TadeoSinay/planos_flama-/salida/documentos/DOC-04_NFPA10_vs_IRAM.pdf

FLAMA S.A. | NFPA 10 frente a IRAM | DOC-04
Edición 0 | Señalización, colores, instalación e intervalos | 28/09/2026

# NFPA 10 frente a IRAM: marcado, colores e instalación

## 1. Identificación de clases de fuego

NFPA 10 admite dos sistemas de marcado de la etiqueta: el sistema letra-forma de color y el sistema de pictogramas (Anexo B). En Argentina, IRAM 10005 usa las mismas formas geométricas para las clases. Láminas: FL_SEN_03 (letra-forma) y FL_SEN_05 (pictogramas).
Clase | Fuego | Letra-forma (NFPA 10 / IRAM 10005) | Pictograma NFPA 10
A | combustibles sólidos comunes | triángulo verde | cesto con residuos y fuego
B | líquidos y gases inflamables | cuadrado rojo | bidón y fuego
C | equipos eléctricos energizados | círculo azul | enchufe y fuego
D | metales combustibles | estrella de 5 puntas amarilla | sin pictograma
K | aceites y grasas de cocina | hexágono negro | sartén y fuego
En el sistema de pictogramas, la clase para la que el agente no es apto se muestra con fondo negro y barra diagonal roja; los matafuegos de agua y espuma deben mostrar la clase C tachada.

## 2. NFPA 704 no se usa en el matafuego

El rombo de NFPA 704 (azul salud, rojo inflamabilidad, amarillo inestabilidad, blanco riesgos especiales, escala 0 a 4) identifica los peligros de los materiales almacenados en un edificio o tanque para los bomberos. No es una señal del matafuego ni de su clase de fuego.

## 3. Colores de seguridad y carteles

Tema | IRAM / Argentina | NFPA 10 / EE. UU.
Color del matafuego | rojo (IRAM 3523 y afines) | rojo habitual; NFPA no fija el color del cuerpo
Cartel en altura | tridimensional EXTINTOR + pictograma, caras ≥ 280 × 220, a 2,0-2,5 m (3517-2:2020 7.3, FL_SEN_02) | OSHA / ANSI Z535; ISO 7010 F001 aceptado
Chapa baliza | 350 (ó 260) × 870, franjas 100 mm a 45°, borde fotoluminiscente 15 mm, tipos de fuego, n° de puesto, datos del PRS (7.2, FL_SEN_01/07) | no existe en NFPA 10
Símbolos de clase | contorno de color con letra + pictograma, colores IRAM-DEF D 1054 (7.2.2, FL_SEN_03) | letra-forma rellena o pictogramas (Anexo B)

## 4. Instalación

Tema | IRAM / Argentina | NFPA 10
Altura de la parte superior | ≤ 1,5 m hasta 20 kg; ≤ 1,0 m si pesa más (3517-2:2020 6.2.14) | ≤ 1,53 m (5 ft) si pesa ≤ 18,14 kg; ≤ 1,07 m (3,5 ft) si pesa más (§6.1.3.8.1-2)
Separación al piso | ≥ 0,10 m (6.2.14) | ≥ 102 mm (4 in) (§6.1.3.8.3)
Distancia de recorrido | ≤ 20 m clase A, ≤ 15 m clase B, ≤ 3 m clase K; mínimo uno cada 200 m² (6.2.4, 6.2.5) | clase A: 22,9 m (75 ft); clase B: 9,15 o 15,25 m (30 o 50 ft) según potencial
Visibilidad | chapa baliza y cartel | visible, accesible, sin obstrucciones; señalizado si no se ve

## 5. Inspección, mantenimiento y prueba hidráulica

Actividad | IRAM | NFPA 10
Control / inspección | trimestral; mensual en alto riesgo (8.2) | mensual

FLAMA S.A. · DOC-04 · página 1 de 2

Mantenimiento | anual; vehículos: semestral recomendado (9.2.1)

anual

Examen interno polvo presurizado | en cada mantenimiento con cámara (9.8.2) | cada 6 años
PH polvo y gases limpios | 5 años máx.; rodantes a 4 MPa (9.7) | cada 12 años
PH CO2 | cada 5 años | cada 5 años
PH agua, AFFF, acetato de potasio | 2 años máx. (anexo E) | cada 5 años
Agente agua / AFFF / sales K | cambio anual (9.9.1.8-10) | AFFF premezclado: cada 3 años
Mangueras rodantes y CO2 | PH anual (9.7.1.4) | PH con el cilindro

Los números de sección de NFPA 10 corresponden a la edición 2022; verificar contra la edición adoptada por la autoridad competente. Valores IRAM: IRAM 3517-2:2020 (apartados citados).
Fuente: C = catálogo FLAMA · N = norma citada (texto leído) · N* = norma hermana aplicada por analogía · R = valor de referencia habitual, a confirmar por FLAMA con la edición vigente de la norma IRAM (el texto de las normas IRAM es material protegido y no se transcribe).

FLAMA S.A. · DOC-04 · página 2 de 2
