TadeoSinay/planos_flama-/salida/FL_MAT_ABC_2.5kg/FL_MAT_ABC_2.5kg.step

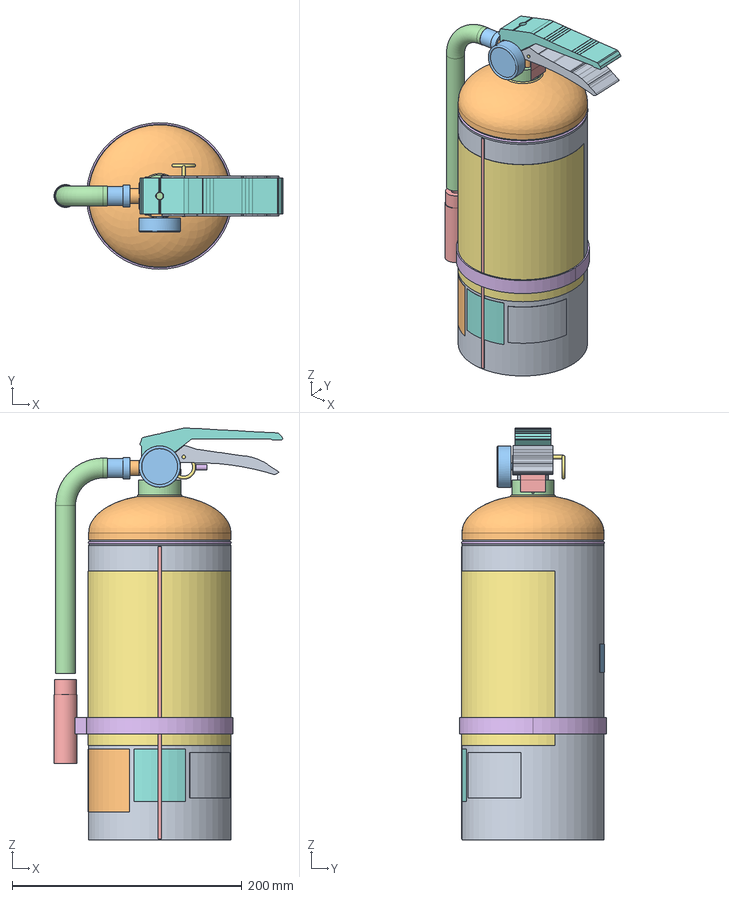
[picture p57: CAD file, 2026-10-10]
salida/FL_MAT_ABC_2.5kg/FL_MAT_ABC_2.5kg.step
199.2 x 127.6 x 358.7 mm
cuerpo
cupula
fondo
cuello
soldaduras
espiga
tuerca
cuerpo_valvula
manometro
vastago
resorte
eje
pasador
manija_superior
manija_inferior
cano_pesca
racor
manguera
tobera
suncho
etiqueta
oblea_pba
sello_iram
tarjeta_caba
etiqueta_serie
junta_cuello
faja_garantia
precinto
