TadeoSinay/planos_flama-/salida/FL_MAT_ABC_25kg/FL_MAT_ABC_25kg.step

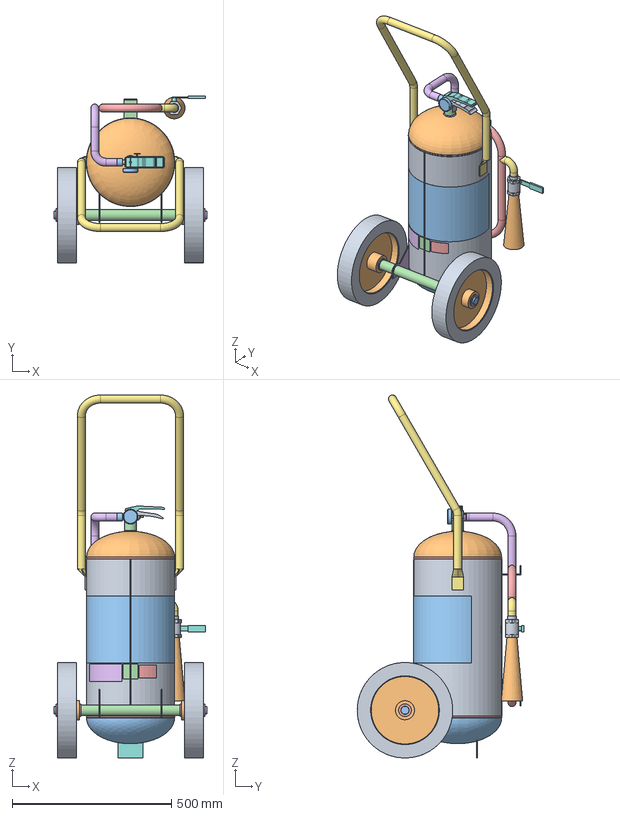
[picture p58: CAD file, 2026-10-10]
salida/FL_MAT_ABC_25kg/FL_MAT_ABC_25kg.step
480.0 x 522.9 x 1140.0 mm
cuerpo
cupula
fondo
cuello
soldaduras
tercera_pata
rueda_der
llanta_der
rueda_izq
llanta_izq
eje_ruedas
portaeje
arandelas_tope
soportes_eje
manija_carro
espiga
tuerca
cuerpo_valvula
manometro
vastago
resorte
eje
pasador
manija_superior
manija_inferior
cano_pesca
racor
ganchos_manguera
manguera_enrollada
manguera
valvula_esferica
tobera_campana
etiqueta
oblea_pba
sello_iram
tarjeta_caba
etiqueta_serie
junta_cuello
faja_garantia
precinto
