TadeoSinay/planos_flama-/salida/FL_MAT_ABC_50kg/FL_MAT_ABC_50kg_3D.dxf

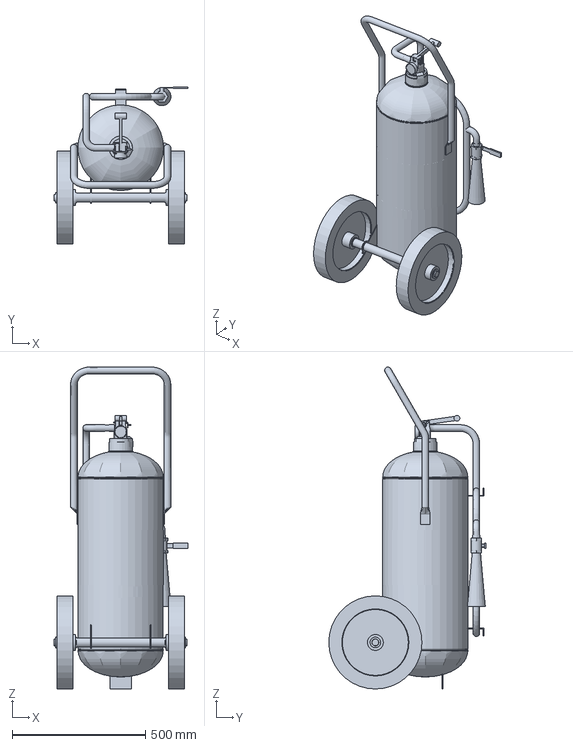
[picture p59: CAD file, 2026-10-10]
salida/FL_MAT_ABC_50kg/FL_MAT_ABC_50kg_3D.dxf
502.5 x 591.5 x 1210.0 mm
