TadeoSinay/planos_flama-/salida/FL_MAT_ABC_5kg/FL_MAT_ABC_5kg.step

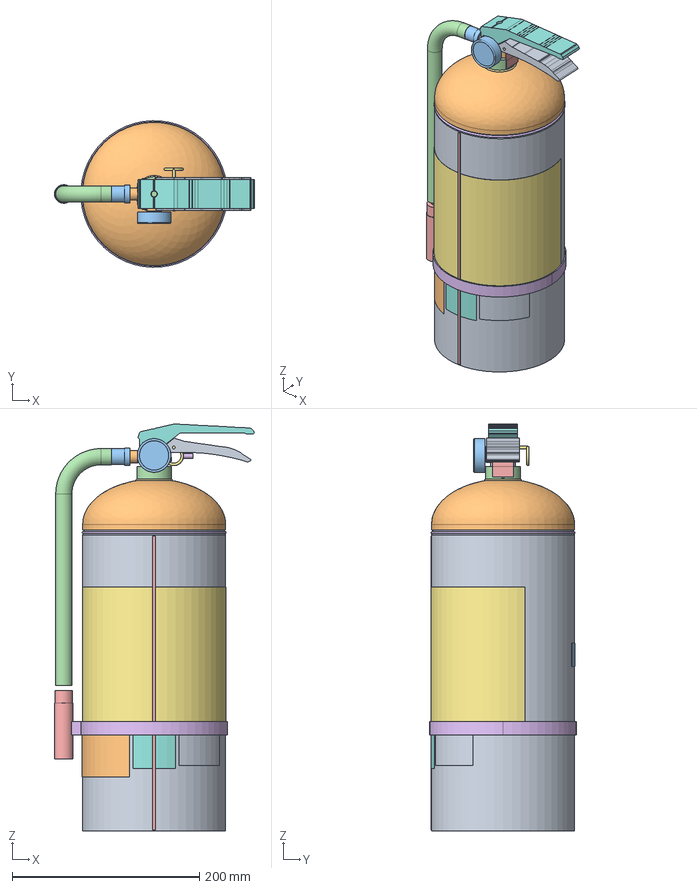
[picture p60: CAD file, 2026-10-10]
salida/FL_MAT_ABC_5kg/FL_MAT_ABC_5kg.step
213.7 x 156.6 x 434.7 mm
cuerpo
cupula
fondo
cuello
soldaduras
espiga
tuerca
cuerpo_valvula
manometro
vastago
resorte
eje
pasador
manija_superior
manija_inferior
cano_pesca
racor
manguera
tobera
suncho
etiqueta
oblea_pba
sello_iram
tarjeta_caba
etiqueta_serie
junta_cuello
faja_garantia
precinto
