TadeoSinay/planos_flama-/salida/FL_MAT_ABC_70kg/FL_MAT_ABC_70kg_3D.dxf

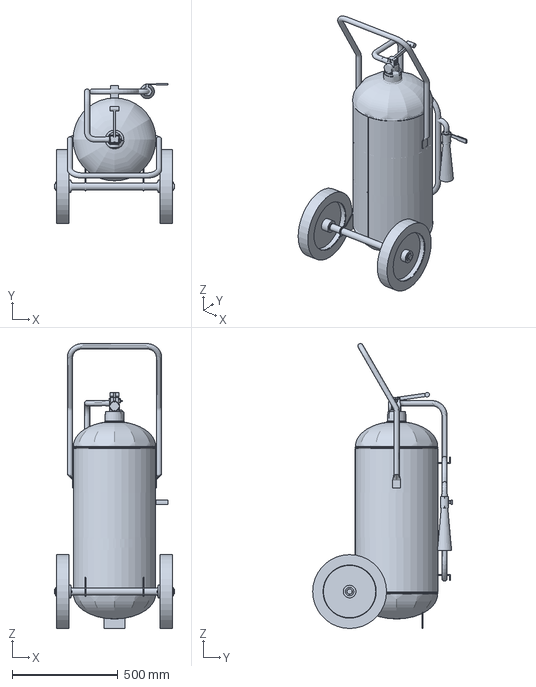
[picture p61: CAD file, 2026-10-10]
salida/FL_MAT_ABC_70kg/FL_MAT_ABC_70kg_3D.dxf
570.0 x 661.5 x 1350.0 mm
