TadeoSinay/planos_flama-/salida/FL_MAT_AFFF_10l/FL_MAT_AFFF_10l_3D.dxf

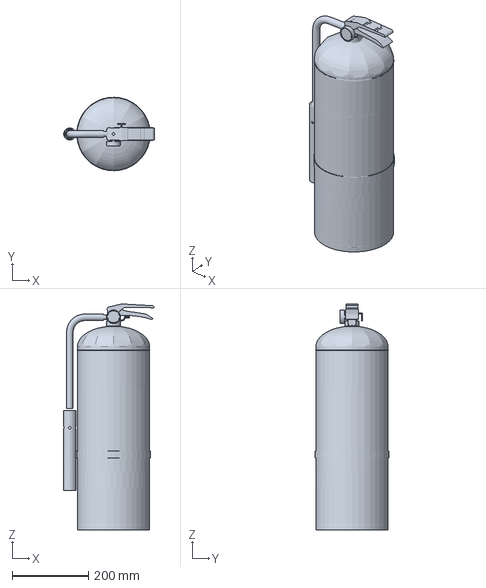
[picture p62: CAD file, 2026-10-10]
salida/FL_MAT_AFFF_10l/FL_MAT_AFFF_10l_3D.dxf
238.3 x 193.5 x 594.3 mm
