TadeoSinay/planos_flama-/salida/FL_MAT_AGUA_10l/FL_MAT_AGUA_10l_3D.dxf

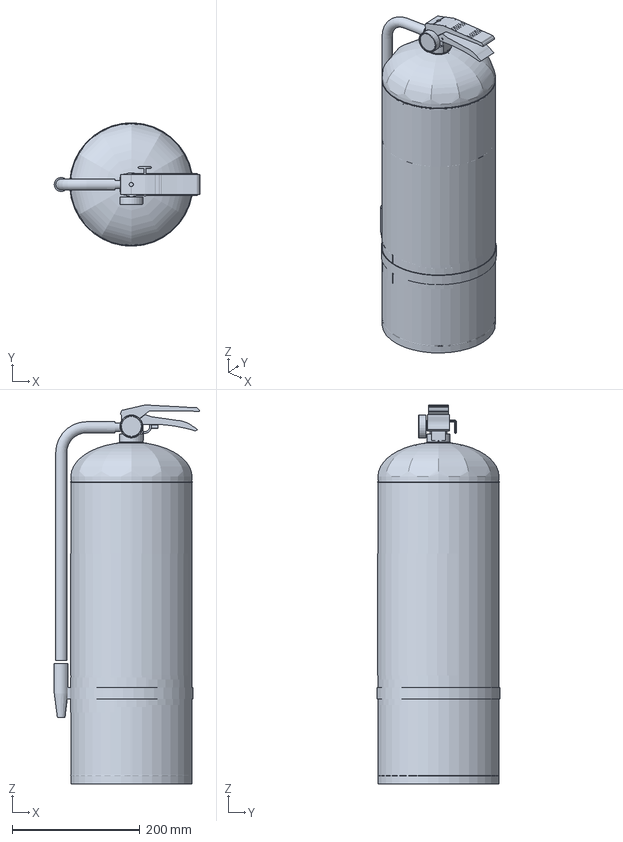
[picture p63: CAD file, 2026-10-10]
salida/FL_MAT_AGUA_10l/FL_MAT_AGUA_10l_3D.dxf
228.3 x 193.5 x 594.3 mm
