TadeoSinay/planos_flama-/salida/FL_MAT_CLASED_9l/FL_MAT_CLASED_9l_3D.dxf

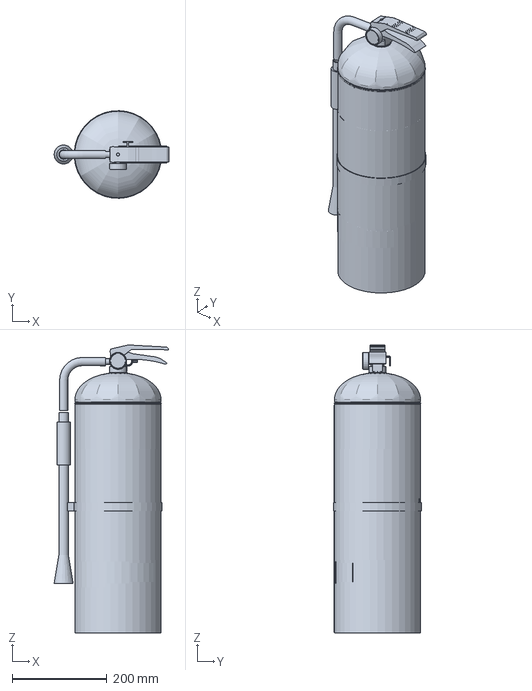
[picture p64: CAD file, 2026-10-10]
salida/FL_MAT_CLASED_9l/FL_MAT_CLASED_9l_3D.dxf
242.0 x 185.0 x 607.7 mm
