TadeoSinay/planos_flama-/salida/FL_MAT_CO2_2kg/FL_MAT_CO2_2kg_3D.dxf

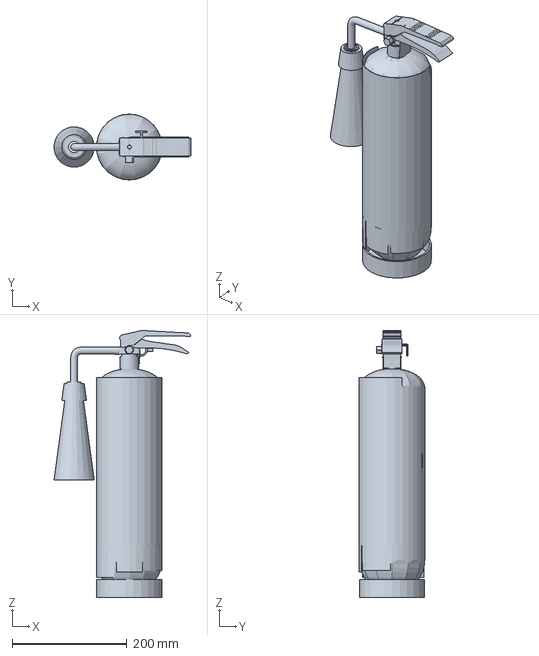
[picture p65: CAD file, 2026-10-10]
salida/FL_MAT_CO2_2kg/FL_MAT_CO2_2kg_3D.dxf
238.3 x 114.6 x 464.4 mm
