TadeoSinay/planos_flama-/salida/FL_MAT_CO2_5kg/FL_MAT_CO2_5kg.step

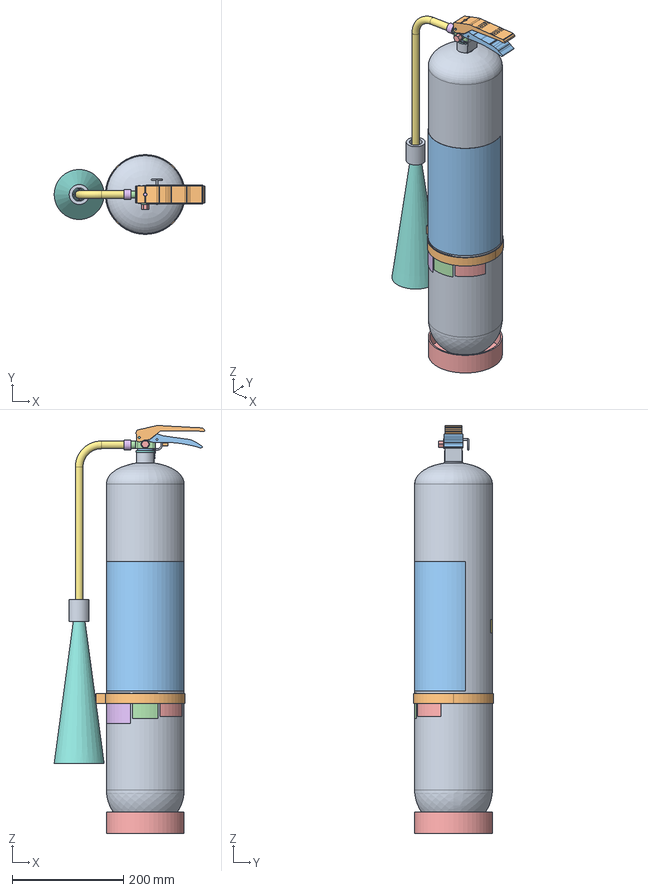
[picture p66: CAD file, 2026-10-10]
salida/FL_MAT_CO2_5kg/FL_MAT_CO2_5kg.step
271.3 x 143.6 x 734.6 mm
cuerpo
espiga
tuerca
cuerpo_valvula
disco_seguridad
vastago
resorte
eje
pasador
manija_superior
manija_inferior
cano_pesca
pie
racor
manguera
difusor
empunadura
suncho
etiqueta
oblea_pba
sello_iram
tarjeta_caba
etiqueta_serie
junta_cuello
faja_garantia
precinto
