TadeoSinay/planos_flama-/salida/FL_MAT_SALESK_6l/FL_MAT_SALESK_6l_3D.dxf

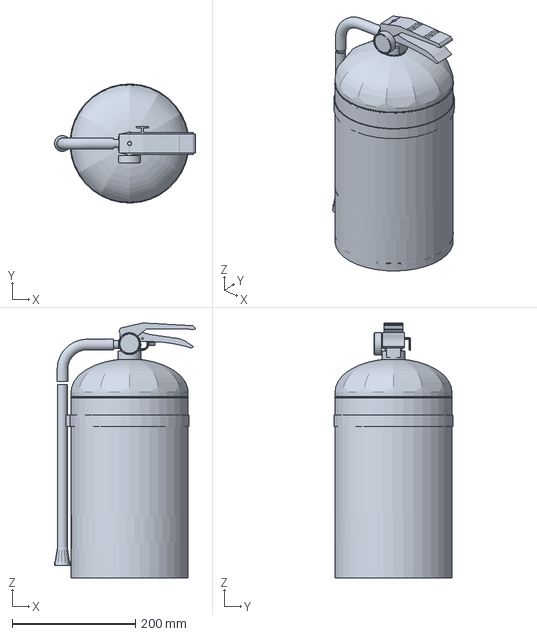
[picture p67: CAD file, 2026-10-10]
salida/FL_MAT_SALESK_6l/FL_MAT_SALESK_6l_3D.dxf
229.3 x 193.5 x 414.3 mm
