TadeoSinay/planos_flama-/salida/senaletica/FL_SEN_09.dxf

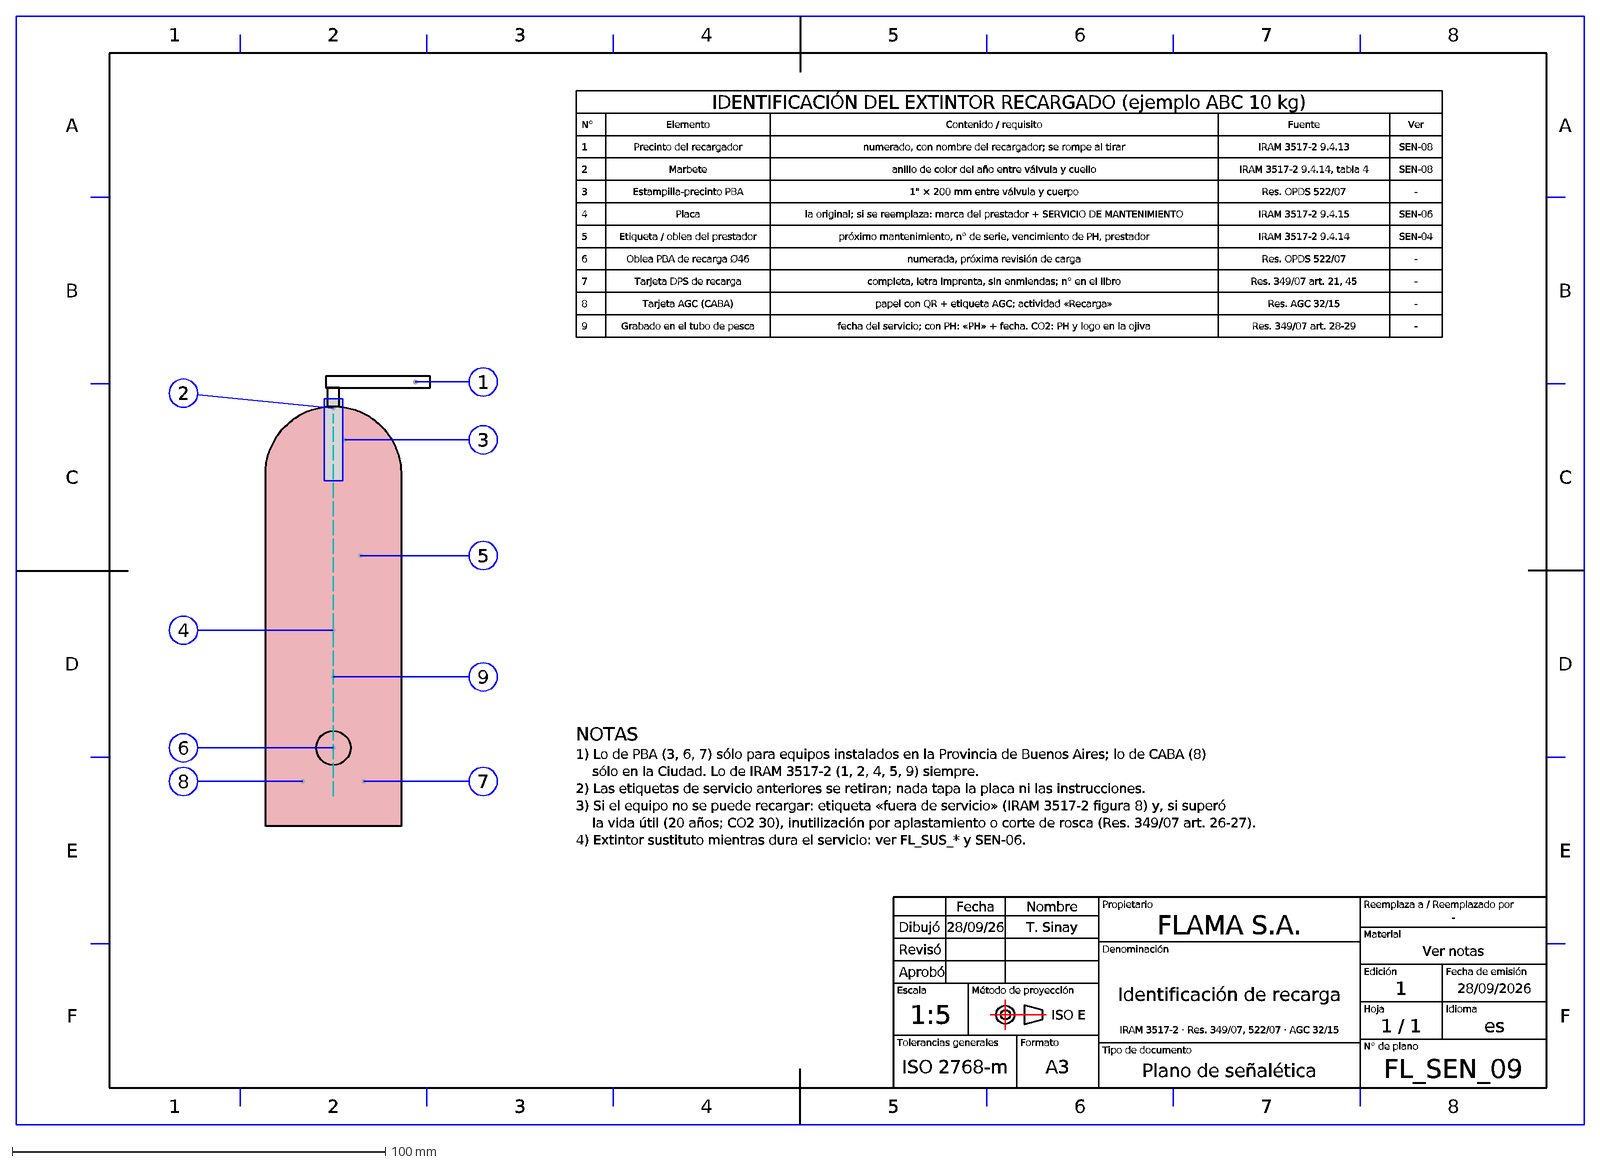
[picture p68: CAD file, 2026-10-10]
salida/senaletica/FL_SEN_09.dxf
1
2
3
4
5
6
7
8
F
E
D
C
B
A
Fecha
Nombre
Dibujó
28/09/26
T. Sinay
Revisó
Aprobó
Escala
1:5
Método de proyección
ISO E
Tolerancias generales
ISO 2768-m
Formato
A3
Propietario
FLAMA S.A.
Denominación
Identificación de recarga
IRAM 3517-2 · Res. 349/07, 522/07 · AGC 32/15
Tipo de documento
Plano de señalética
Reemplaza a / Reemplazado por
-
Material
Ver notas
Edición
Fecha de emisión
28/09/2026
Hoja
1 / 1
Idioma
es
N° de plano
FL_SEN_09
9
IDENTIFICACIÓN DEL EXTINTOR RECARGADO (ejemplo ABC 10 kg)
N°
Elemento
Contenido / requisito
Fuente
Ver
Precinto del recargador
numerado, con nombre del recargador; se rompe al tirar
IRAM 3517-2 9.4.13
SEN-08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
