TadeoSinay/planos_flama-/salida/accesorios/FL_ACC_03.step

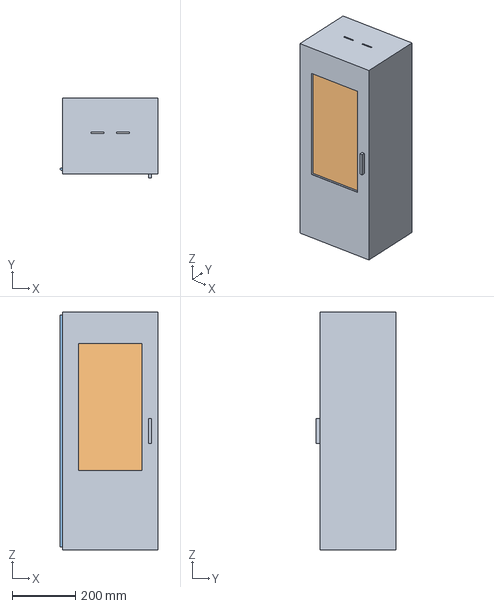
[picture p70: CAD file, 2026-10-10]
salida/accesorios/FL_ACC_03.step
308.0 x 252.0 x 750.0 mm
