TadeoSinay/planos_flama-/salida/esquemas/FL_ESQ_03.dxf

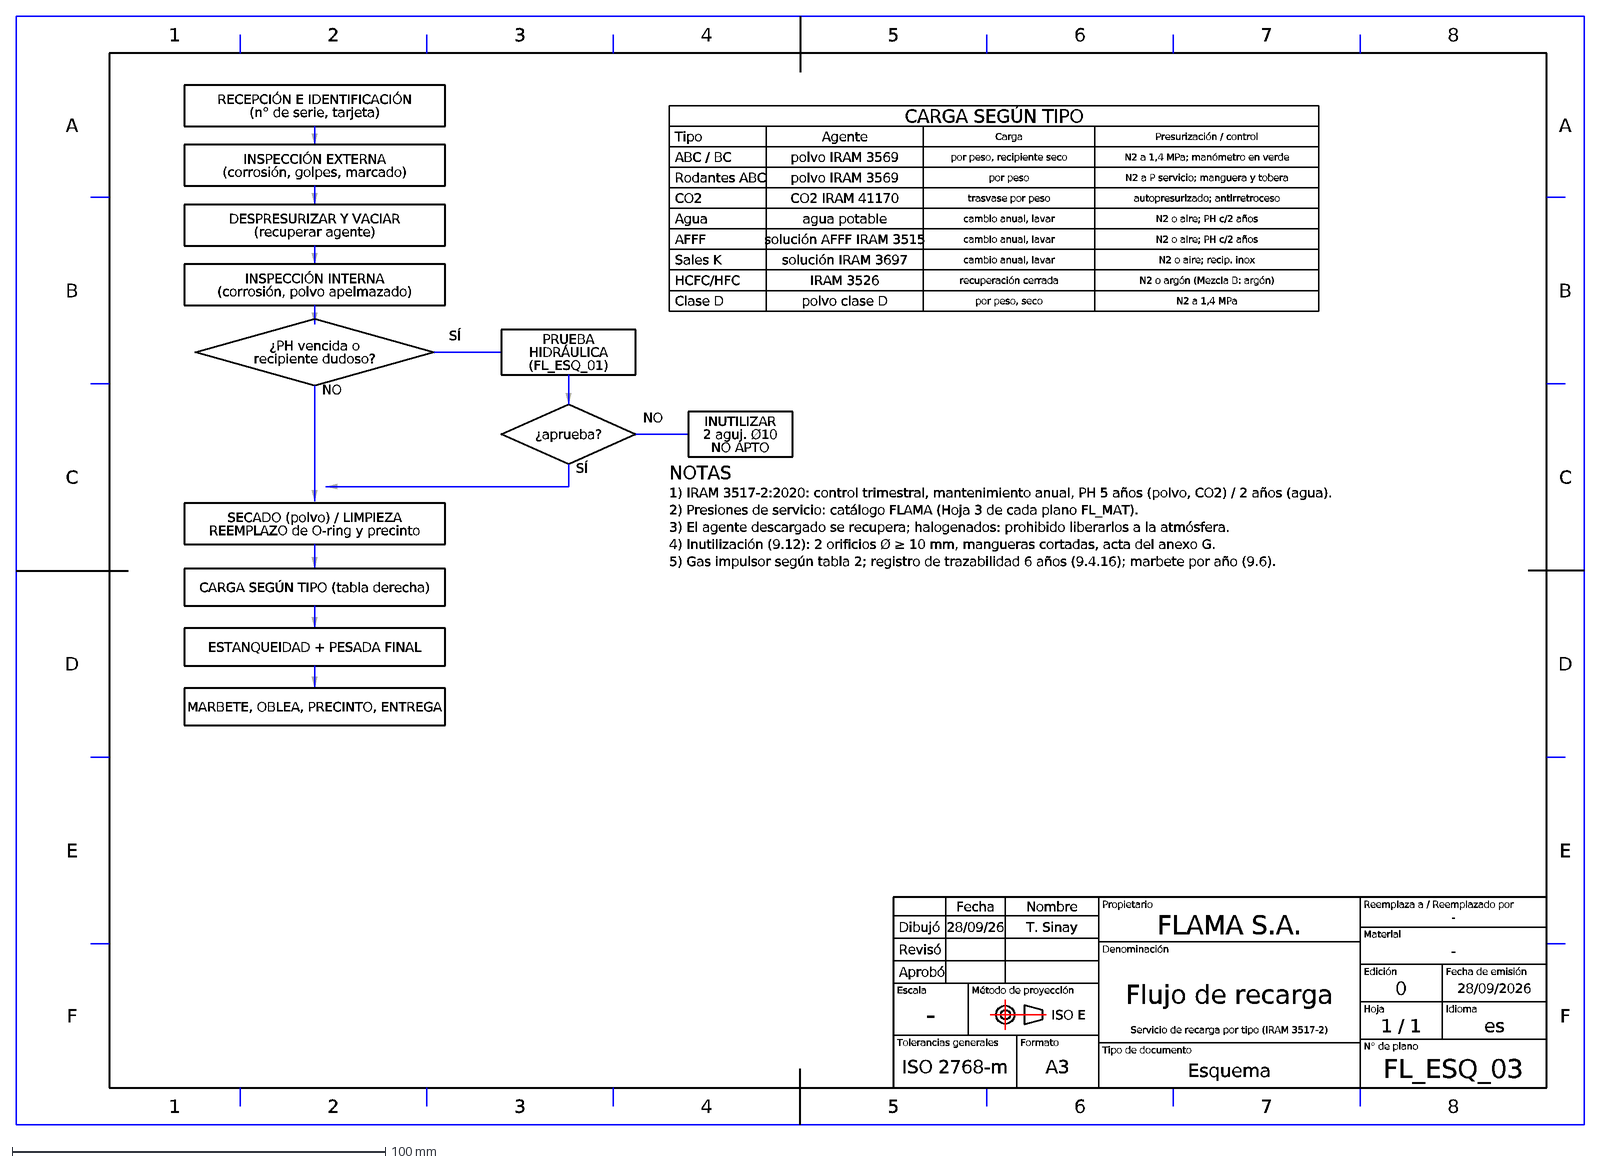
[picture p72: CAD file, 2026-10-10]
salida/esquemas/FL_ESQ_03.dxf
1
2
3
4
5
6
7
8
F
E
D
C
B
A
Fecha
Nombre
Dibujó
28/09/26
T. Sinay
Revisó
Aprobó
Escala
-
Método de proyección
ISO E
Tolerancias generales
ISO 2768-m
Formato
A3
Propietario
FLAMA S.A.
Denominación
Flujo de recarga
Servicio de recarga por tipo (IRAM 3517-2)
Tipo de documento
Esquema
Reemplaza a / Reemplazado por
Material
Edición
0
Fecha de emisión
28/09/2026
Hoja
1 / 1
Idioma
es
N° de plano
FL_ESQ_03
RECEPCIÓN E IDENTIFICACIÓN
(n° de serie, tarjeta)
INSPECCIÓN EXTERNA
(corrosión, golpes, marcado)
DESPRESURIZAR Y VACIAR
(recuperar agente)
INSPECCIÓN INTERNA
(corrosión, polvo apelmazado)
¿PH vencida o
recipiente dudoso?
SÍ
PRUEBA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
