TadeoSinay/planos_flama-/salida/FL_MAT_ABC_2.5kg/FL_MAT_ABC_2.5kg_3D.dxf

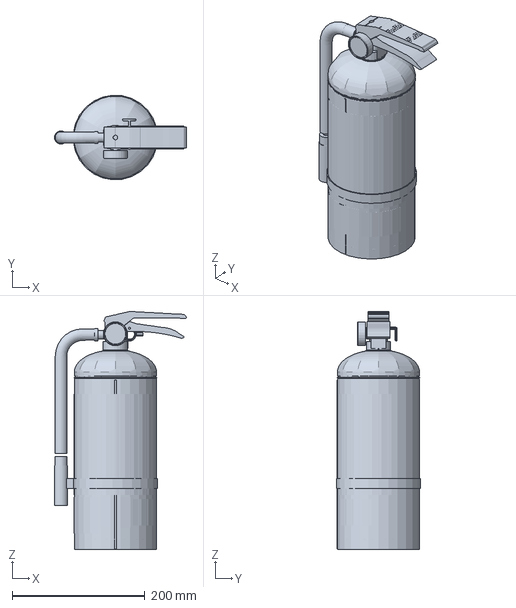
[picture p73: CAD file, 2026-10-10]
salida/FL_MAT_ABC_2.5kg/FL_MAT_ABC_2.5kg_3D.dxf
199.2 x 127.3 x 358.7 mm
