TadeoSinay/planos_flama-/salida/FL_MAT_ABC_70kg/FL_MAT_ABC_70kg.step

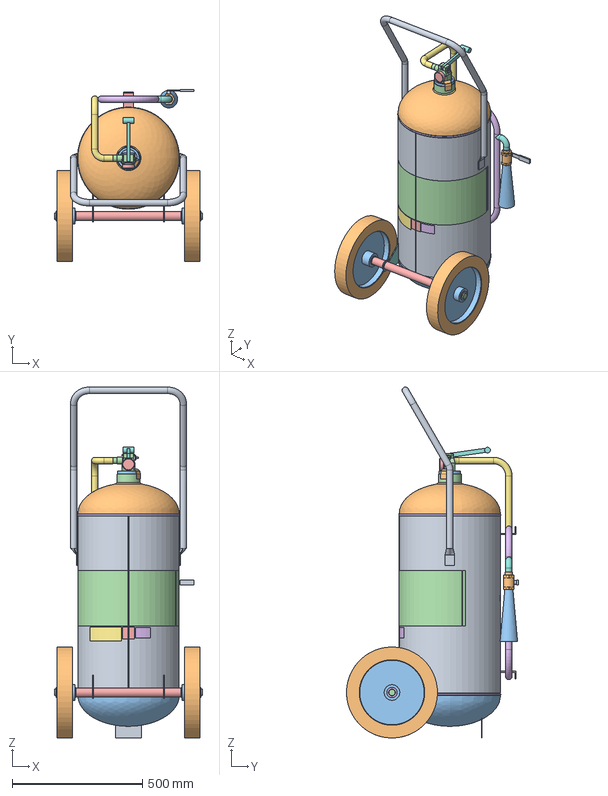
[picture p74: CAD file, 2026-10-10]
salida/FL_MAT_ABC_70kg/FL_MAT_ABC_70kg.step
570.0 x 661.4 x 1350.0 mm
cuerpo
cupula
fondo
cuello
placas_refuerzo
soldaduras
tercera_pata
rueda_der
llanta_der
rueda_izq
llanta_izq
eje_ruedas
portaeje
arandelas_tope
soportes_eje
manija_carro
espiga
tuerca
cuerpo_valvula
manometro
vastago
resorte
manija_superior
eje
pasador
cano_pesca
racor
ganchos_manguera
manguera_enrollada
manguera
valvula_esferica
tobera_campana
etiqueta
oblea_pba
sello_iram
tarjeta_caba
etiqueta_serie
junta_cuello
faja_garantia
precinto
