TadeoSinay/planos_flama-/salida/FL_MAT_CO2_5kg/FL_MAT_CO2_5kg_3D.dxf

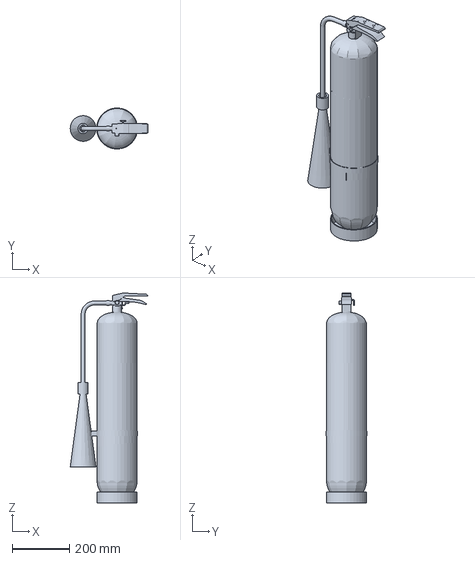
[picture p75: CAD file, 2026-10-10]
salida/FL_MAT_CO2_5kg/FL_MAT_CO2_5kg_3D.dxf
271.3 x 143.5 x 734.6 mm
