TadeoSinay/planos_flama-/salida/senaletica/FL_SEN_04.dxf

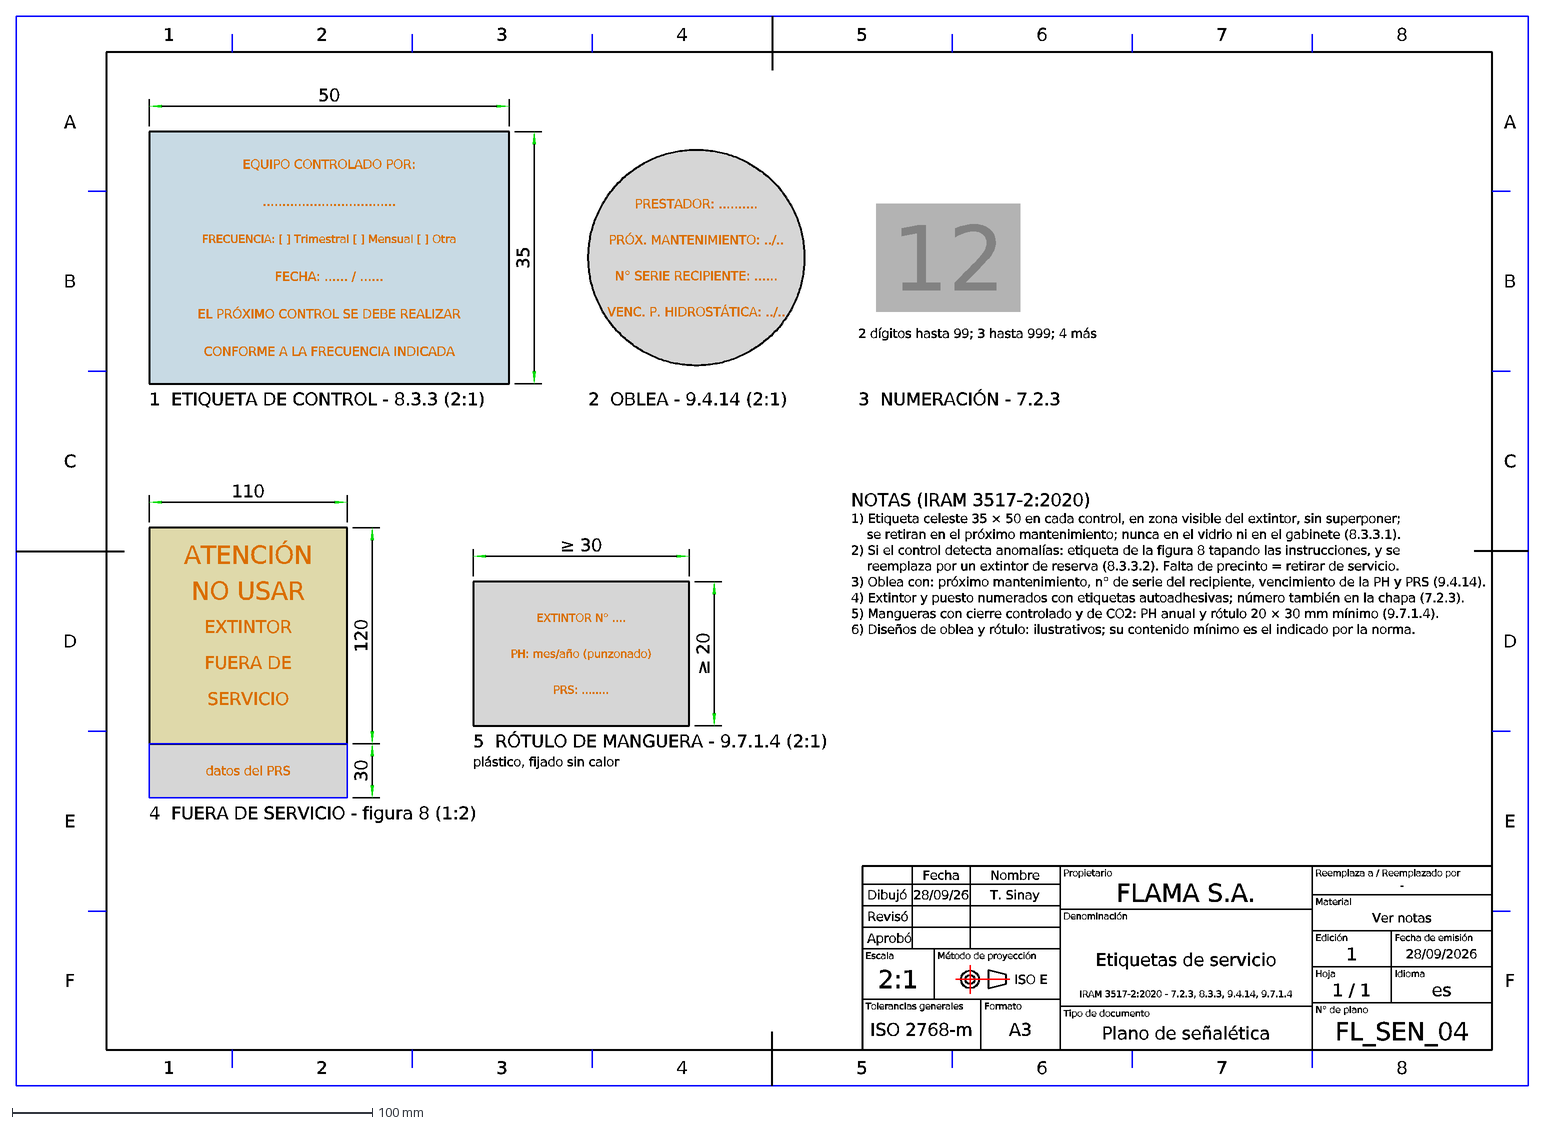
[picture p77: CAD file, 2026-10-10]
salida/senaletica/FL_SEN_04.dxf
1
2
3
4
5
6
7
8
F
E
D
C
B
A
Fecha
Nombre
Dibujó
28/09/26
T. Sinay
Revisó
Aprobó
Escala
2:1
Método de proyección
ISO E
Tolerancias generales
ISO 2768-m
Formato
A3
Propietario
FLAMA S.A.
Denominación
Etiquetas de servicio
IRAM 3517-2:2020 - 7.2.3, 8.3.3, 9.4.14, 9.7.1.4
Tipo de documento
Plano de señalética
Reemplaza a / Reemplazado por
-
Material
Ver notas
Edición
Fecha de emisión
28/09/2026
Hoja
1 / 1
Idioma
es
N° de plano
FL_SEN_04
EQUIPO CONTROLADO POR:
..................................
FRECUENCIA: [ ] Trimestral [ ] Mensual [ ] Otra
FECHA: ...... / ......
EL PRÓXIMO CONTROL SE DEBE REALIZAR
CONFORME A LA FRECUENCIA INDICADA
50
35
1 ETIQUETA DE CONTROL - 8.3.3 (2:1)
PRESTADOR: ..........
PRÓX. MANTENIMIENTO: ../..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
