TadeoSinay/planos_flama-/salida/accesorios/FL_ACC_01.step

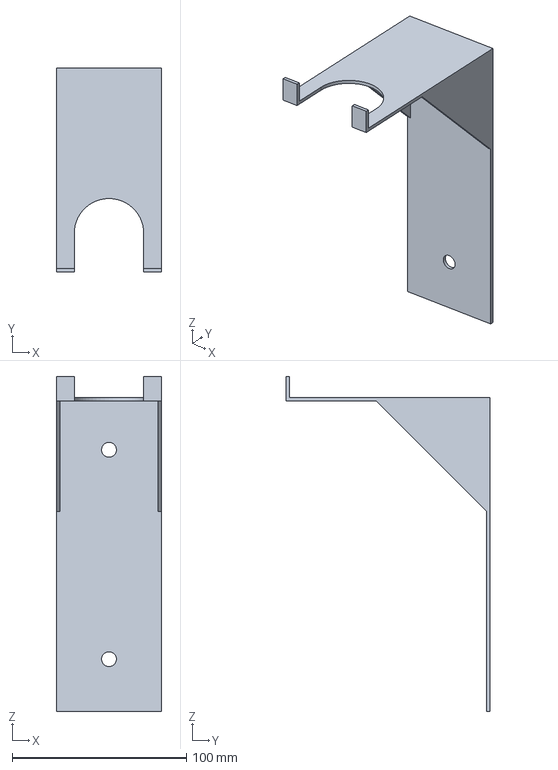
[picture p79: CAD file, 2026-10-10]
salida/accesorios/FL_ACC_01.step
60.0 x 117.0 x 192.0 mm
