TadeoSinay/planos_flama-/salida/cilindros/despiece/FL_DES_REC_ABC_10kg.dxf

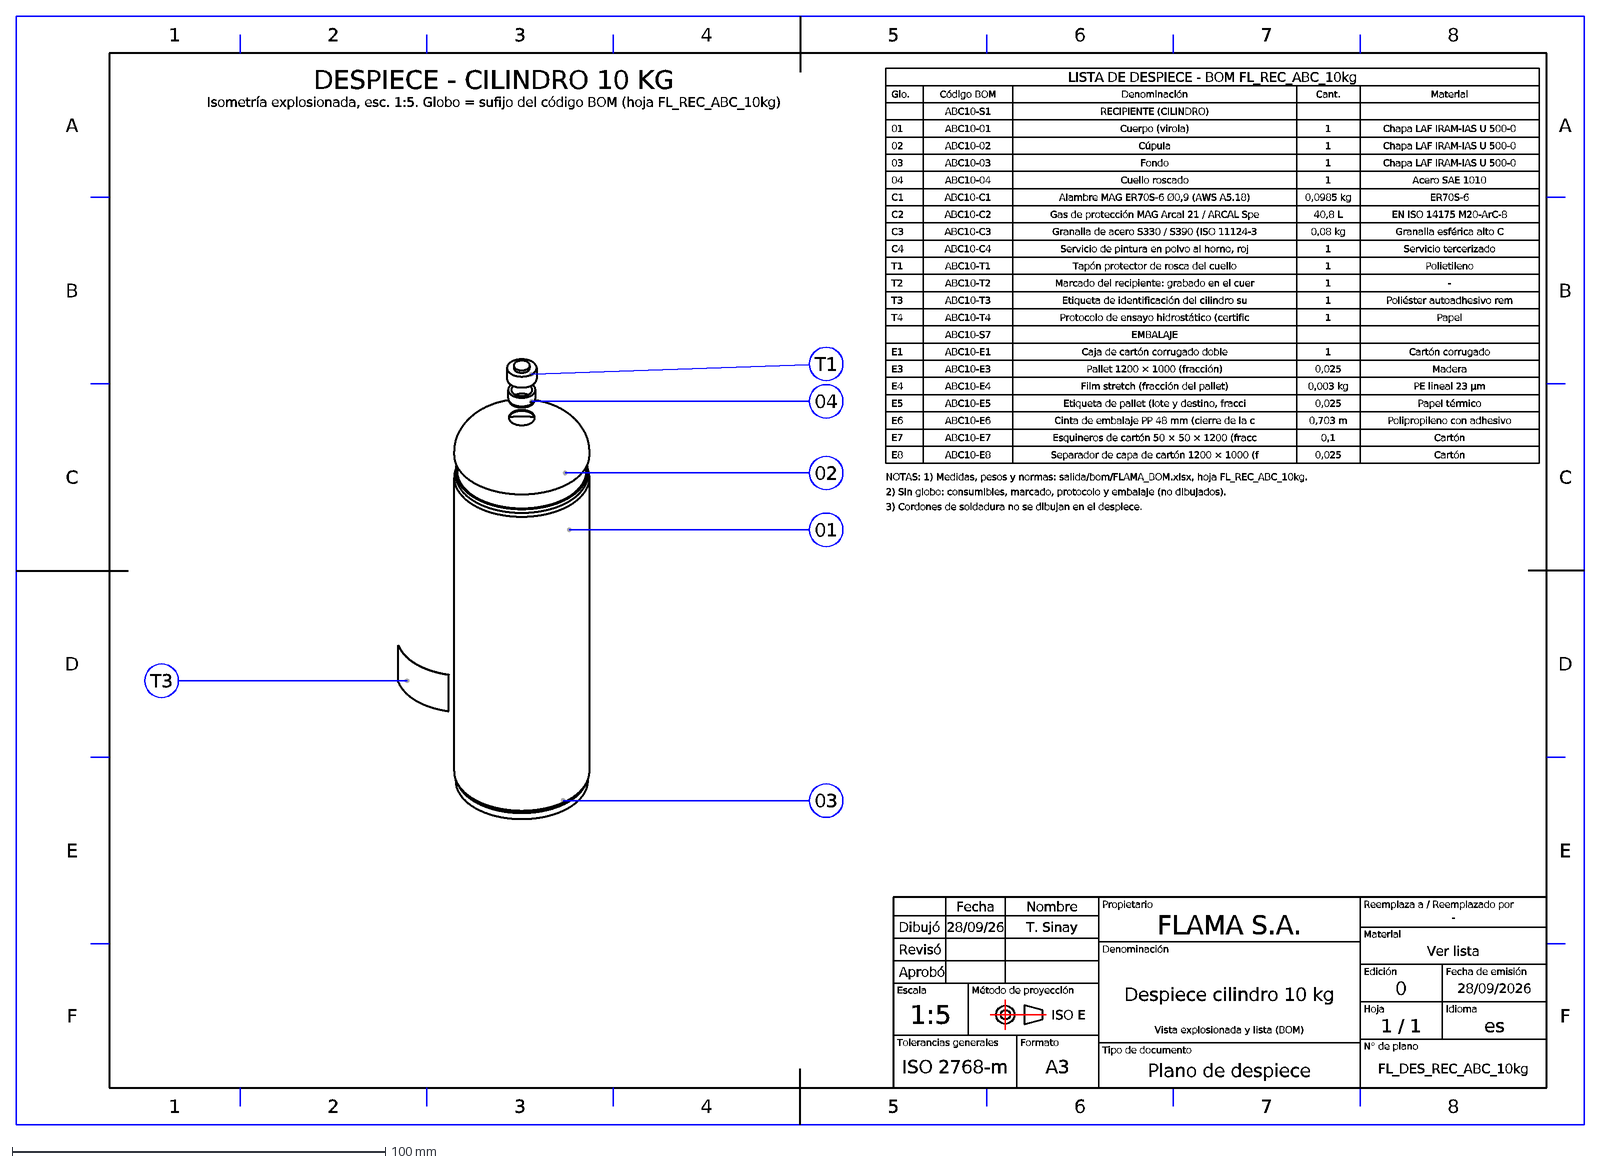
[picture p80: CAD file, 2026-10-10]
salida/cilindros/despiece/FL_DES_REC_ABC_10kg.dxf
1
2
3
4
5
6
7
8
F
E
D
C
B
A
T3
03
01
02
04
T1
DESPIECE - CILINDRO 10 KG
Isometría explosionada, esc. 1:5. Globo = sufijo del código BOM (hoja FL_REC_ABC_10kg)
LISTA DE DESPIECE - BOM FL_REC_ABC_10kg
Glo.
Código BOM
Denominación
Cant.
Material
ABC10-S1
RECIPIENTE (CILINDRO)
ABC10-01
Cuerpo (virola)
Chapa LAF IRAM-IAS U 500-0
ABC10-02
Cúpula
ABC10-03
Fondo
ABC10-04
Cuello roscado
Acero SAE 1010
C1
ABC10-C1
Alambre MAG ER70S-6 Ø0,9 (AWS A5.18)
0,0985 kg
ER70S-6
C2
ABC10-C2
Gas de protección MAG Arcal 21 / ARCAL Spe
40,8 L
EN ISO 14175 M20-ArC-8
C3
ABC10-C3
Granalla de acero S330 / S390 (ISO 11124-3
0,08 kg
Granalla esférica alto C
C4
ABC10-C4
Servicio de pintura en polvo al horno, roj
Servicio tercerizado
ABC10-T1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
