TadeoSinay/planos_flama-/salida/esquemas/FL_ESQ_02.dxf

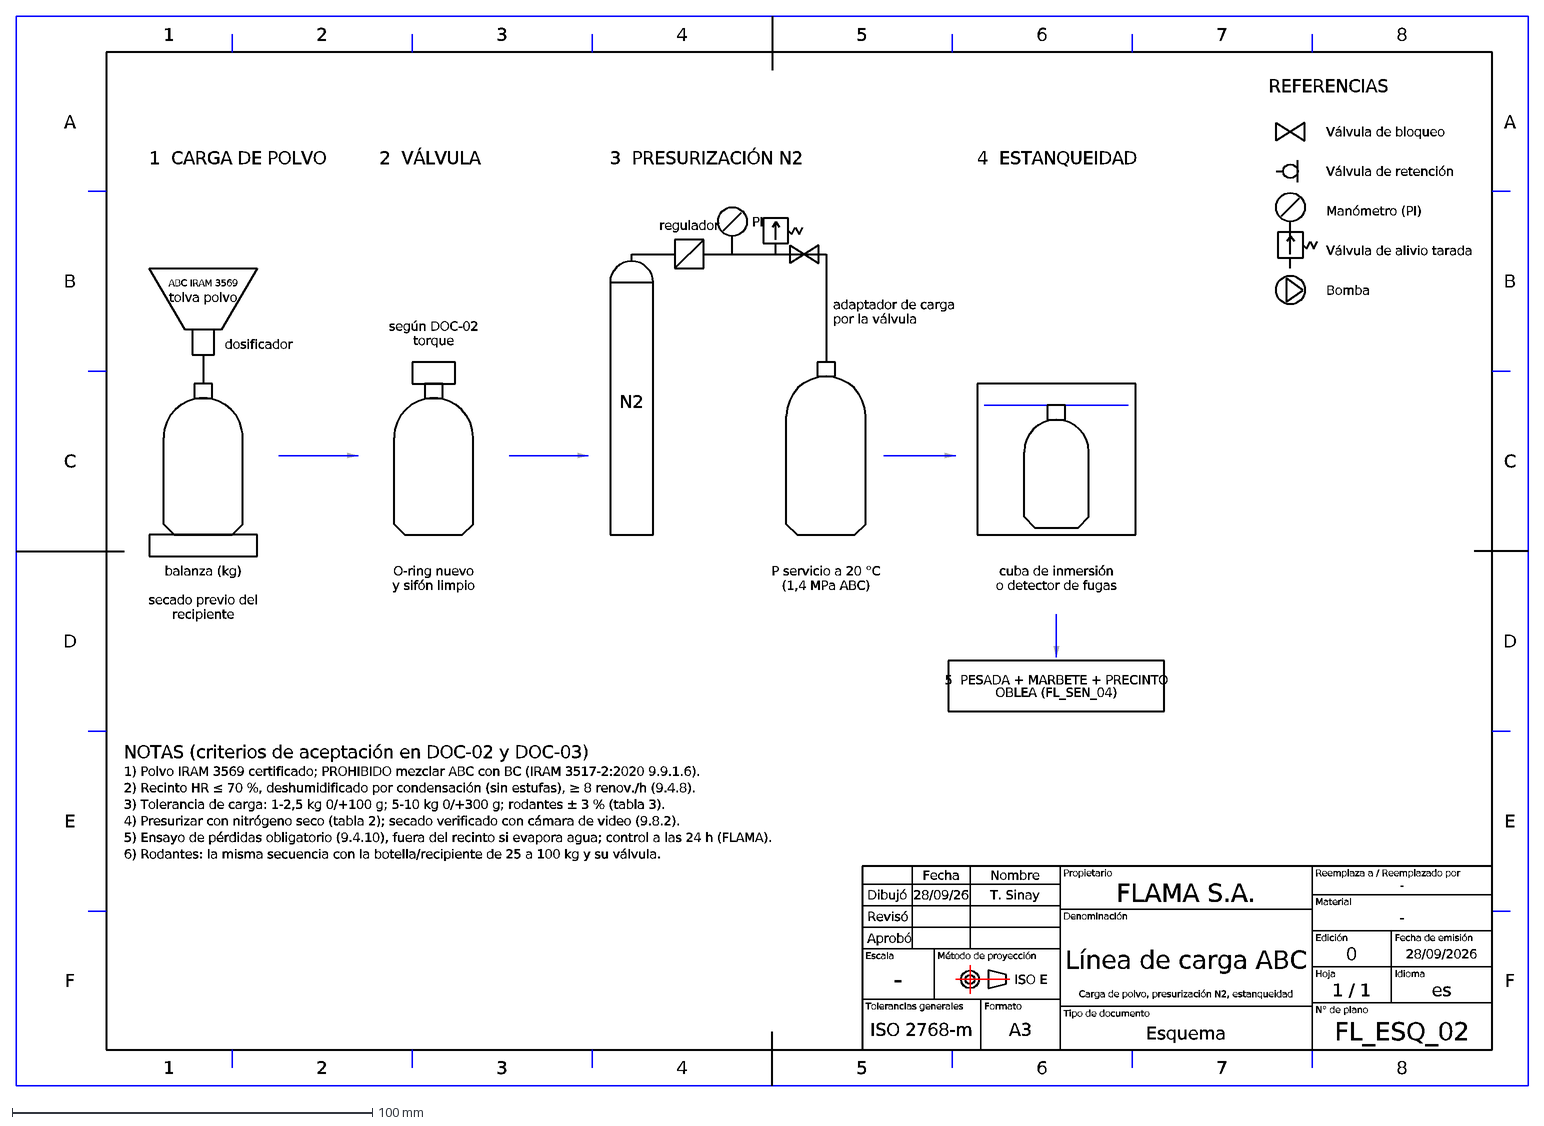
[picture p81: CAD file, 2026-10-10]
salida/esquemas/FL_ESQ_02.dxf
1
2
3
4
5
6
7
8
F
E
D
C
B
A
Fecha
Nombre
Dibujó
28/09/26
T. Sinay
Revisó
Aprobó
Escala
-
Método de proyección
ISO E
Tolerancias generales
ISO 2768-m
Formato
A3
Propietario
FLAMA S.A.
Denominación
Línea de carga ABC
Carga de polvo, presurización N2, estanqueidad
Tipo de documento
Esquema
Reemplaza a / Reemplazado por
Material
Edición
0
Fecha de emisión
28/09/2026
Hoja
1 / 1
Idioma
es
N° de plano
FL_ESQ_02
1 CARGA DE POLVO
tolva polvo
ABC IRAM 3569
dosificador
balanza (kg)
secado previo del
recipiente
2 VÁLVULA
torque
según DOC-02
O-ring nuevo
y sifón limpio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
