TadeoSinay/planos_flama-/salida/senaletica/FL_SEN_06.dxf

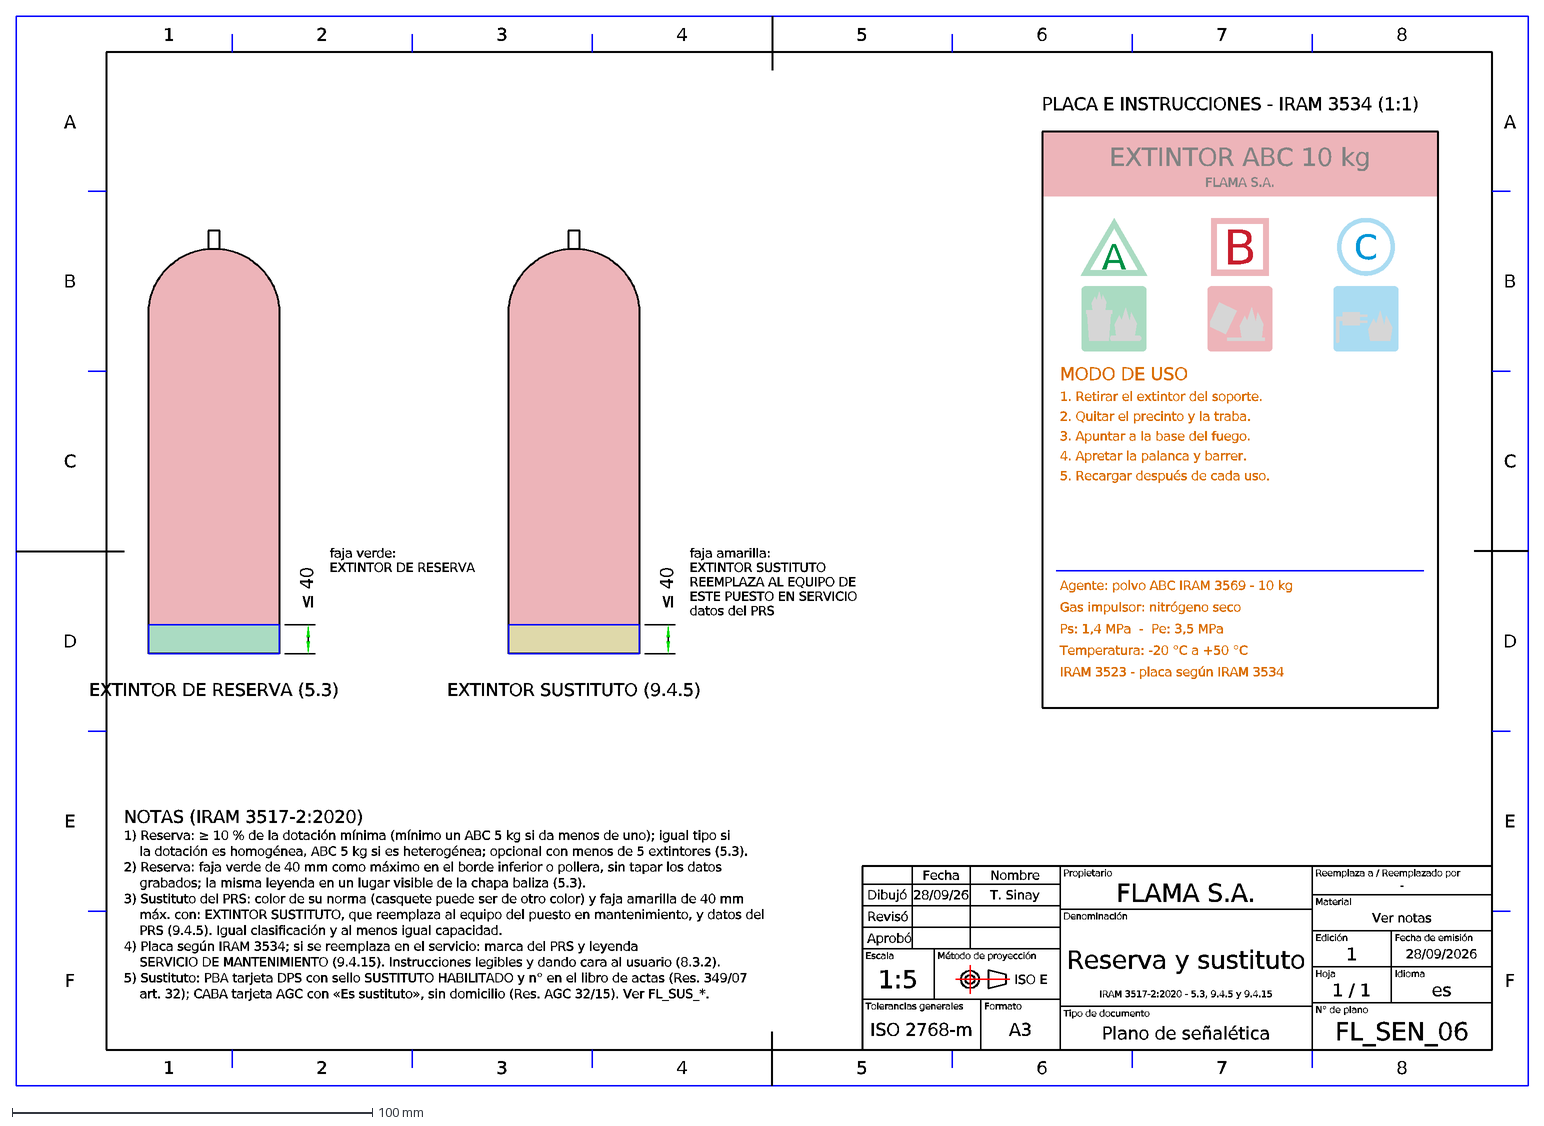
[picture p82: CAD file, 2026-10-10]
salida/senaletica/FL_SEN_06.dxf
1
2
3
4
5
6
7
8
F
E
D
C
B
A
Fecha
Nombre
Dibujó
28/09/26
T. Sinay
Revisó
Aprobó
Escala
1:5
Método de proyección
ISO E
Tolerancias generales
ISO 2768-m
Formato
A3
Propietario
FLAMA S.A.
Denominación
Reserva y sustituto
IRAM 3517-2:2020 - 5.3, 9.4.5 y 9.4.15
Tipo de documento
Plano de señalética
Reemplaza a / Reemplazado por
-
Material
Ver notas
Edición
Fecha de emisión
28/09/2026
Hoja
1 / 1
Idioma
es
N° de plano
FL_SEN_06
≤ 40
faja verde:
EXTINTOR DE RESERVA
faja amarilla:
EXTINTOR SUSTITUTO
REEMPLAZA AL EQUIPO DE
ESTE PUESTO EN SERVICIO
datos del PRS
EXTINTOR DE RESERVA (5.3)
EXTINTOR SUSTITUTO (9.4.5)
EXTINTOR ABC 10 kg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
