TadeoSinay/planos_flama-/salida/cilindros/despiece/FL_DES_REC_ABC_70kg.dxf

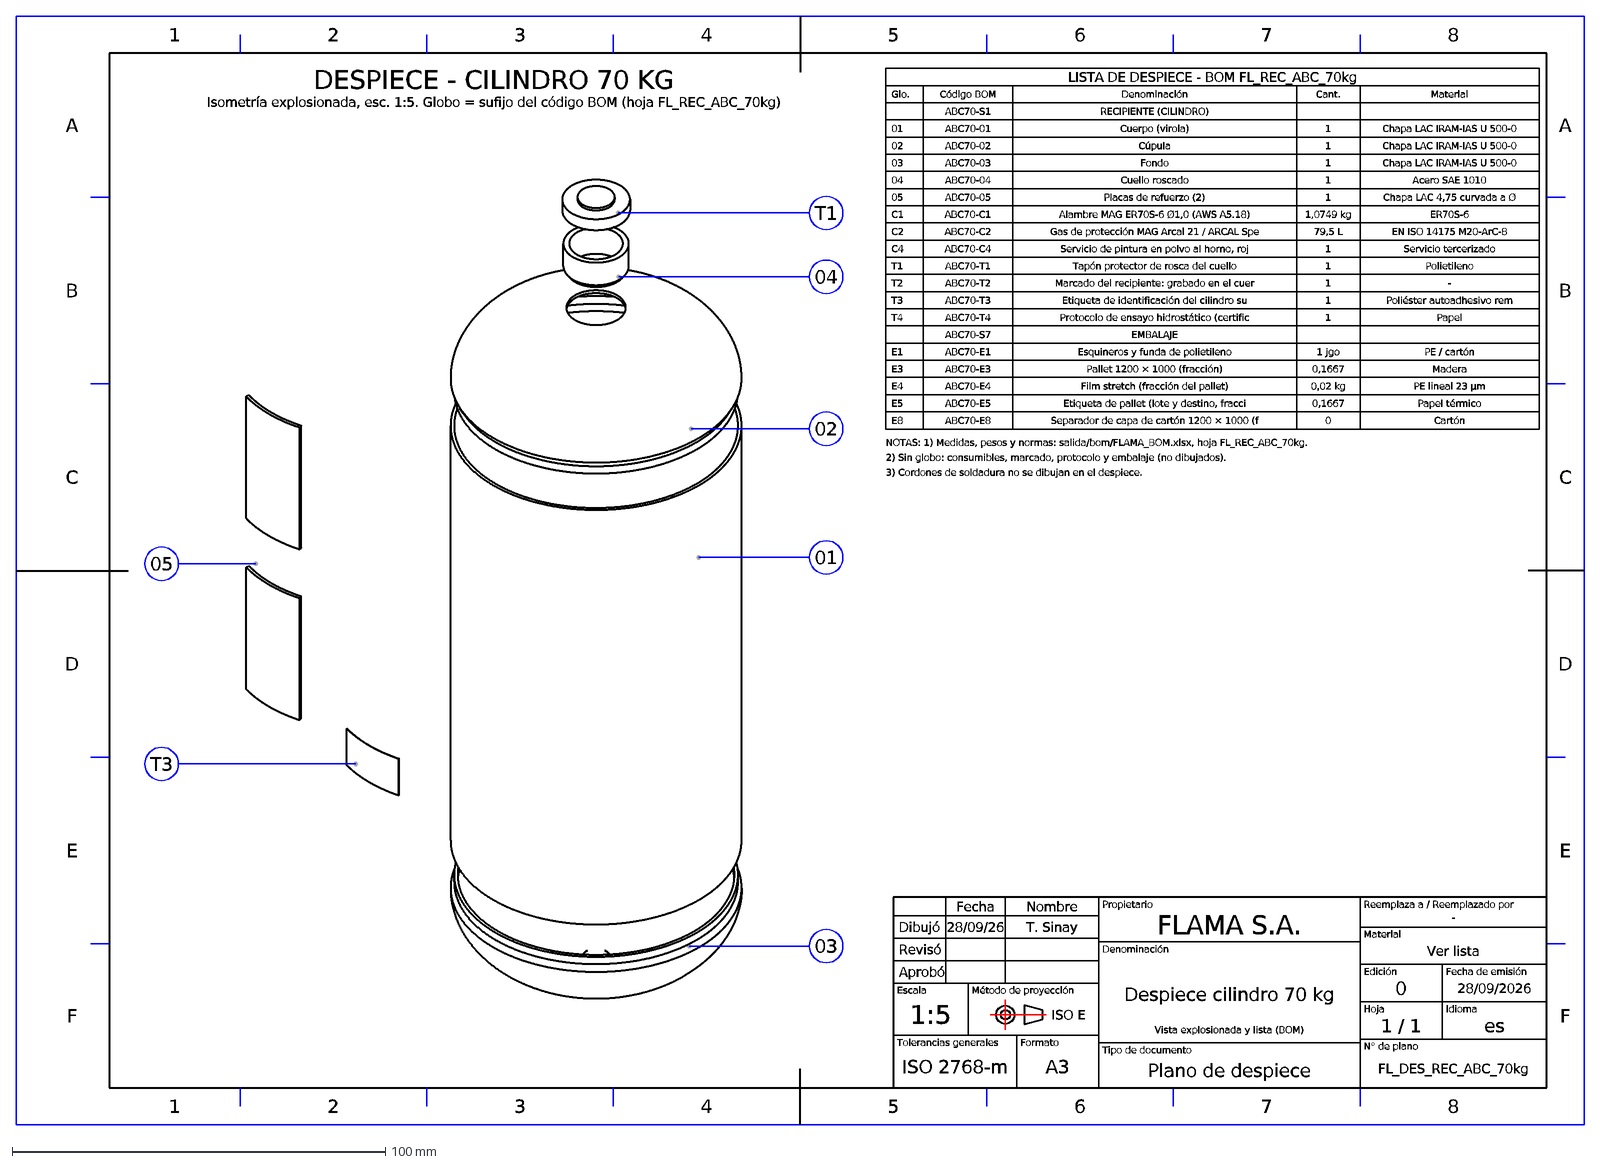
[picture p84: CAD file, 2026-10-10]
salida/cilindros/despiece/FL_DES_REC_ABC_70kg.dxf
1
2
3
4
5
6
7
8
F
E
D
C
B
A
T3
05
03
01
02
04
T1
DESPIECE - CILINDRO 70 KG
Isometría explosionada, esc. 1:5. Globo = sufijo del código BOM (hoja FL_REC_ABC_70kg)
LISTA DE DESPIECE - BOM FL_REC_ABC_70kg
Glo.
Código BOM
Denominación
Cant.
Material
ABC70-S1
RECIPIENTE (CILINDRO)
ABC70-01
Cuerpo (virola)
Chapa LAC IRAM-IAS U 500-0
ABC70-02
Cúpula
ABC70-03
Fondo
ABC70-04
Cuello roscado
Acero SAE 1010
ABC70-05
Placas de refuerzo (2)
Chapa LAC 4,75 curvada a Ø
C1
ABC70-C1
Alambre MAG ER70S-6 Ø1,0 (AWS A5.18)
1,0749 kg
ER70S-6
C2
ABC70-C2
Gas de protección MAG Arcal 21 / ARCAL Spe
79,5 L
EN ISO 14175 M20-ArC-8
C4
ABC70-C4
Servicio de pintura en polvo al horno, roj
Servicio tercerizado
ABC70-T1
Tapón protector de rosca del cuello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
