TadeoSinay/planos_flama-/salida/senaletica/FL_SEN_02.dxf

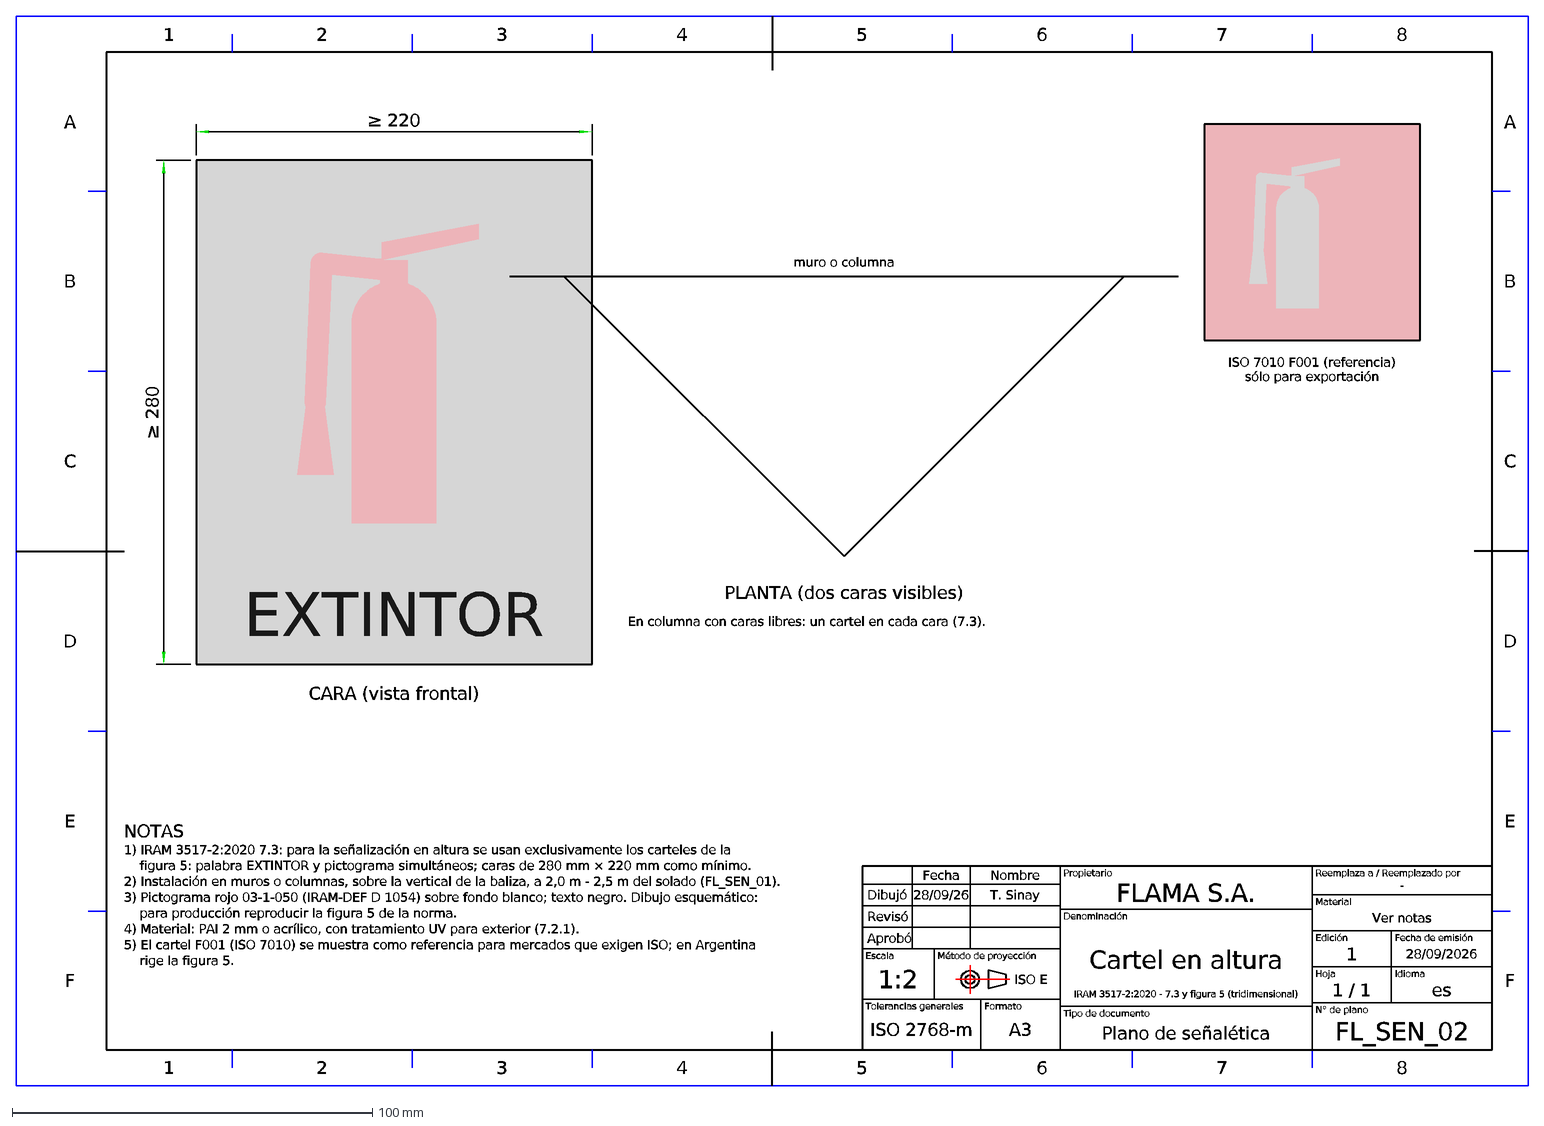
[picture p85: CAD file, 2026-10-10]
salida/senaletica/FL_SEN_02.dxf
1
2
3
4
5
6
7
8
F
E
D
C
B
A
Fecha
Nombre
Dibujó
28/09/26
T. Sinay
Revisó
Aprobó
Escala
1:2
Método de proyección
ISO E
Tolerancias generales
ISO 2768-m
Formato
A3
Propietario
FLAMA S.A.
Denominación
Cartel en altura
IRAM 3517-2:2020 - 7.3 y figura 5 (tridimensional)
Tipo de documento
Plano de señalética
Reemplaza a / Reemplazado por
-
Material
Ver notas
Edición
Fecha de emisión
28/09/2026
Hoja
1 / 1
Idioma
es
N° de plano
FL_SEN_02
EXTINTOR
≥ 220
≥ 280
CARA (vista frontal)
muro o columna
PLANTA (dos caras visibles)
En columna con caras libres: un cartel en cada cara (7.3).
ISO 7010 F001 (referencia)
sólo para exportación
NOTAS
1) IRAM 3517-2:2020 7.3: para la señalización en altura se usan exclusivamente los carteles de la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
