TadeoSinay/planos_flama-/salida/cilindros/despiece/FL_DES_REC_ABC_50kg.dxf

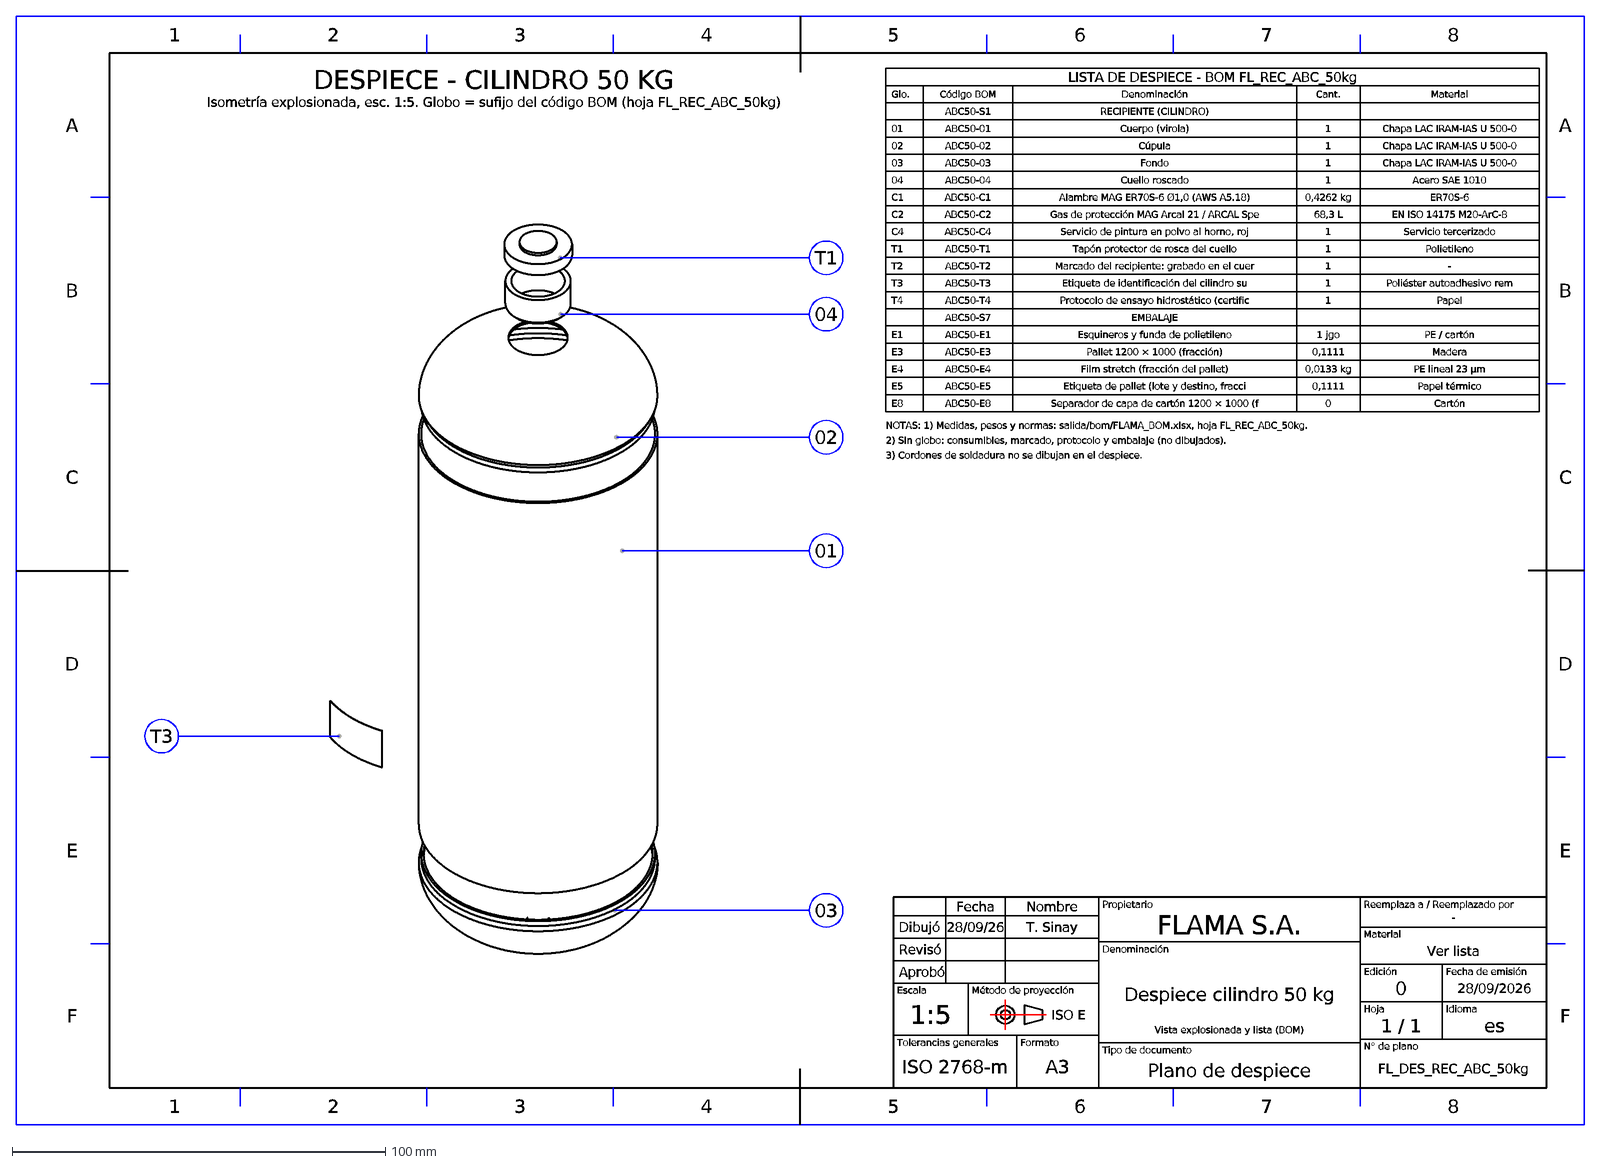
[picture p87: CAD file, 2026-10-10]
salida/cilindros/despiece/FL_DES_REC_ABC_50kg.dxf
1
2
3
4
5
6
7
8
F
E
D
C
B
A
T3
03
01
02
04
T1
DESPIECE - CILINDRO 50 KG
Isometría explosionada, esc. 1:5. Globo = sufijo del código BOM (hoja FL_REC_ABC_50kg)
LISTA DE DESPIECE - BOM FL_REC_ABC_50kg
Glo.
Código BOM
Denominación
Cant.
Material
ABC50-S1
RECIPIENTE (CILINDRO)
ABC50-01
Cuerpo (virola)
Chapa LAC IRAM-IAS U 500-0
ABC50-02
Cúpula
ABC50-03
Fondo
ABC50-04
Cuello roscado
Acero SAE 1010
C1
ABC50-C1
Alambre MAG ER70S-6 Ø1,0 (AWS A5.18)
0,4262 kg
ER70S-6
C2
ABC50-C2
Gas de protección MAG Arcal 21 / ARCAL Spe
68,3 L
EN ISO 14175 M20-ArC-8
C4
ABC50-C4
Servicio de pintura en polvo al horno, roj
Servicio tercerizado
ABC50-T1
Tapón protector de rosca del cuello
Polietileno
T2
ABC50-T2
Marcado del recipiente: grabado en el cuer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
