TadeoSinay/planos_flama-/salida/senaletica/FL_SEN_07.dxf

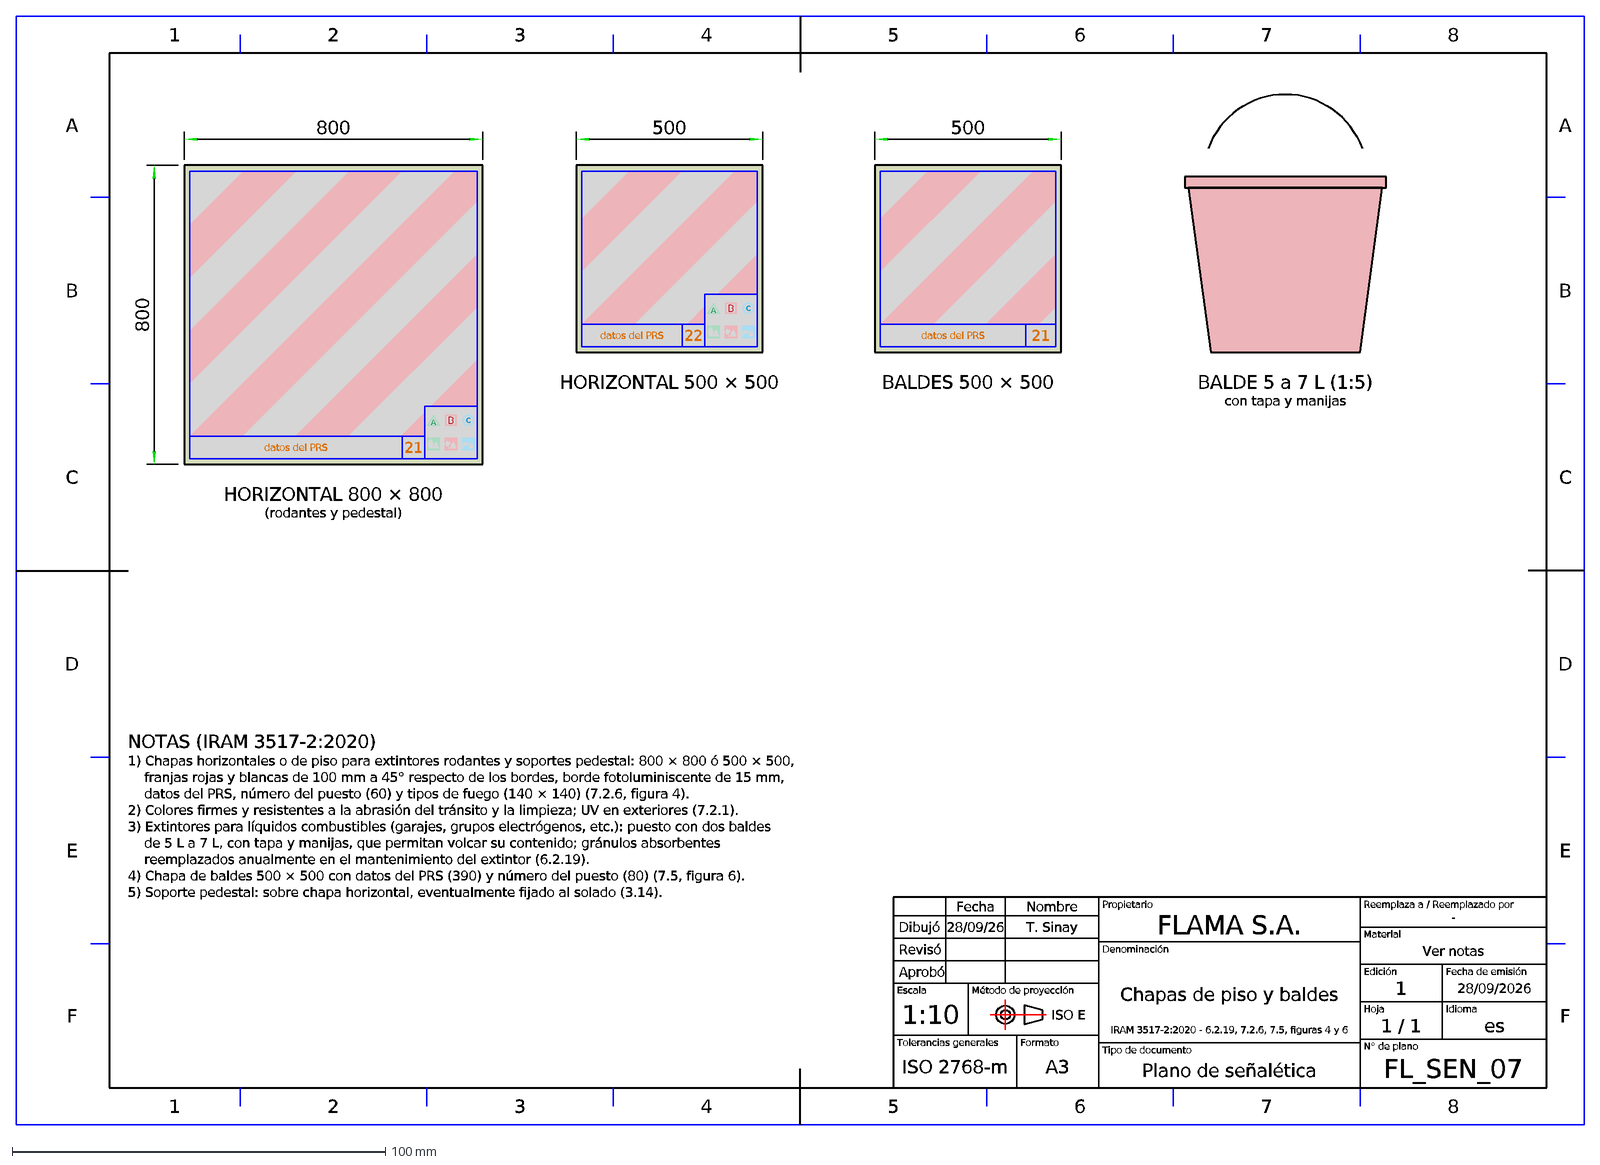
[picture p88: CAD file, 2026-10-10]
salida/senaletica/FL_SEN_07.dxf
1
2
3
4
5
6
7
8
F
E
D
C
B
A
Fecha
Nombre
Dibujó
28/09/26
T. Sinay
Revisó
Aprobó
Escala
1:10
Método de proyección
ISO E
Tolerancias generales
ISO 2768-m
Formato
A3
Propietario
FLAMA S.A.
Denominación
Chapas de piso y baldes
IRAM 3517-2:2020 - 6.2.19, 7.2.6, 7.5, figuras 4 y 6
Tipo de documento
Plano de señalética
Reemplaza a / Reemplazado por
-
Material
Ver notas
Edición
Fecha de emisión
28/09/2026
Hoja
1 / 1
Idioma
es
N° de plano
FL_SEN_07
datos del PRS
21
800
HORIZONTAL 800 × 800
(rodantes y pedestal)
22
500
HORIZONTAL 500 × 500
BALDES 500 × 500
BALDE 5 a 7 L (1:5)
con tapa y manijas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
