TadeoSinay/planos_flama-/salida/cilindros/despiece/FL_DES_REC_ABC_25kg.dxf

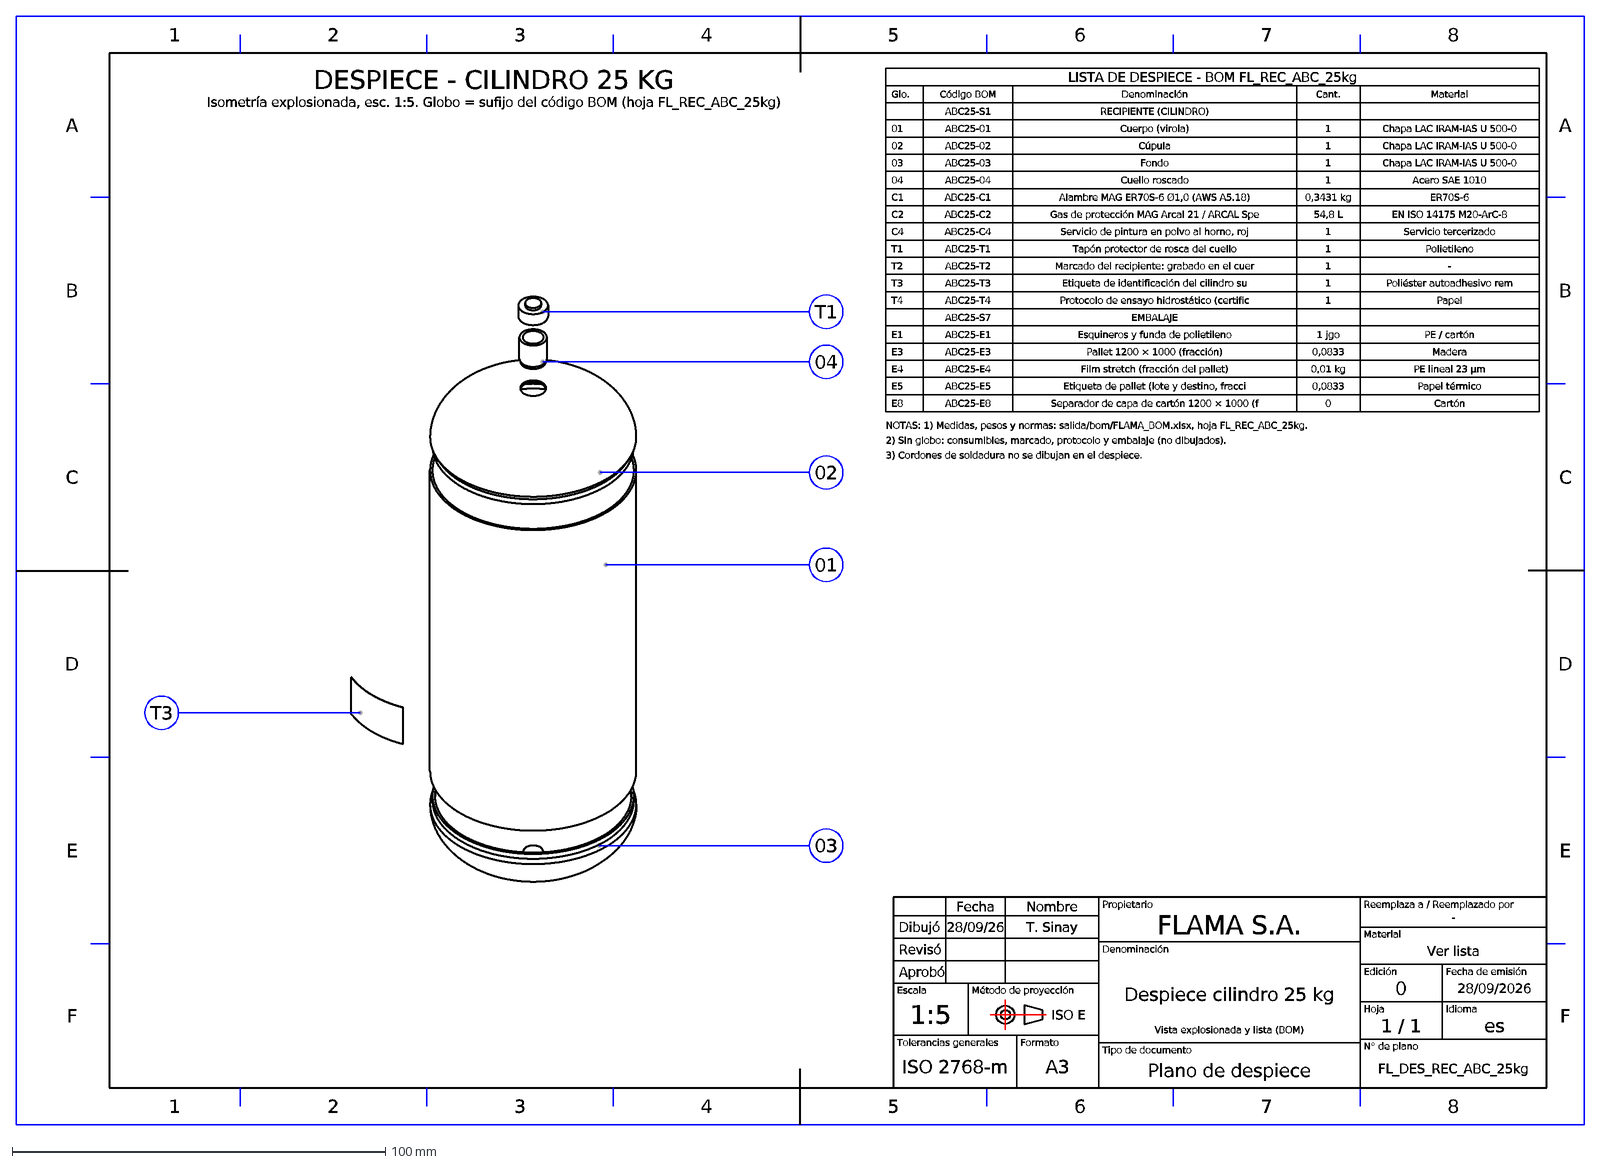
[picture p90: CAD file, 2026-10-10]
salida/cilindros/despiece/FL_DES_REC_ABC_25kg.dxf
1
2
3
4
5
6
7
8
F
E
D
C
B
A
T3
03
01
02
04
T1
DESPIECE - CILINDRO 25 KG
Isometría explosionada, esc. 1:5. Globo = sufijo del código BOM (hoja FL_REC_ABC_25kg)
LISTA DE DESPIECE - BOM FL_REC_ABC_25kg
Glo.
Código BOM
Denominación
Cant.
Material
ABC25-S1
RECIPIENTE (CILINDRO)
ABC25-01
Cuerpo (virola)
Chapa LAC IRAM-IAS U 500-0
ABC25-02
Cúpula
ABC25-03
Fondo
ABC25-04
Cuello roscado
Acero SAE 1010
C1
ABC25-C1
Alambre MAG ER70S-6 Ø1,0 (AWS A5.18)
0,3431 kg
ER70S-6
C2
ABC25-C2
Gas de protección MAG Arcal 21 / ARCAL Spe
54,8 L
EN ISO 14175 M20-ArC-8
C4
ABC25-C4
Servicio de pintura en polvo al horno, roj
Servicio tercerizado
ABC25-T1
Tapón protector de rosca del cuello
Polietileno
T2
ABC25-T2
Marcado del recipiente: grabado en el cuer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
