TadeoSinay/planos_flama-/salida/senaletica/FL_SEN_08.dxf

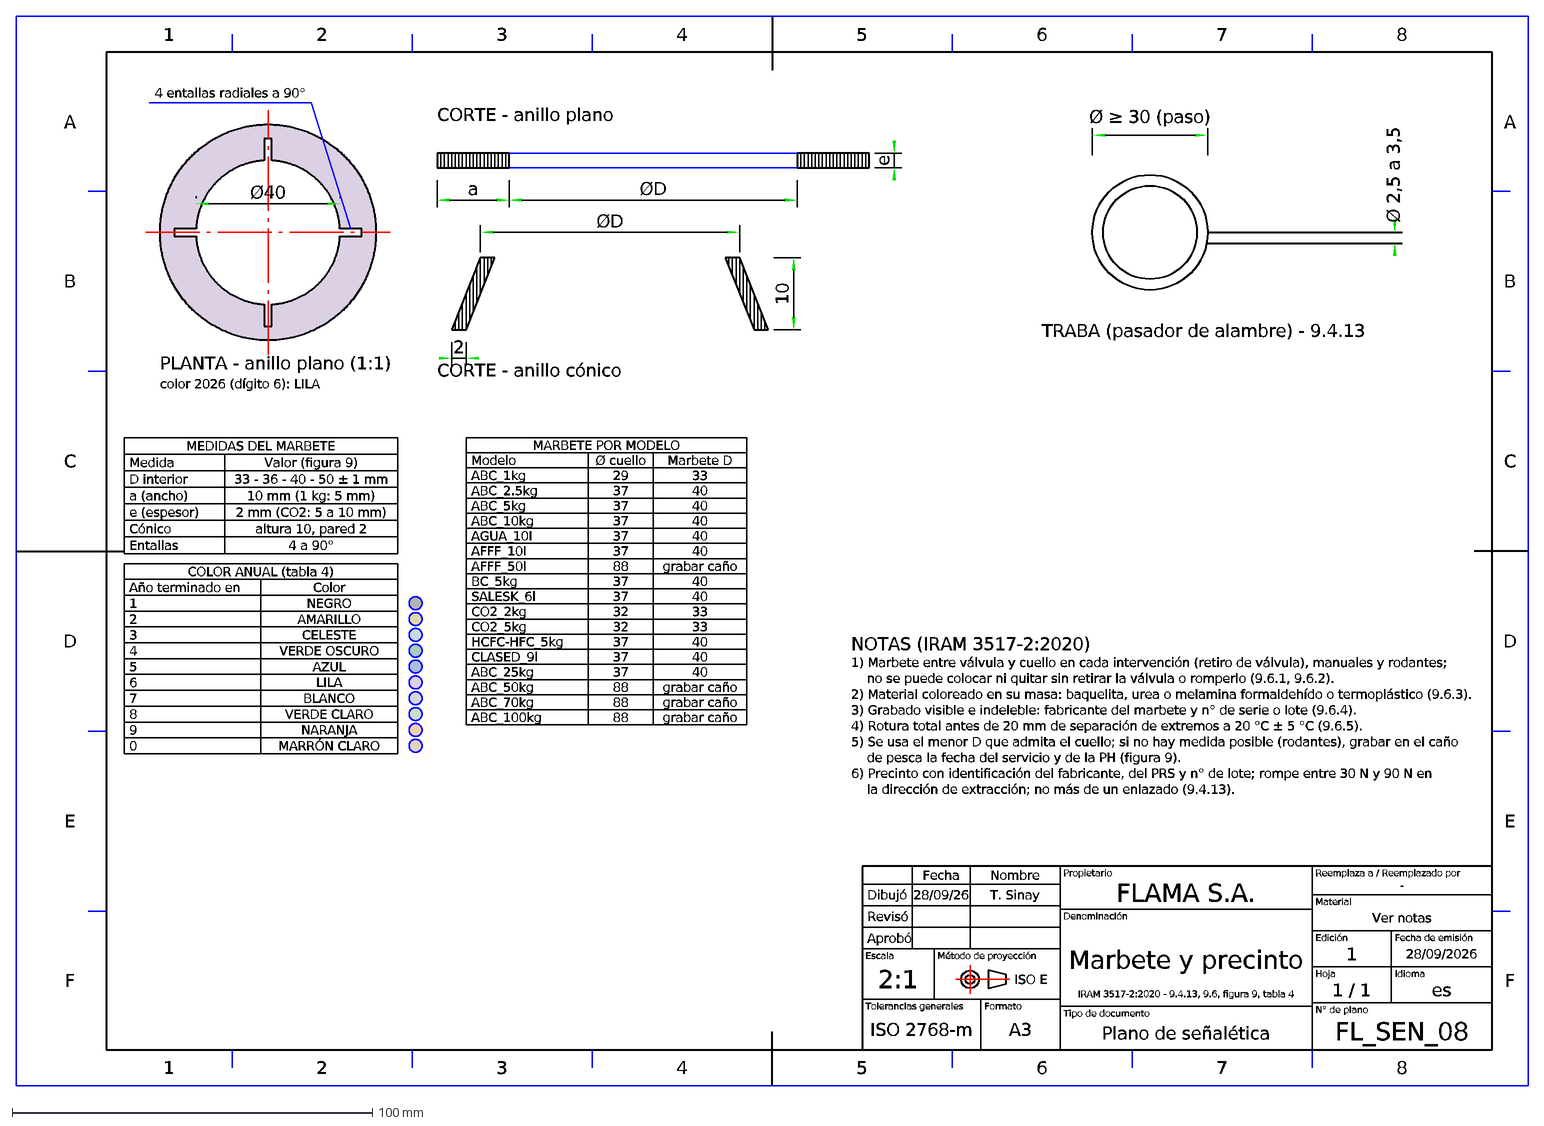
[picture p91: CAD file, 2026-10-10]
salida/senaletica/FL_SEN_08.dxf
1
2
3
4
5
6
7
8
F
E
D
C
B
A
Fecha
Nombre
Dibujó
28/09/26
T. Sinay
Revisó
Aprobó
Escala
2:1
Método de proyección
ISO E
Tolerancias generales
ISO 2768-m
Formato
A3
Propietario
FLAMA S.A.
Denominación
Marbete y precinto
IRAM 3517-2:2020 - 9.4.13, 9.6, figura 9, tabla 4
Tipo de documento
Plano de señalética
Reemplaza a / Reemplazado por
-
Material
Ver notas
Edición
Fecha de emisión
28/09/2026
Hoja
1 / 1
Idioma
es
N° de plano
FL_SEN_08
Ø40
PLANTA - anillo plano (1:1)
color 2026 (dígito 6): LILA
4 entallas radiales a 90°
a
ØD
e
CORTE - anillo plano
10
CORTE - anillo cónico
MEDIDAS DEL MARBETE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
