TadeoSinay/planos_flama-/salida/cilindros/despiece/FL_DES_REC_ABC_2.5kg.dxf

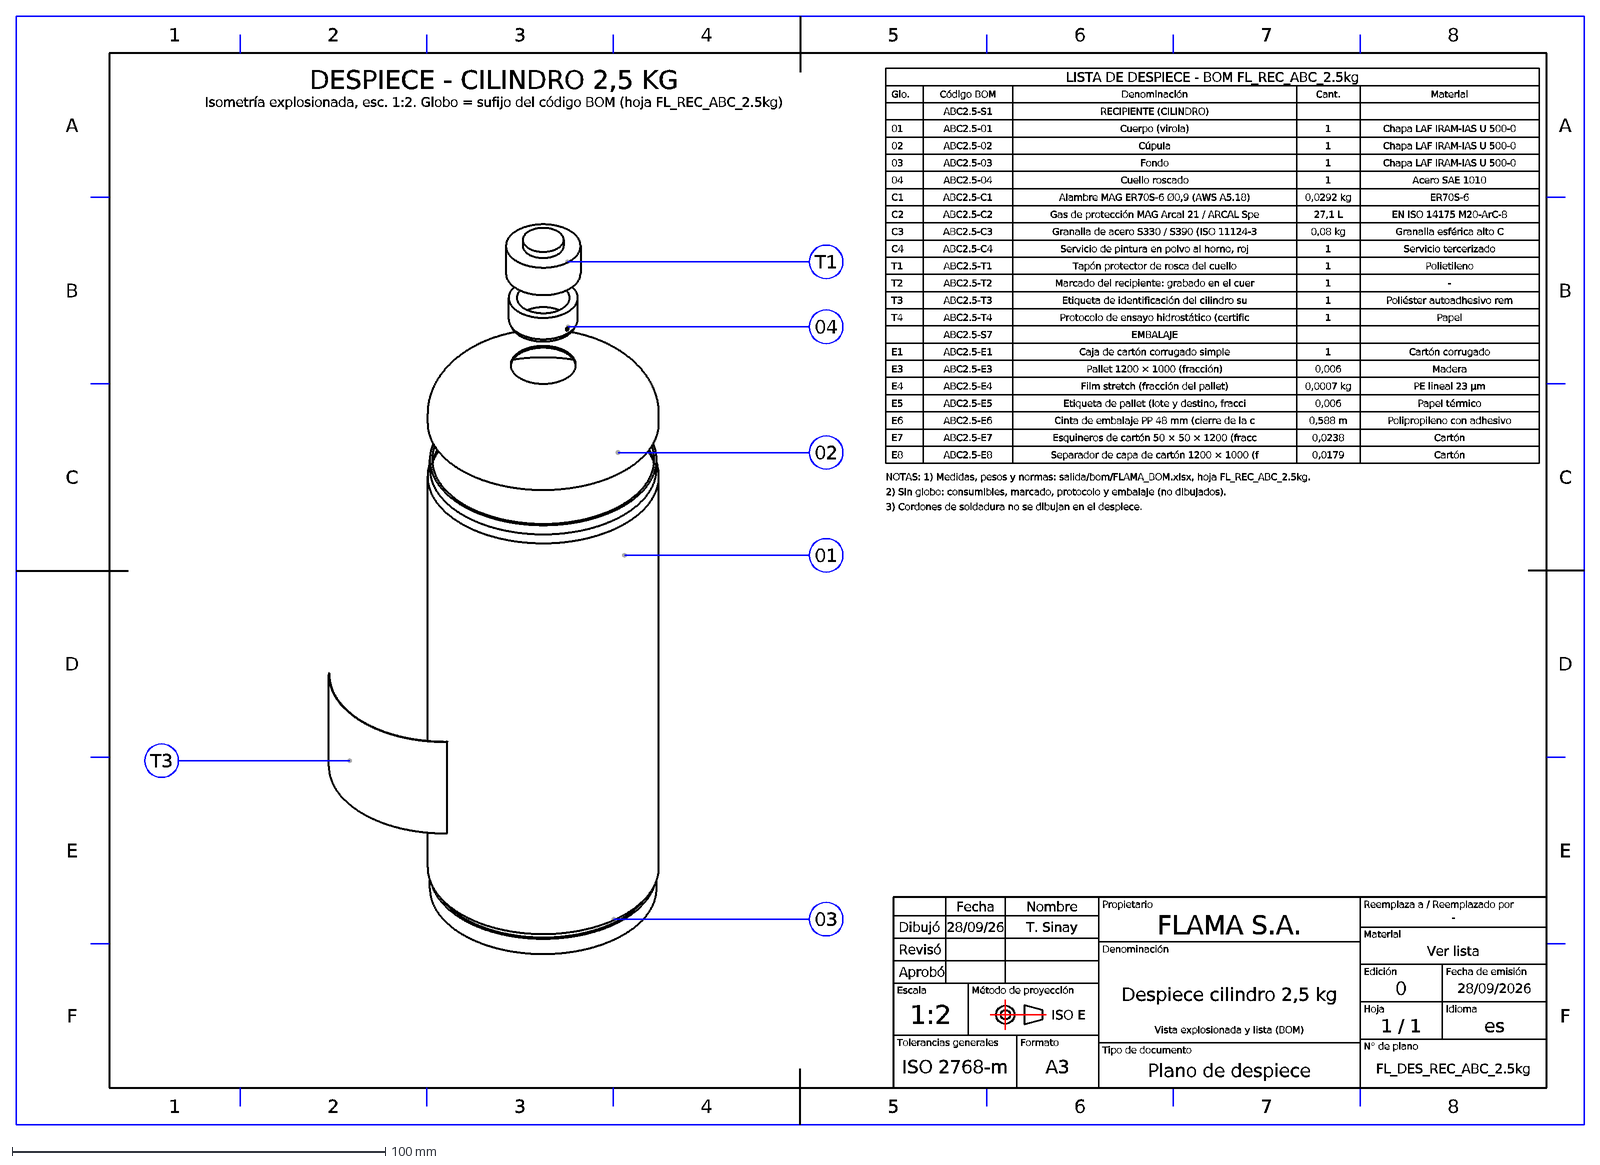
[picture p93: CAD file, 2026-10-10]
salida/cilindros/despiece/FL_DES_REC_ABC_2.5kg.dxf
1
2
3
4
5
6
7
8
F
E
D
C
B
A
T3
03
01
02
04
T1
DESPIECE - CILINDRO 2,5 KG
Isometría explosionada, esc. 1:2. Globo = sufijo del código BOM (hoja FL_REC_ABC_2.5kg)
LISTA DE DESPIECE - BOM FL_REC_ABC_2.5kg
Glo.
Código BOM
Denominación
Cant.
Material
ABC2.5-S1
RECIPIENTE (CILINDRO)
ABC2.5-01
Cuerpo (virola)
Chapa LAF IRAM-IAS U 500-0
ABC2.5-02
Cúpula
ABC2.5-03
Fondo
ABC2.5-04
Cuello roscado
Acero SAE 1010
C1
ABC2.5-C1
Alambre MAG ER70S-6 Ø0,9 (AWS A5.18)
0,0292 kg
ER70S-6
C2
ABC2.5-C2
Gas de protección MAG Arcal 21 / ARCAL Spe
27,1 L
EN ISO 14175 M20-ArC-8
C3
ABC2.5-C3
Granalla de acero S330 / S390 (ISO 11124-3
0,08 kg
Granalla esférica alto C
C4
ABC2.5-C4
Servicio de pintura en polvo al horno, roj
Servicio tercerizado
ABC2.5-T1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
