TadeoSinay/planos_flama-/salida/senaletica/FL_SEN_05.dxf

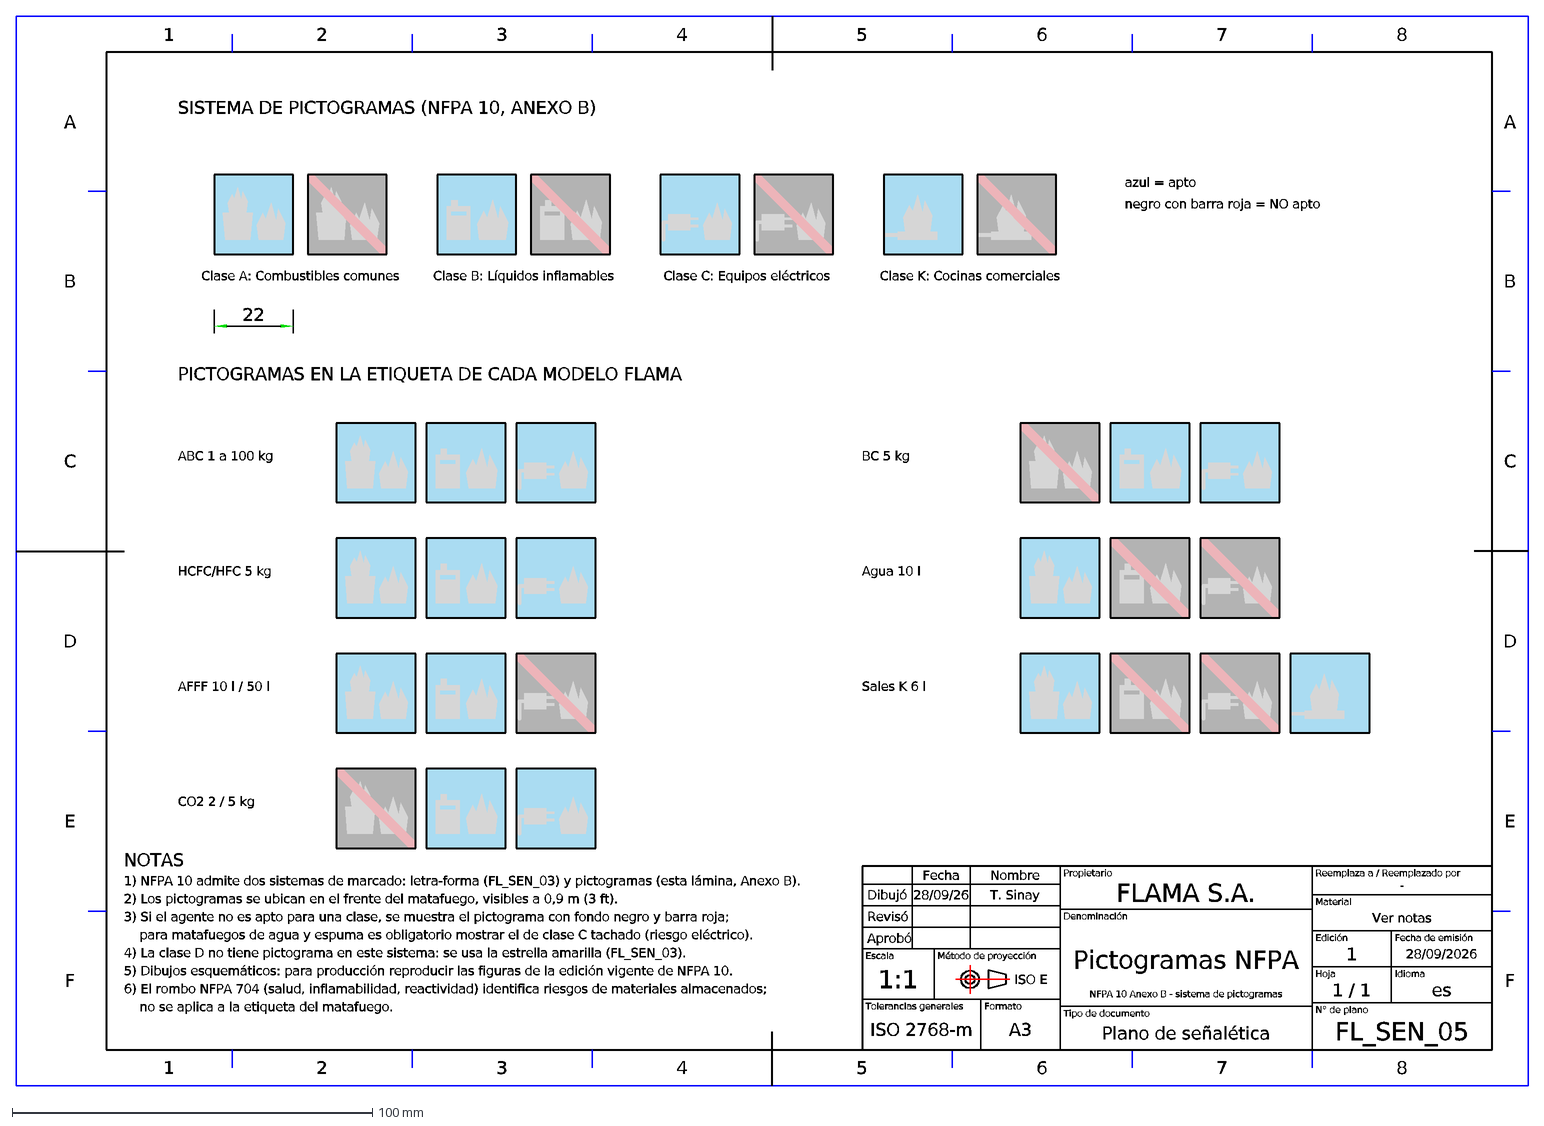
[picture p94: CAD file, 2026-10-10]
salida/senaletica/FL_SEN_05.dxf
1
2
3
4
5
6
7
8
F
E
D
C
B
A
Fecha
Nombre
Dibujó
28/09/26
T. Sinay
Revisó
Aprobó
Escala
1:1
Método de proyección
ISO E
Tolerancias generales
ISO 2768-m
Formato
A3
Propietario
FLAMA S.A.
Denominación
Pictogramas NFPA
NFPA 10 Anexo B - sistema de pictogramas
Tipo de documento
Plano de señalética
Reemplaza a / Reemplazado por
-
Material
Ver notas
Edición
Fecha de emisión
28/09/2026
Hoja
1 / 1
Idioma
es
N° de plano
FL_SEN_05
SISTEMA DE PICTOGRAMAS (NFPA 10, ANEXO B)
Clase A: Combustibles comunes
Clase B: Líquidos inflamables
Clase C: Equipos eléctricos
Clase K: Cocinas comerciales
azul = apto
negro con barra roja = NO apto
22
PICTOGRAMAS EN LA ETIQUETA DE CADA MODELO FLAMA
ABC 1 a 100 kg
BC 5 kg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
