TadeoSinay/planos_flama-/salida/sustituto/FL_SUS_00.dxf

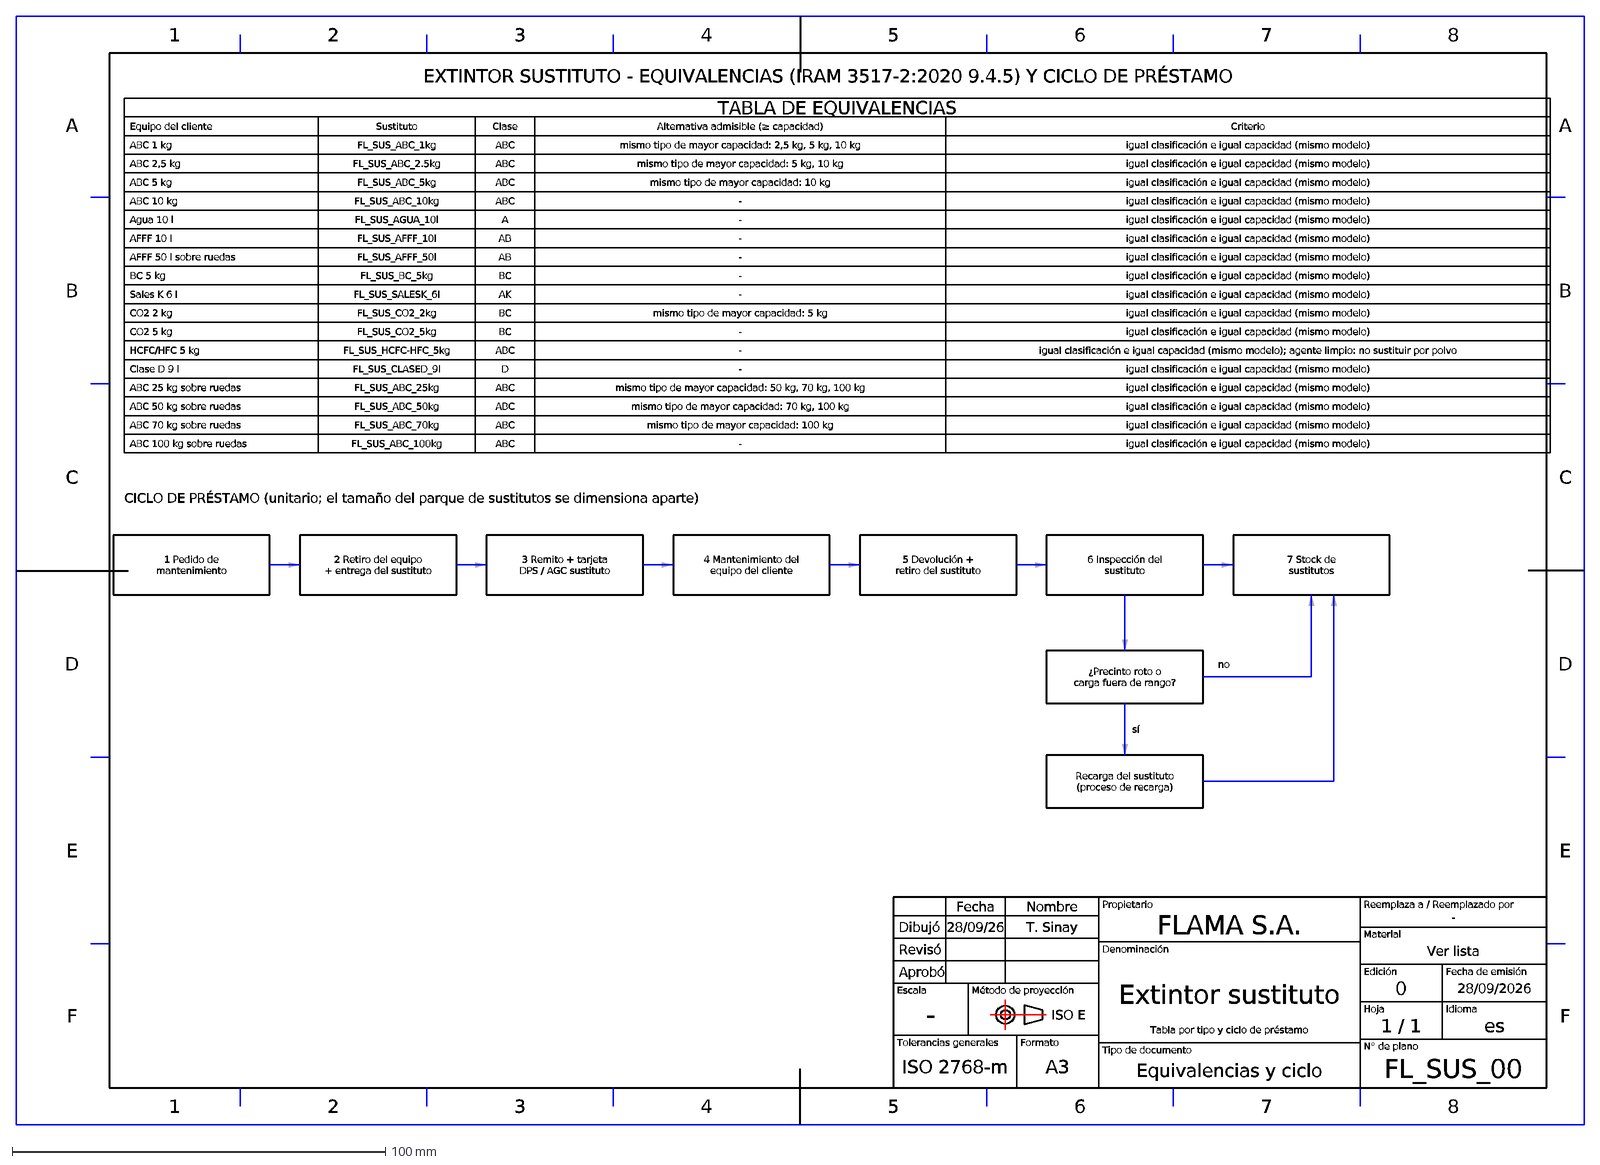
[picture p95: CAD file, 2026-10-10]
salida/sustituto/FL_SUS_00.dxf
1
2
3
4
5
6
7
8
F
E
D
C
B
A
Fecha
Nombre
Dibujó
28/09/26
T. Sinay
Revisó
Aprobó
Escala
-
Método de proyección
ISO E
Tolerancias generales
ISO 2768-m
Formato
A3
Propietario
FLAMA S.A.
Denominación
Extintor sustituto
Tabla por tipo y ciclo de préstamo
Tipo de documento
Equivalencias y ciclo
Reemplaza a / Reemplazado por
Material
Ver lista
Edición
0
Fecha de emisión
28/09/2026
Hoja
1 / 1
Idioma
es
N° de plano
FL_SUS_00
EXTINTOR SUSTITUTO - EQUIVALENCIAS (IRAM 3517-2:2020 9.4.5) Y CICLO DE PRÉSTAMO
TABLA DE EQUIVALENCIAS
Equipo del cliente
Sustituto
Clase
Alternativa admisible (≥ capacidad)
Criterio
ABC 1 kg
FL_SUS_ABC_1kg
ABC
mismo tipo de mayor capacidad: 2,5 kg, 5 kg, 10 kg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
