TadeoSinay/planos_flama-/salida/cilindros/despiece/FL_DES_REC_ABC_5kg.dxf

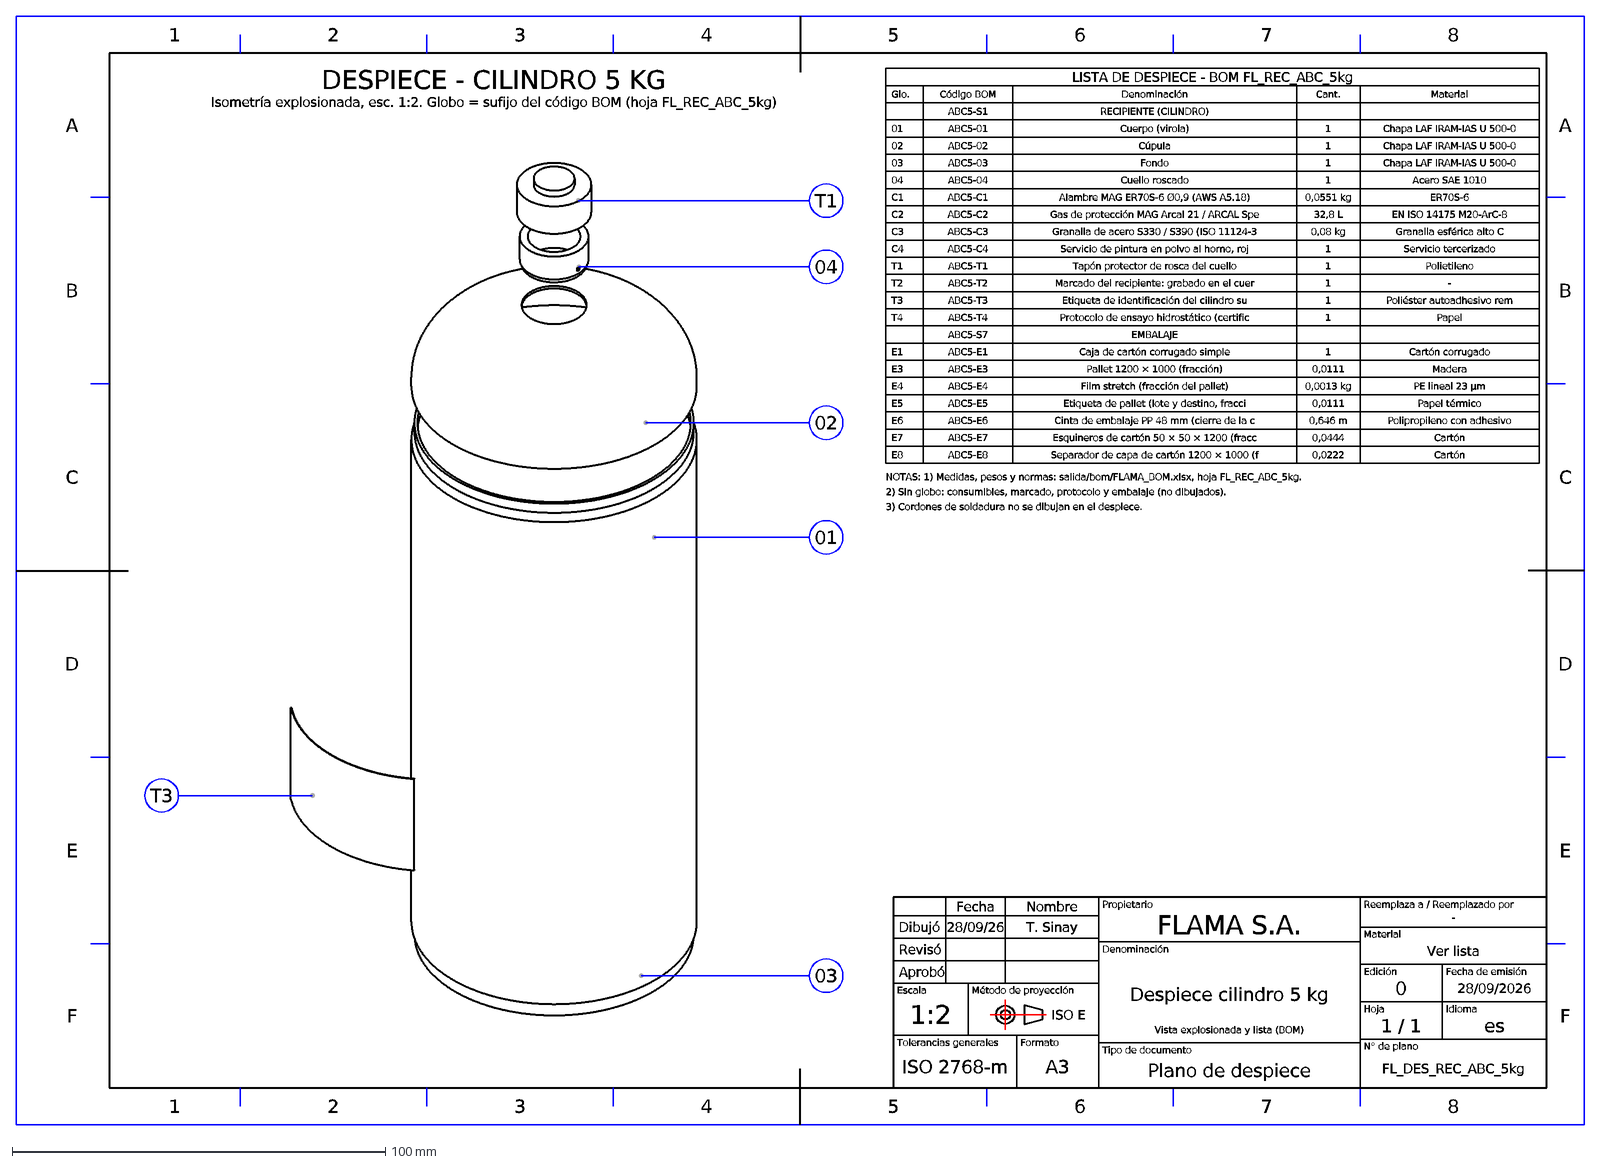
[picture p96: CAD file, 2026-10-10]
salida/cilindros/despiece/FL_DES_REC_ABC_5kg.dxf
1
2
3
4
5
6
7
8
F
E
D
C
B
A
T3
03
01
02
04
T1
DESPIECE - CILINDRO 5 KG
Isometría explosionada, esc. 1:2. Globo = sufijo del código BOM (hoja FL_REC_ABC_5kg)
LISTA DE DESPIECE - BOM FL_REC_ABC_5kg
Glo.
Código BOM
Denominación
Cant.
Material
ABC5-S1
RECIPIENTE (CILINDRO)
ABC5-01
Cuerpo (virola)
Chapa LAF IRAM-IAS U 500-0
ABC5-02
Cúpula
ABC5-03
Fondo
ABC5-04
Cuello roscado
Acero SAE 1010
C1
ABC5-C1
Alambre MAG ER70S-6 Ø0,9 (AWS A5.18)
0,0551 kg
ER70S-6
C2
ABC5-C2
Gas de protección MAG Arcal 21 / ARCAL Spe
32,8 L
EN ISO 14175 M20-ArC-8
C3
ABC5-C3
Granalla de acero S330 / S390 (ISO 11124-3
0,08 kg
Granalla esférica alto C
C4
ABC5-C4
Servicio de pintura en polvo al horno, roj
Servicio tercerizado
ABC5-T1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
