TadeoSinay/planos_flama-/salida/senaletica/FL_SEN_03.dxf

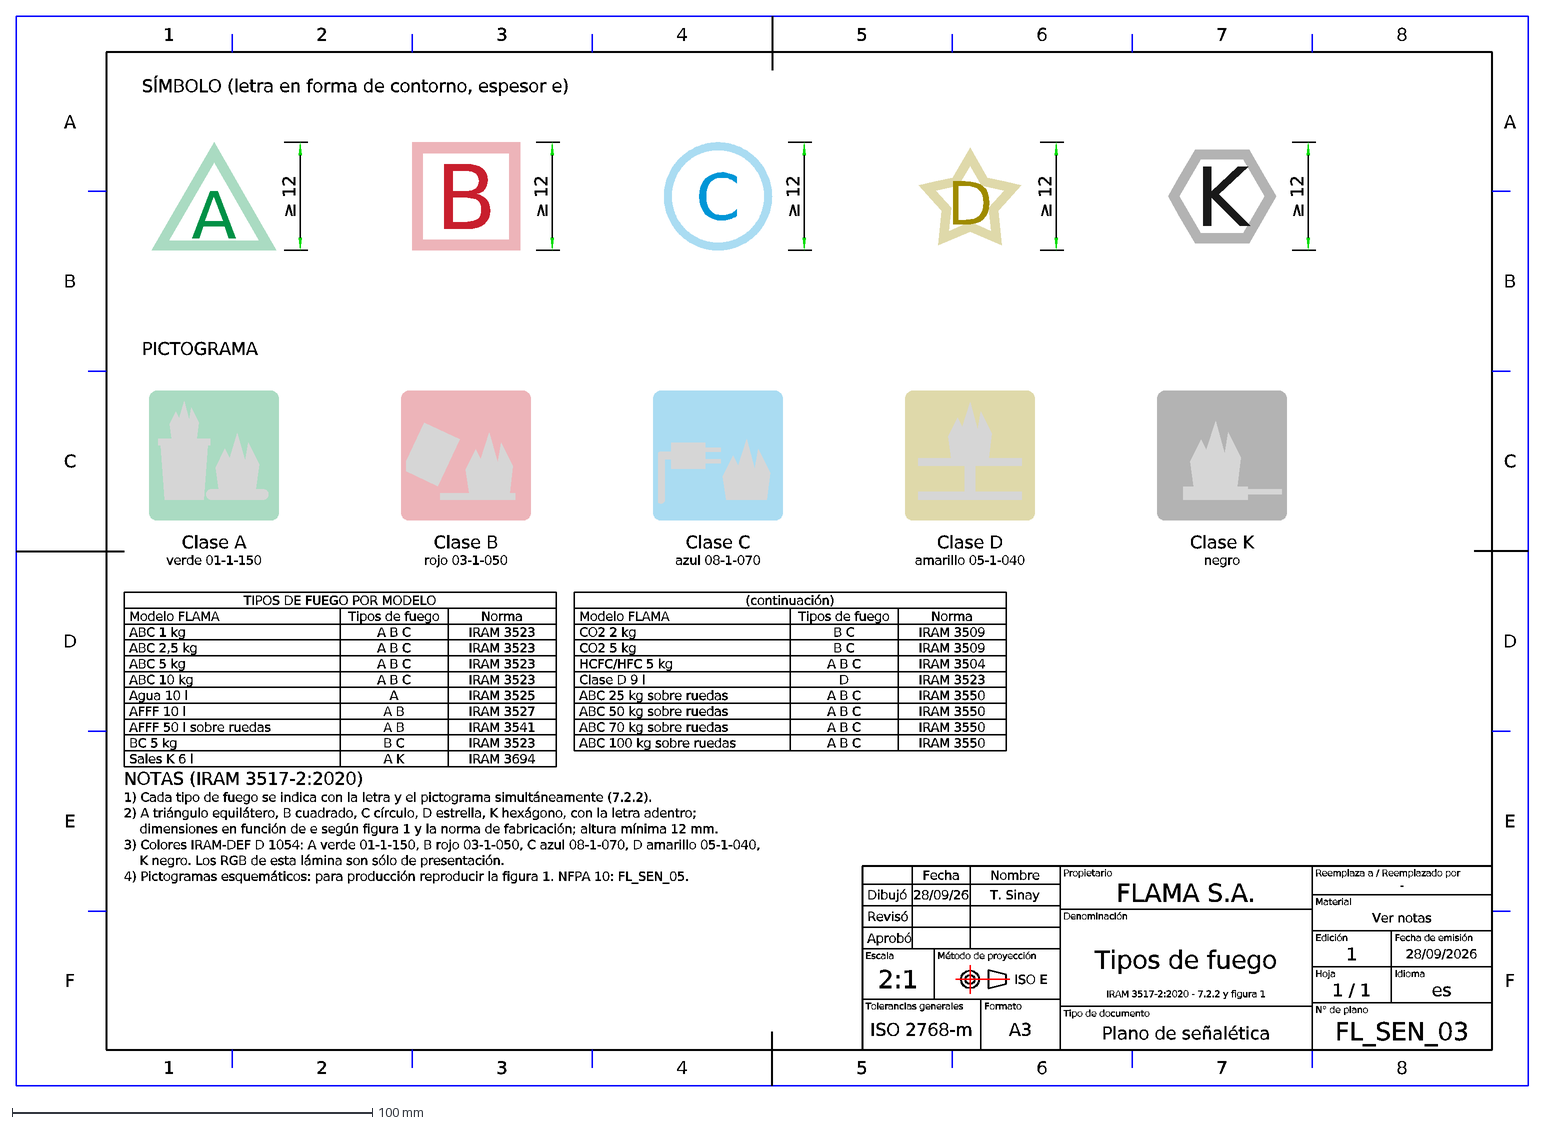
[picture p97: CAD file, 2026-10-10]
salida/senaletica/FL_SEN_03.dxf
1
2
3
4
5
6
7
8
F
E
D
C
B
A
Fecha
Nombre
Dibujó
28/09/26
T. Sinay
Revisó
Aprobó
Escala
2:1
Método de proyección
ISO E
Tolerancias generales
ISO 2768-m
Formato
A3
Propietario
FLAMA S.A.
Denominación
Tipos de fuego
IRAM 3517-2:2020 - 7.2.2 y figura 1
Tipo de documento
Plano de señalética
Reemplaza a / Reemplazado por
-
Material
Ver notas
Edición
Fecha de emisión
28/09/2026
Hoja
1 / 1
Idioma
es
N° de plano
FL_SEN_03
SÍMBOLO (letra en forma de contorno, espesor e)
PICTOGRAMA
≥ 12
Clase A
verde 01-1-150
Clase B
rojo 03-1-050
Clase C
azul 08-1-070
Clase D
amarillo 05-1-040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
