TadeoSinay/planos_flama-/salida/senaletica/FL_SEN_01.dxf

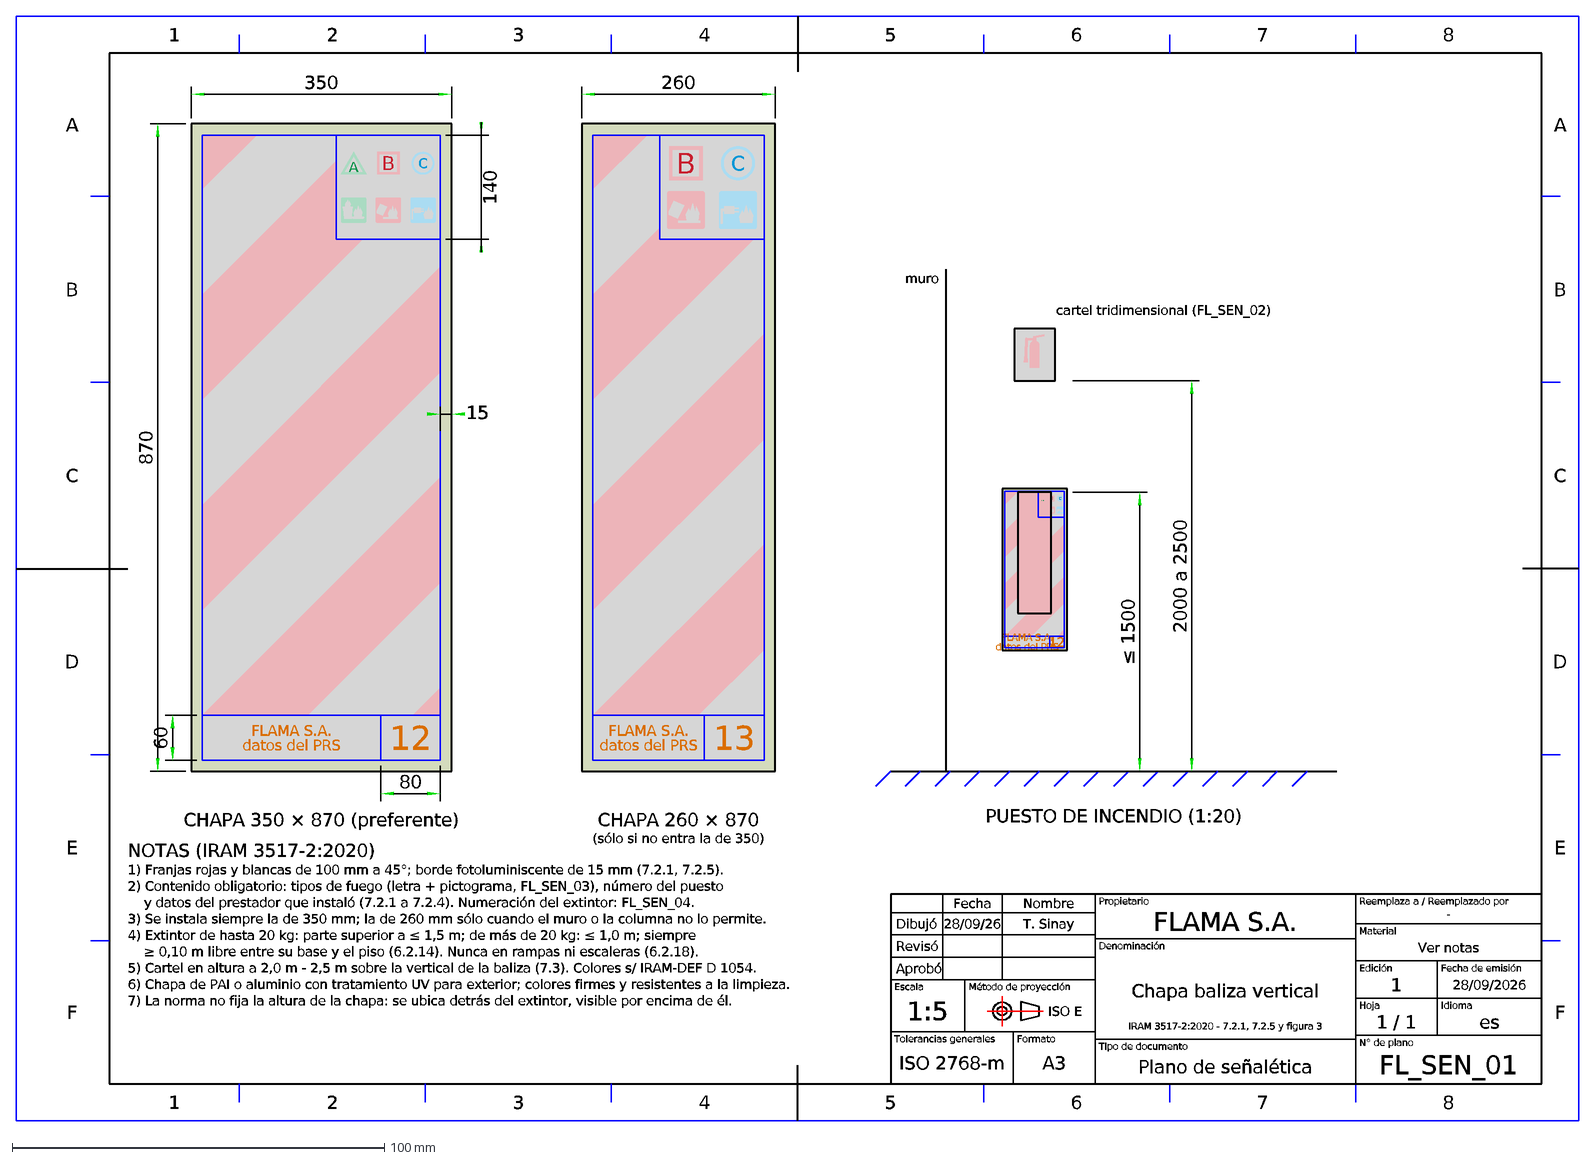
[picture p99: CAD file, 2026-10-10]
salida/senaletica/FL_SEN_01.dxf
1
2
3
4
5
6
7
8
F
E
D
C
B
A
Fecha
Nombre
Dibujó
28/09/26
T. Sinay
Revisó
Aprobó
Escala
1:5
Método de proyección
ISO E
Tolerancias generales
ISO 2768-m
Formato
A3
Propietario
FLAMA S.A.
Denominación
Chapa baliza vertical
IRAM 3517-2:2020 - 7.2.1, 7.2.5 y figura 3
Tipo de documento
Plano de señalética
Reemplaza a / Reemplazado por
-
Material
Ver notas
Edición
Fecha de emisión
28/09/2026
Hoja
1 / 1
Idioma
es
N° de plano
FL_SEN_01
datos del PRS
12
350
870
140
60
80
15
CHAPA 350 × 870 (preferente)
13
260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
