TadeoSinay/planos_flama-/salida/sustituto/FL_SUS_AFFF_50l.dxf

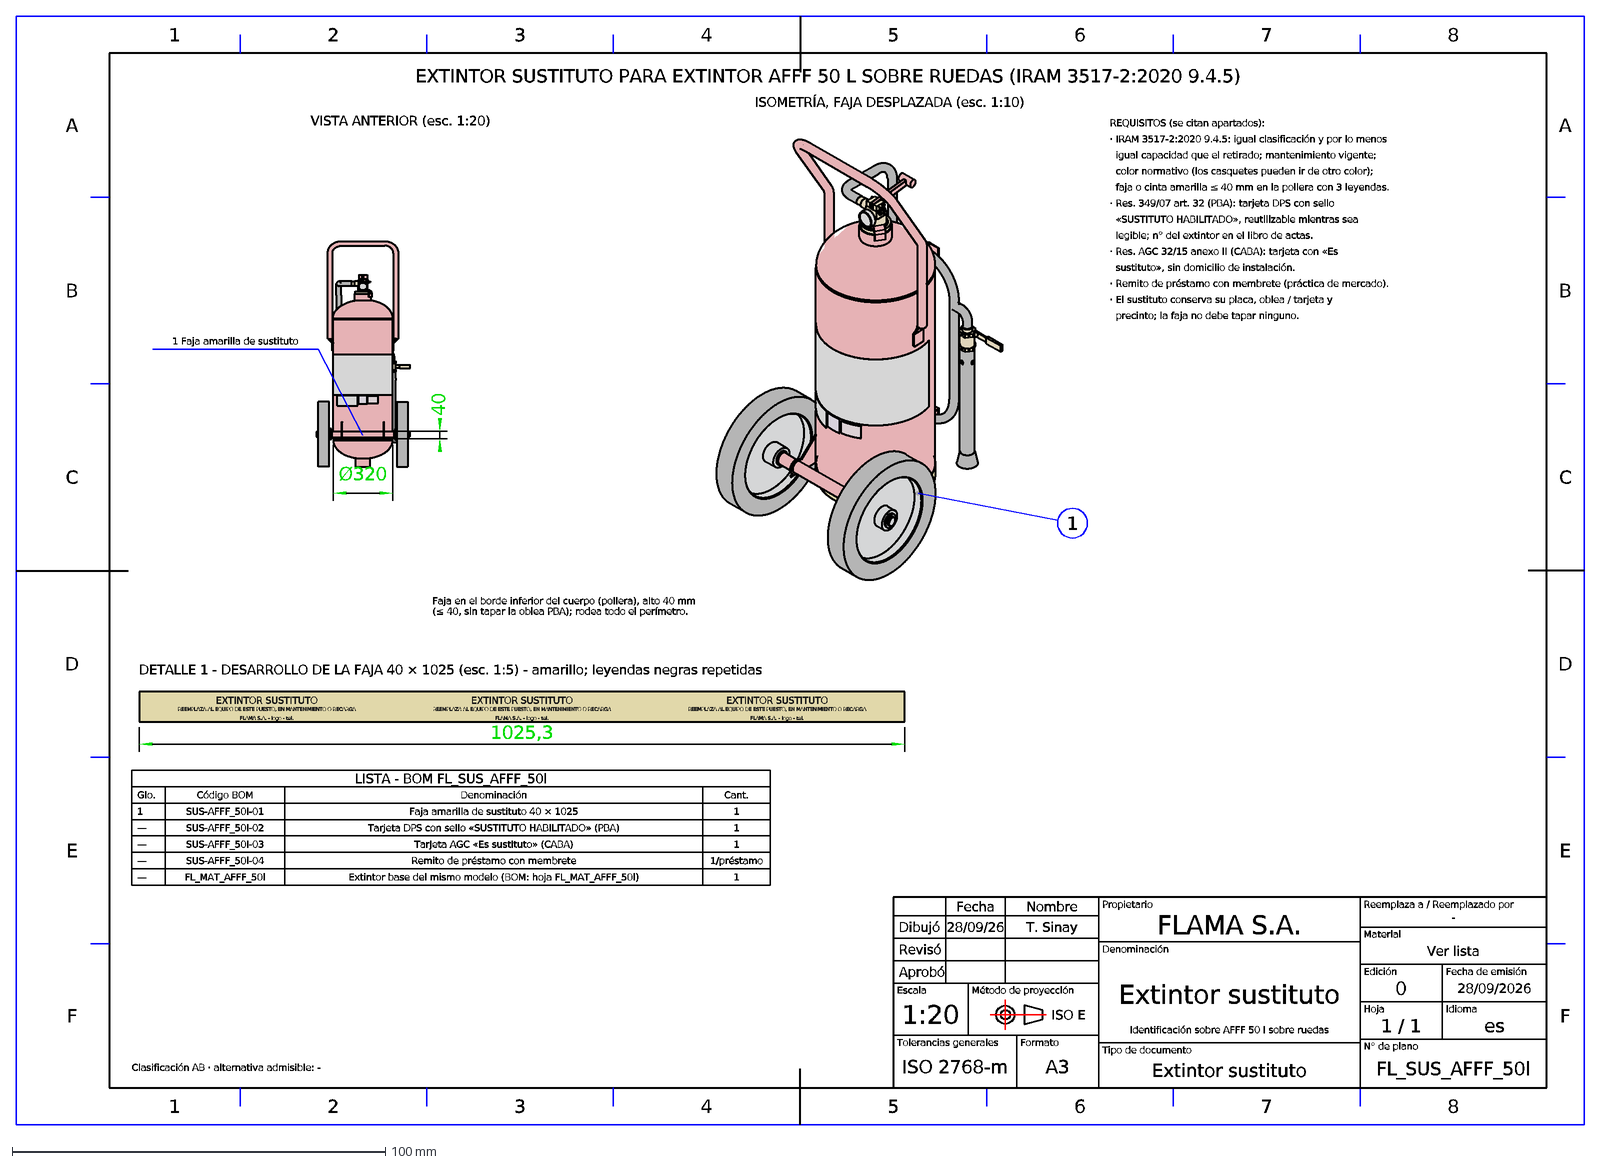
[picture p109: CAD file, 2026-10-10]
salida/sustituto/FL_SUS_AFFF_50l.dxf
1
2
3
4
5
6
7
8
F
E
D
C
B
A
EXTINTOR SUSTITUTO PARA EXTINTOR AFFF 50 L SOBRE RUEDAS (IRAM 3517-2:2020 9.4.5)
40
Ø320
1 Faja amarilla de sustituto
VISTA ANTERIOR (esc. 1:20)
ISOMETRÍA, FAJA DESPLAZADA (esc. 1:10)
REQUISITOS (se citan apartados):
· IRAM 3517-2:2020 9.4.5: igual clasificación y por lo menos
igual capacidad que el retirado; mantenimiento vigente;
color normativo (los casquetes pueden ir de otro color);
faja o cinta amarilla ≤ 40 mm en la pollera con 3 leyendas.
· Res. 349/07 art. 32 (PBA): tarjeta DPS con sello
«SUSTITUTO HABILITADO», reutilizable mientras sea
legible; n° del extintor en el libro de actas.
· Res. AGC 32/15 anexo II (CABA): tarjeta con «Es
sustituto», sin domicilio de instalación.
· Remito de préstamo con membrete (práctica de mercado).
· El sustituto conserva su placa, oblea / tarjeta y
precinto; la faja no debe tapar ninguno.
DETALLE 1 - DESARROLLO DE LA FAJA 40 × 1025 (esc. 1:5) - amarillo; leyendas negras repetidas
EXTINTOR SUSTITUTO
REEMPLAZA AL EQUIPO DE ESTE PUESTO, EN MANTENIMIENTO O RECARGA
FLAMA S.A. - logo - tel.
1025,3
LISTA - BOM FL_SUS_AFFF_50l
Glo.
Código BOM
Denominación
Cant.
SUS-AFFF_50l-01
Faja amarilla de sustituto 40 × 1025
—
SUS-AFFF_50l-02
Tarjeta DPS con sello «SUSTITUTO HABILITADO» (PBA)
SUS-AFFF_50l-03
Tarjeta AGC «Es sustituto» (CABA)
SUS-AFFF_50l-04
Remito de préstamo con membrete
1/préstamo
FL_MAT_AFFF_50l
Extintor base del mismo modelo (BOM: hoja FL_MAT_AFFF_50l)
Clasificación AB · alternativa admisible: -
Fecha
Nombre
Dibujó
28/09/26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
