TadeoSinay/planos_flama-/salida/despiece/FL_DES_ABC_5kg.pdf

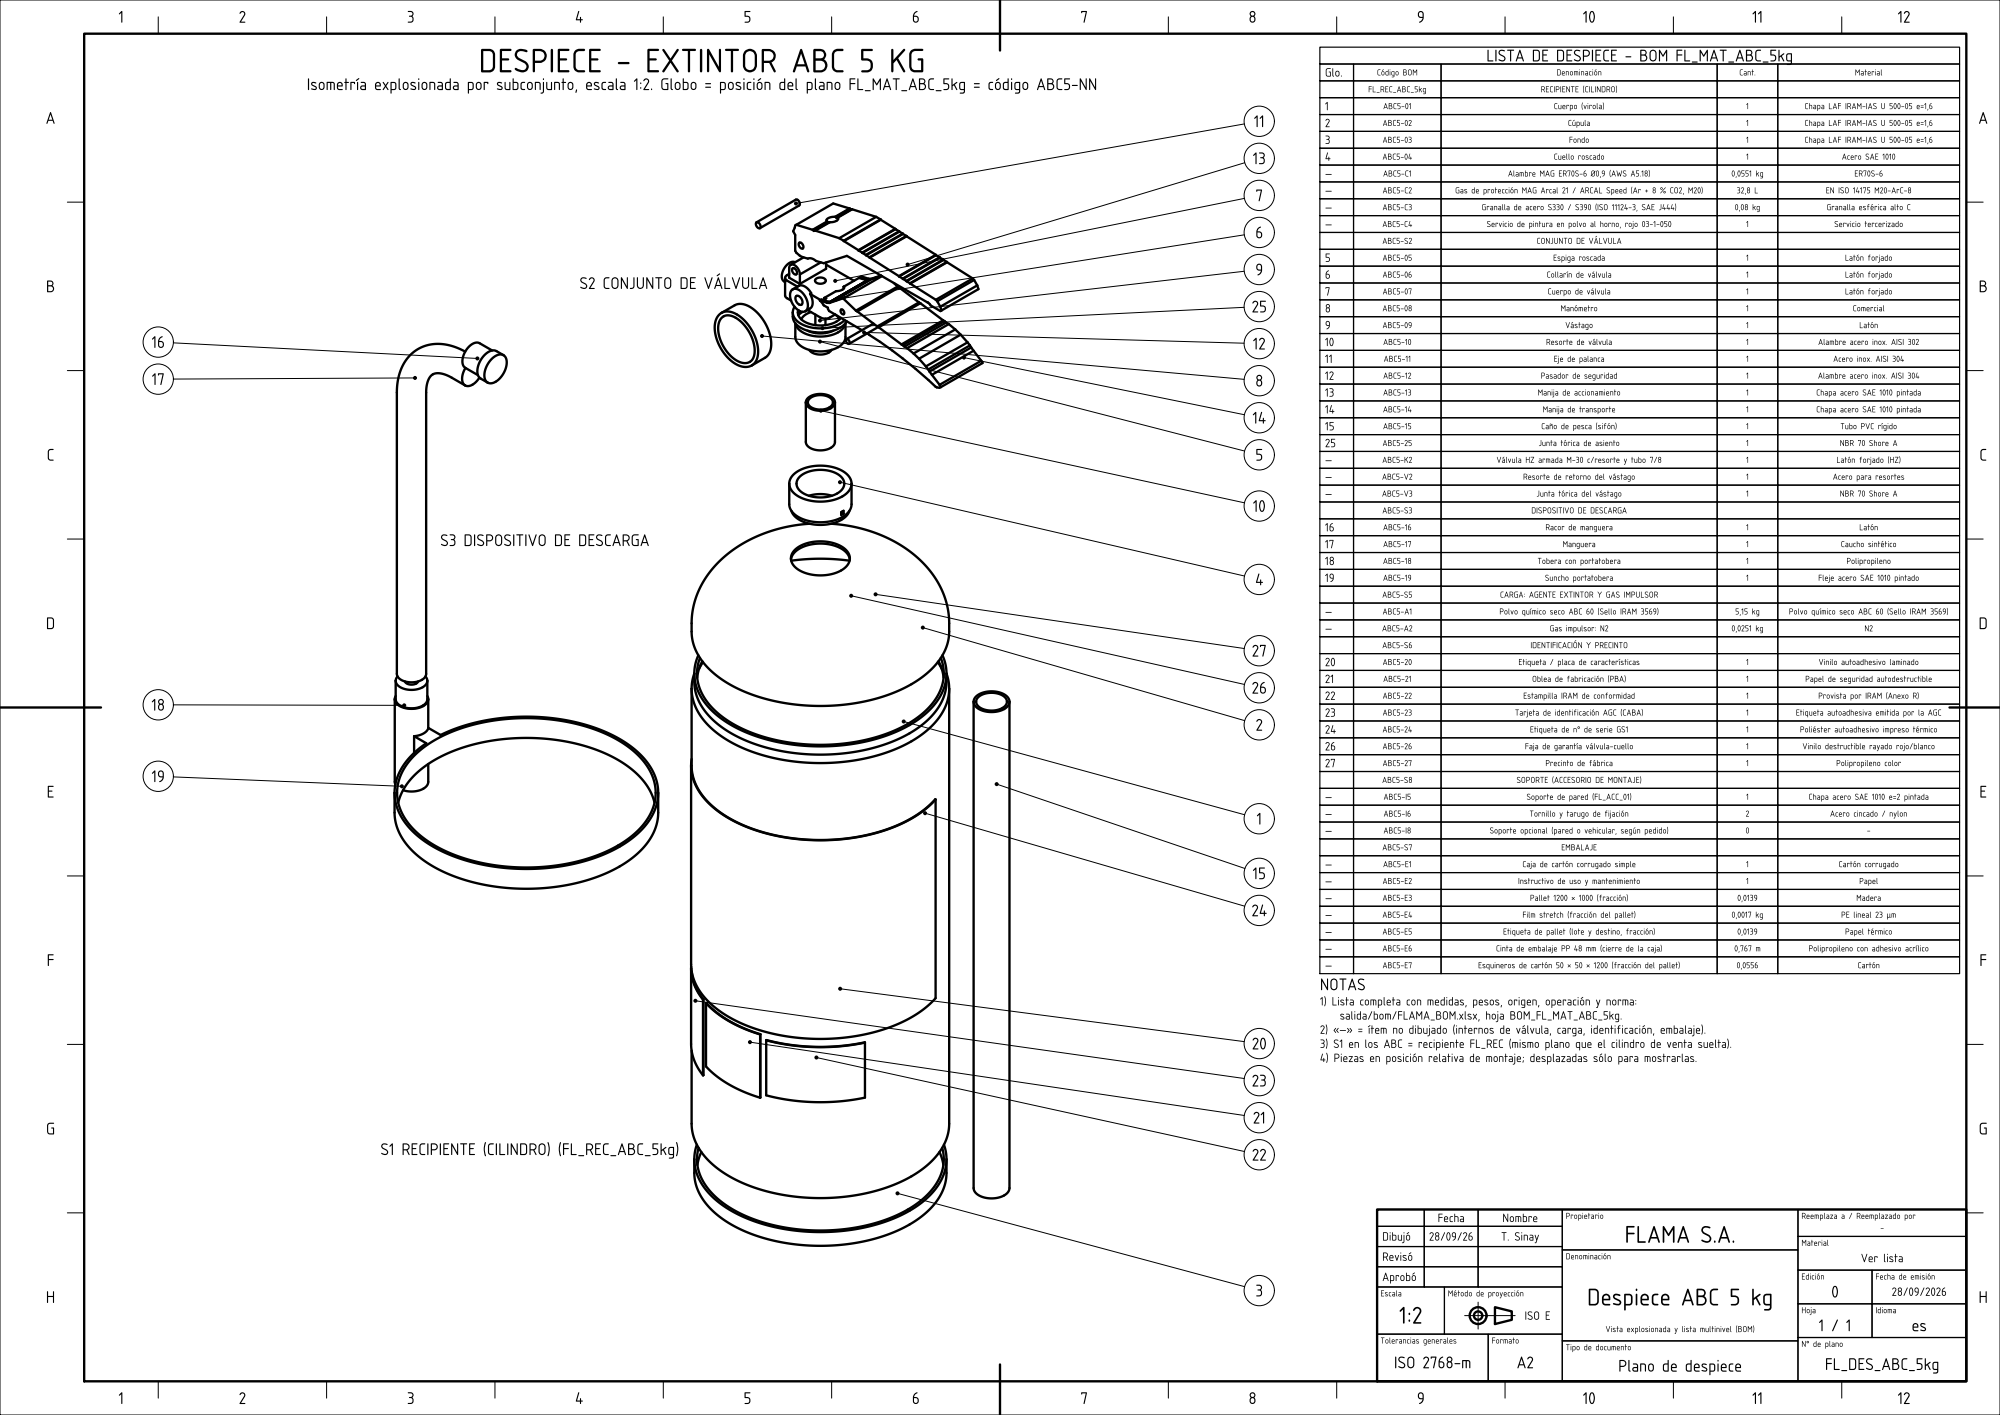
[picture p131: page 1]
