TadeoSinay/planos_flama-/salida/despiece/FL_DES_ABC_70kg.pdf

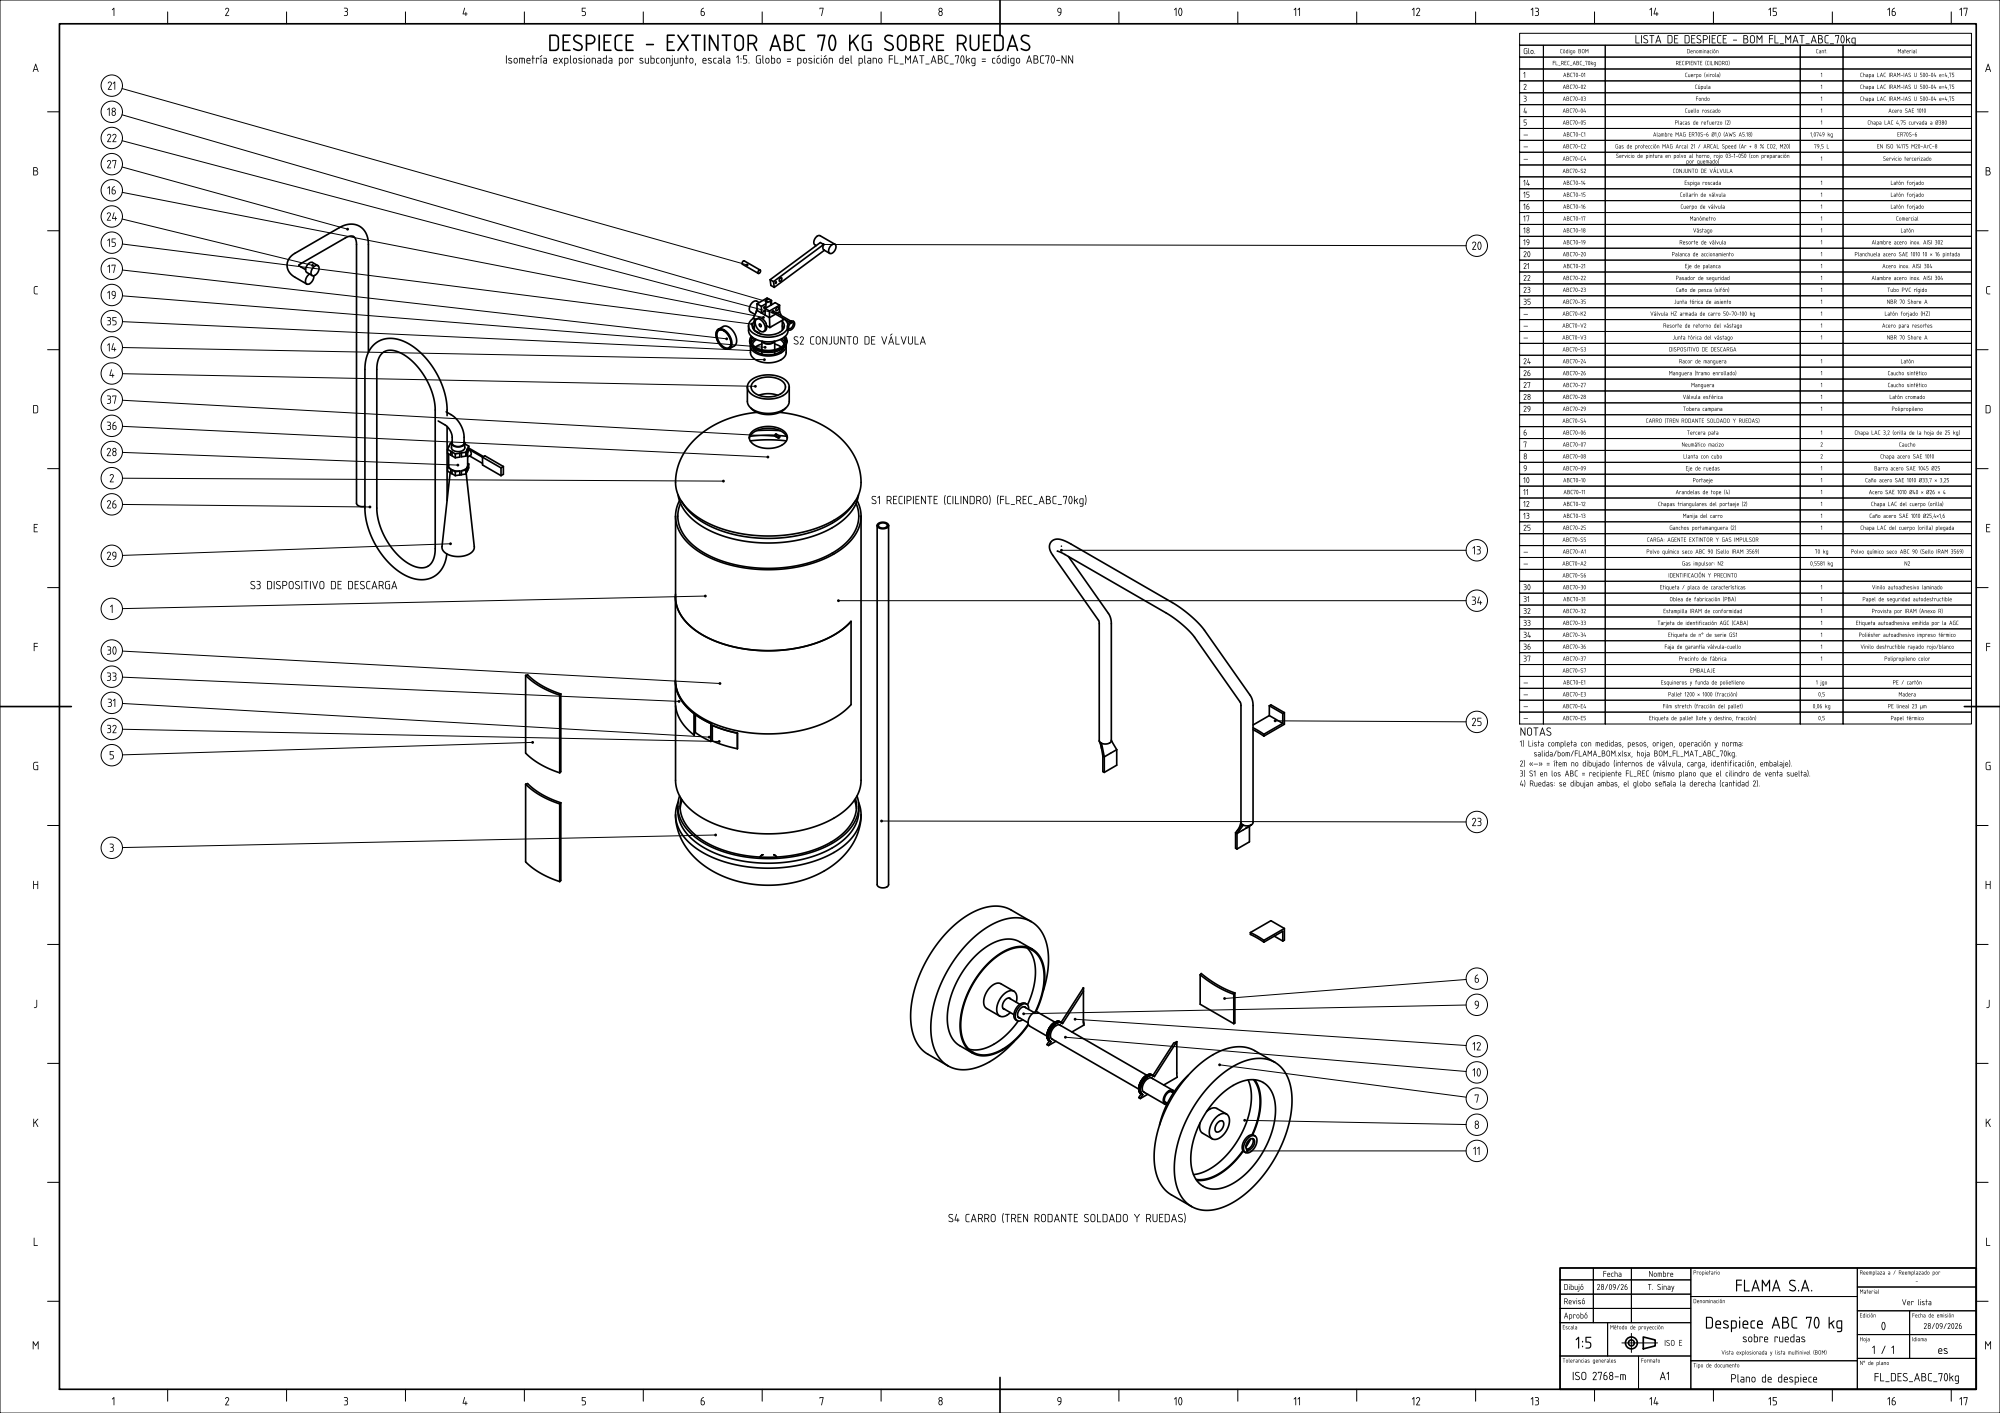
[picture p132: page 1]
