TadeoSinay/planos_flama-/salida/despiece/FL_DES_AFFF_10l.pdf

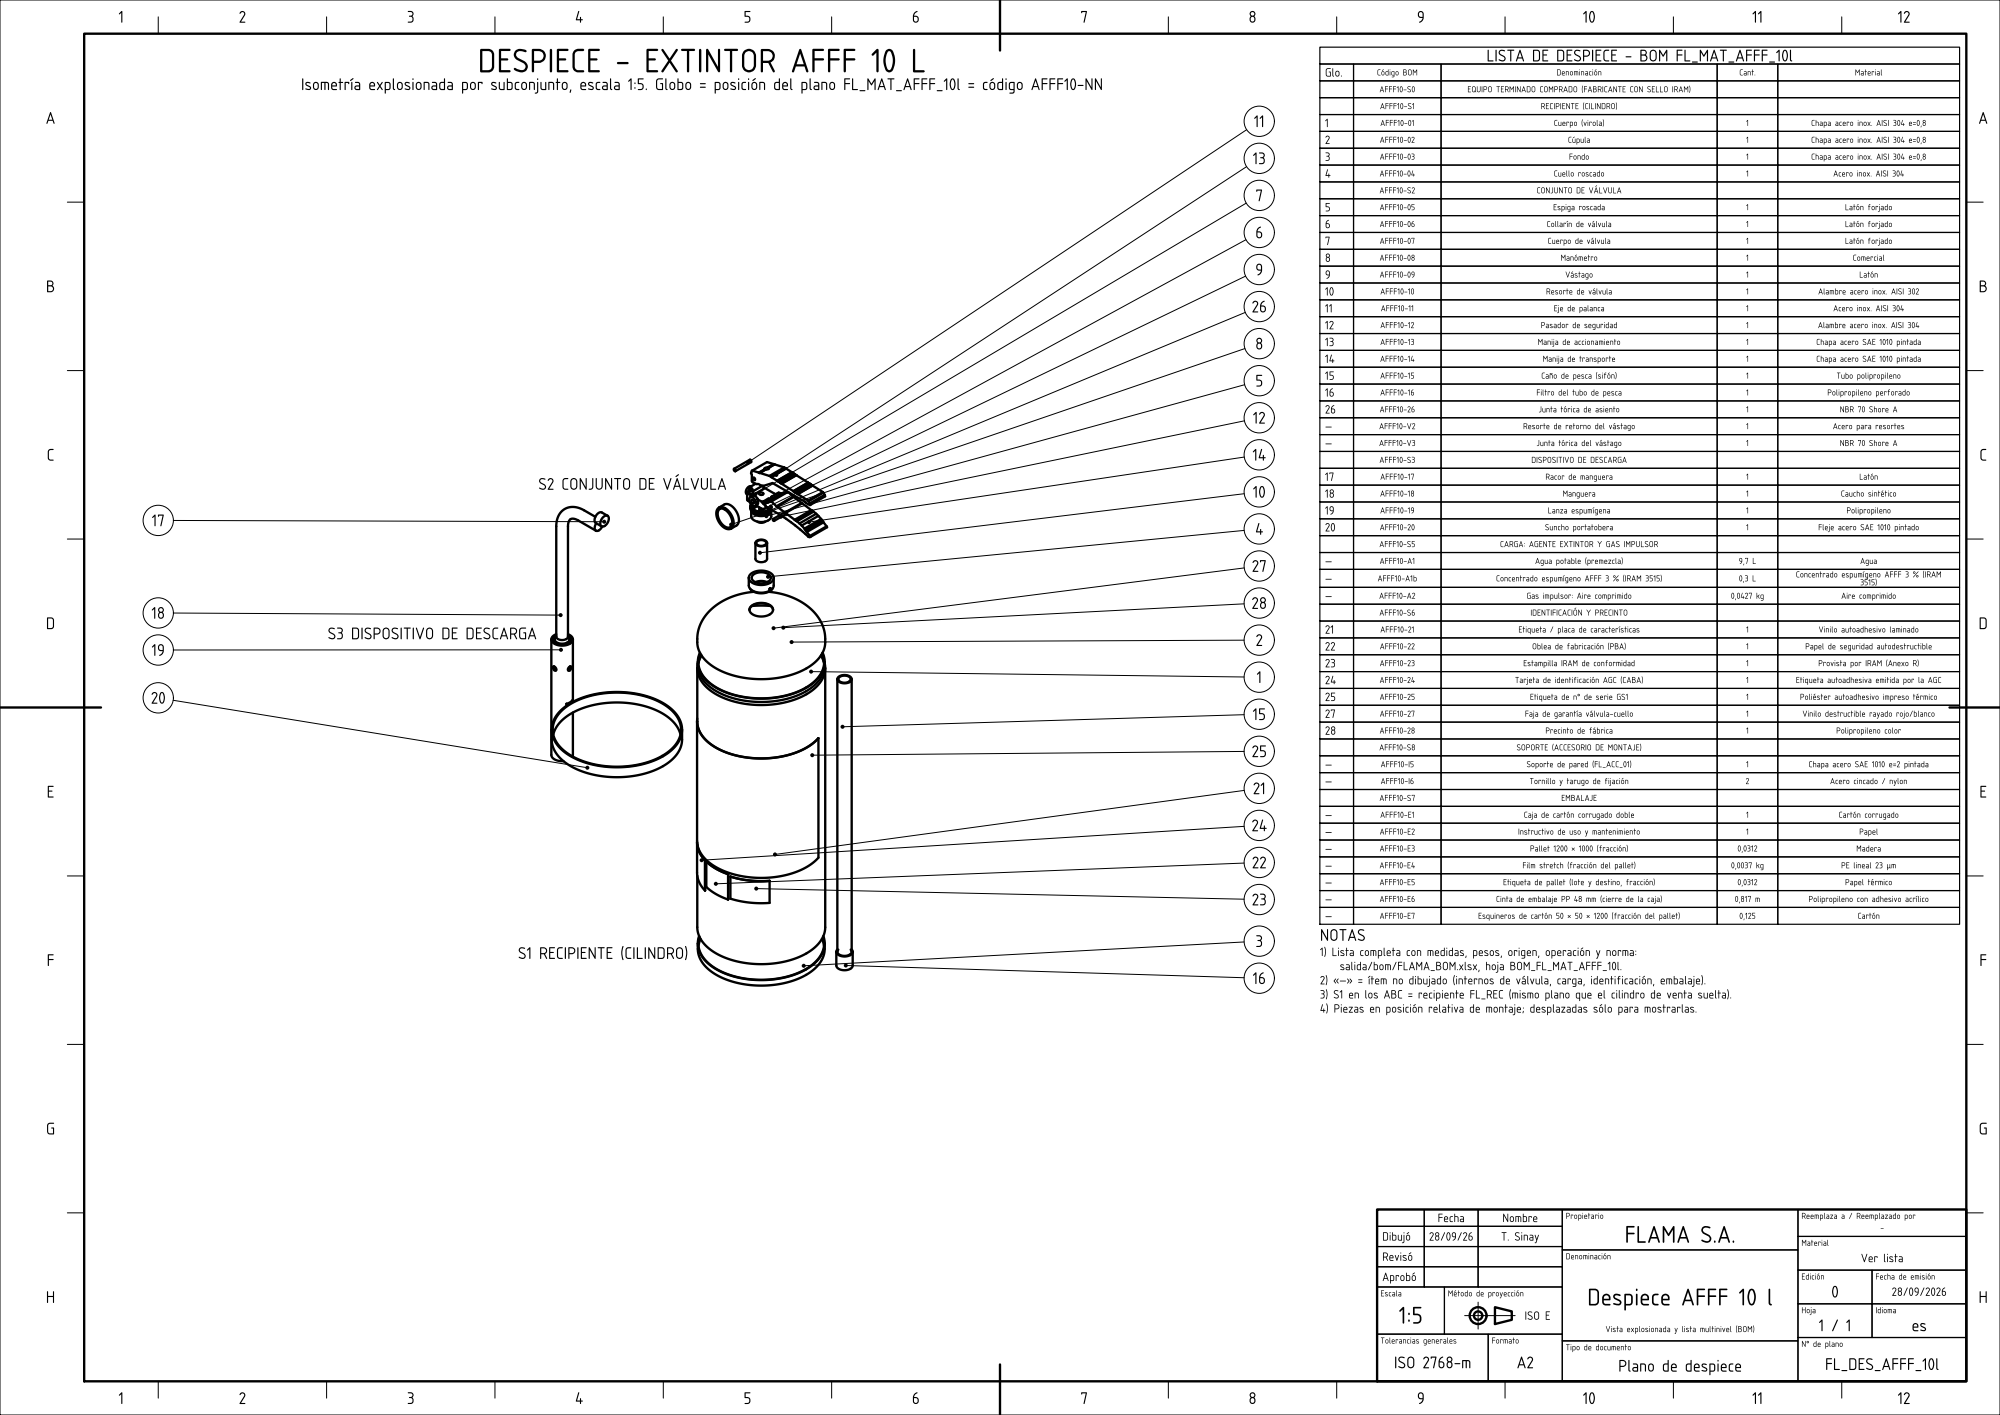
[picture p133: page 1]
