TadeoSinay/planos_flama-/salida/despiece/FL_DES_AFFF_50l.pdf

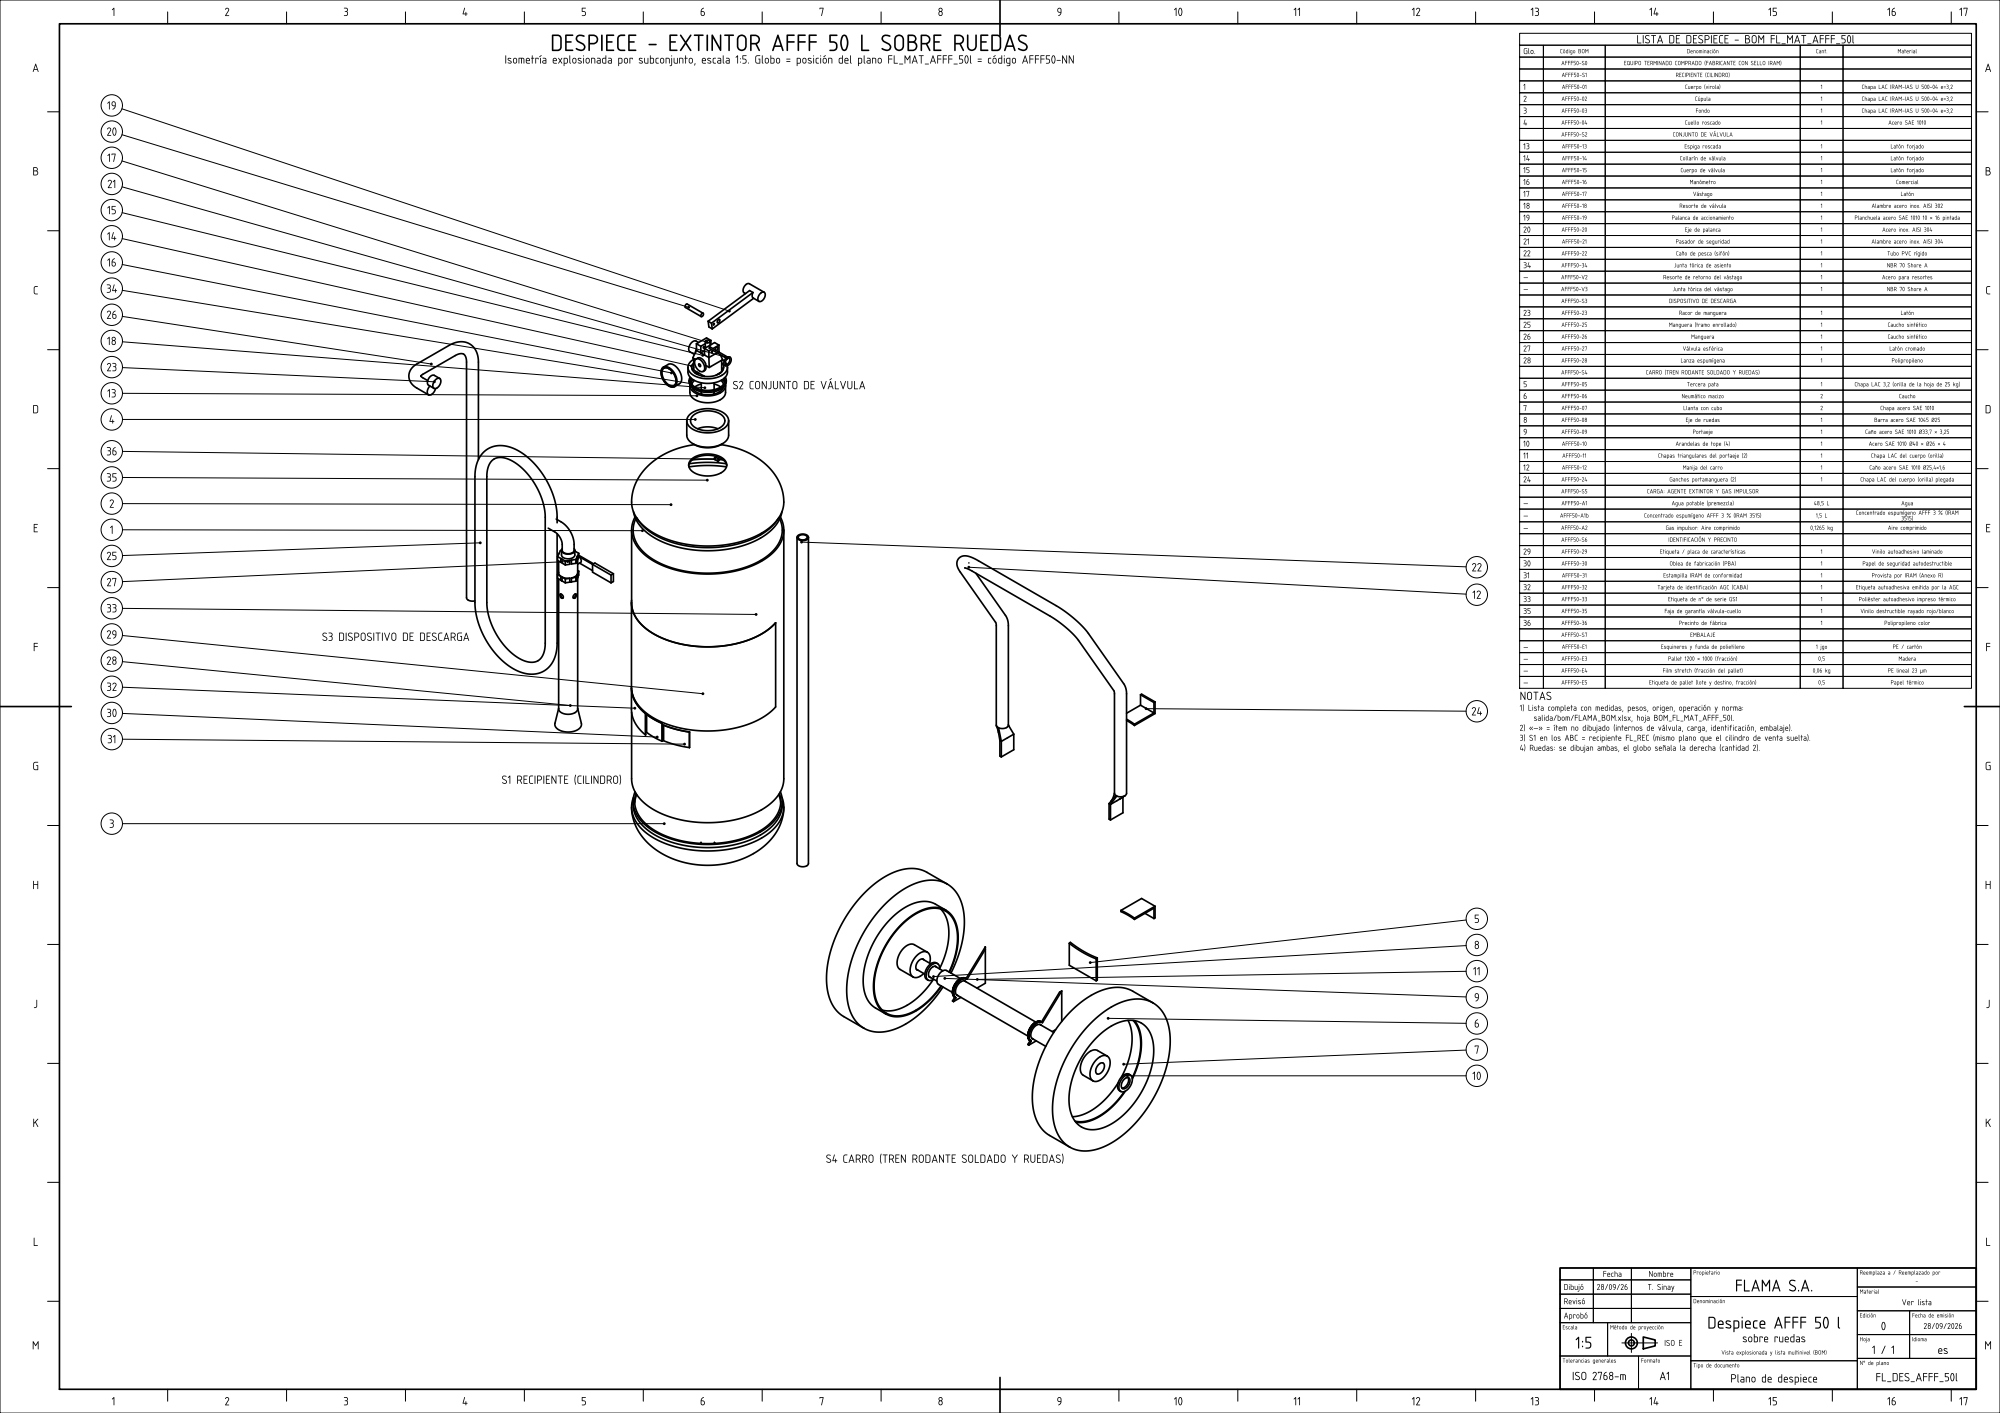
[picture p134: page 1]
