TadeoSinay/planos_flama-/salida/despiece/FL_DES_AGUA_10l.pdf

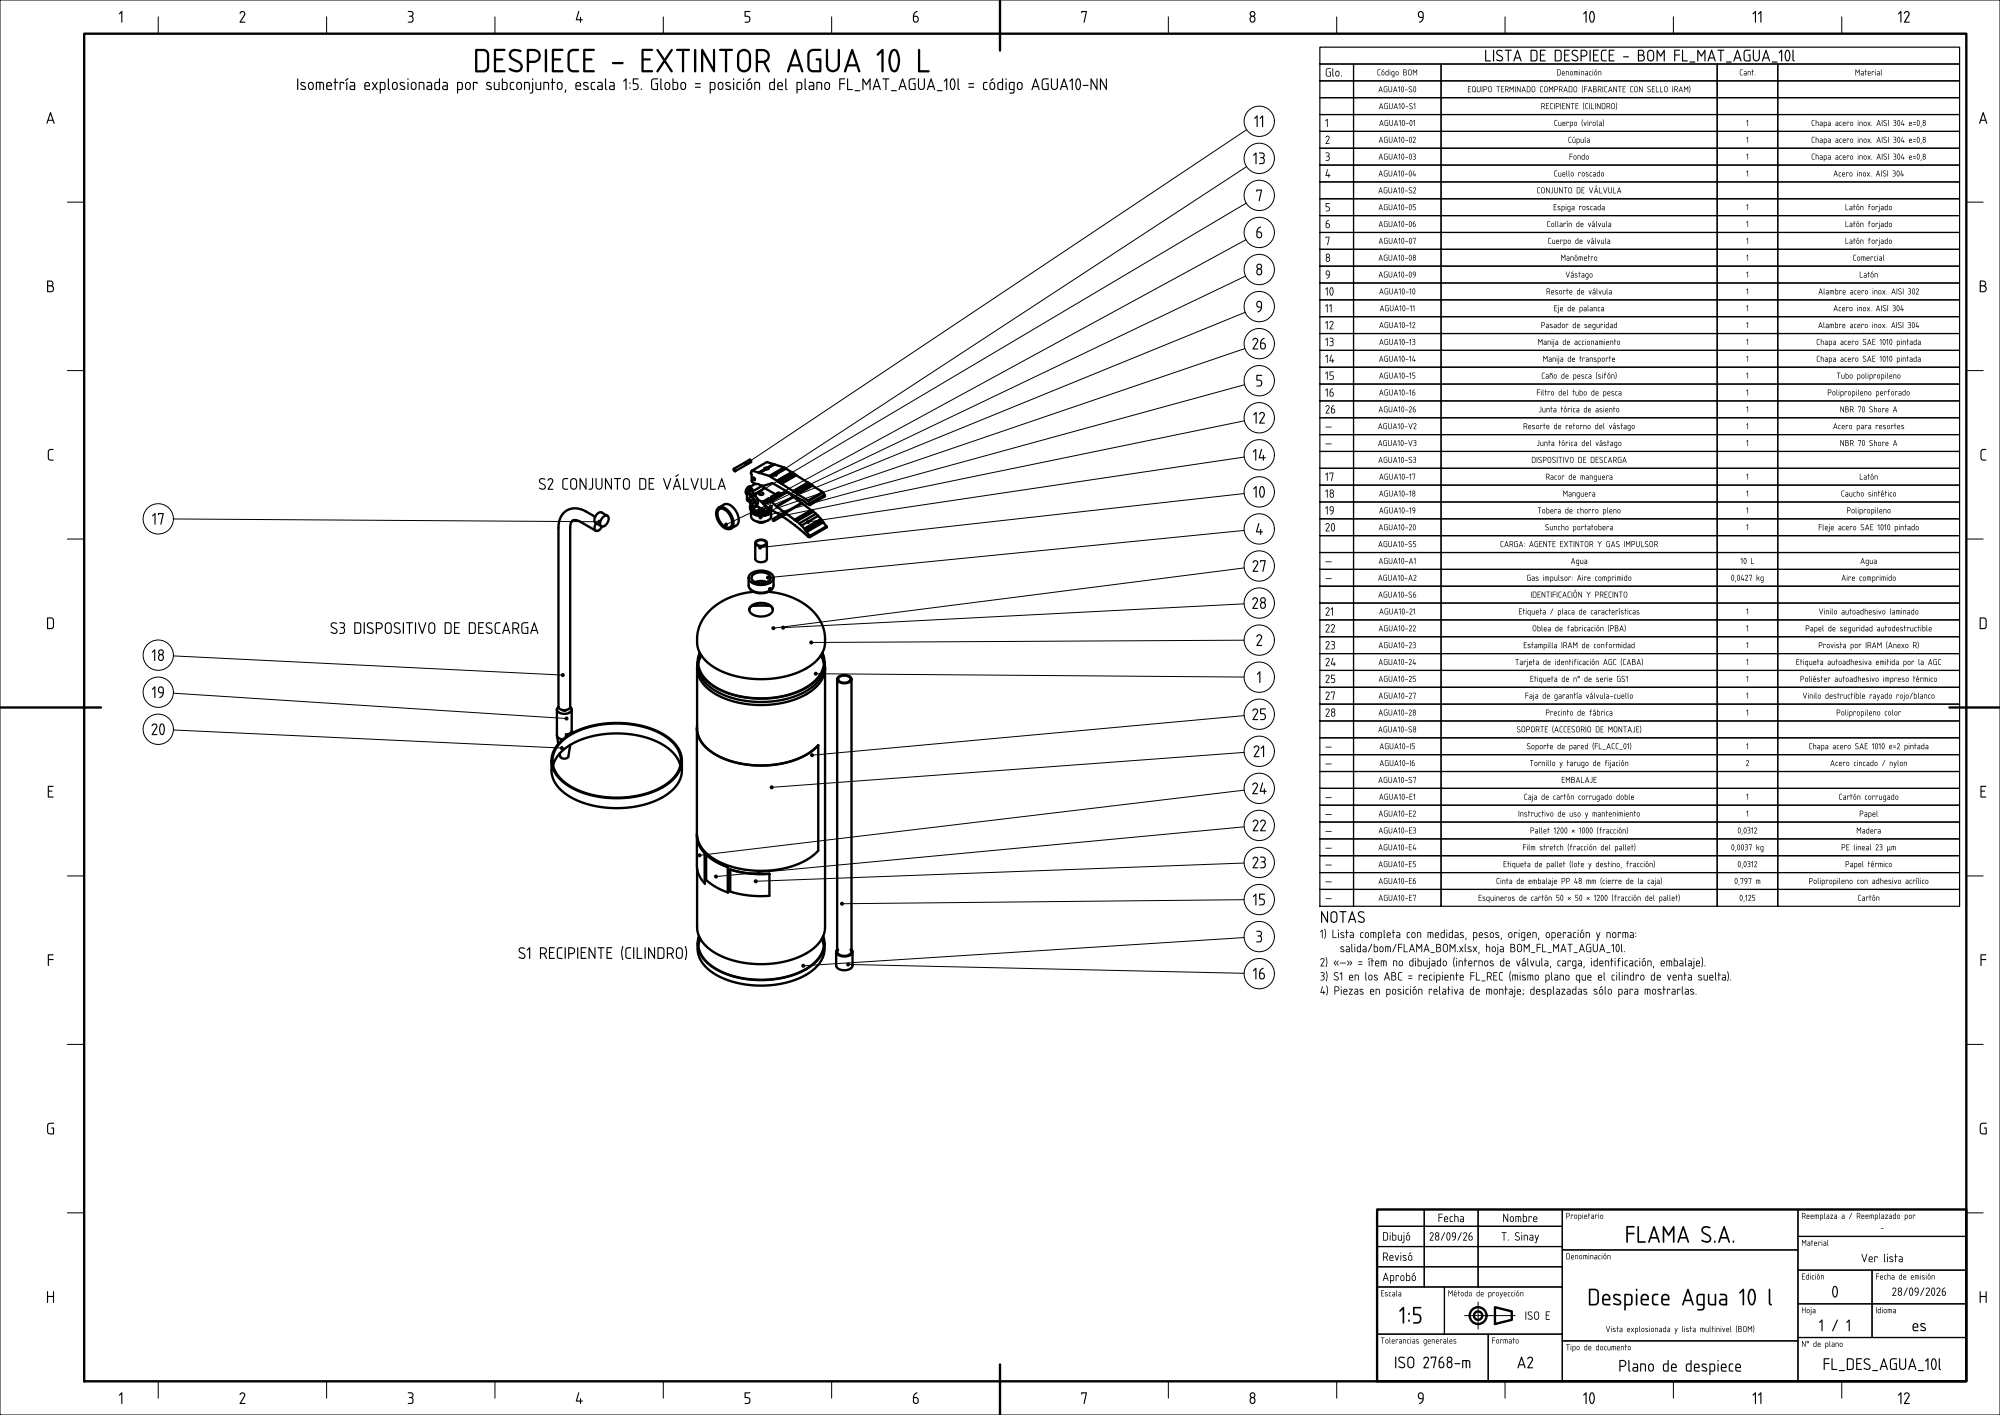
[picture p135: page 1]
