TadeoSinay/planos_flama-/salida/despiece/FL_DES_BC_5kg.pdf

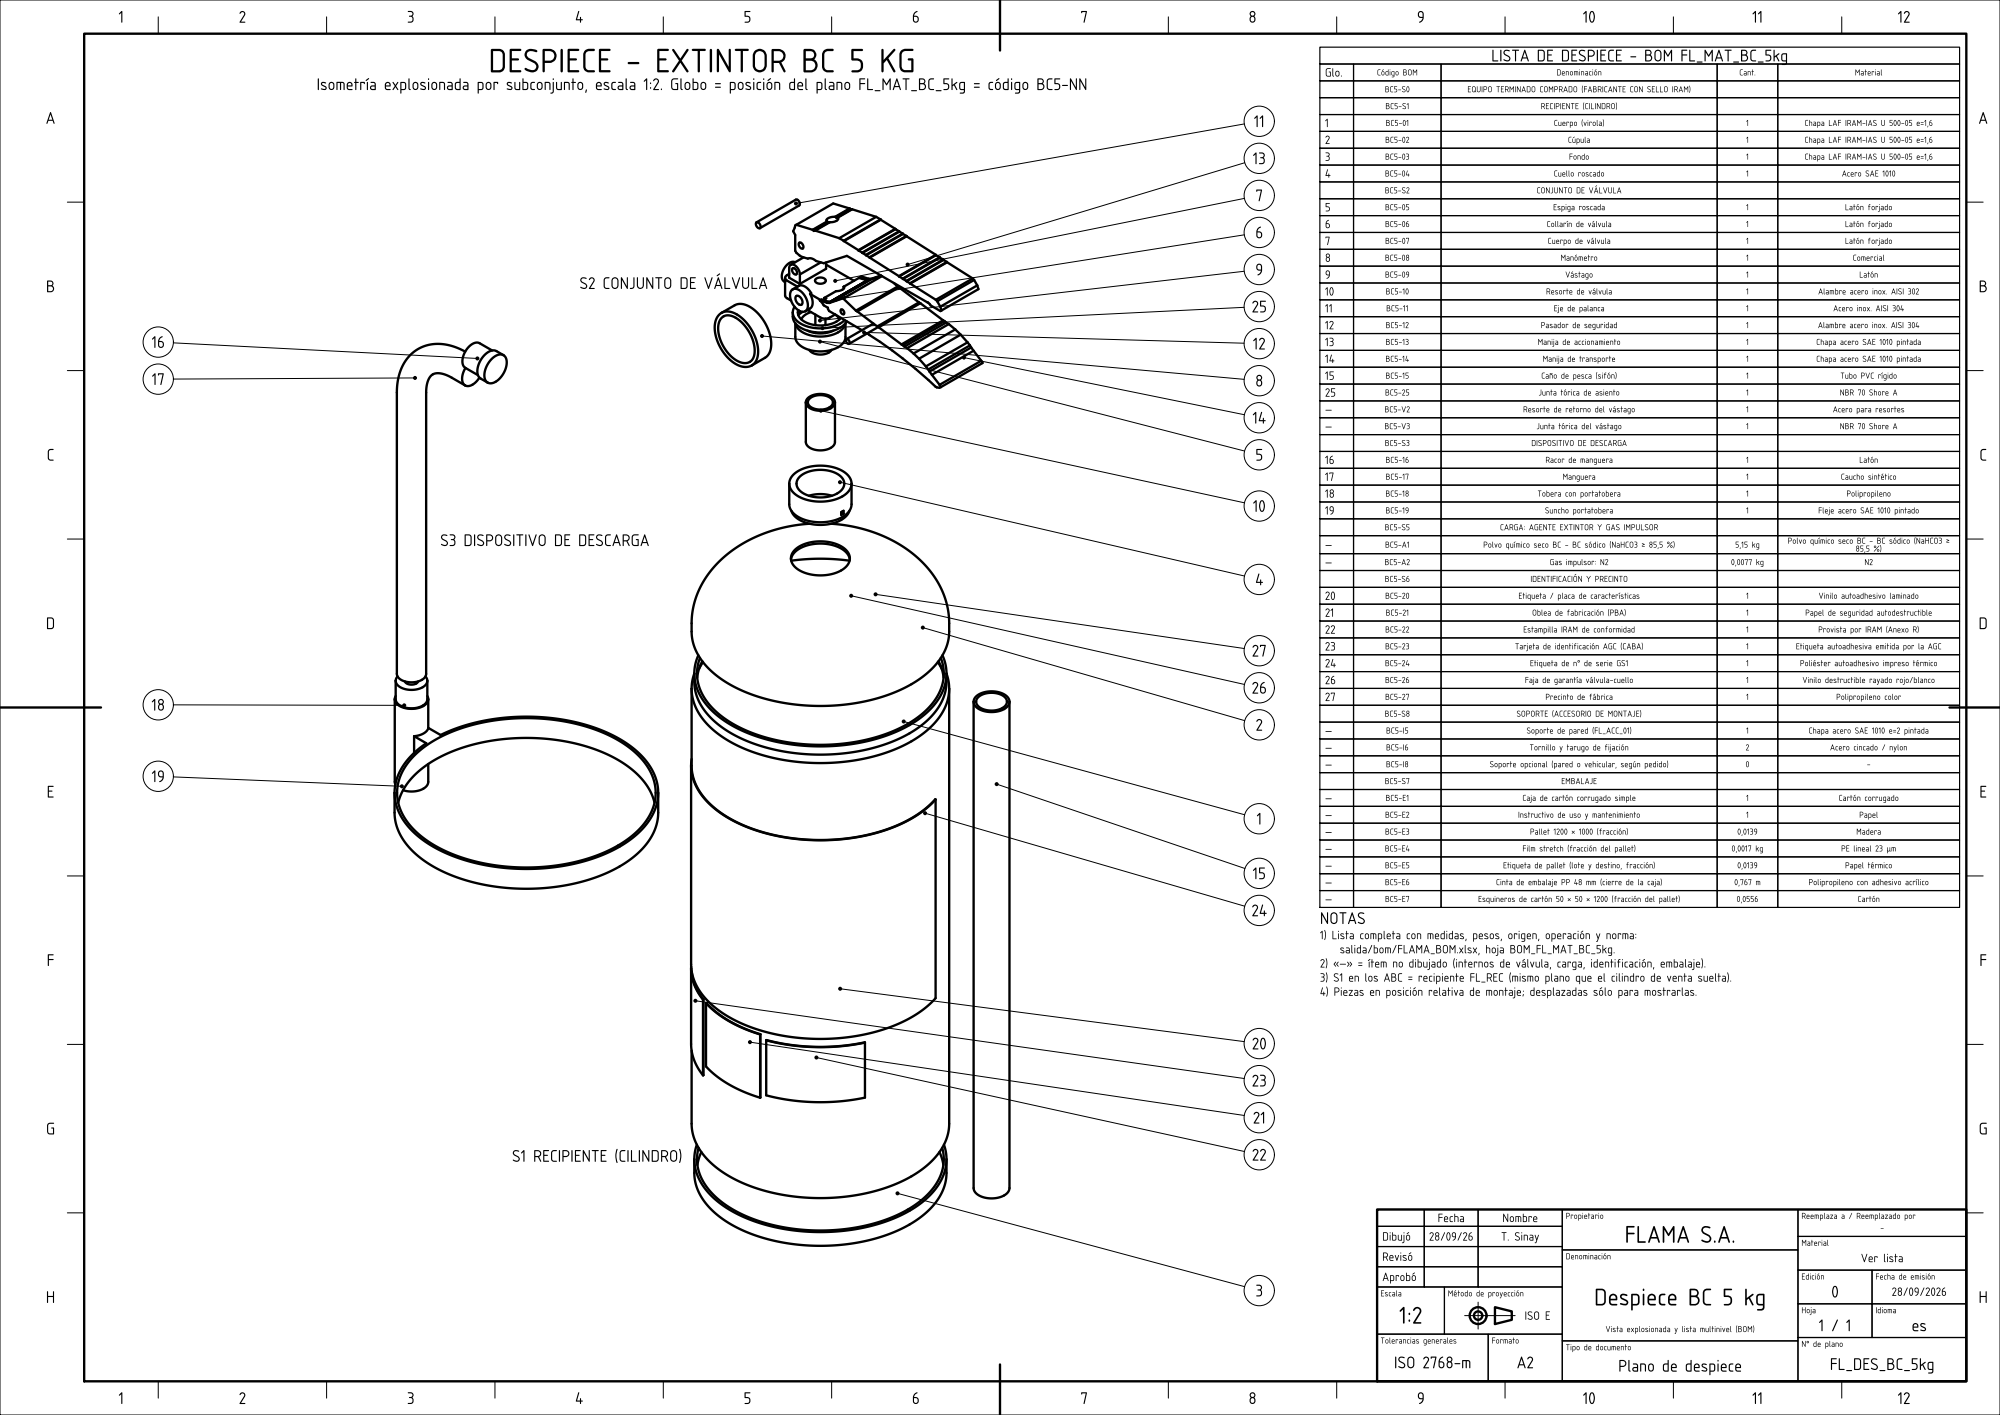
[picture p136: page 1]
