TadeoSinay/planos_flama-/salida/despiece/FL_DES_CLASED_9l.pdf

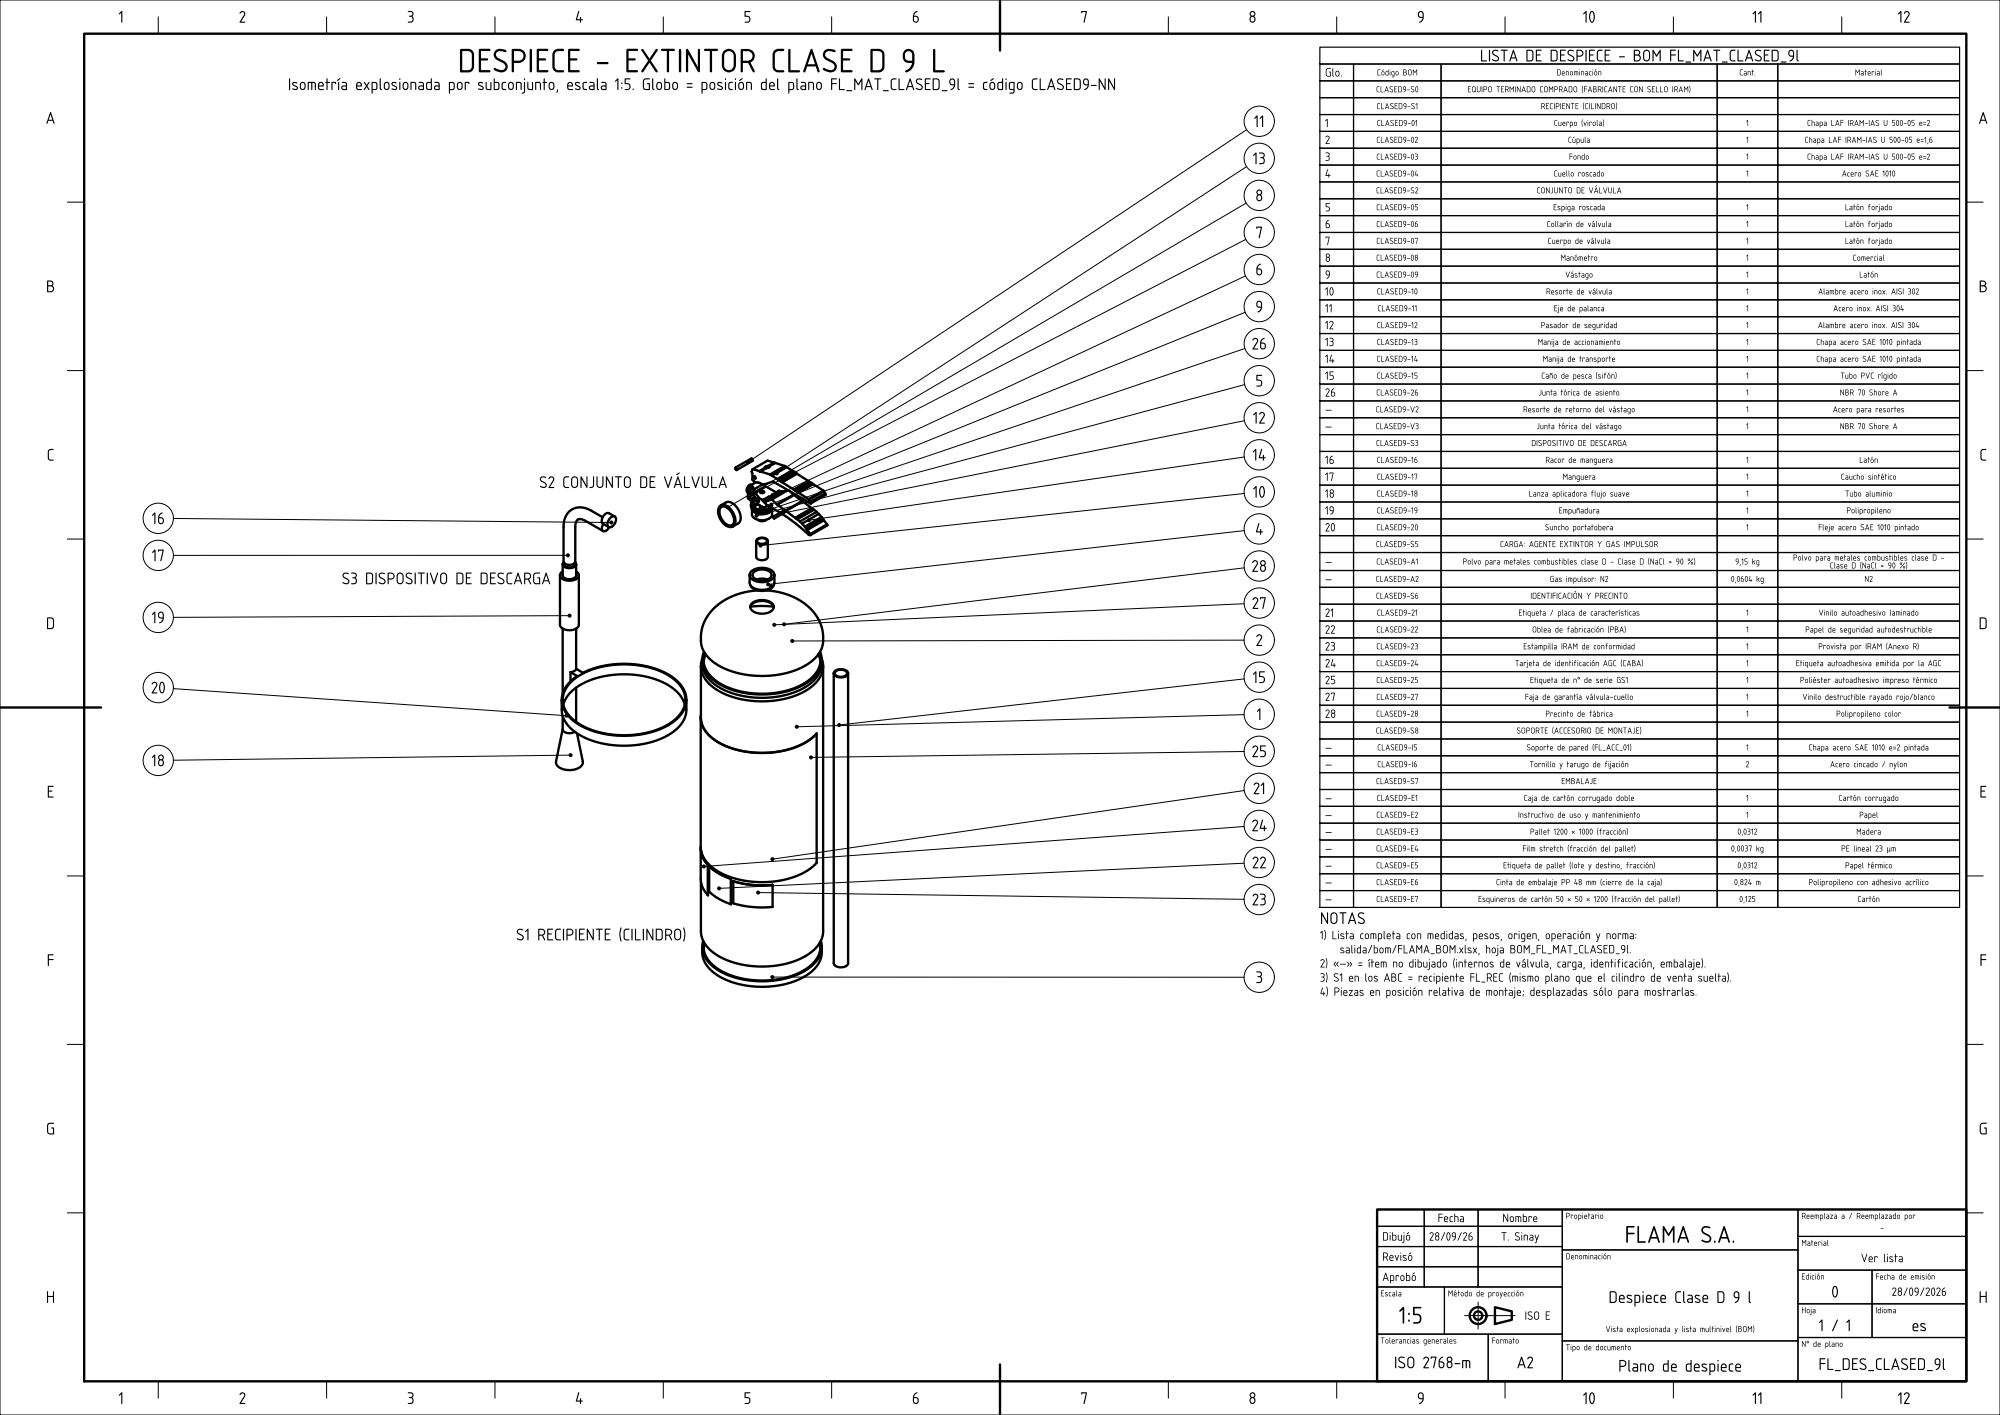
[picture p137: page 1]
