TadeoSinay/planos_flama-/salida/despiece/FL_DES_CO2_2kg.pdf

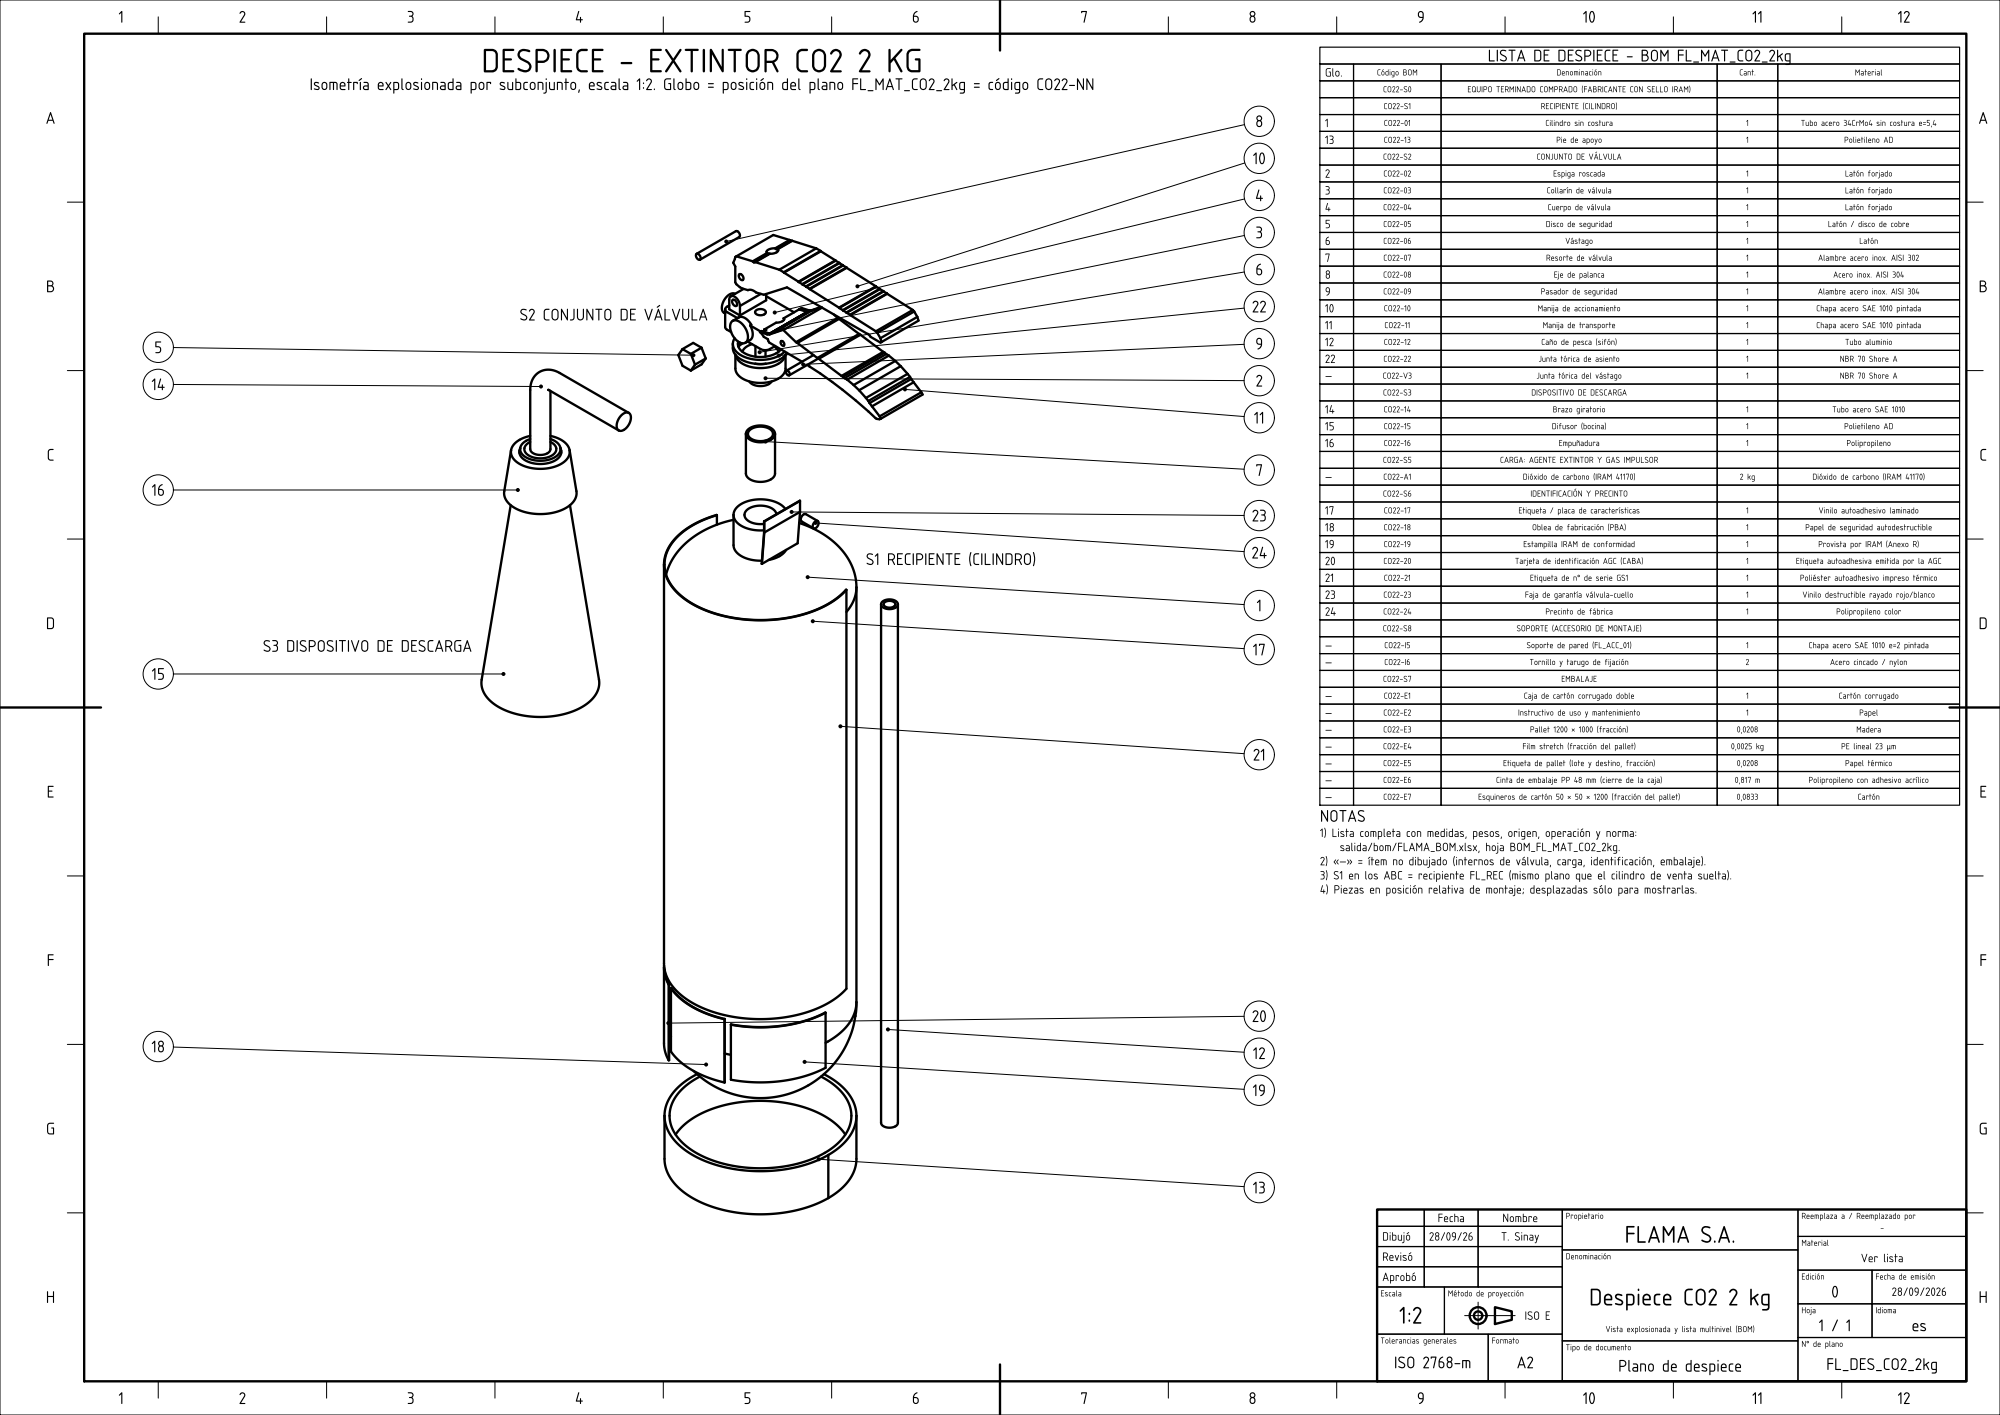
[picture p138: page 1]
