TadeoSinay/planos_flama-/salida/despiece/FL_DES_CO2_5kg.pdf

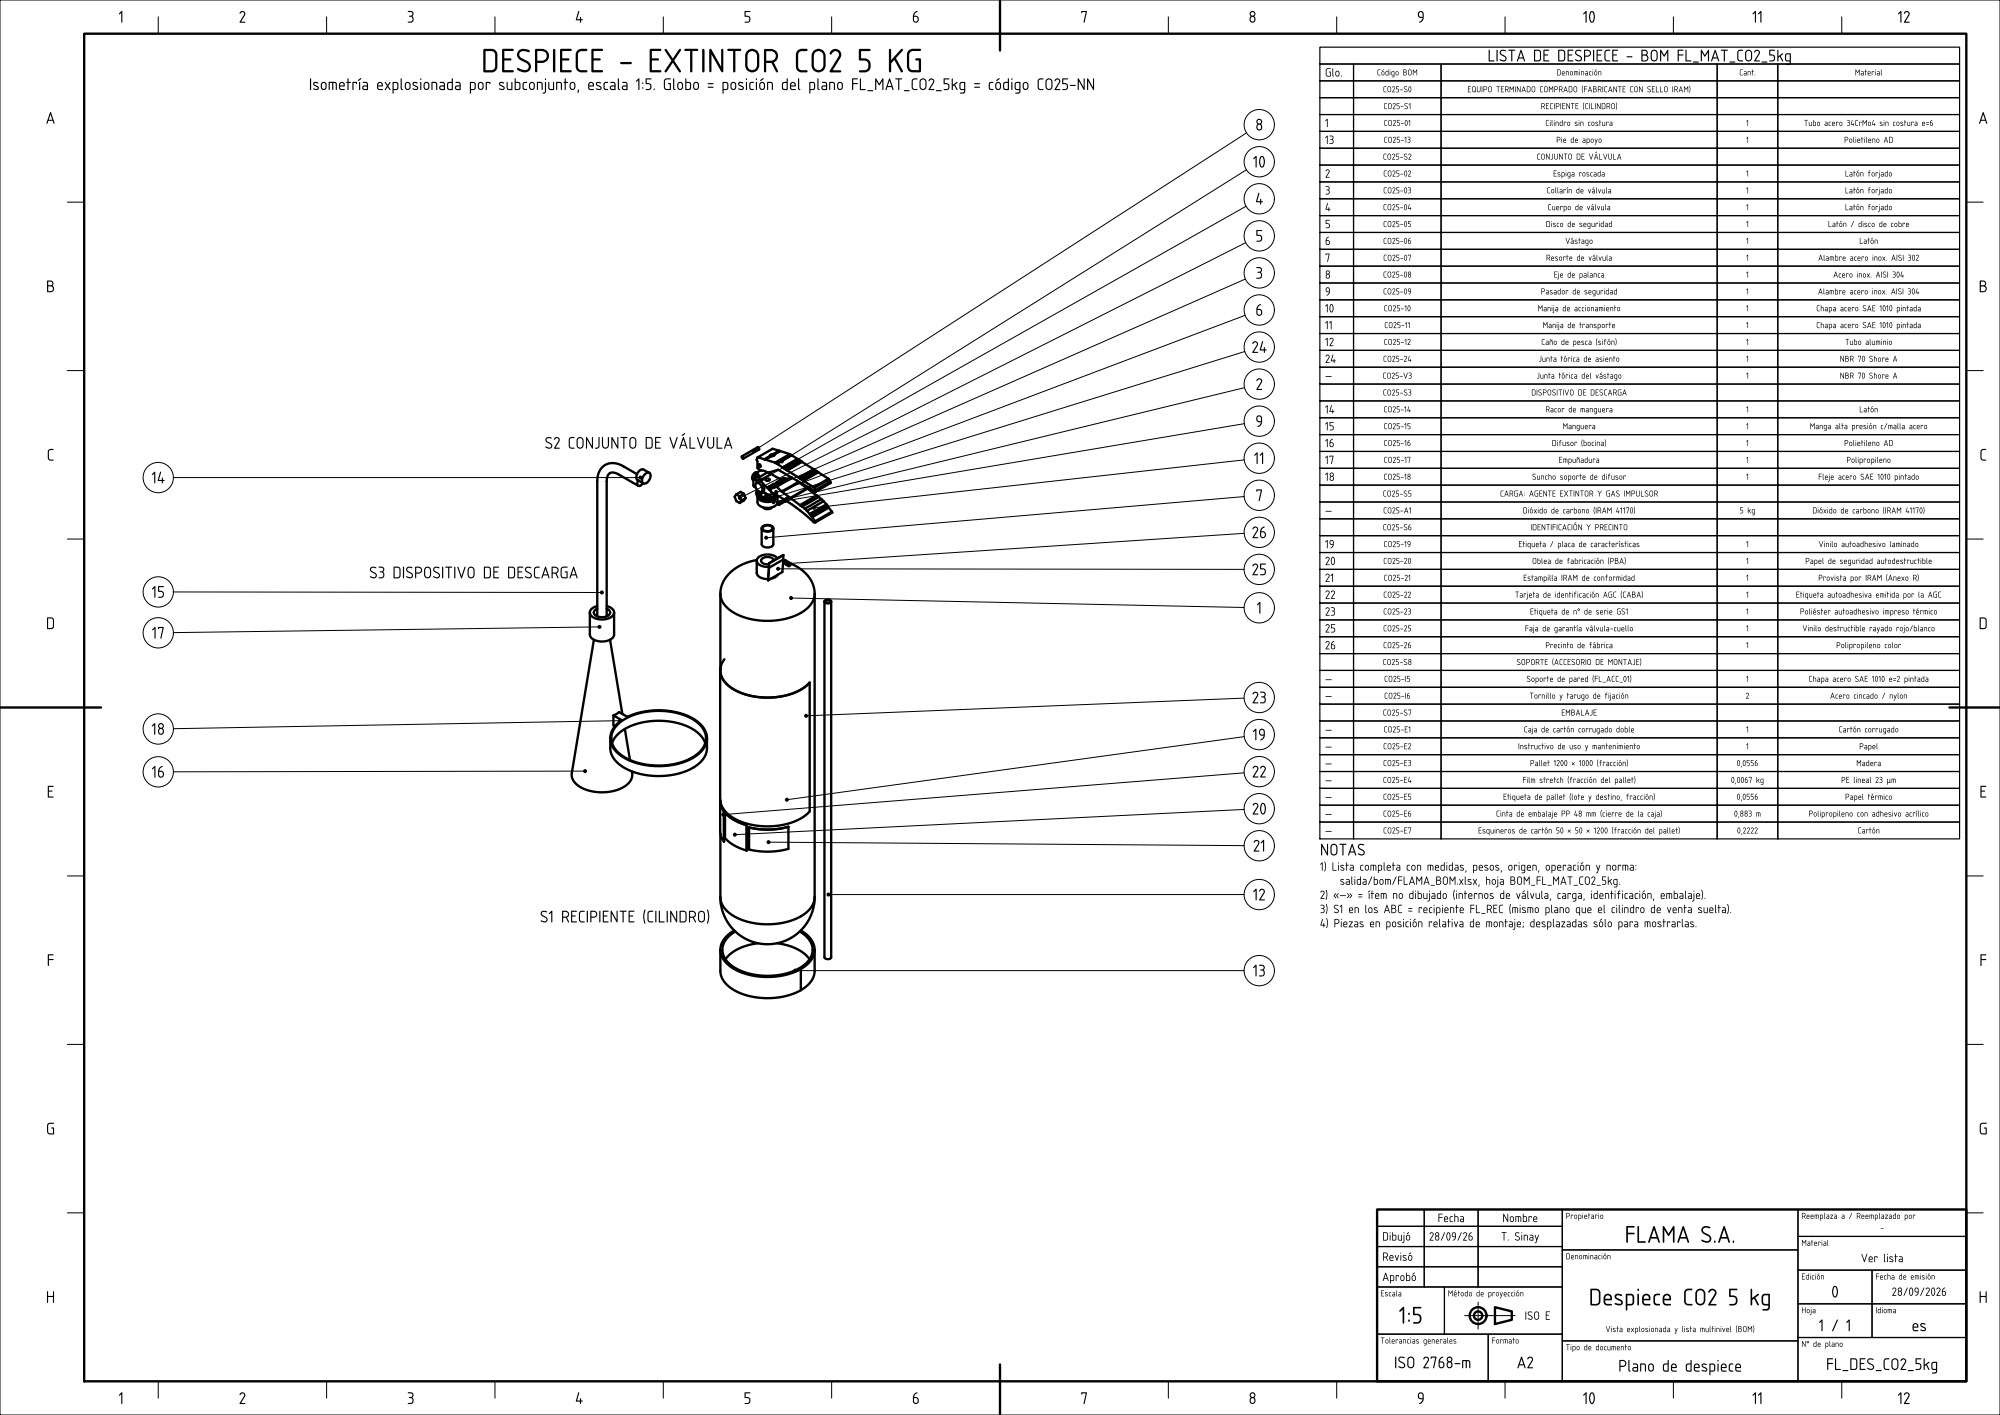
[picture p139: page 1]
