TadeoSinay/planos_flama-/salida/despiece/FL_DES_HCFC-HFC_5kg.pdf

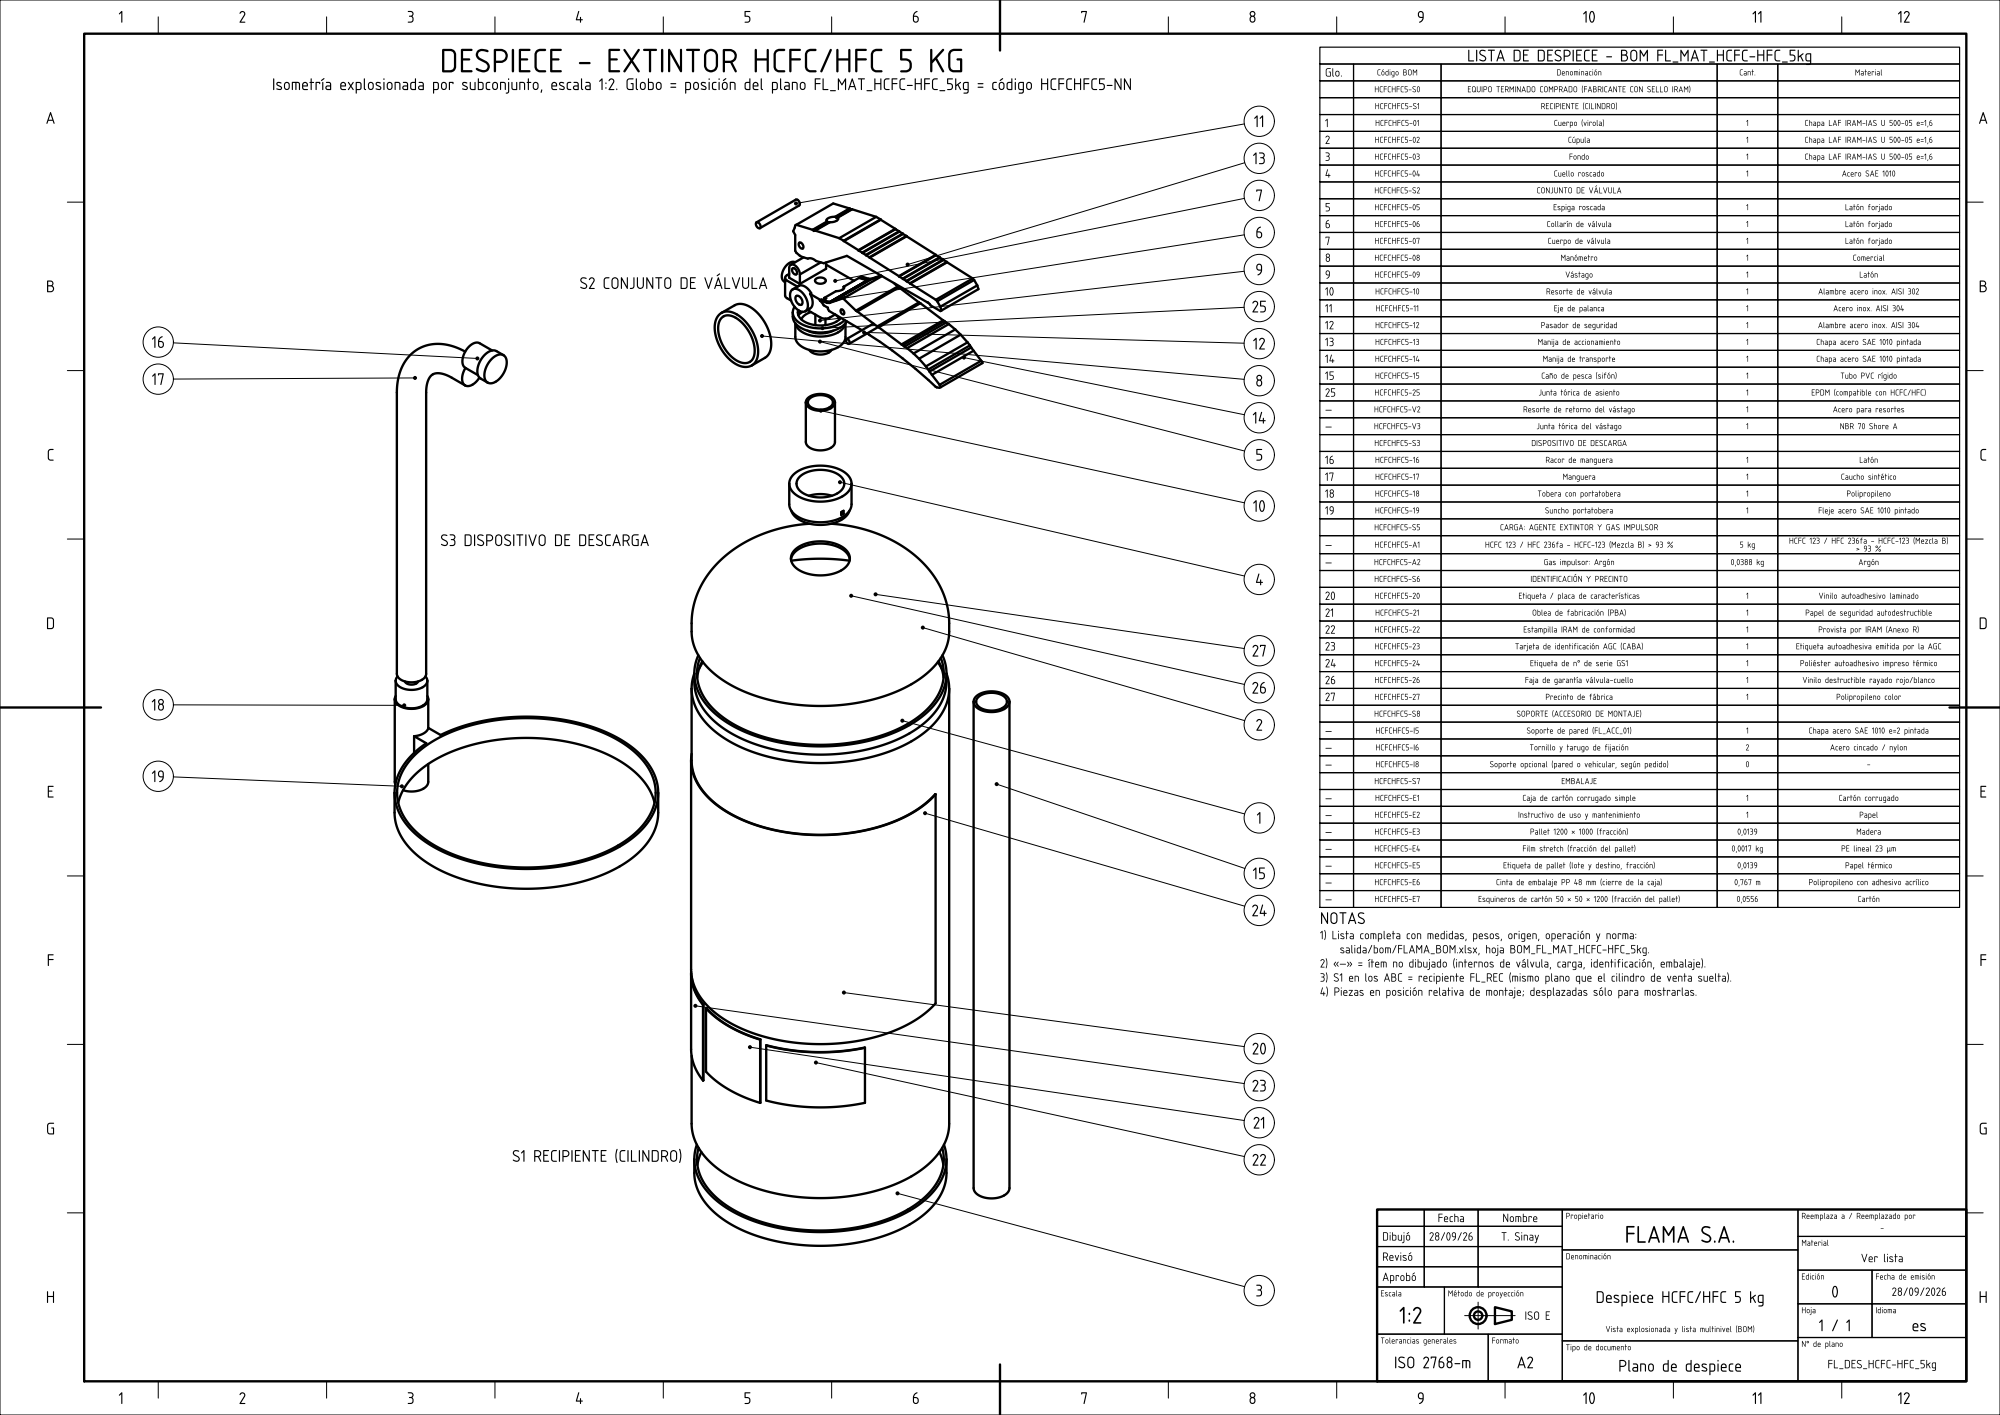
[picture p140: page 1]
