TadeoSinay/planos_flama-/salida/despiece/FL_DES_SALESK_6l.pdf

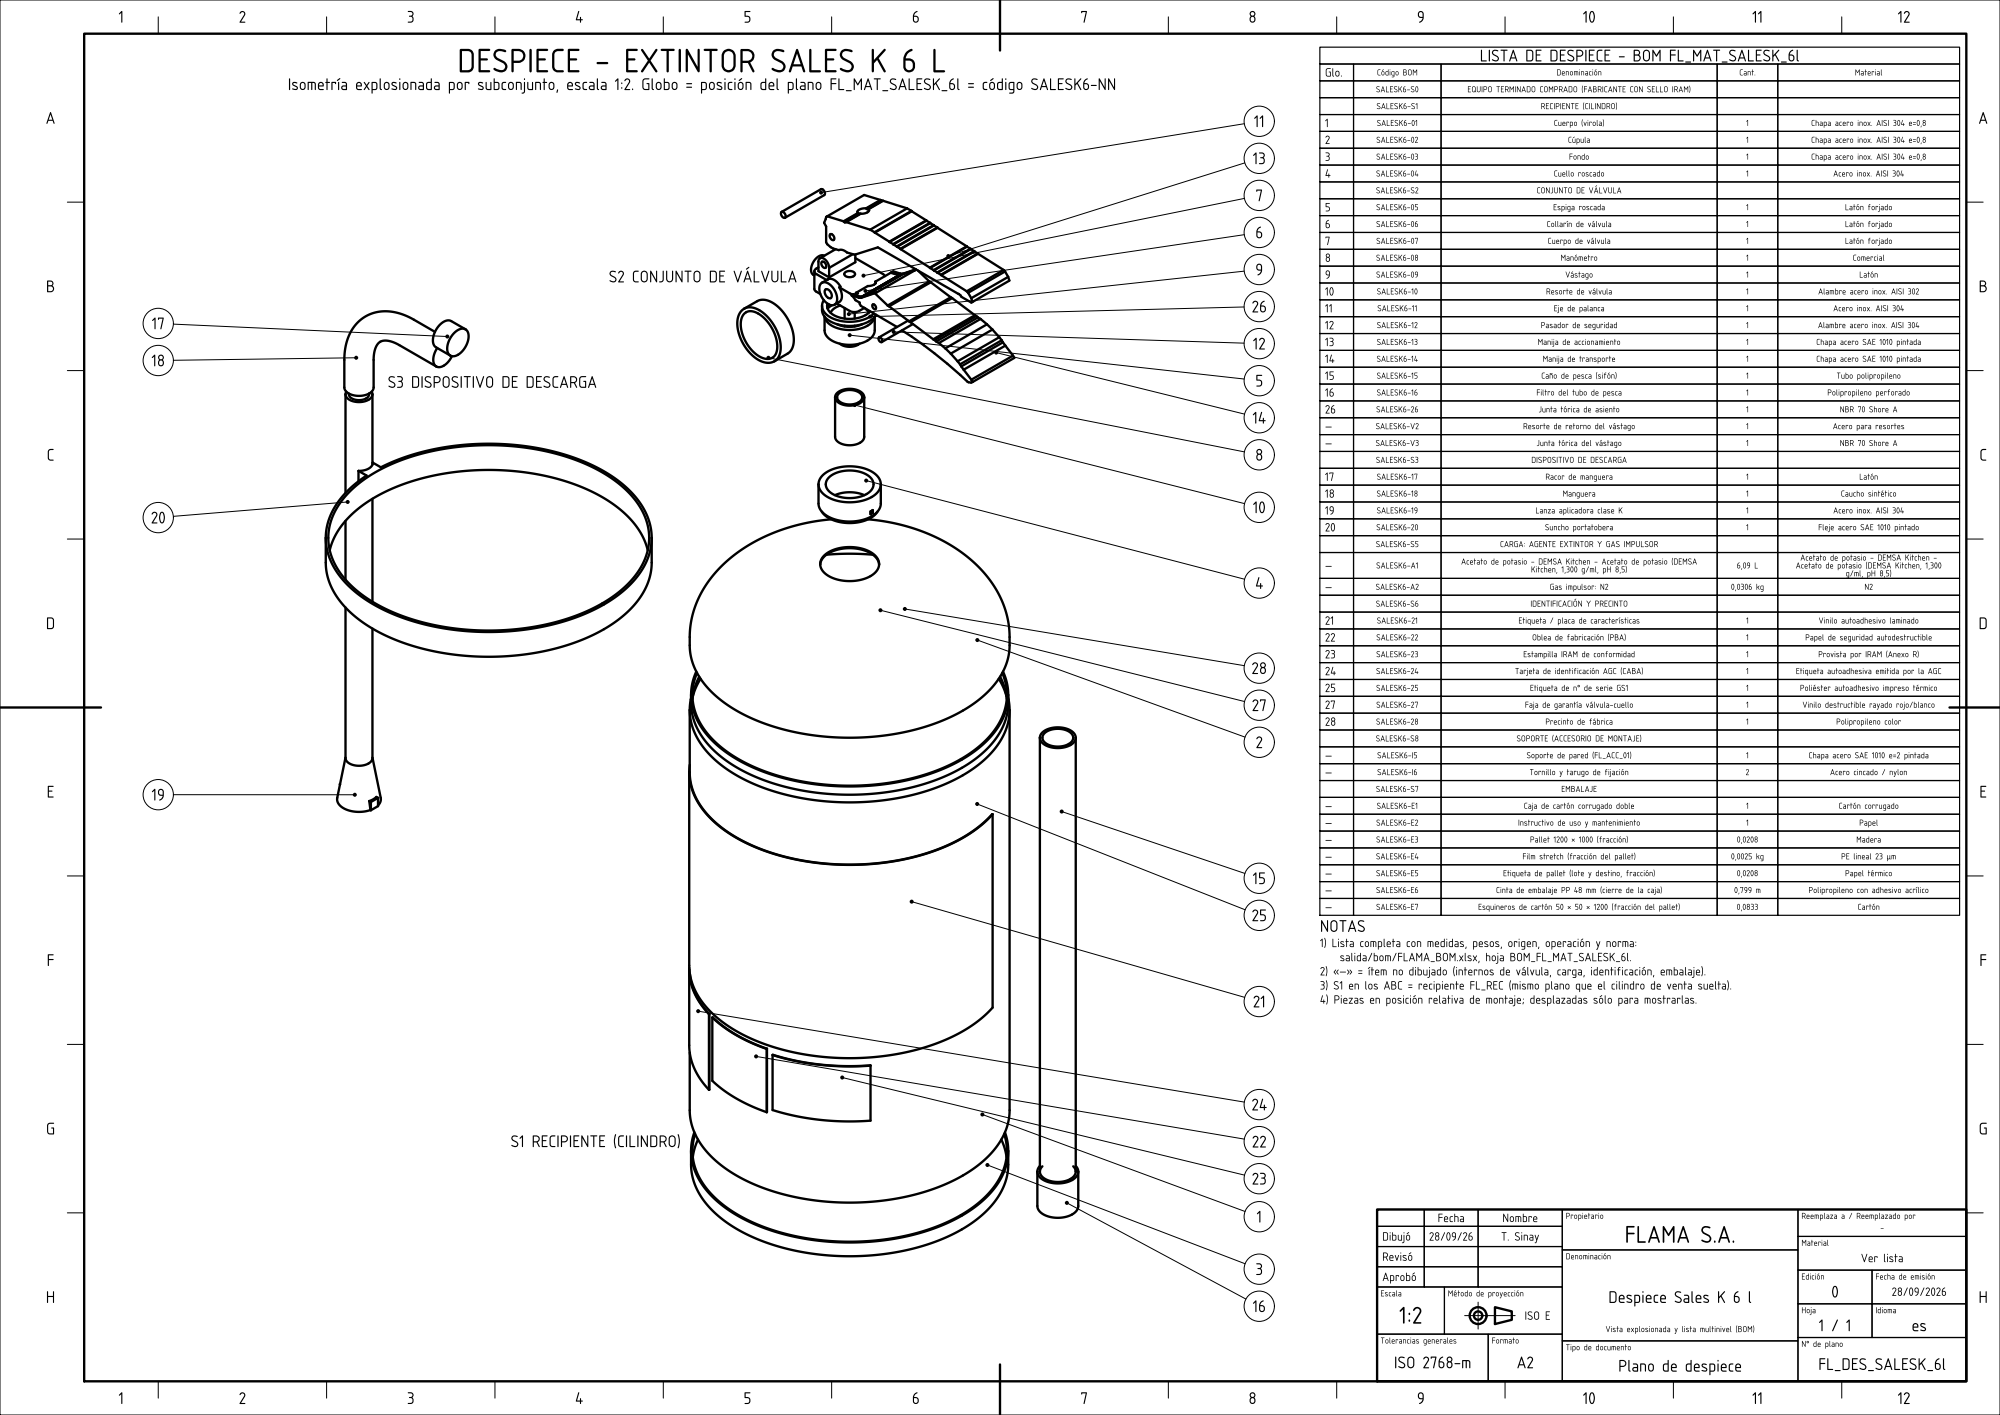
[picture p141: page 1]
