TadeoSinay/planos_flama-/salida/FL_MAT_ABC_100kg/FL_MAT_ABC_100kg.pdf

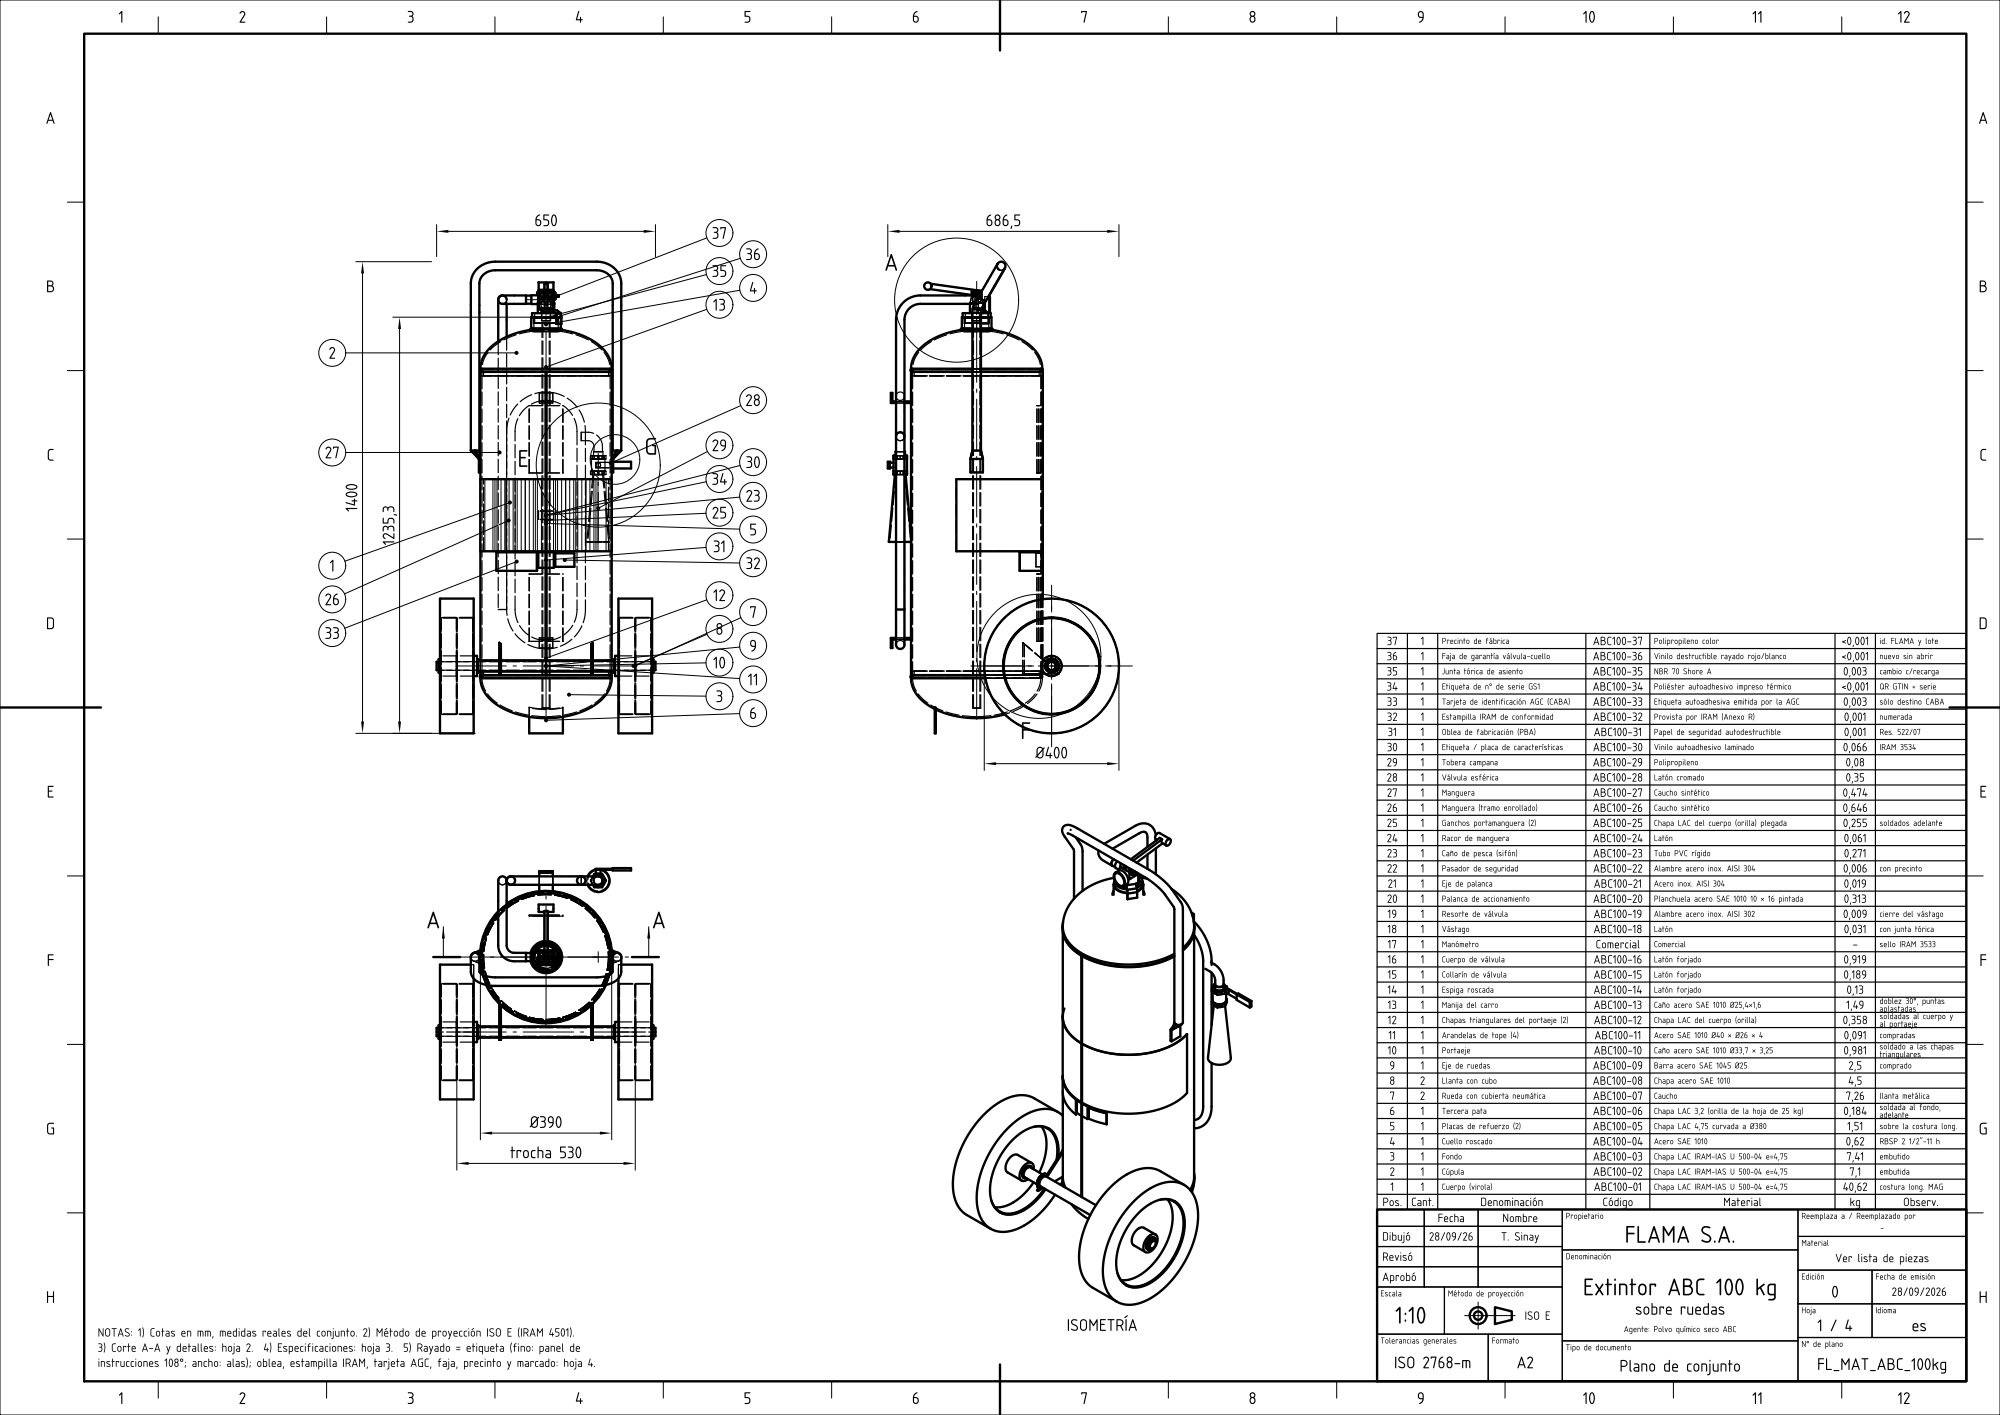
[picture p142: page 1]

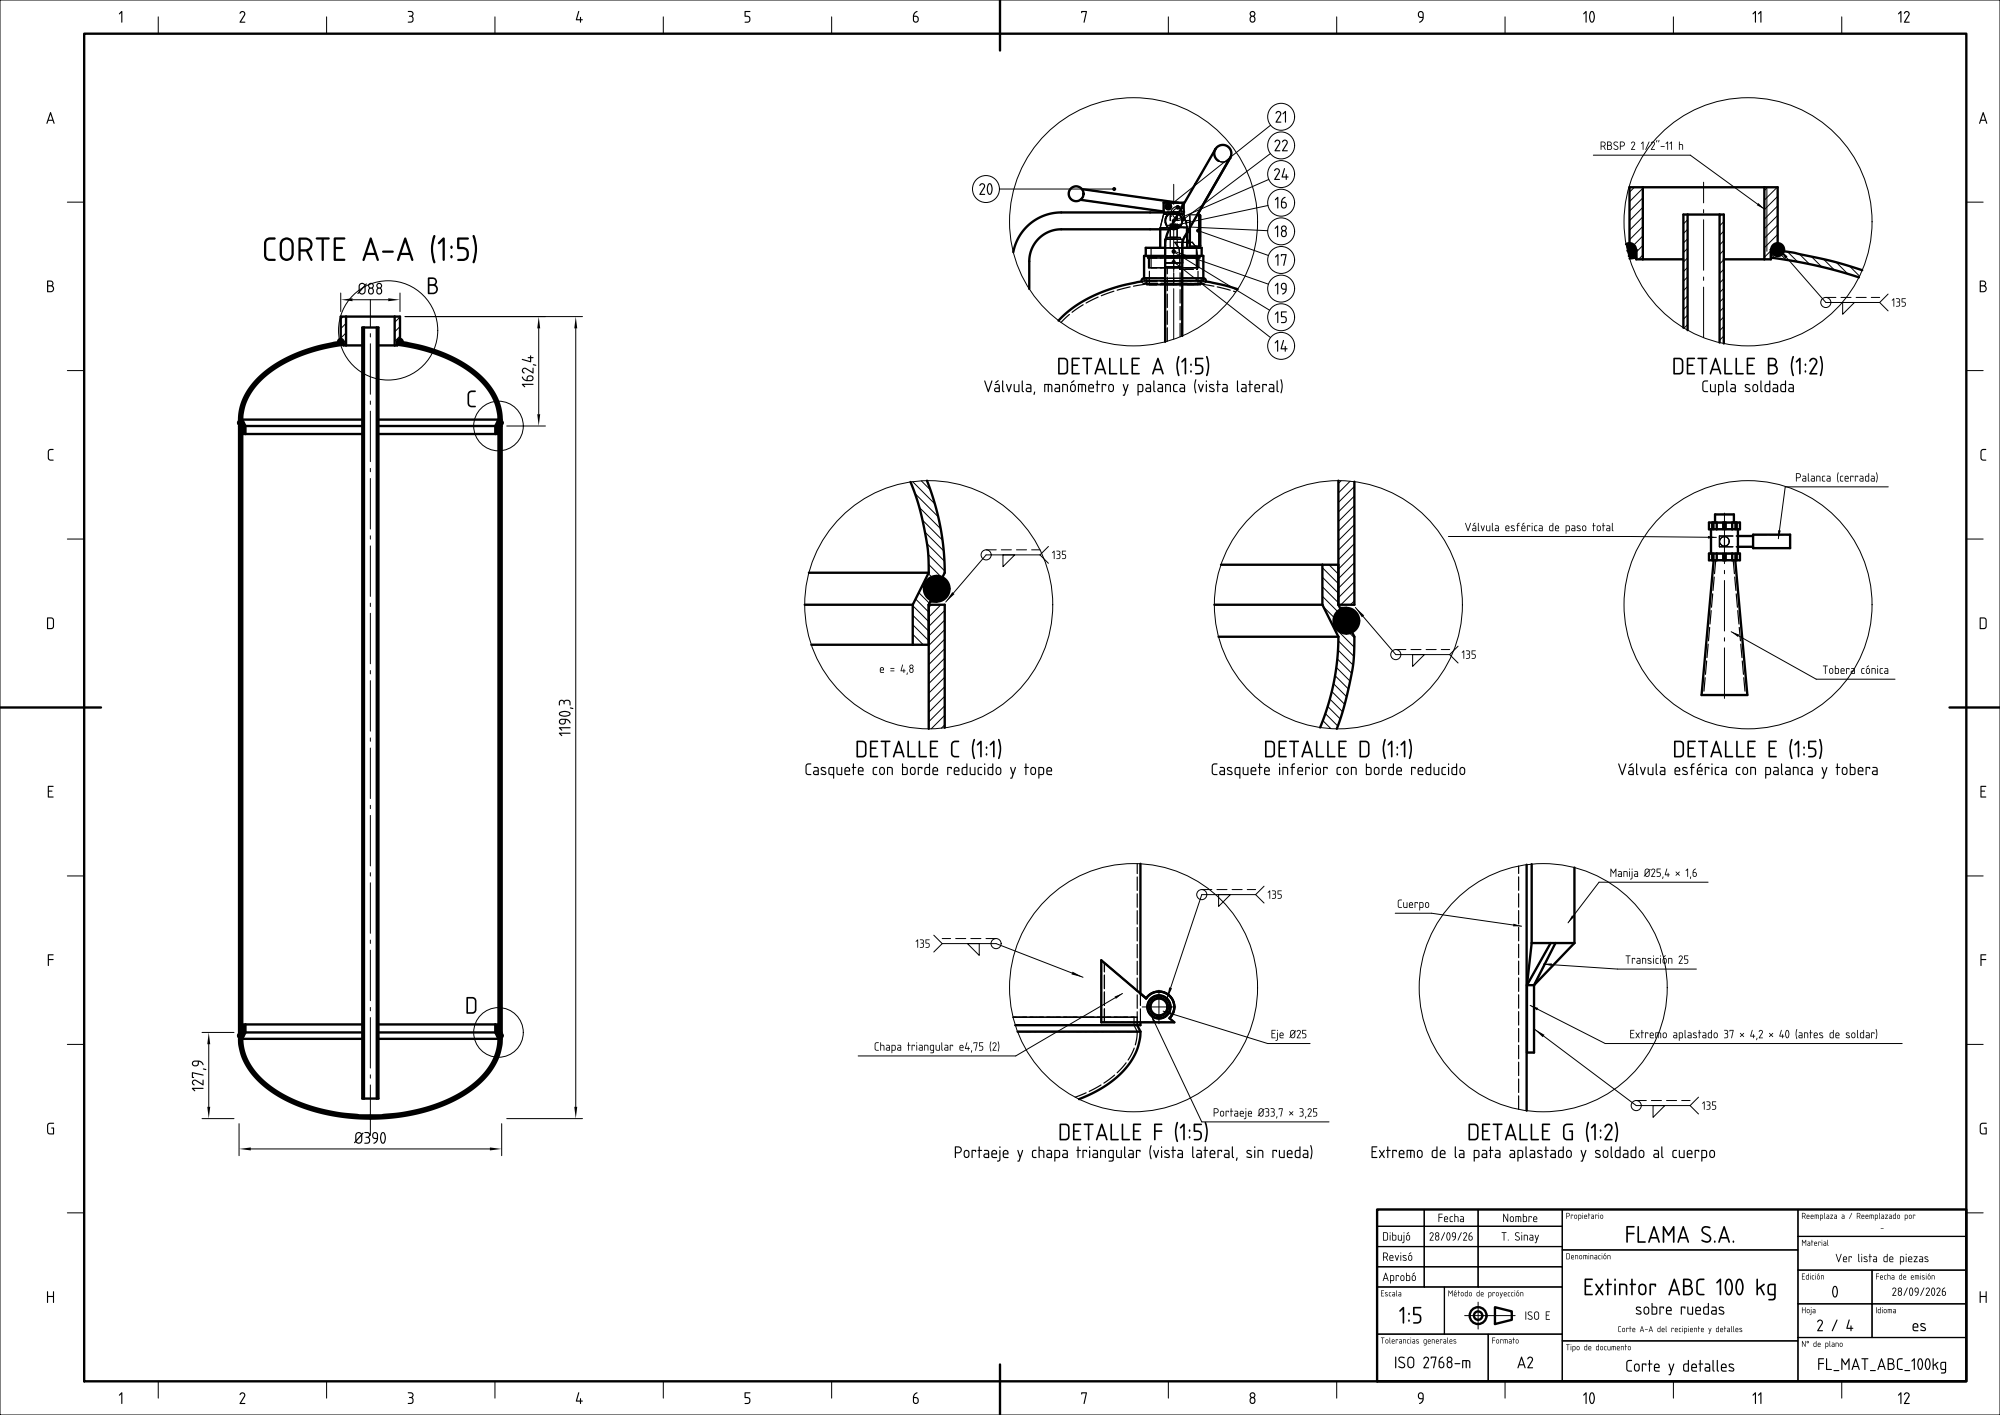
[picture p143: page 2]

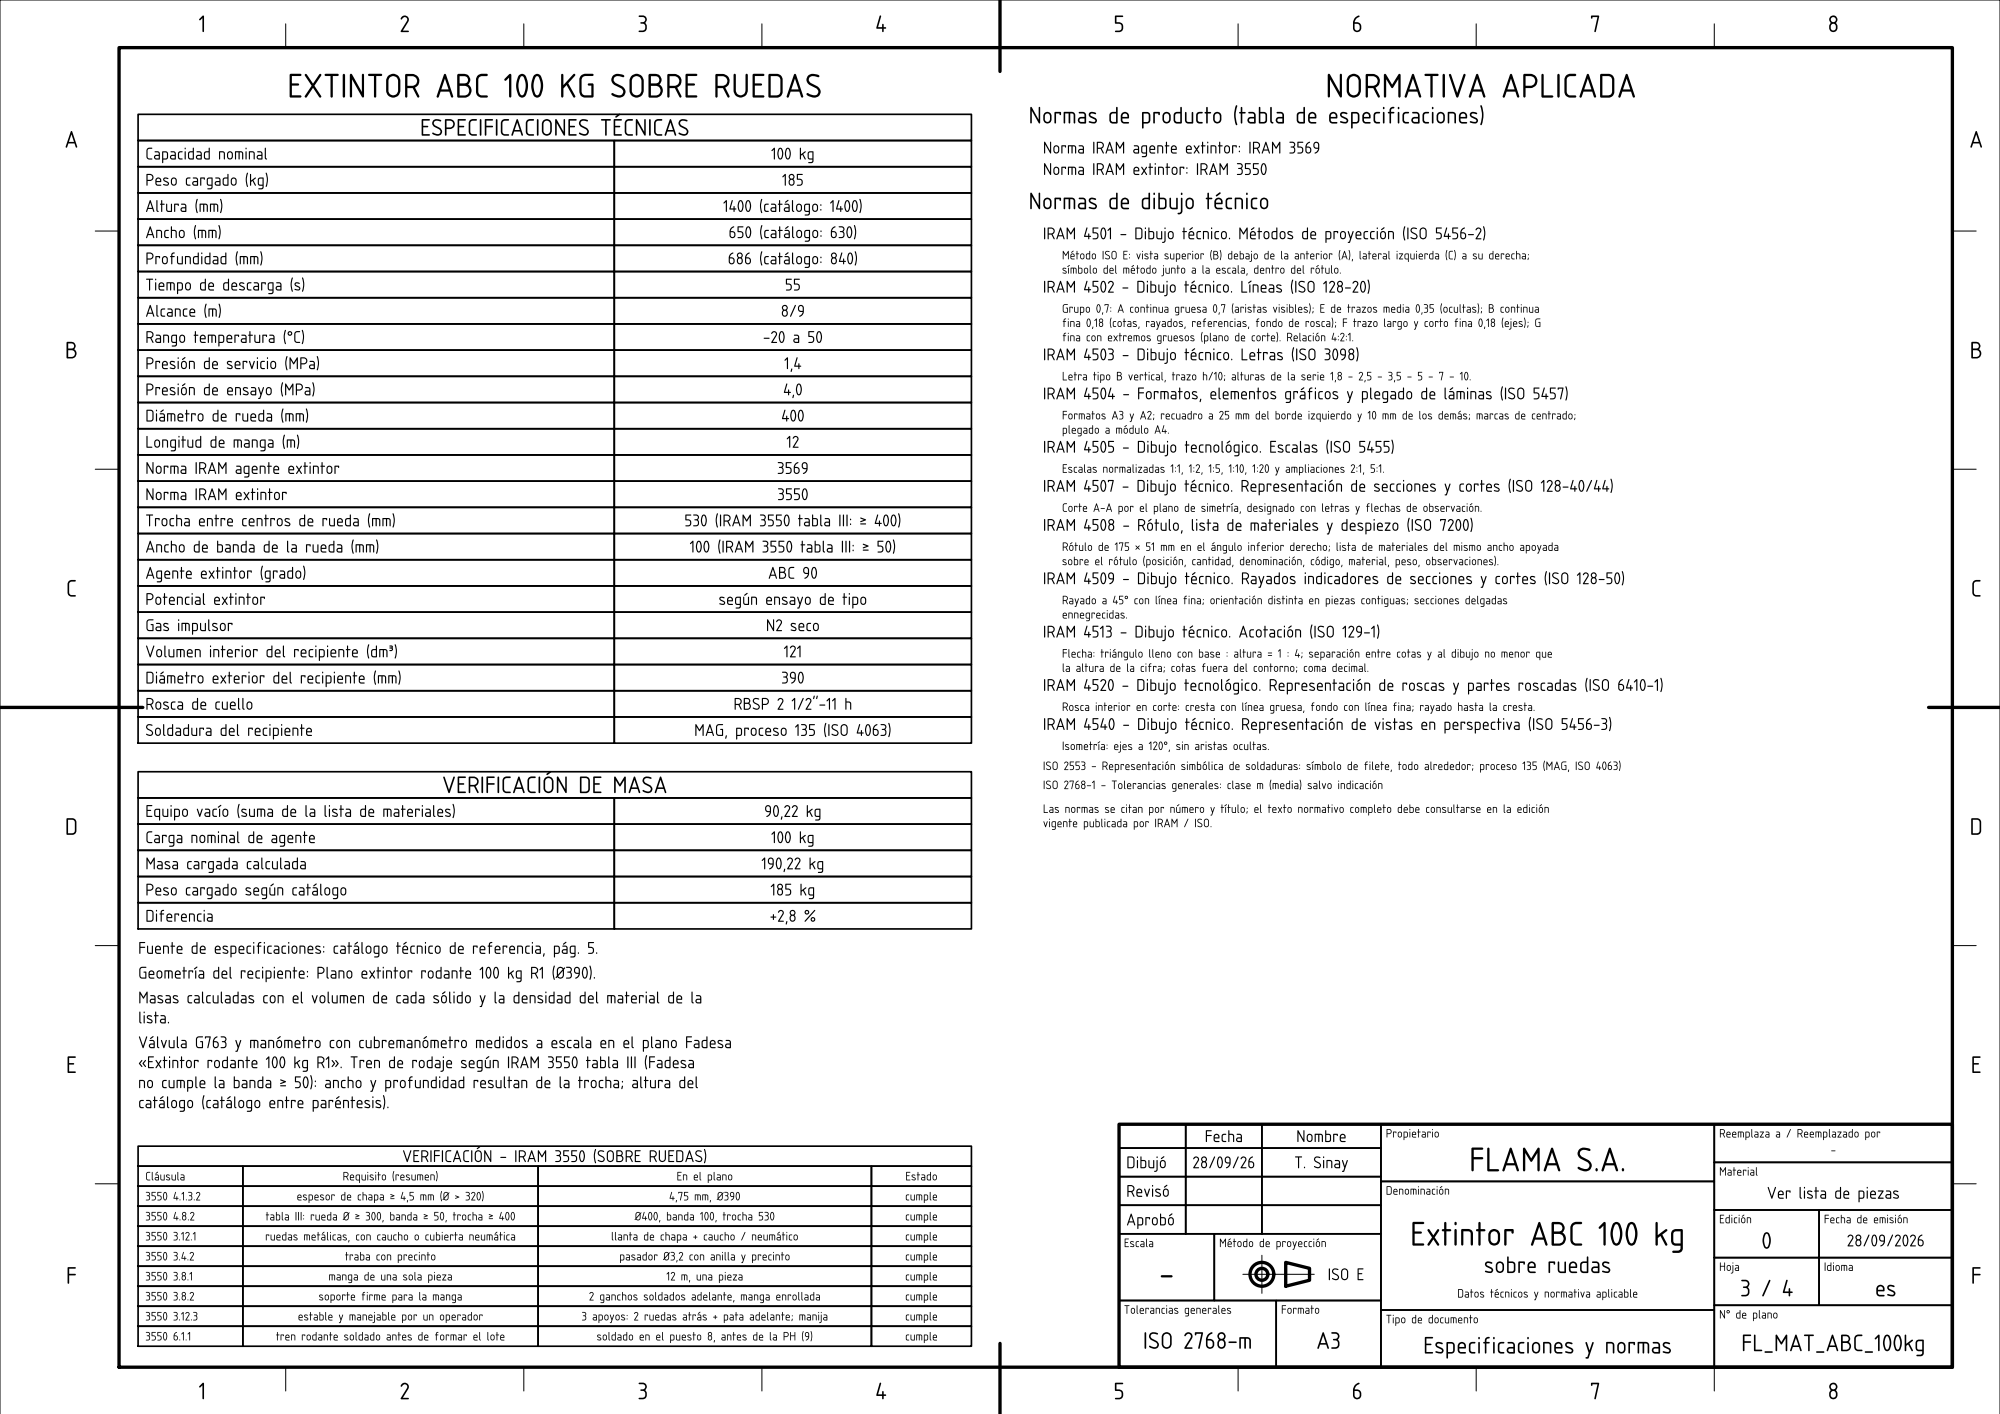
[picture p144: page 3]

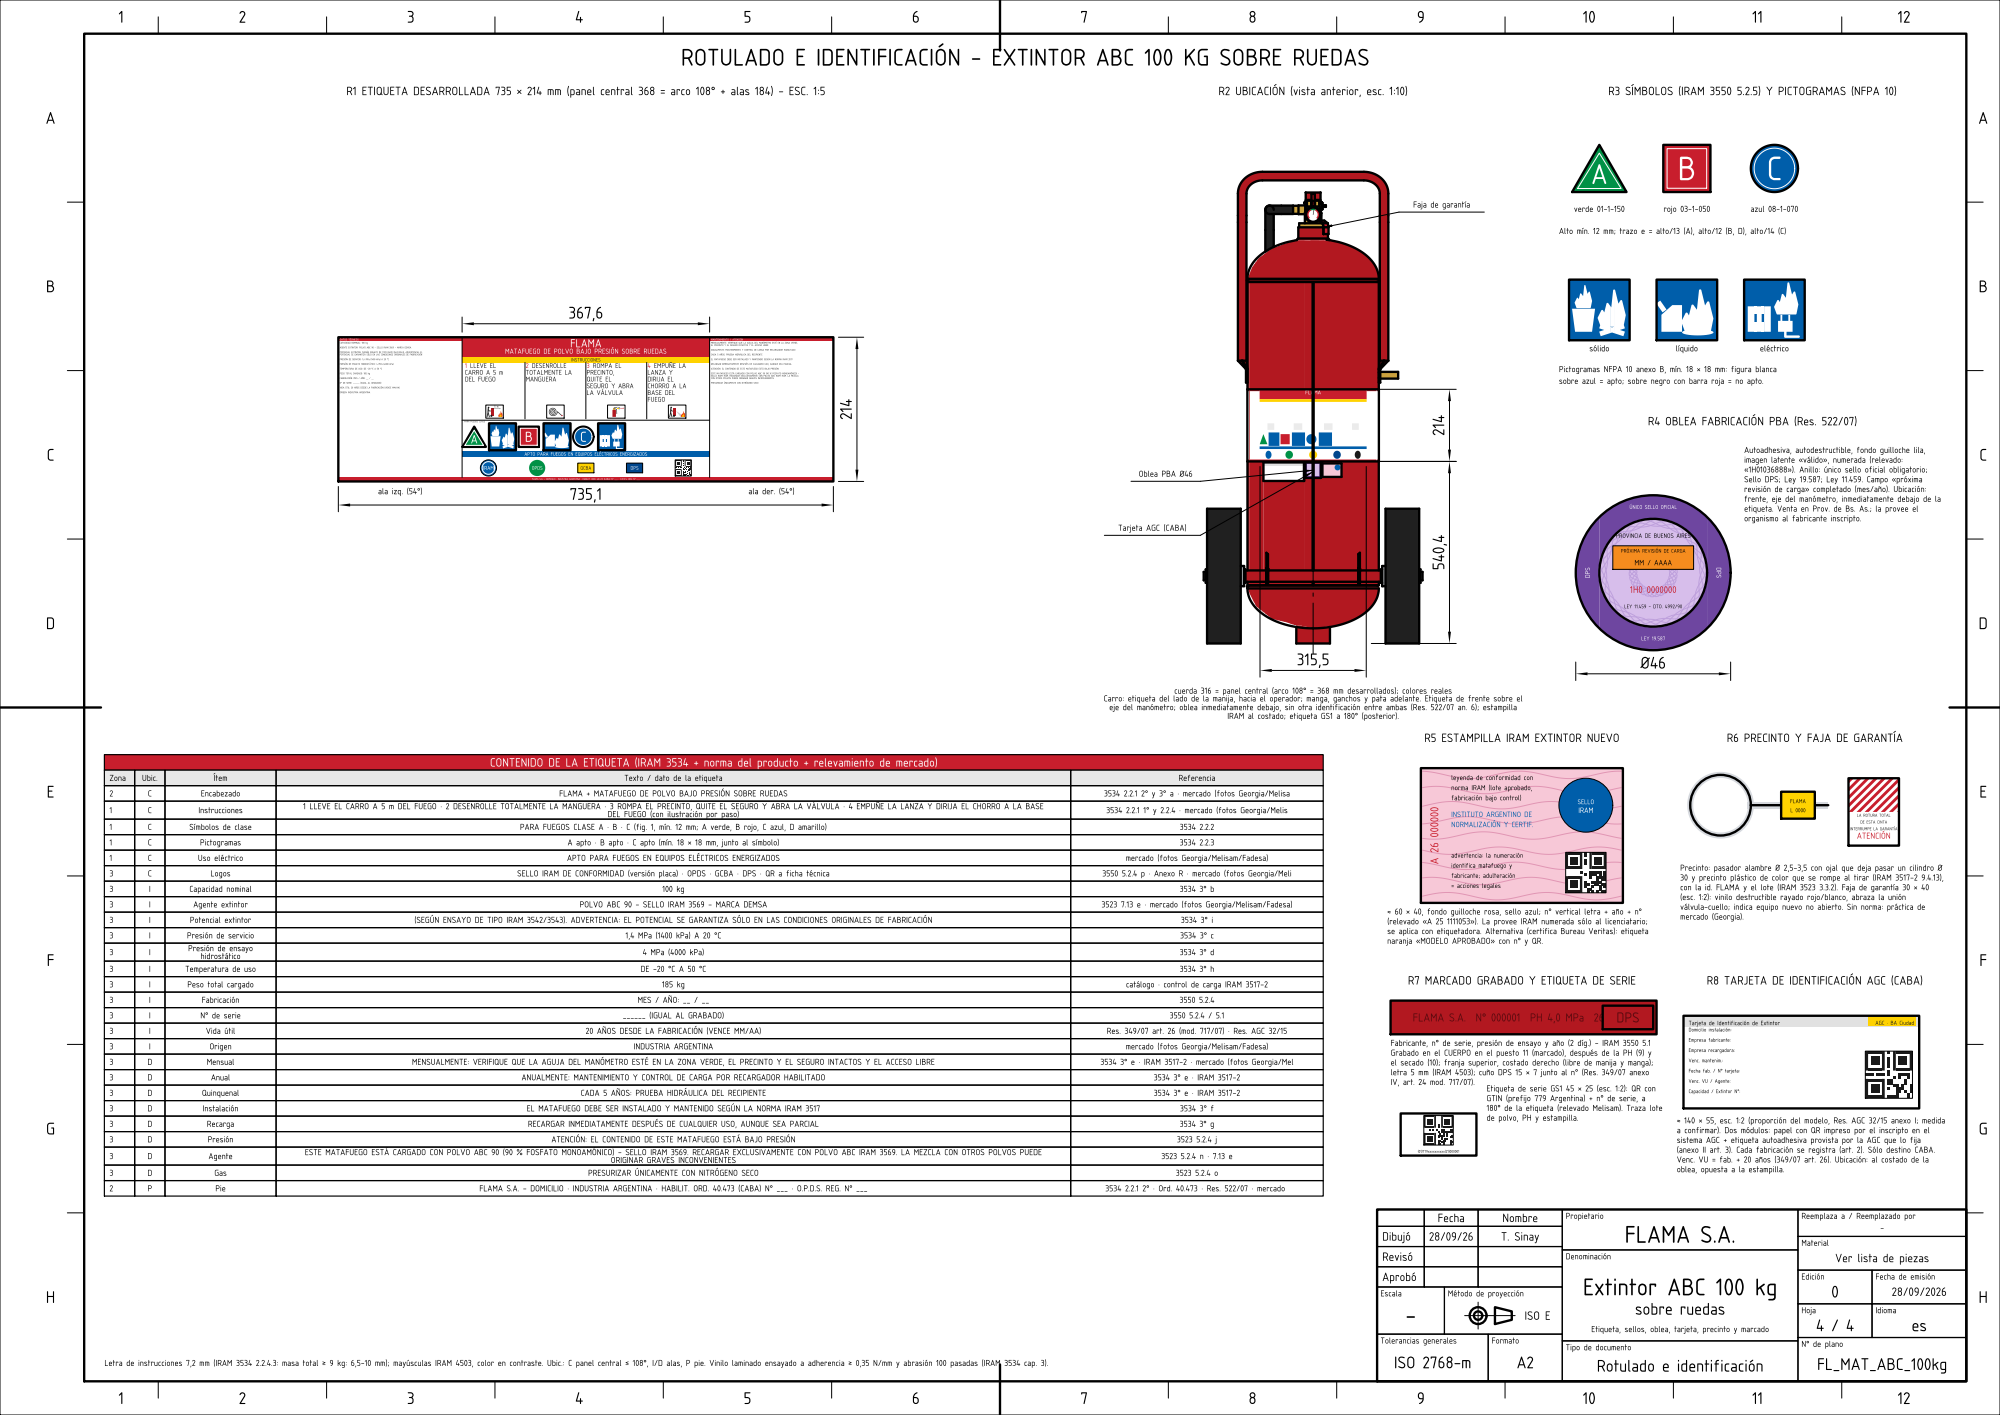
[picture p145: page 4]
