TadeoSinay/planos_flama-/salida/FL_MAT_ABC_10kg/FL_MAT_ABC_10kg.pdf

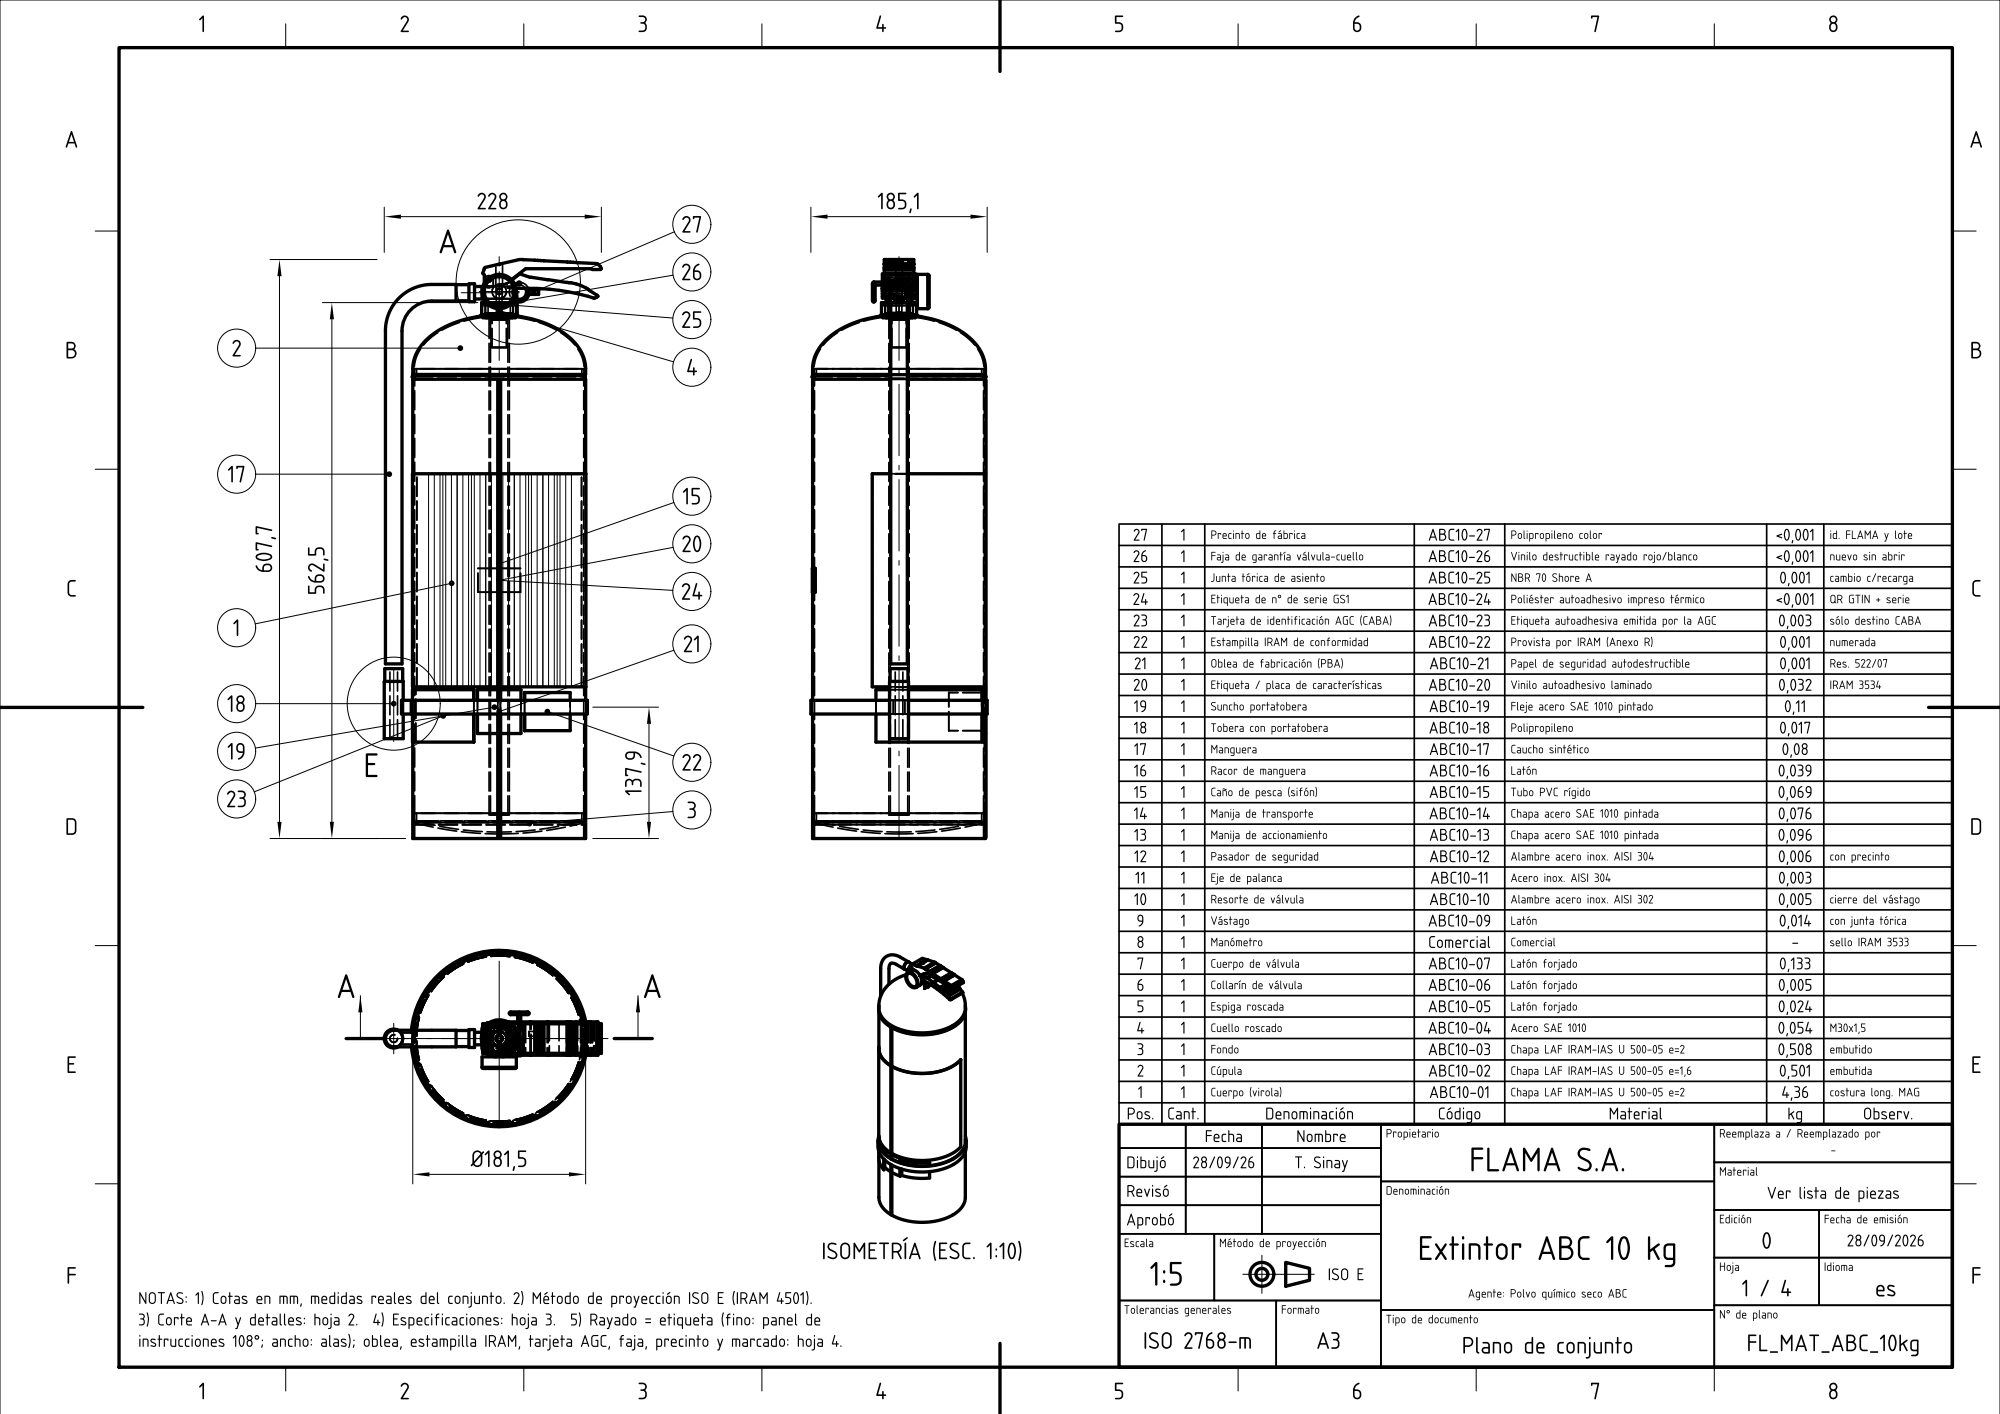
[picture p146: page 1]

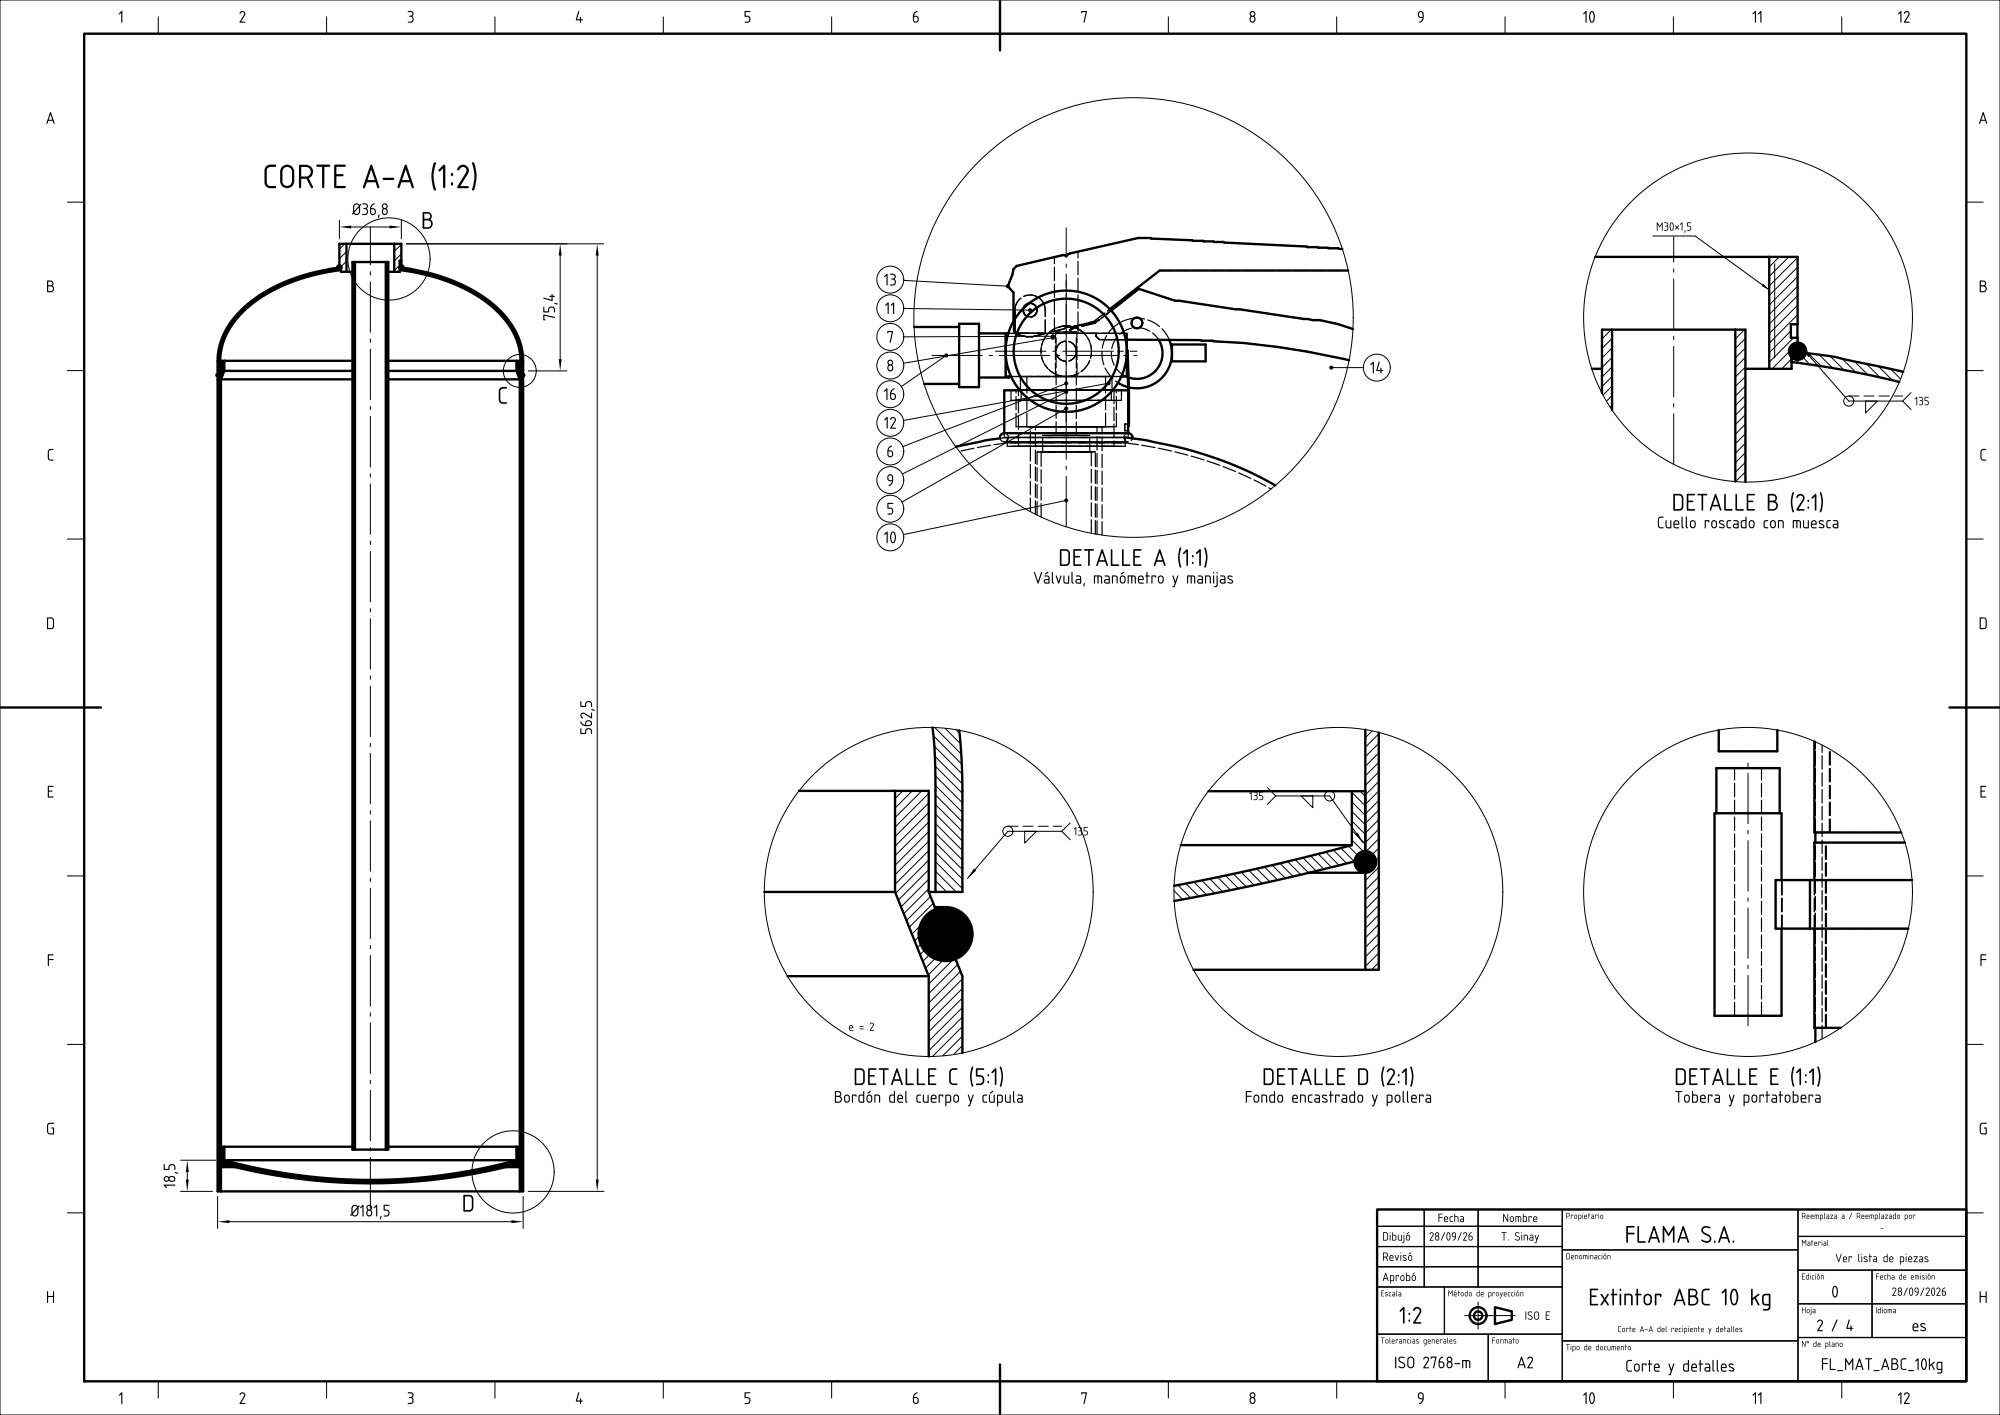
[picture p147: page 2]

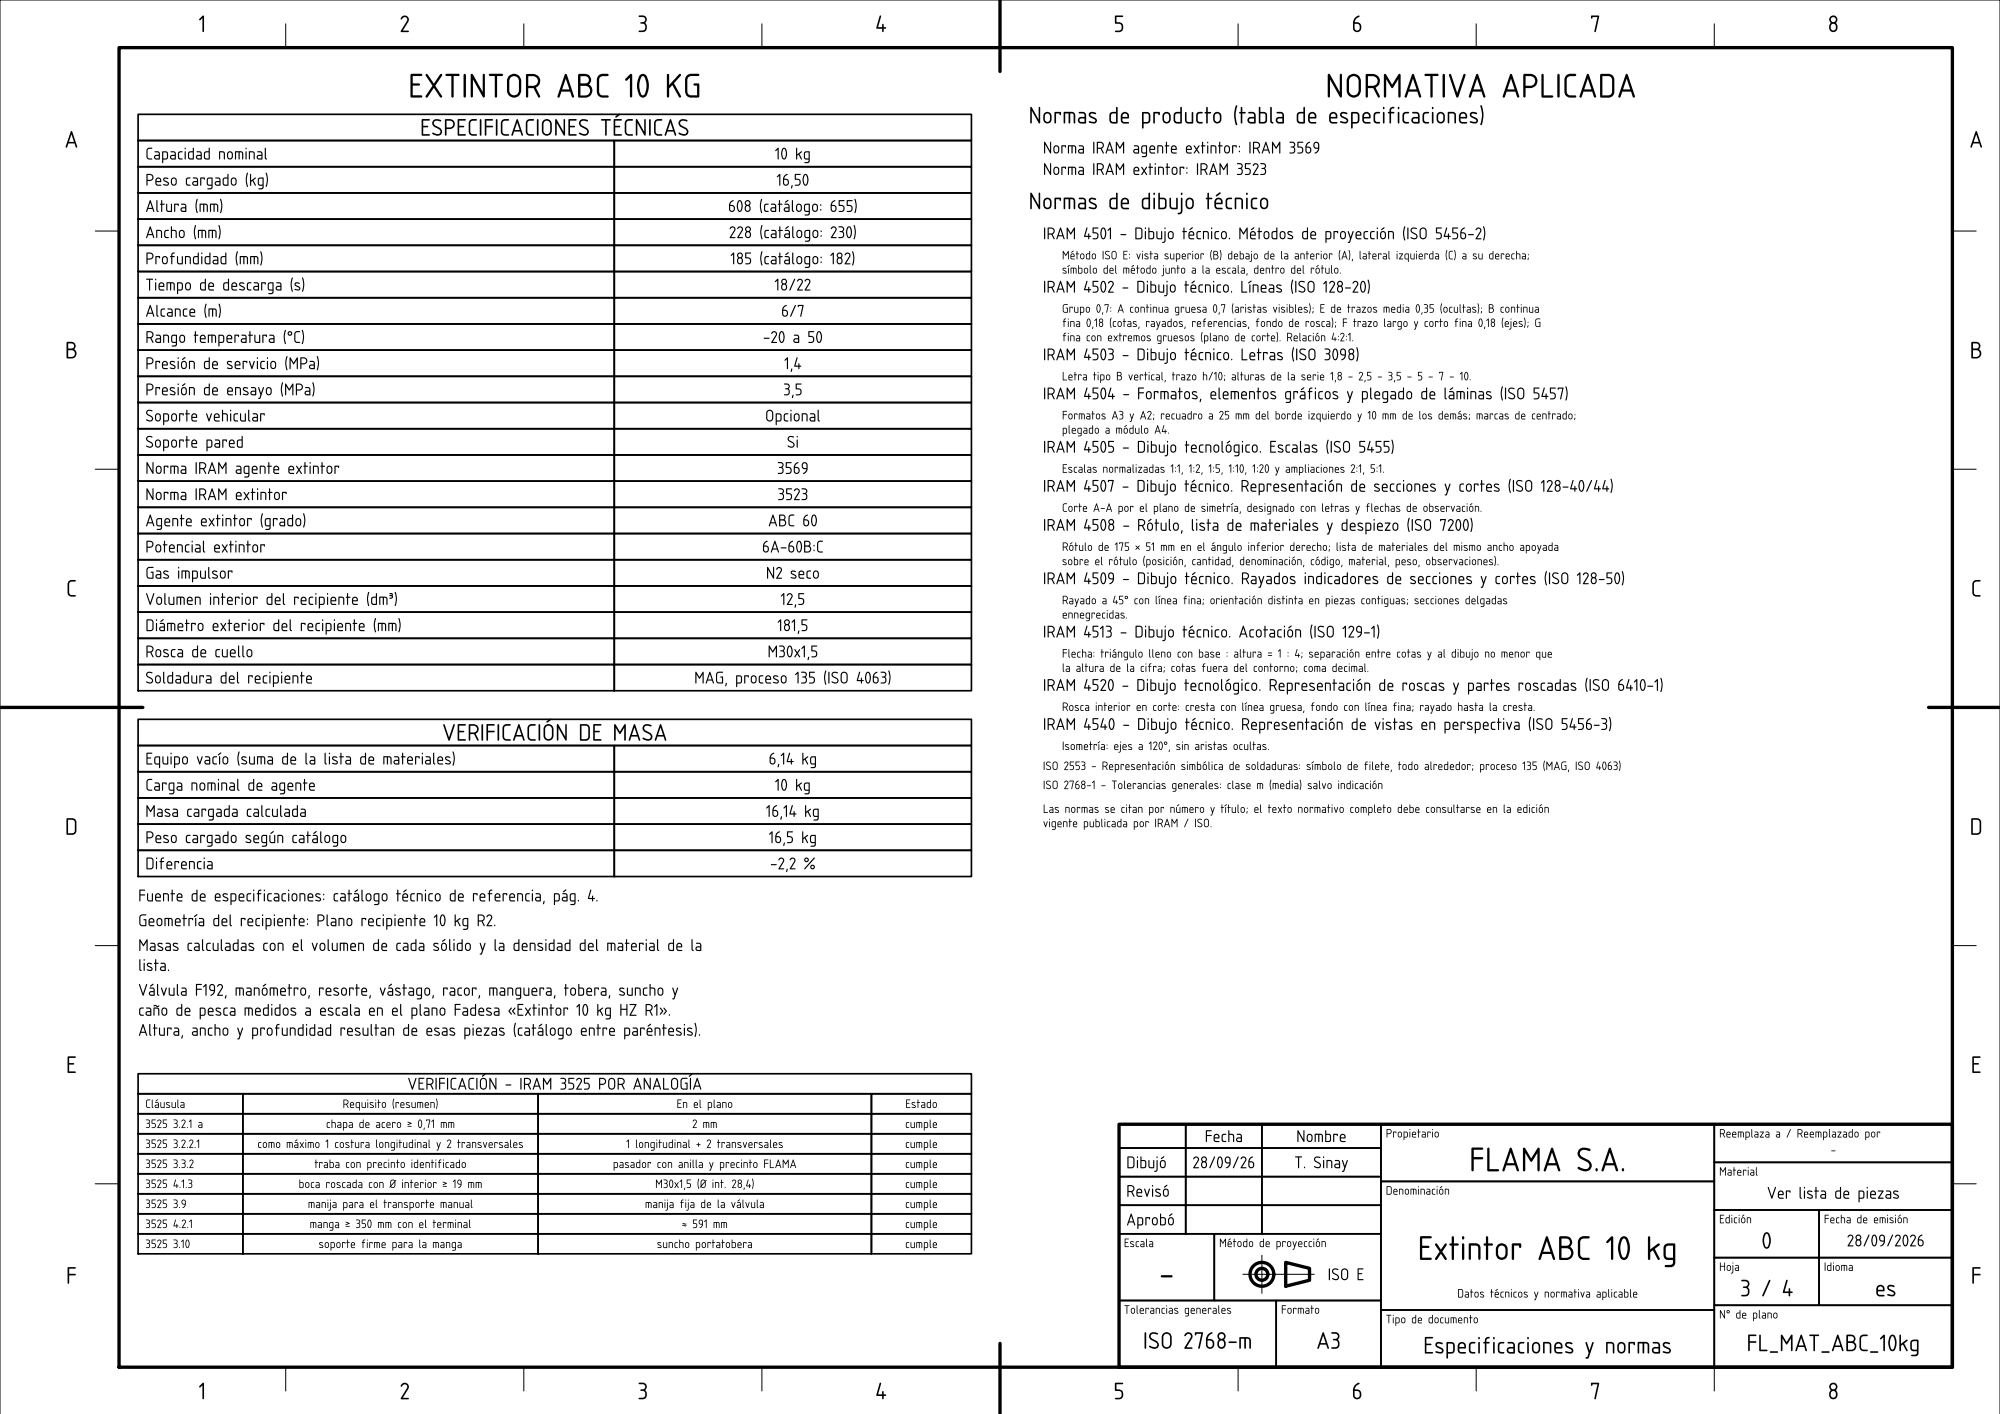
[picture p148: page 3]

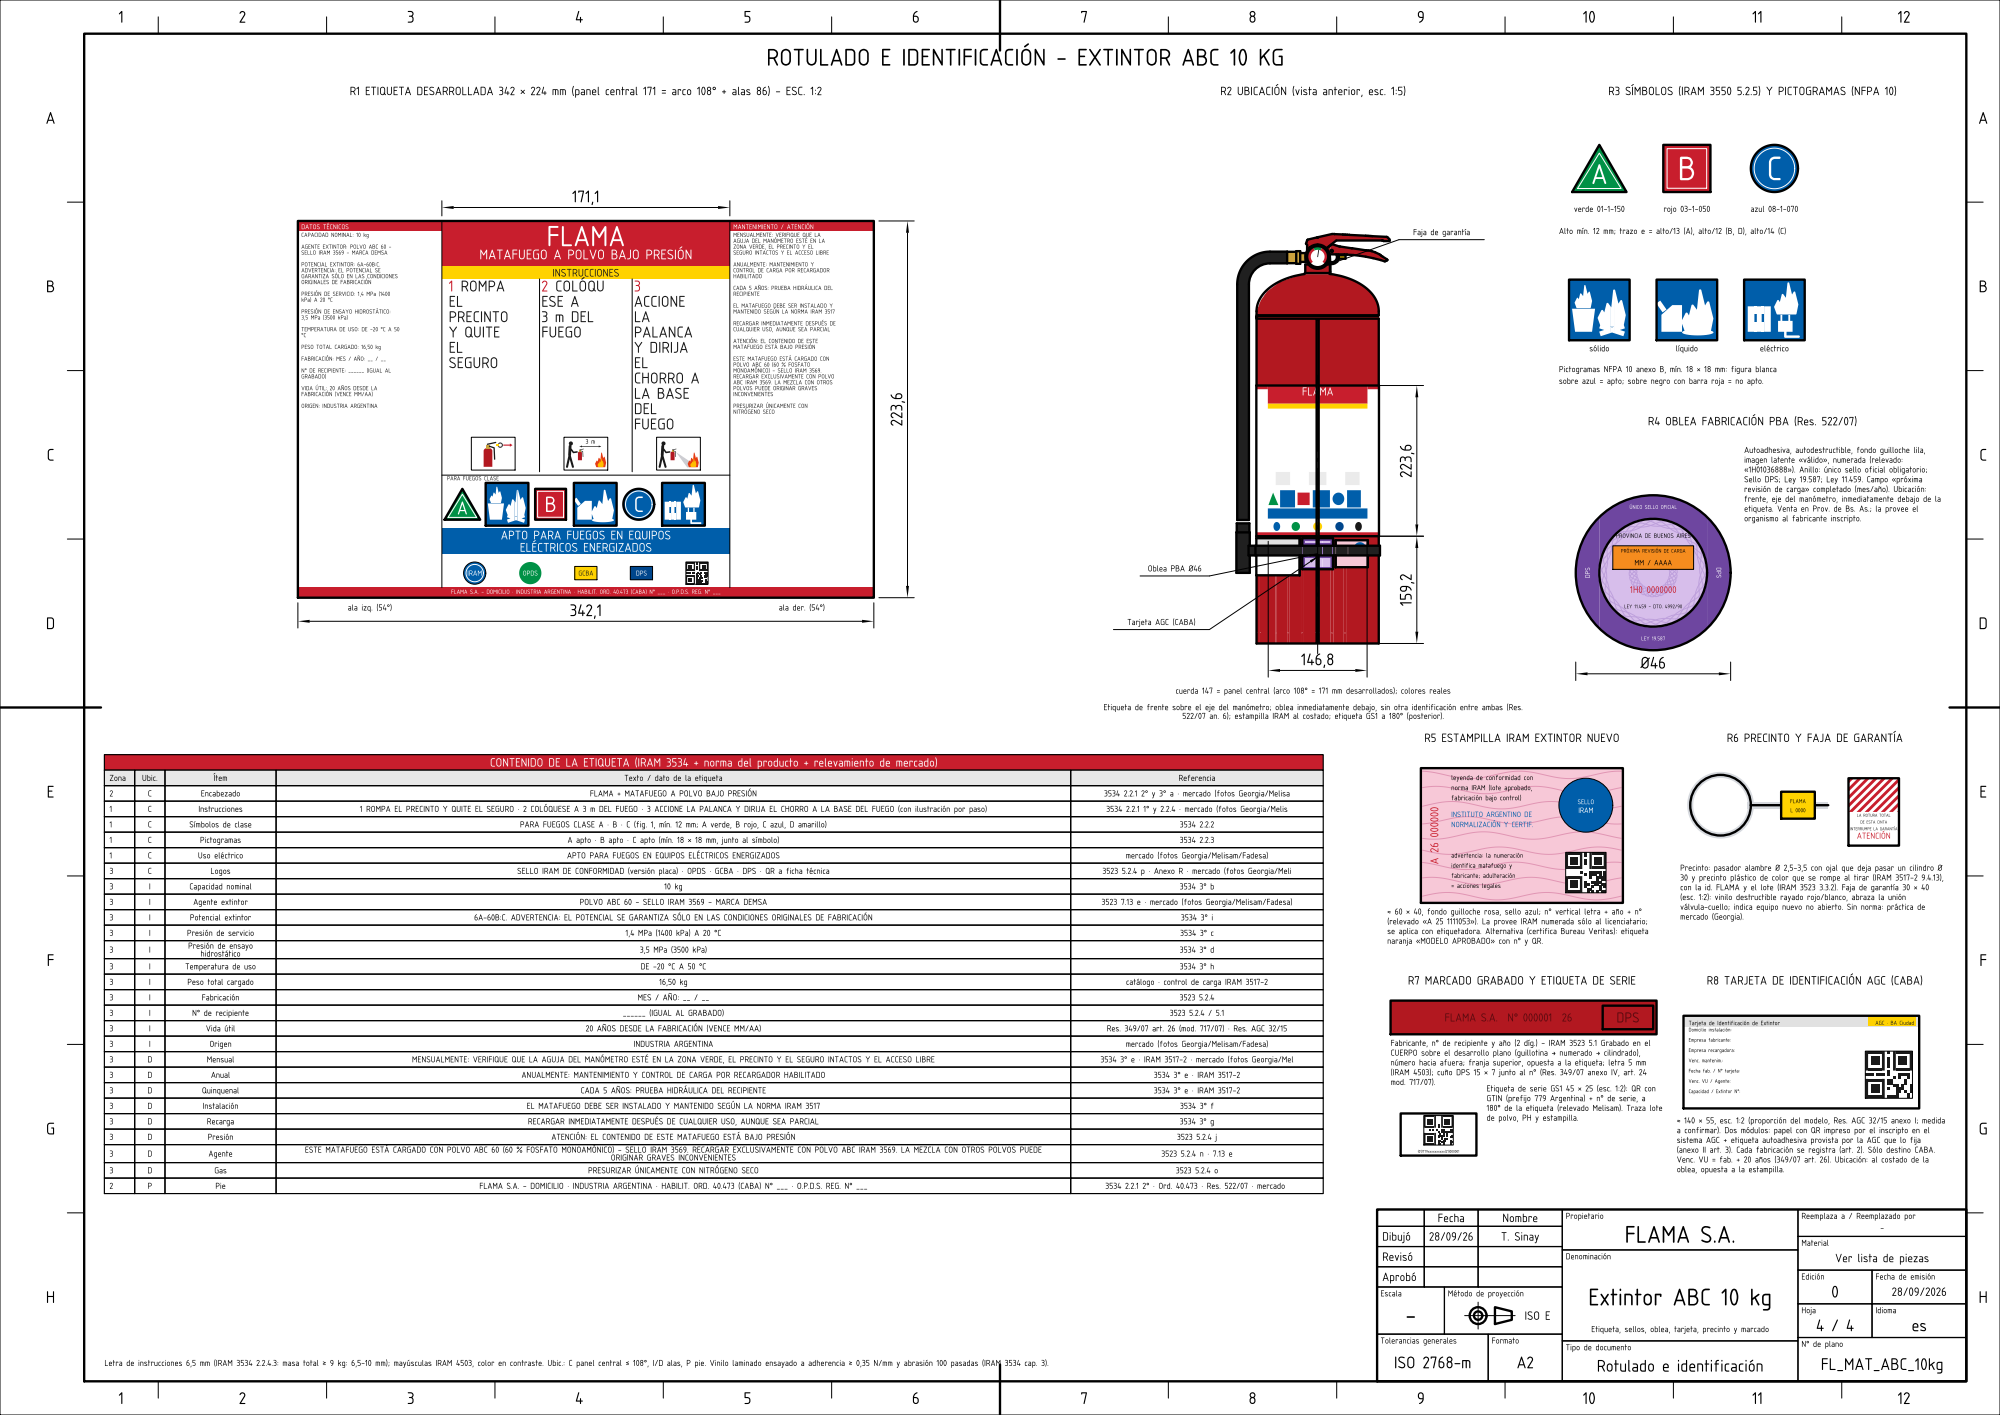
[picture p149: page 4]
