TadeoSinay/planos_flama-/salida/FL_MAT_ABC_1kg/FL_MAT_ABC_1kg.pdf

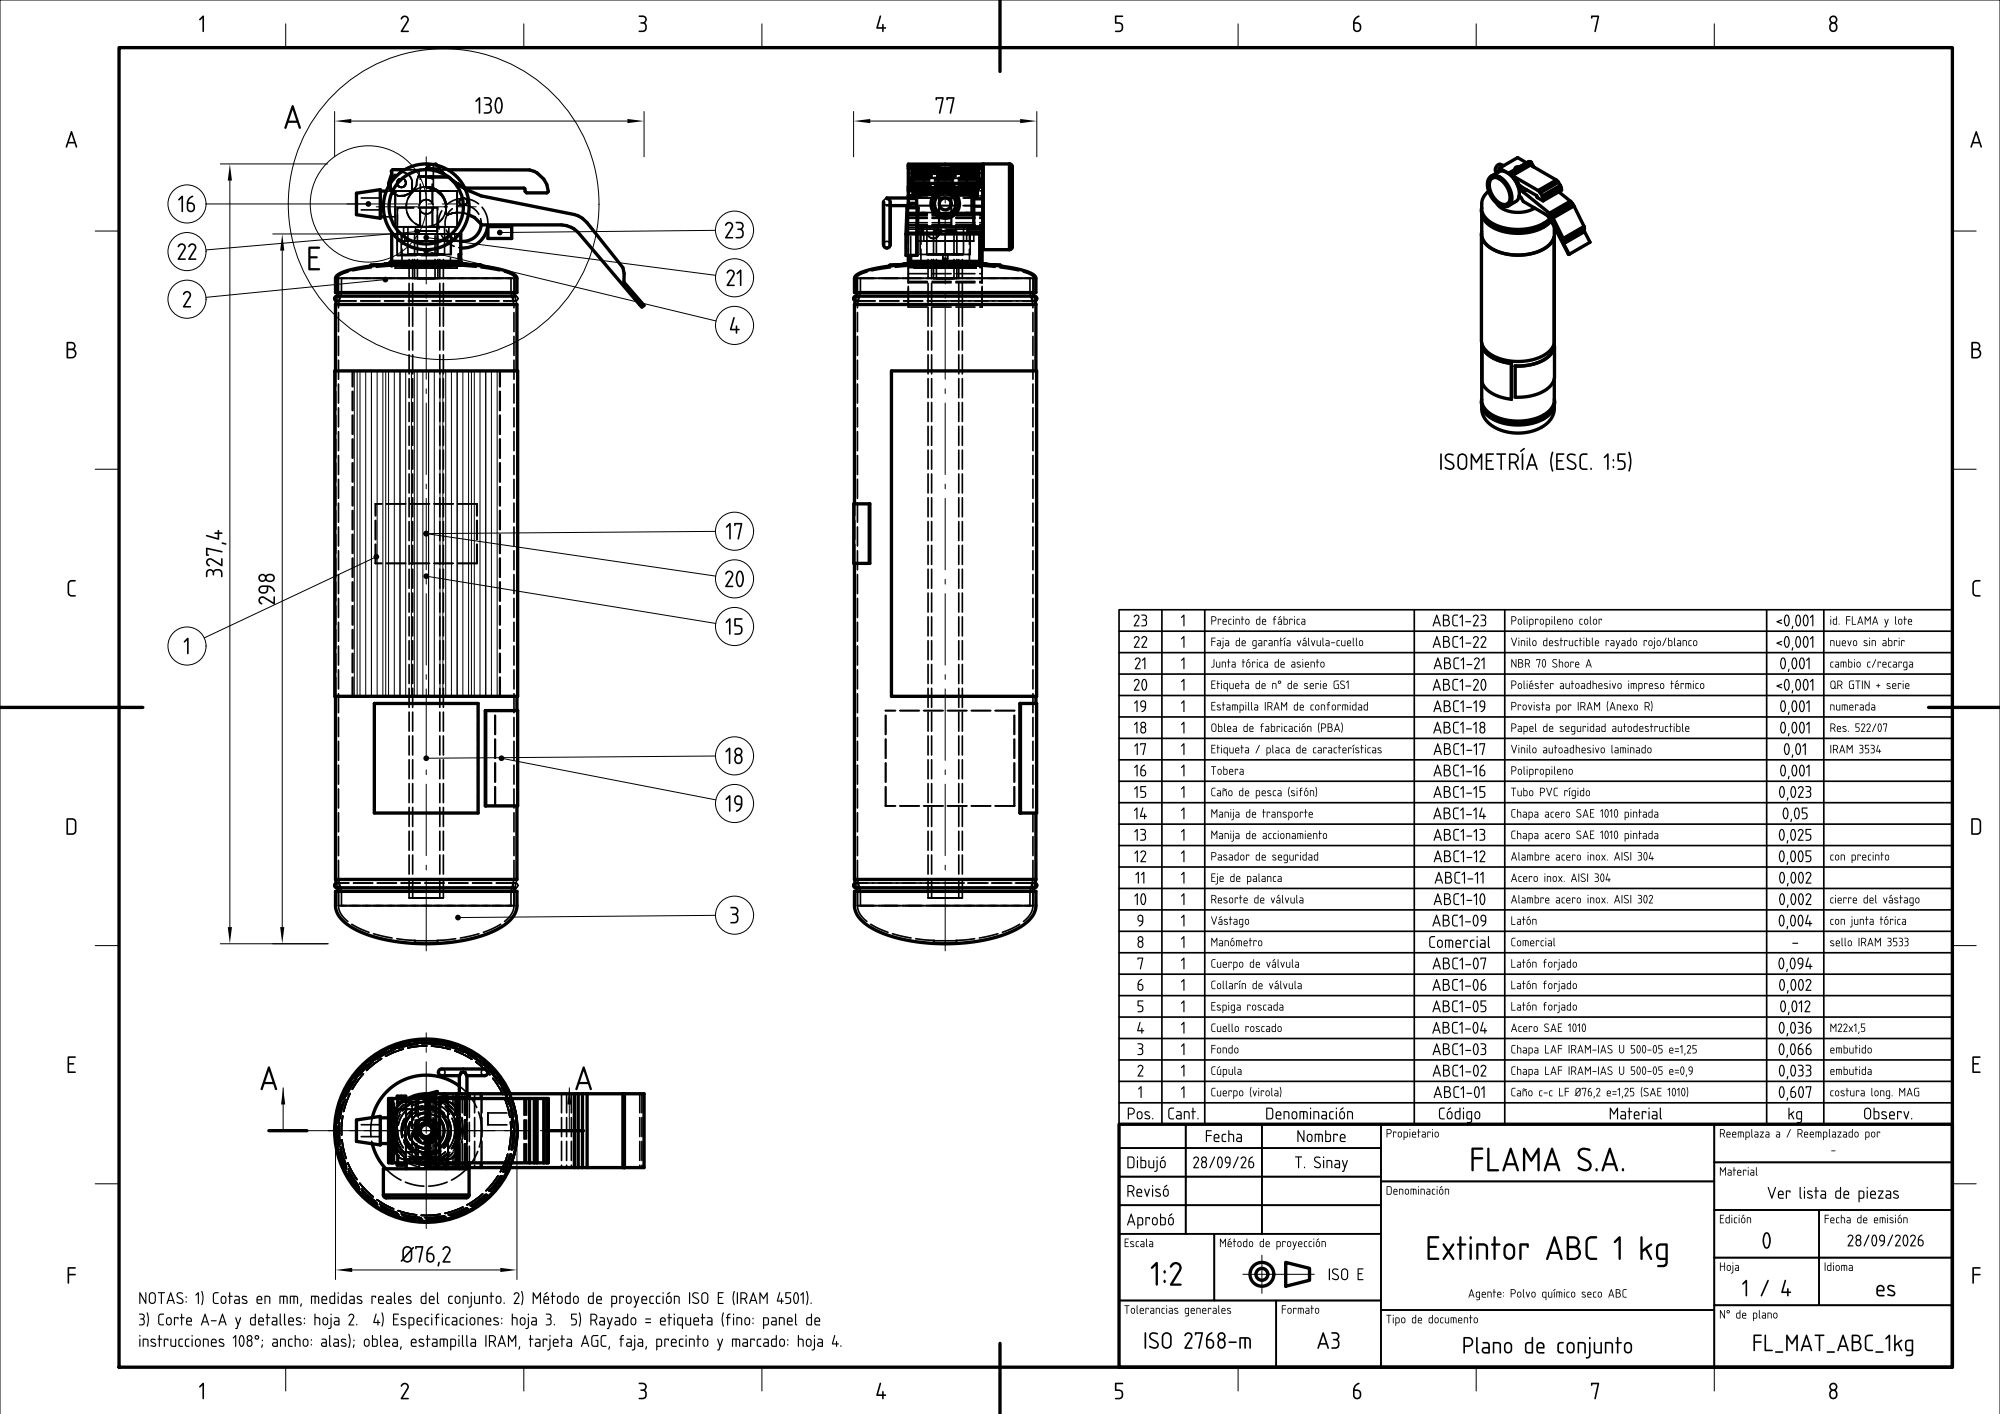
[picture p150: page 1]

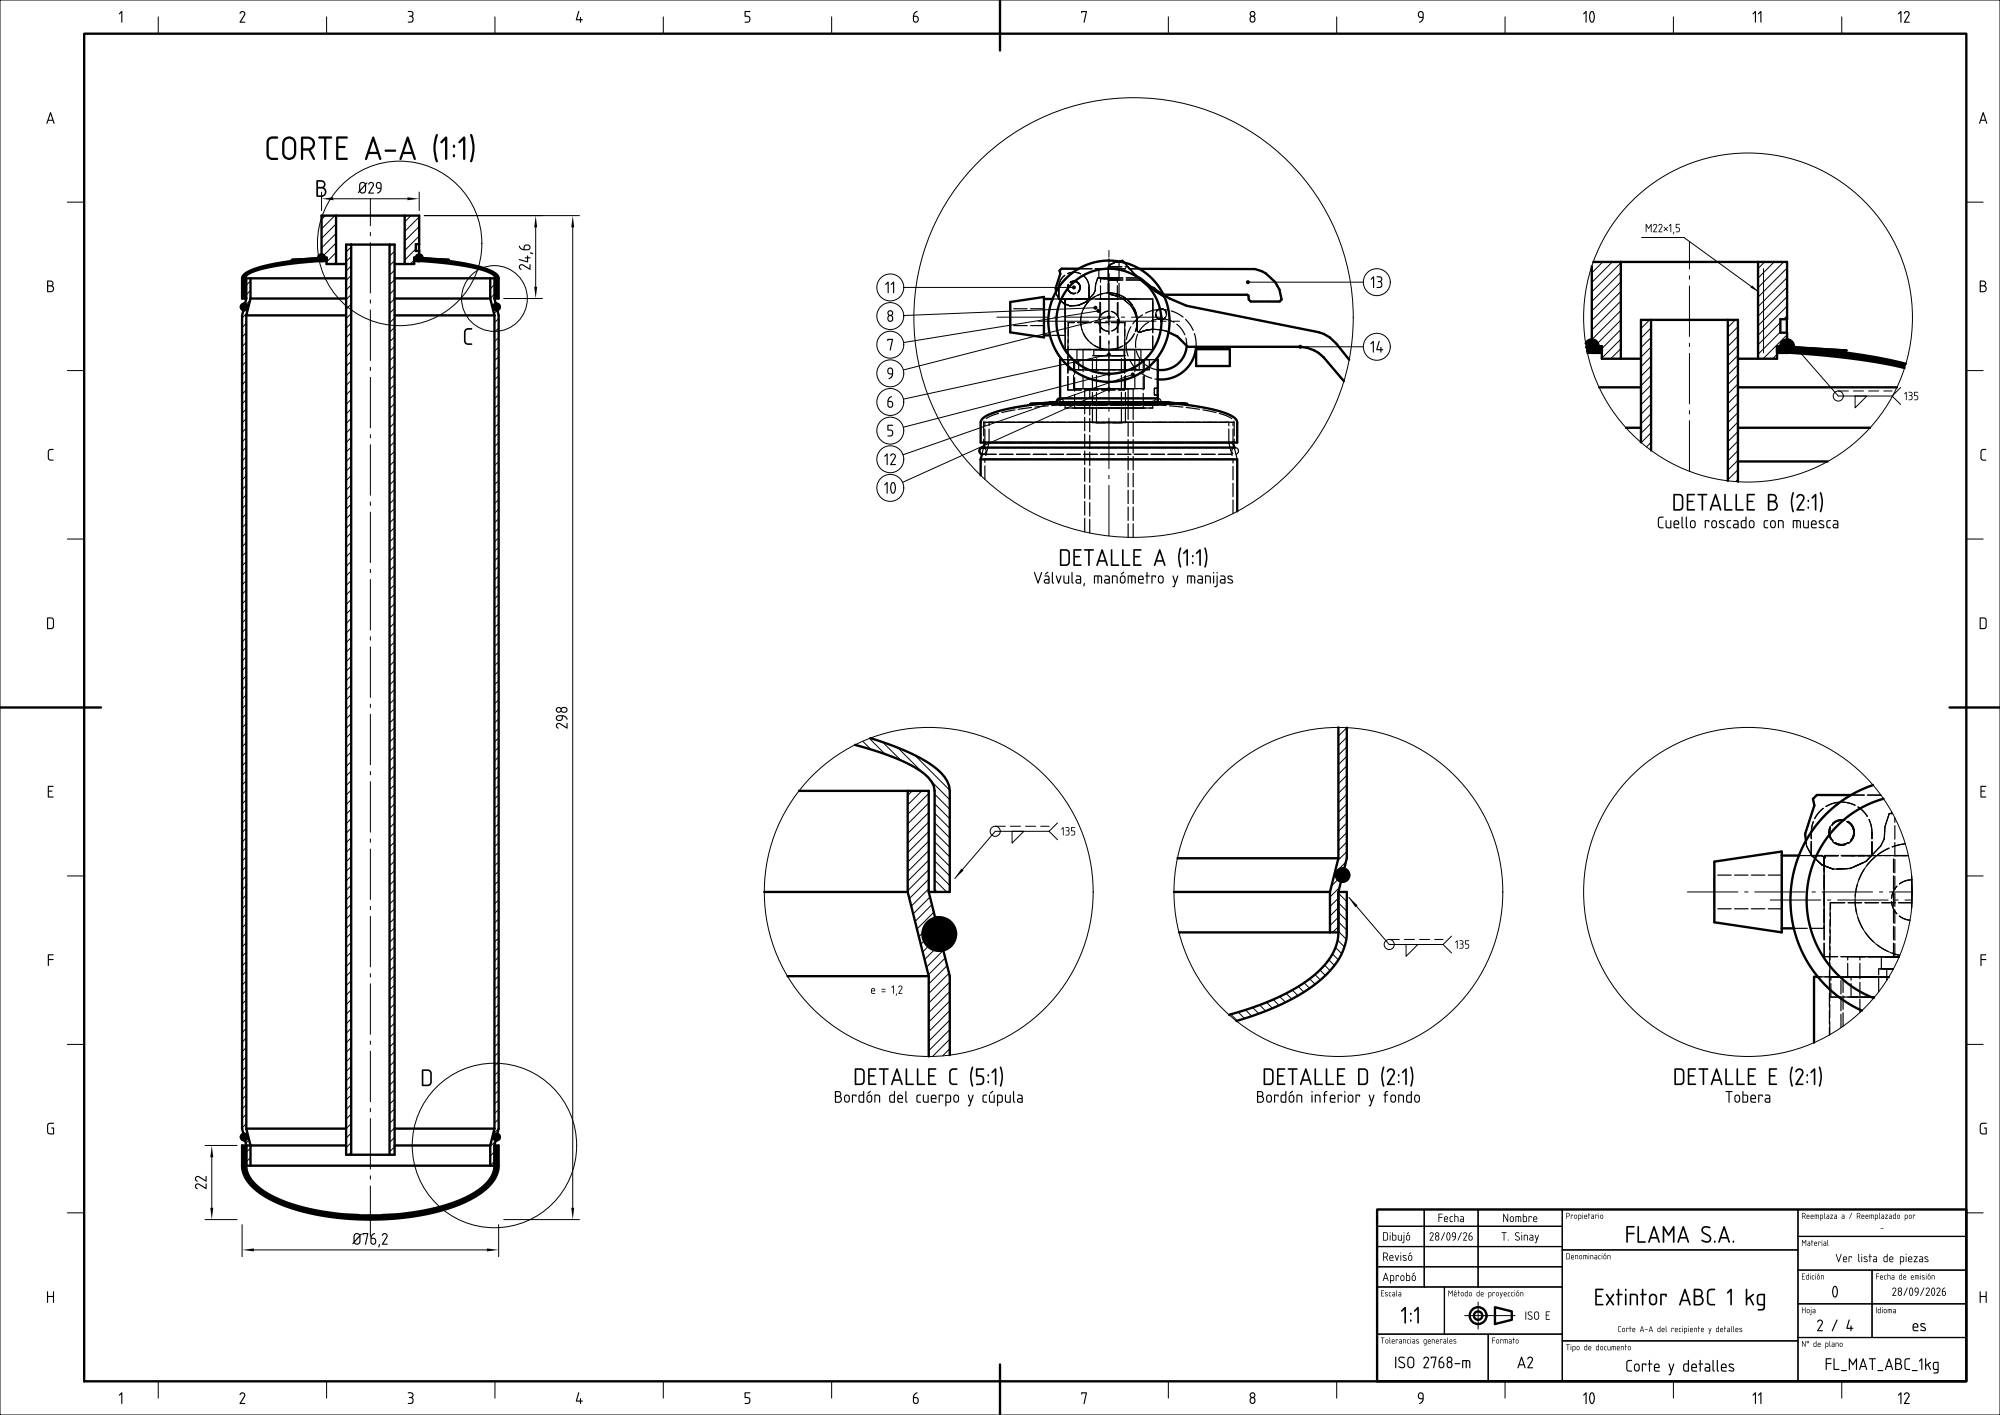
[picture p151: page 2]

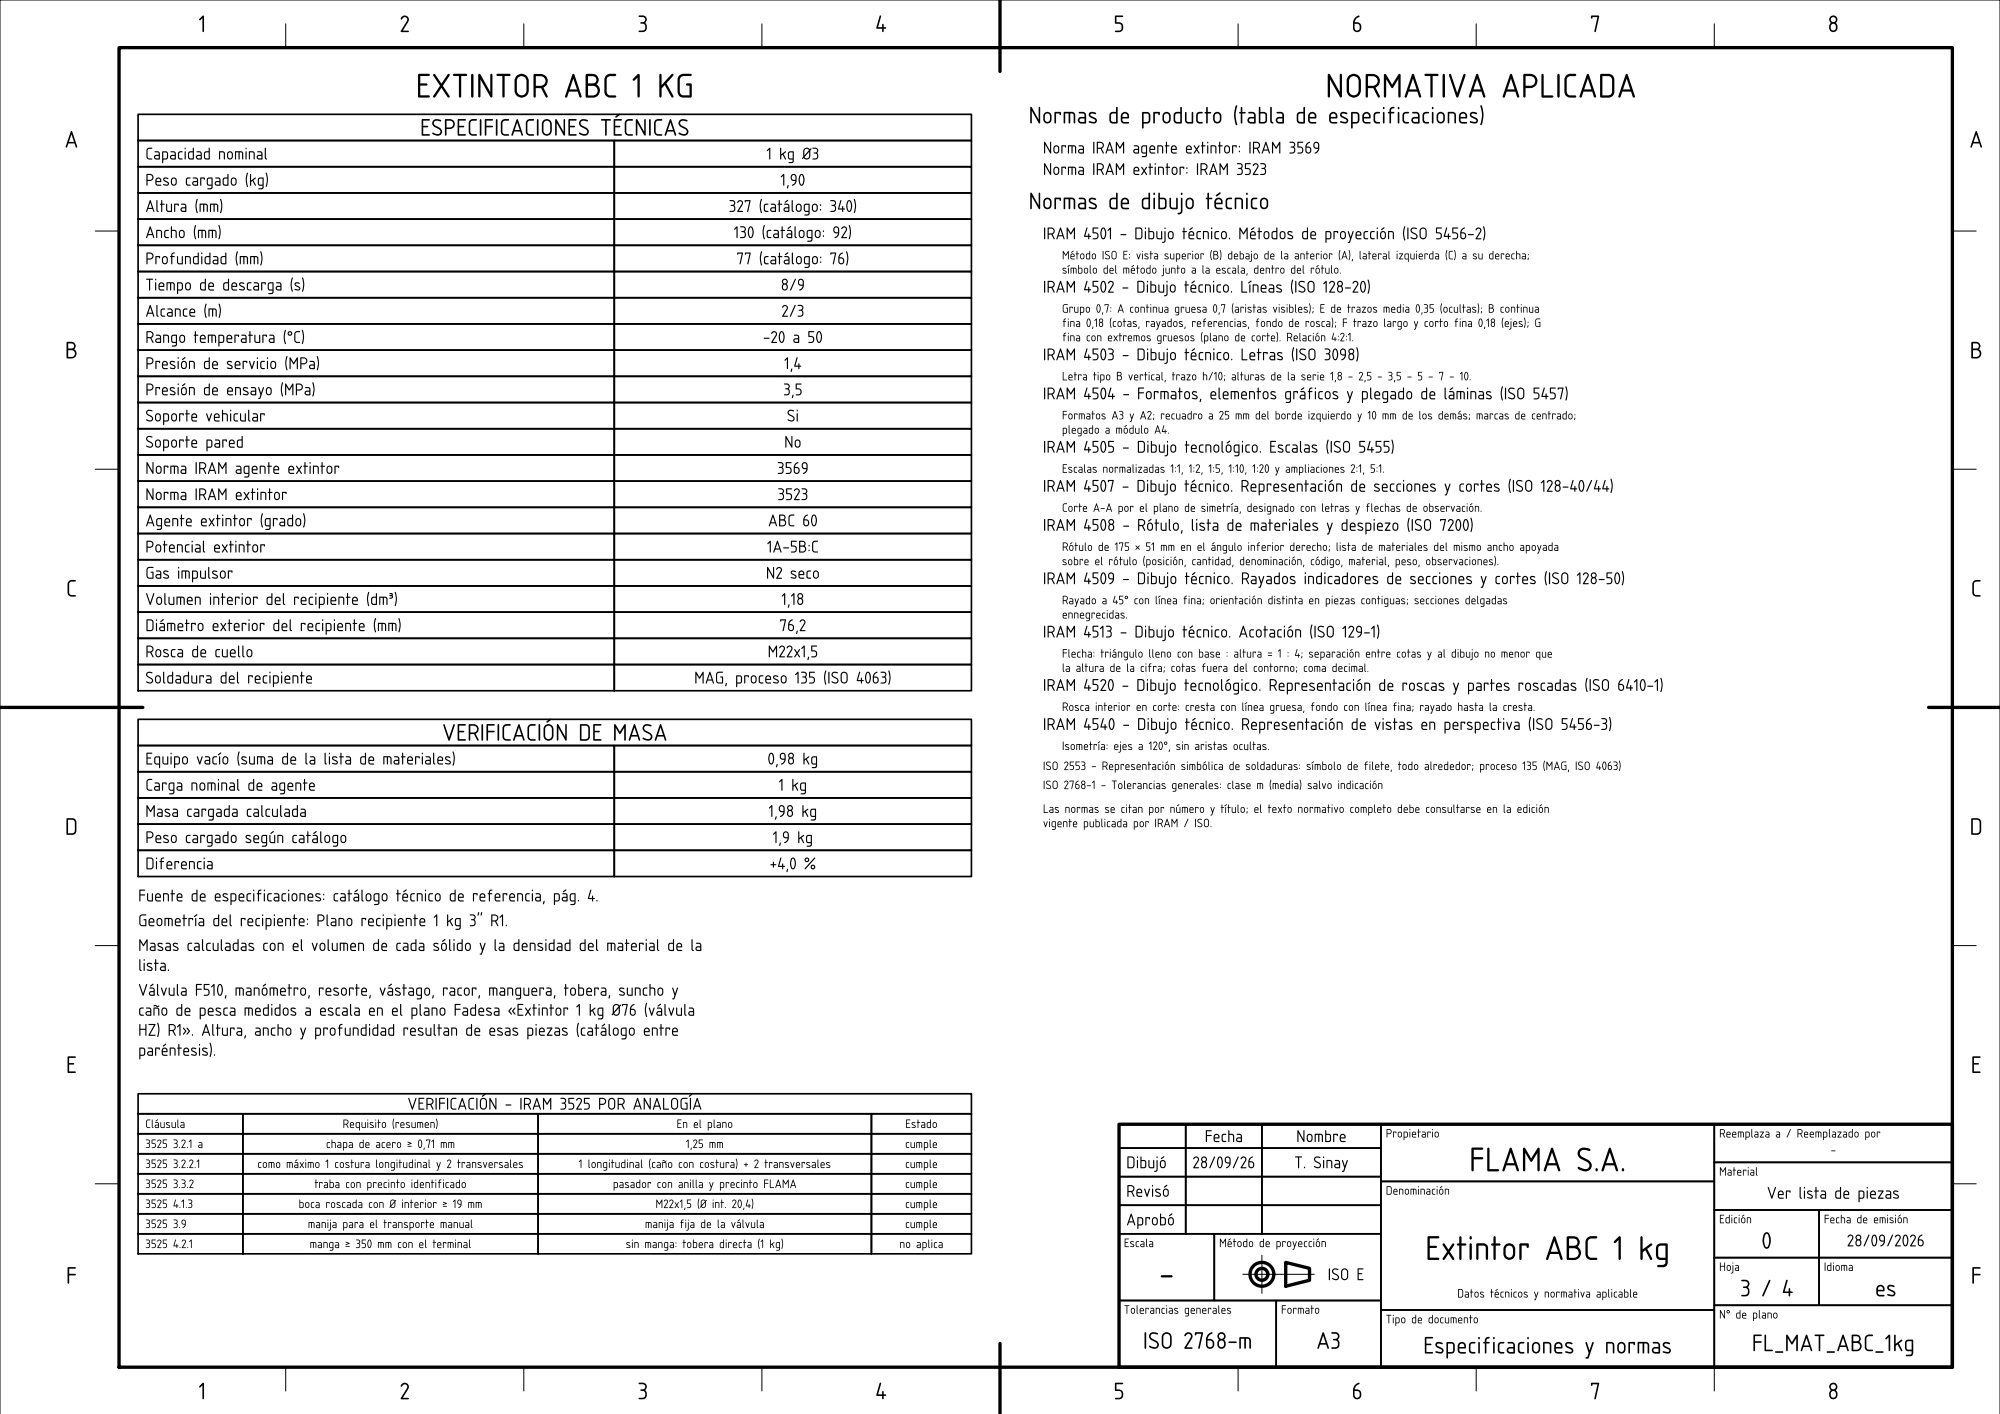
[picture p152: page 3]

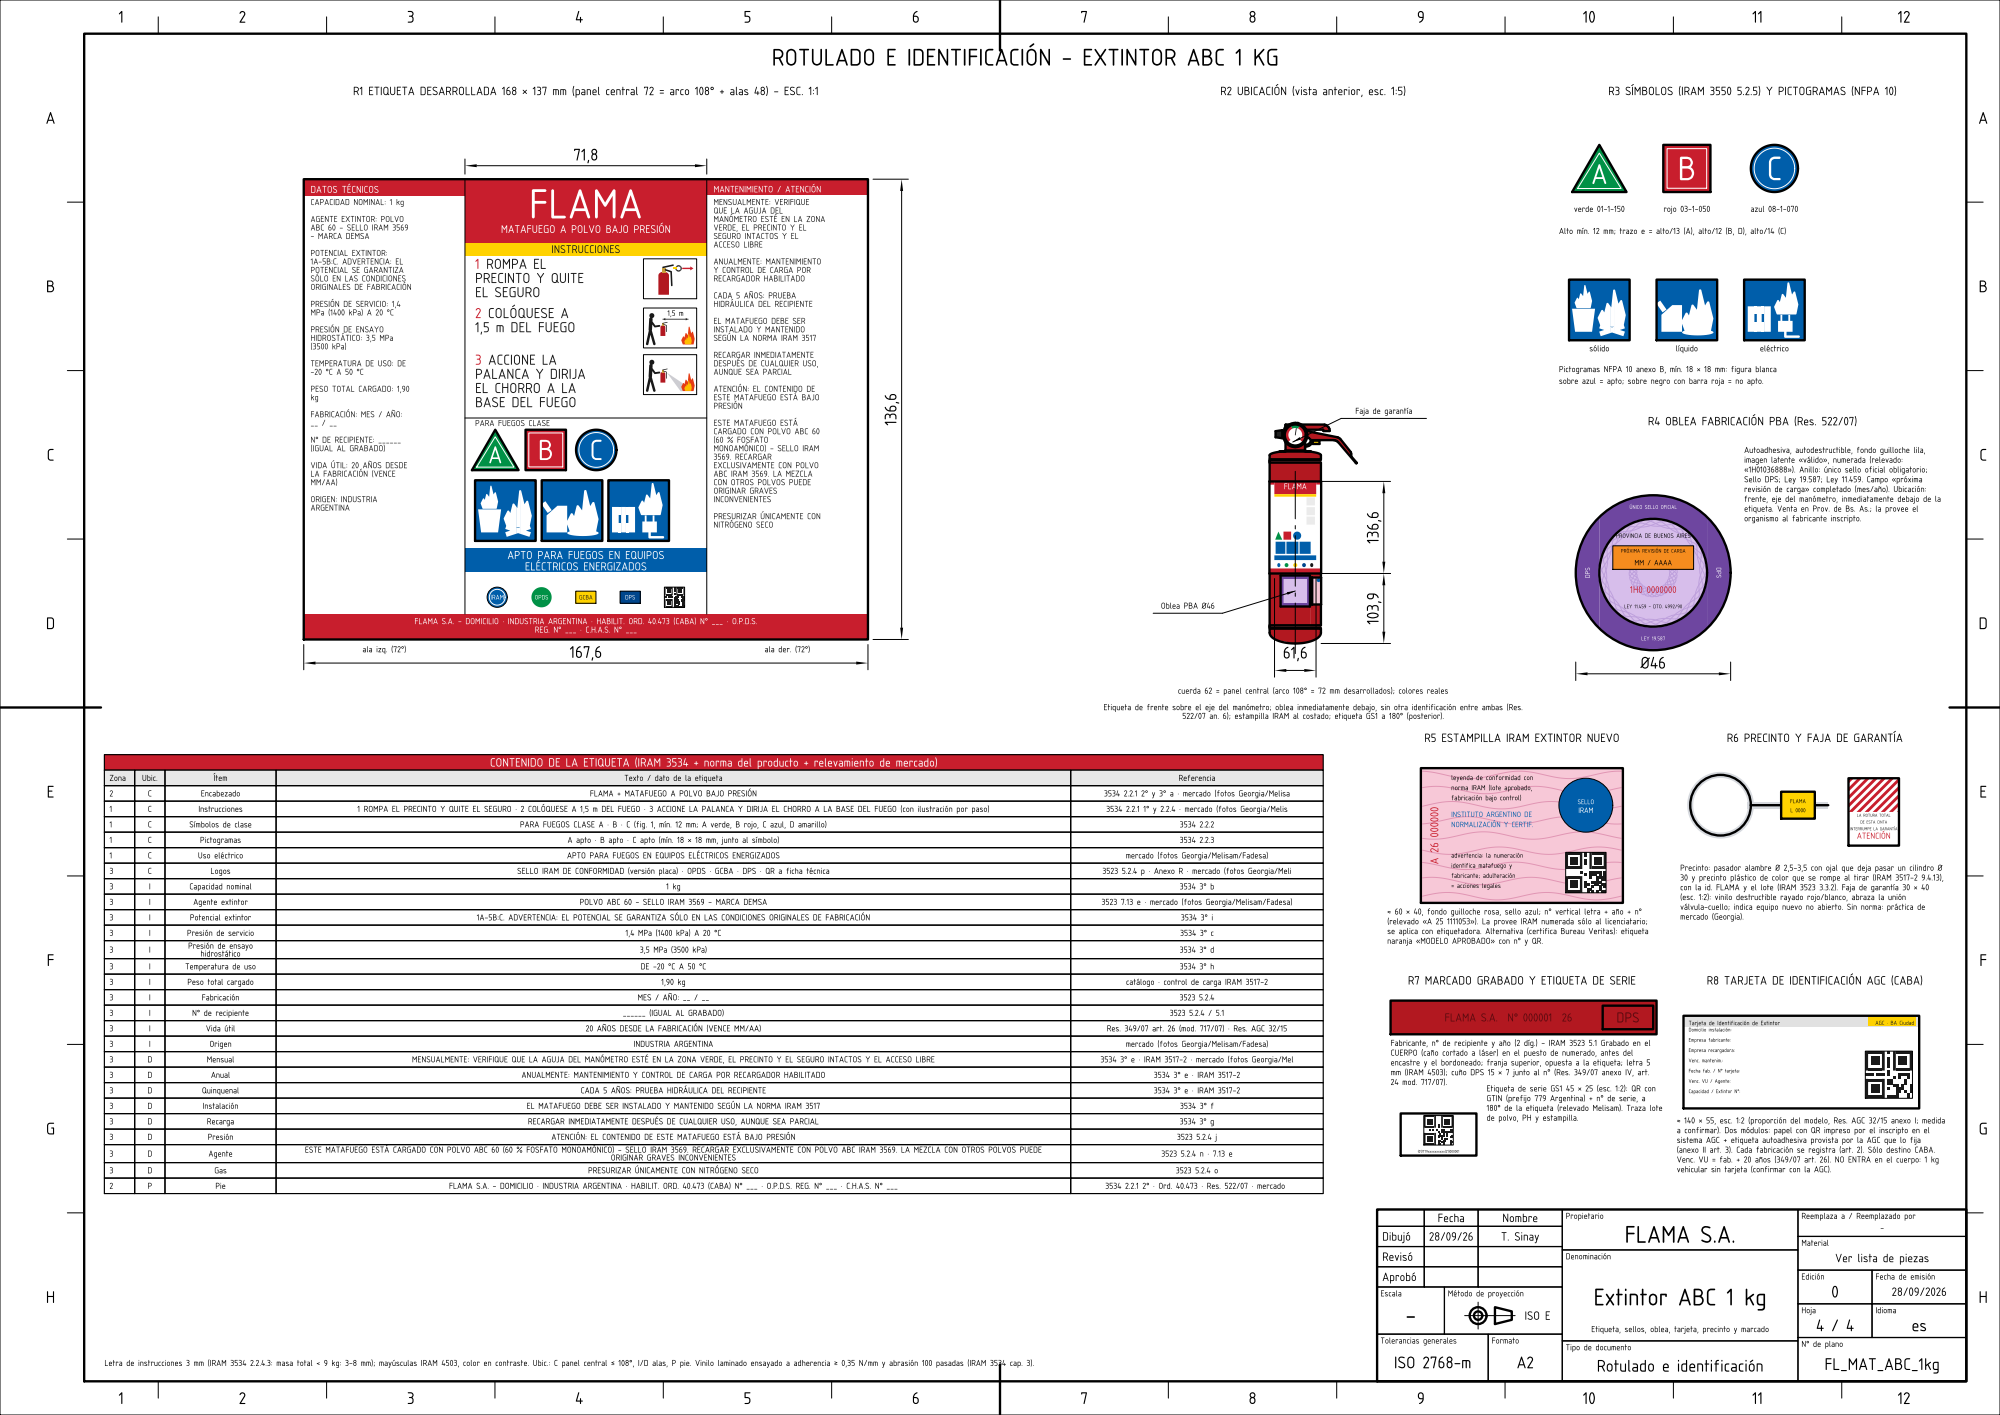
[picture p153: page 4]
