TadeoSinay/planos_flama-/salida/FL_MAT_ABC_2.5kg/FL_MAT_ABC_2.5kg.pdf

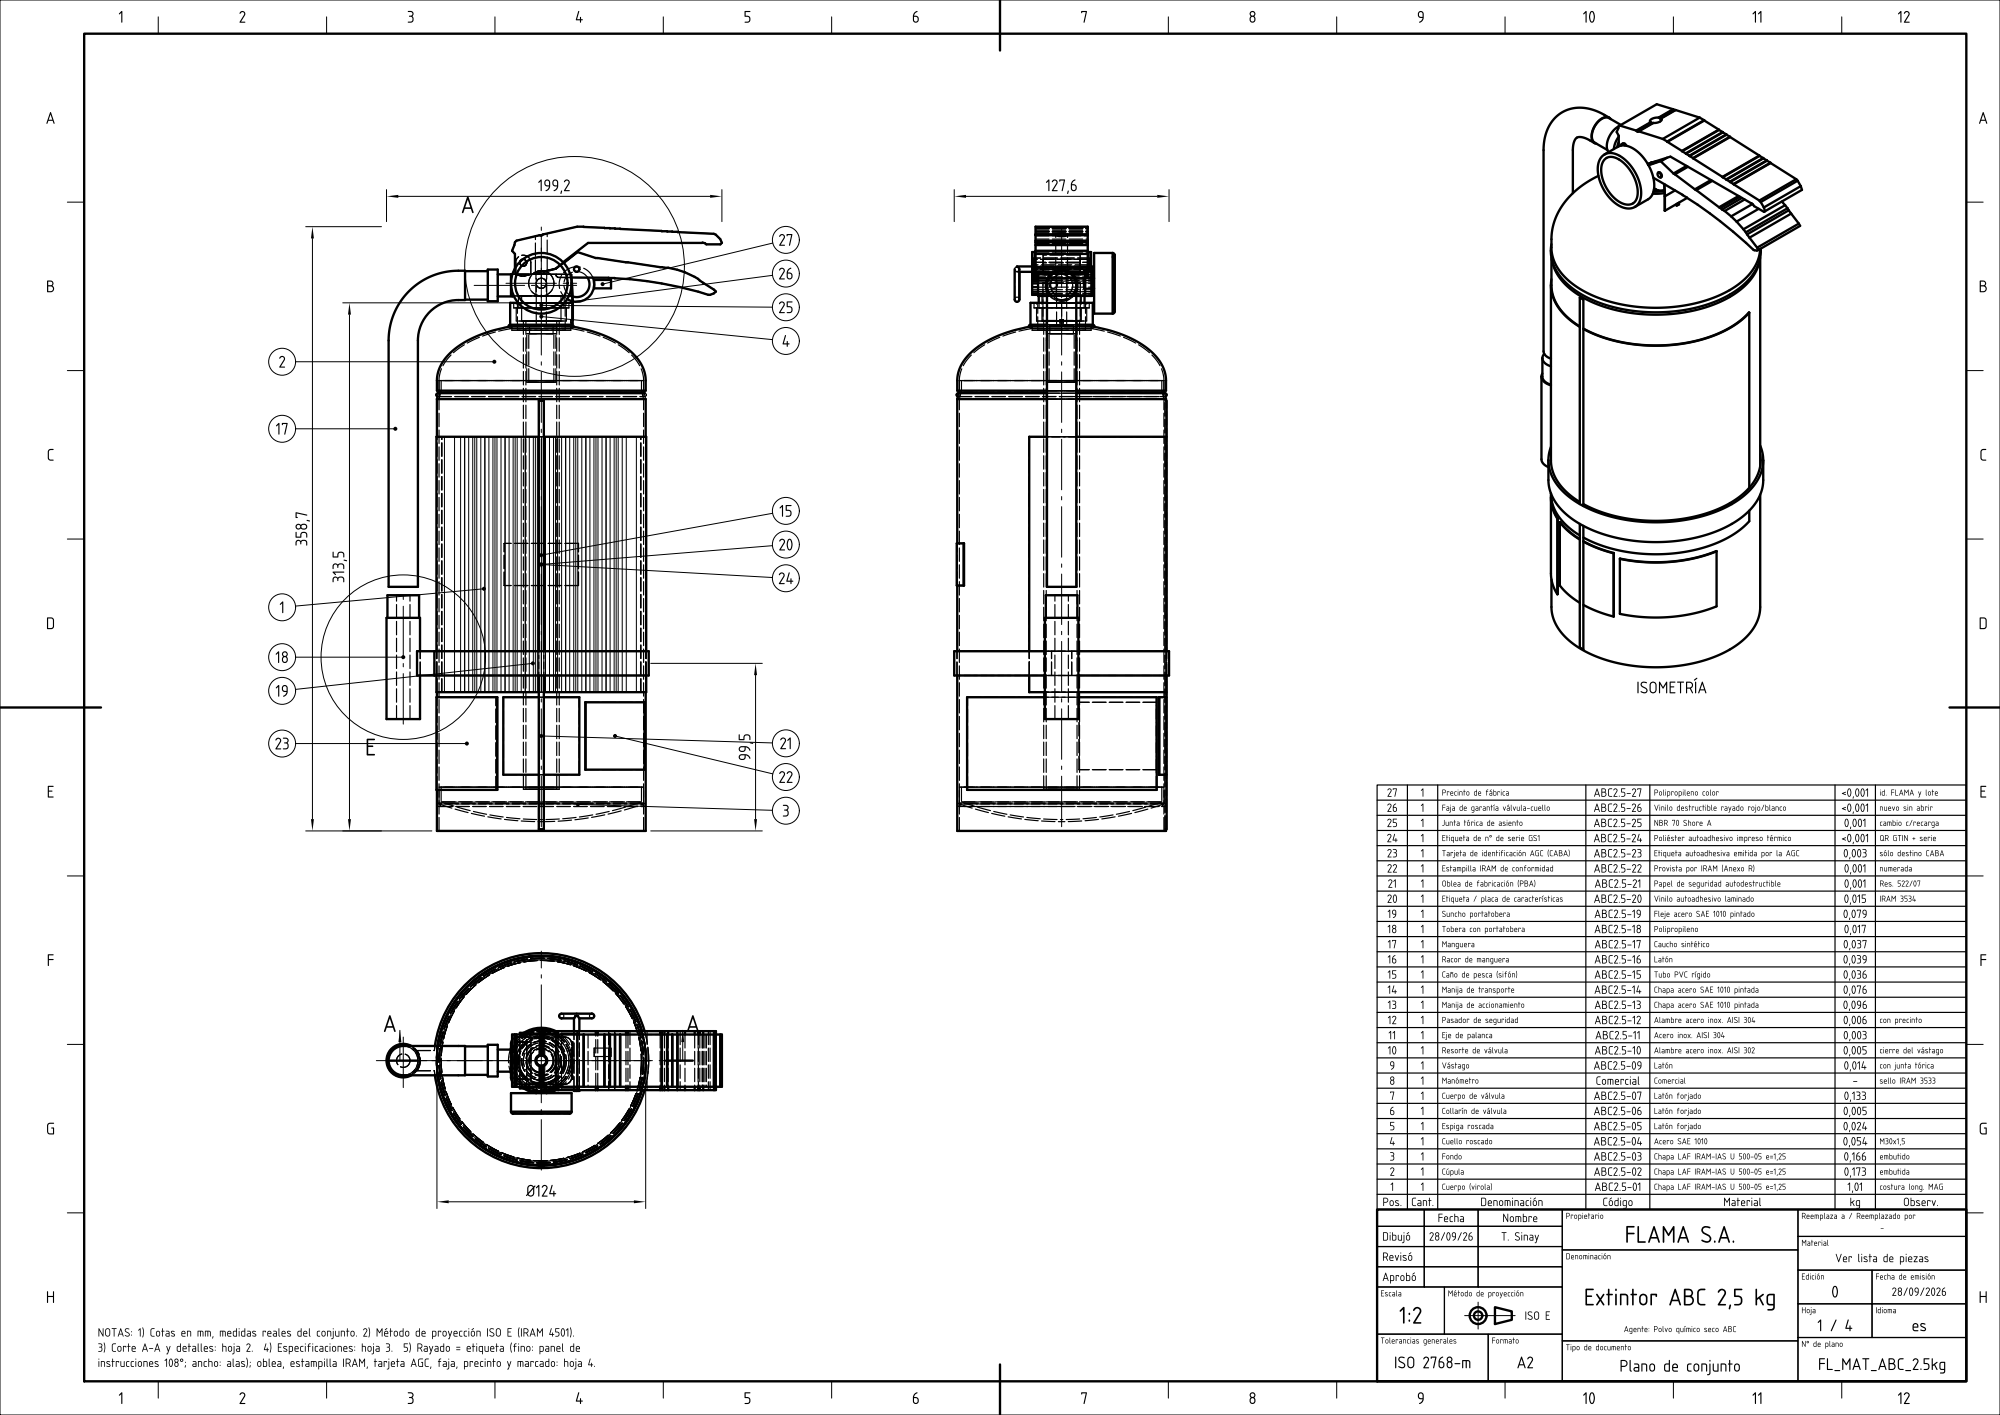
[picture p154: page 1]

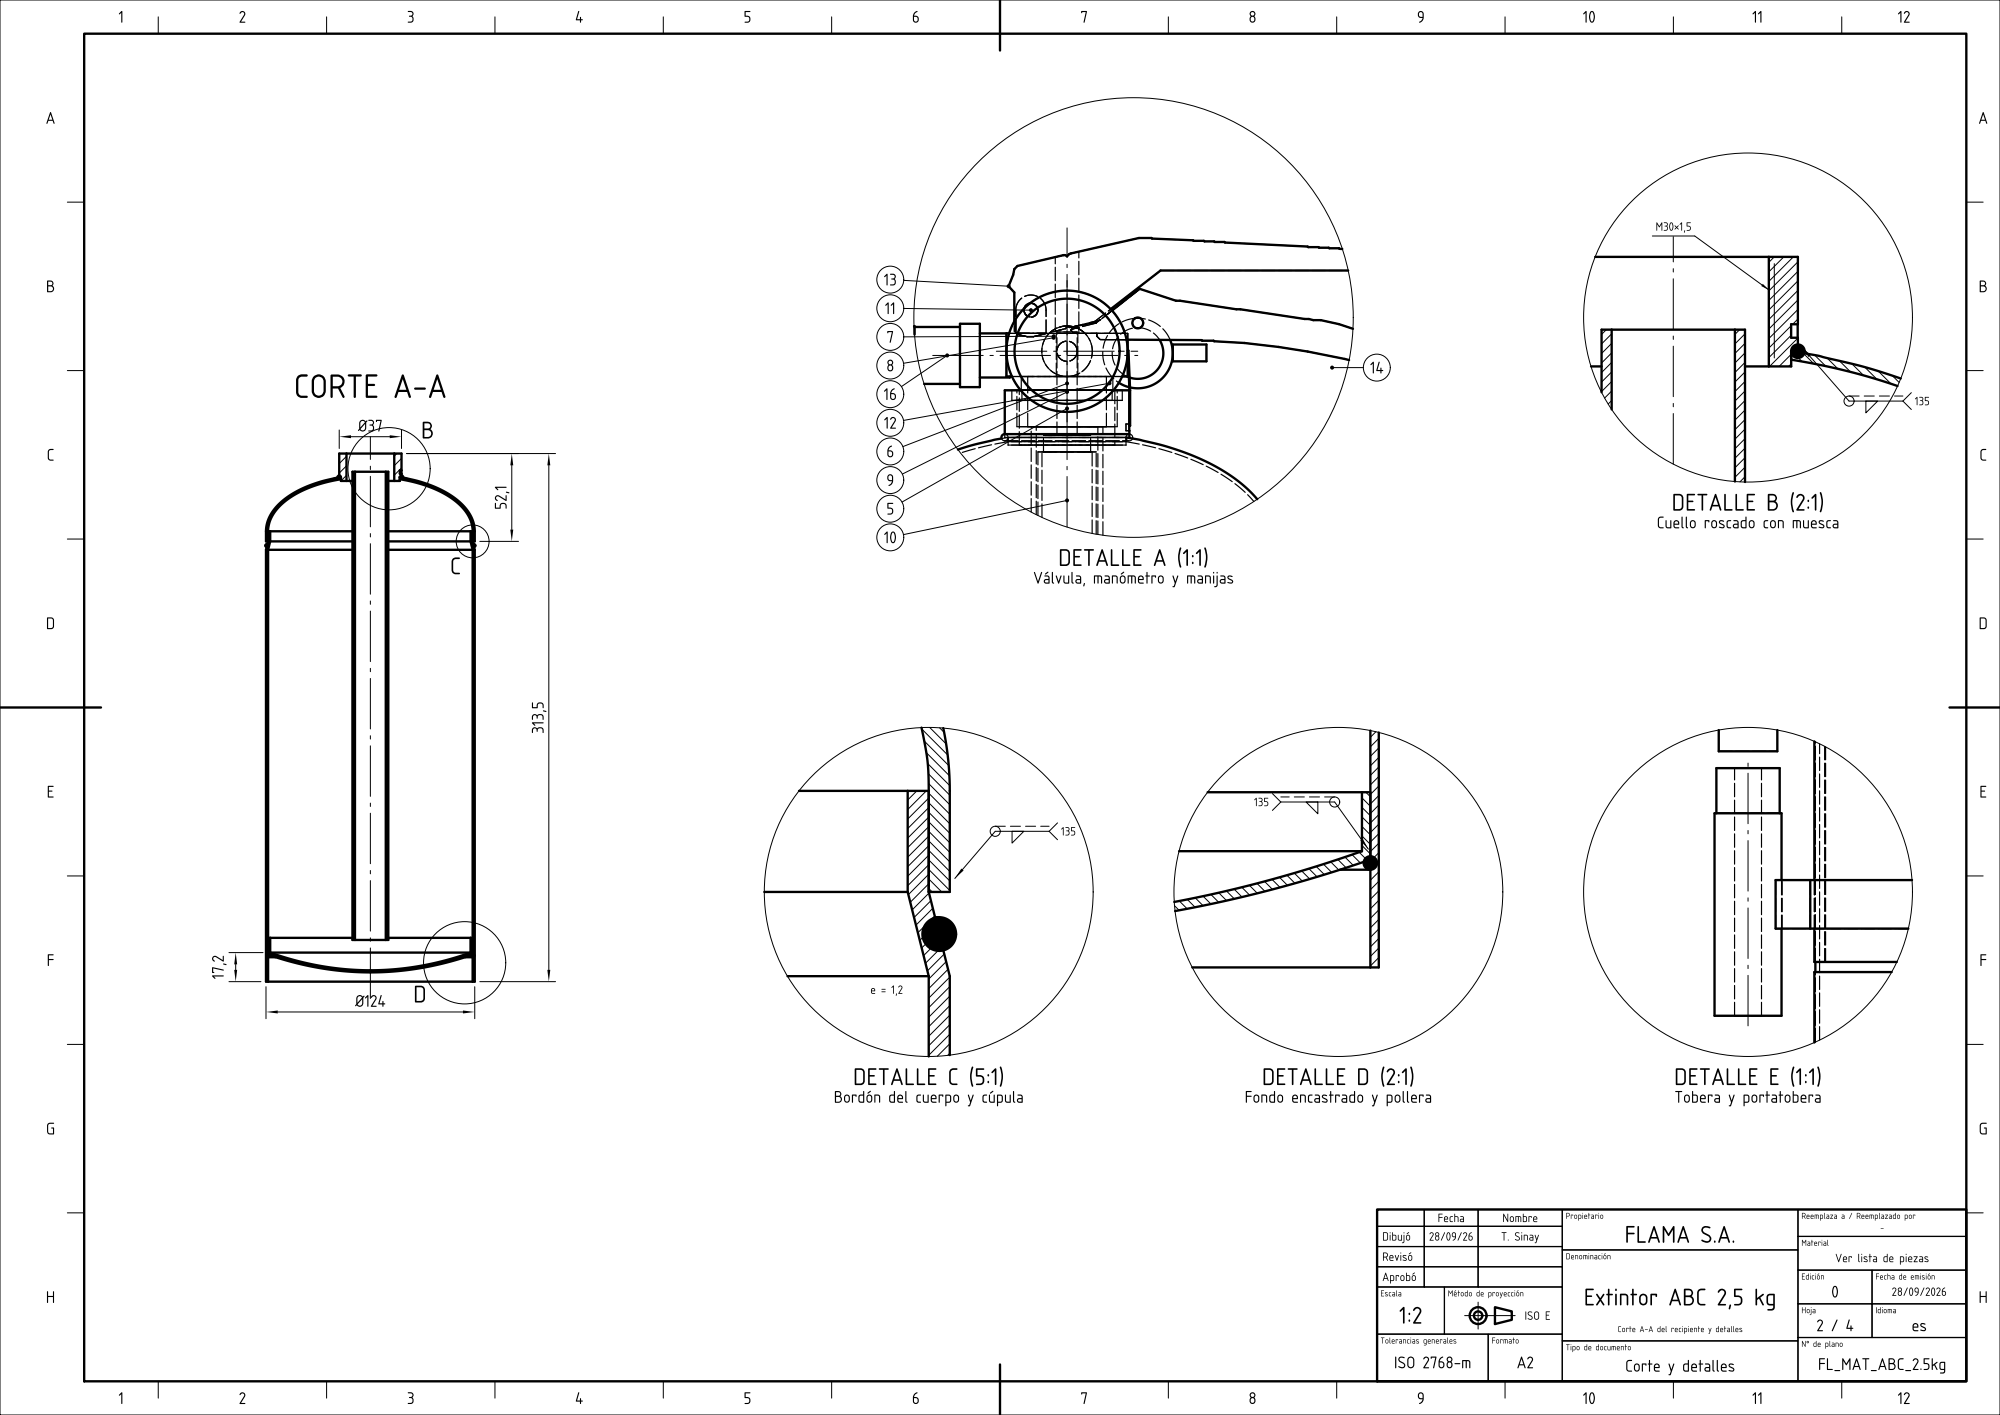
[picture p155: page 2]

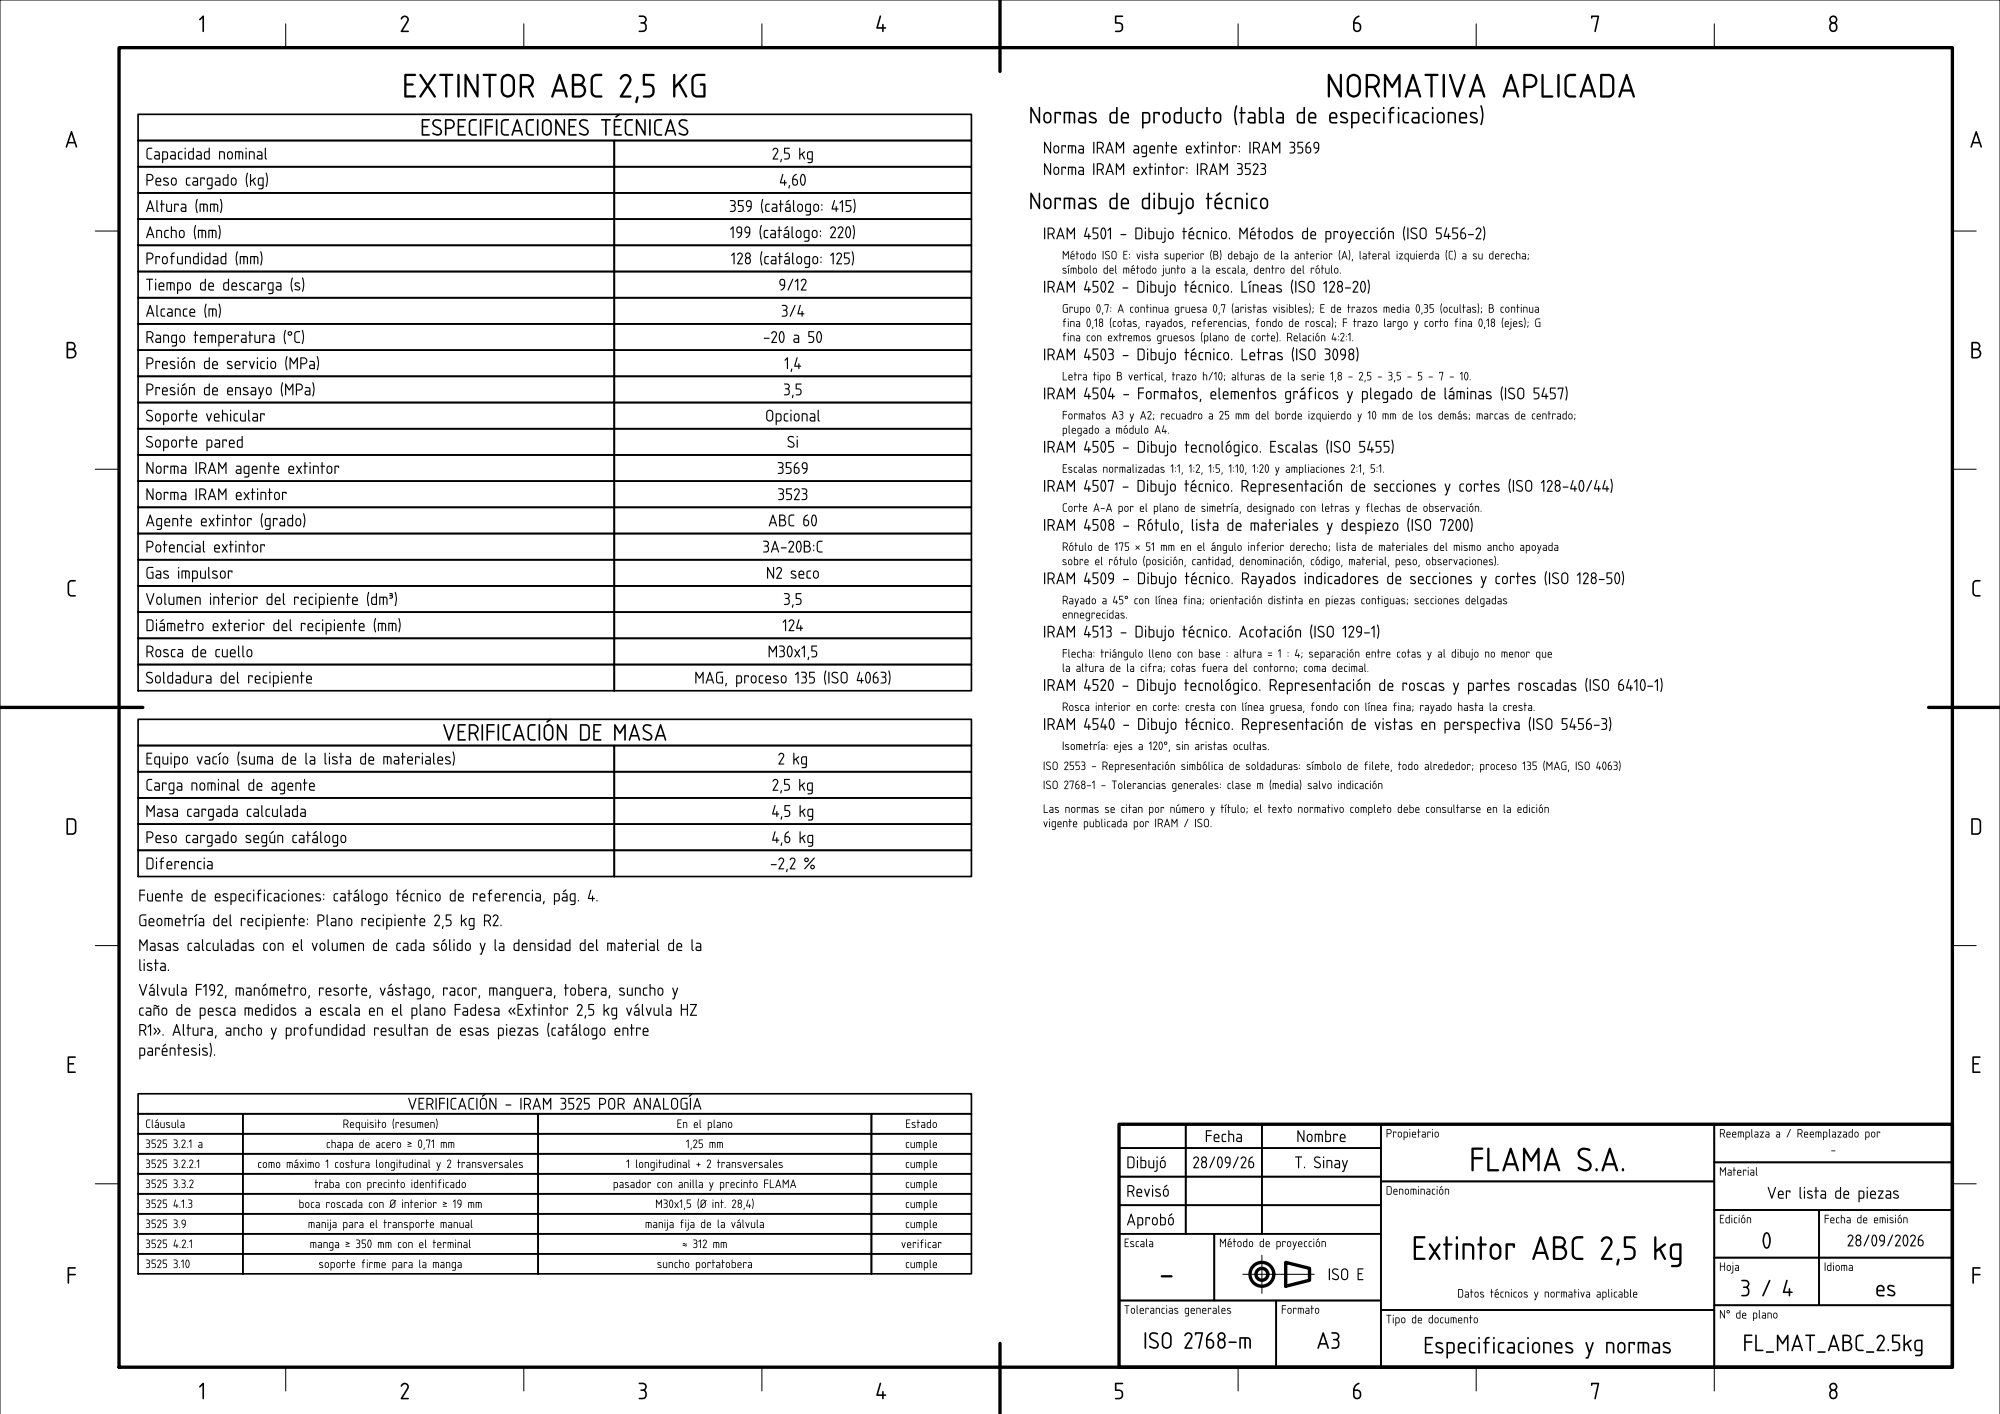
[picture p156: page 3]

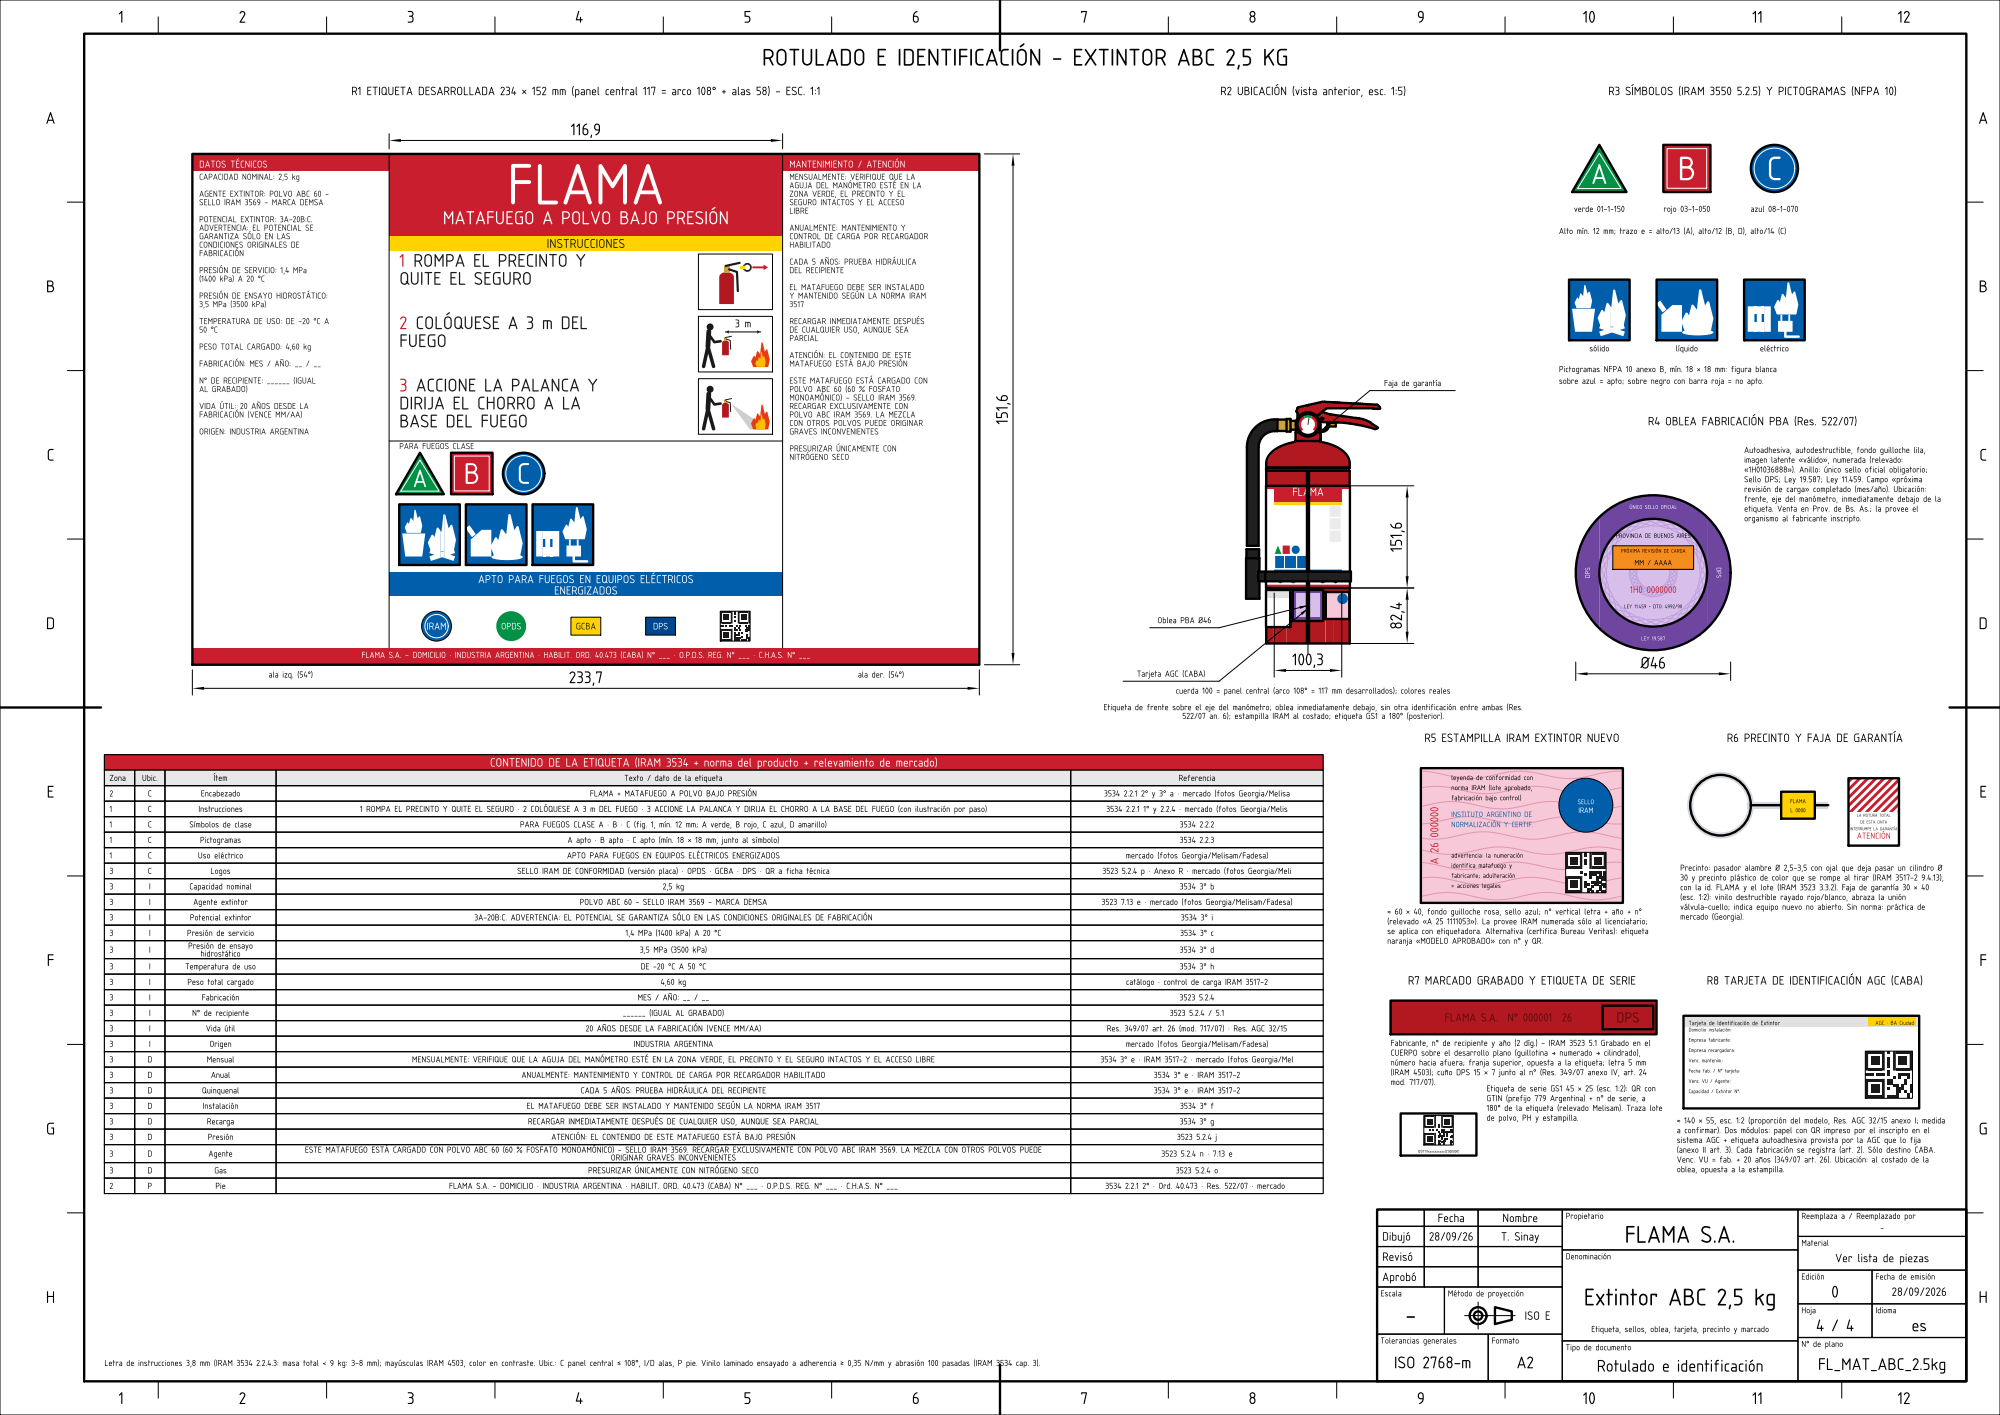
[picture p157: page 4]
