TadeoSinay/planos_flama-/salida/FL_MAT_ABC_25kg/FL_MAT_ABC_25kg.pdf

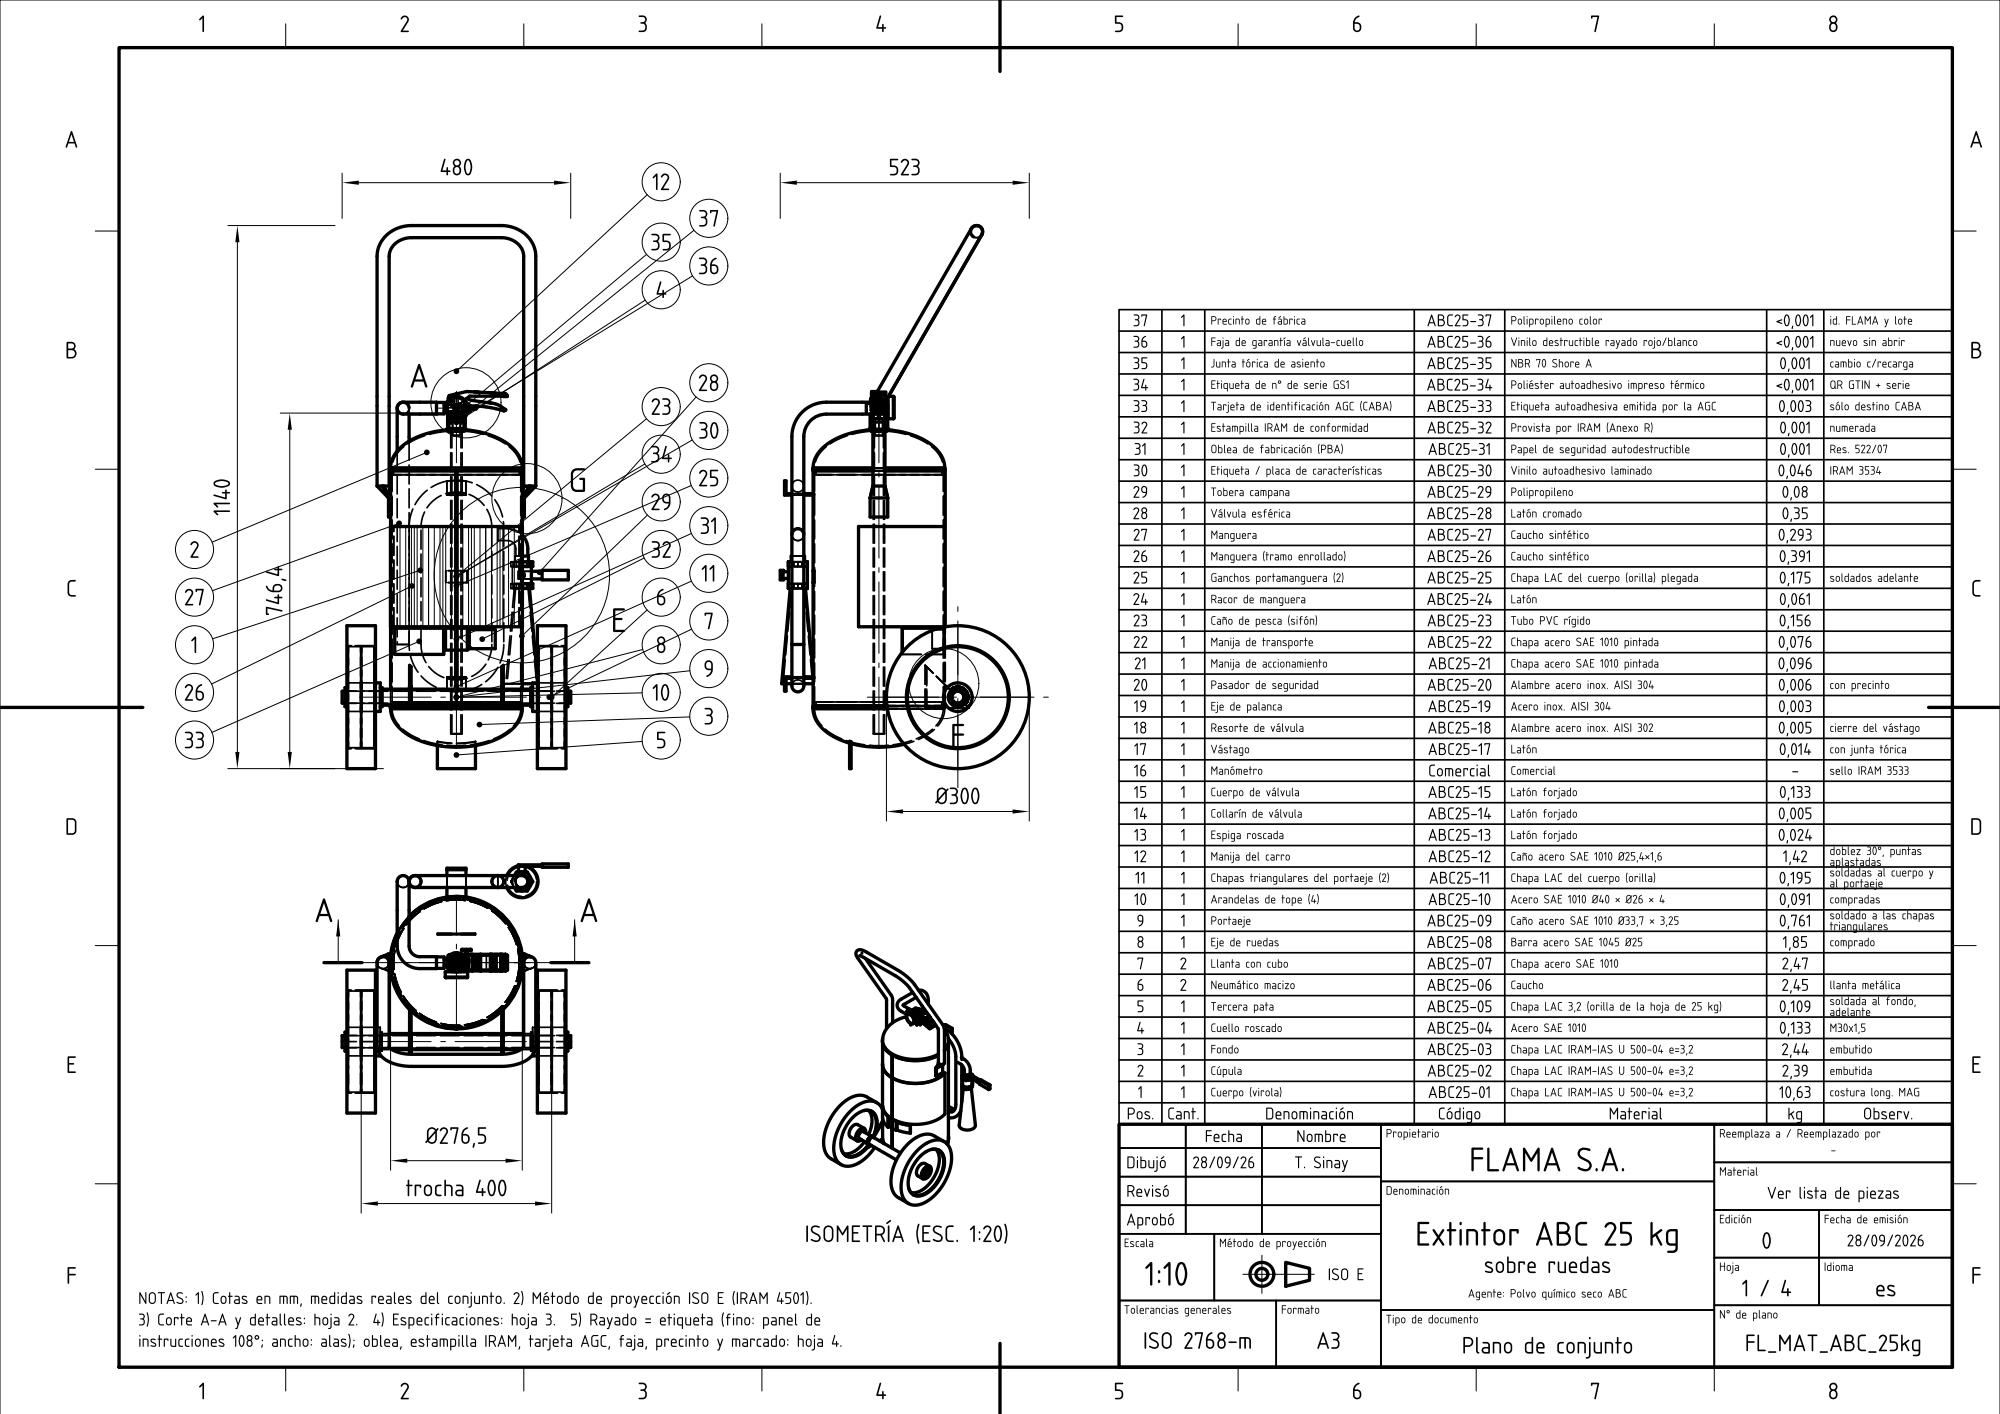
[picture p158: page 1]

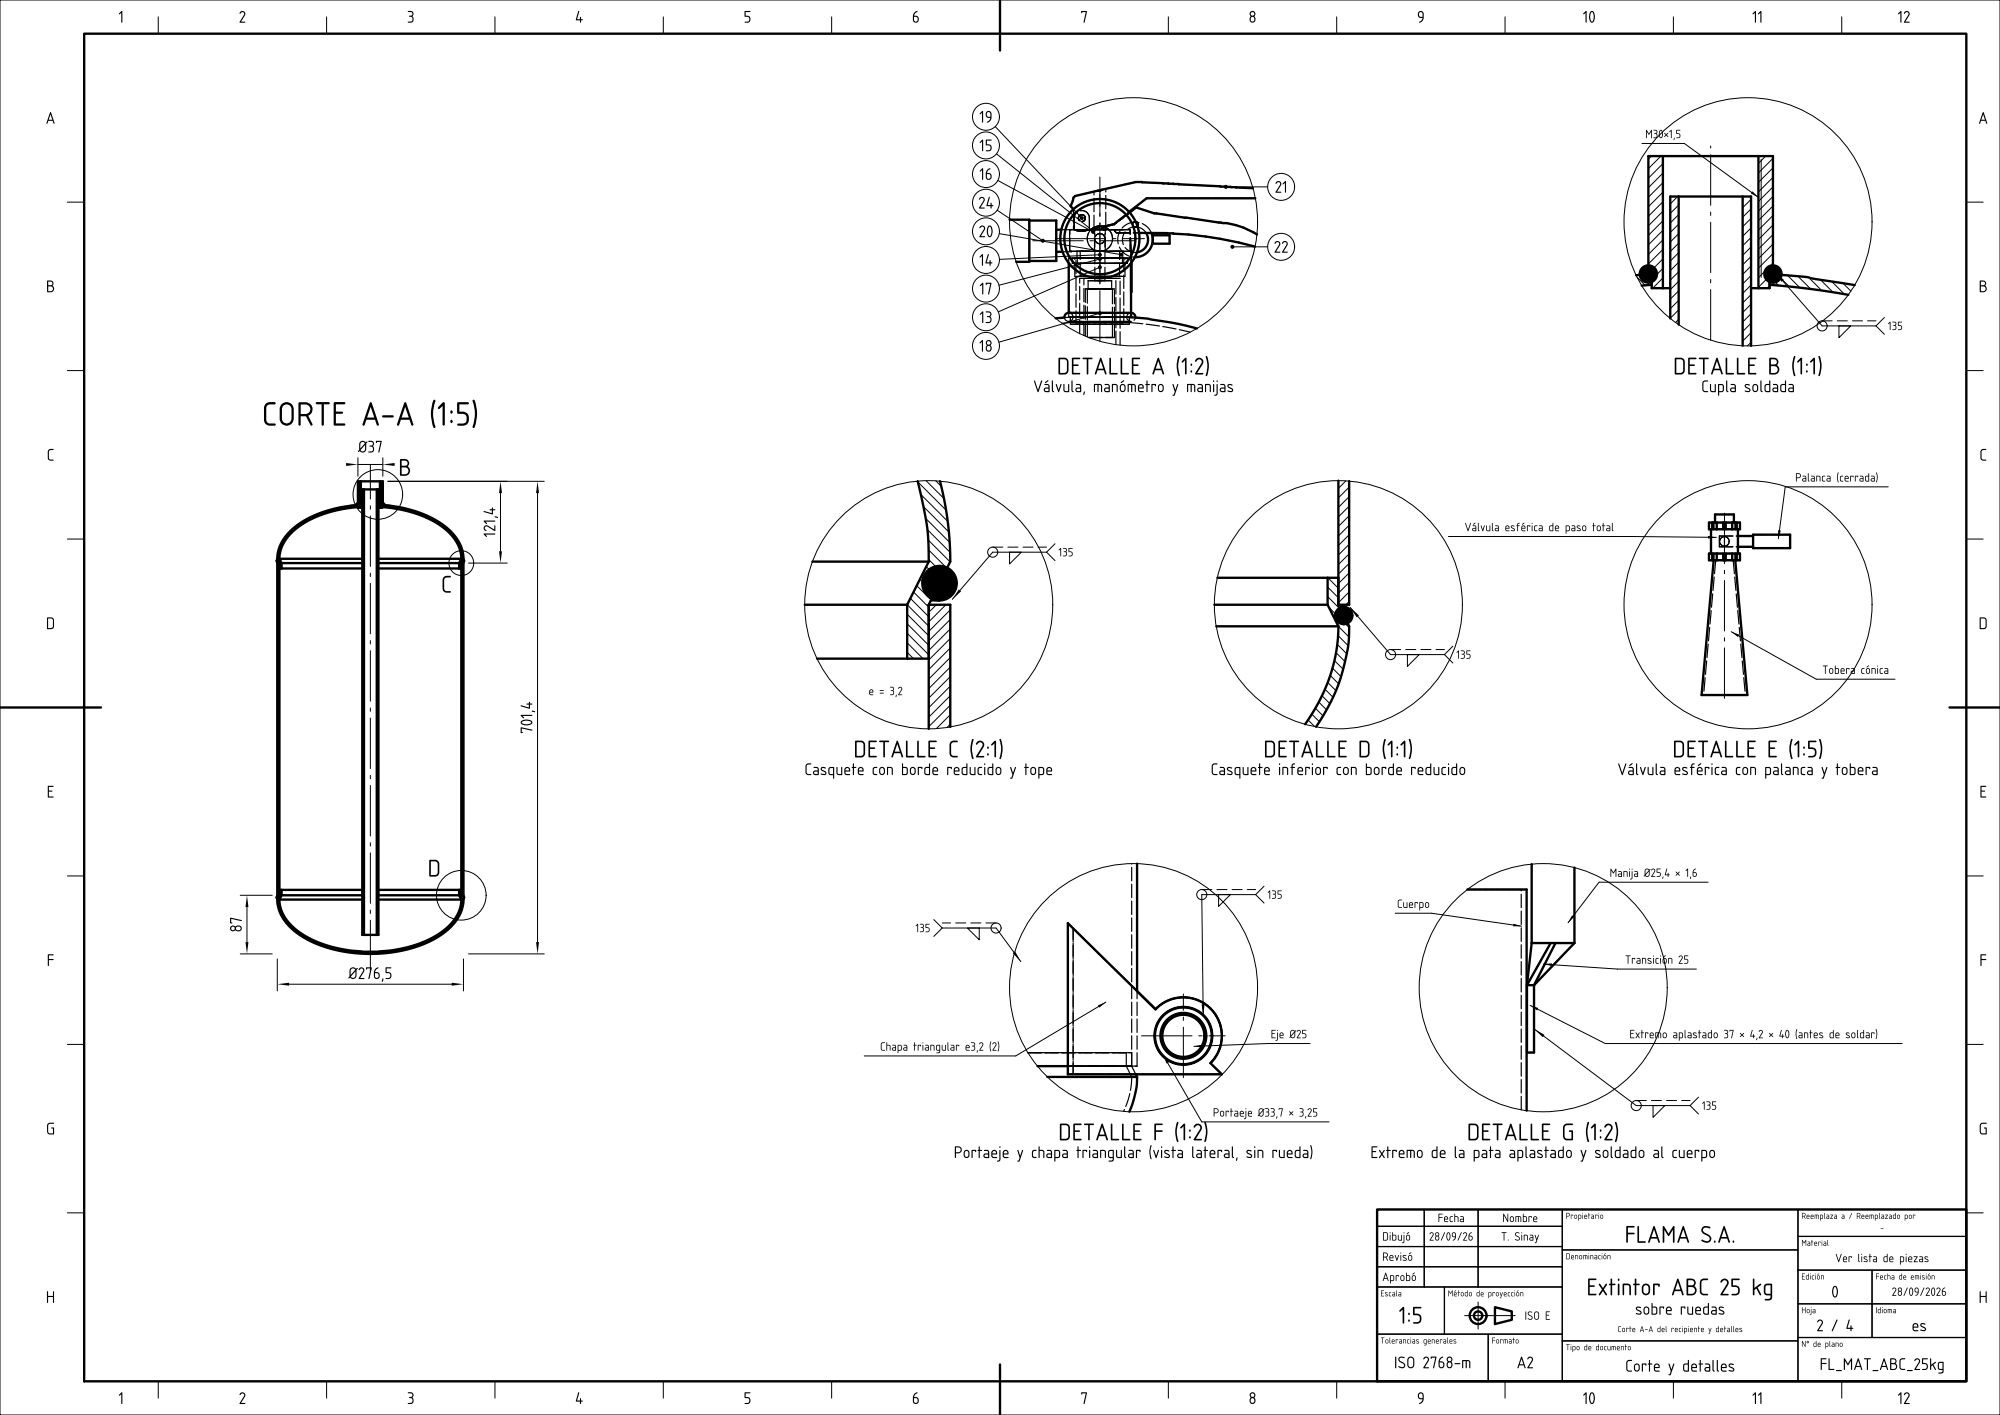
[picture p159: page 2]

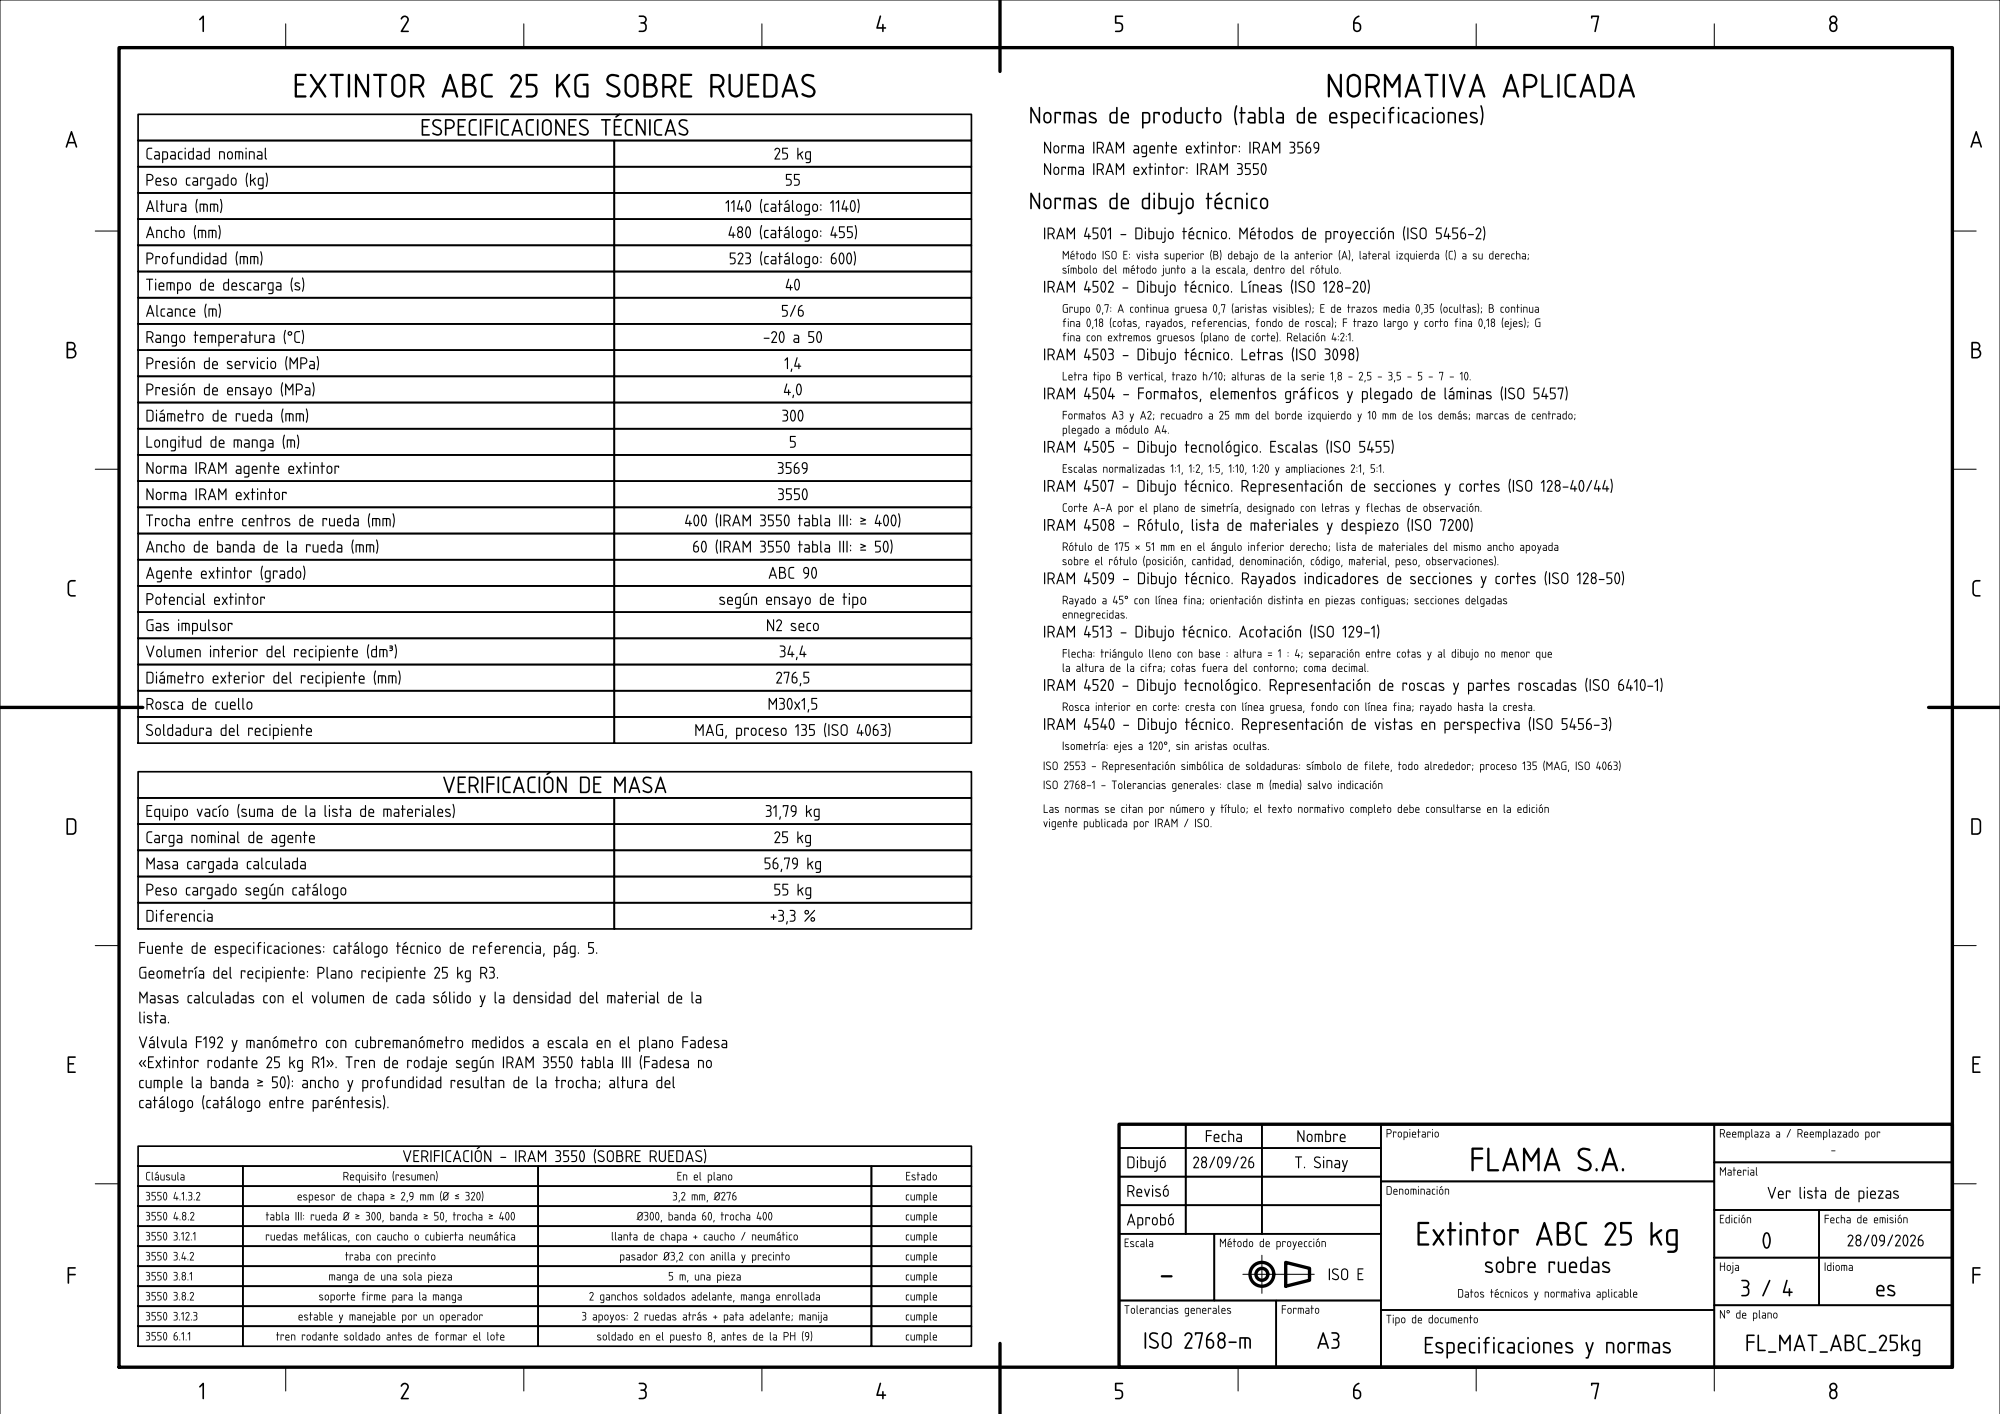
[picture p160: page 3]

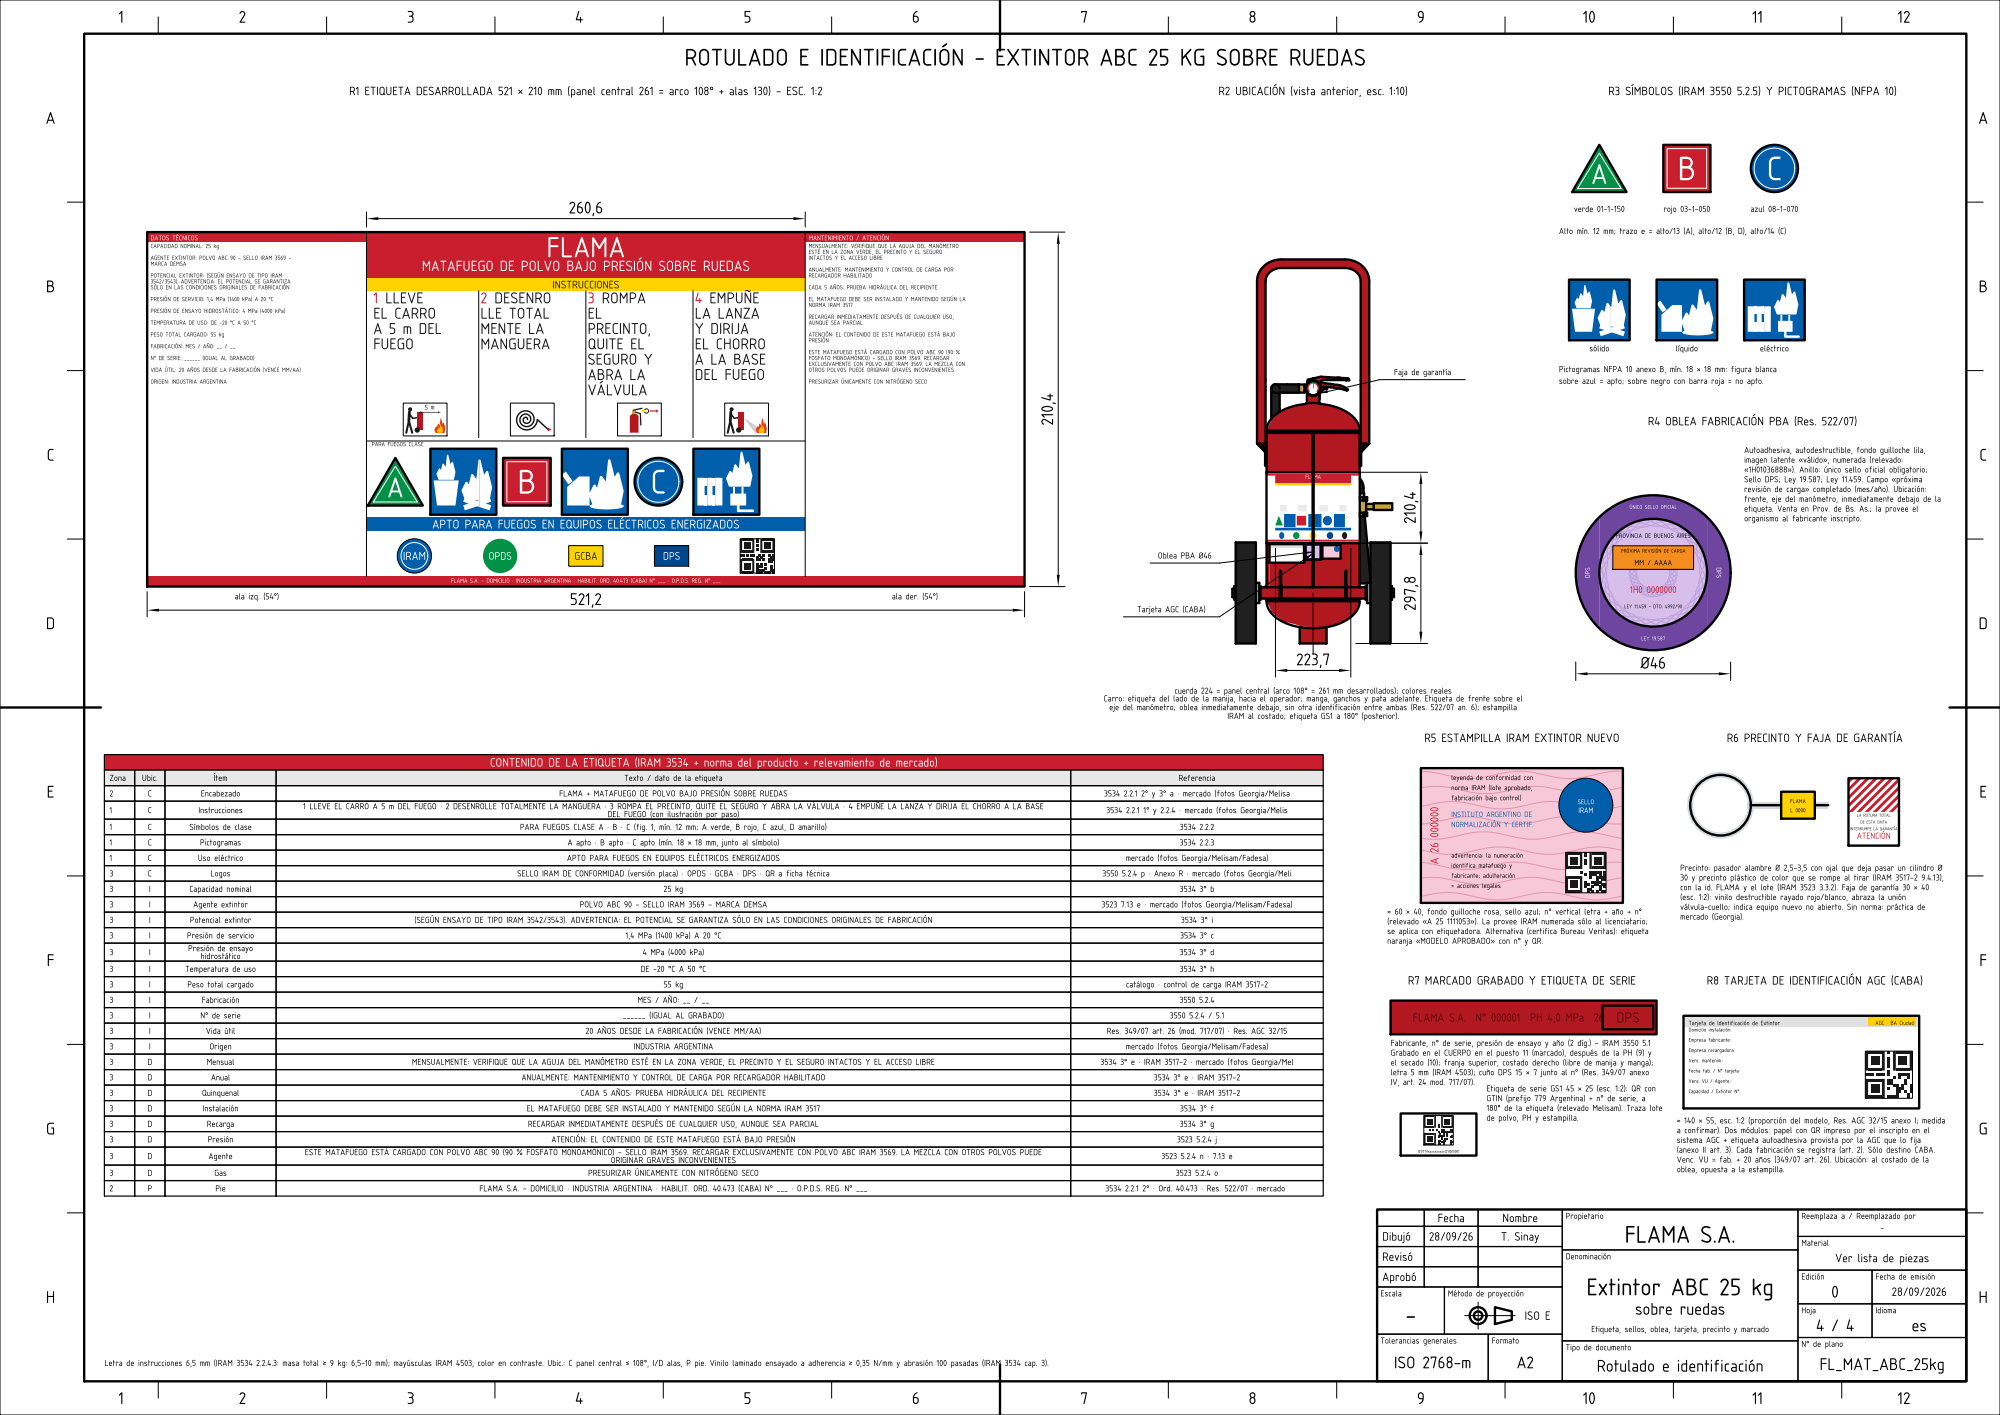
[picture p161: page 4]
