TadeoSinay/planos_flama-/salida/FL_MAT_ABC_50kg/FL_MAT_ABC_50kg.pdf

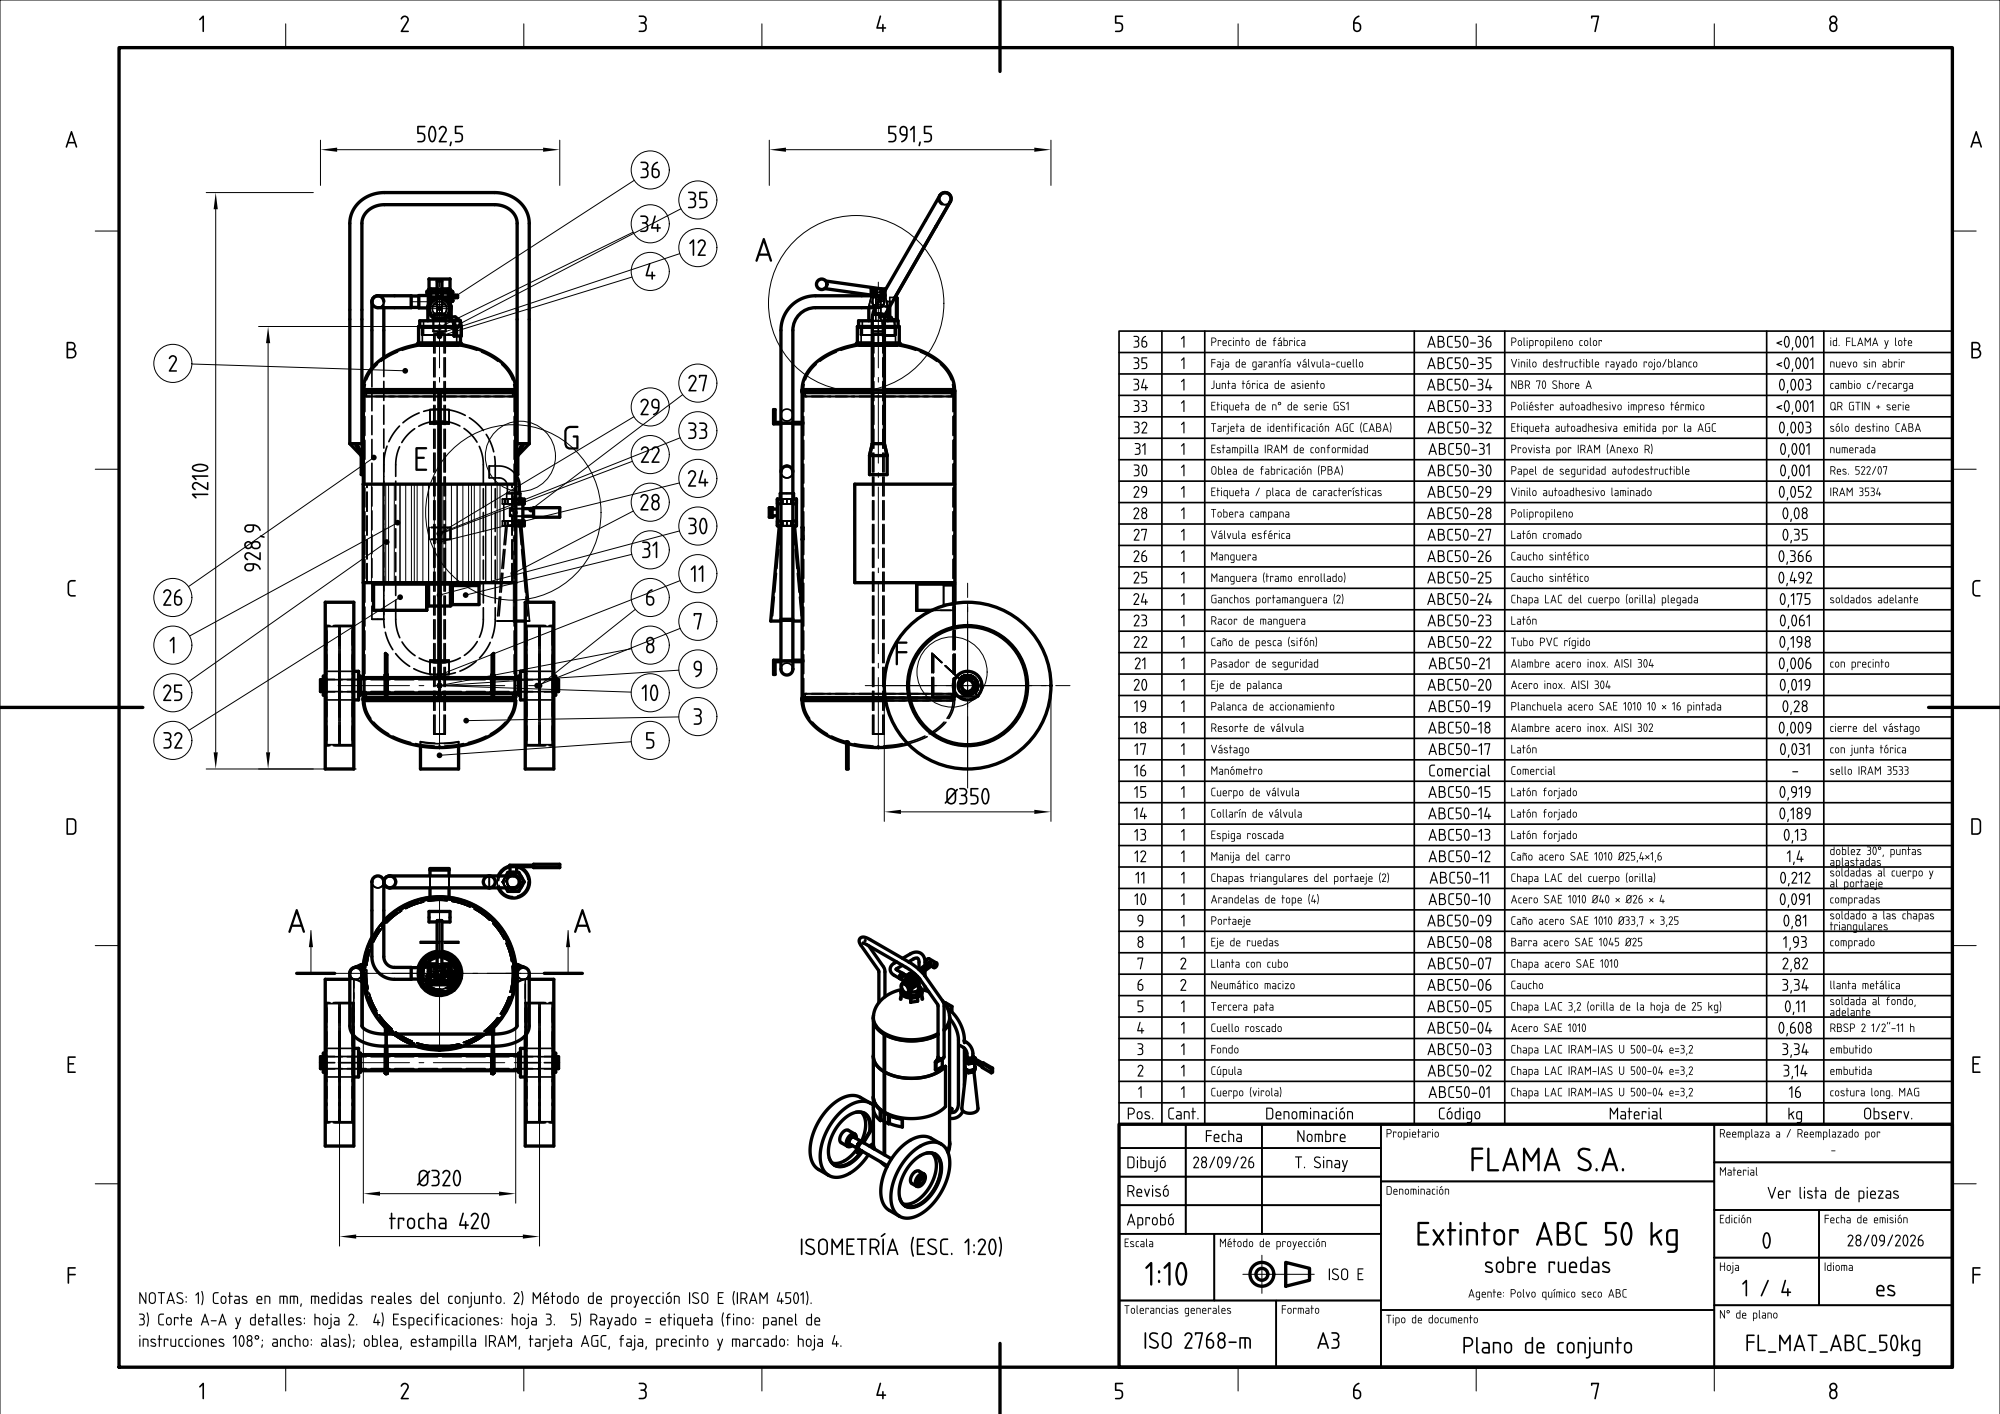
[picture p162: page 1]

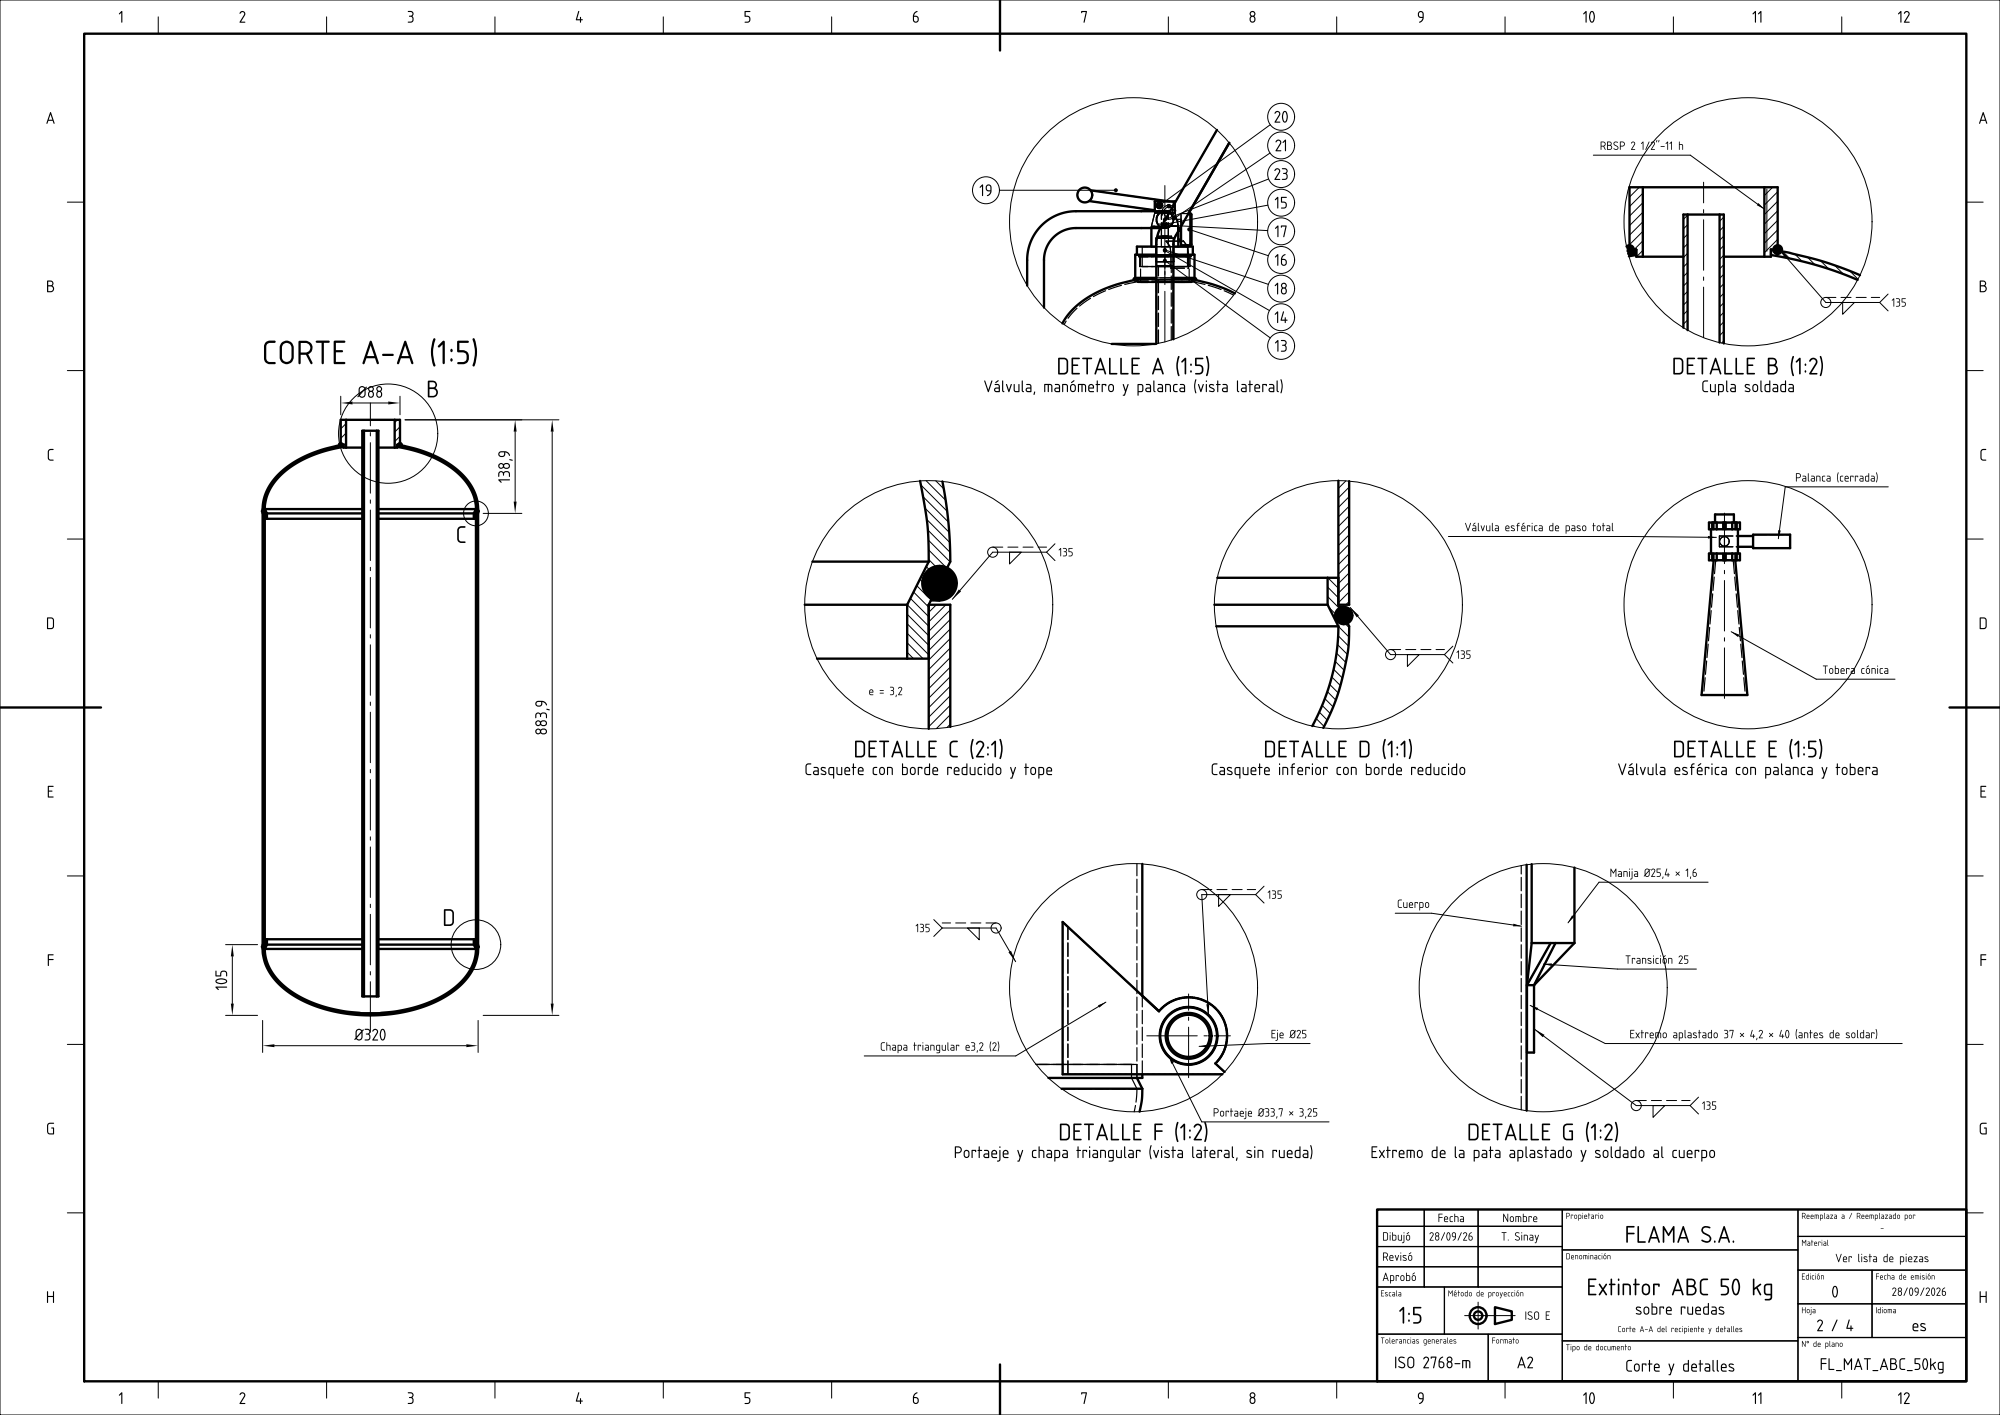
[picture p163: page 2]

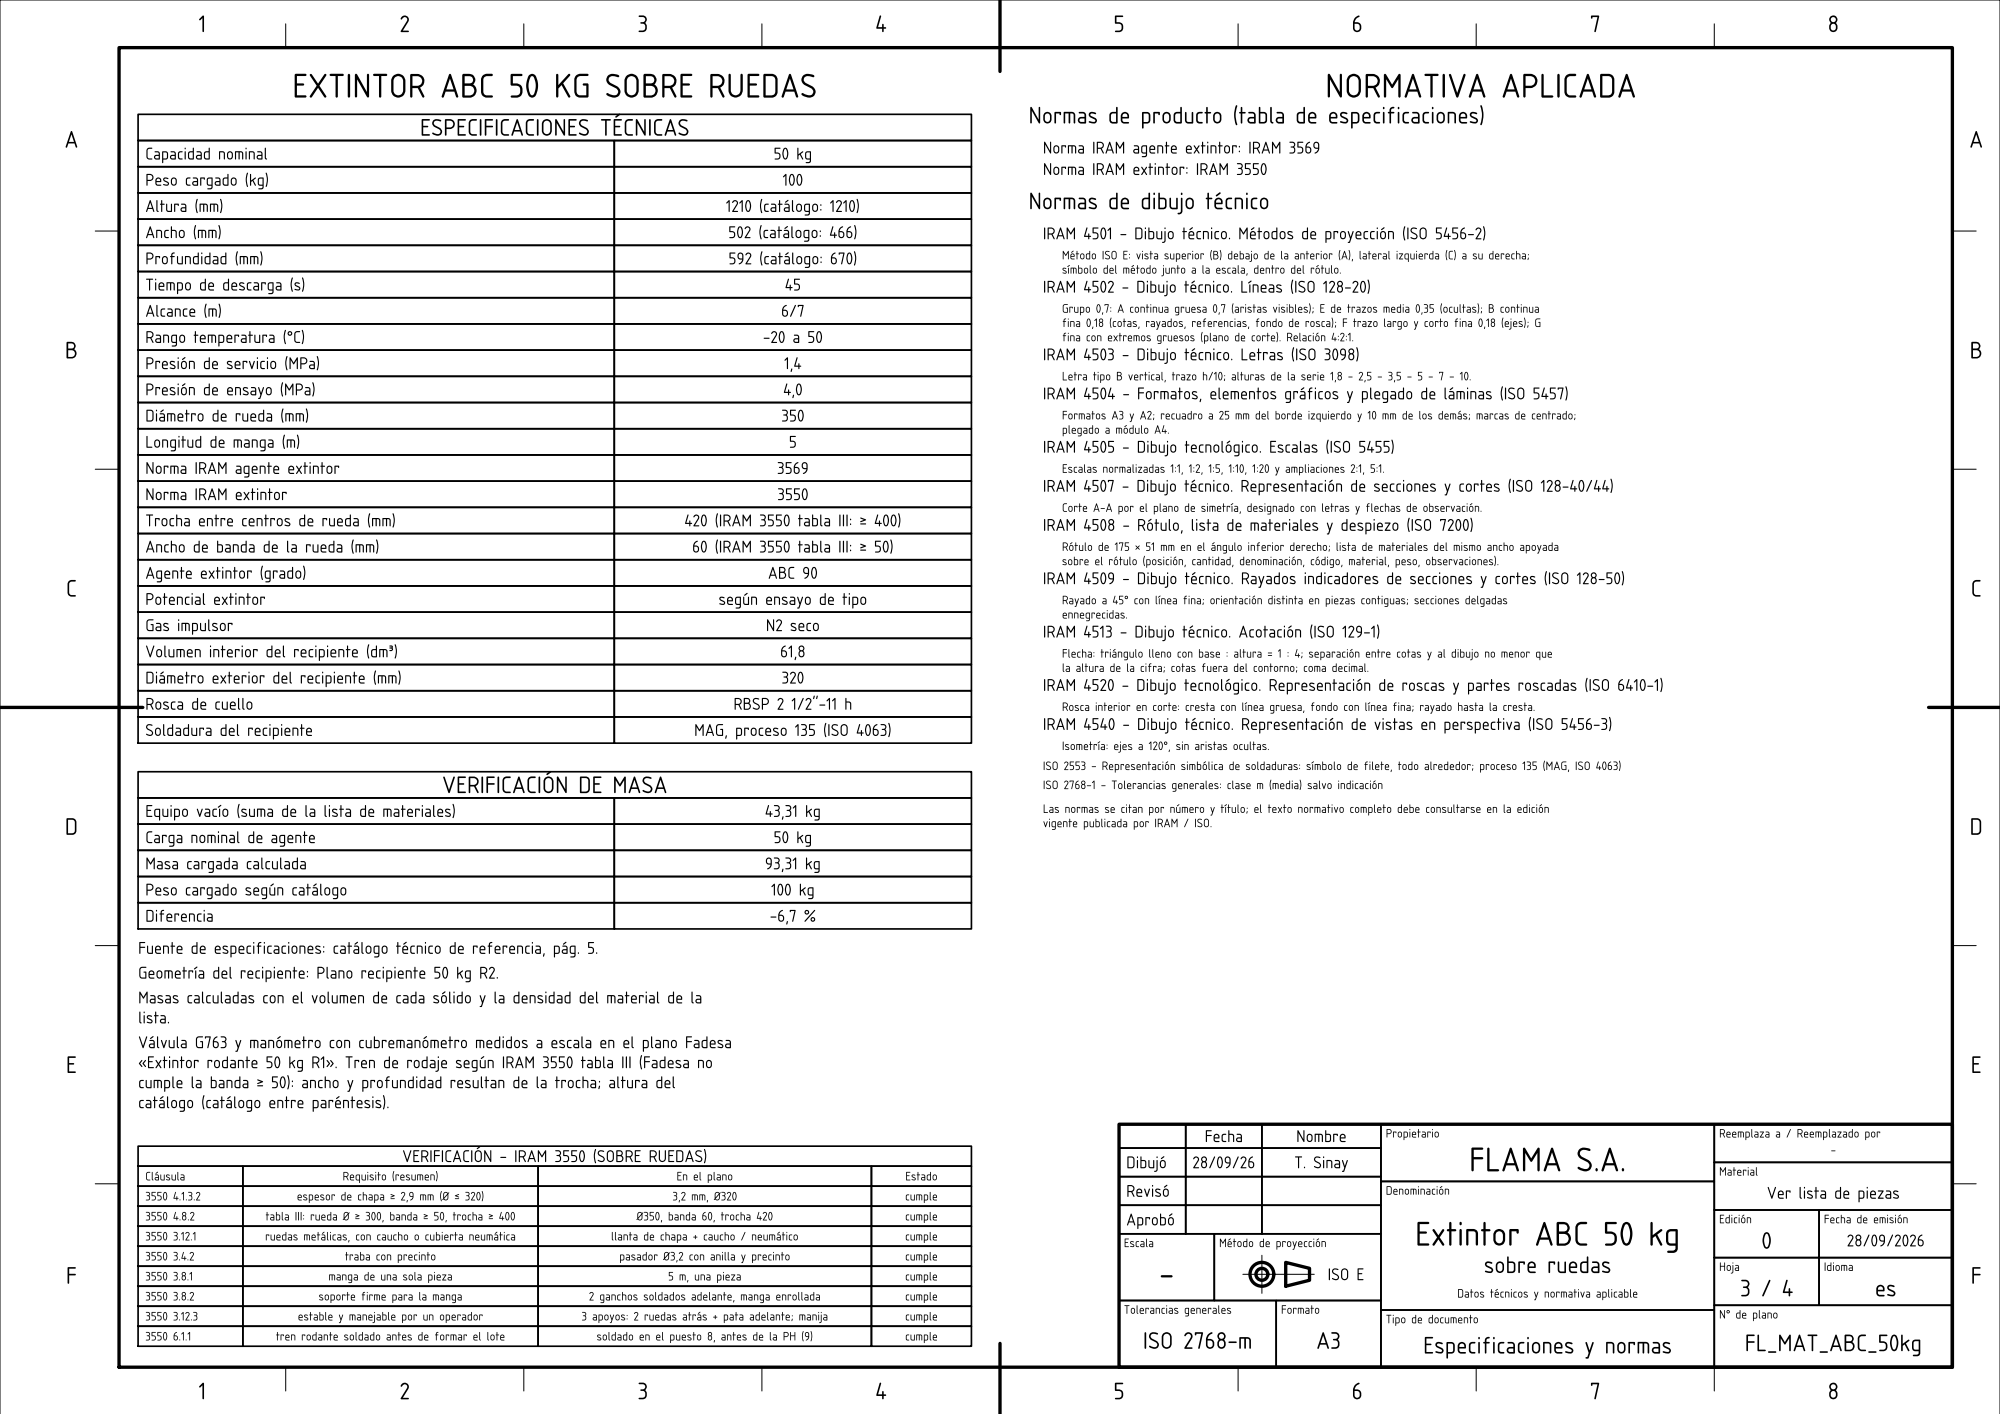
[picture p164: page 3]

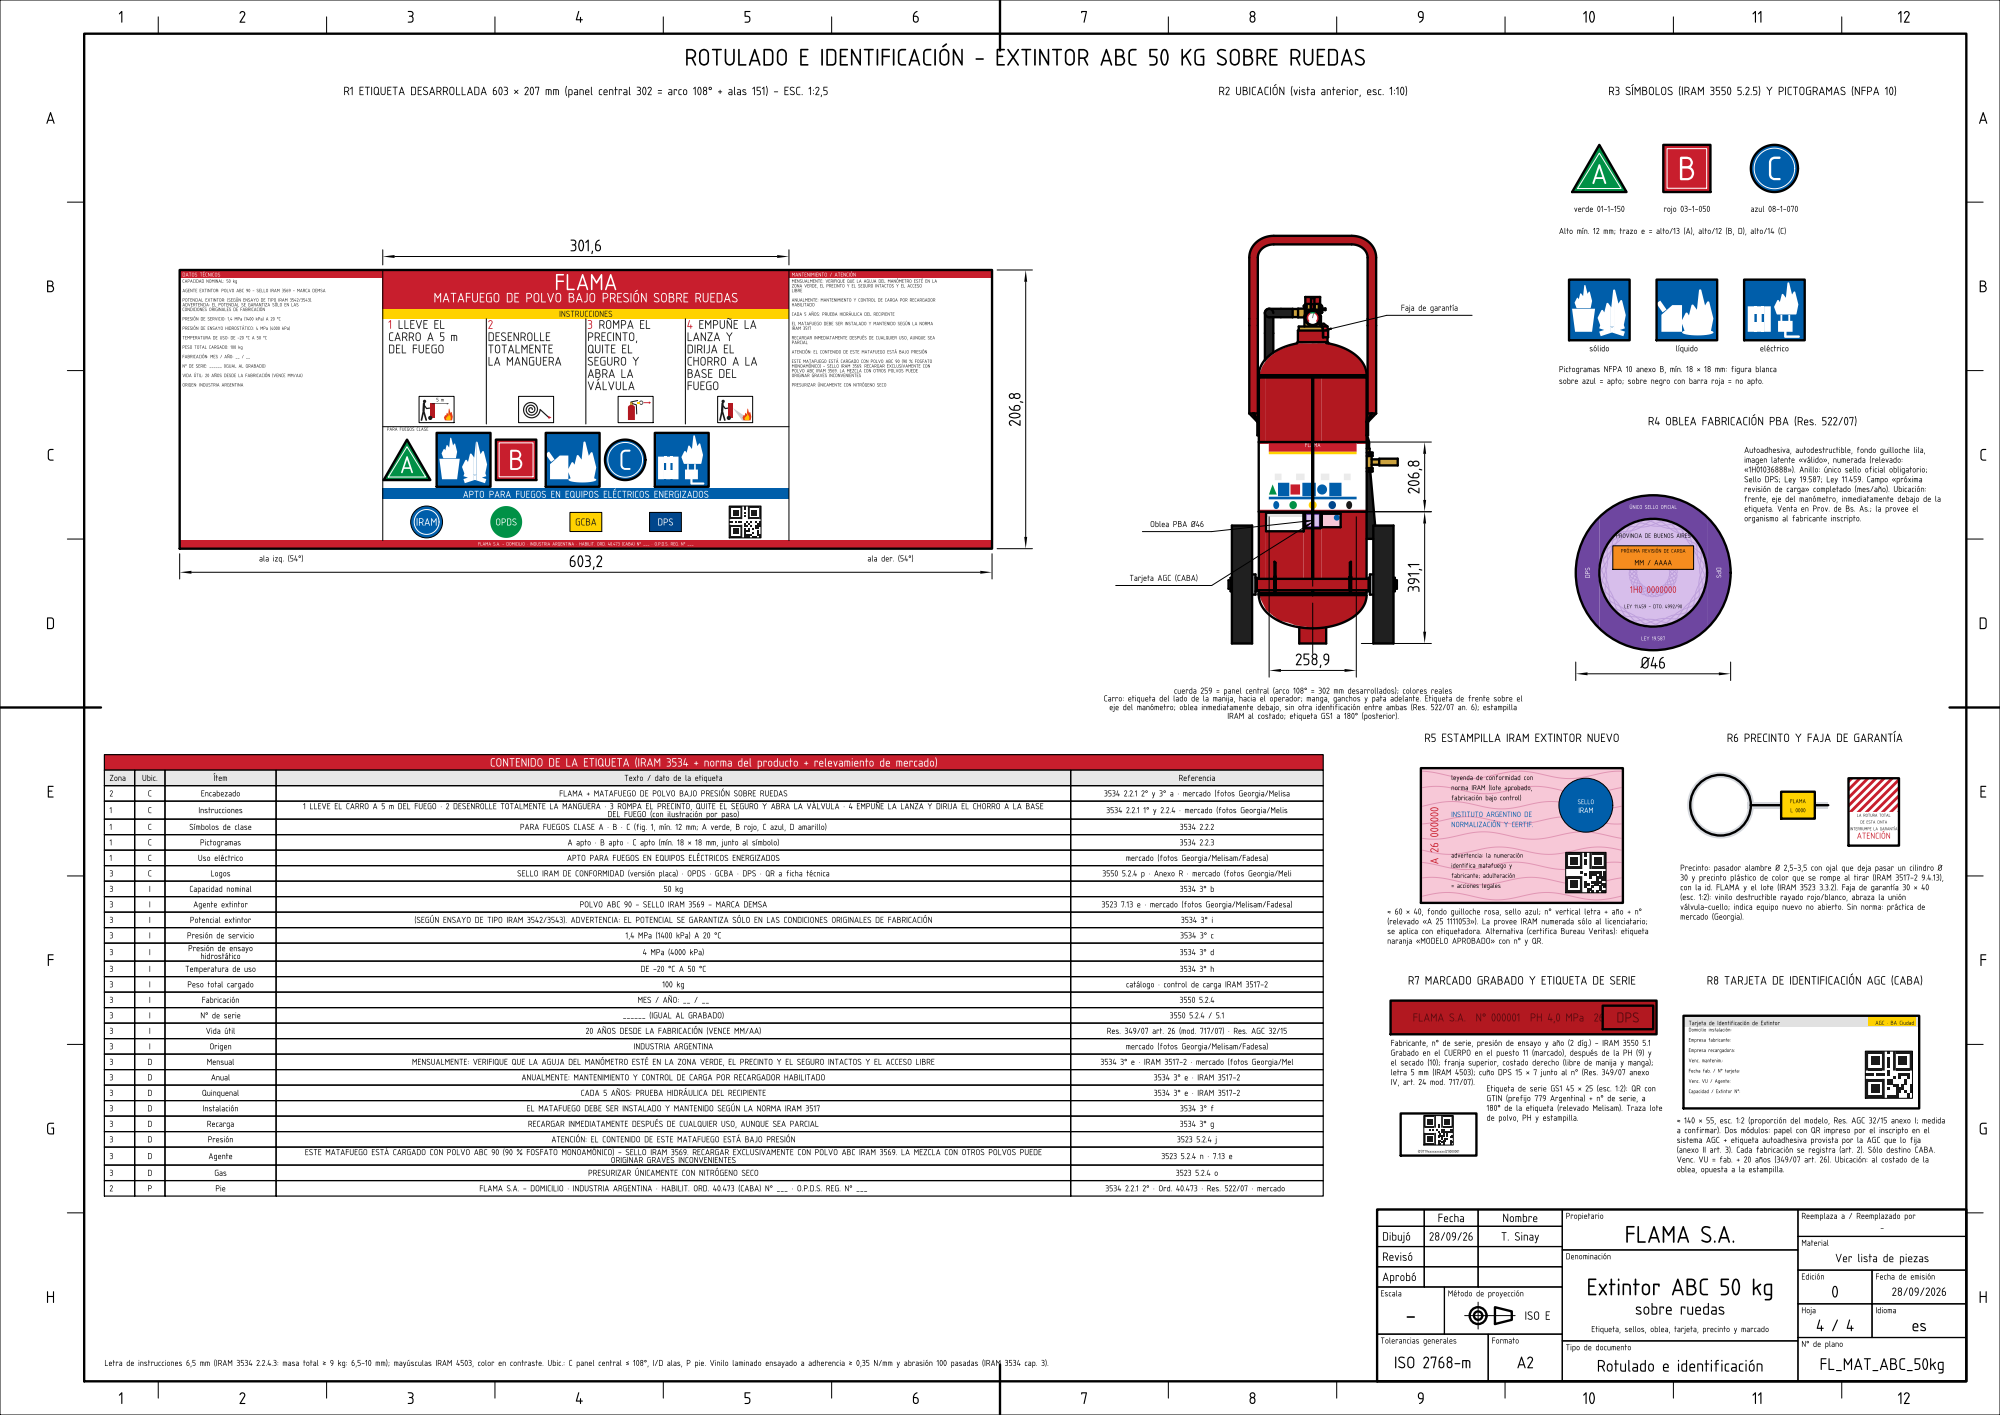
[picture p165: page 4]
