TadeoSinay/planos_flama-/salida/FL_MAT_ABC_5kg/FL_MAT_ABC_5kg.pdf

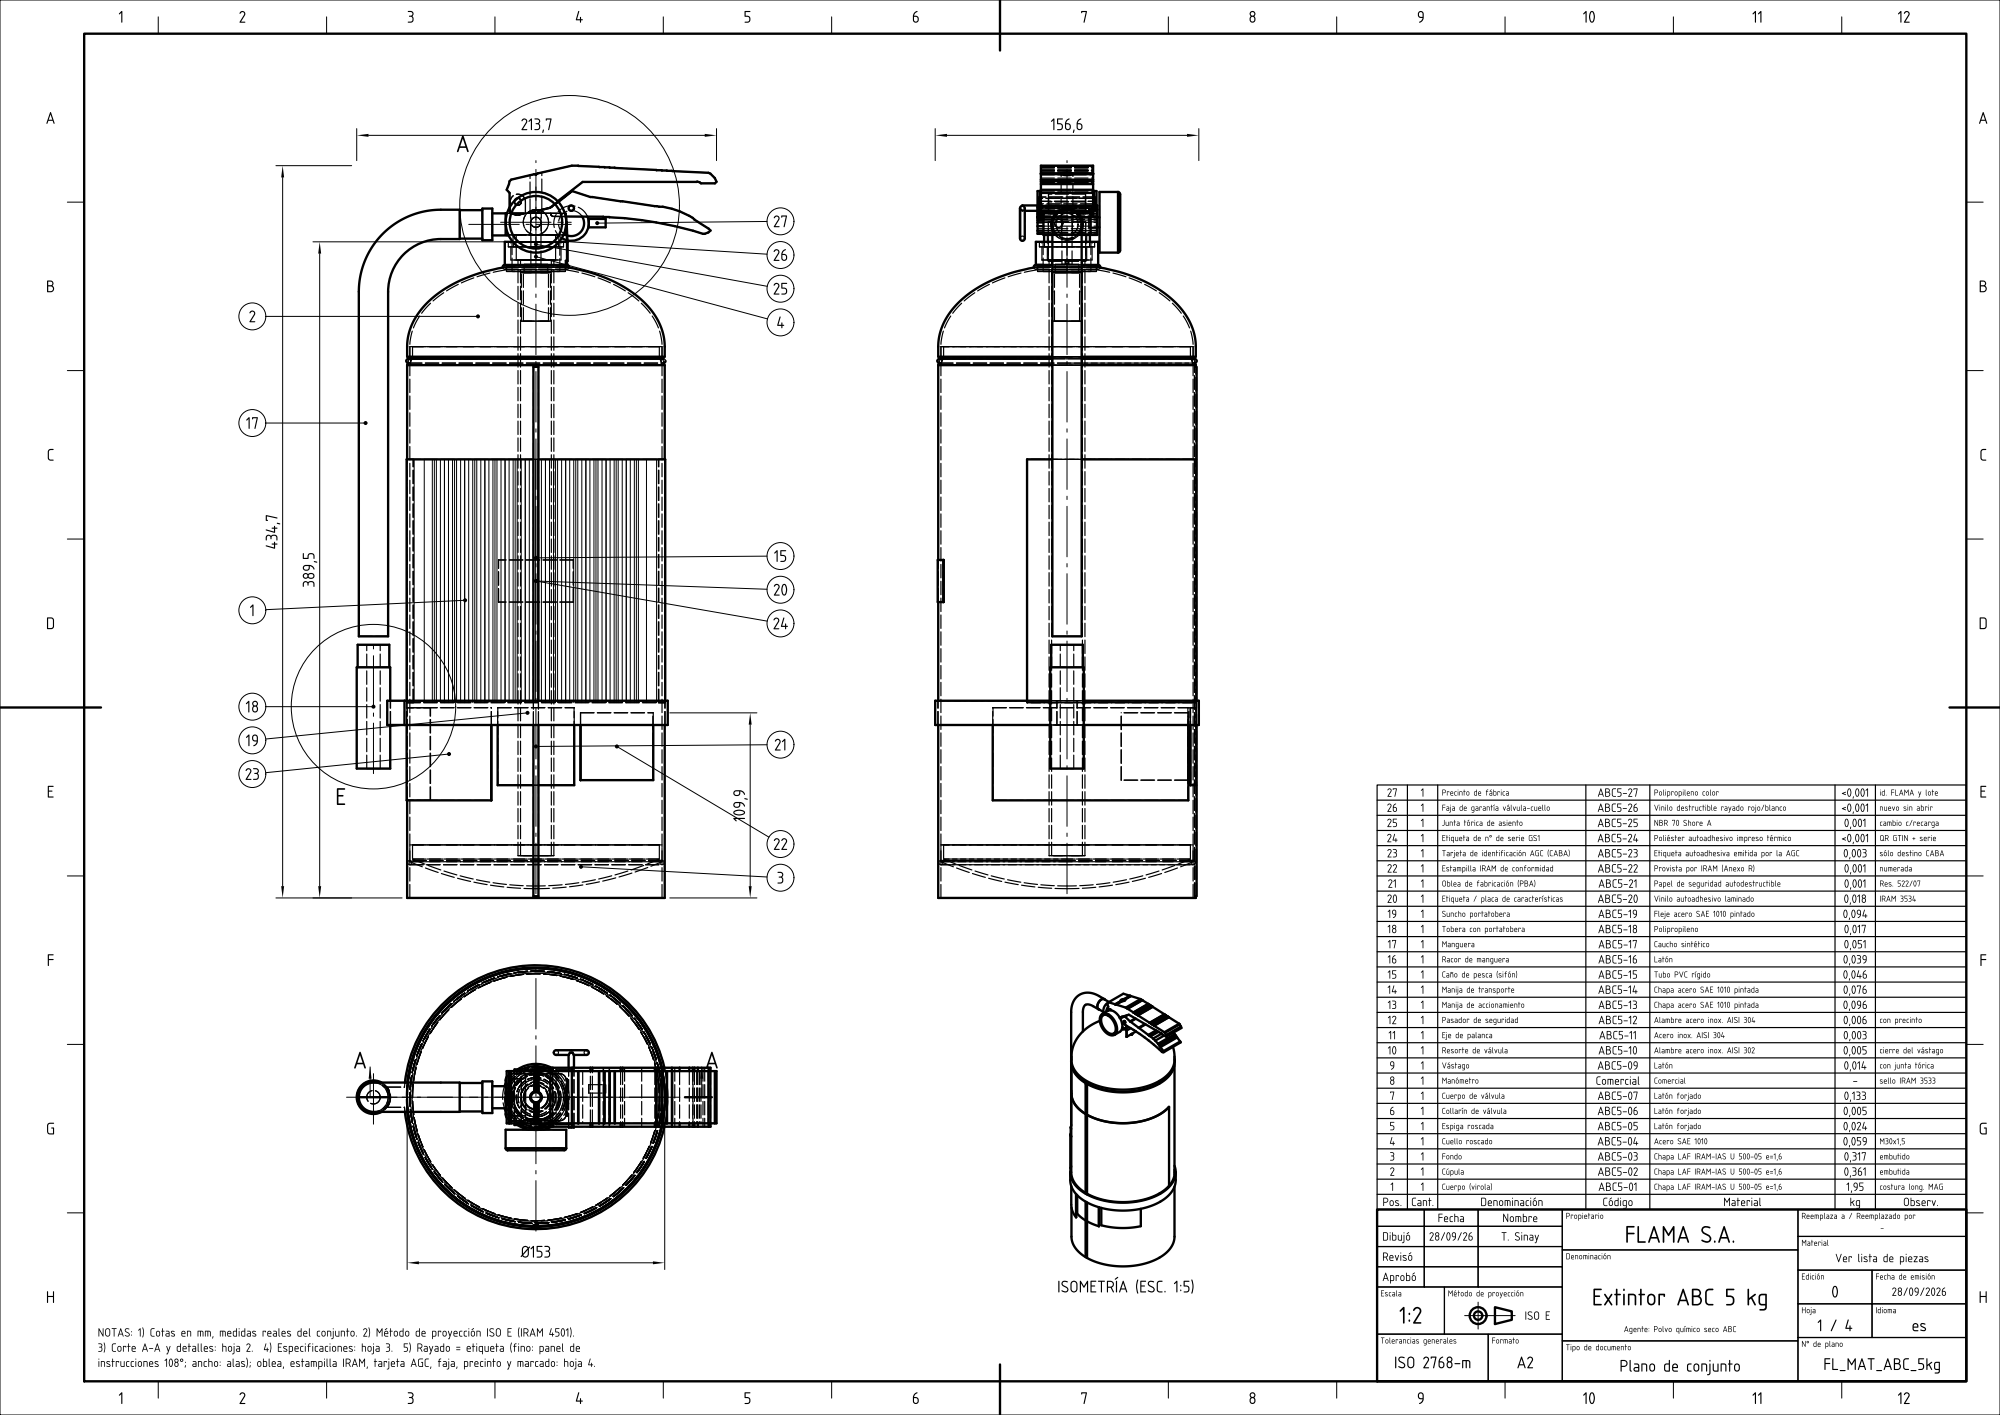
[picture p166: page 1]

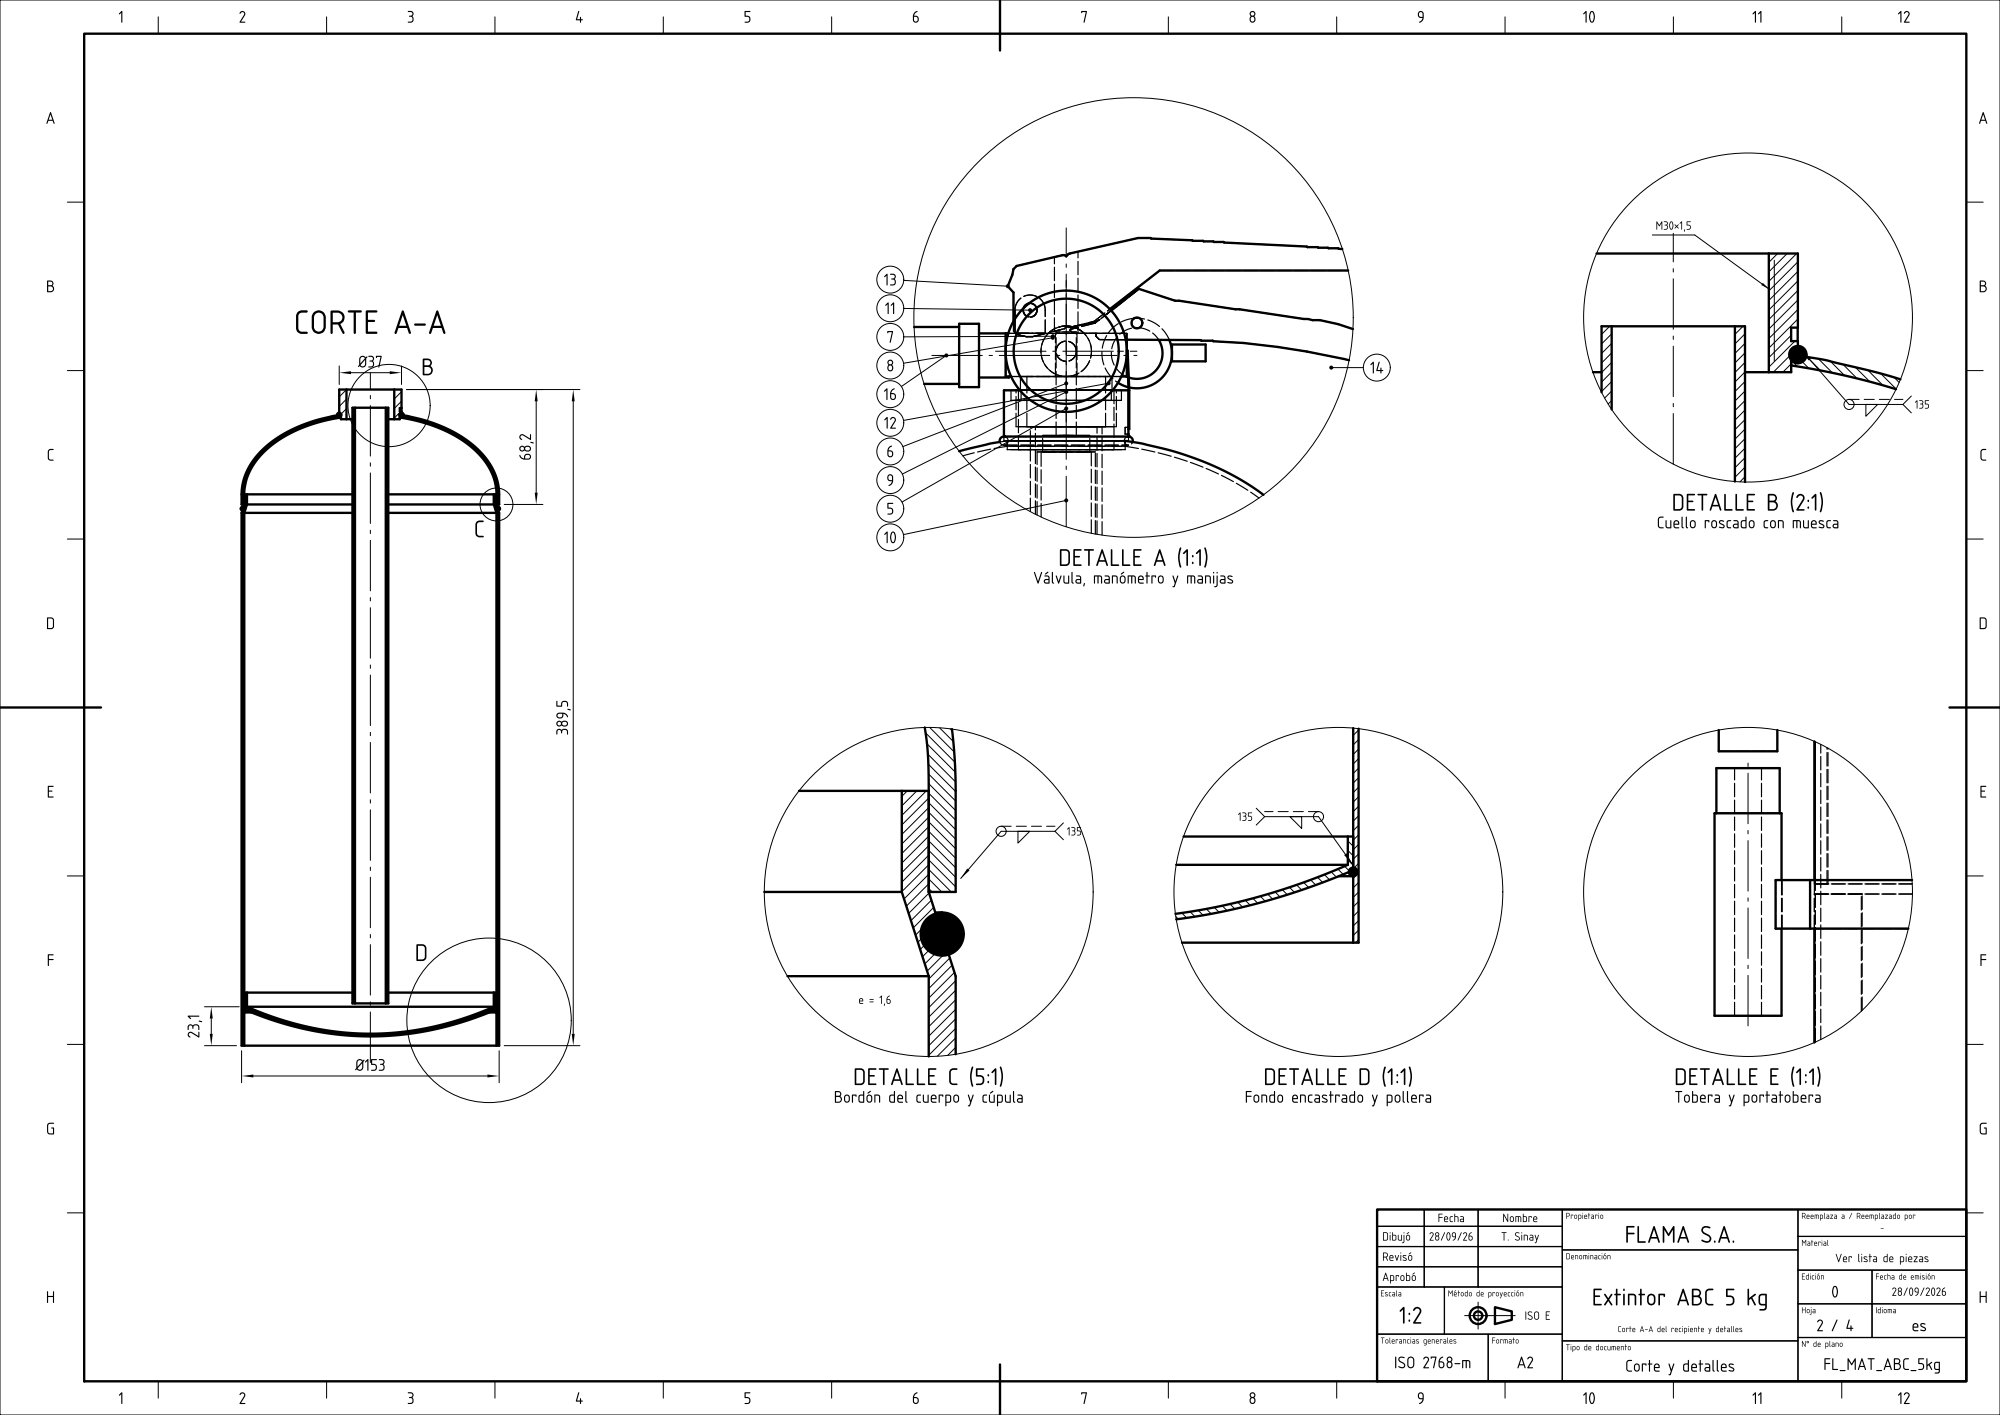
[picture p167: page 2]

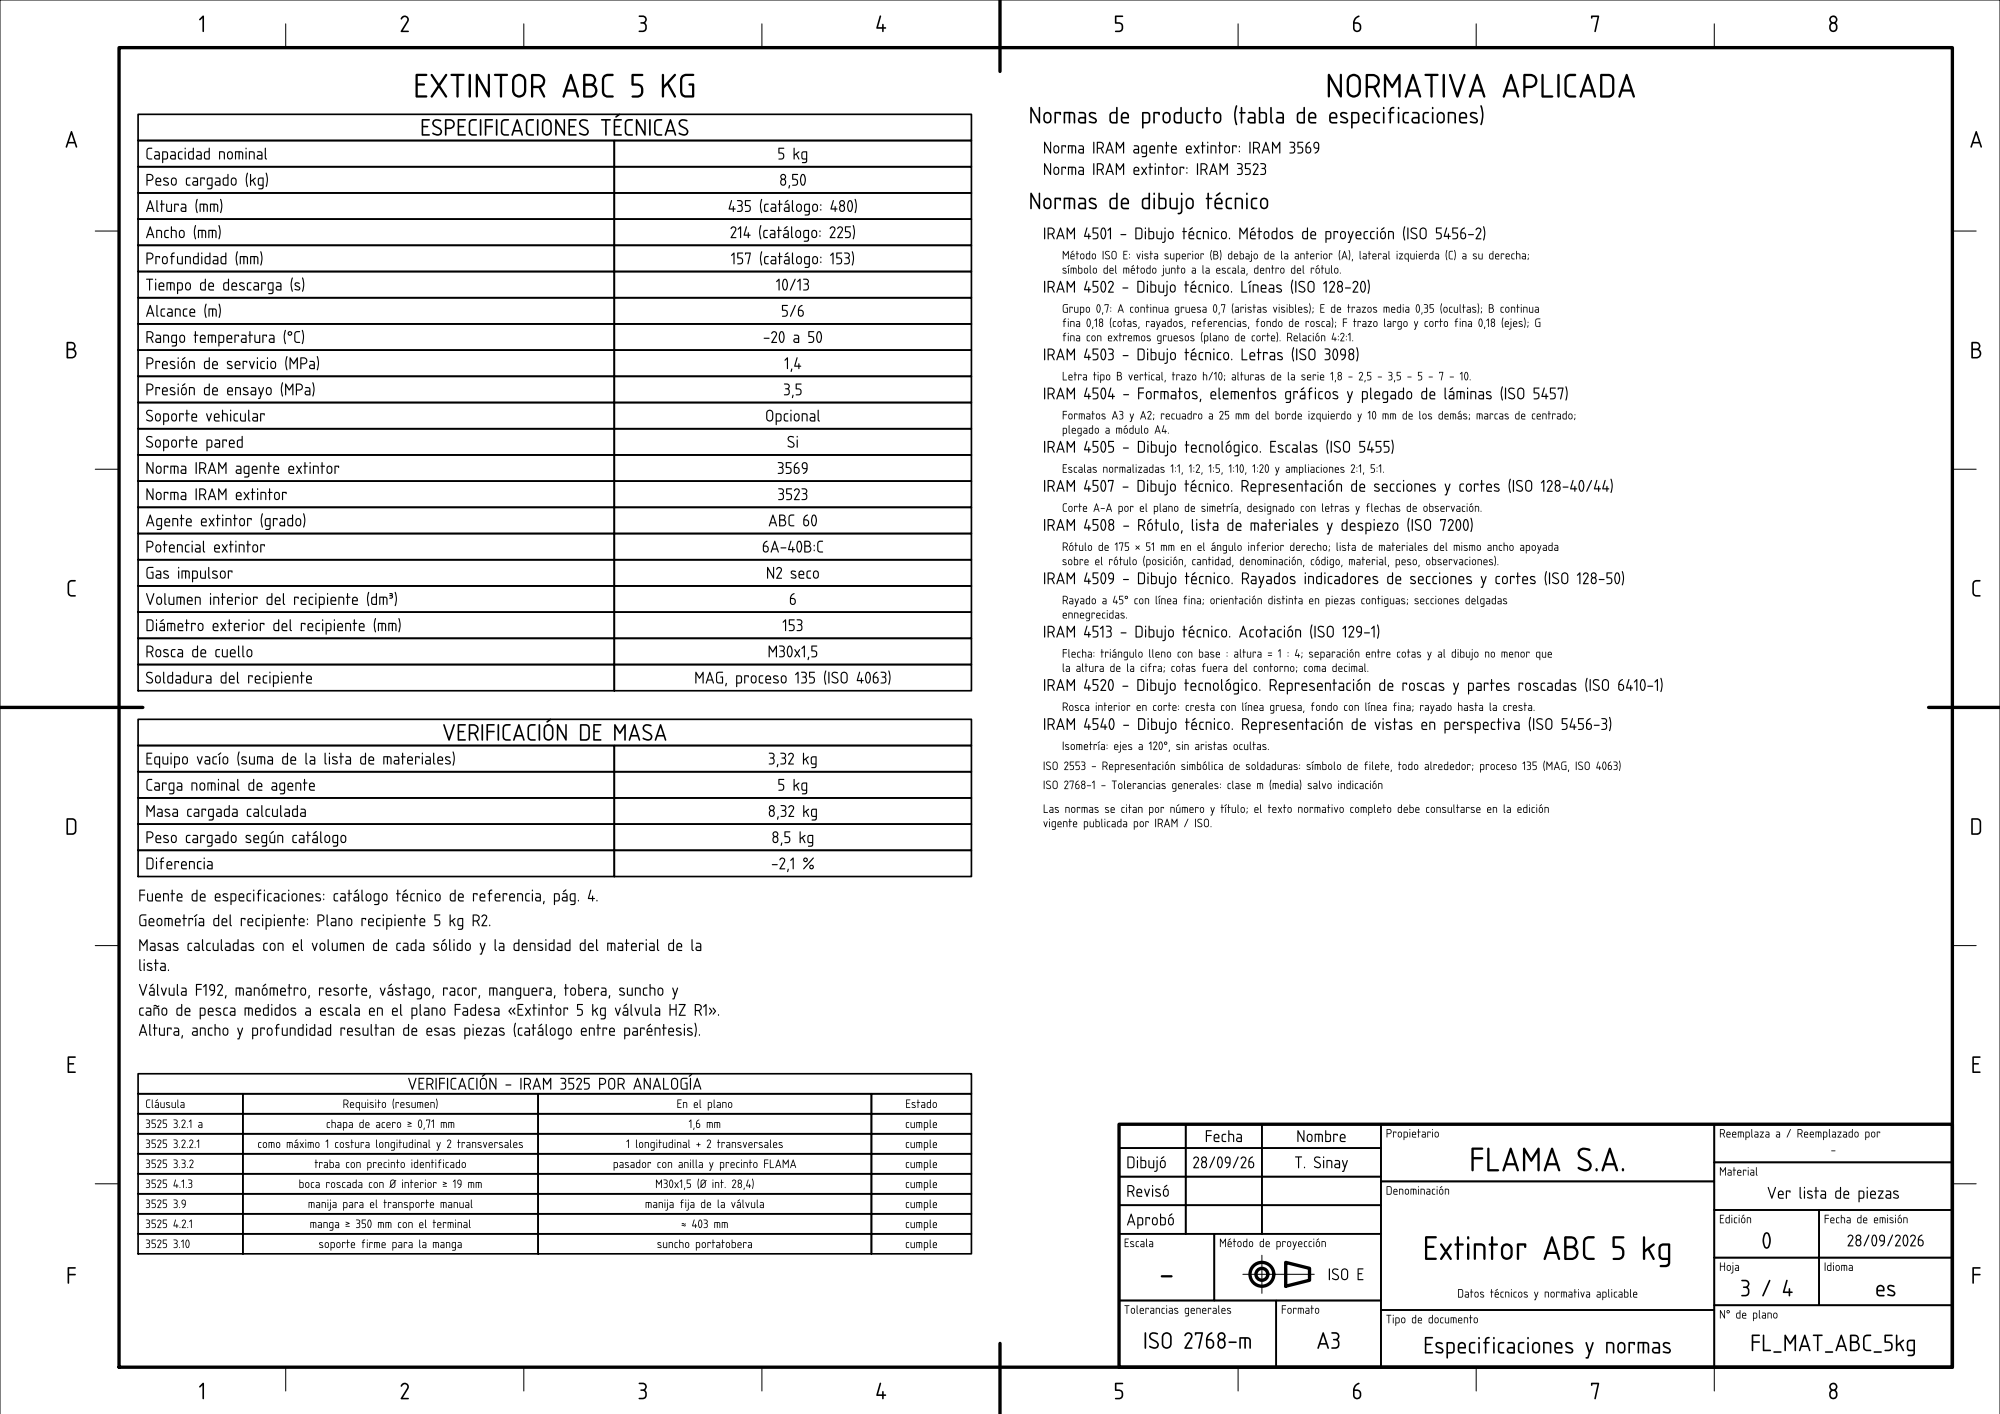
[picture p168: page 3]

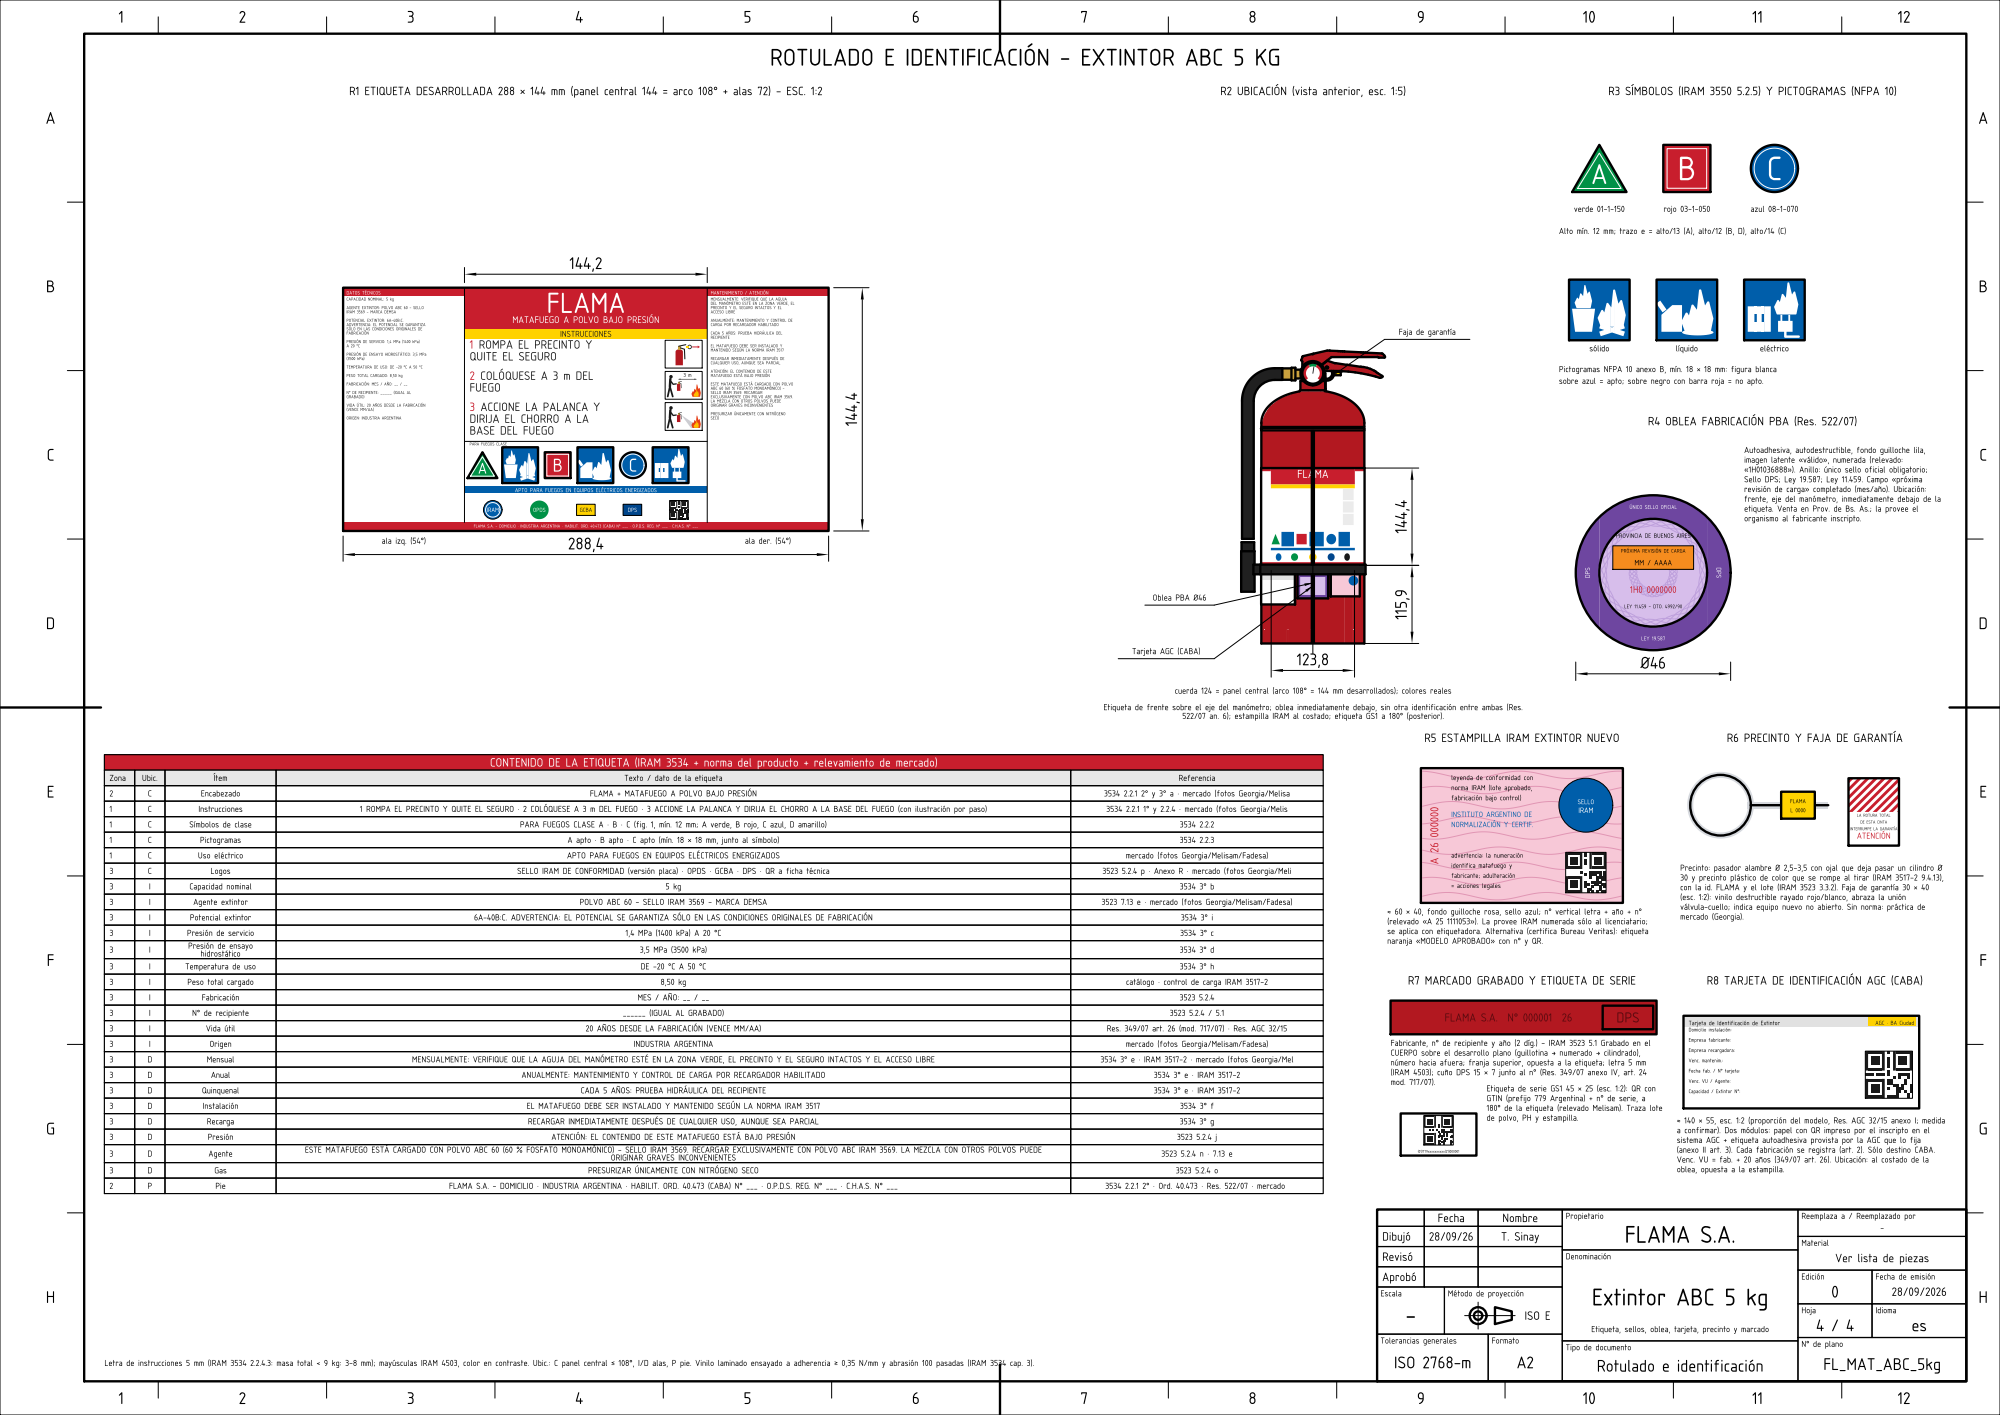
[picture p169: page 4]
