TadeoSinay/planos_flama-/salida/FL_MAT_ABC_70kg/FL_MAT_ABC_70kg.pdf

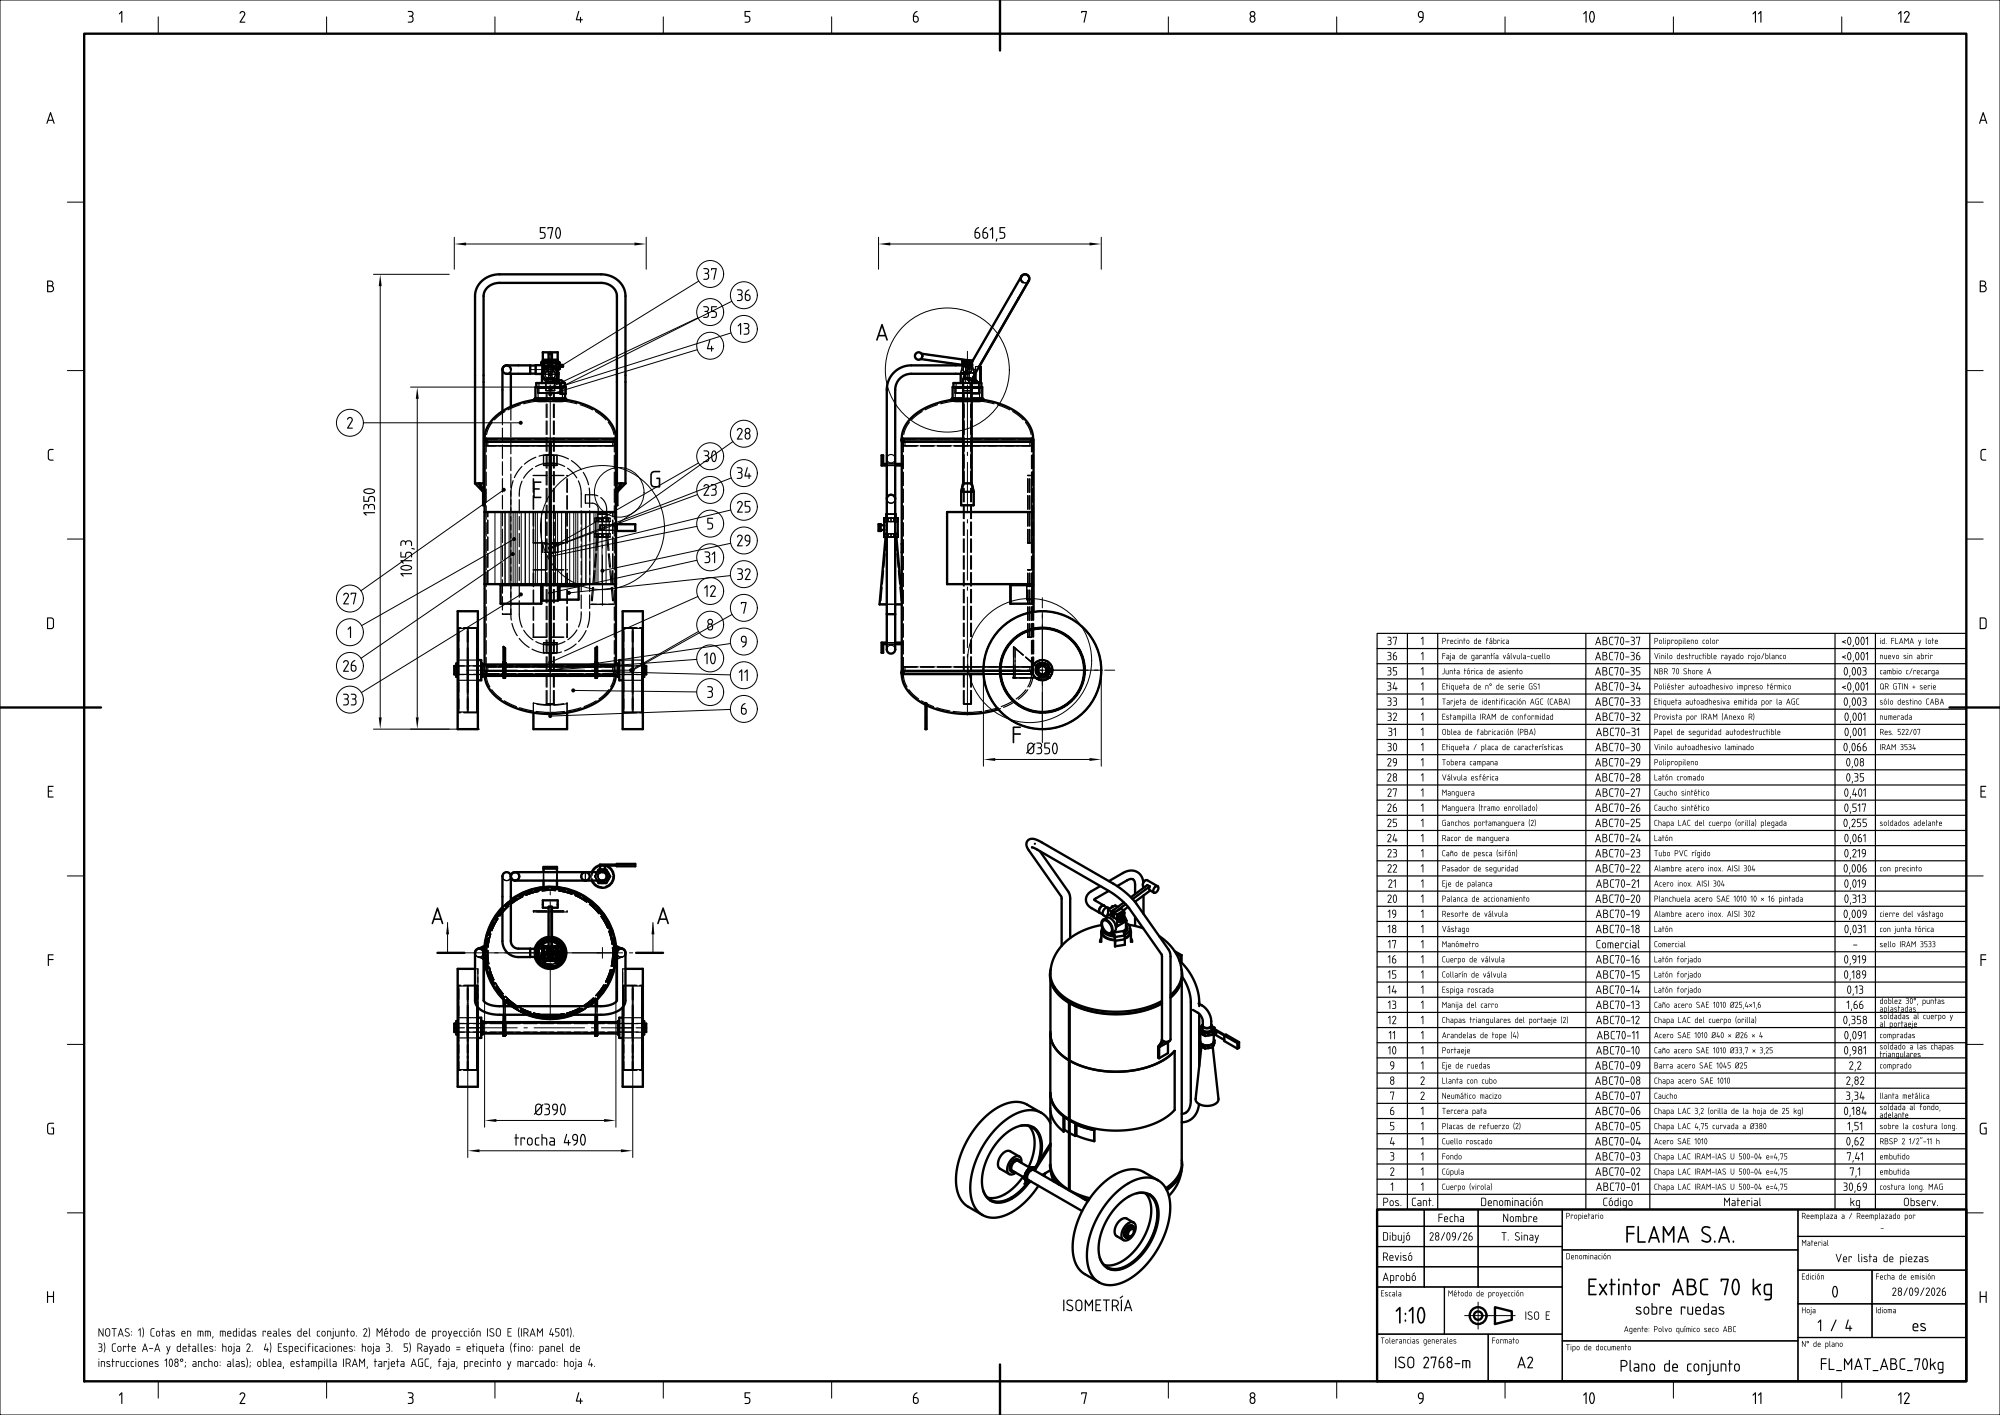
[picture p170: page 1]

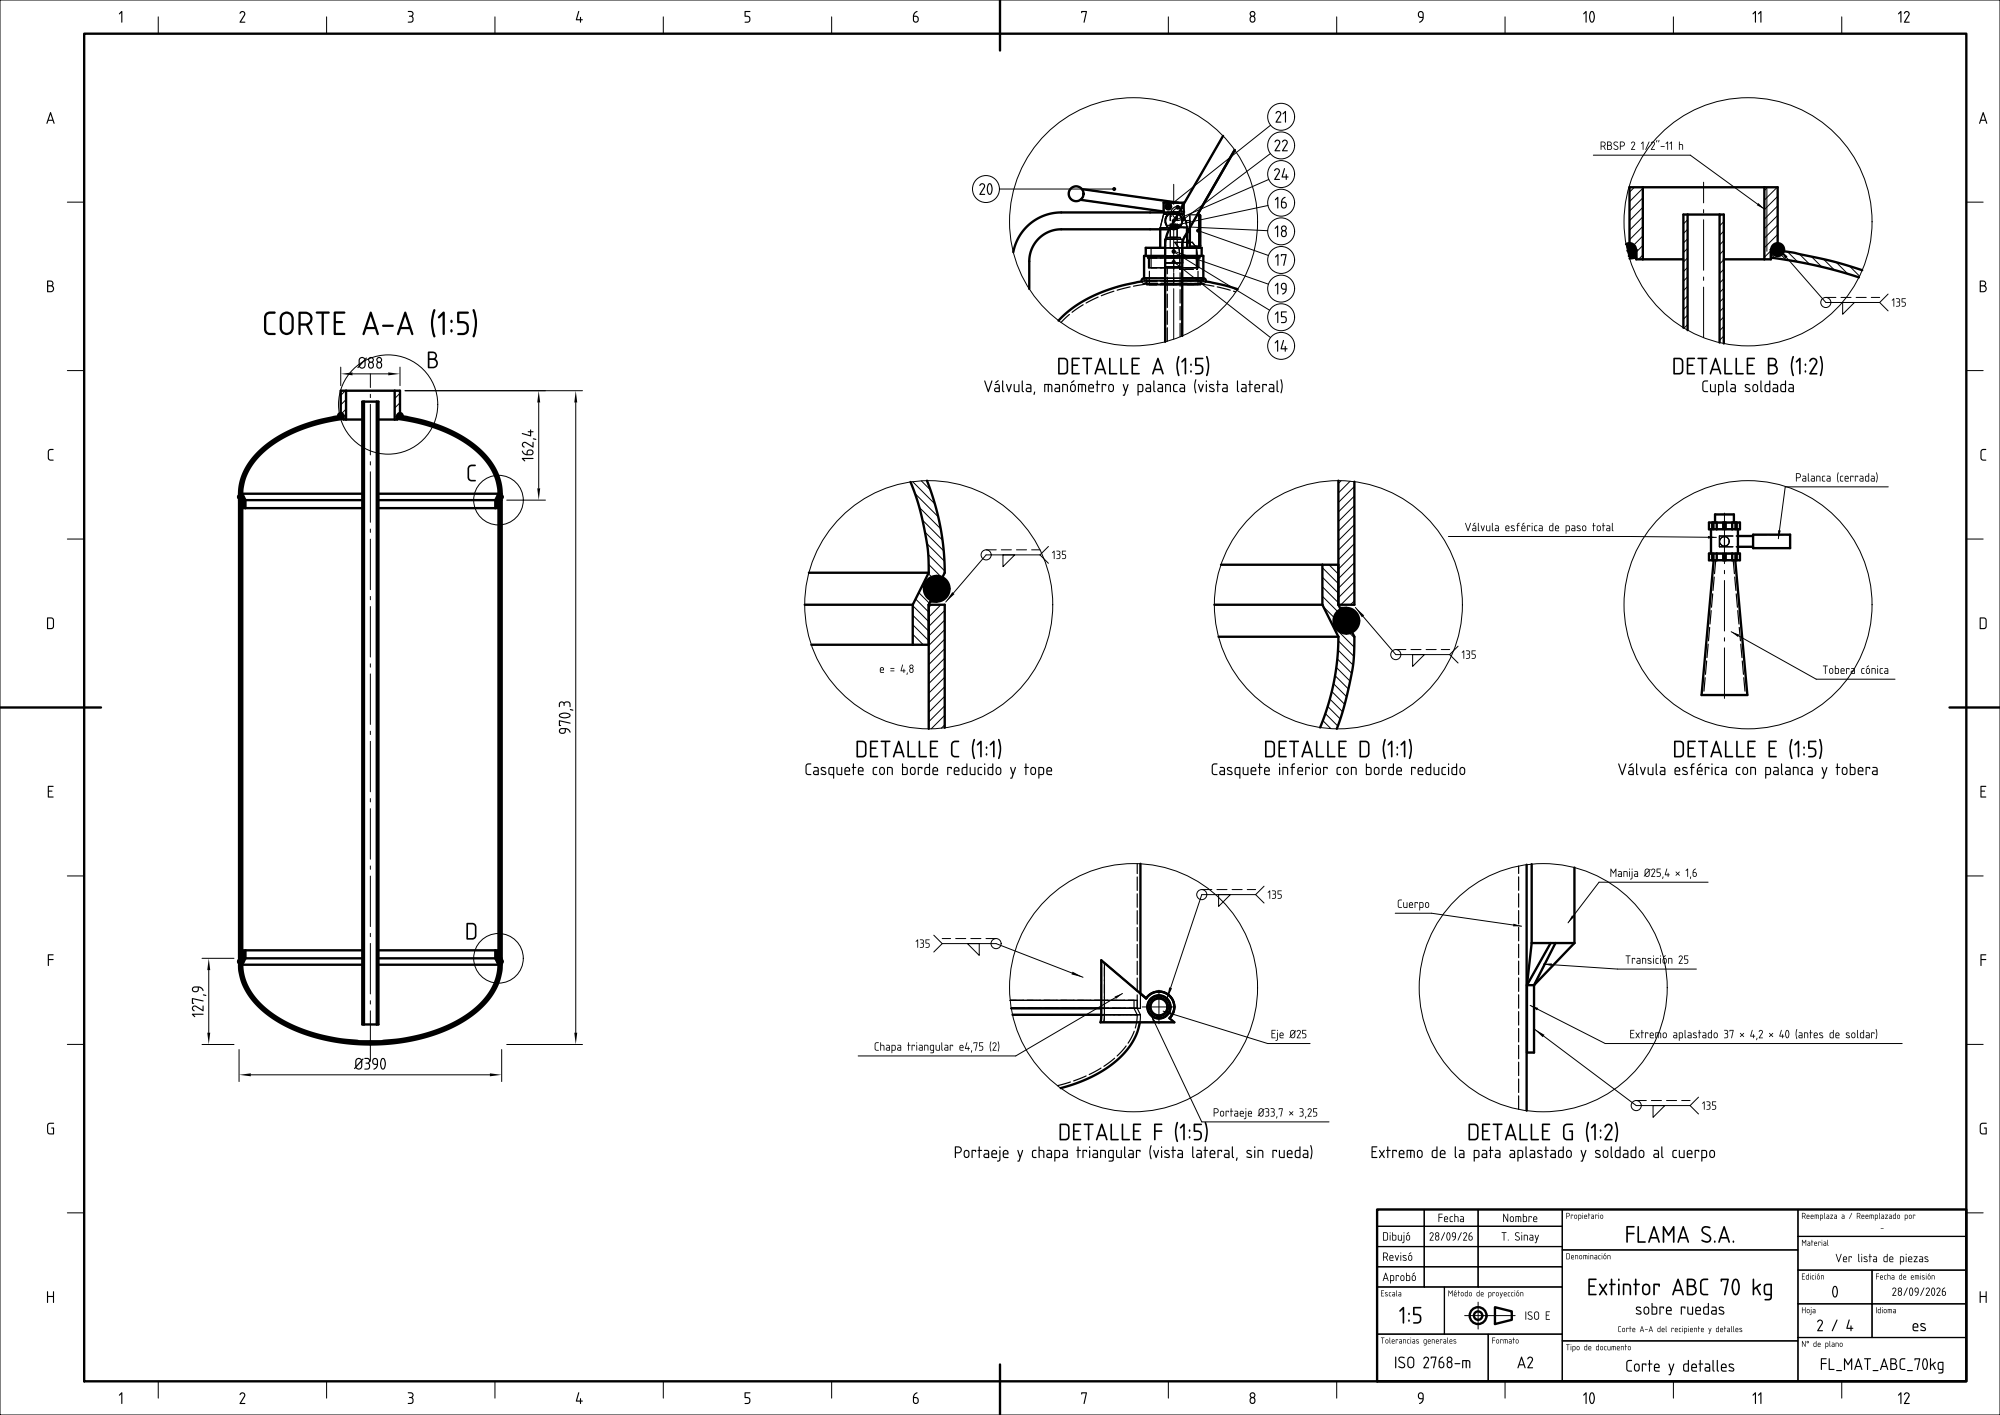
[picture p171: page 2]

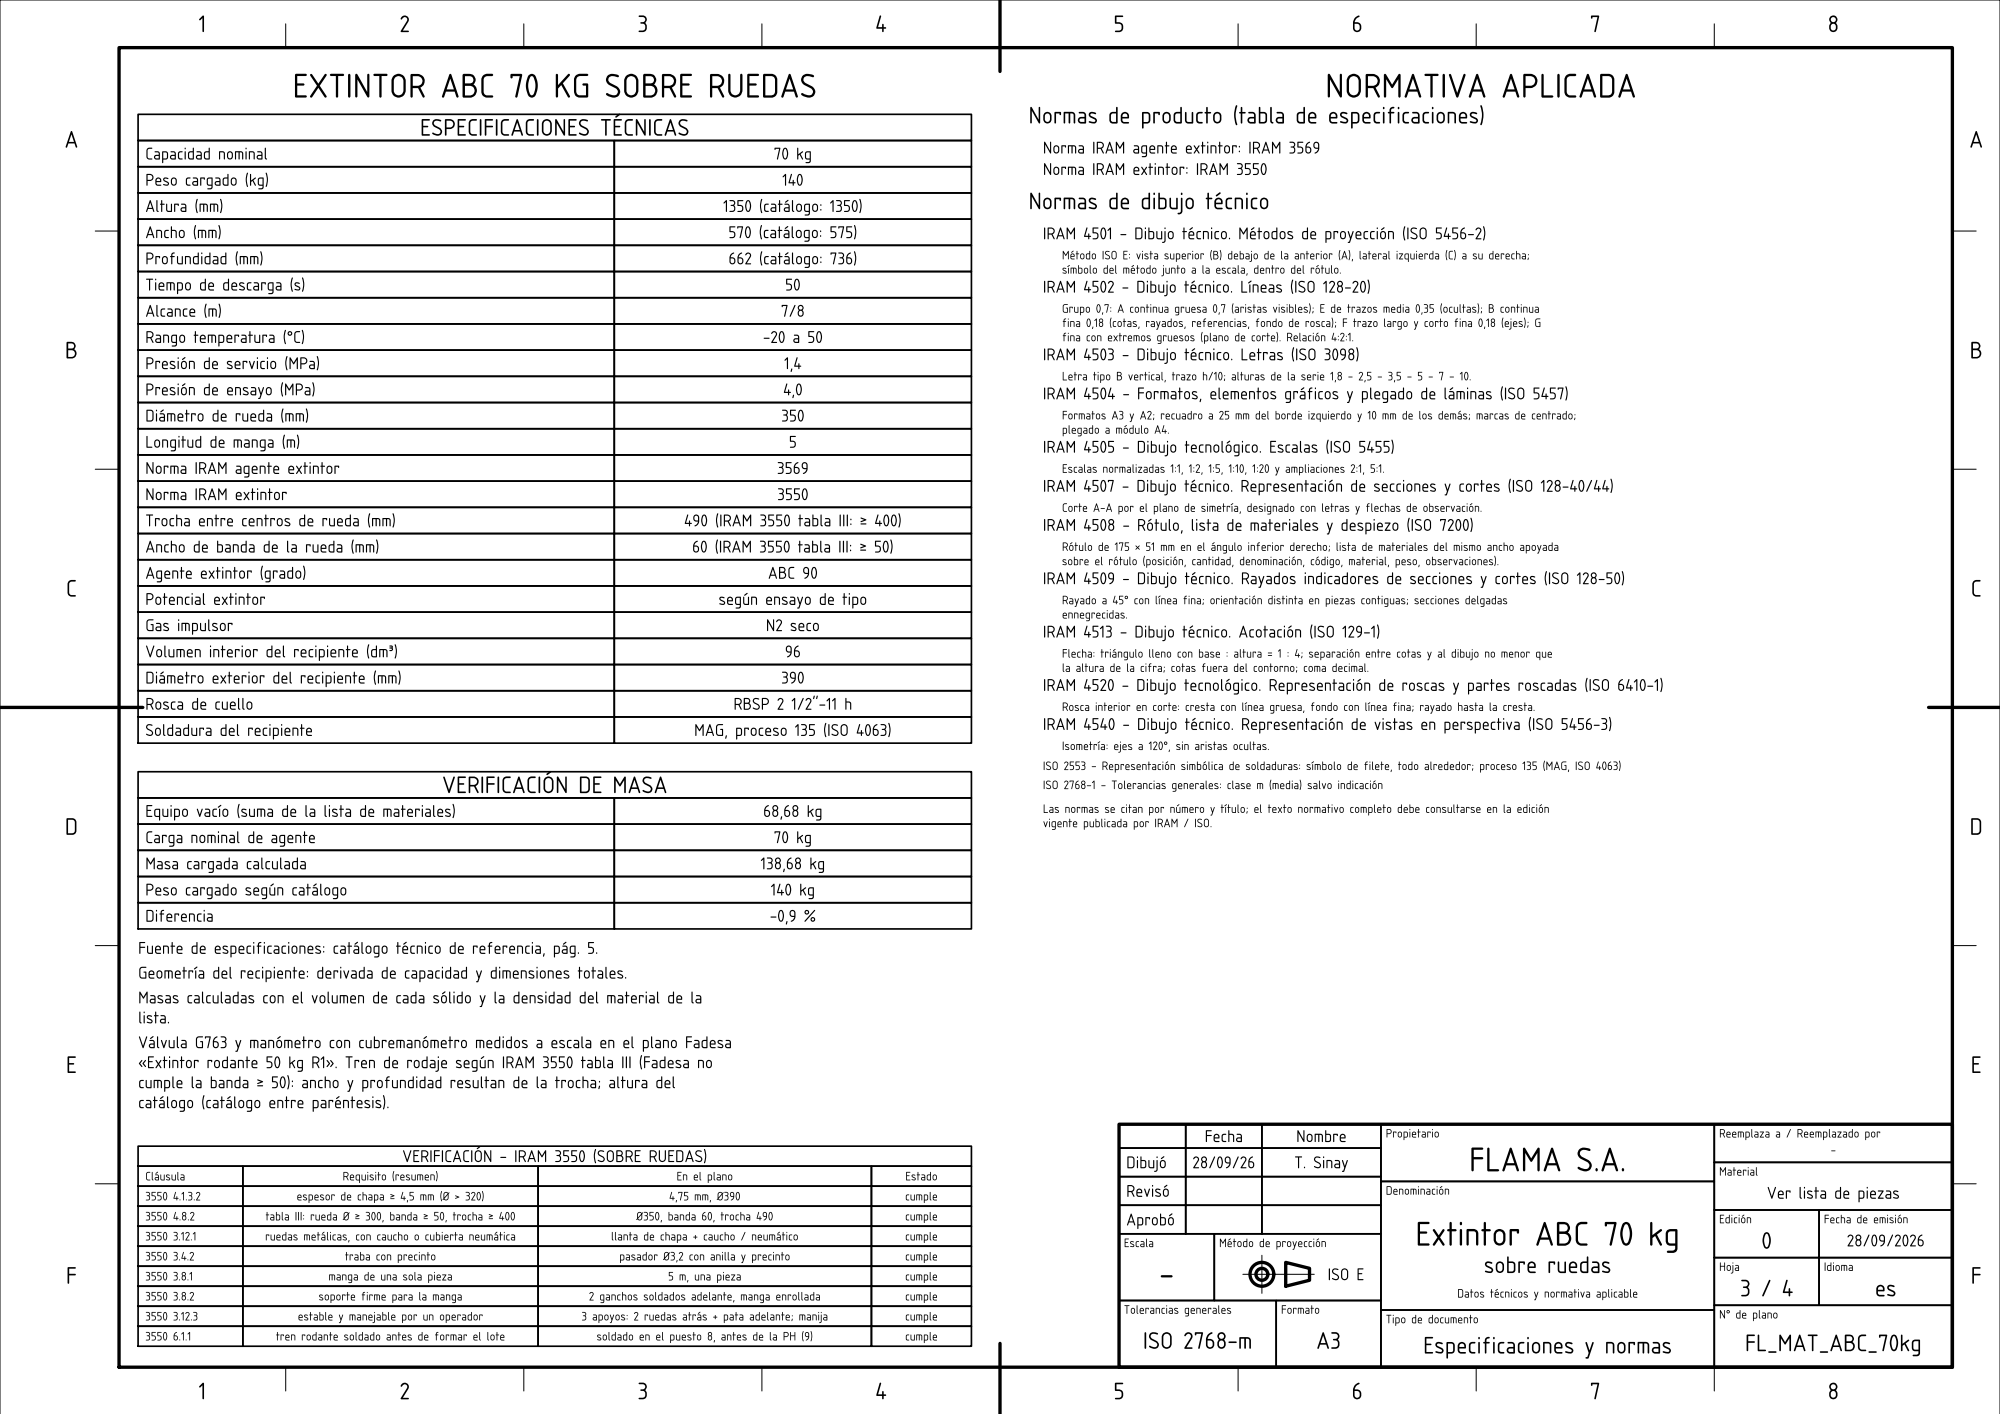
[picture p172: page 3]

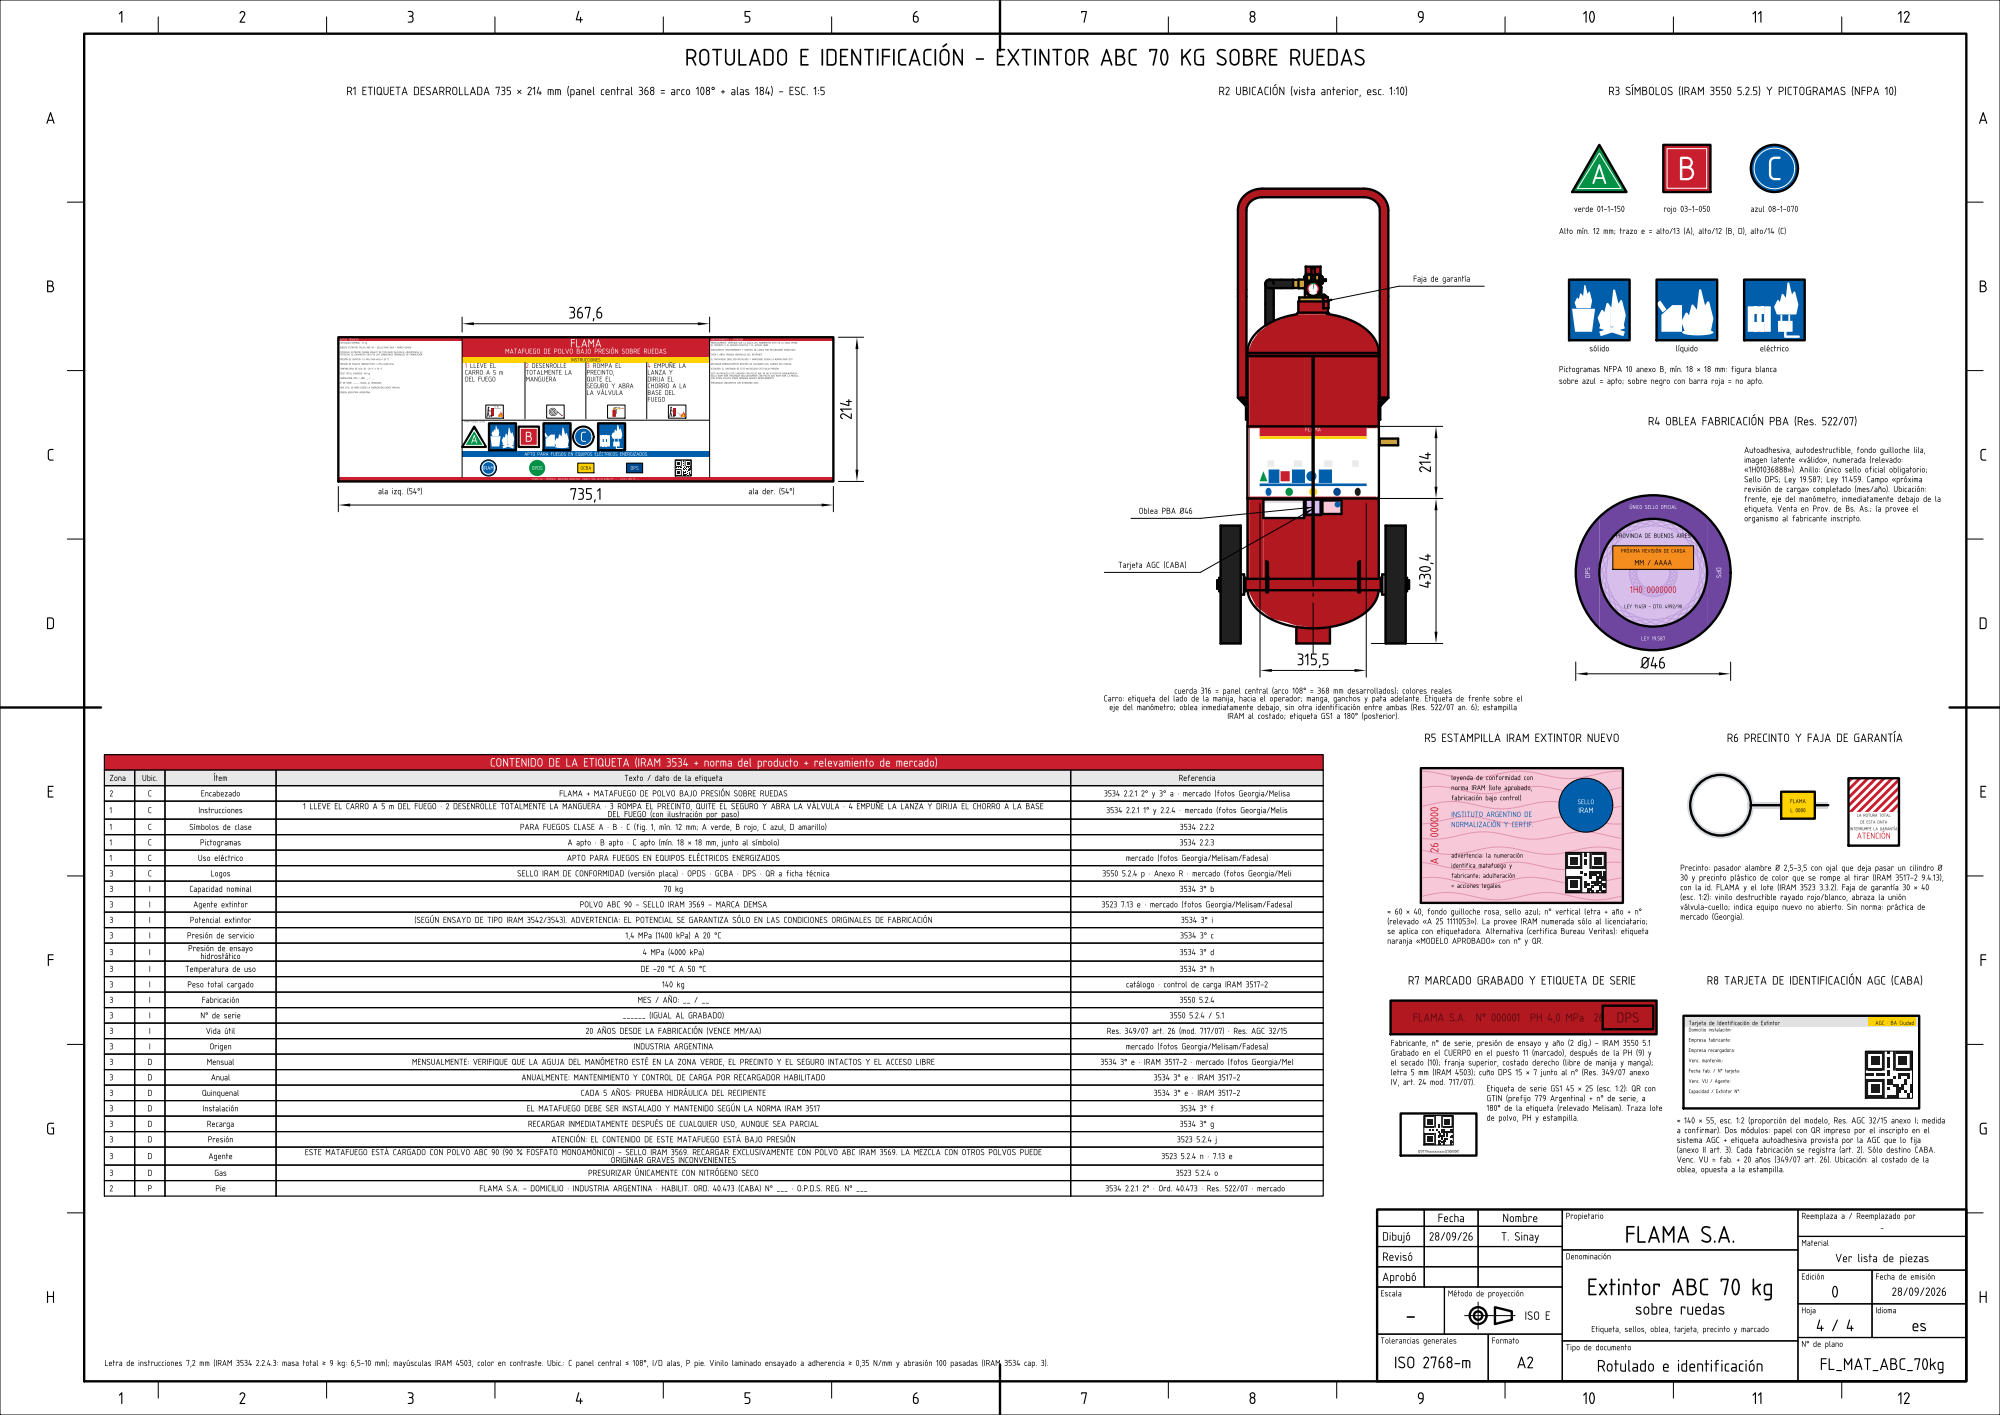
[picture p173: page 4]
