TadeoSinay/planos_flama-/salida/FL_MAT_AFFF_10l/FL_MAT_AFFF_10l.pdf

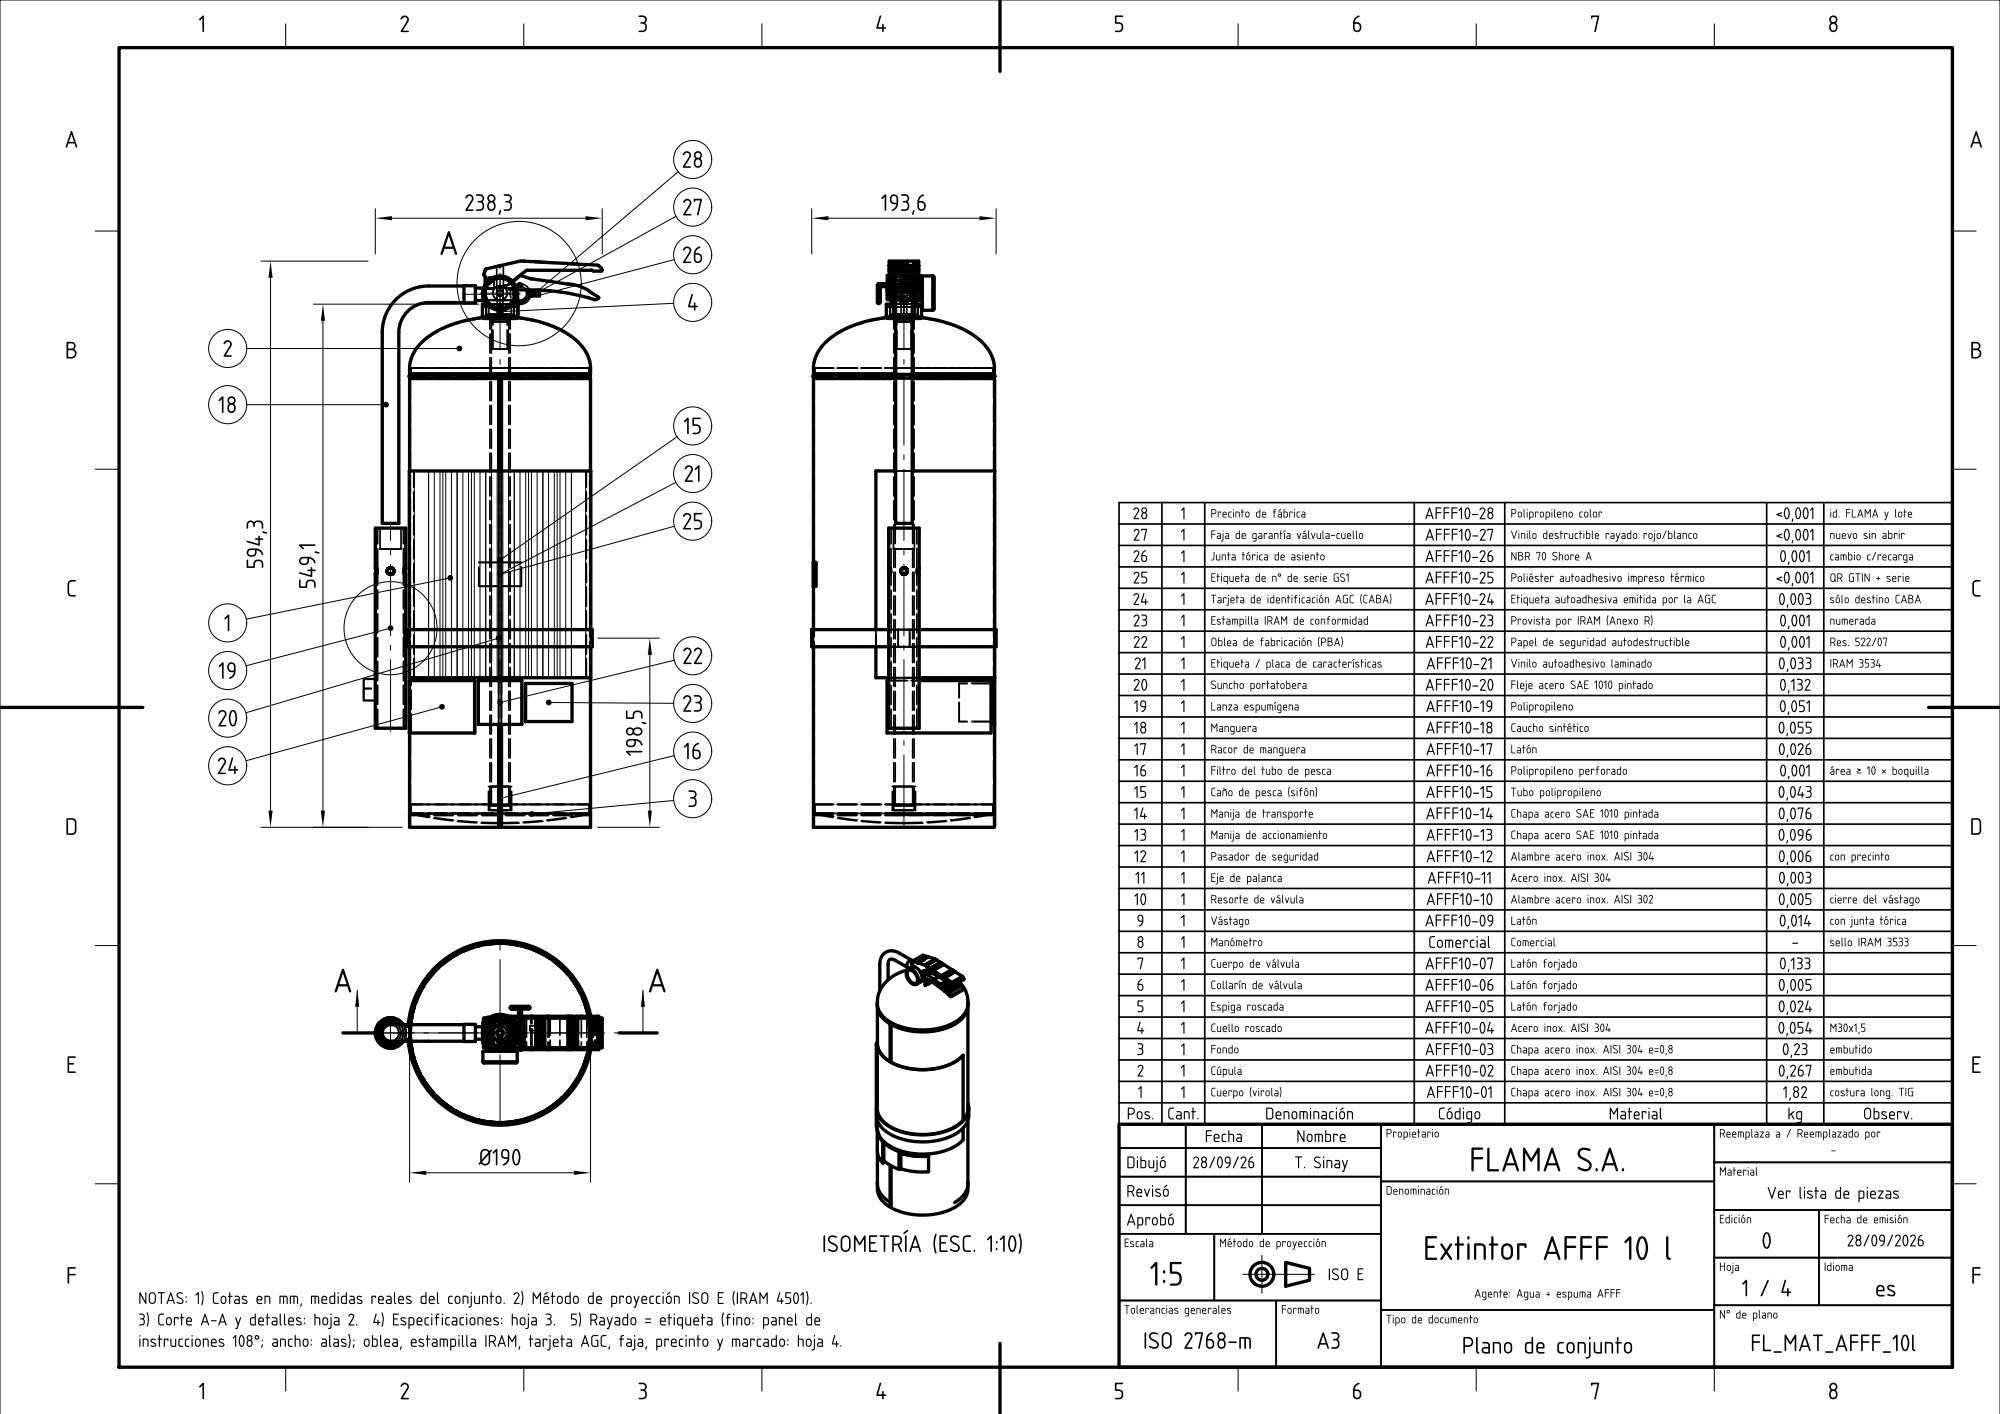
[picture p174: page 1]

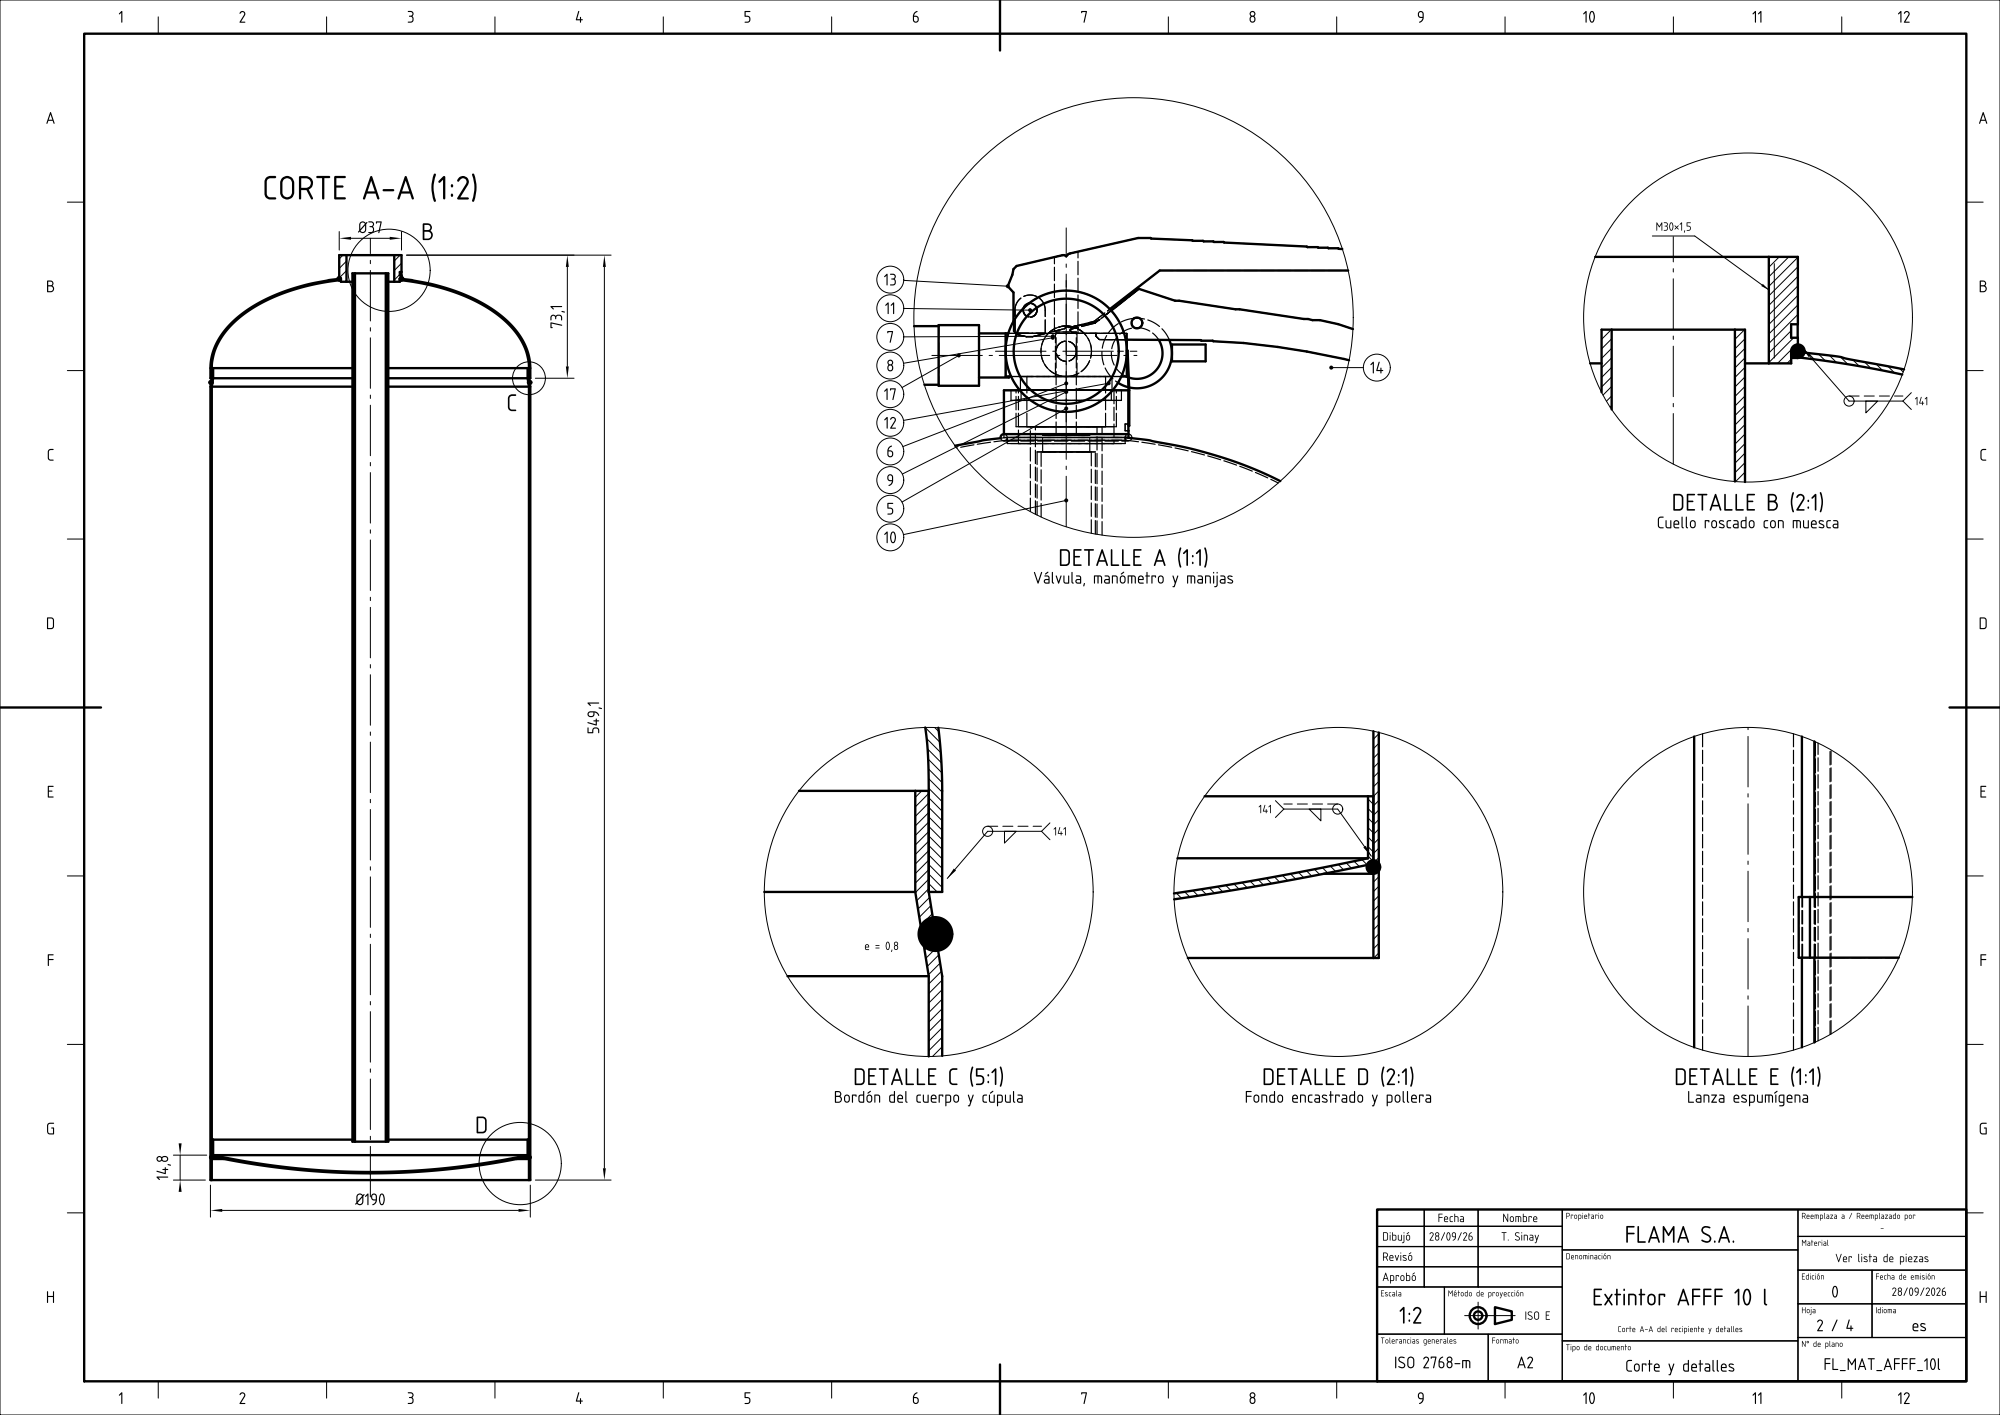
[picture p175: page 2]

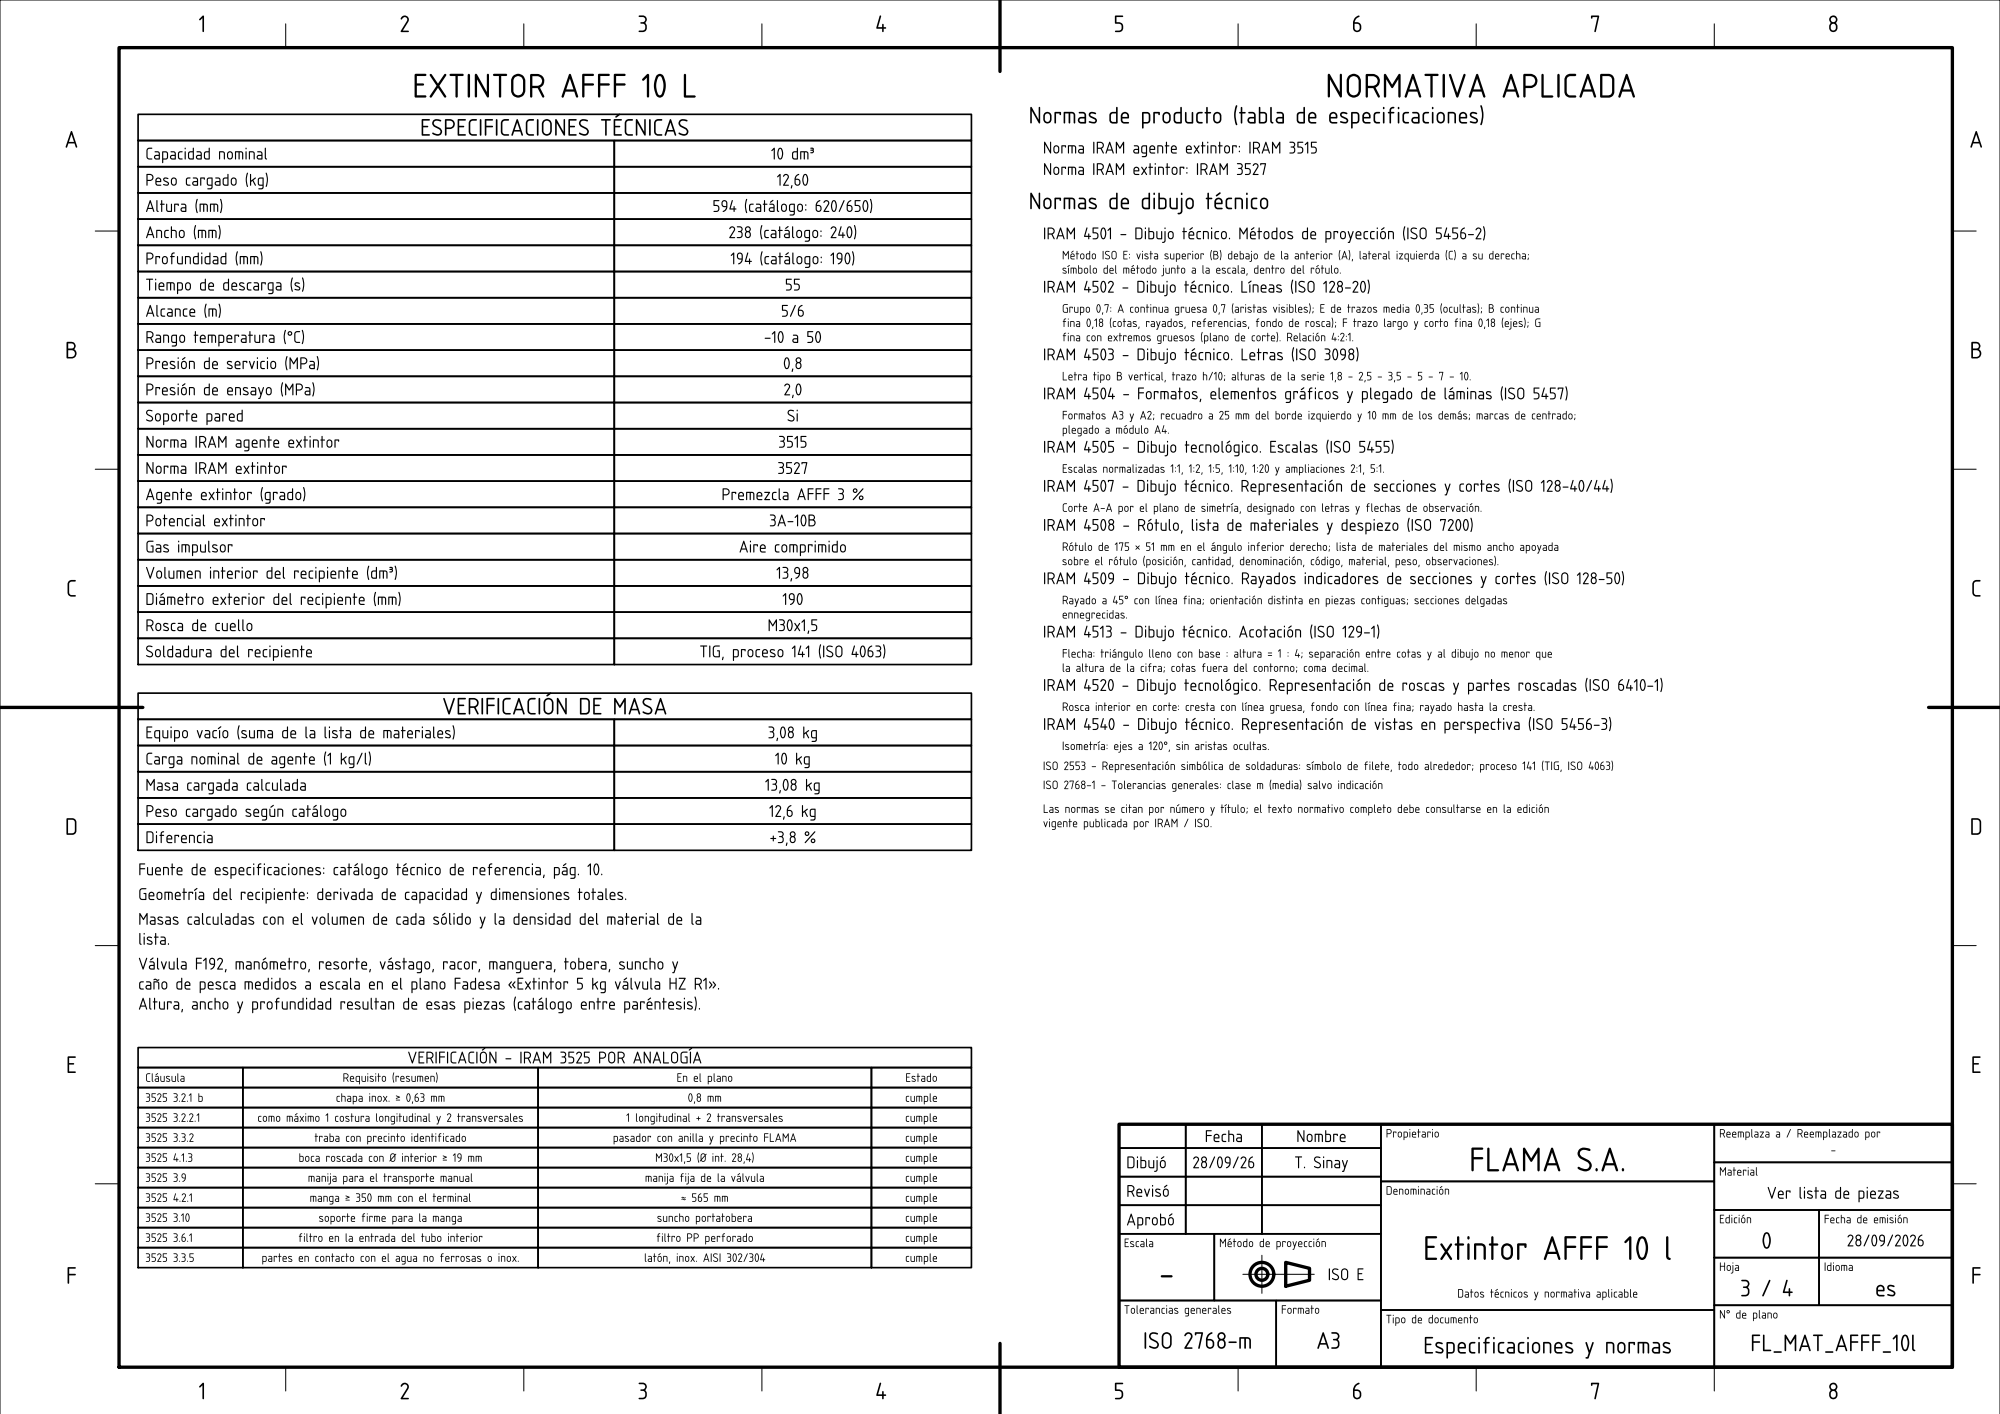
[picture p176: page 3]

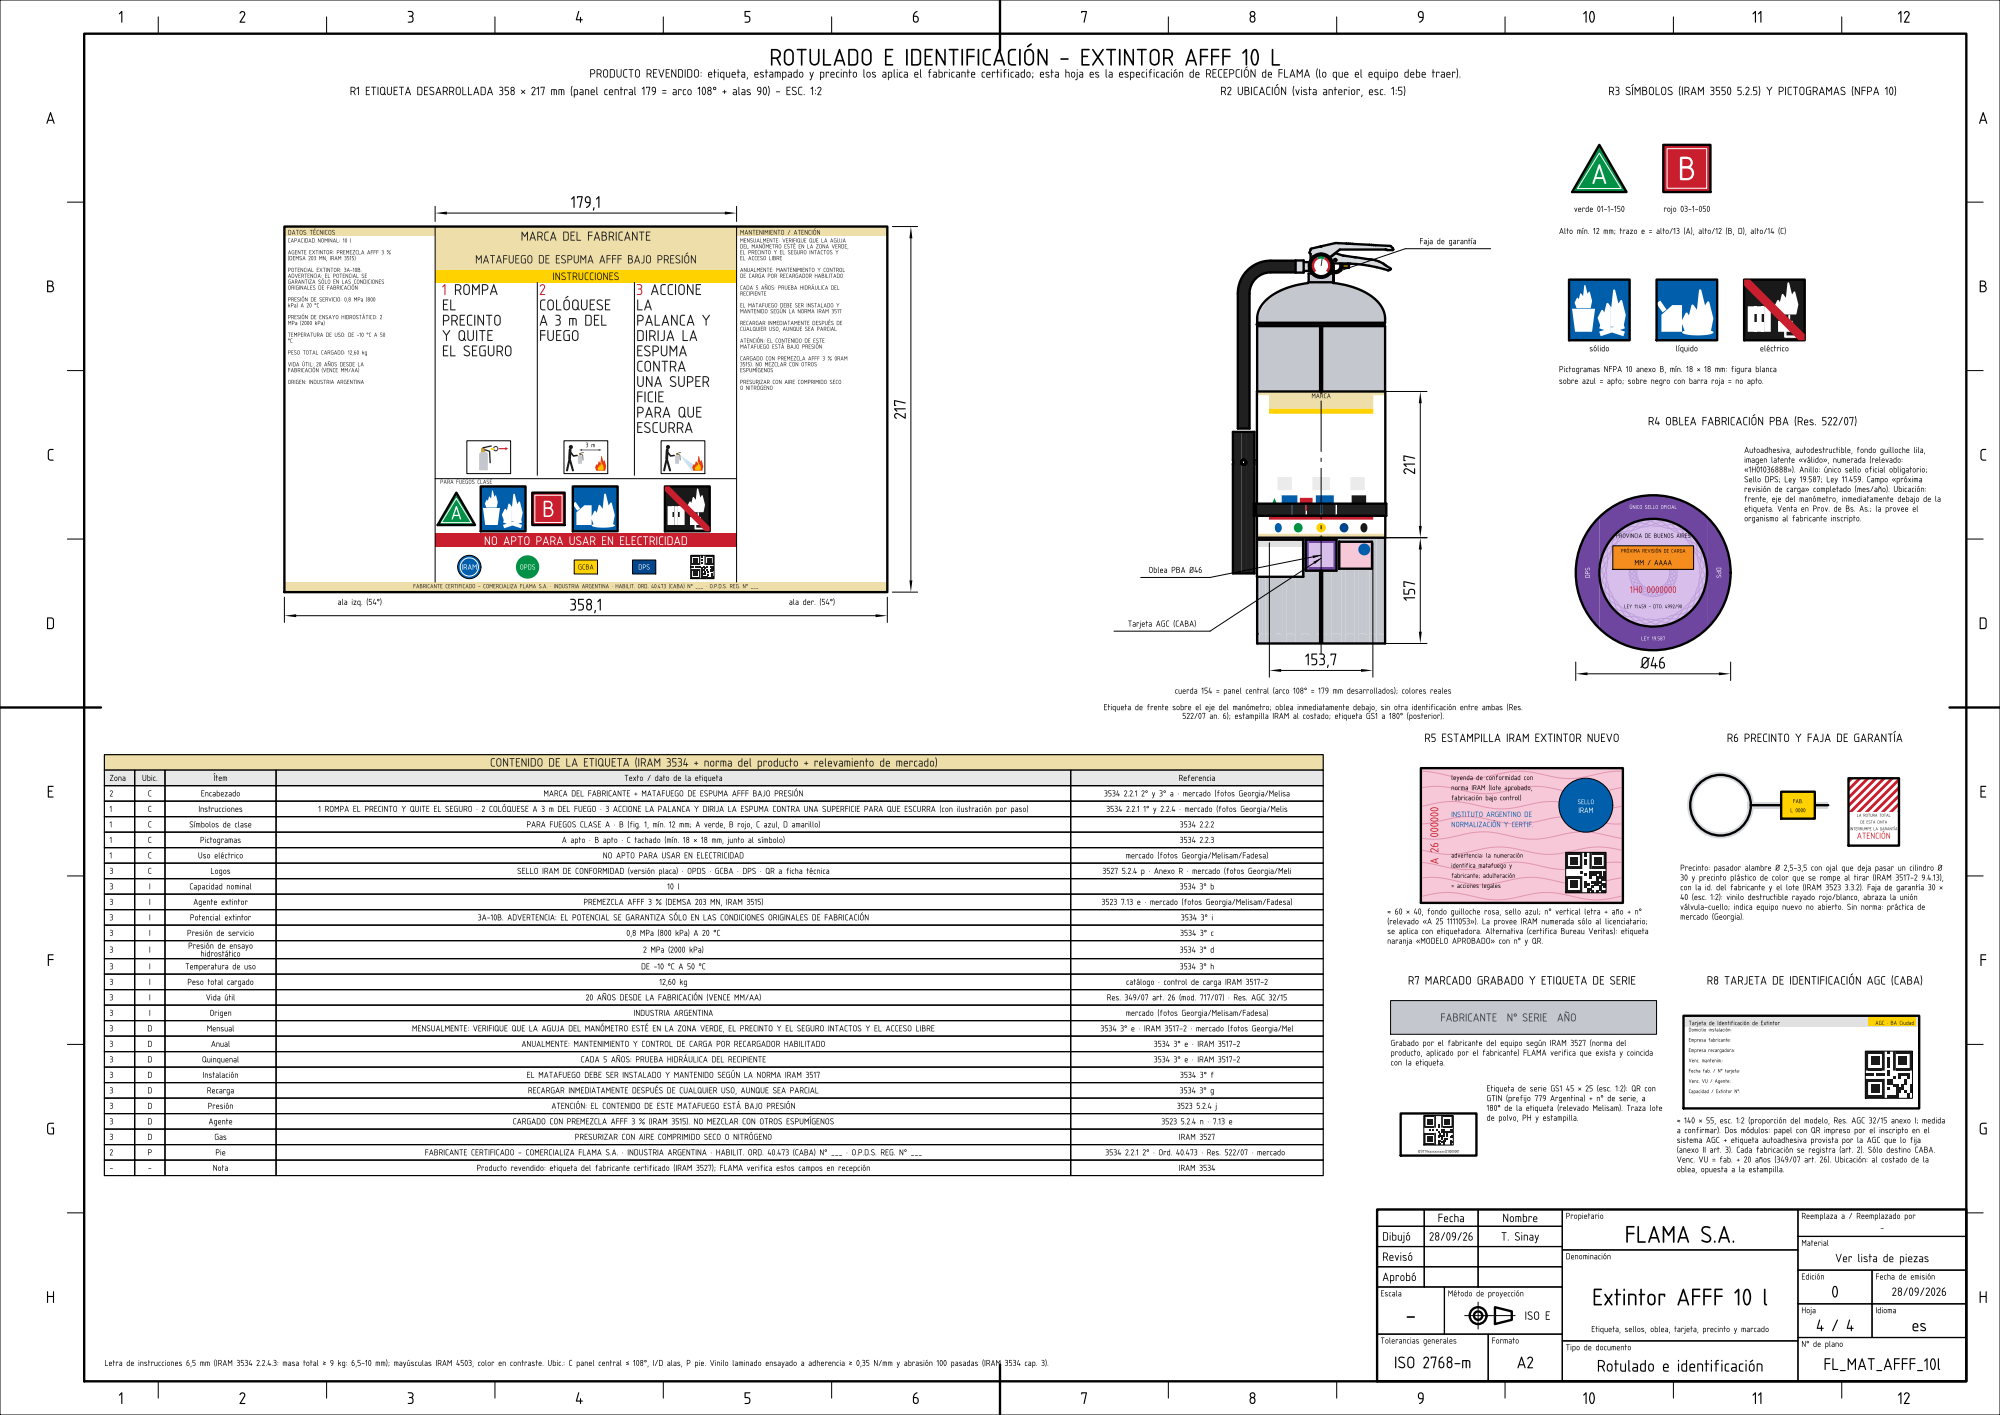
[picture p177: page 4]
