TadeoSinay/planos_flama-/salida/FL_MAT_AFFF_50l/FL_MAT_AFFF_50l.pdf

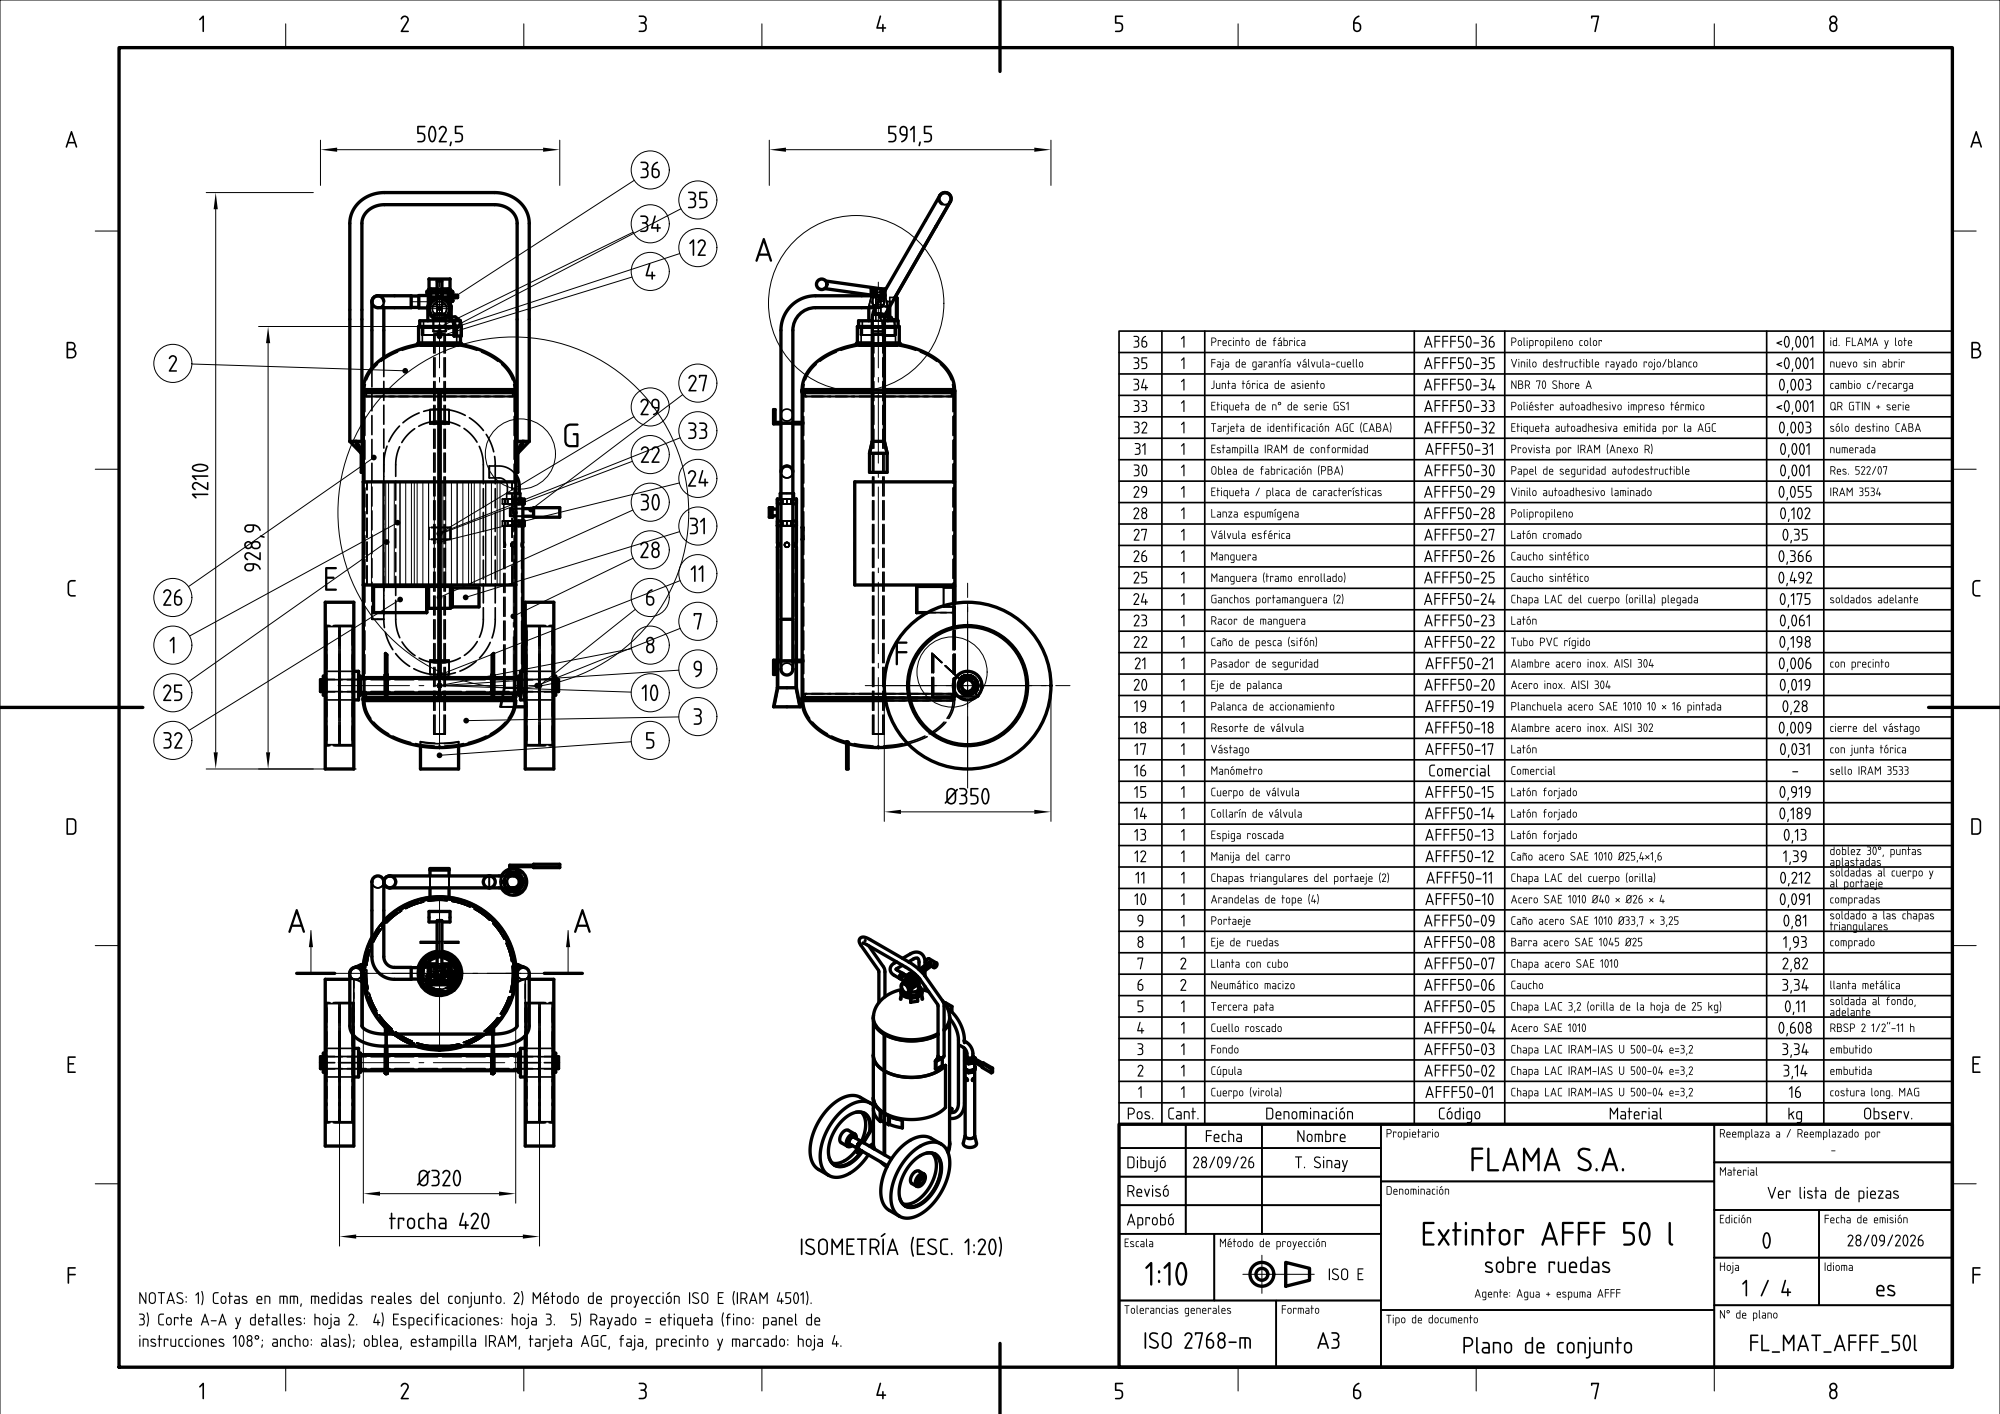
[picture p178: page 1]

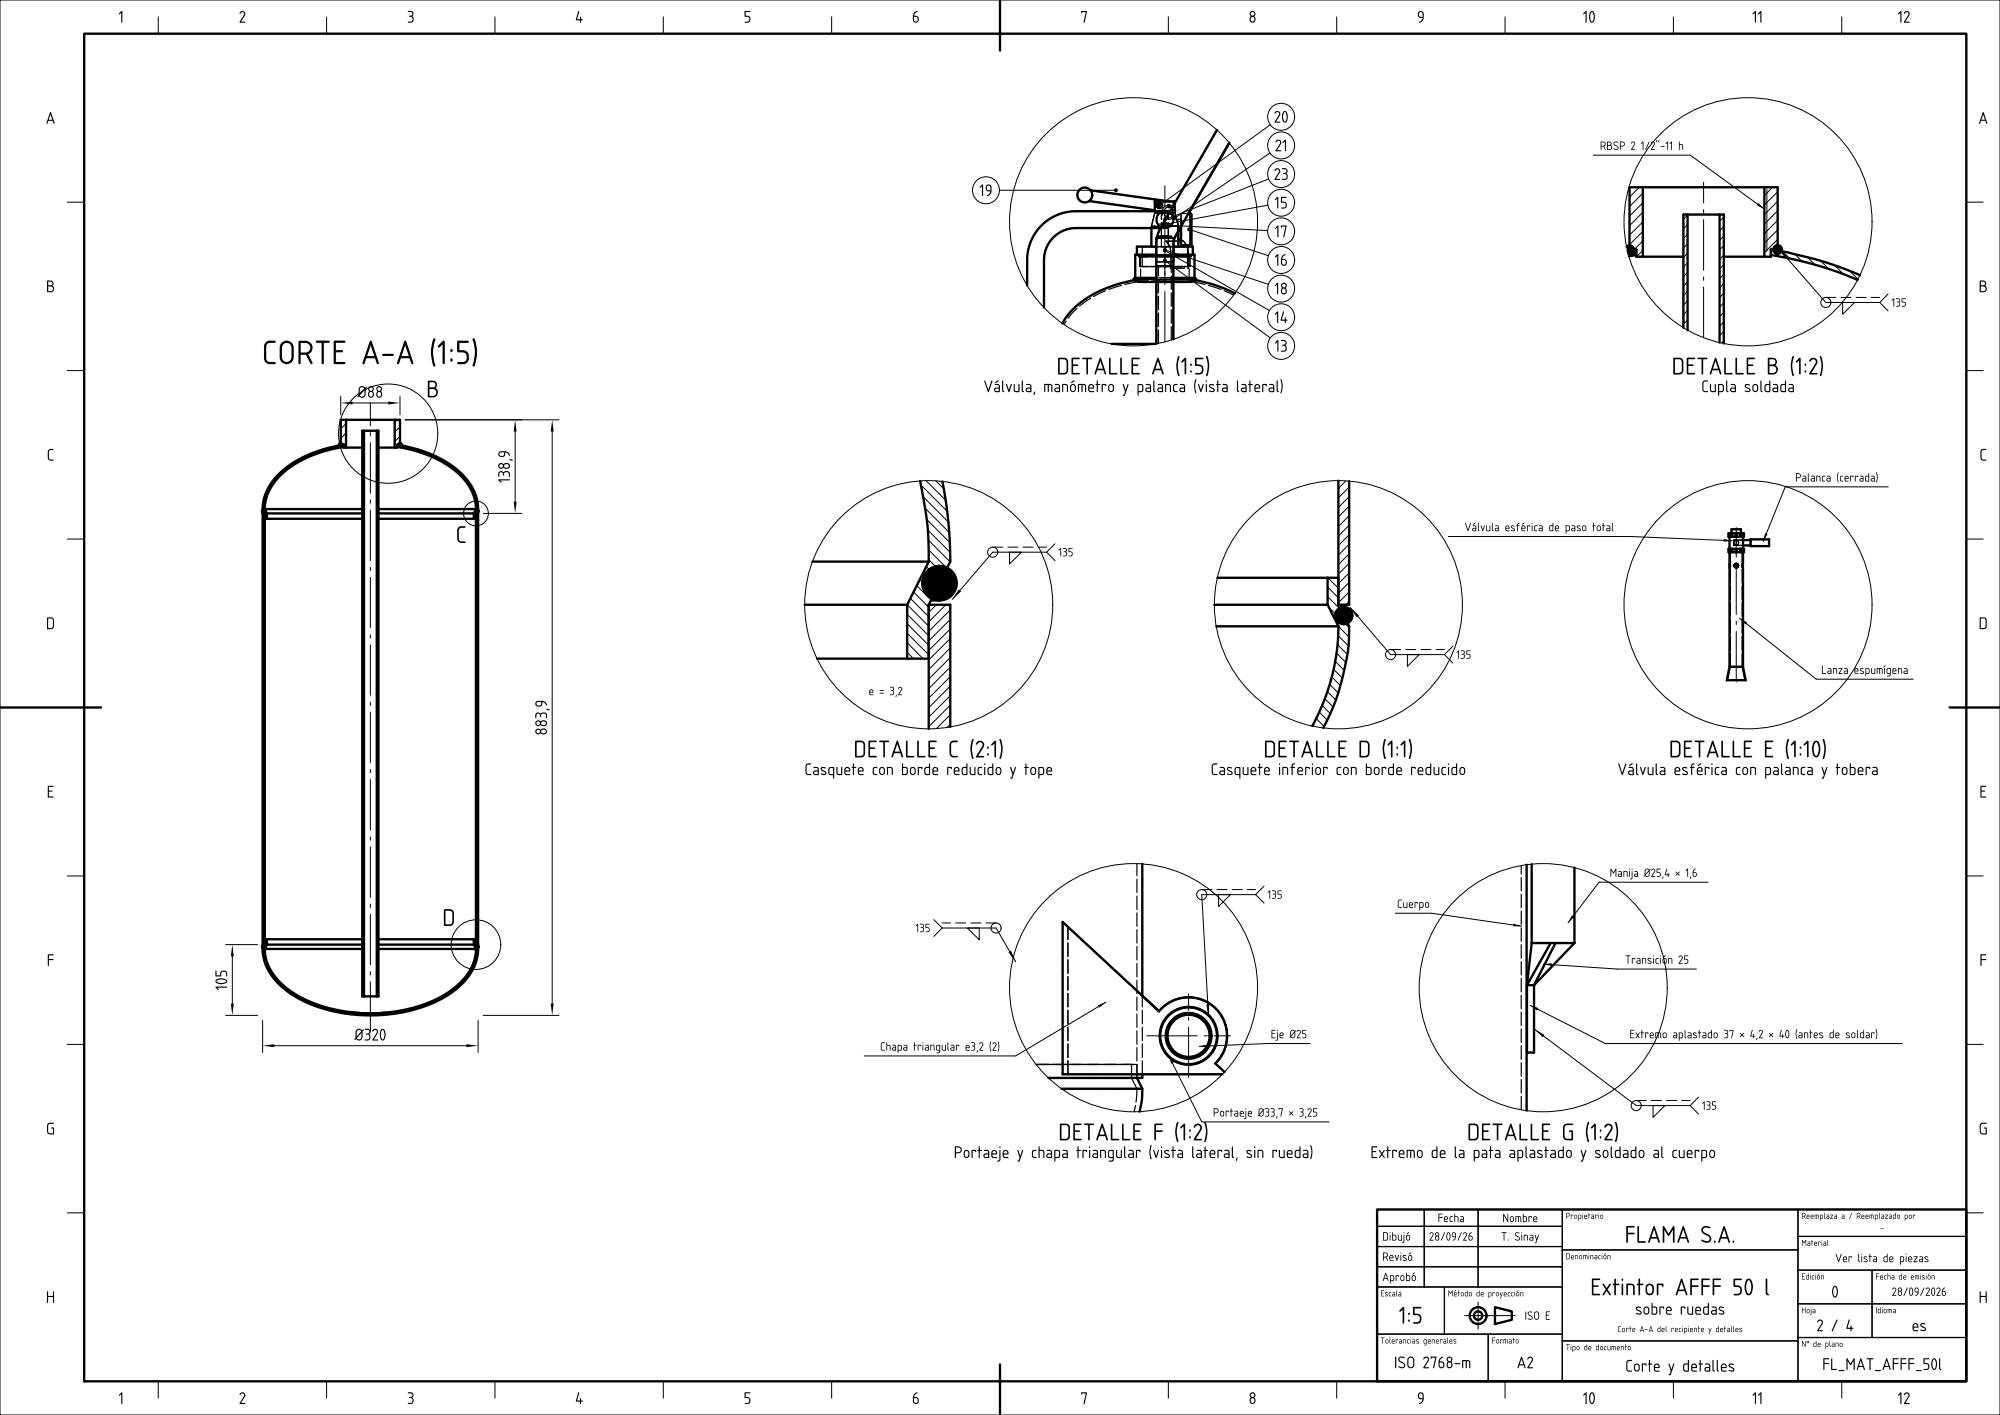
[picture p179: page 2]

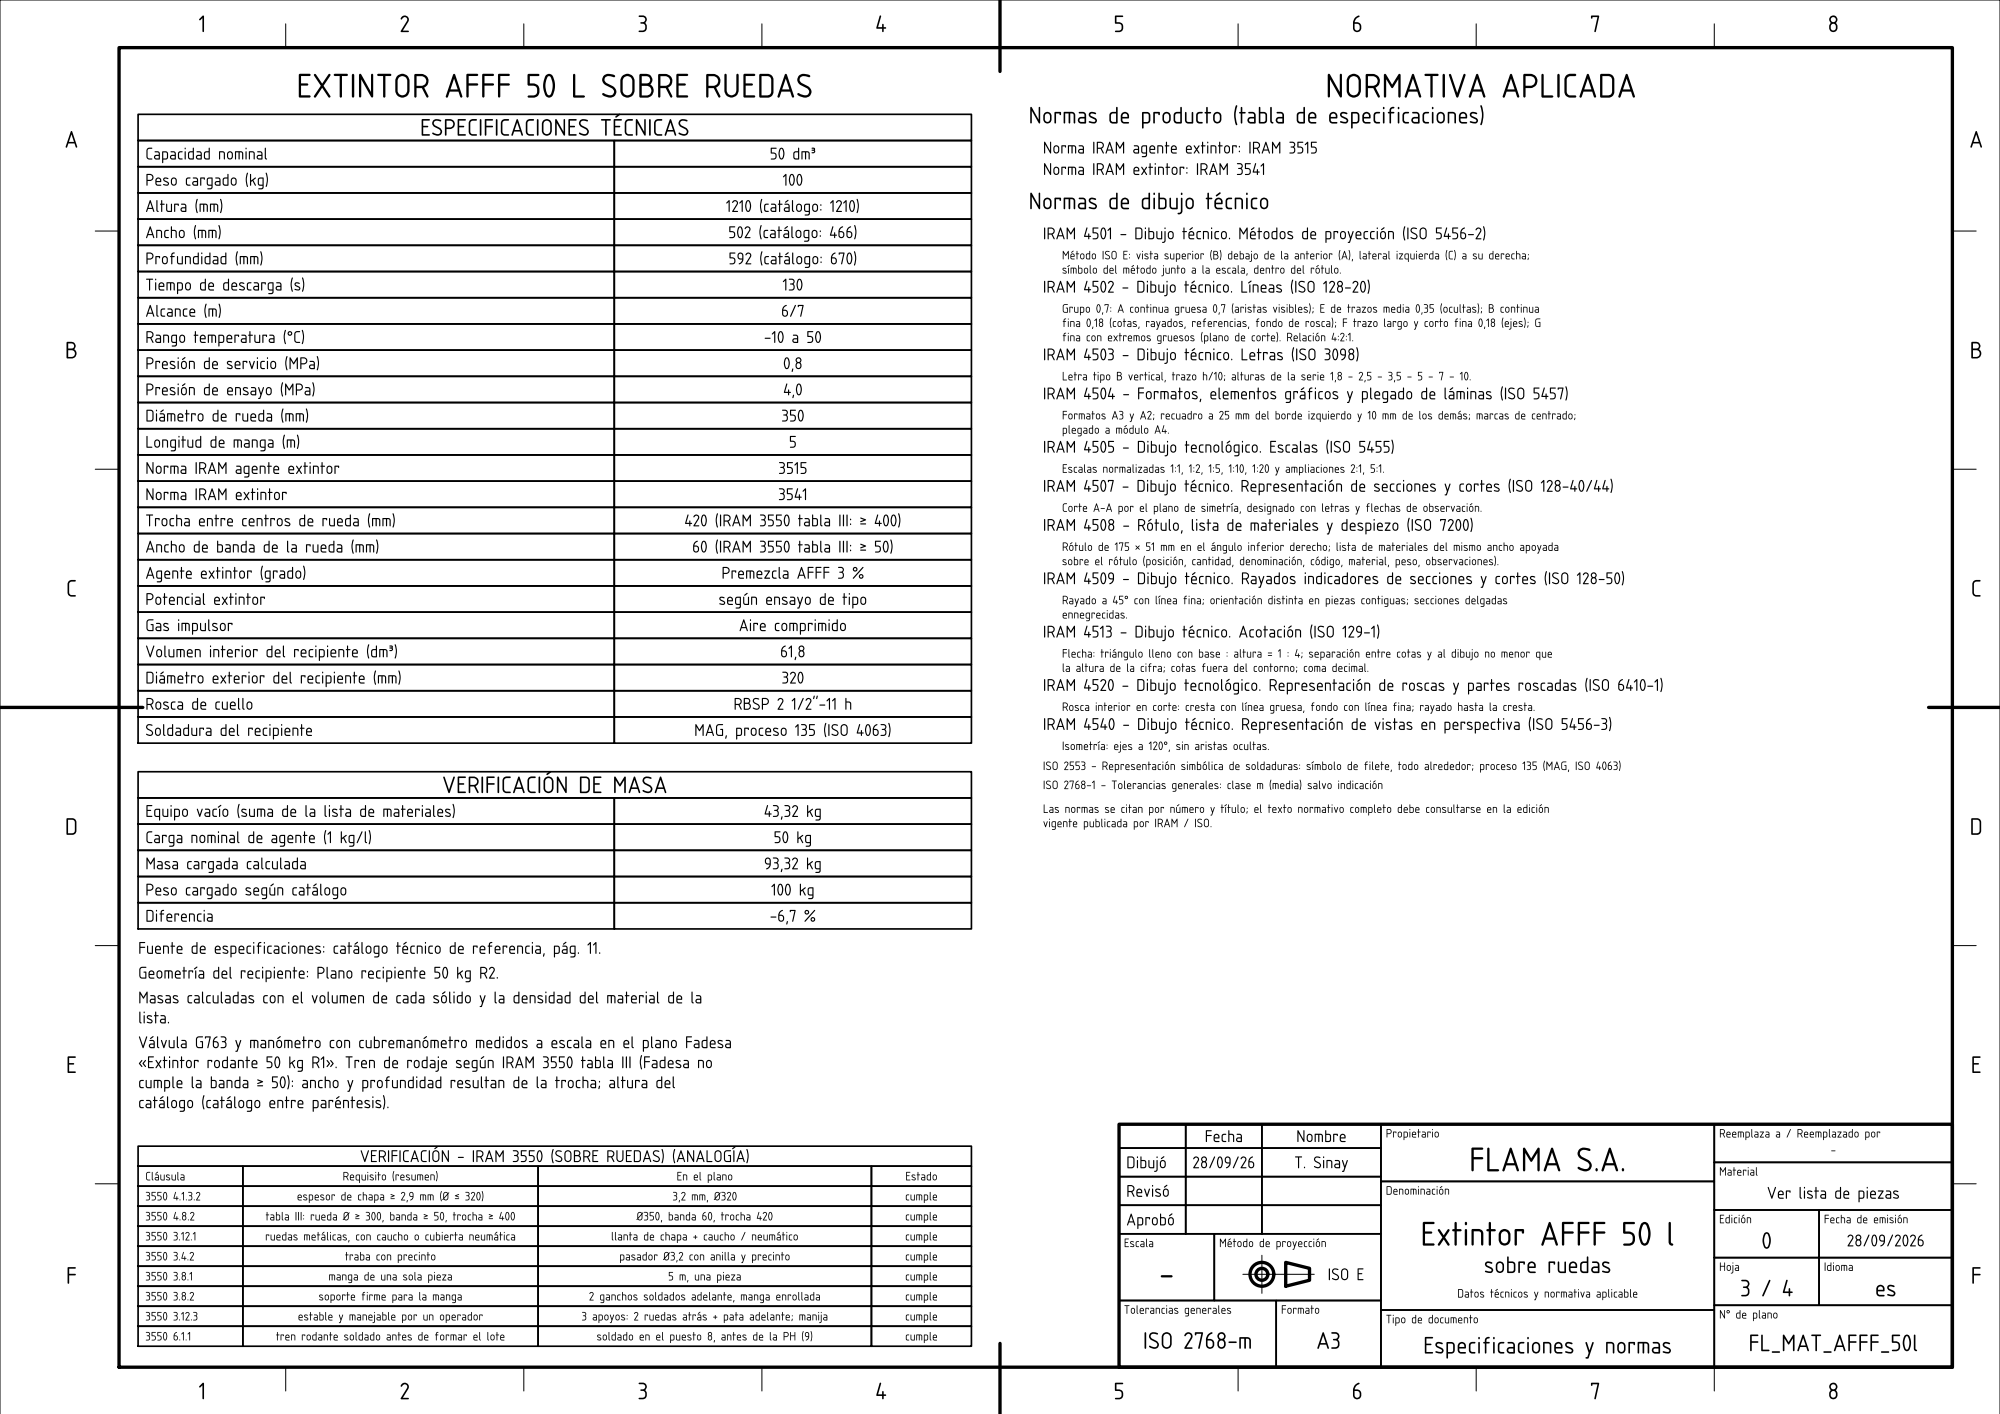
[picture p180: page 3]

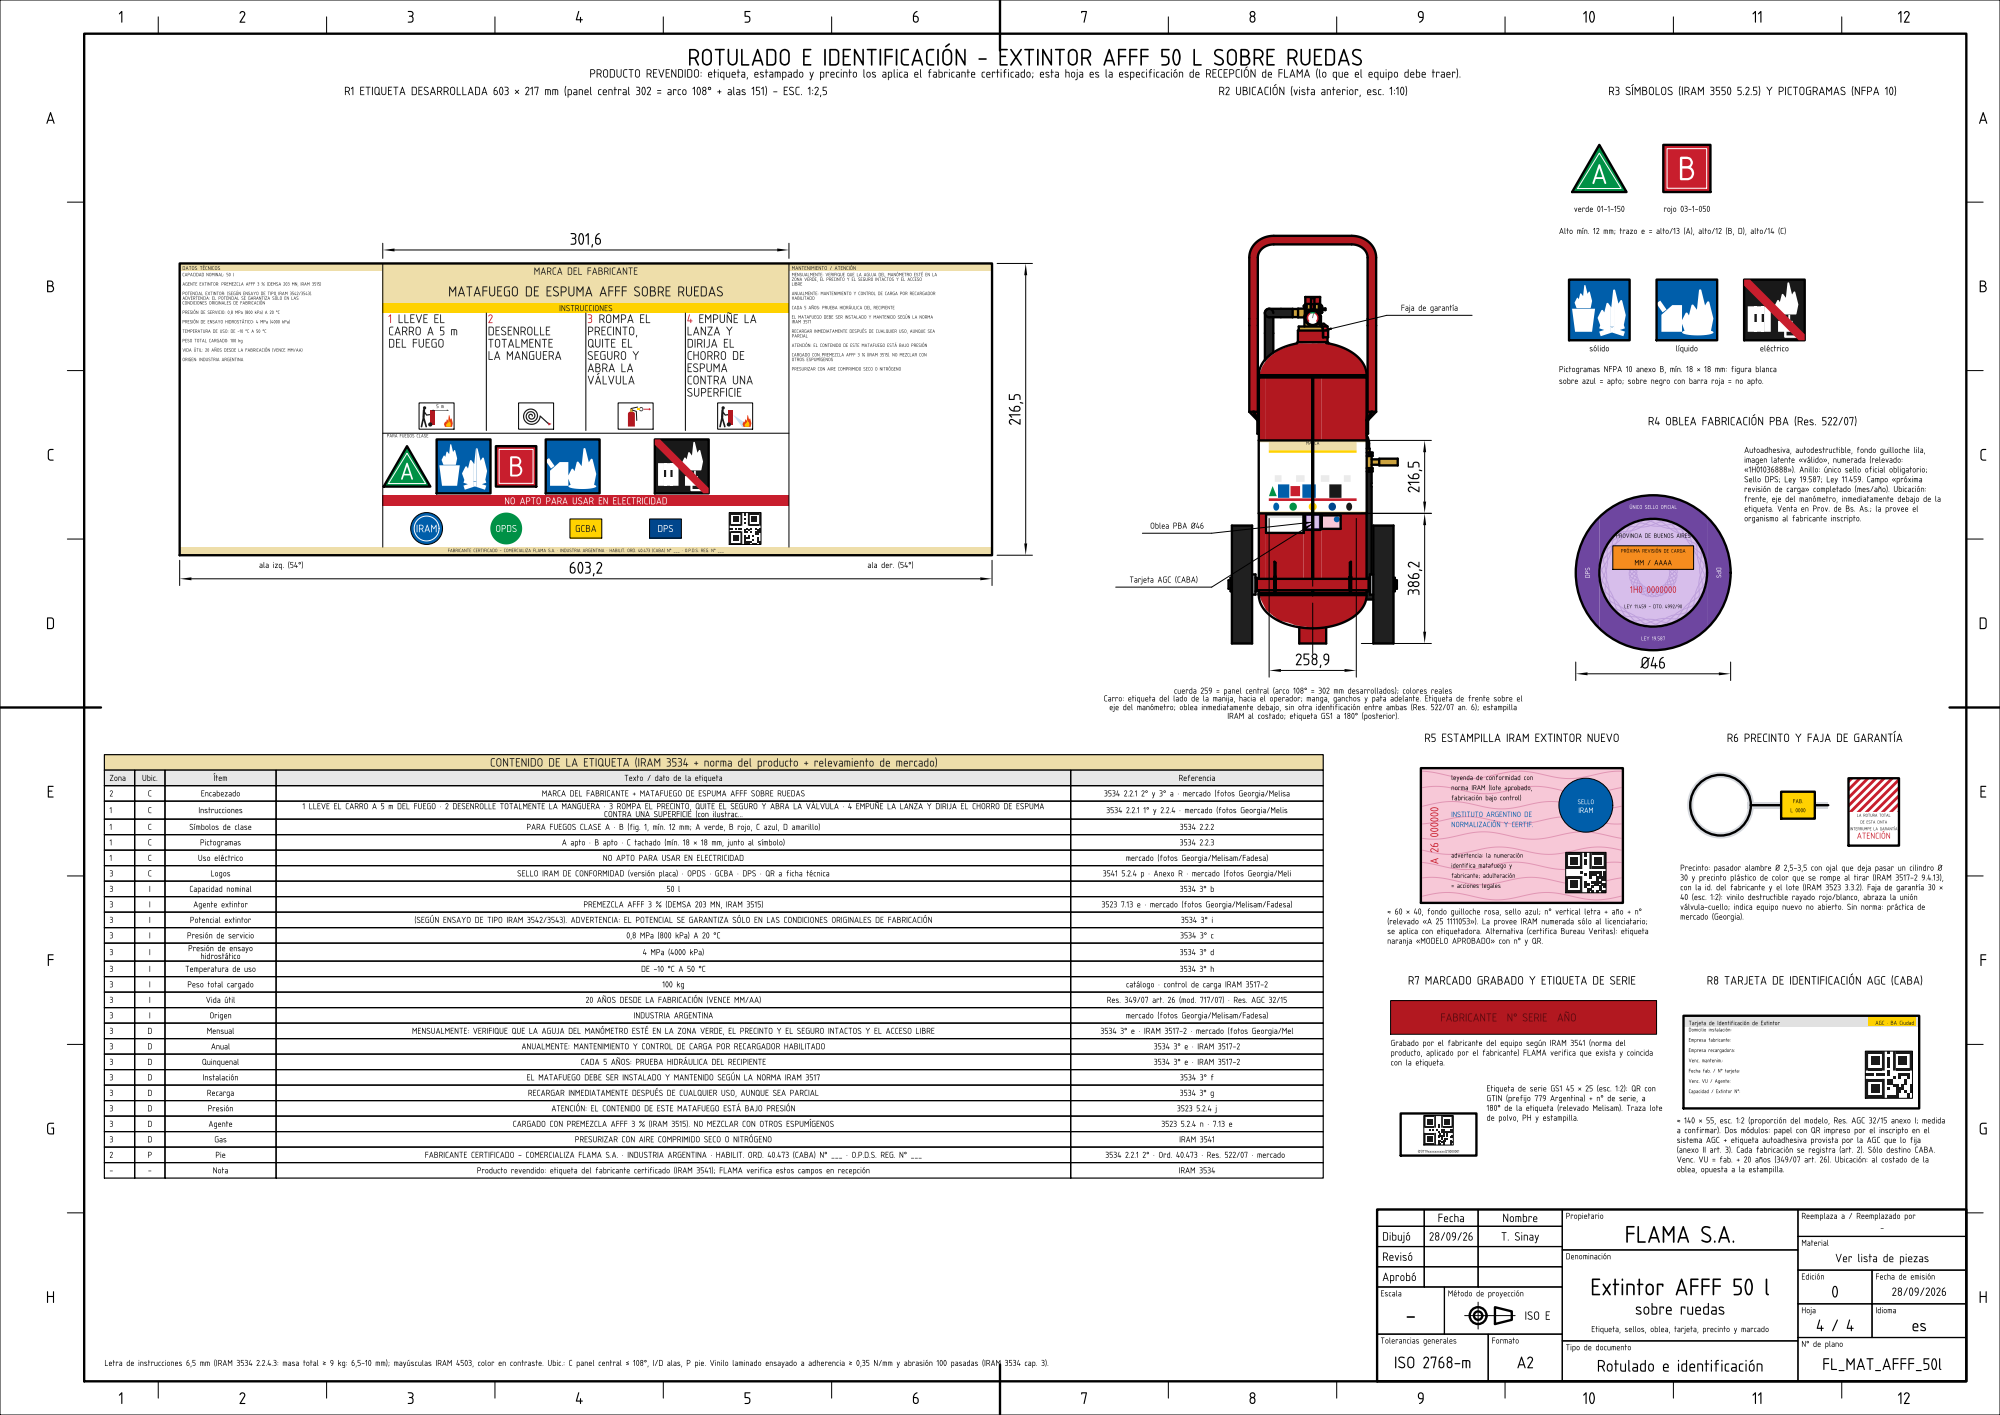
[picture p181: page 4]
