TadeoSinay/planos_flama-/salida/FL_MAT_AGUA_10l/FL_MAT_AGUA_10l.pdf

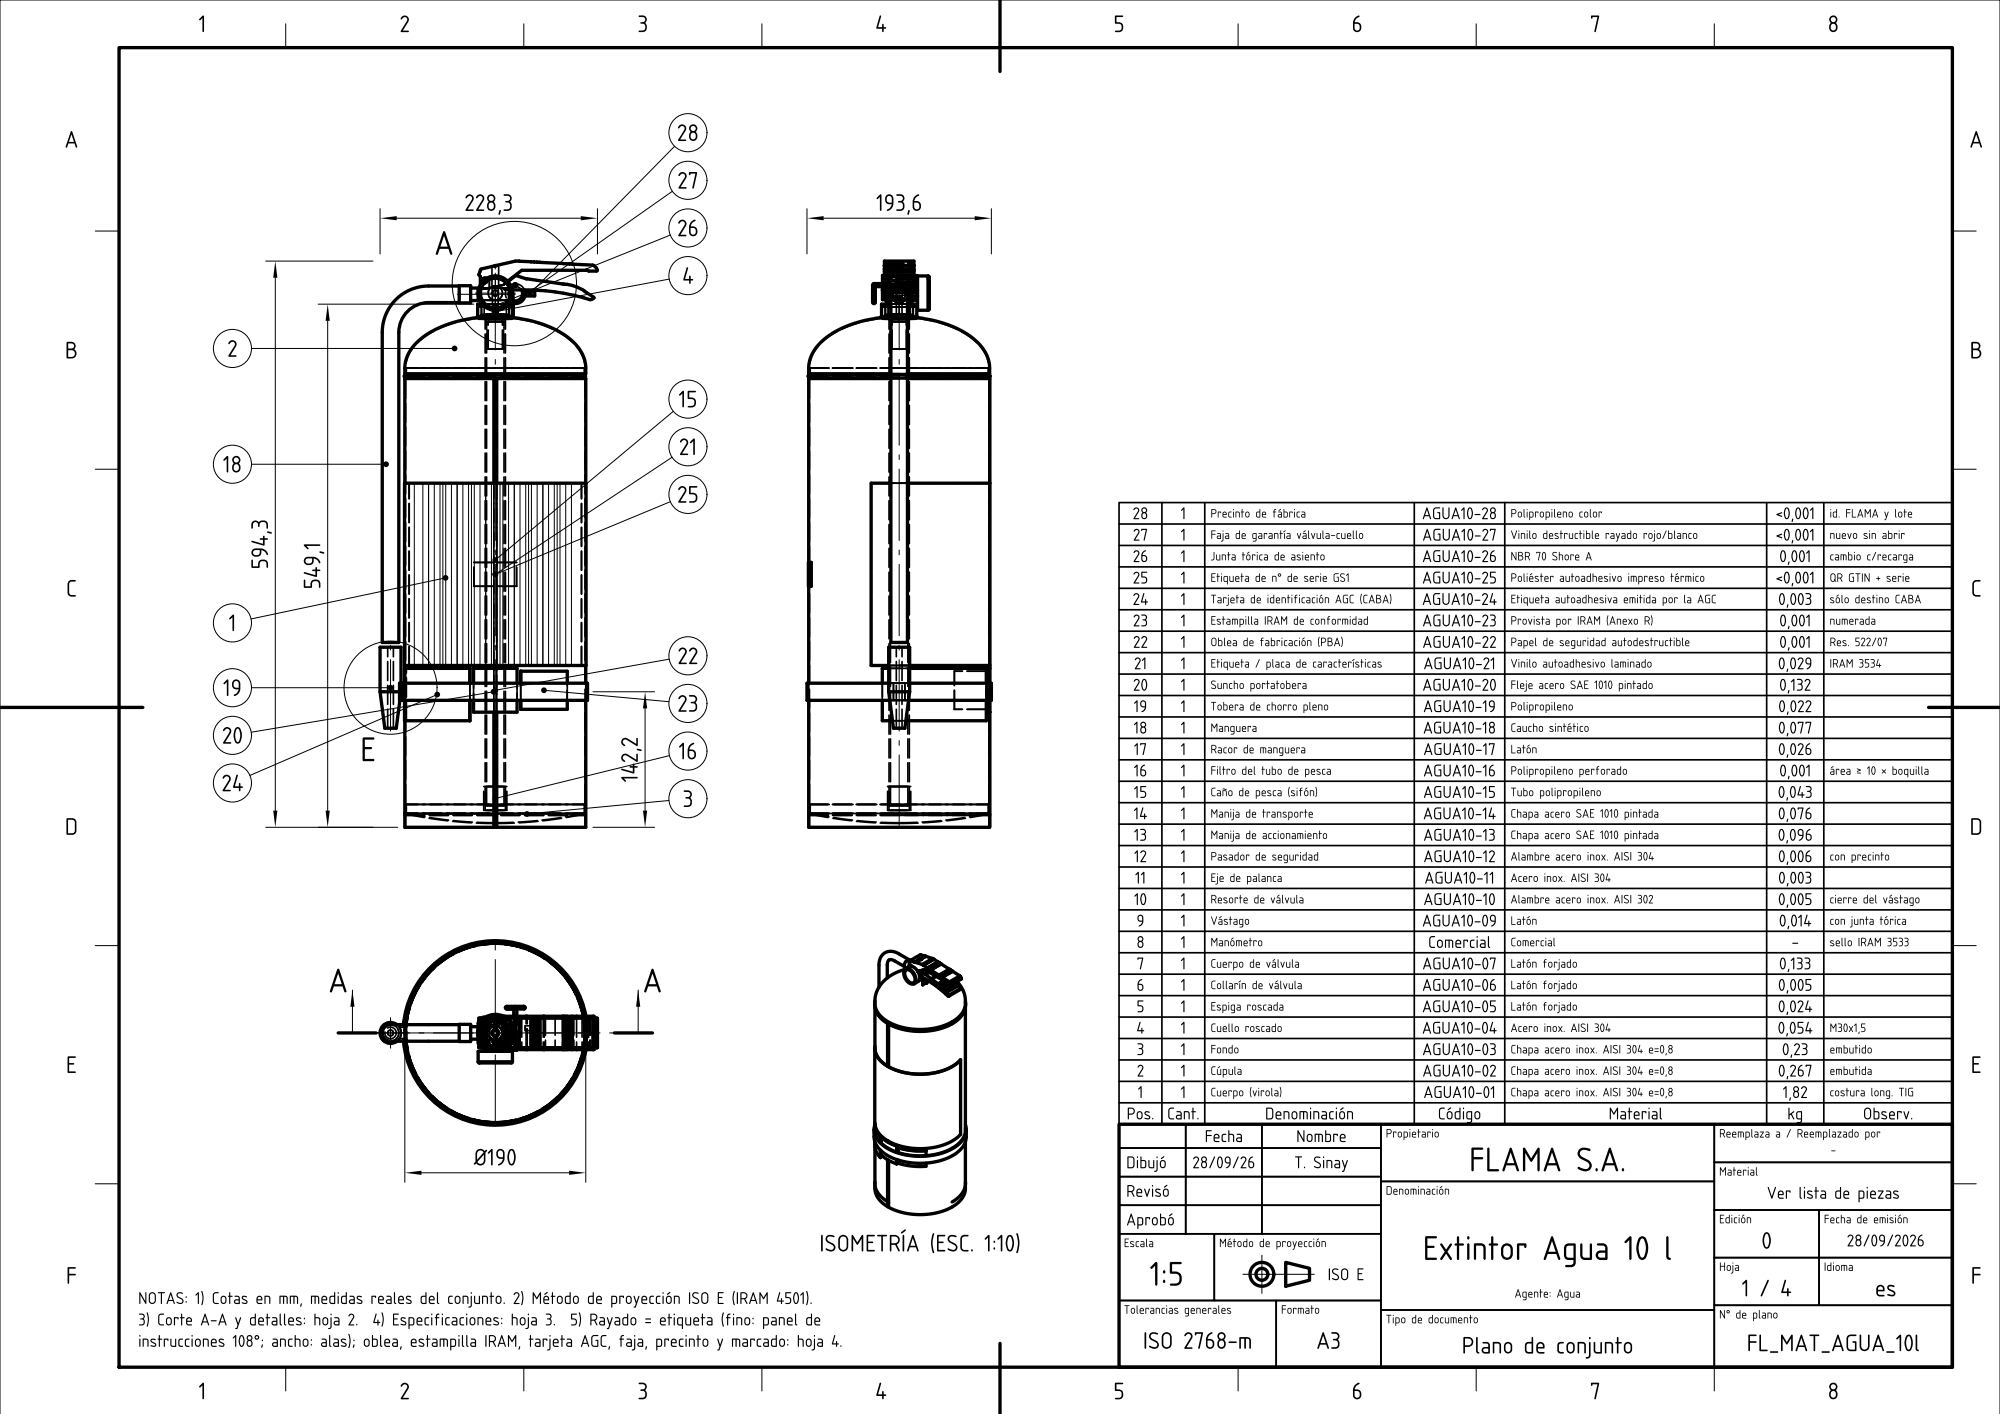
[picture p182: page 1]

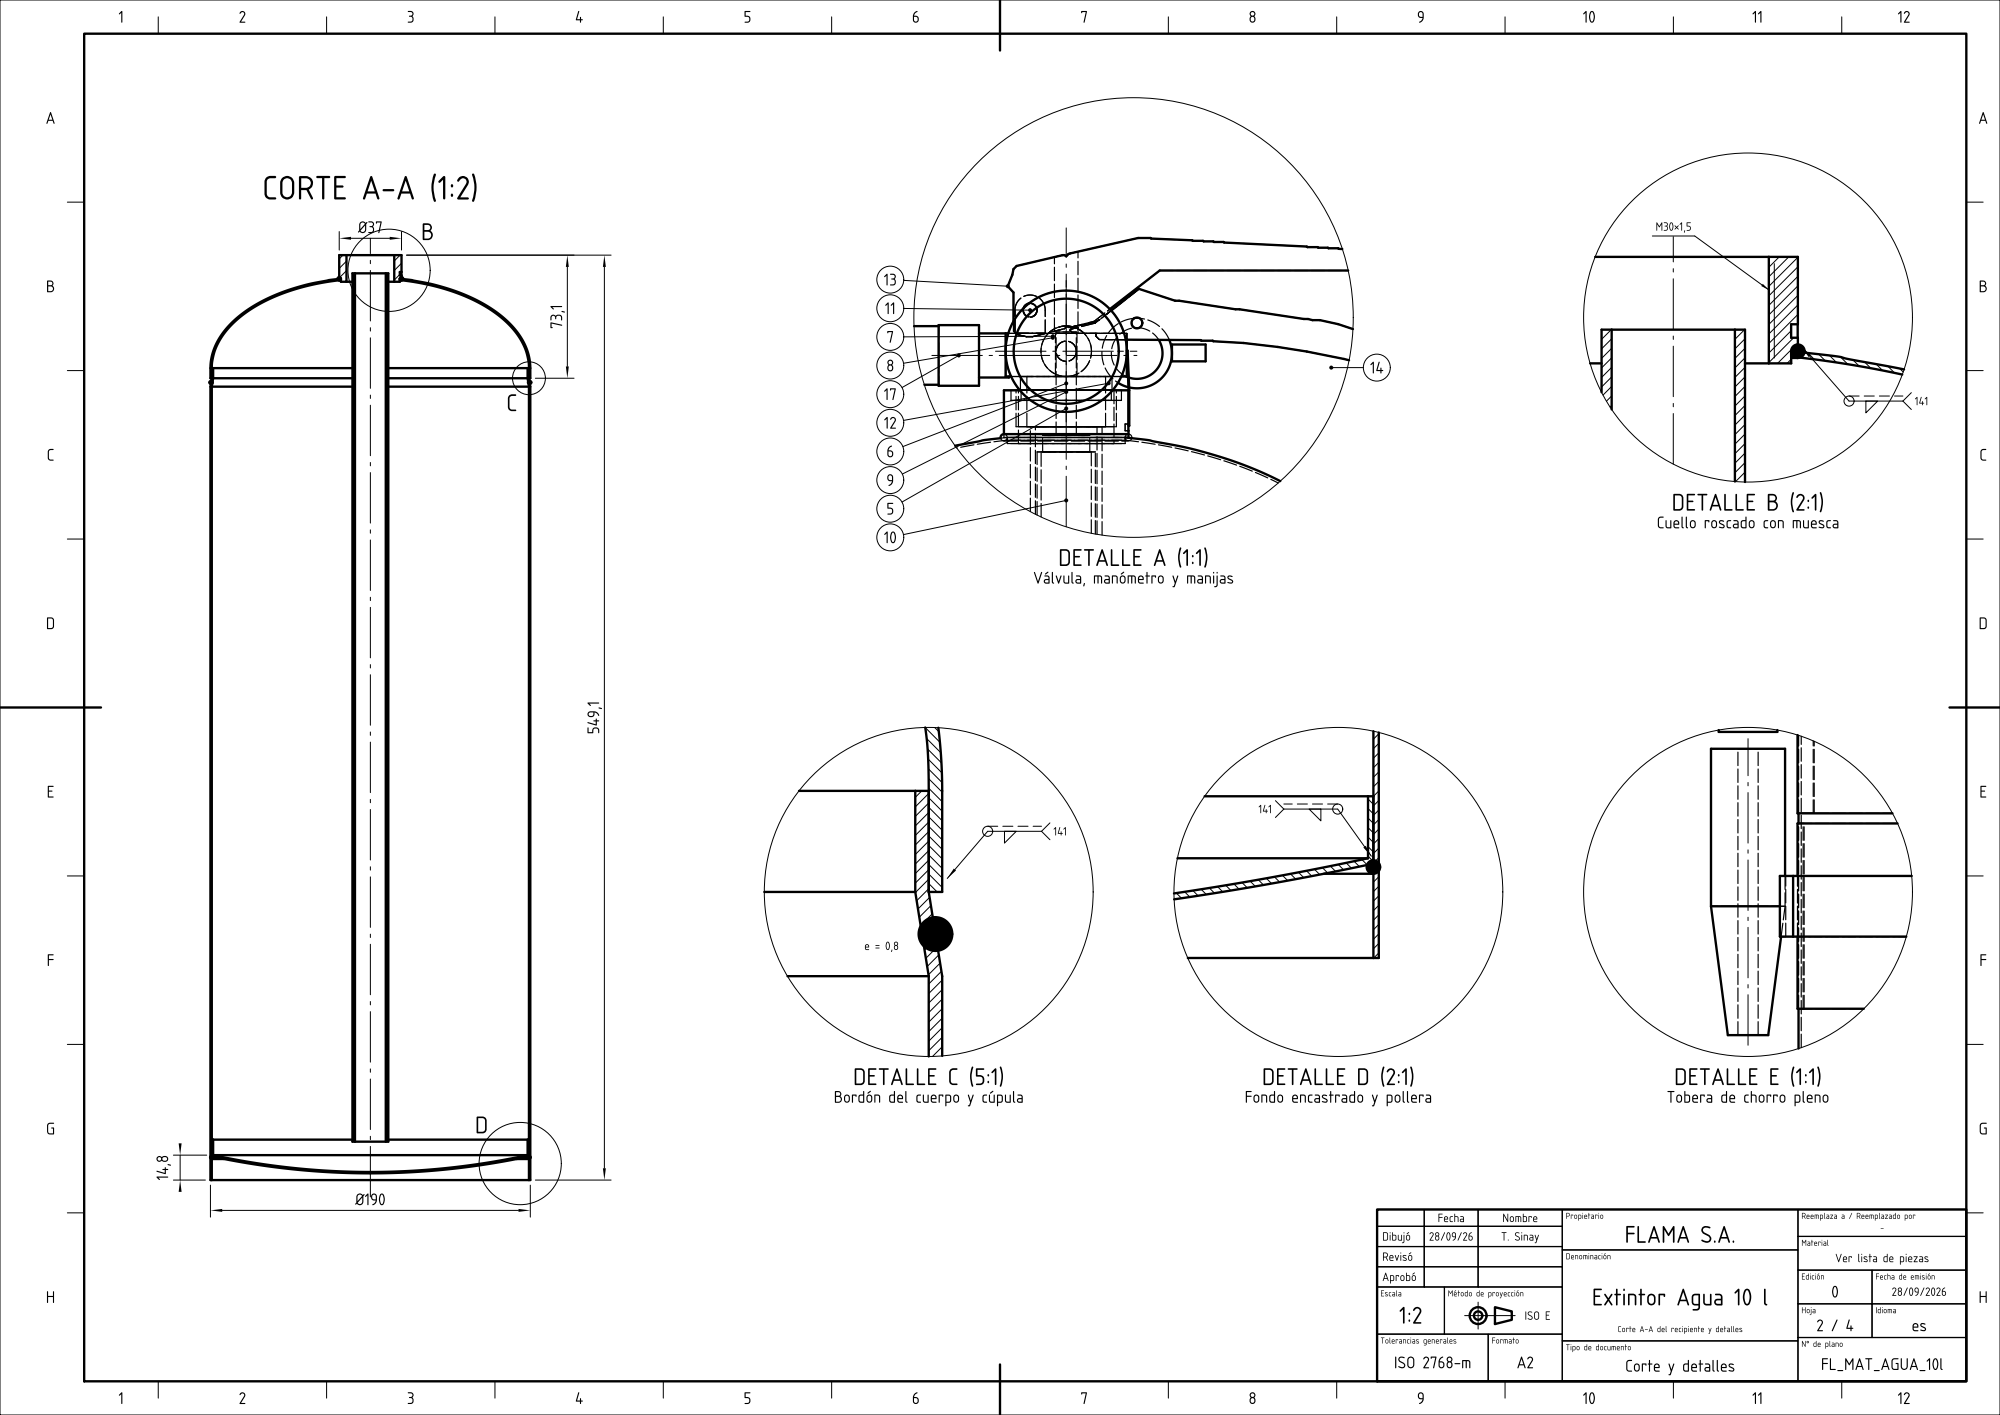
[picture p183: page 2]

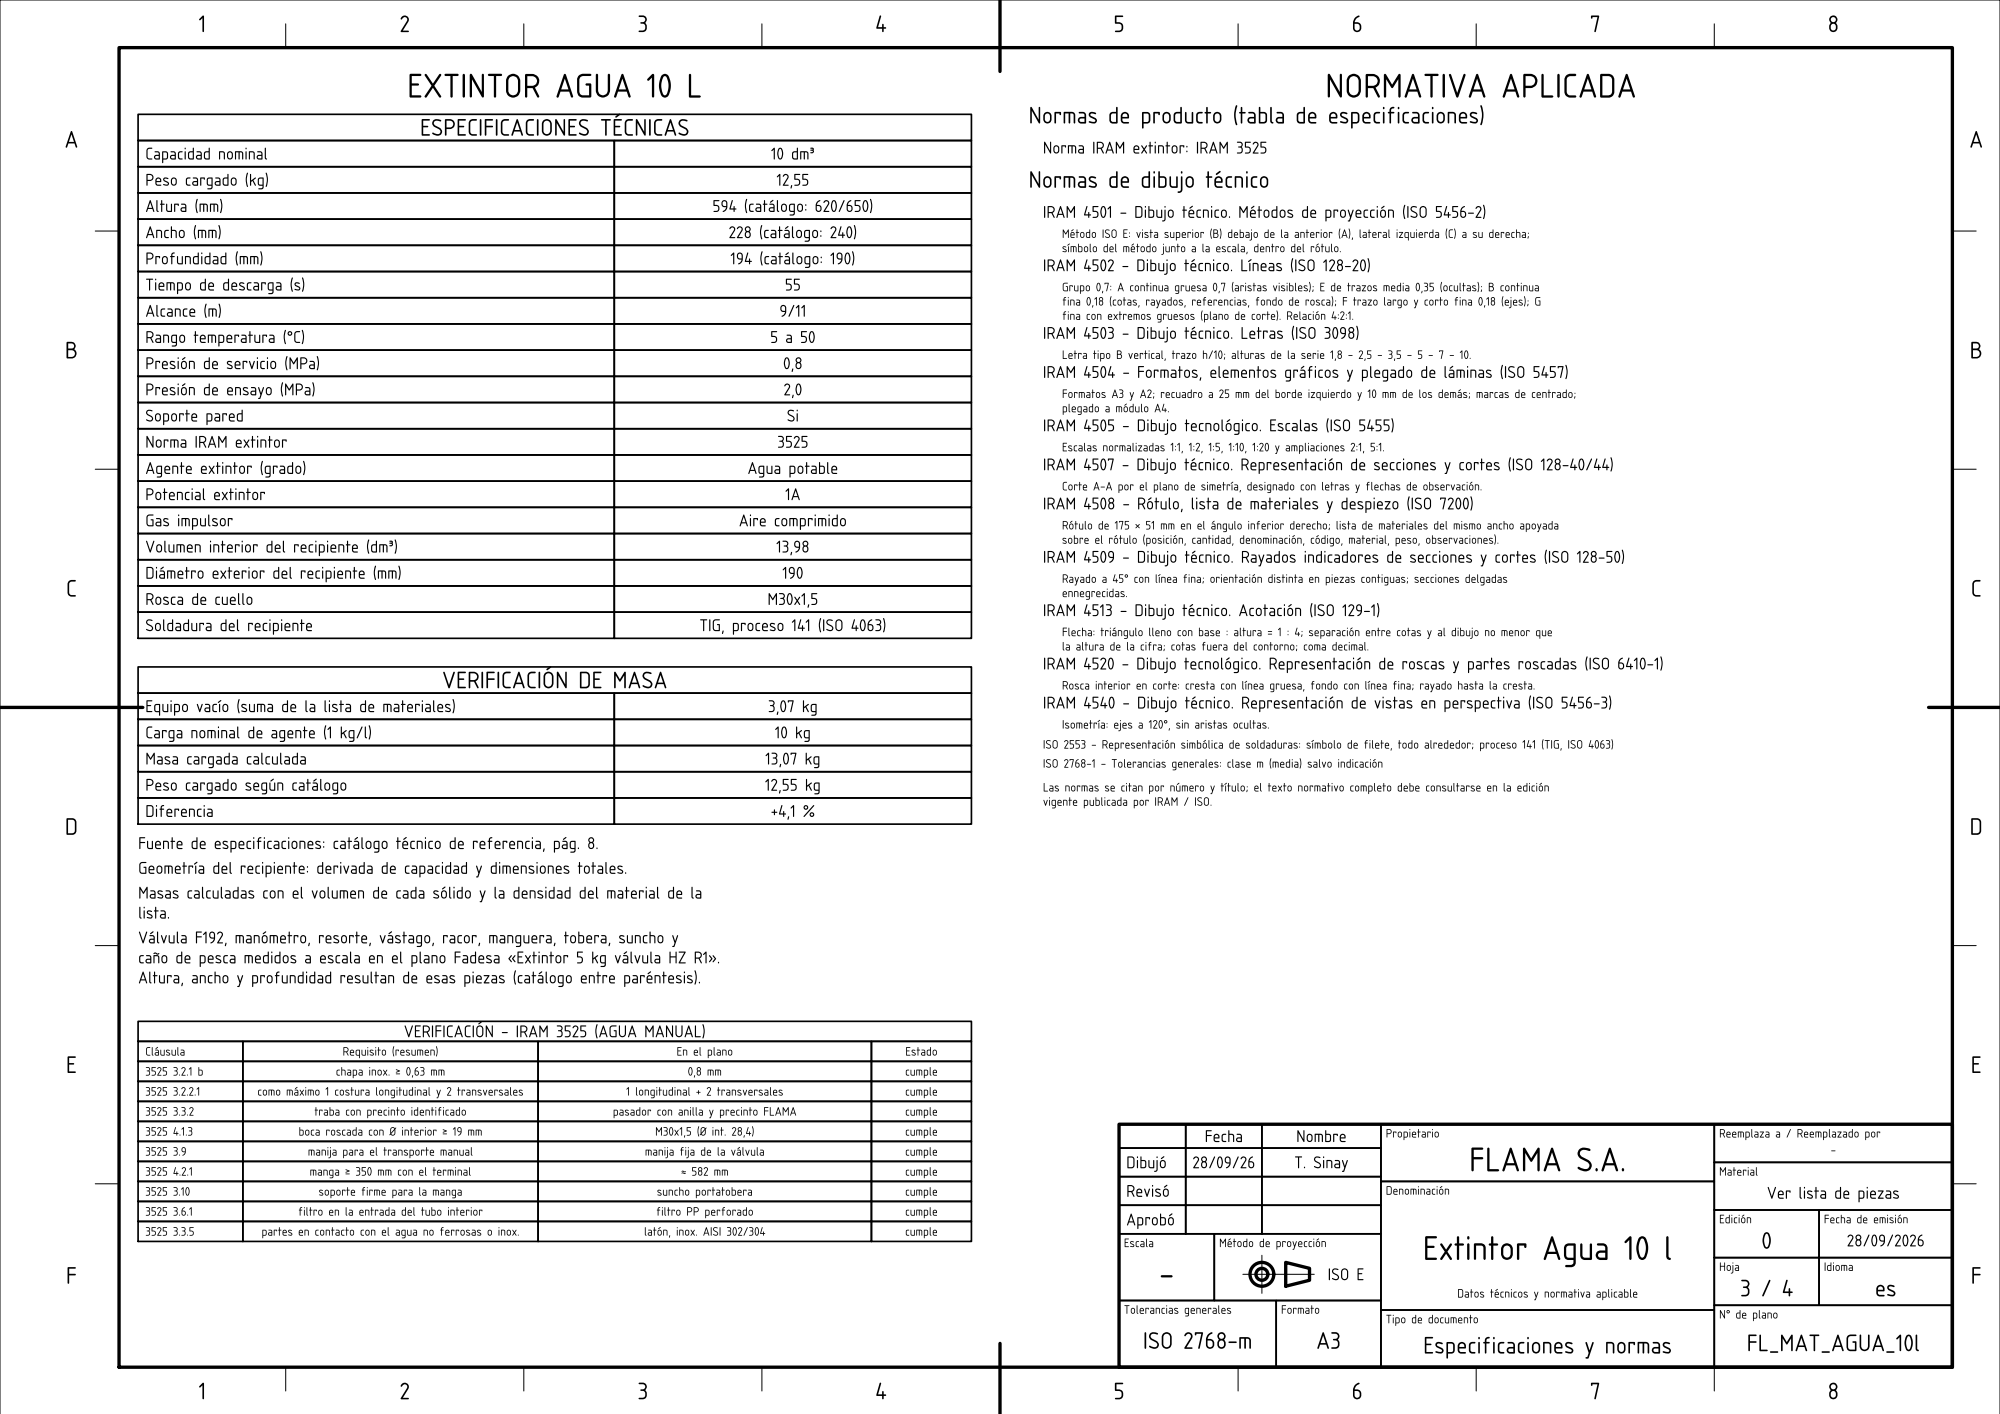
[picture p184: page 3]

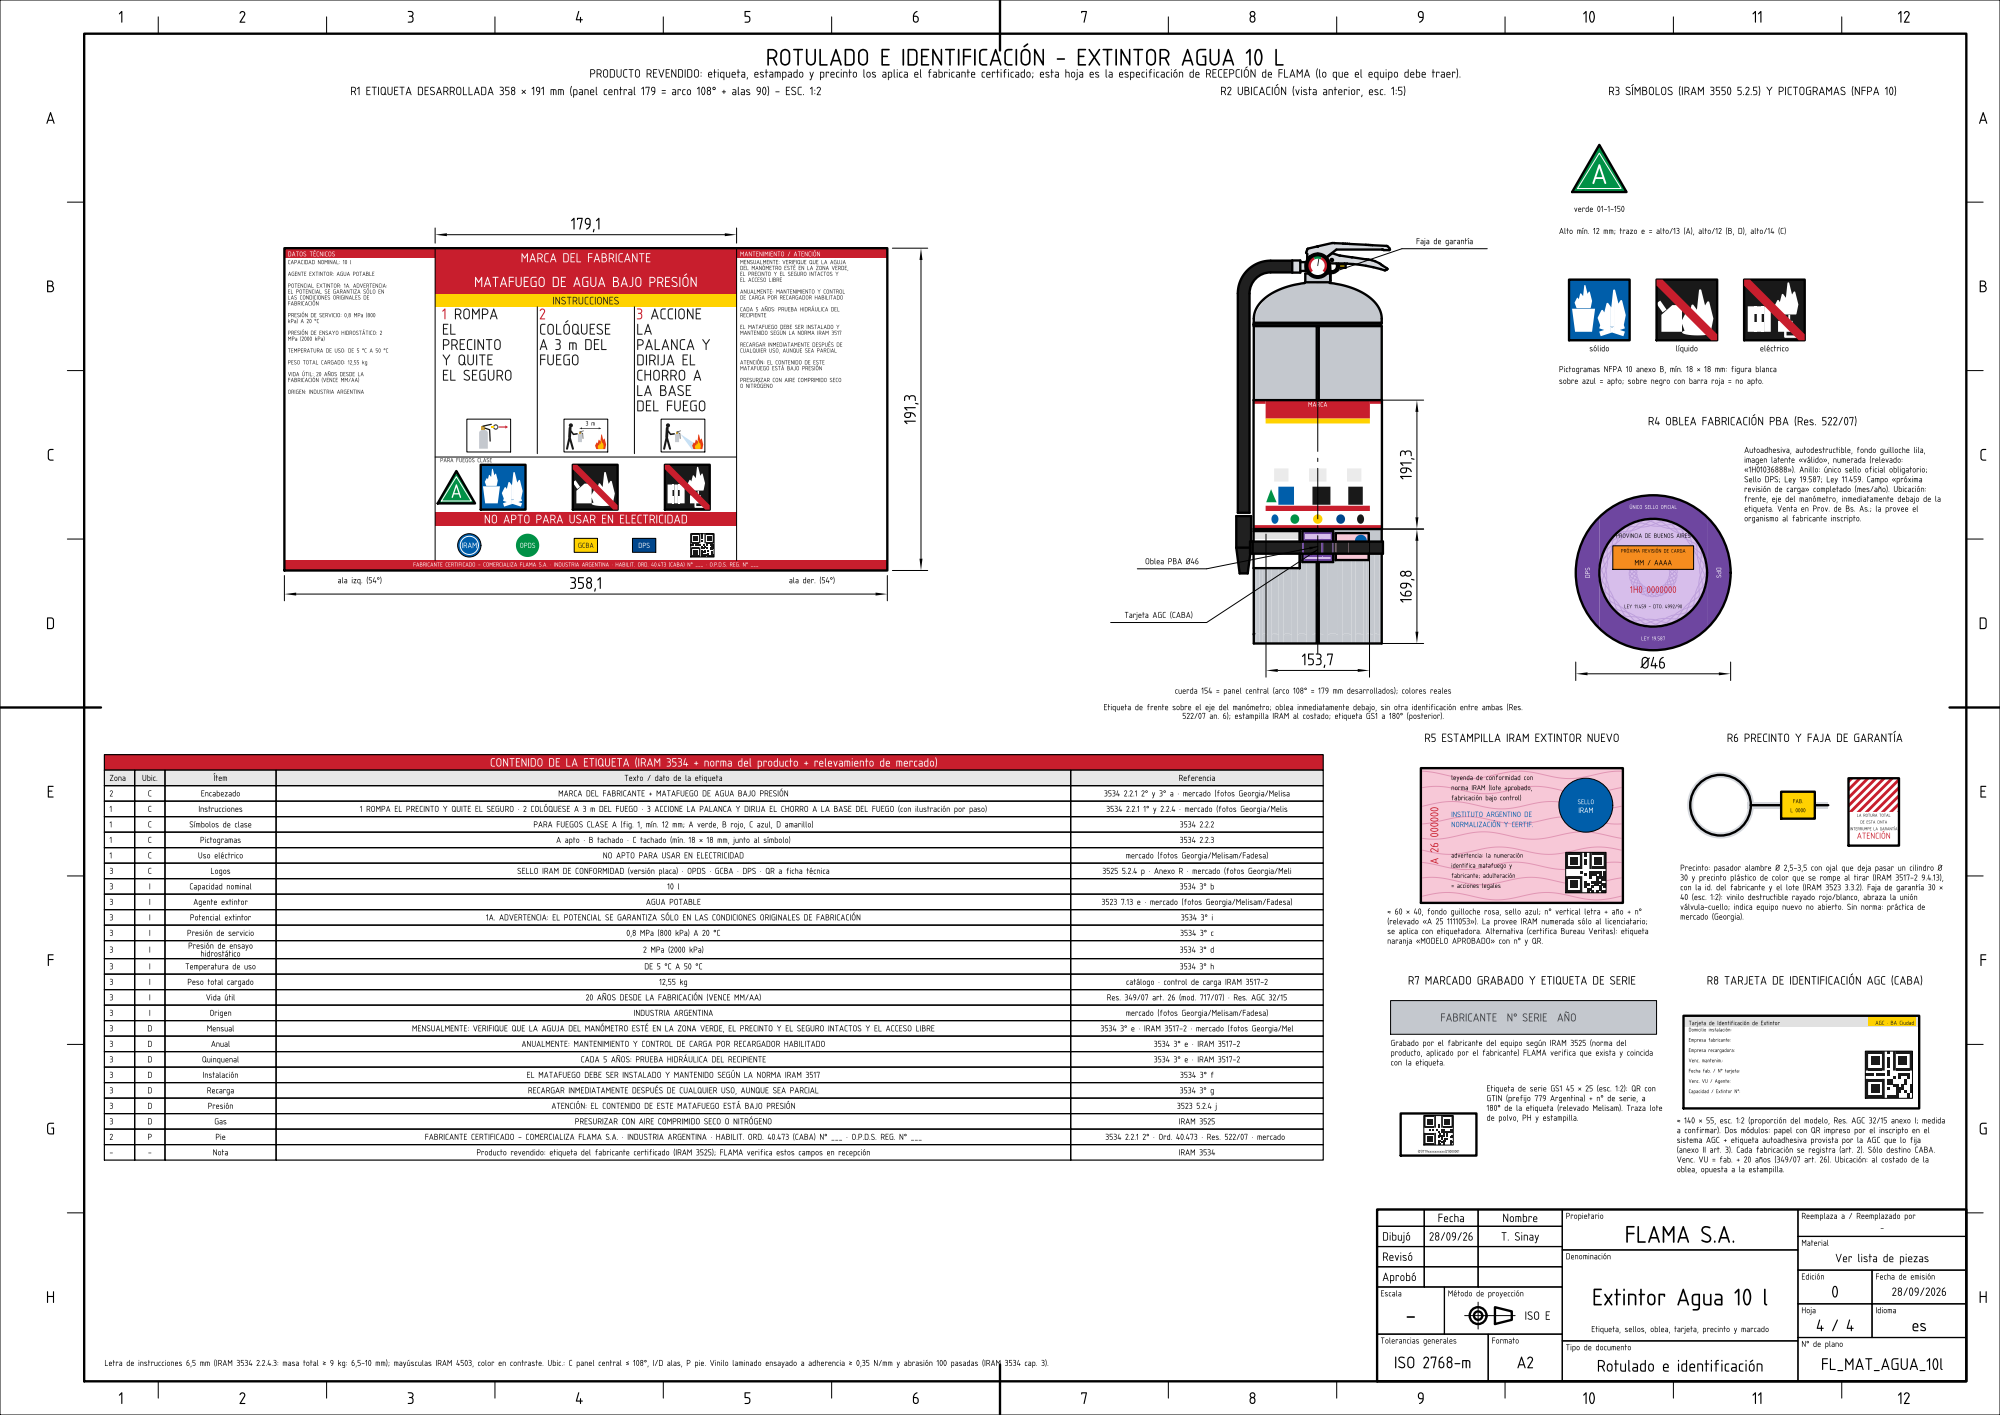
[picture p185: page 4]
