TadeoSinay/planos_flama-/salida/FL_MAT_BC_5kg/FL_MAT_BC_5kg.pdf

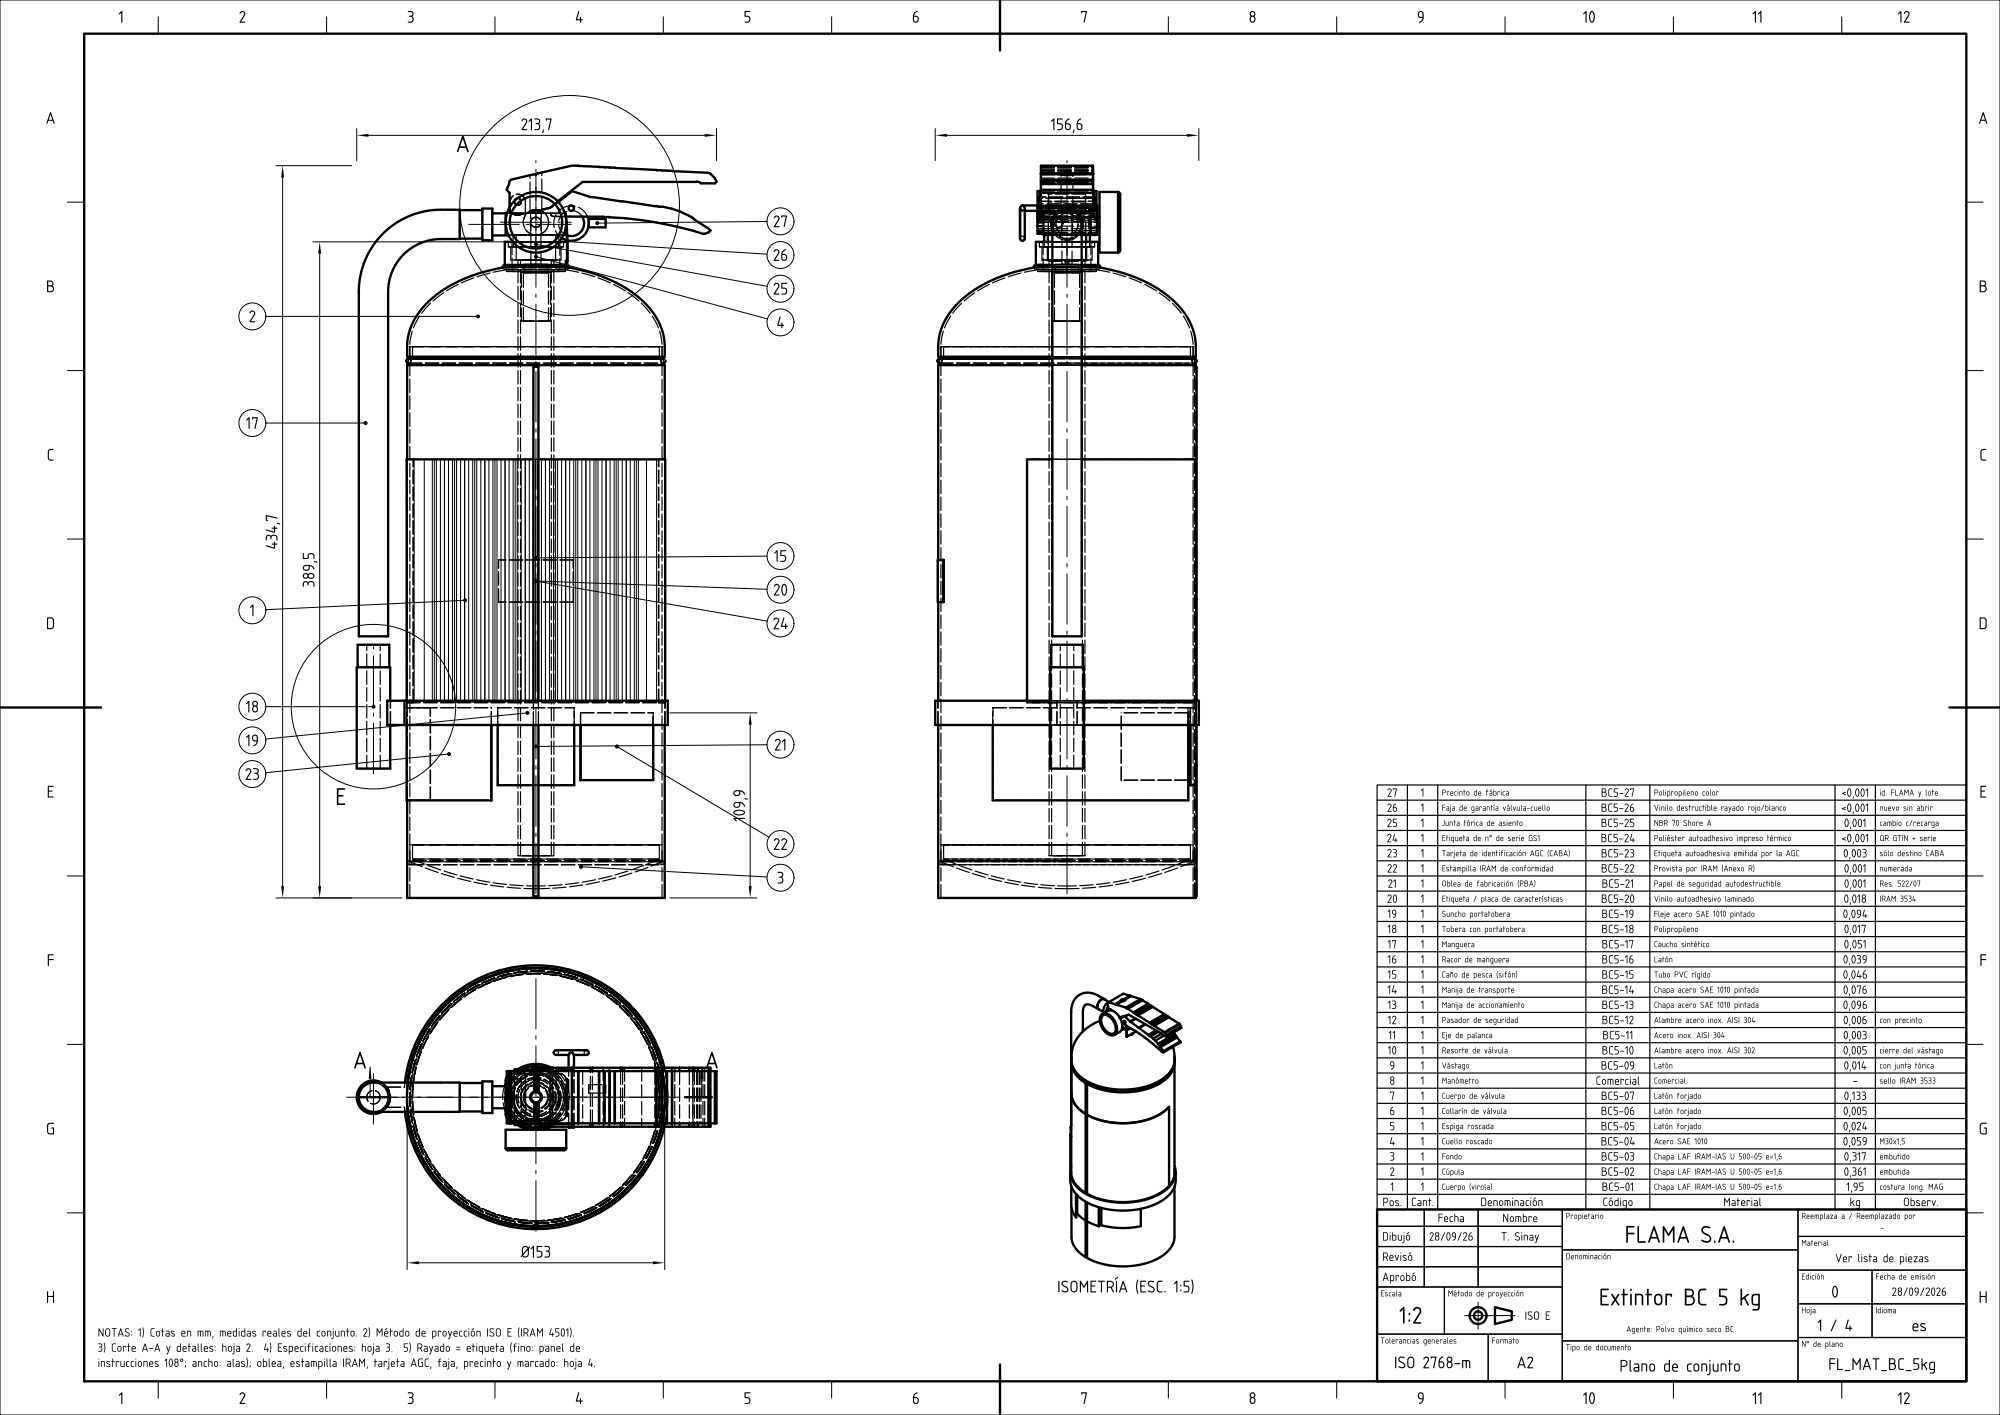
[picture p186: page 1]

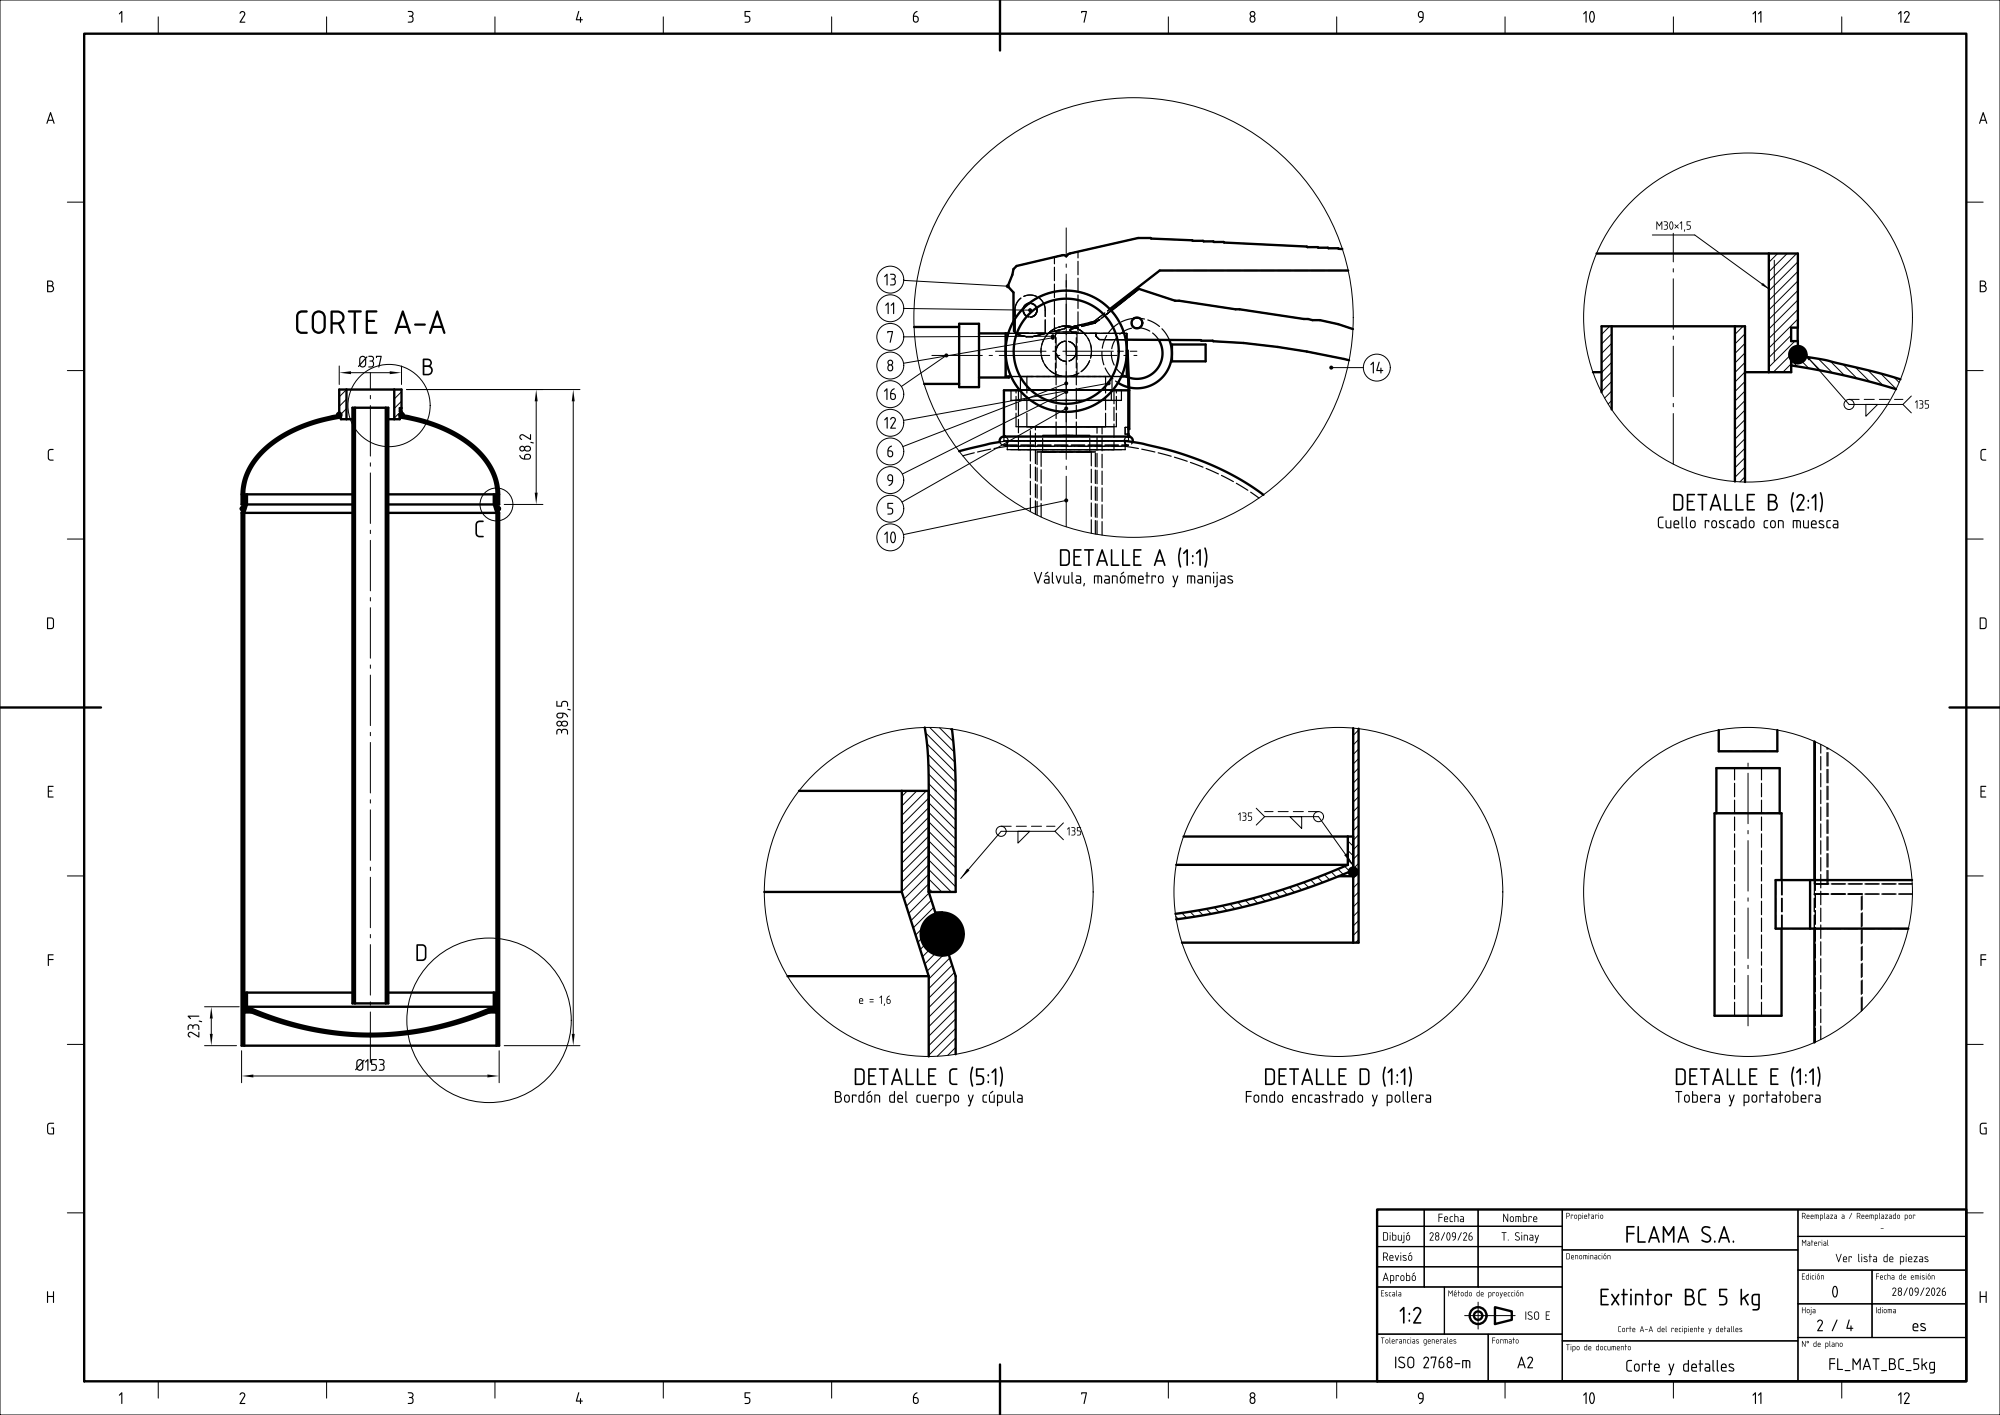
[picture p187: page 2]

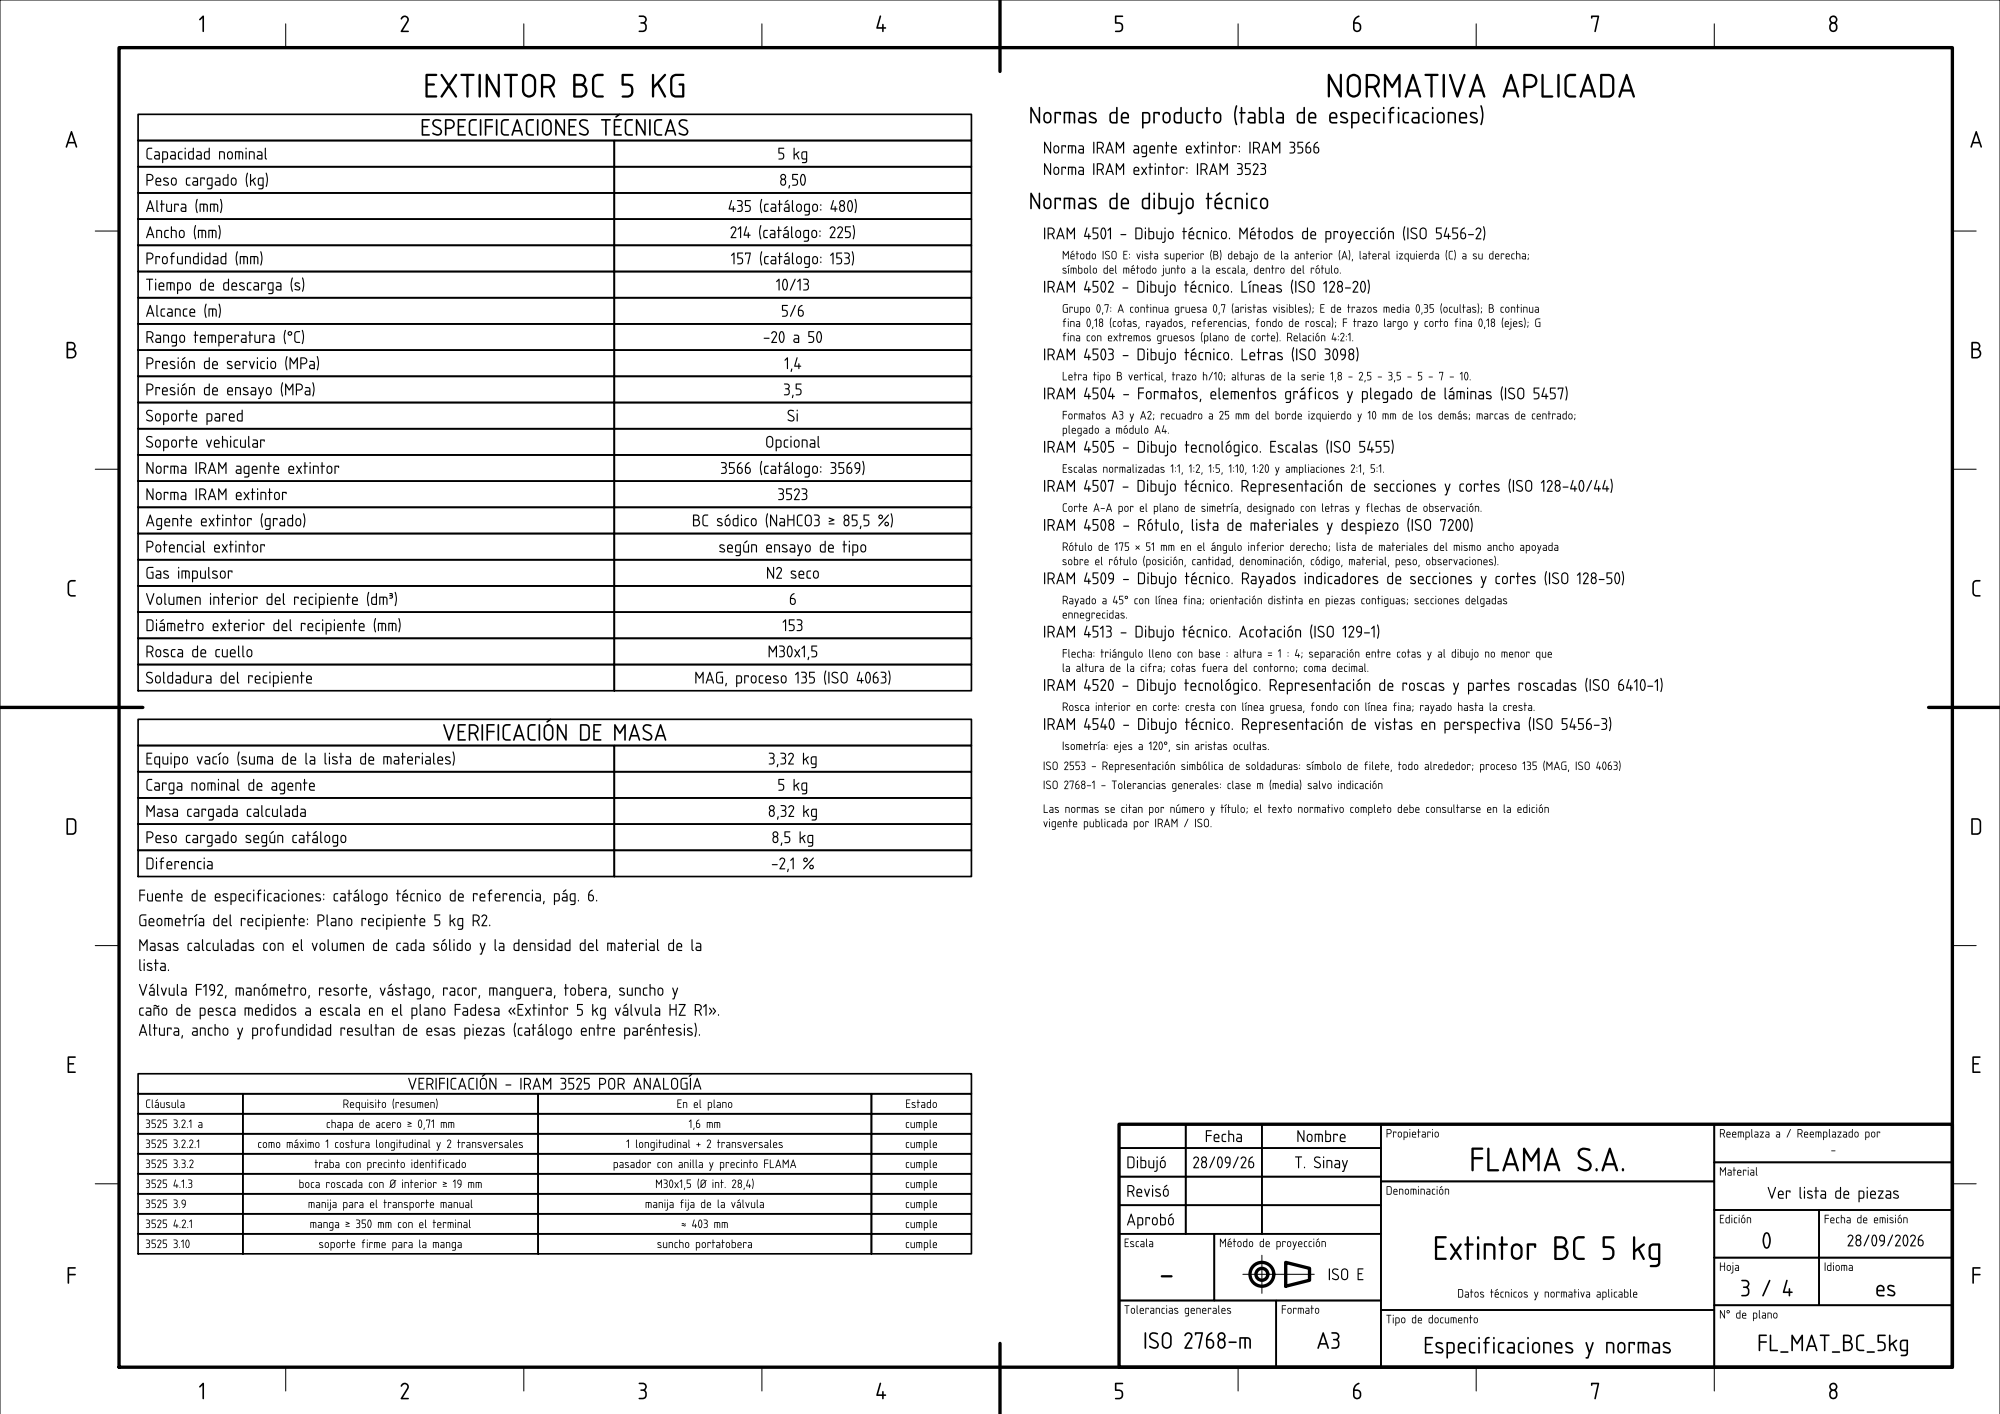
[picture p188: page 3]

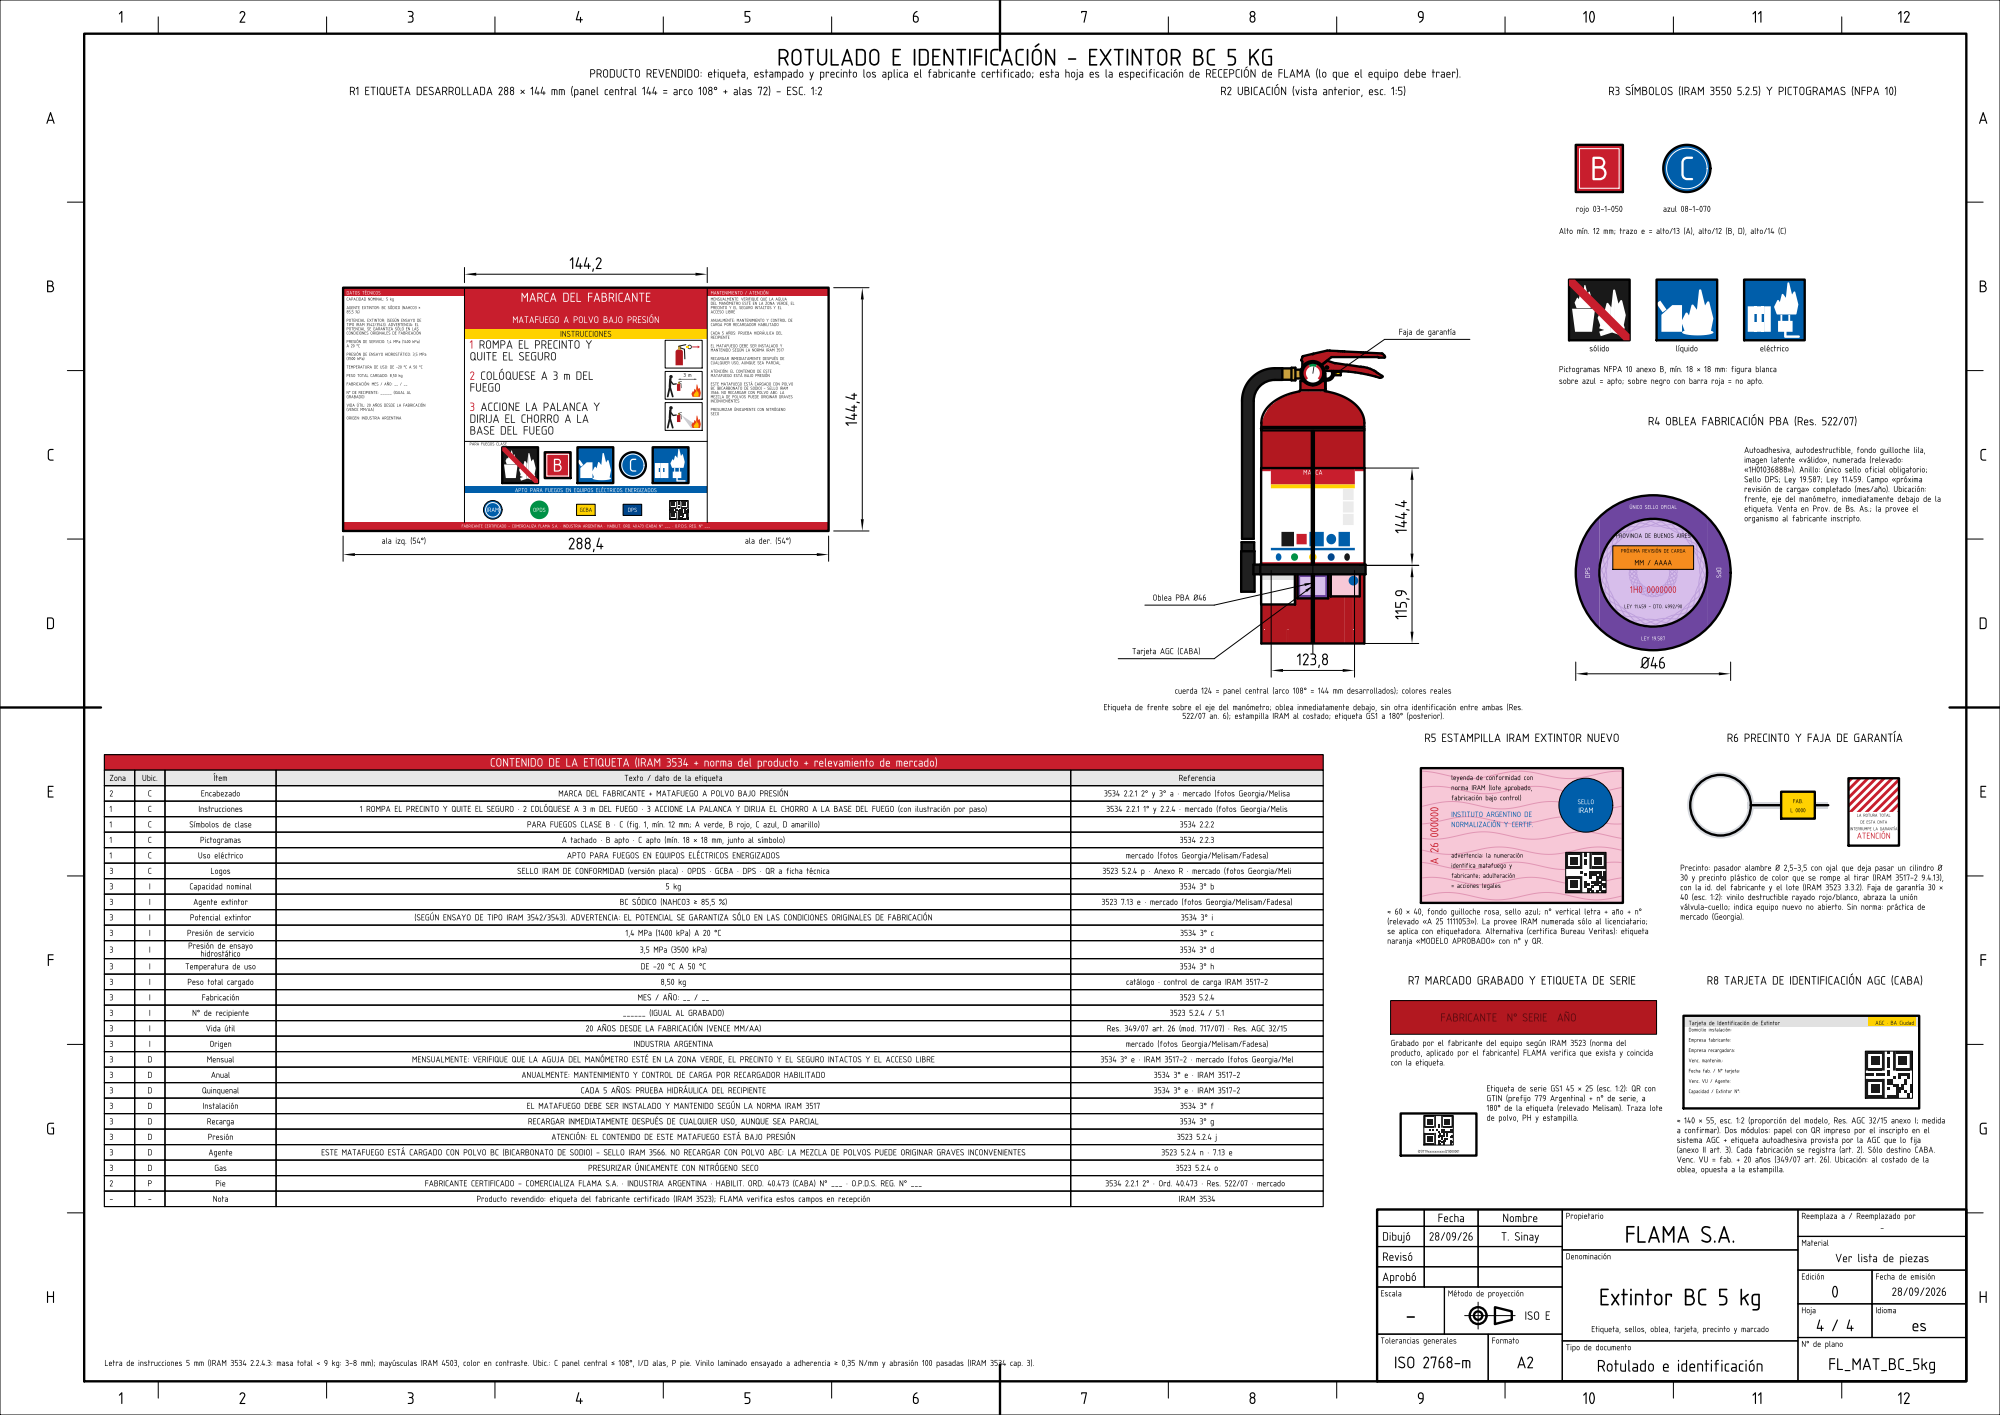
[picture p189: page 4]
