TadeoSinay/planos_flama-/salida/FL_MAT_CLASED_9l/FL_MAT_CLASED_9l.pdf

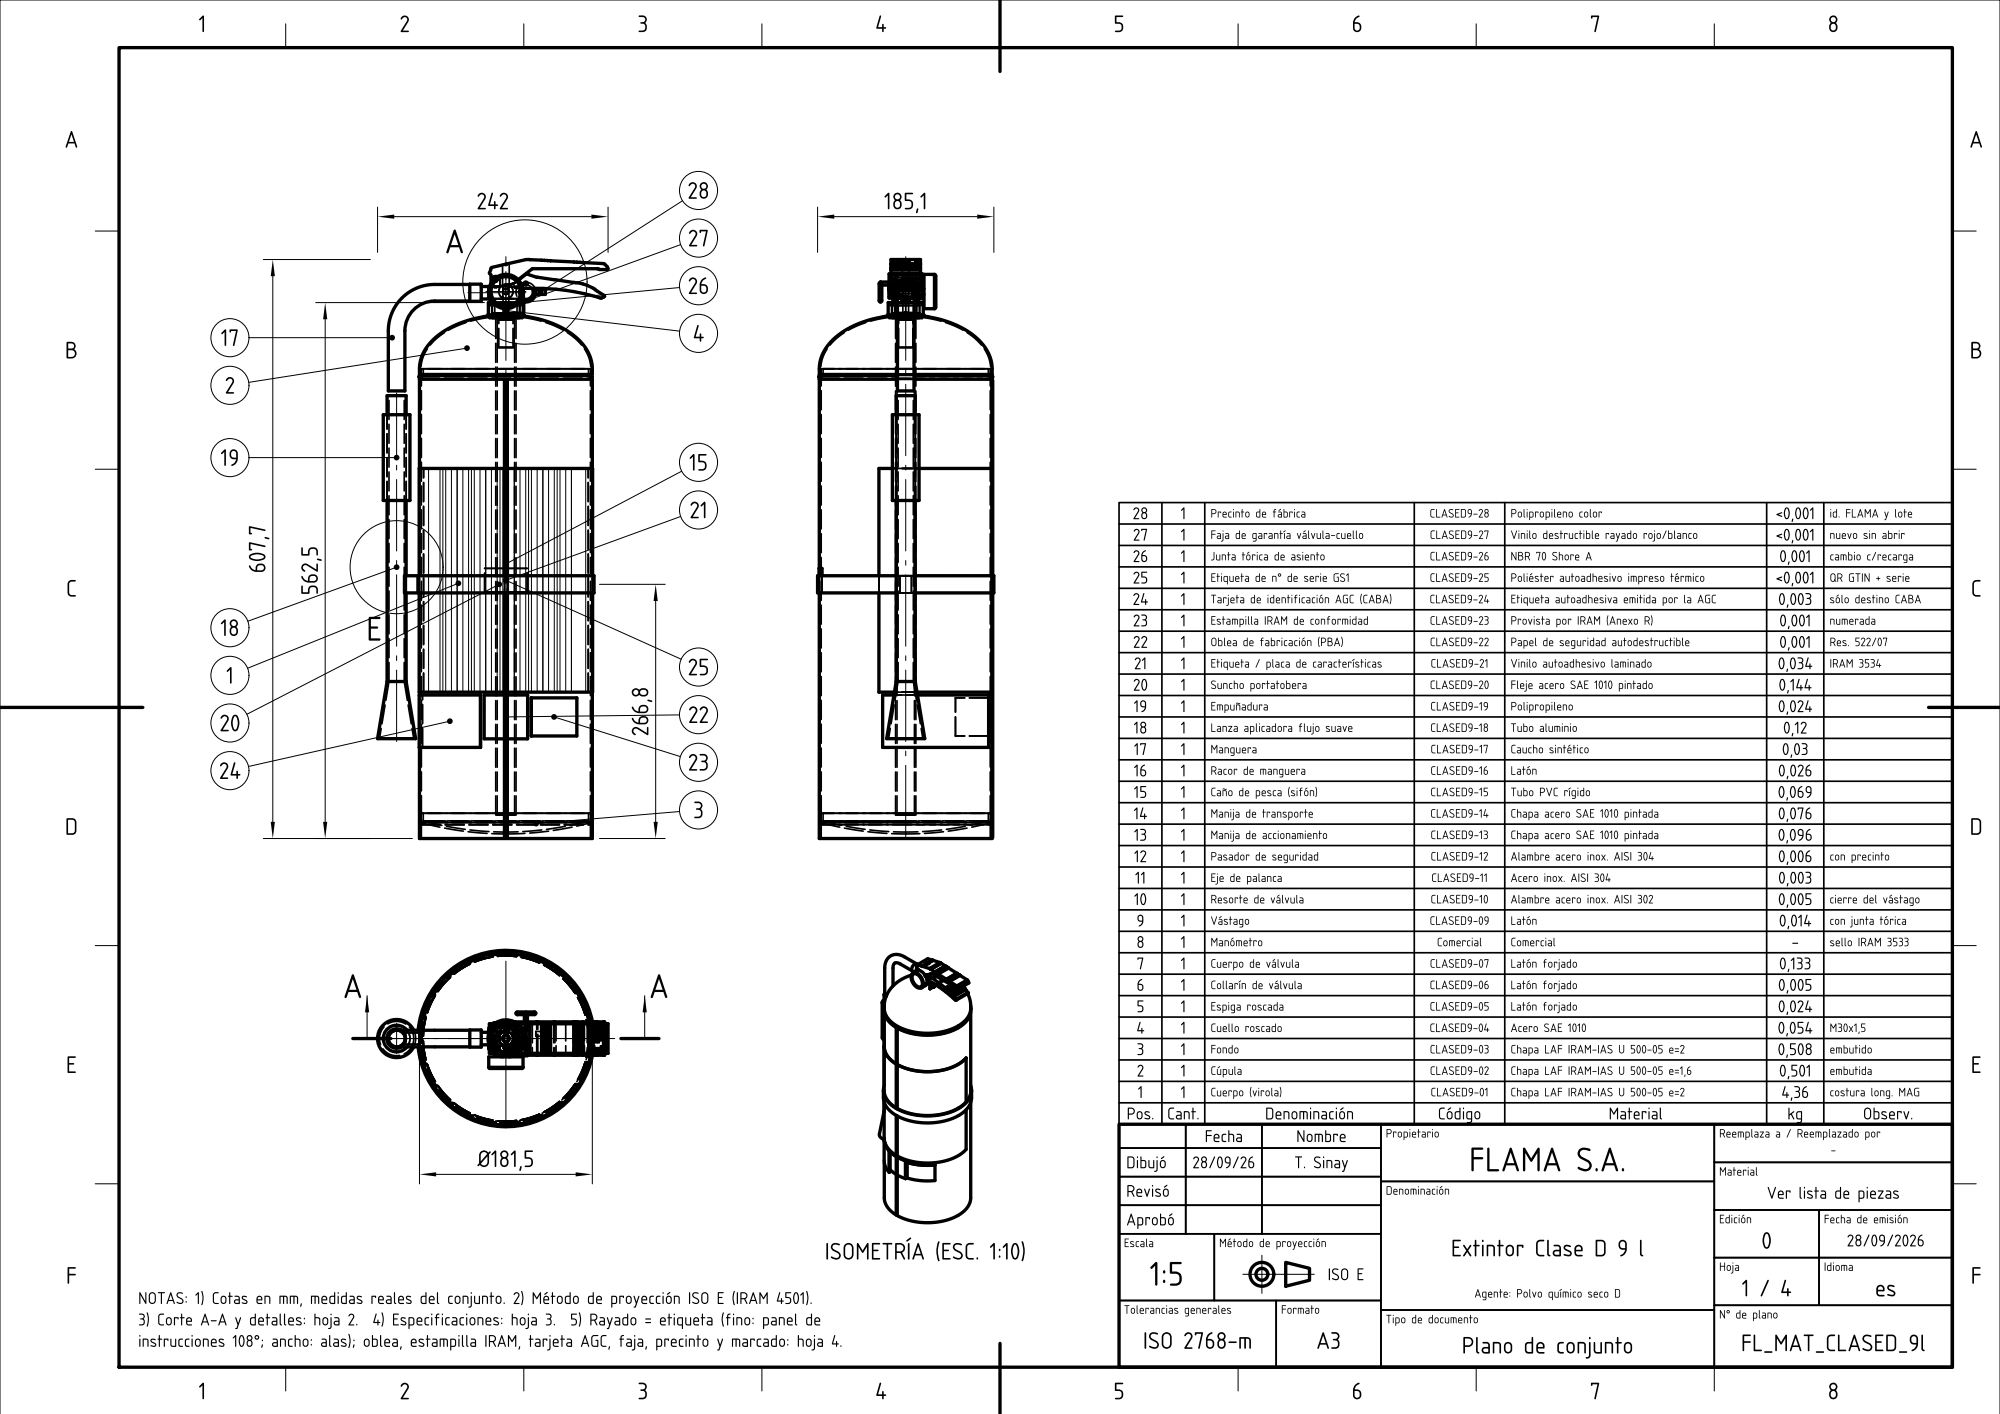
[picture p190: page 1]

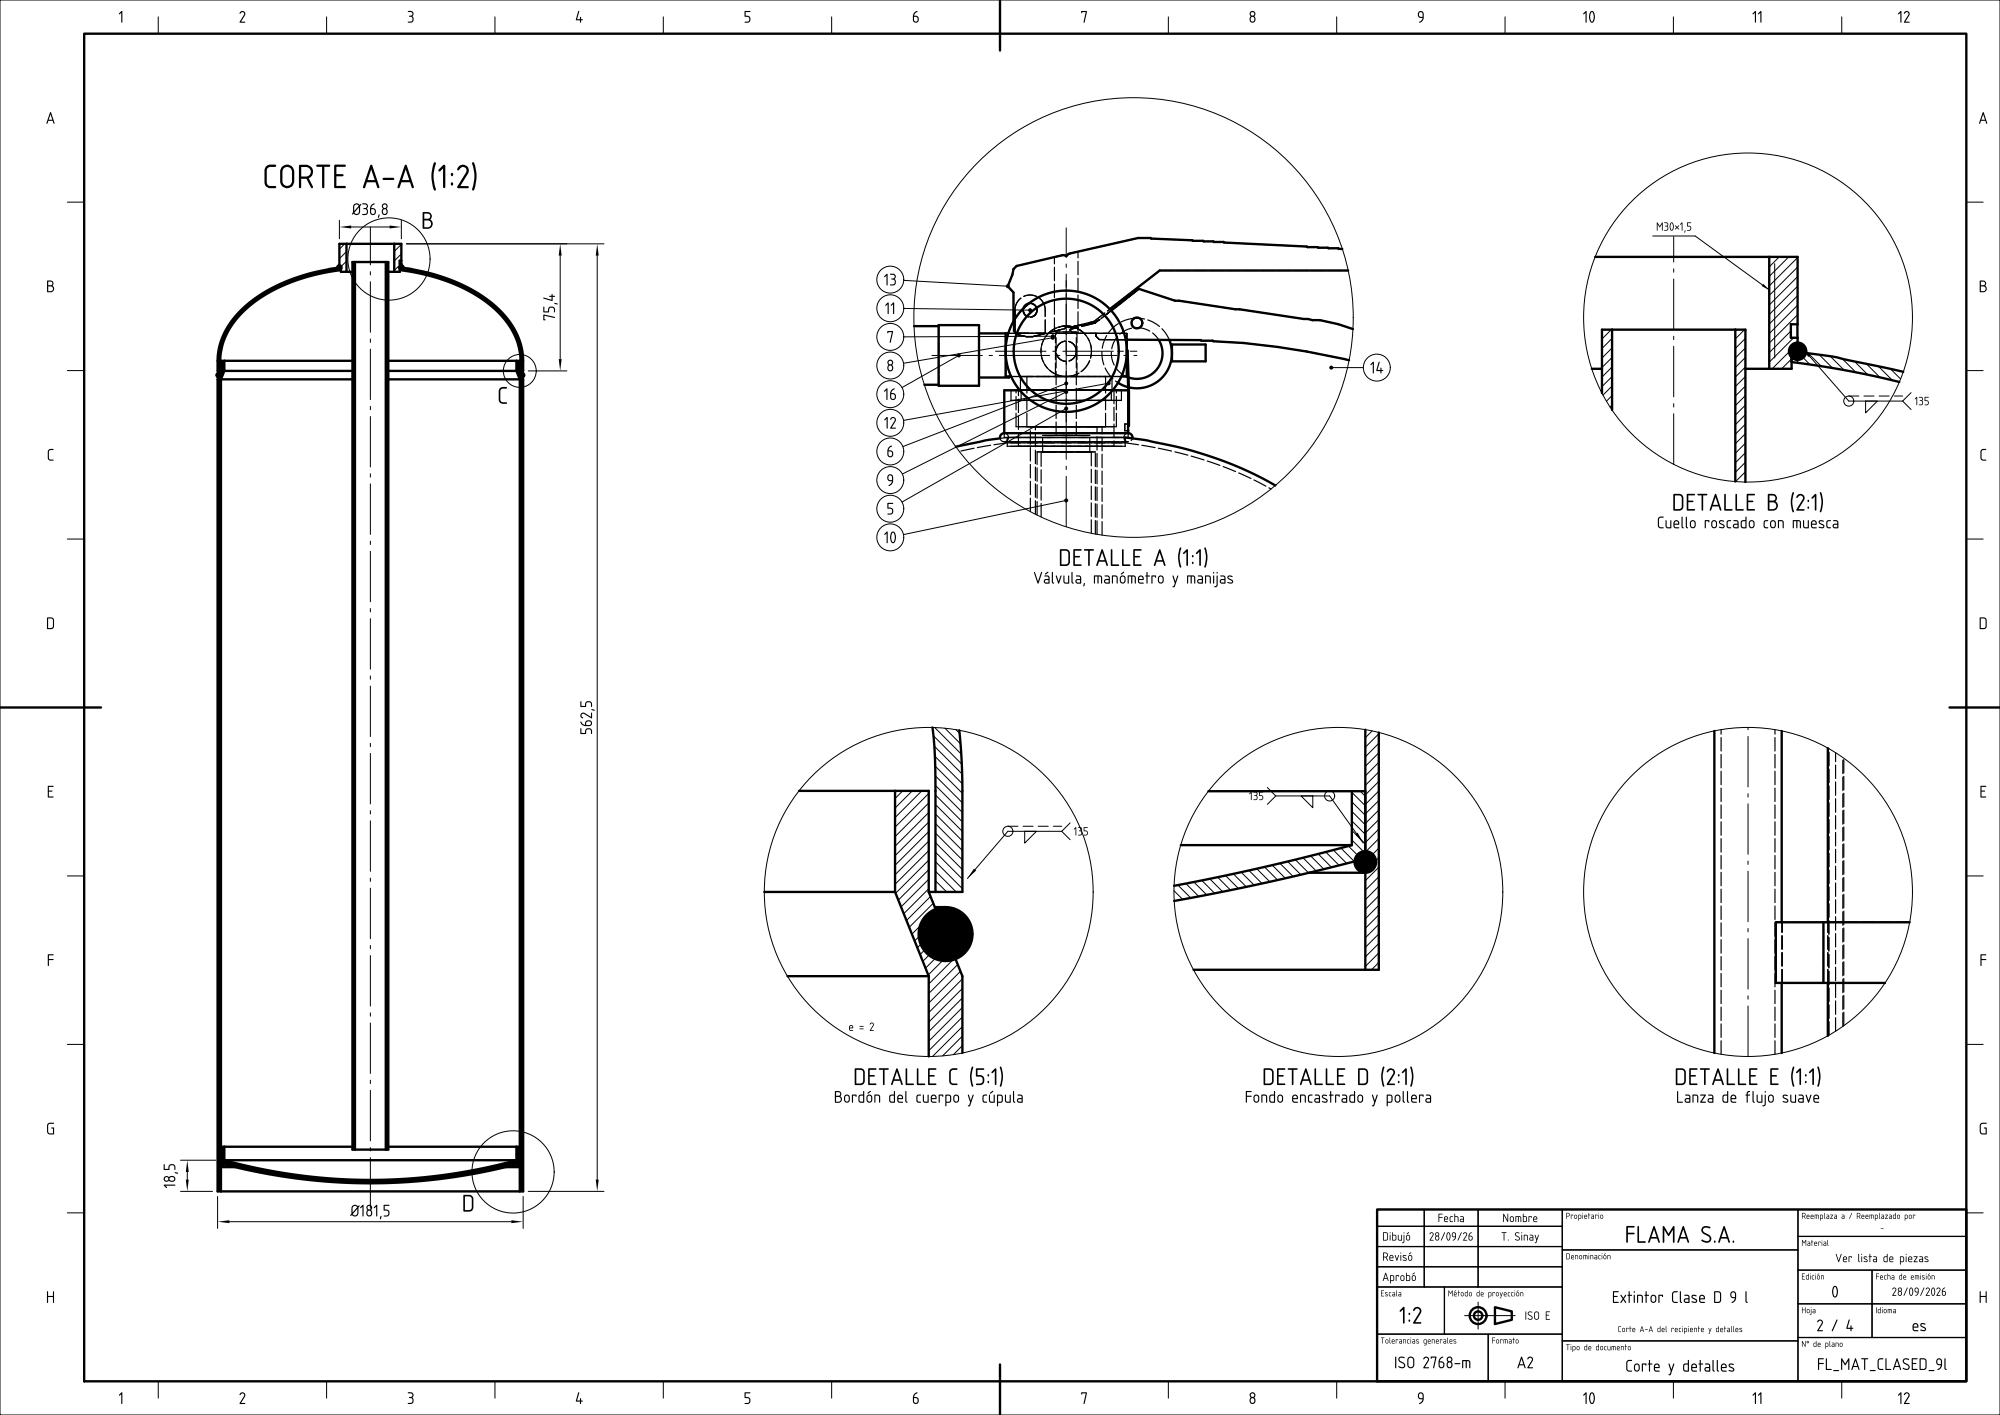
[picture p191: page 2]

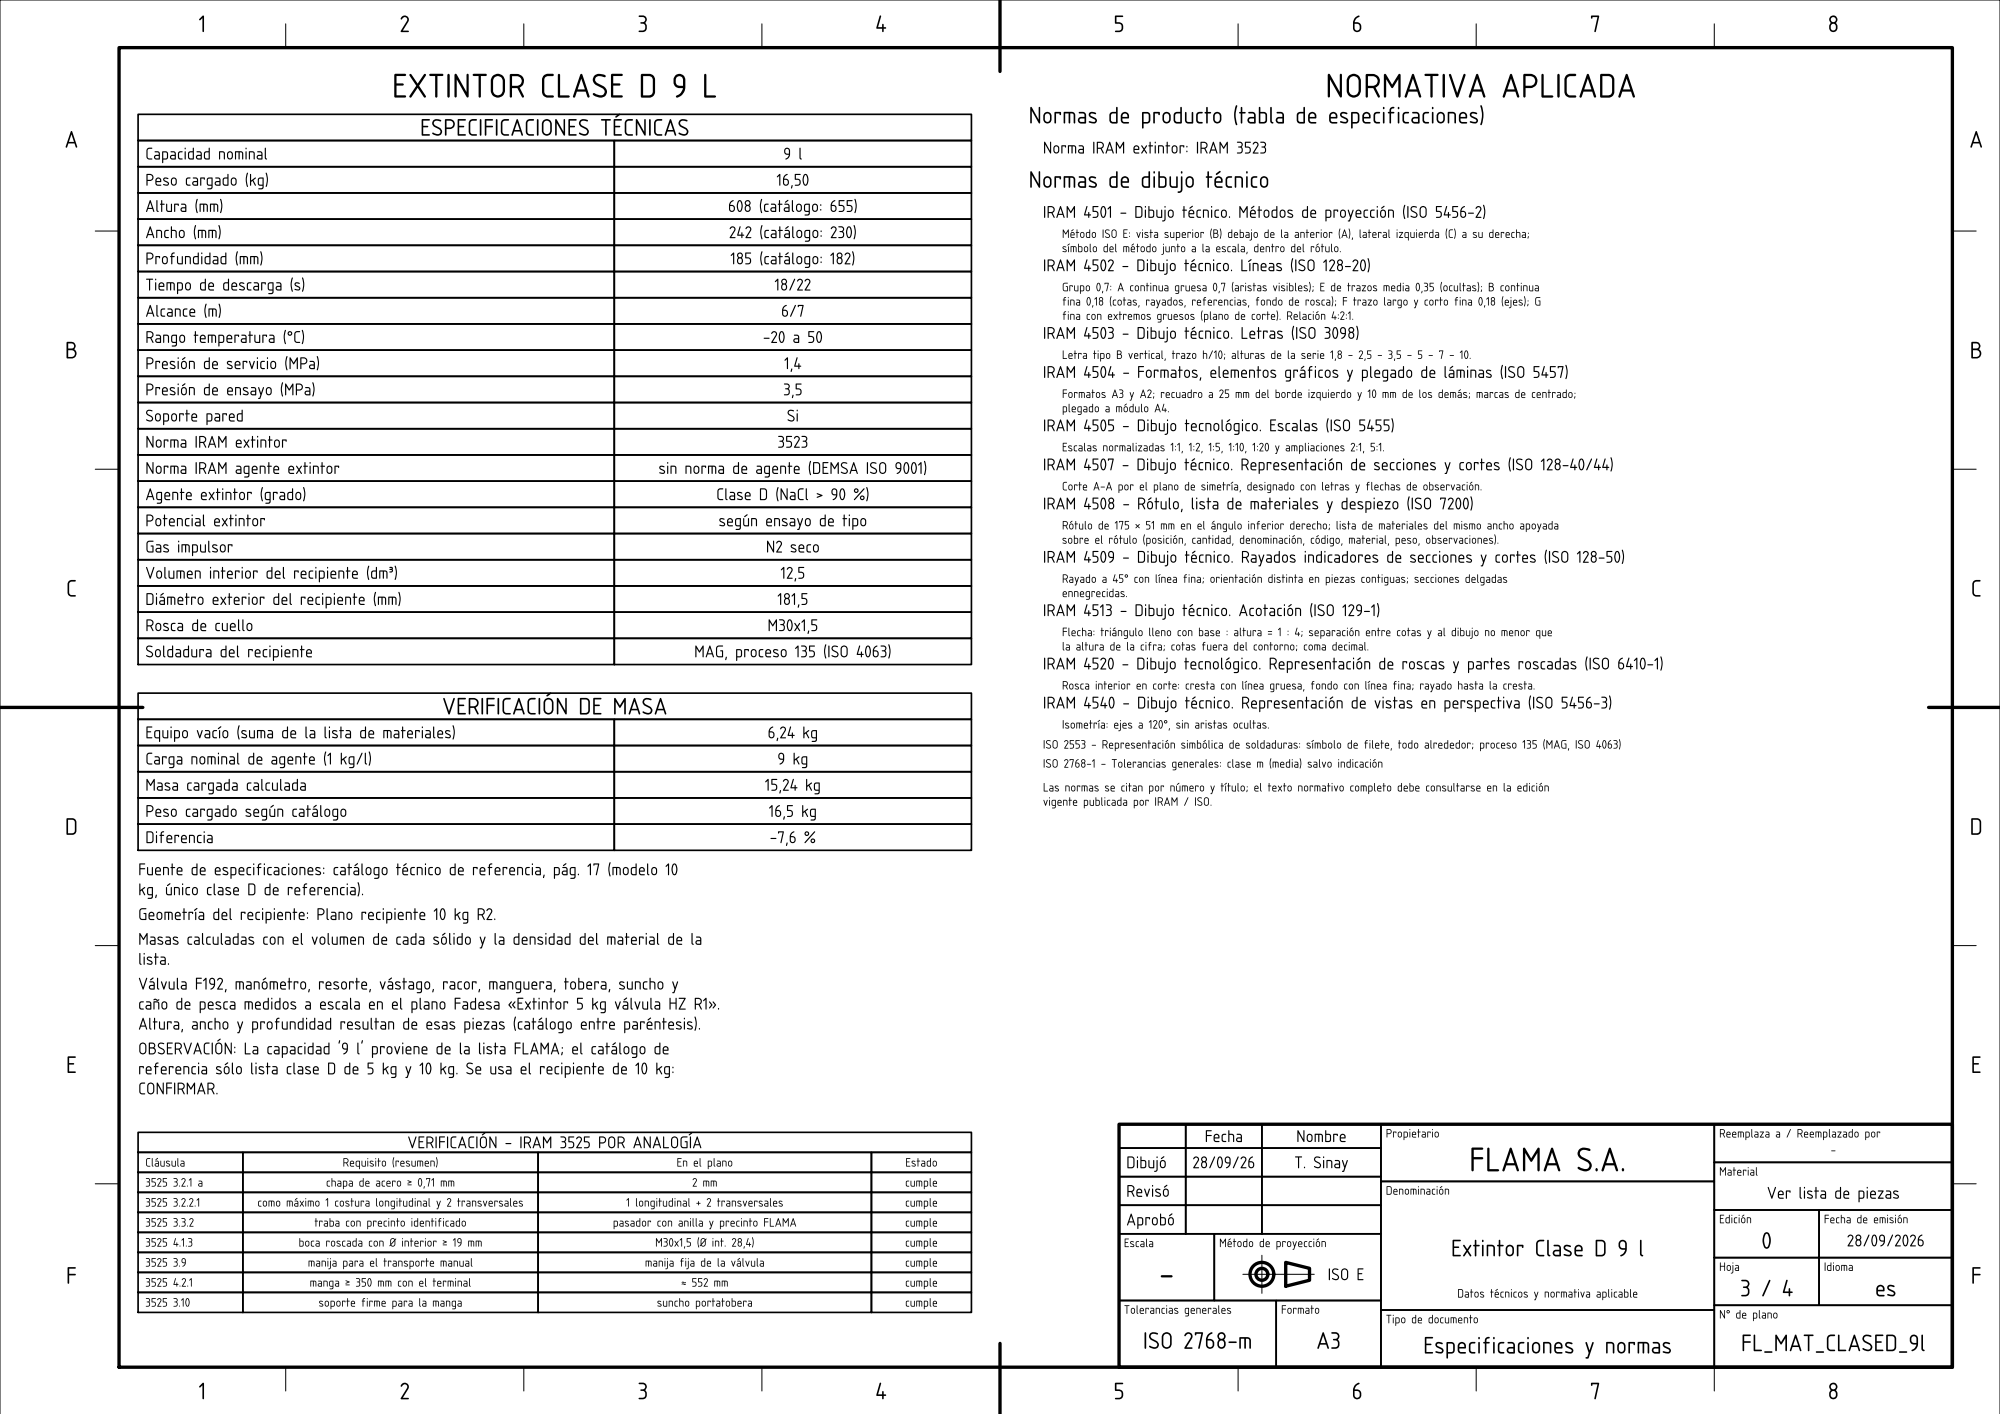
[picture p192: page 3]

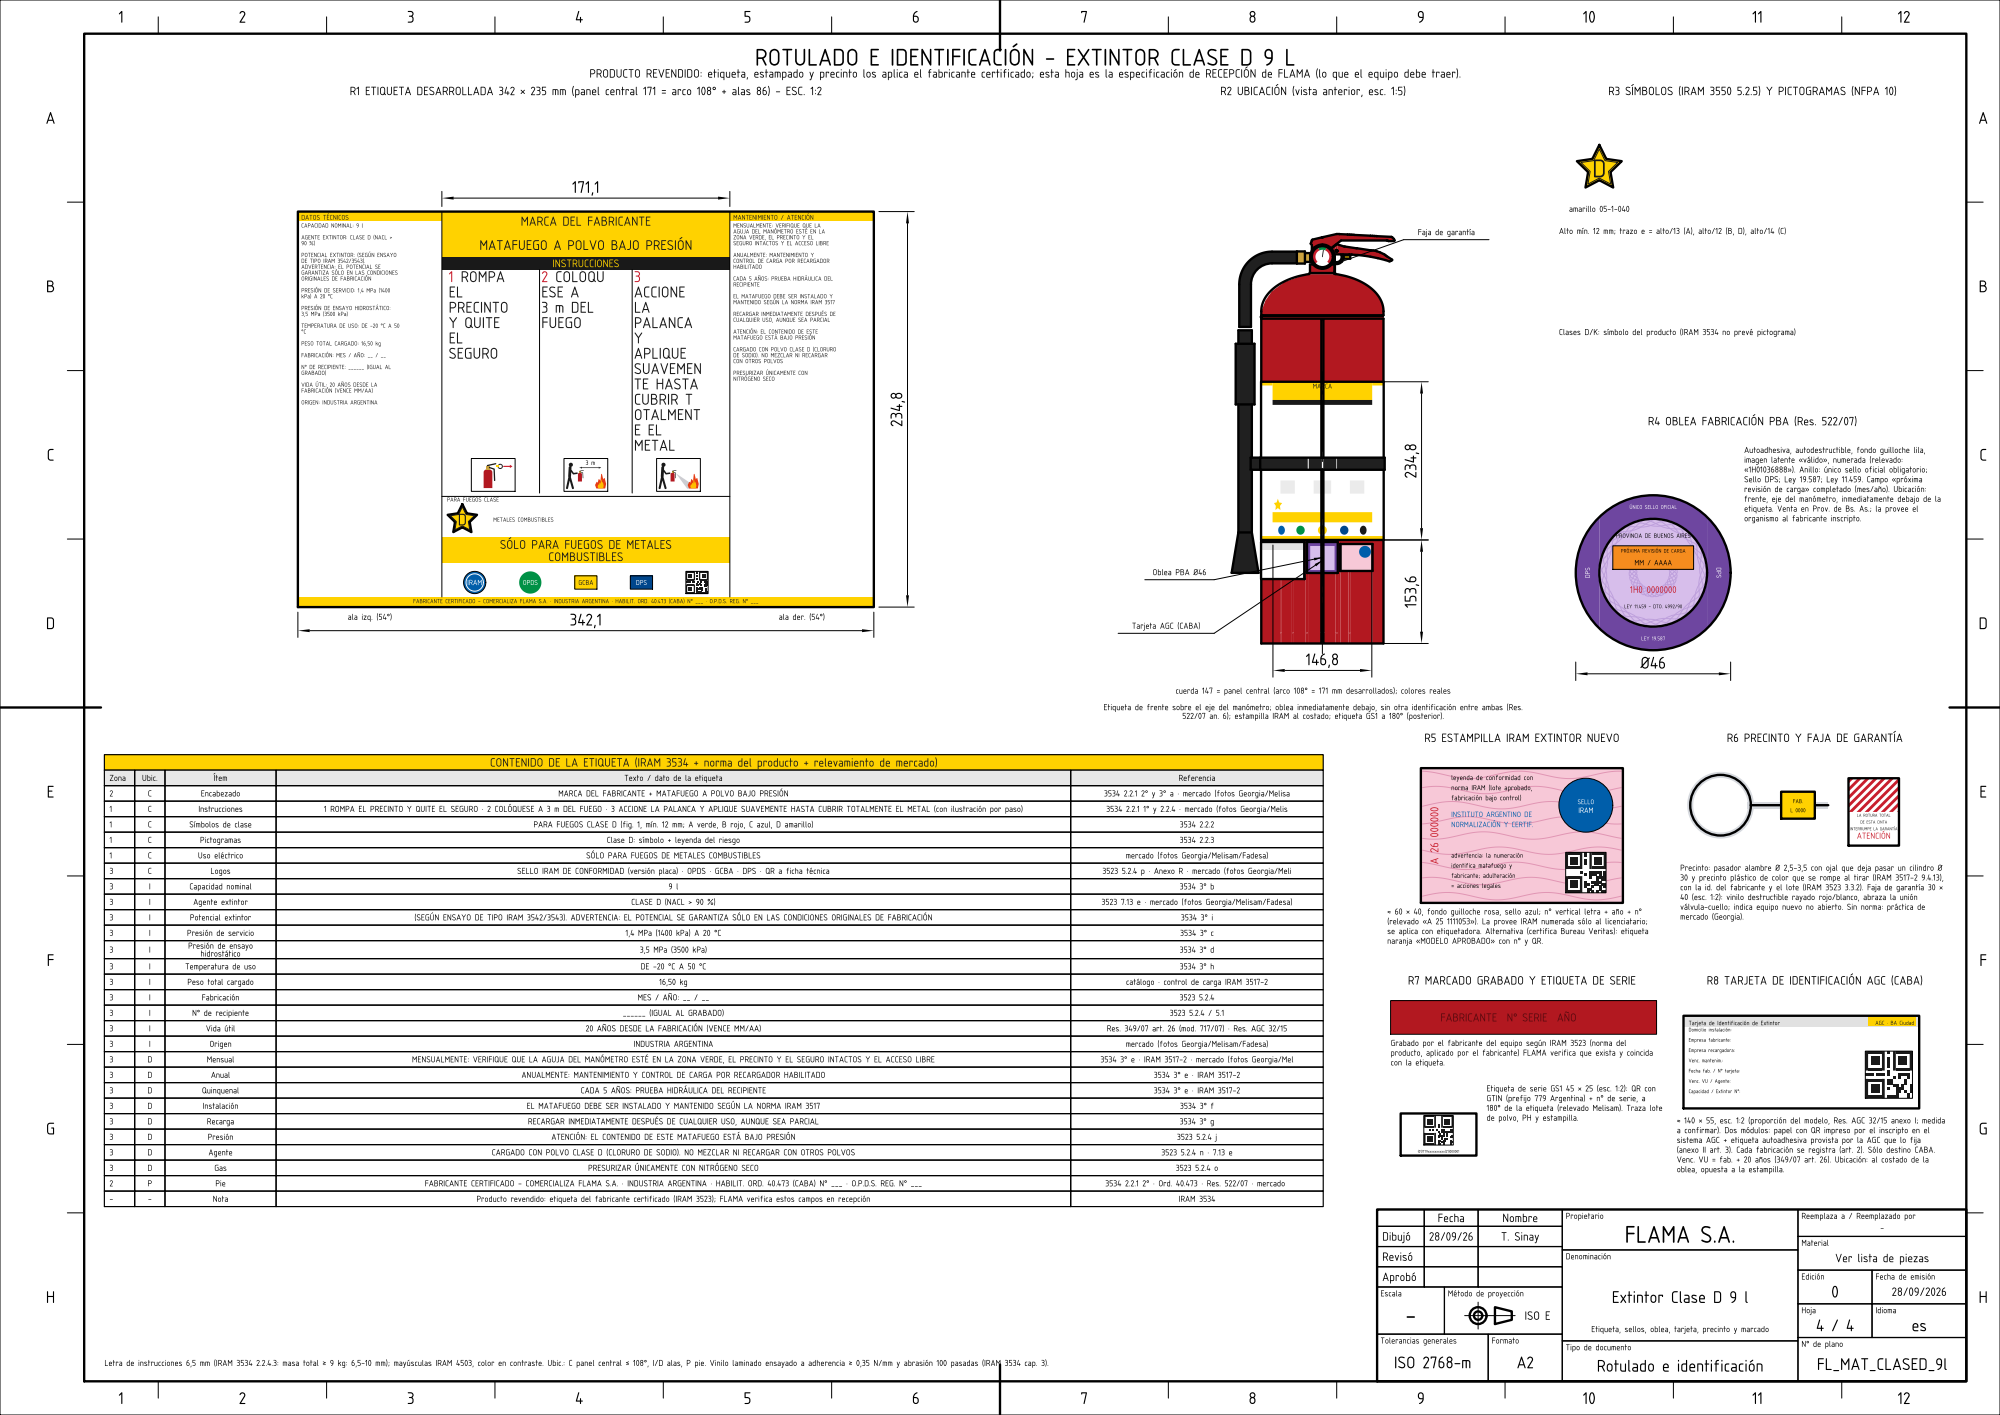
[picture p193: page 4]
