TadeoSinay/planos_flama-/salida/FL_MAT_CO2_2kg/FL_MAT_CO2_2kg.pdf

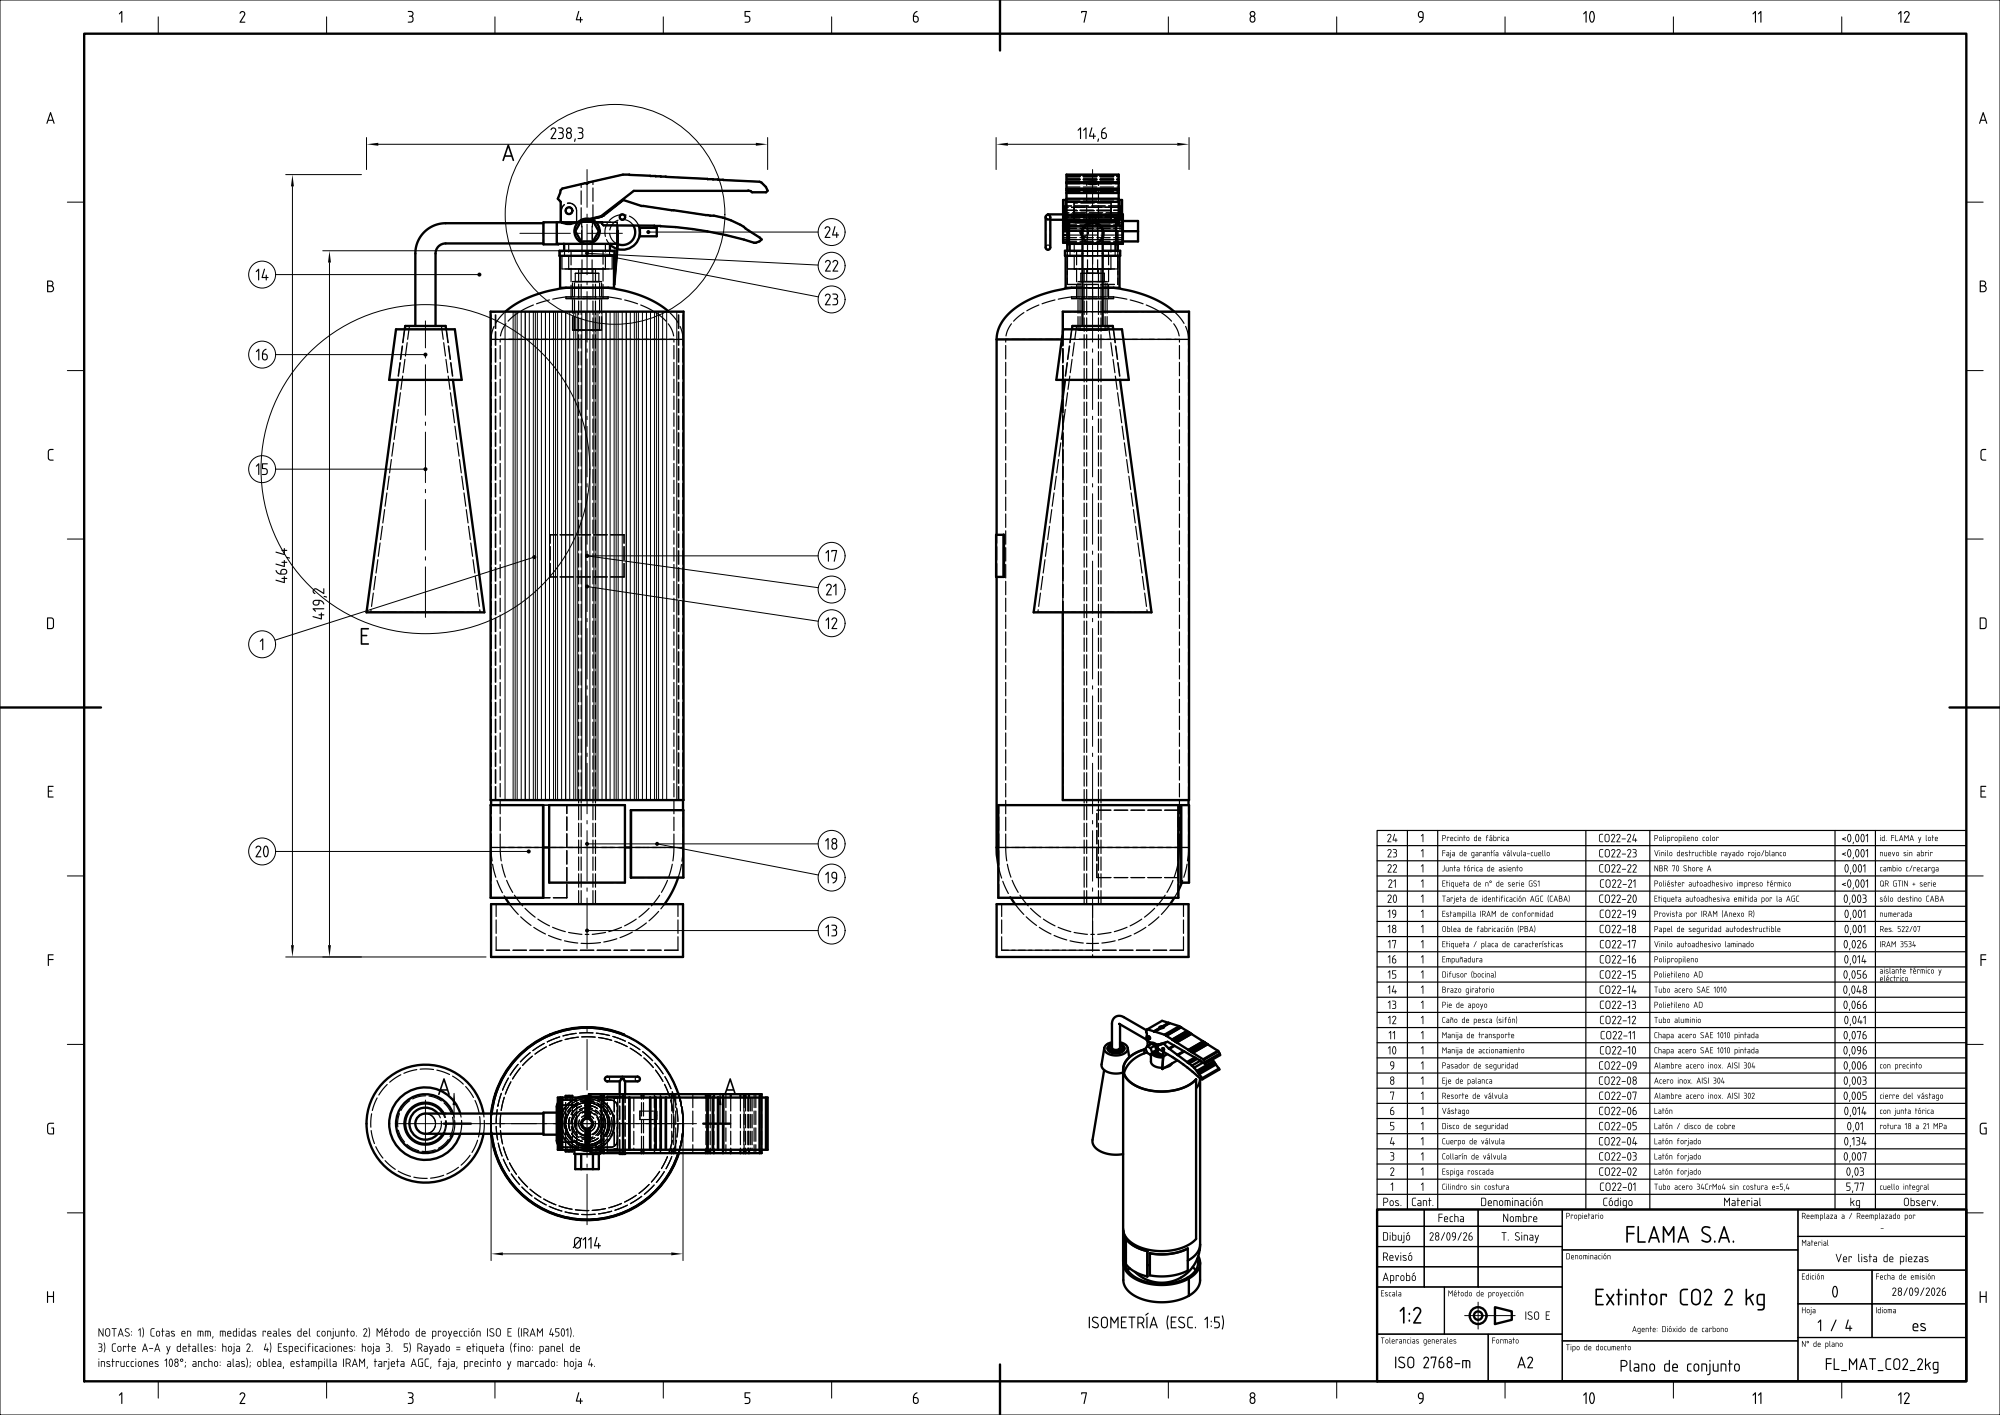
[picture p194: page 1]

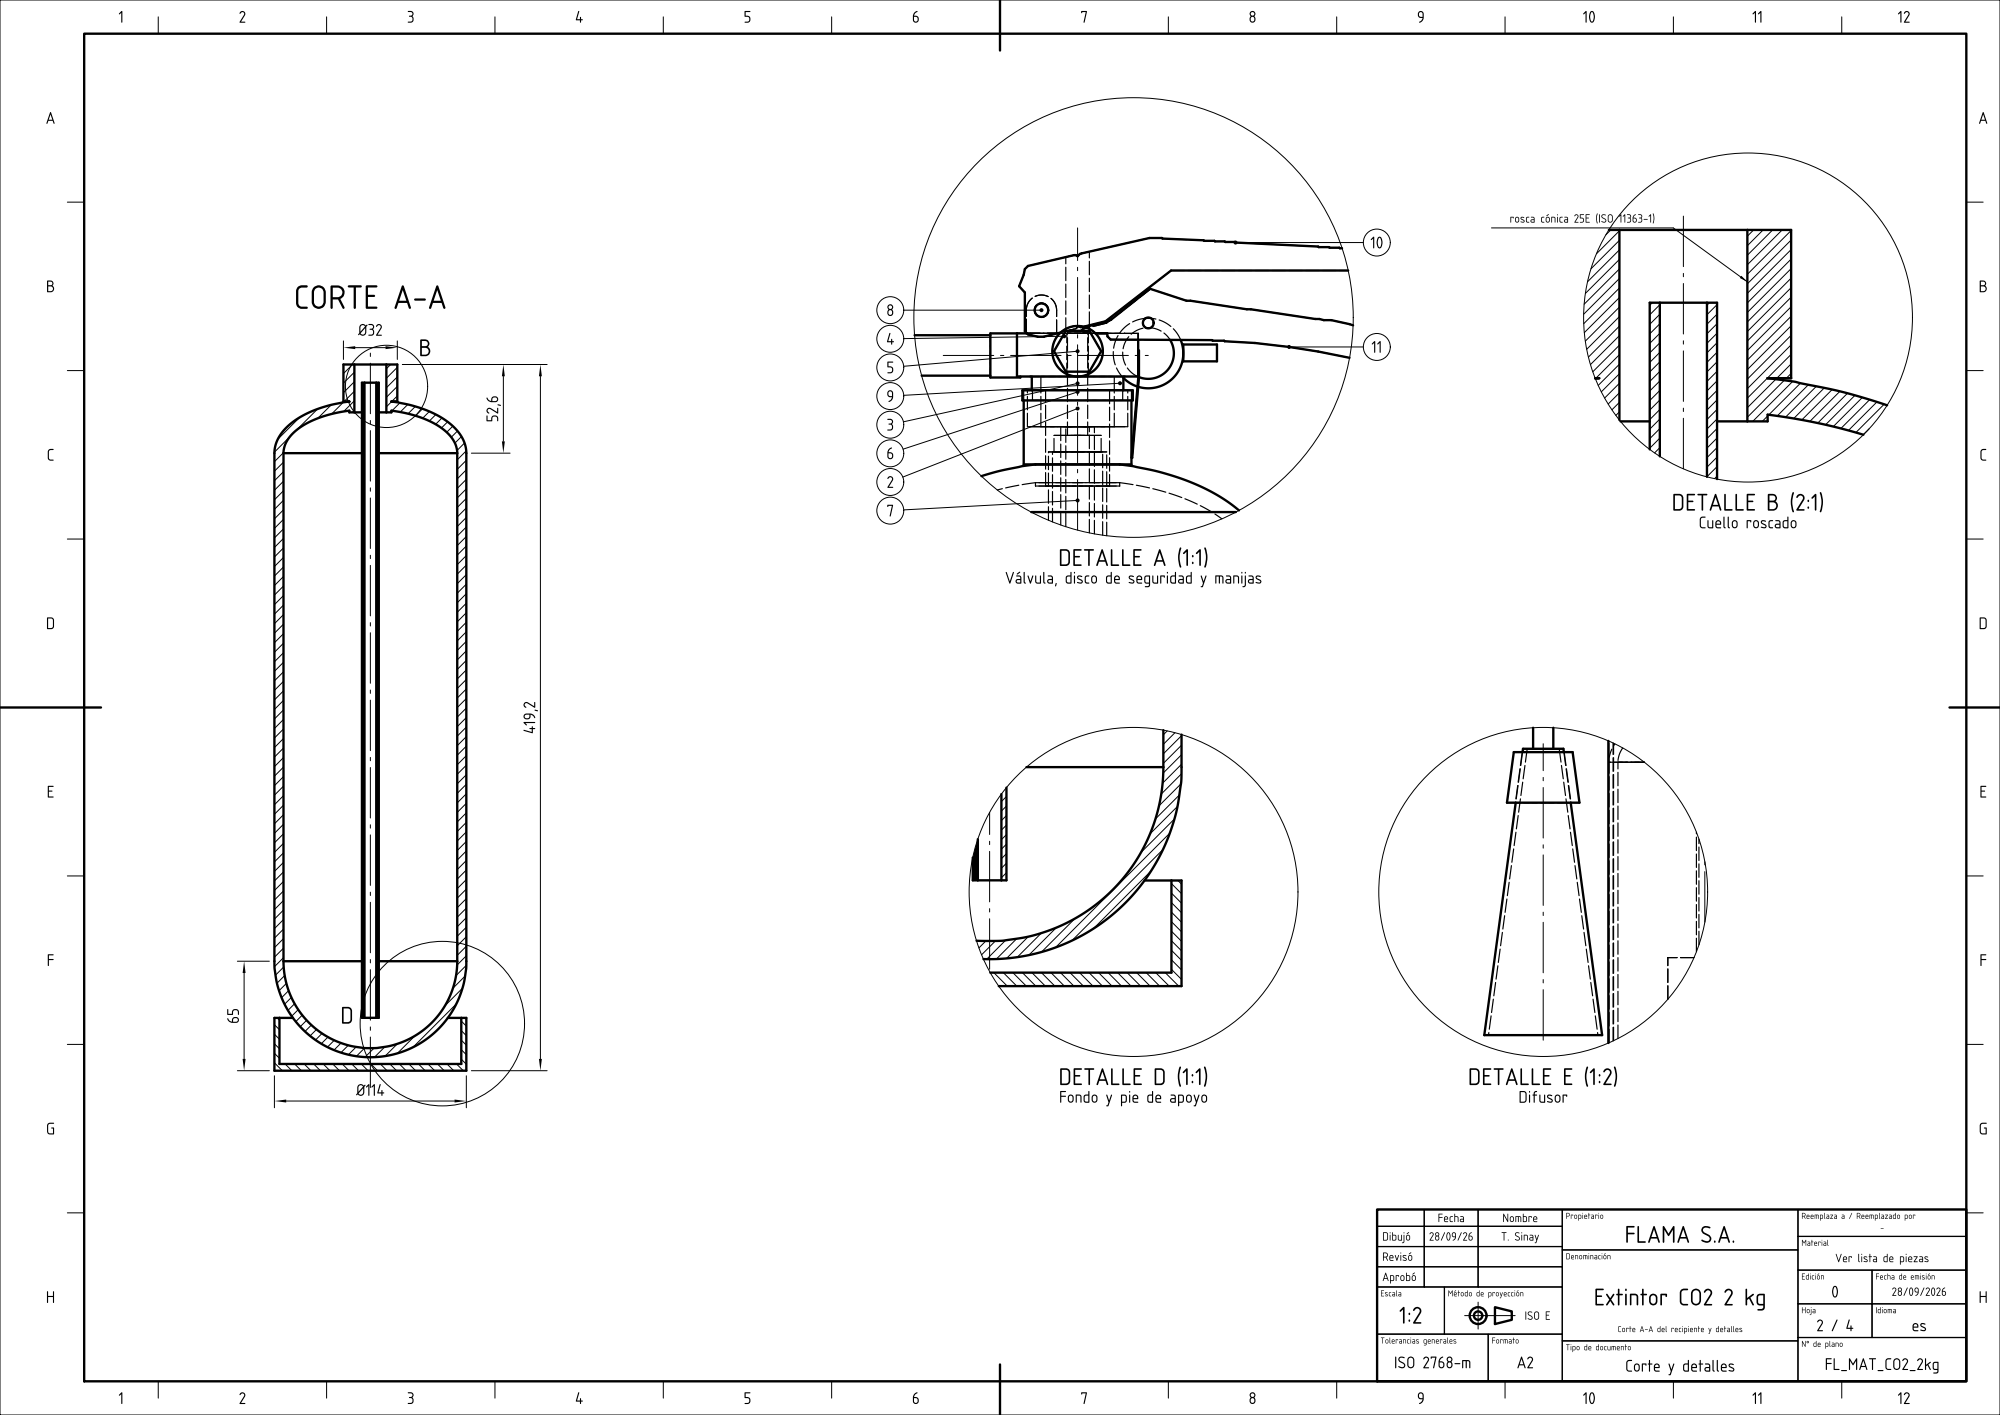
[picture p195: page 2]

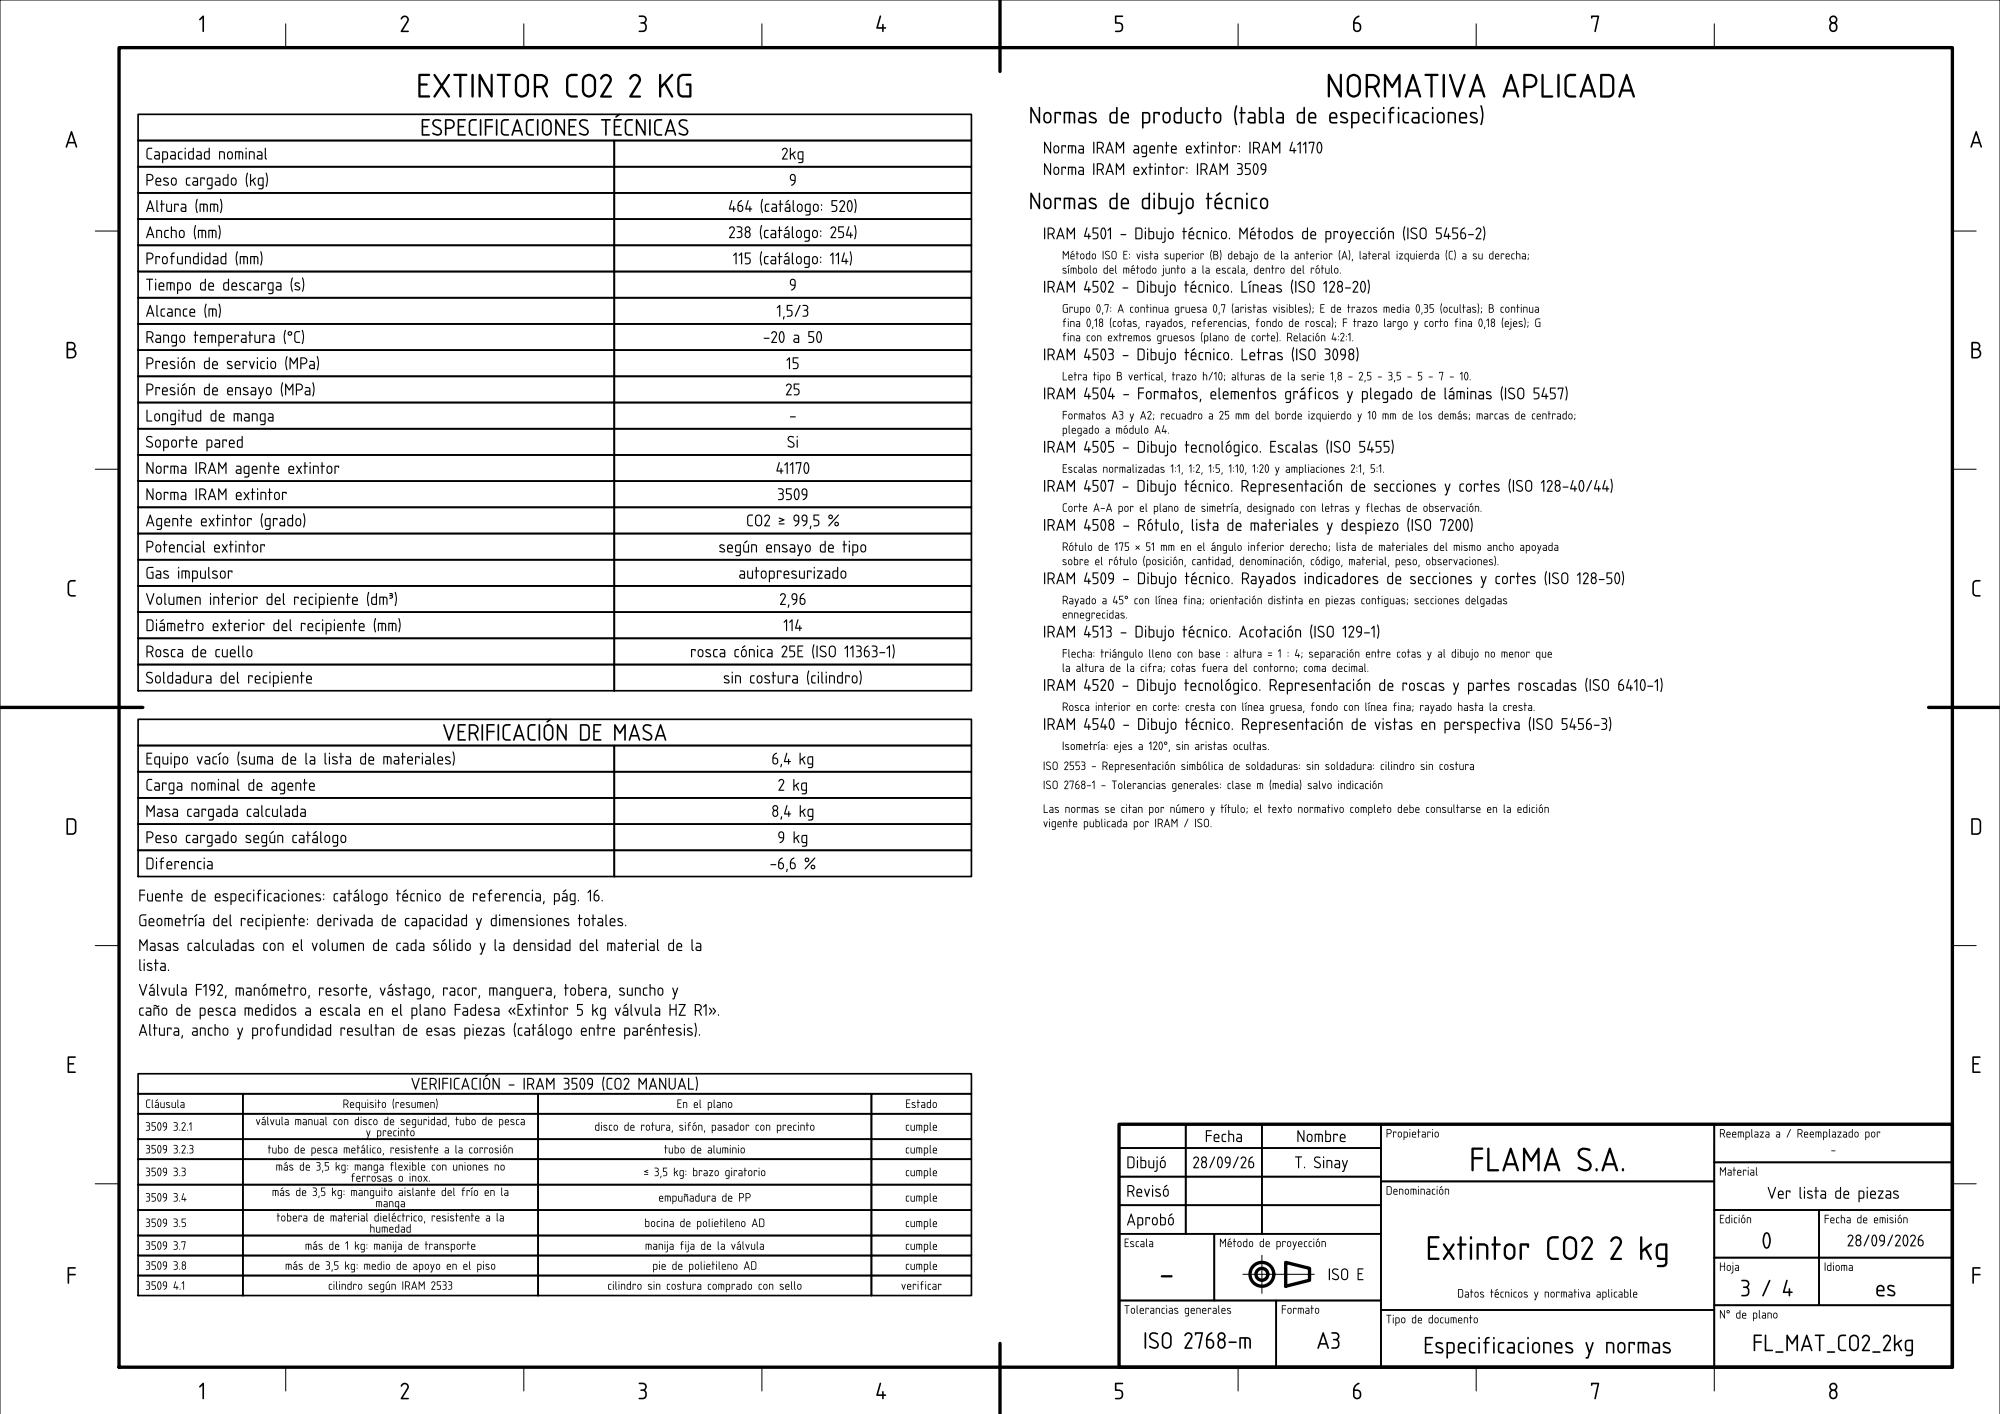
[picture p196: page 3]

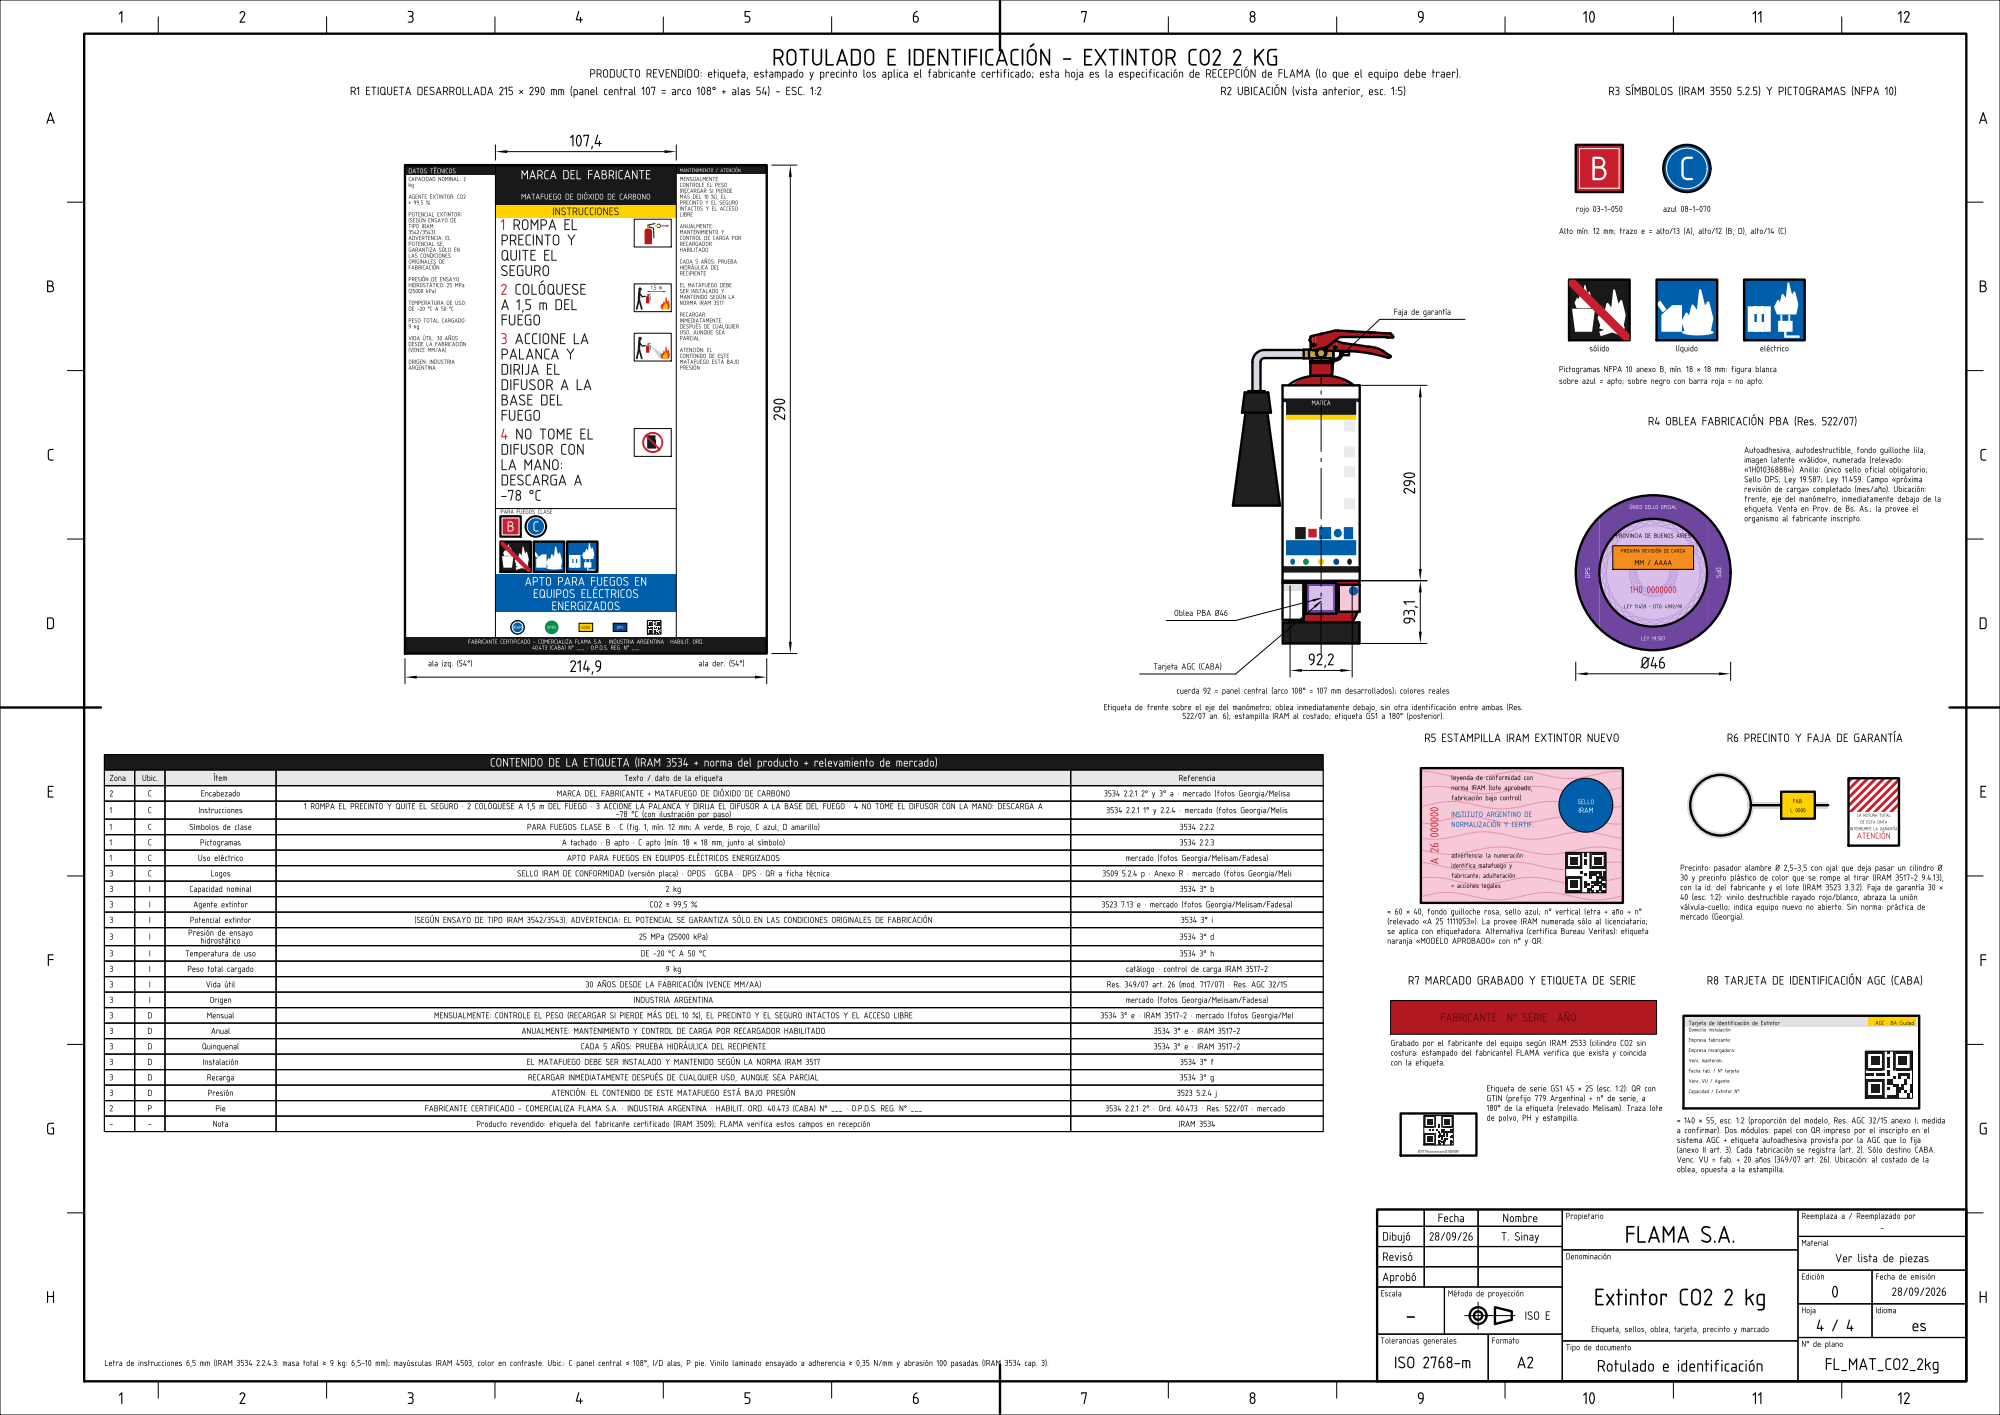
[picture p197: page 4]
