TadeoSinay/planos_flama-/salida/FL_MAT_CO2_5kg/FL_MAT_CO2_5kg.pdf

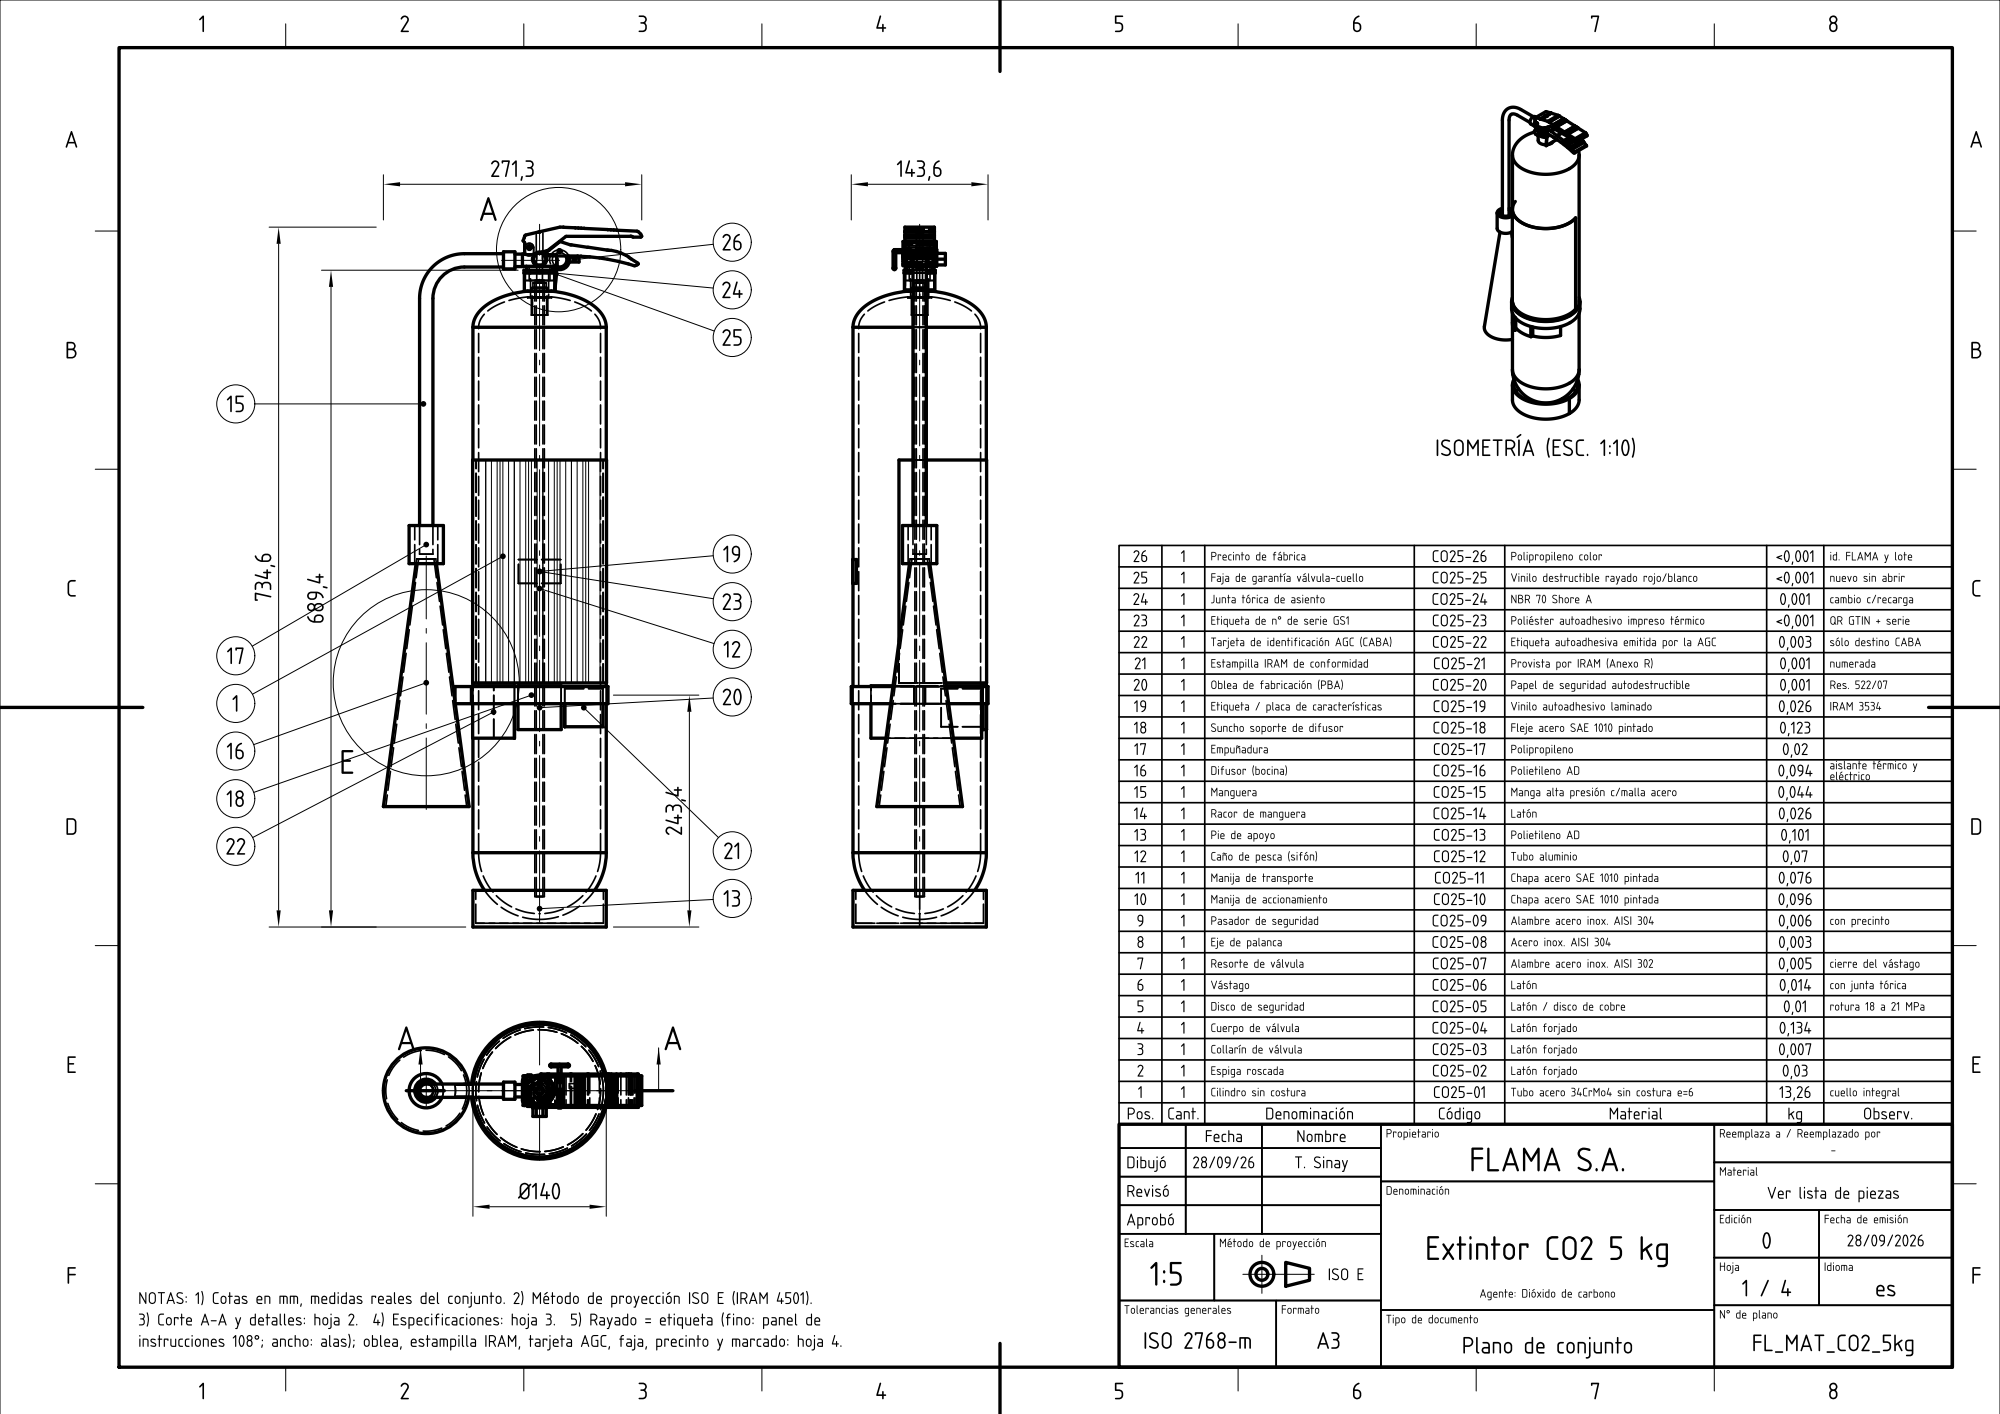
[picture p198: page 1]

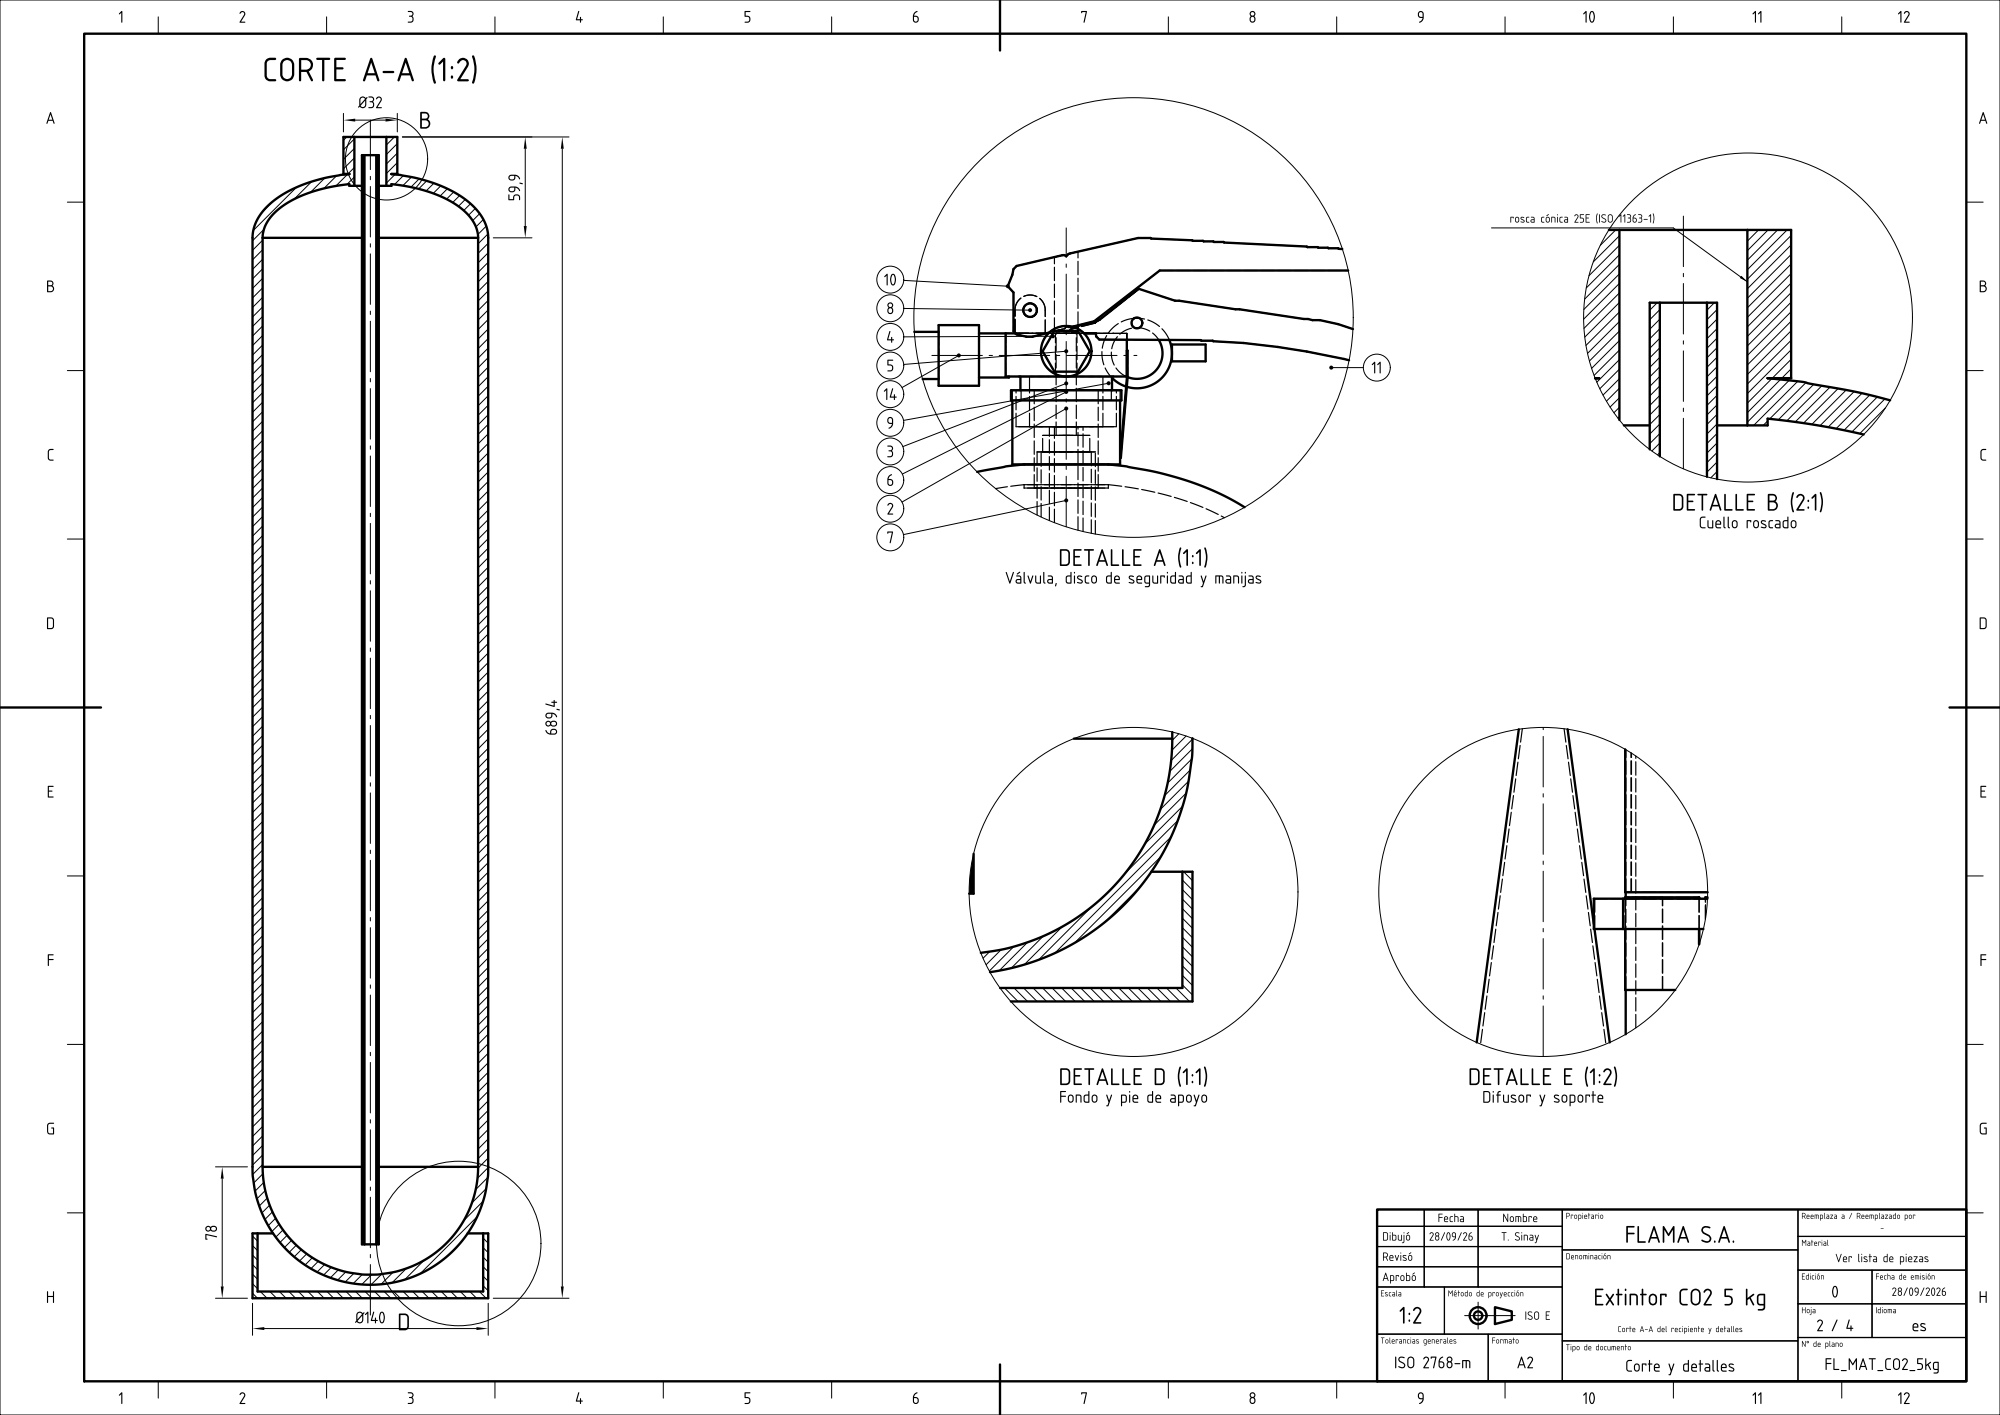
[picture p199: page 2]

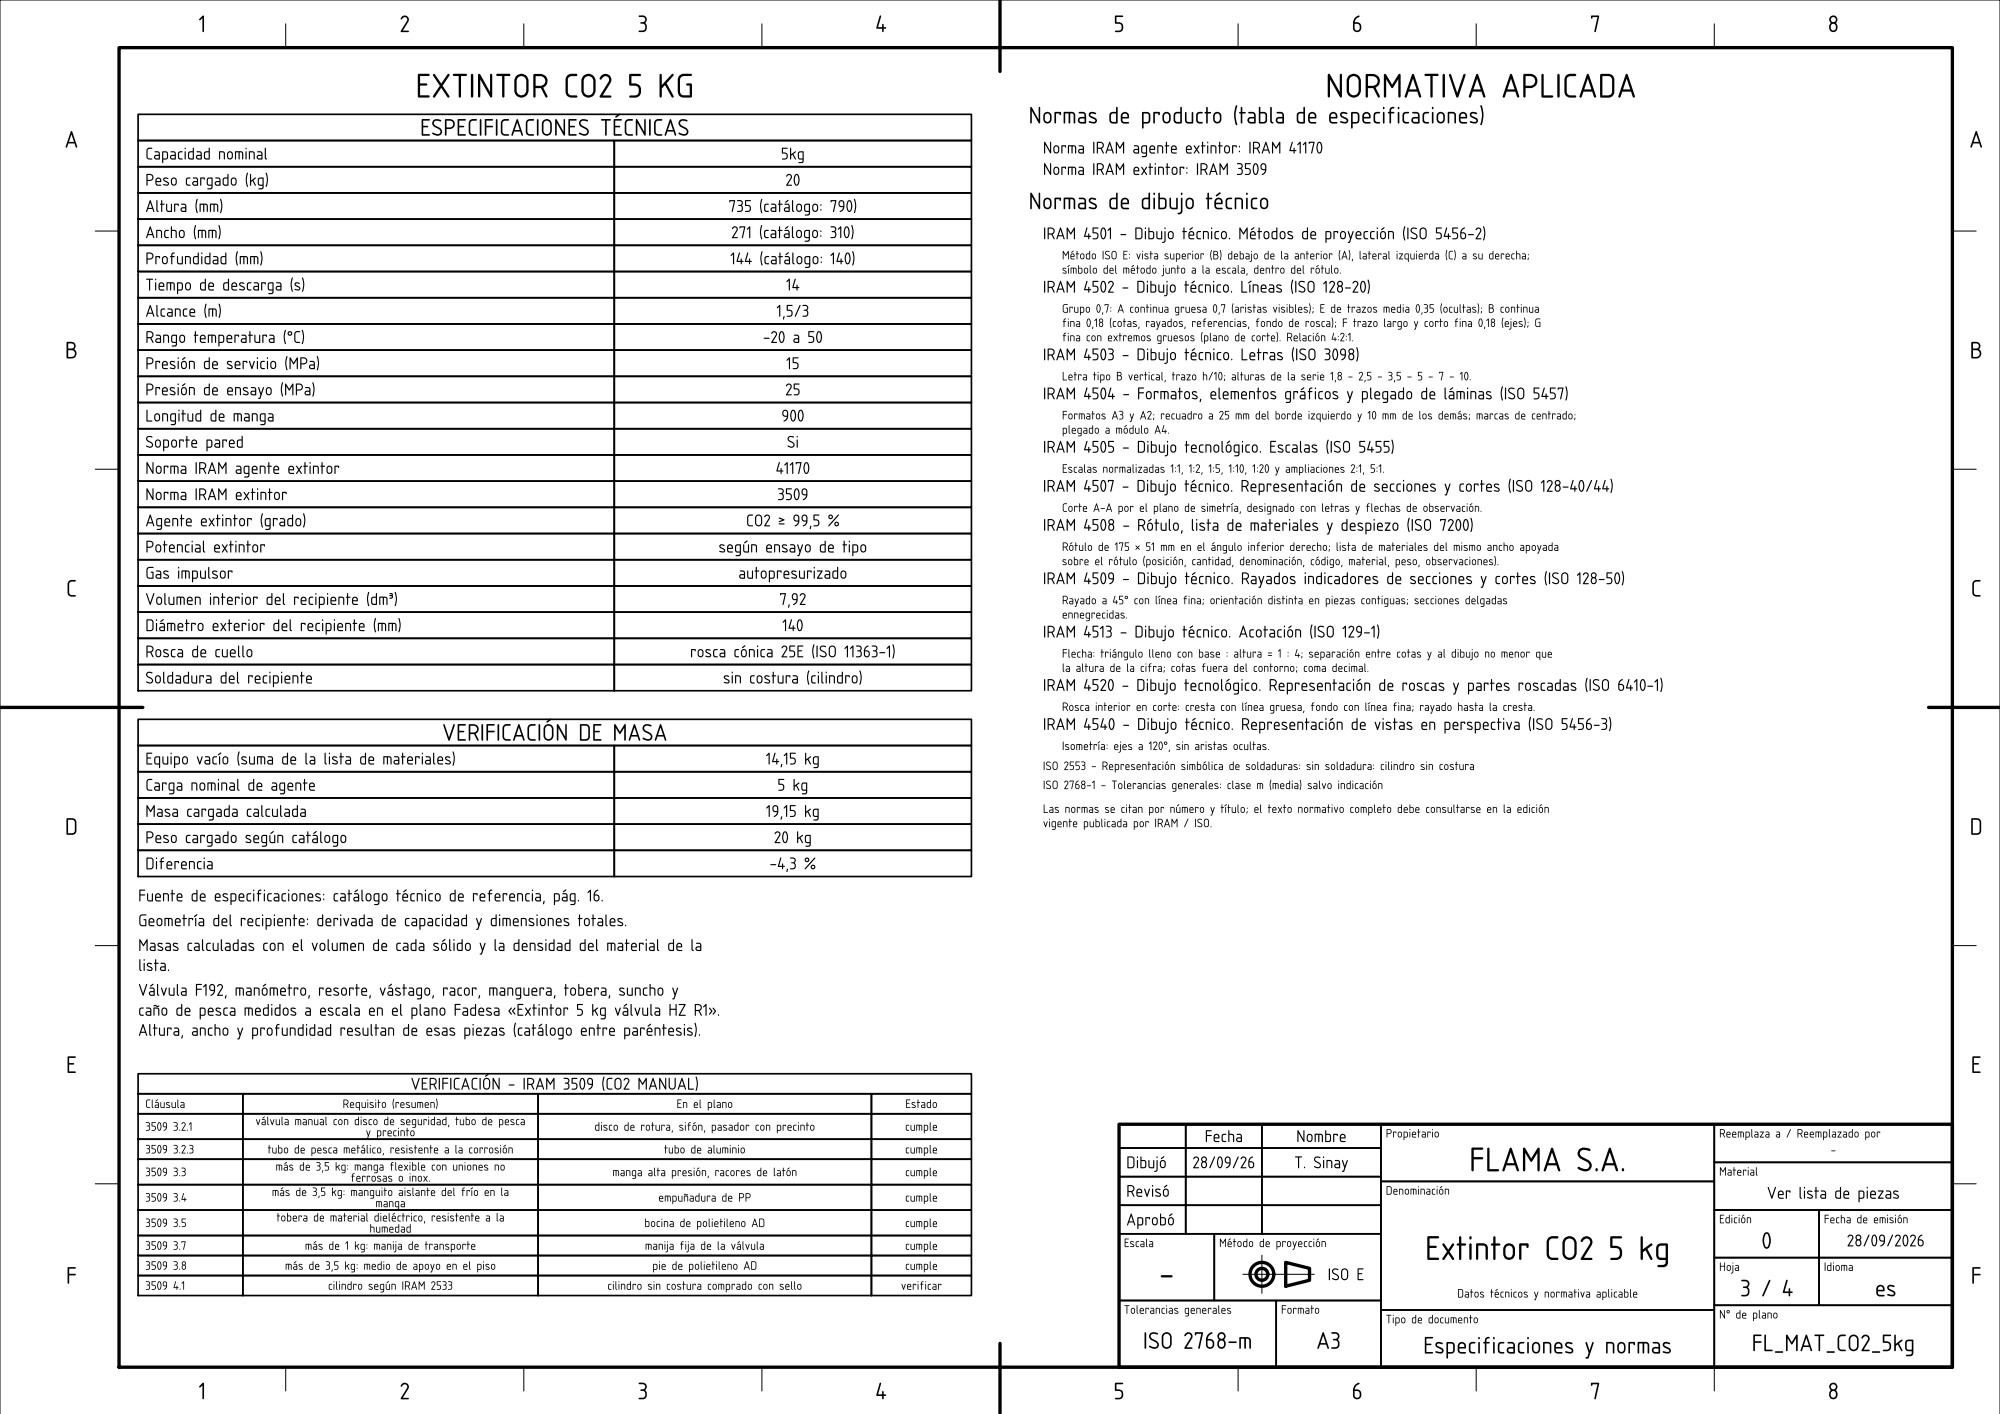
[picture p200: page 3]

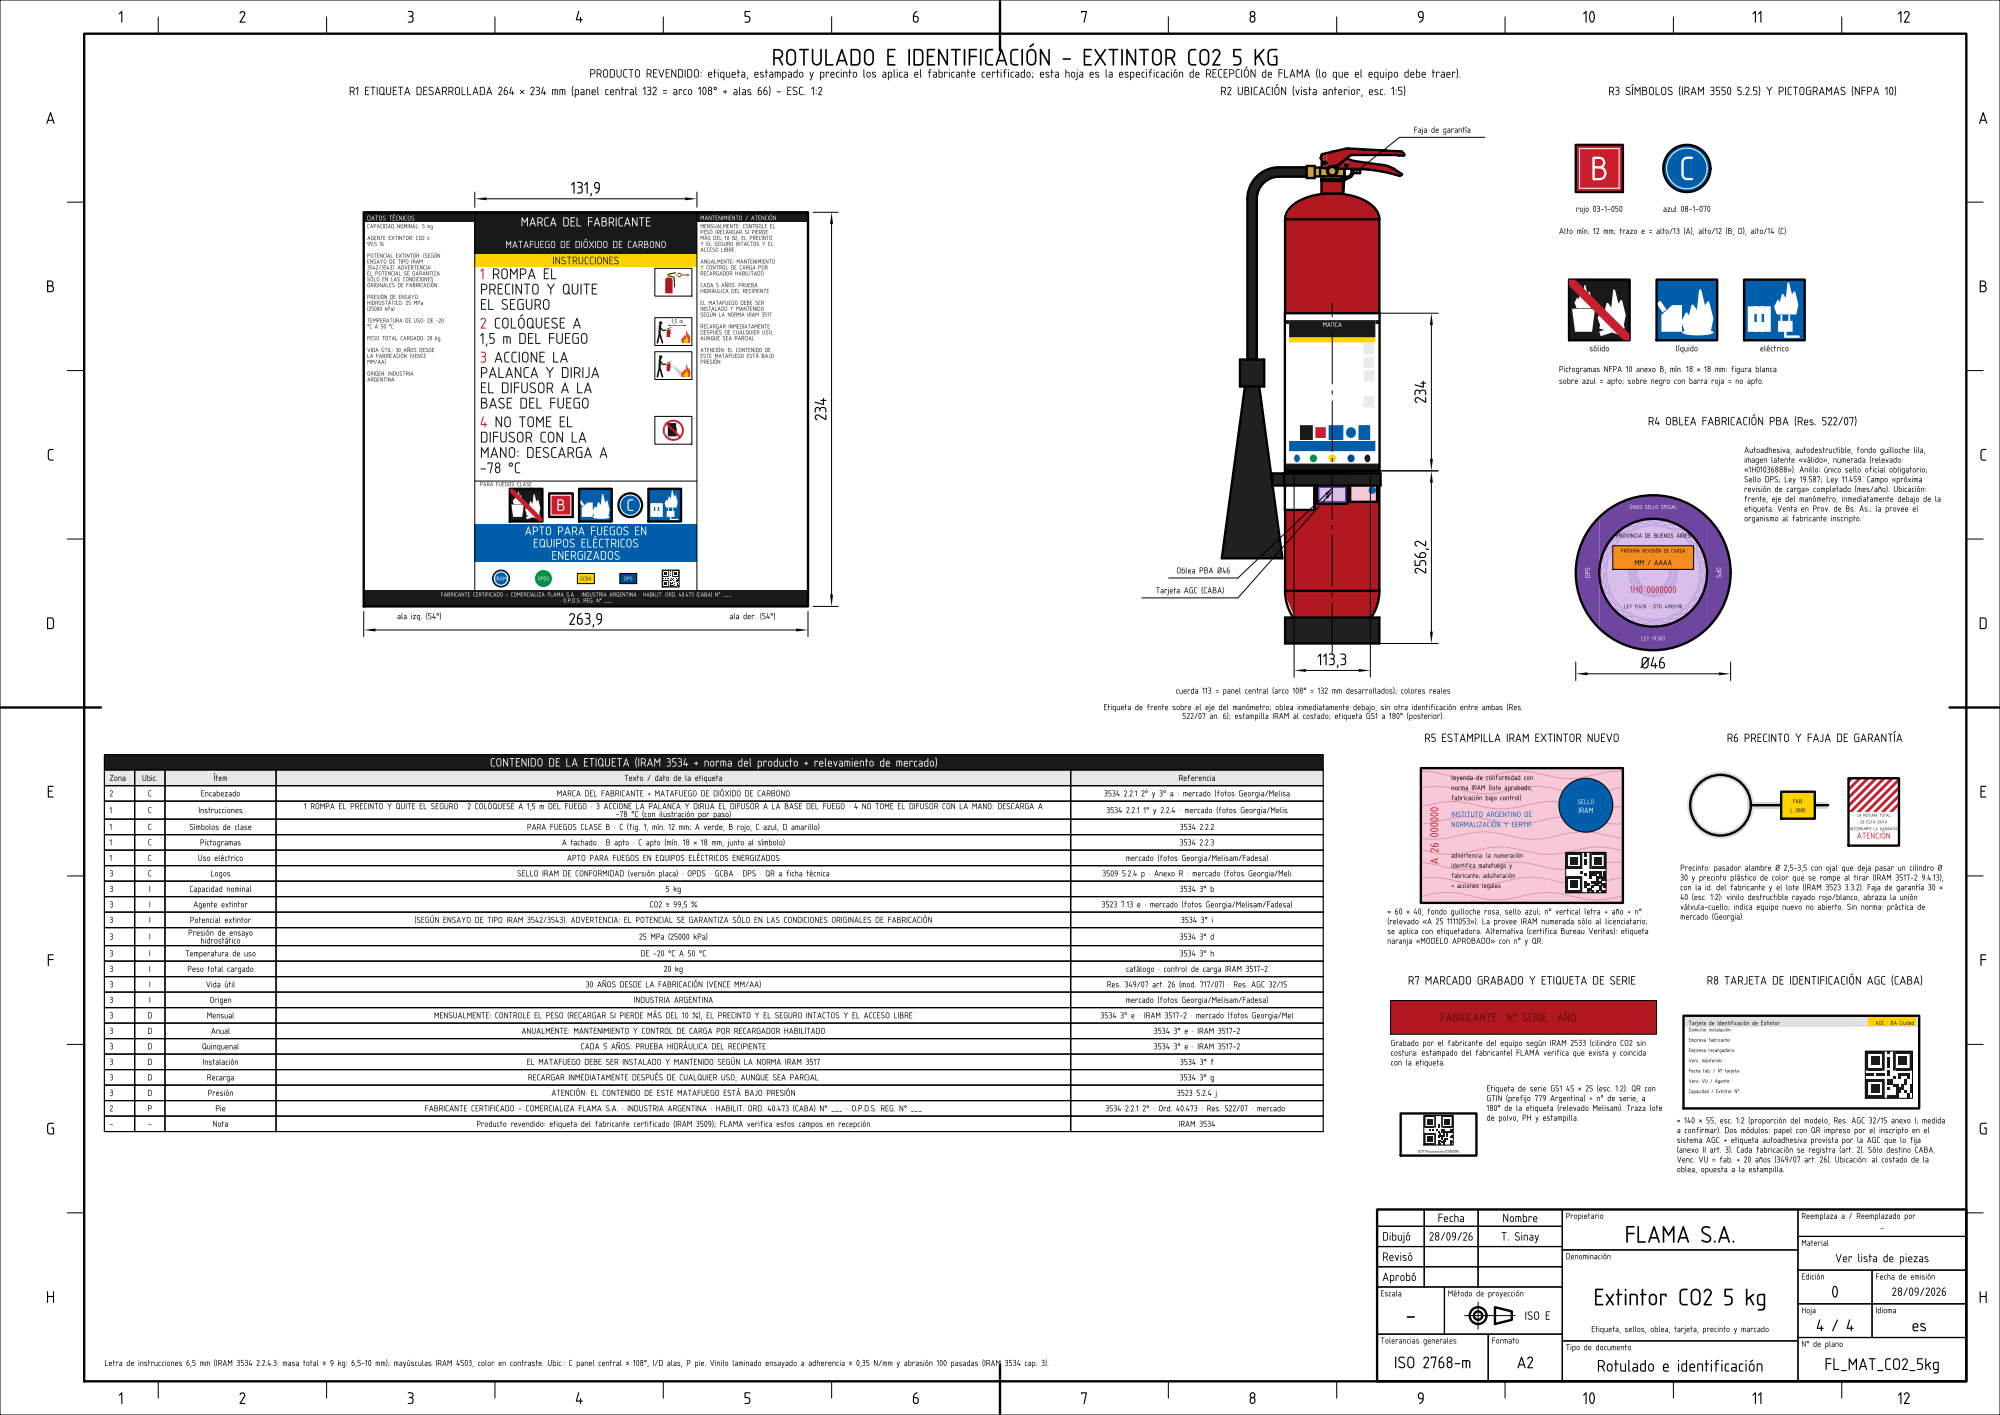
[picture p201: page 4]
