TadeoSinay/planos_flama-/salida/FL_MAT_HCFC-HFC_5kg/FL_MAT_HCFC-HFC_5kg.pdf

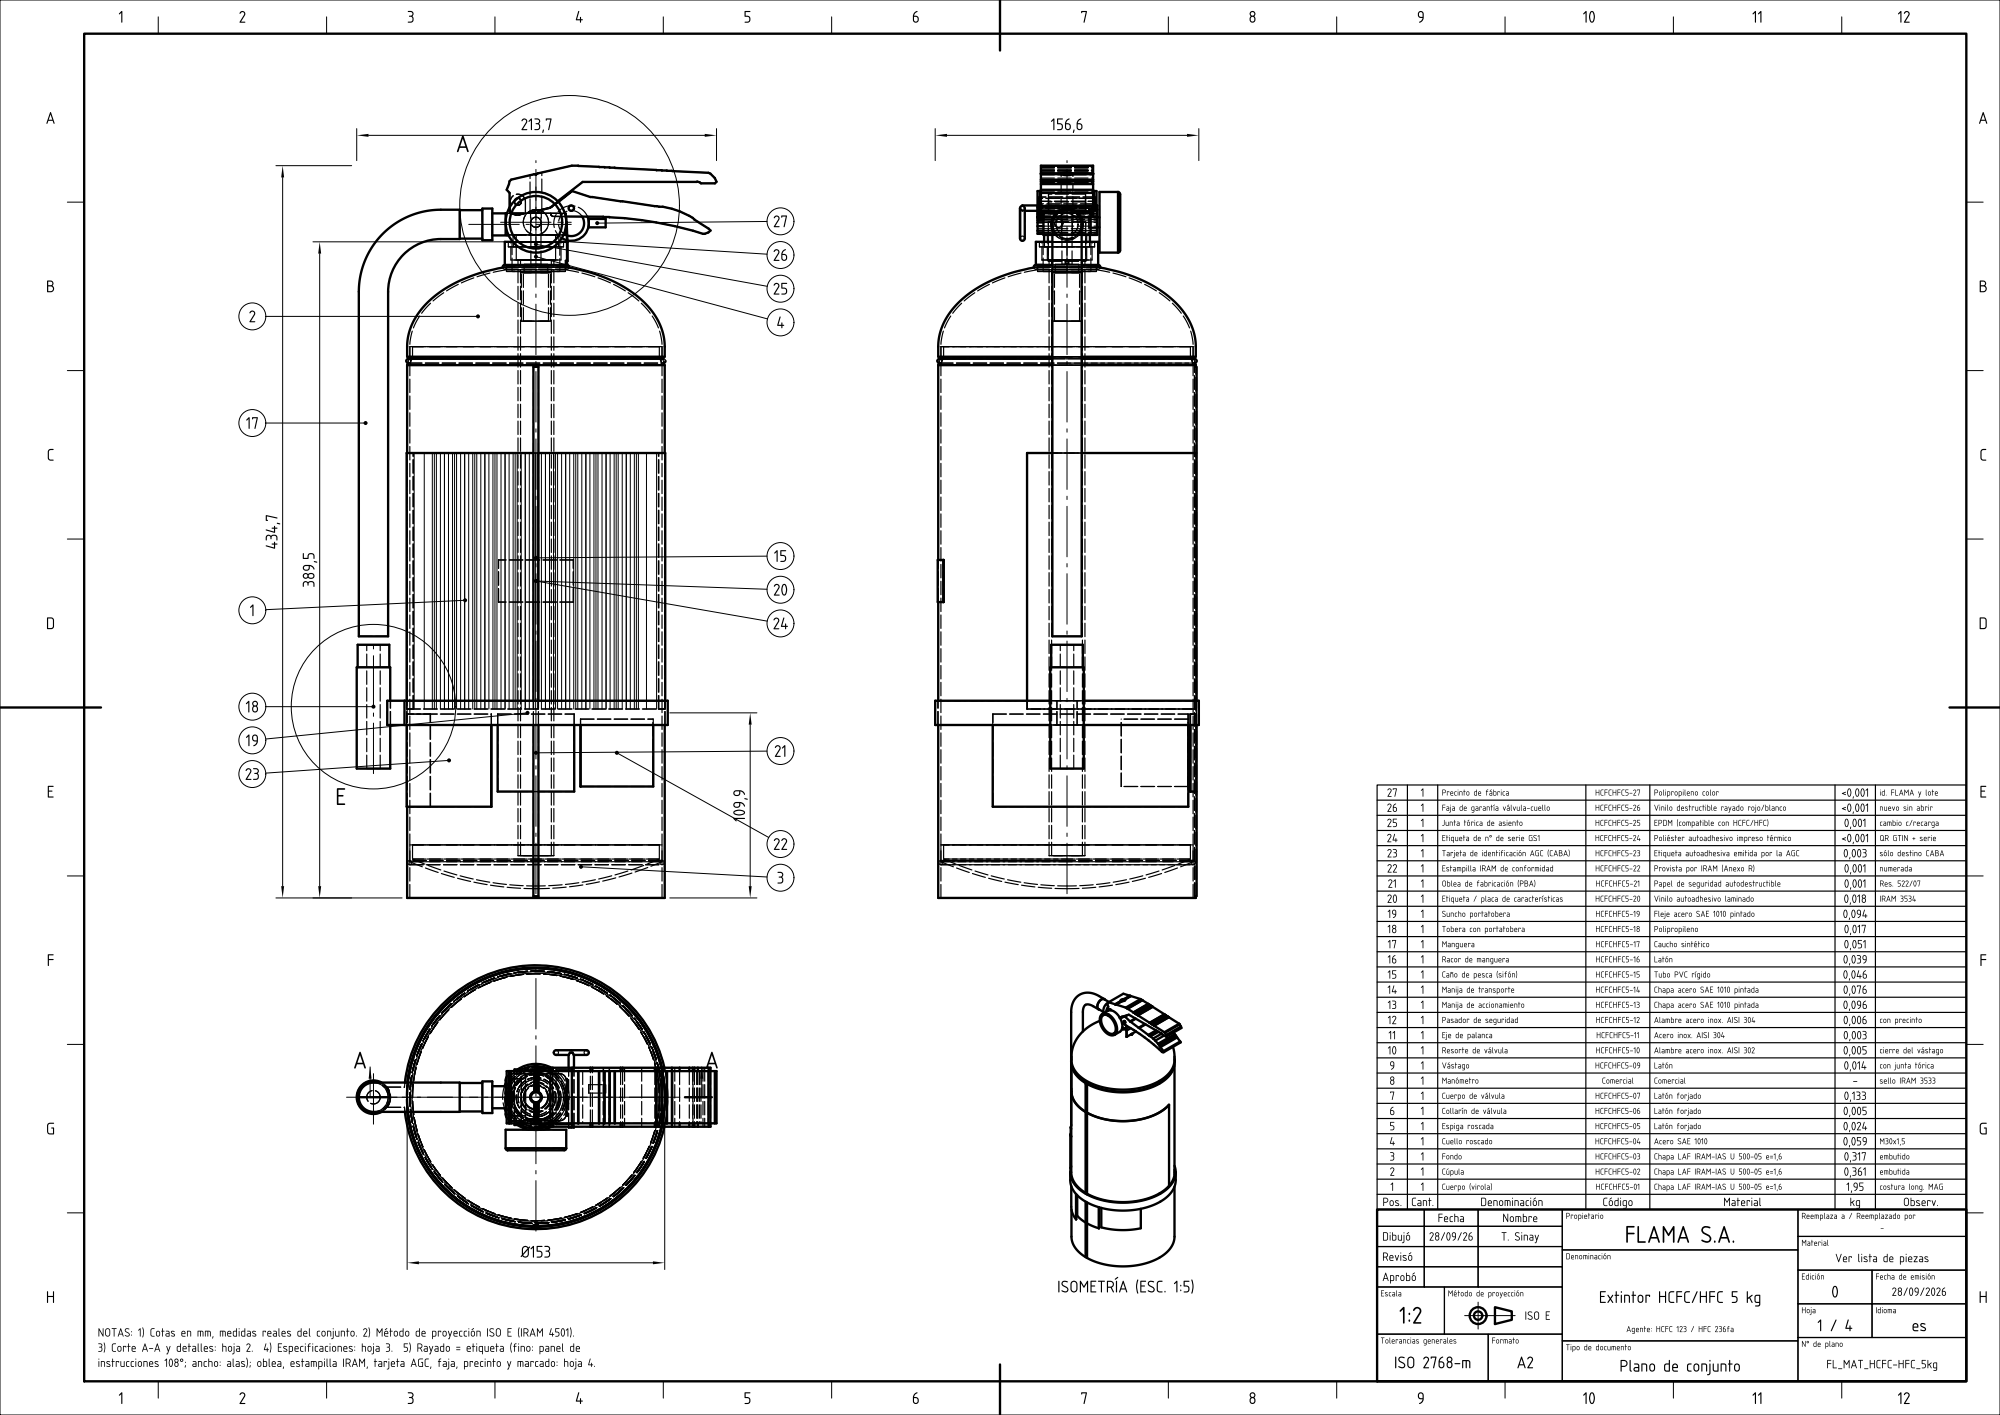
[picture p202: page 1]

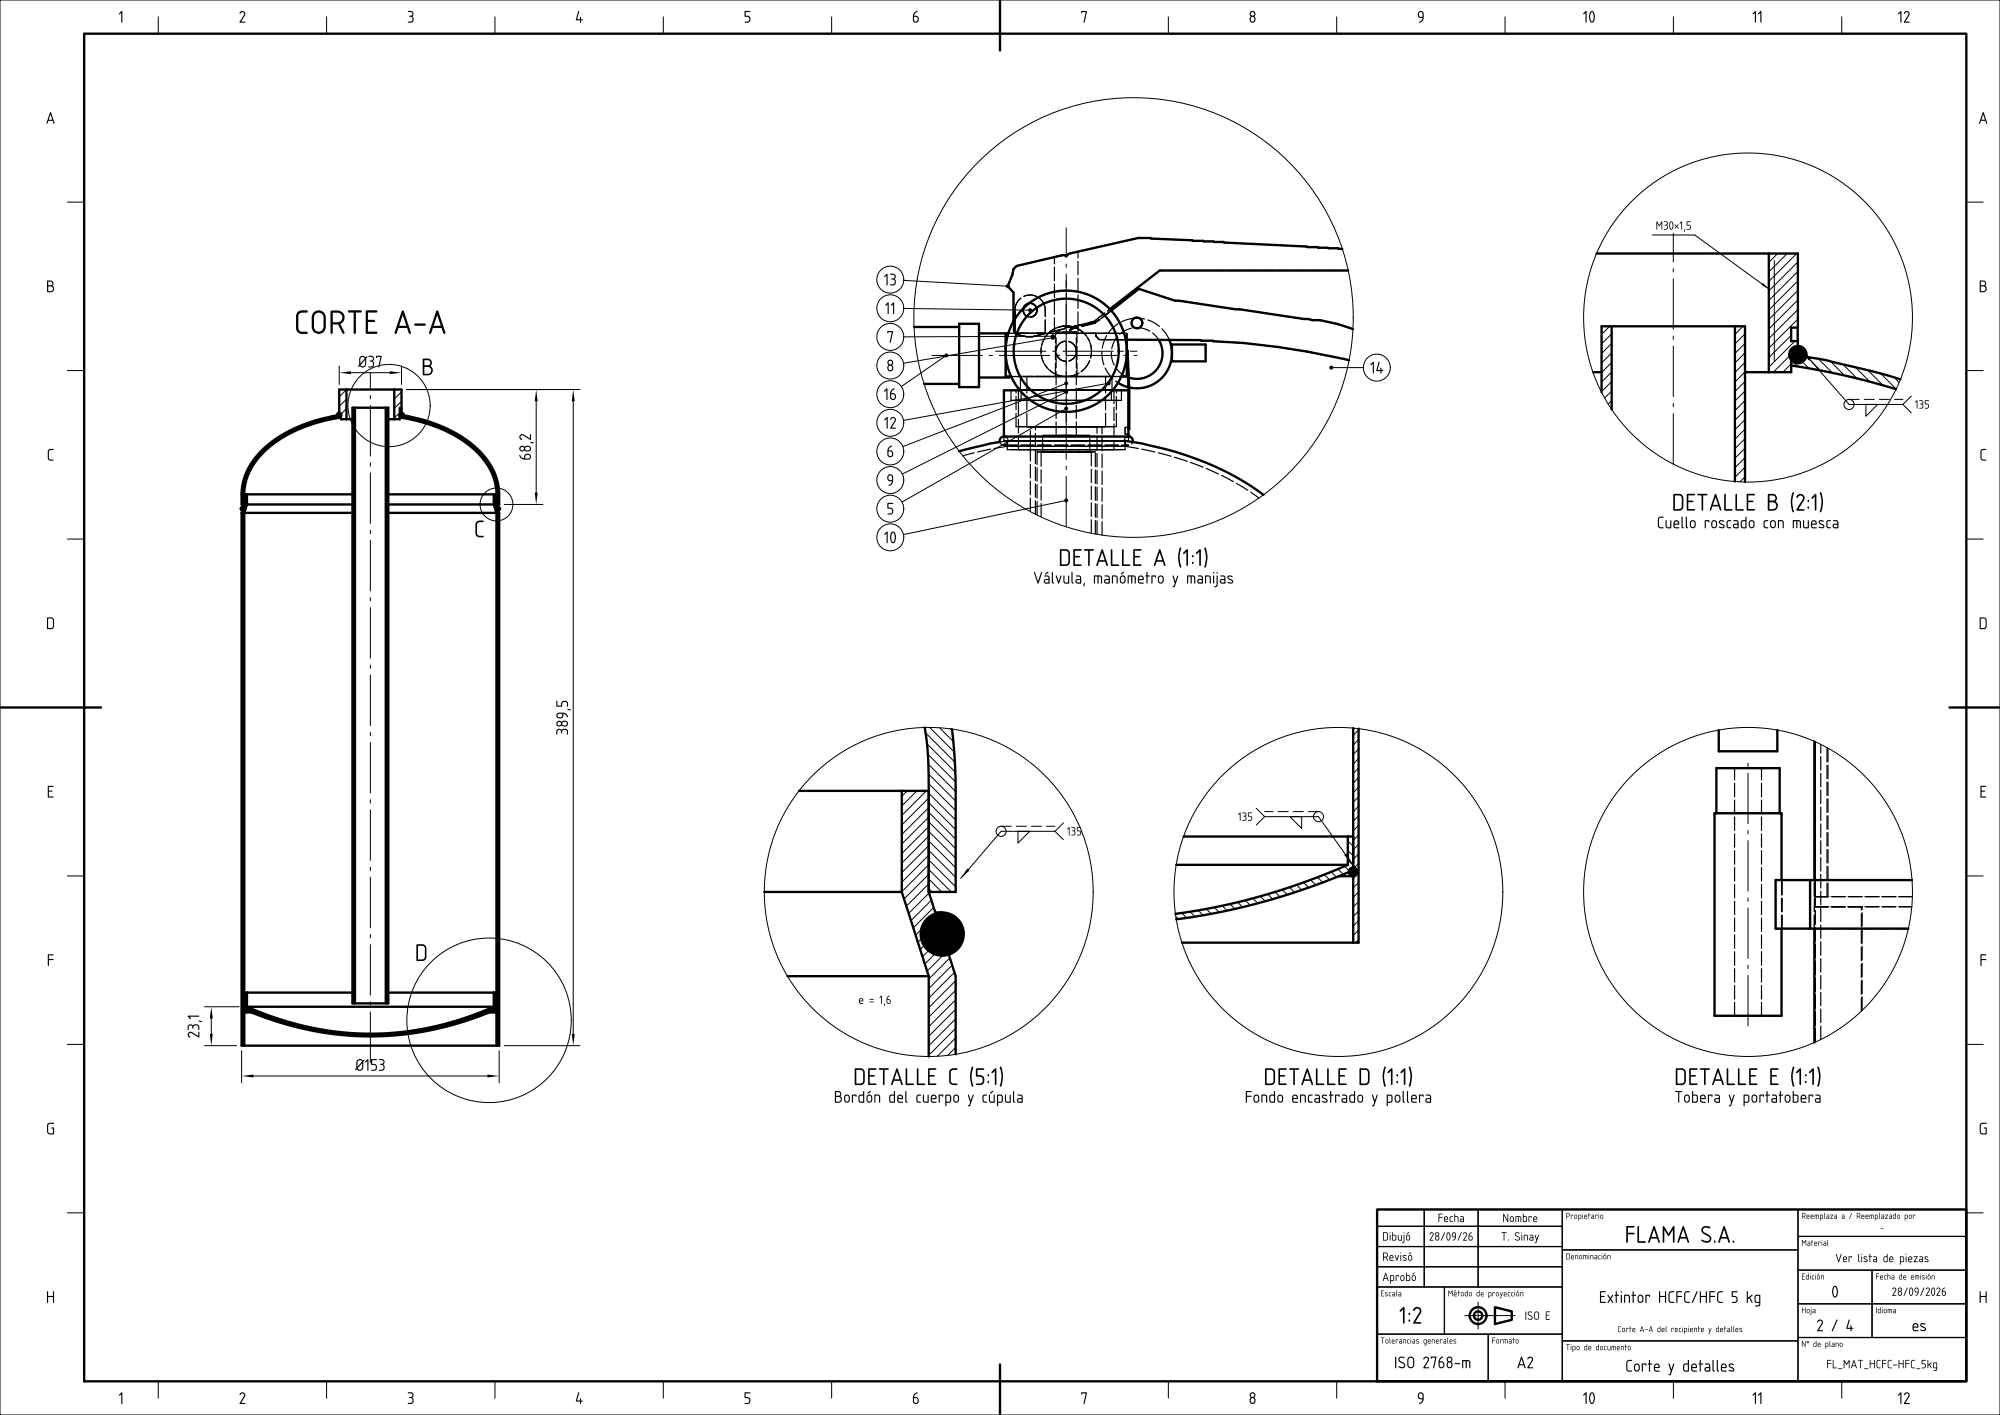
[picture p203: page 2]

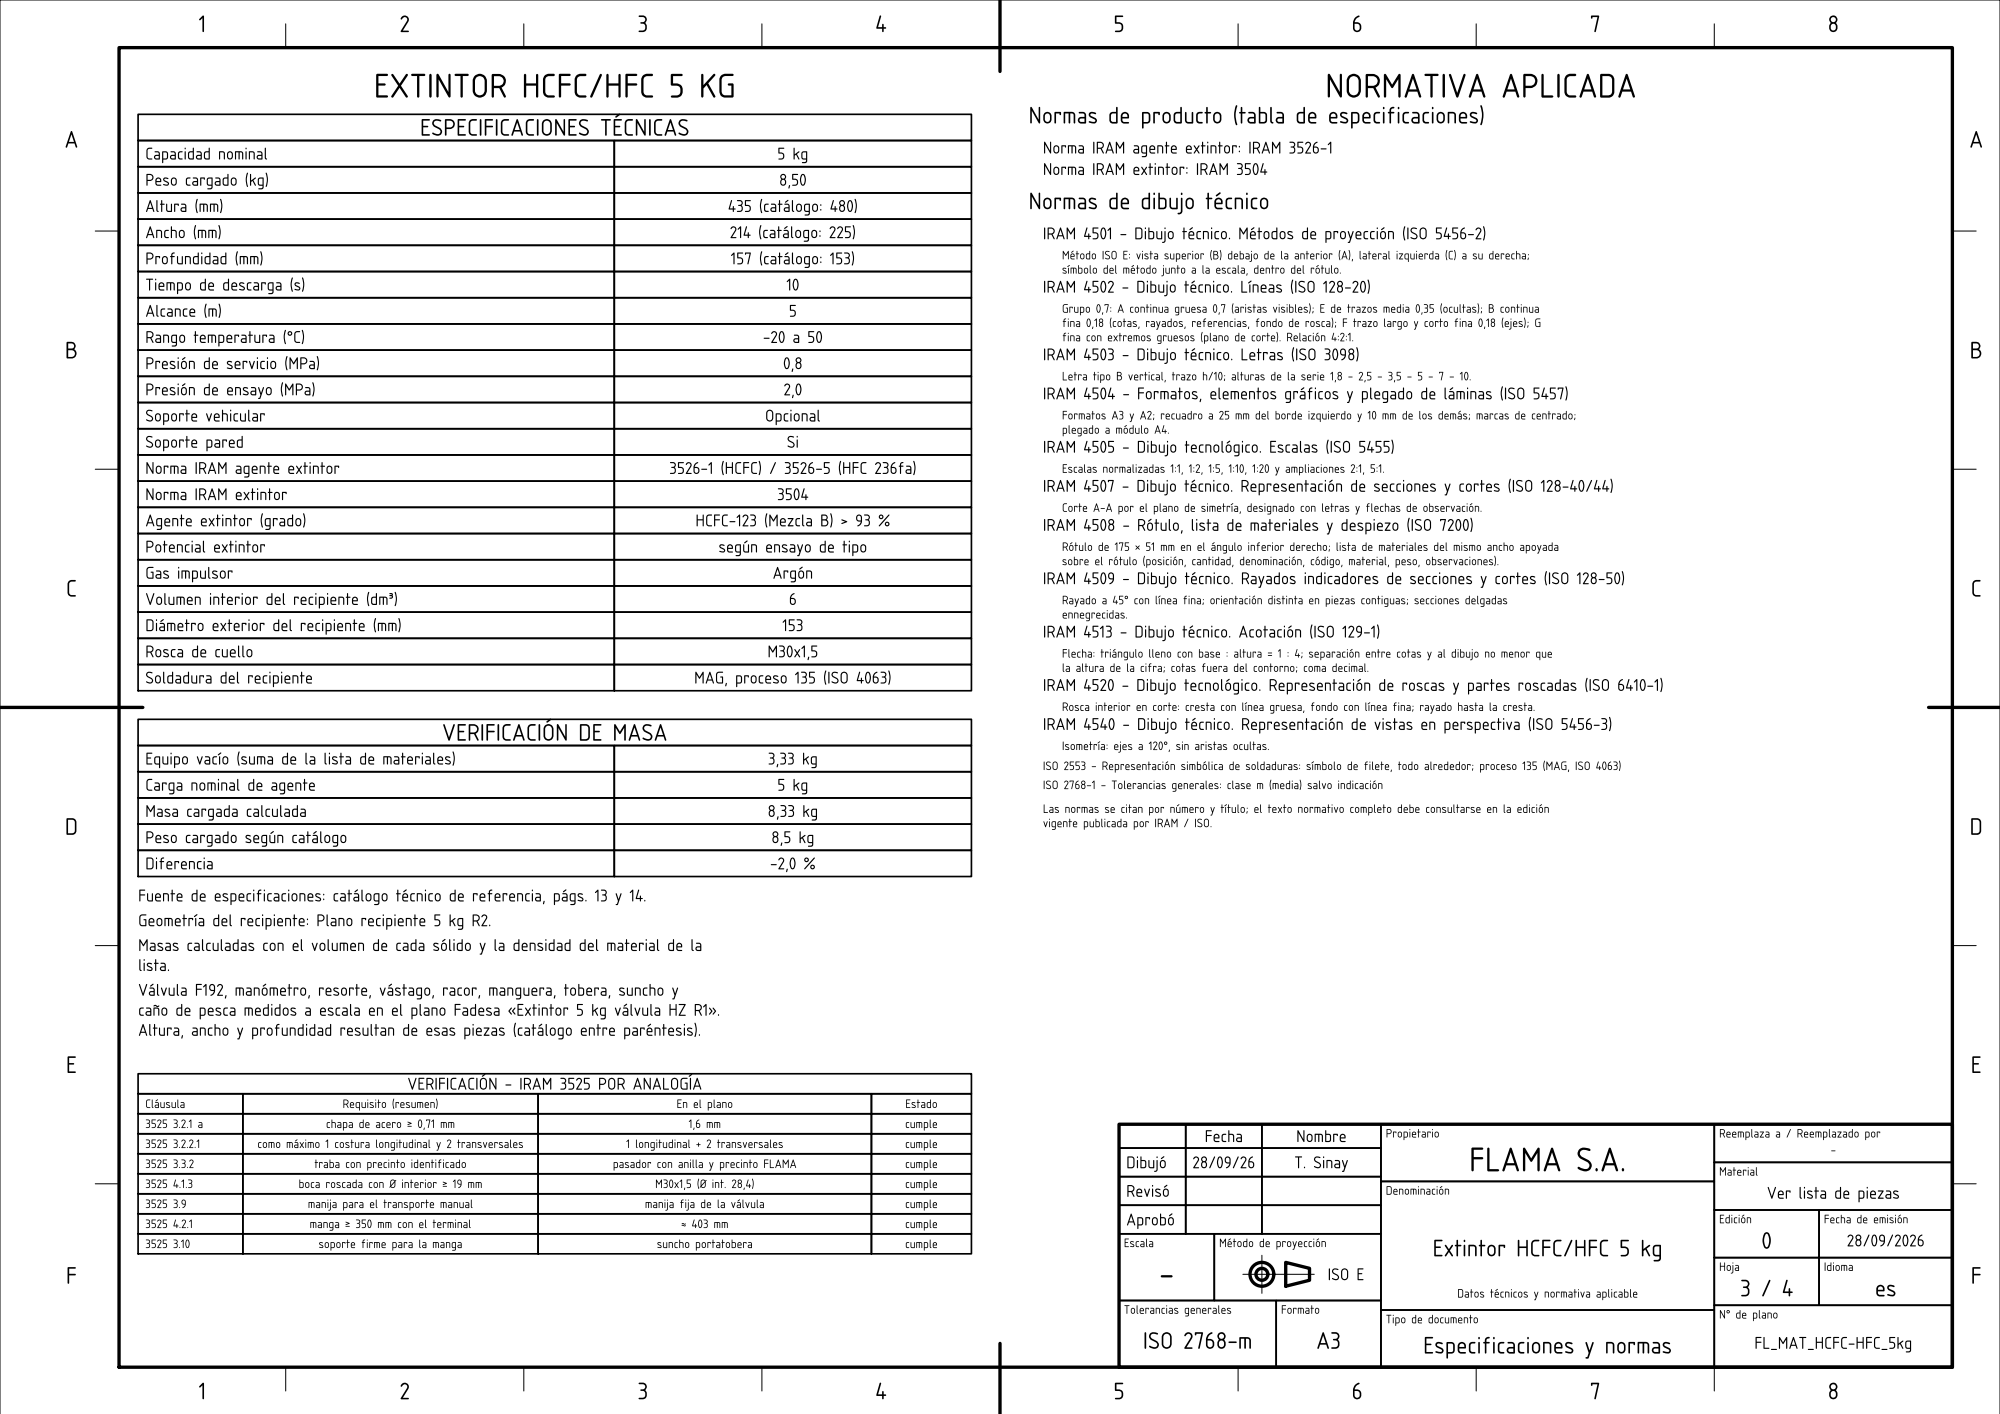
[picture p204: page 3]

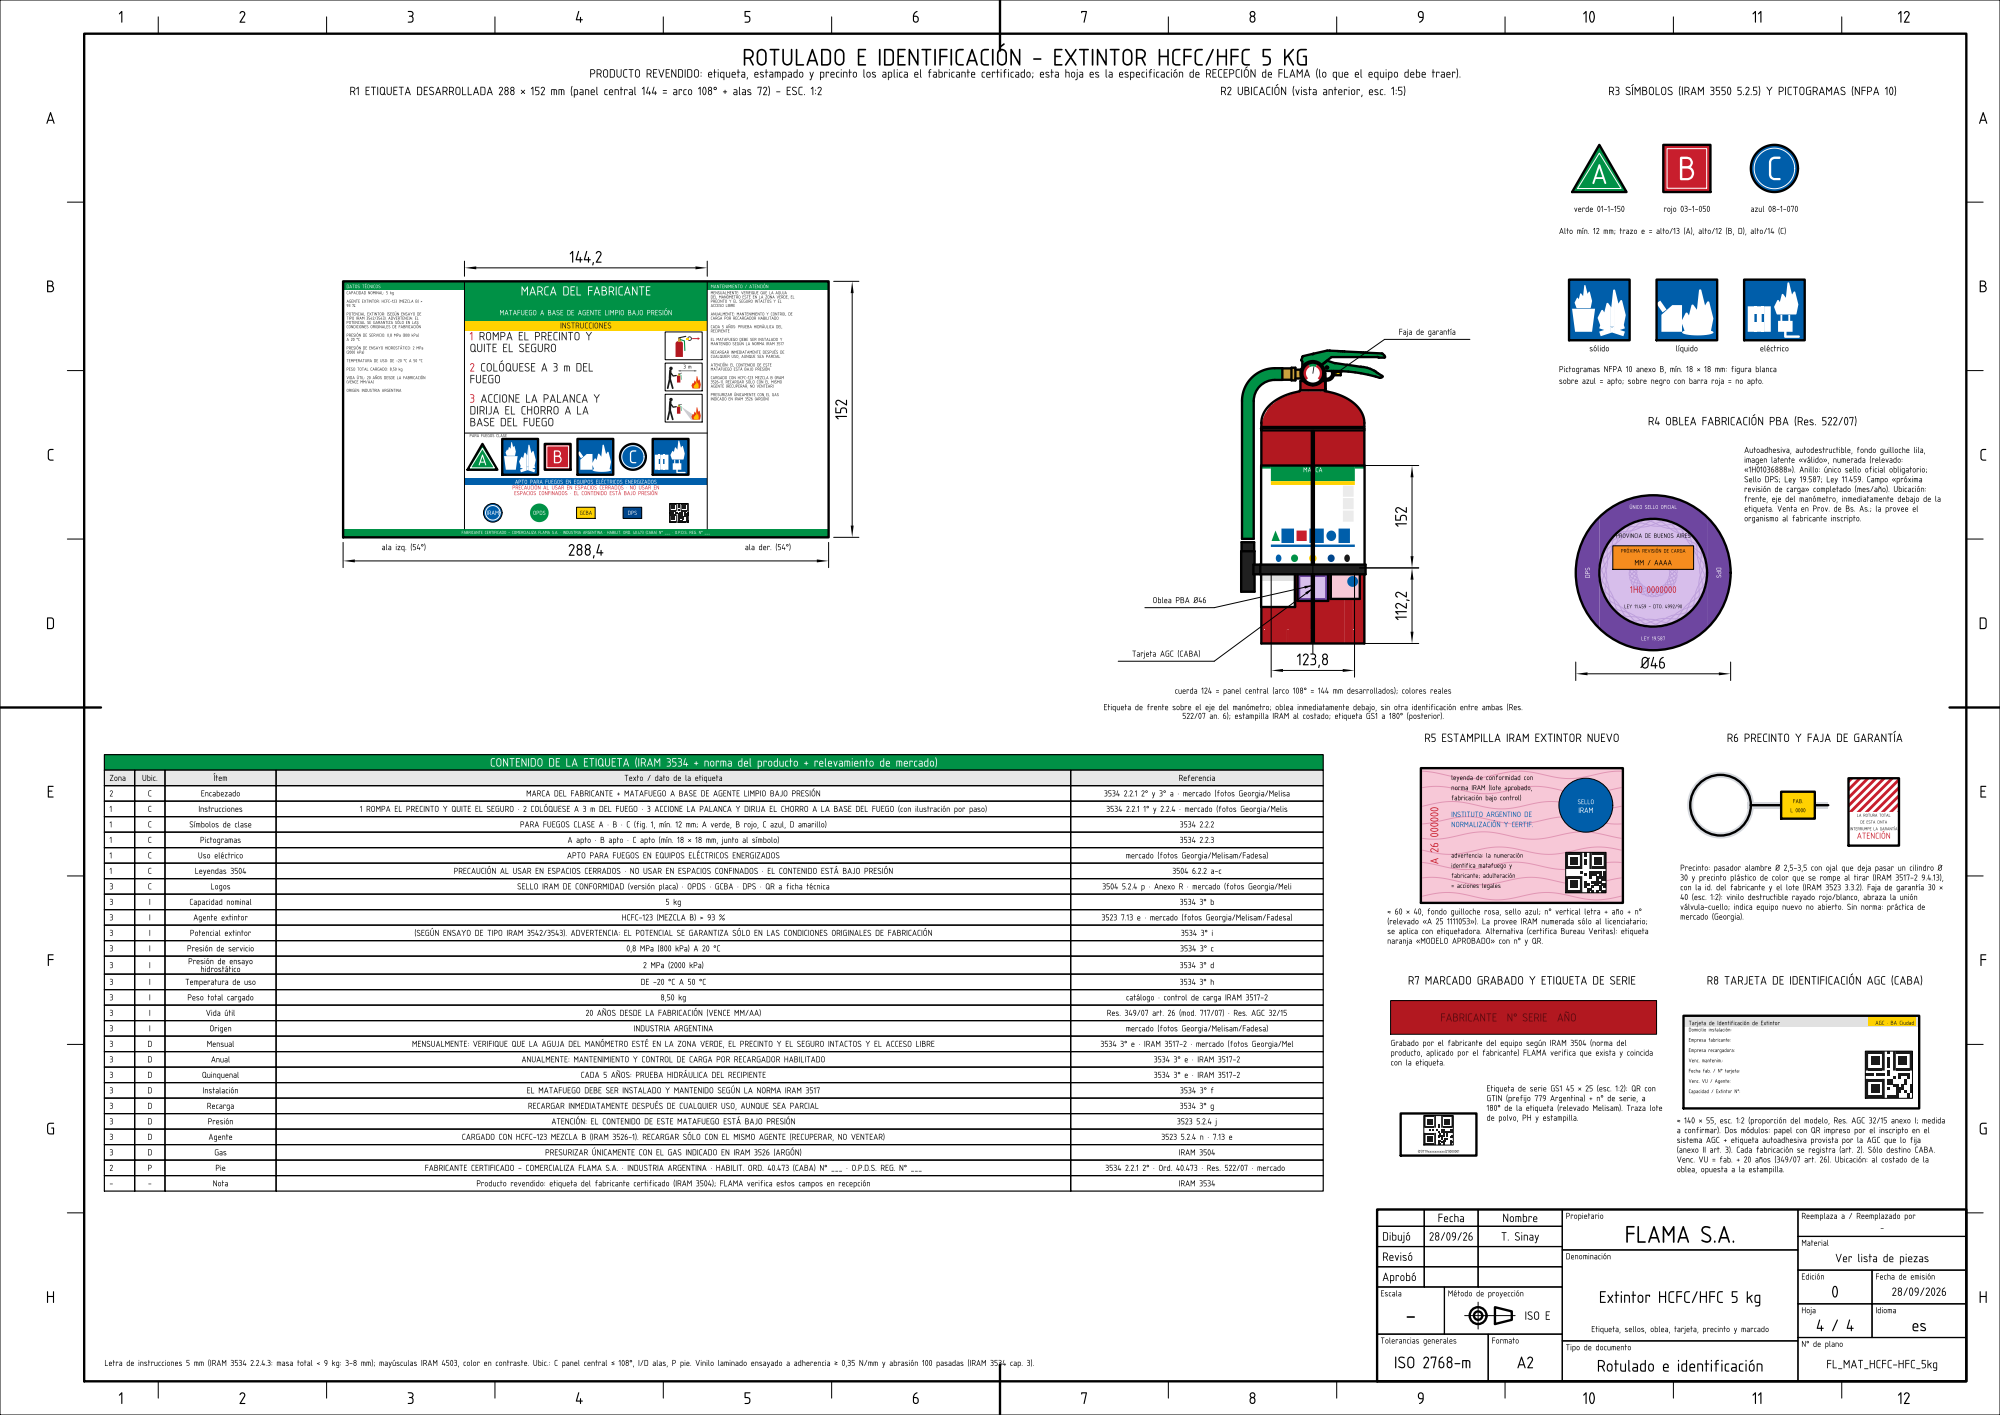
[picture p205: page 4]
