TadeoSinay/planos_flama-/salida/FL_MAT_SALESK_6l/FL_MAT_SALESK_6l.pdf

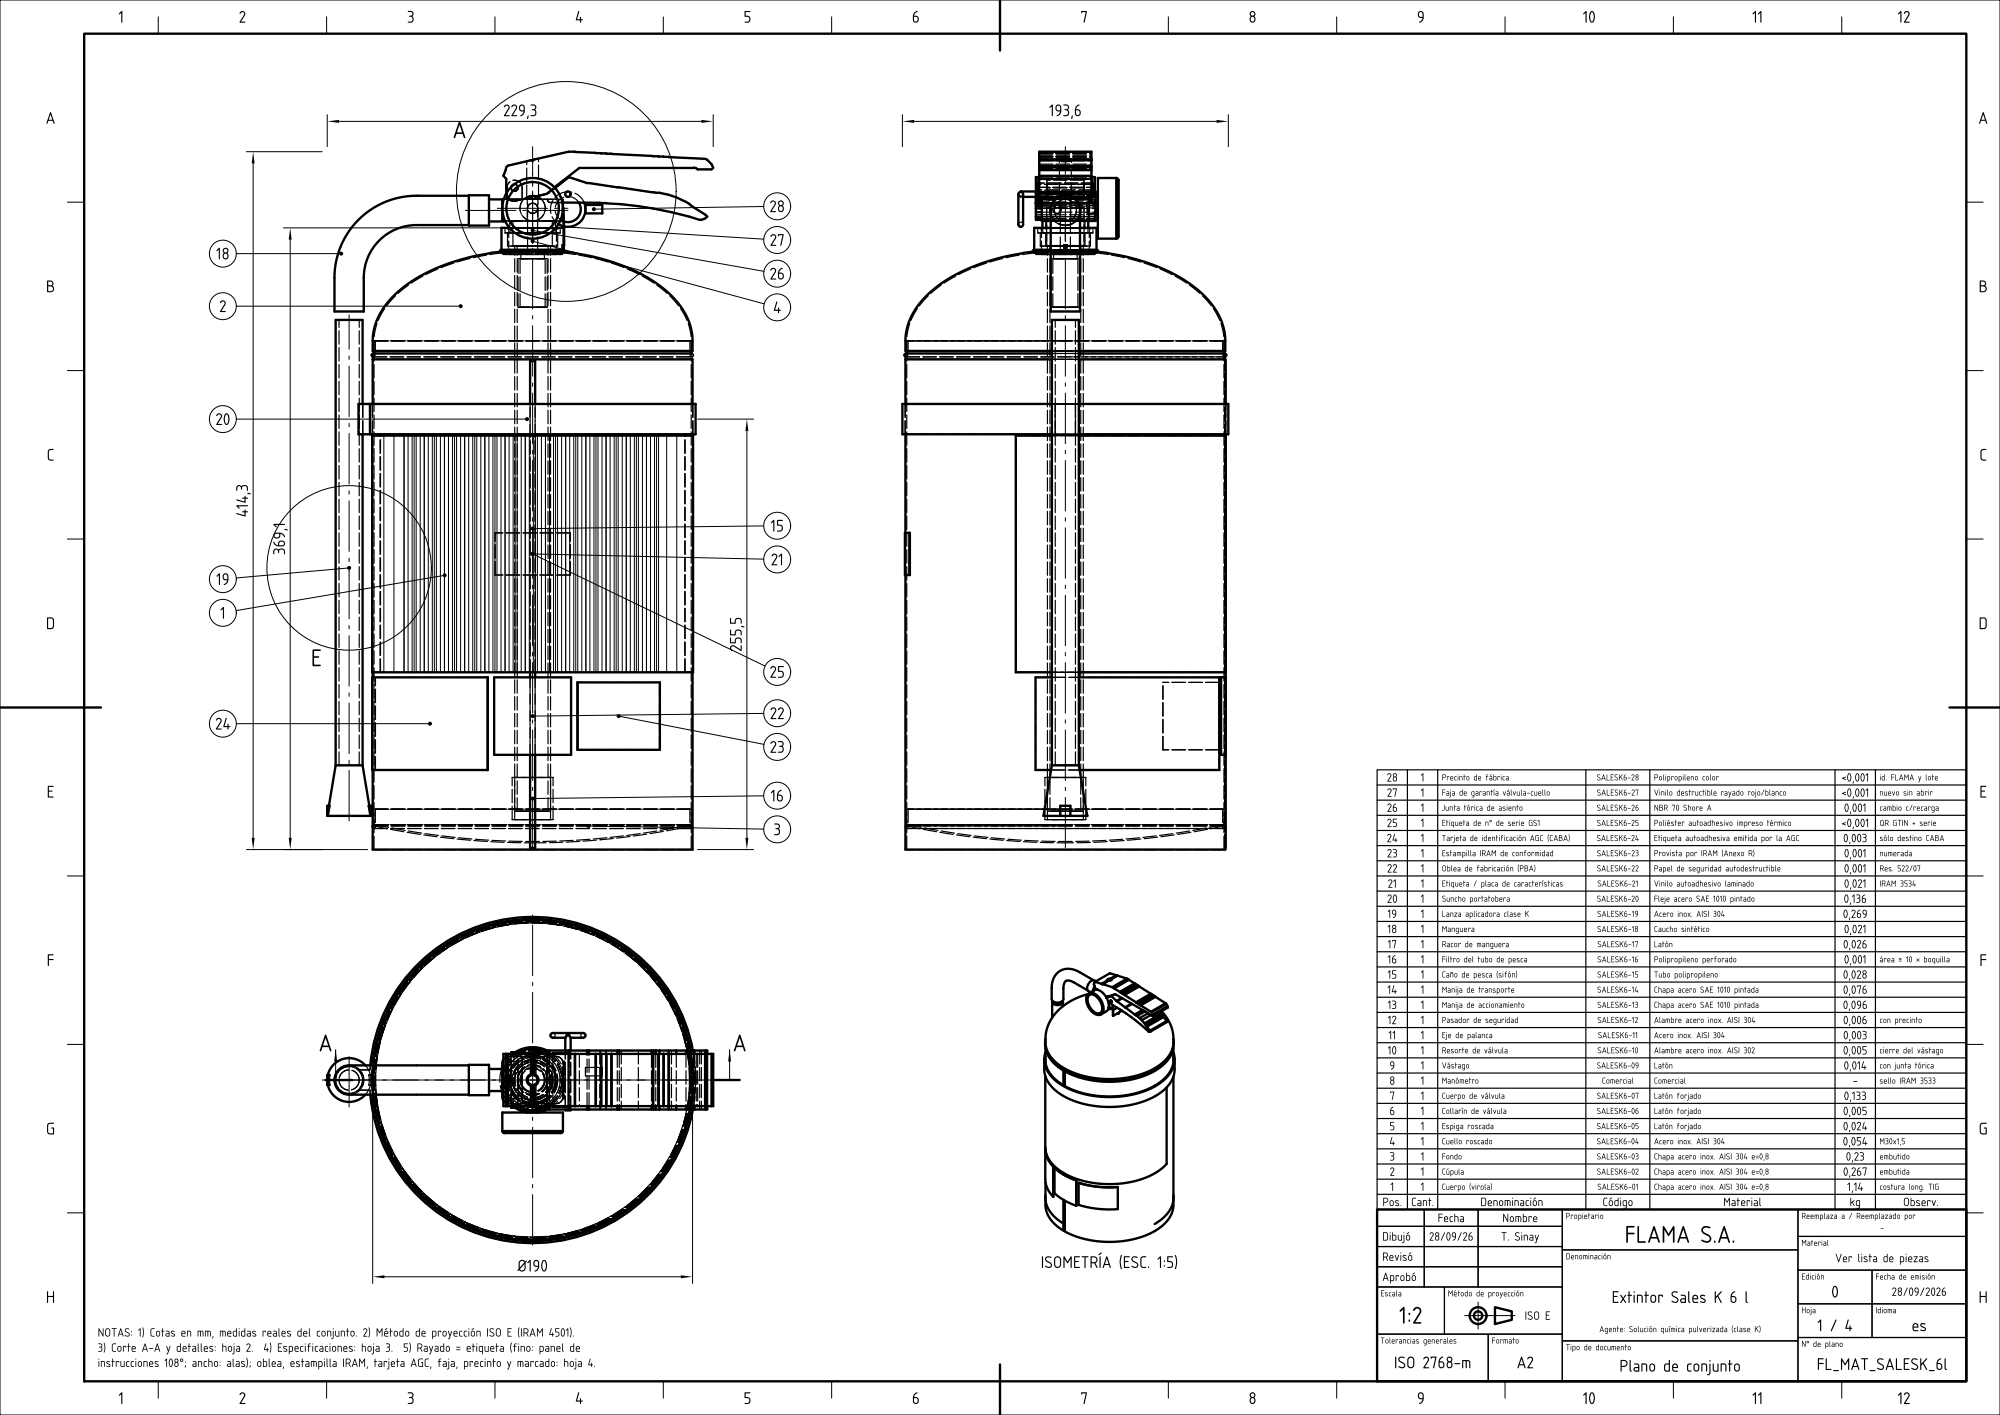
[picture p206: page 1]

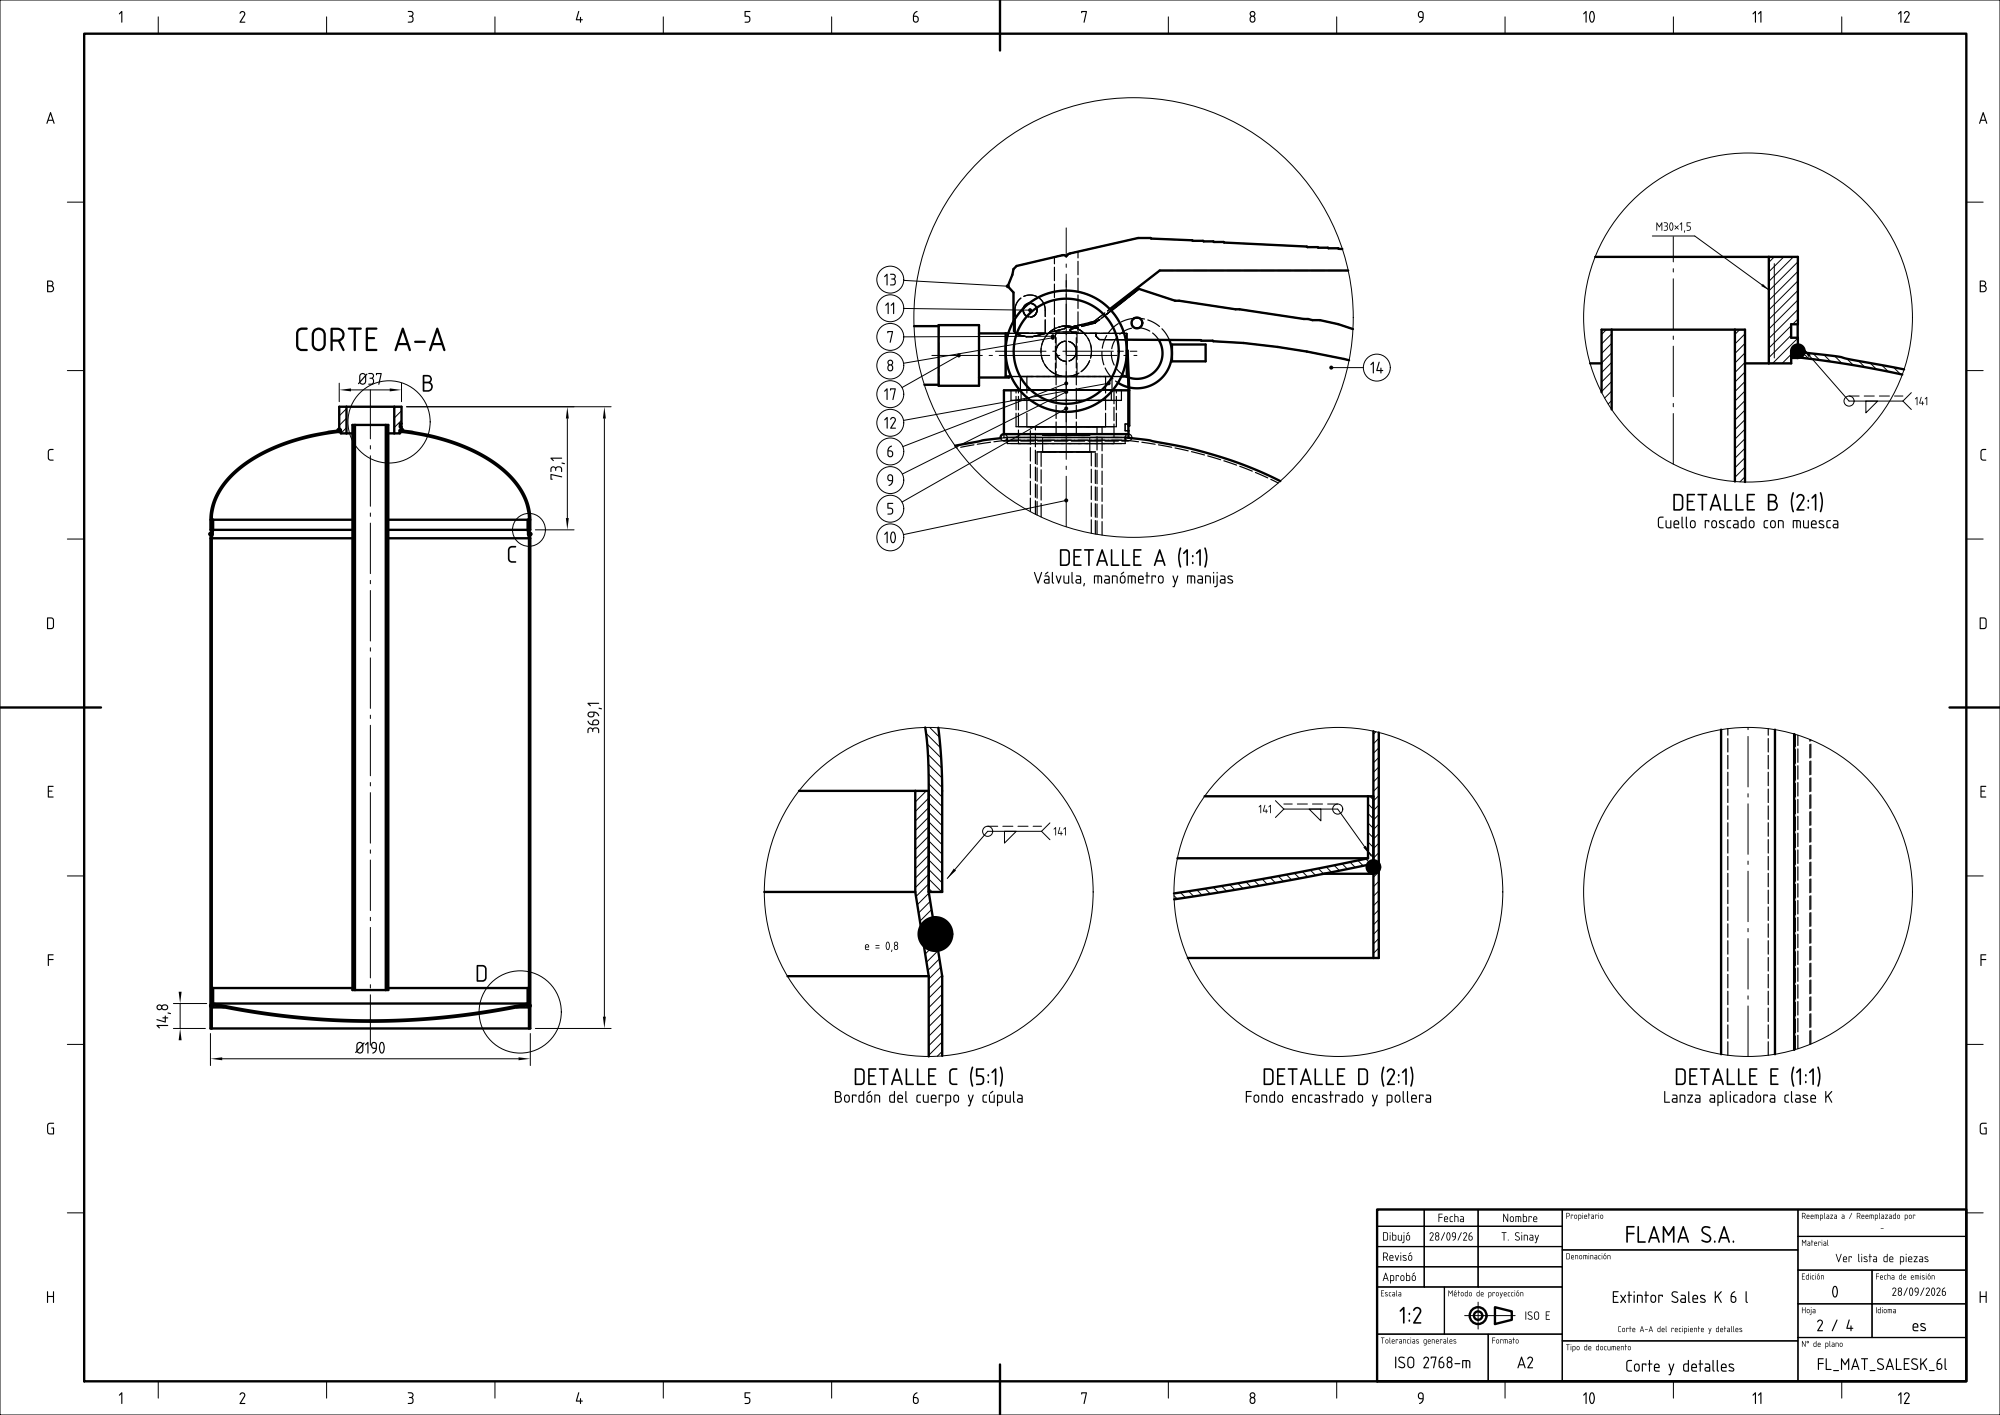
[picture p207: page 2]

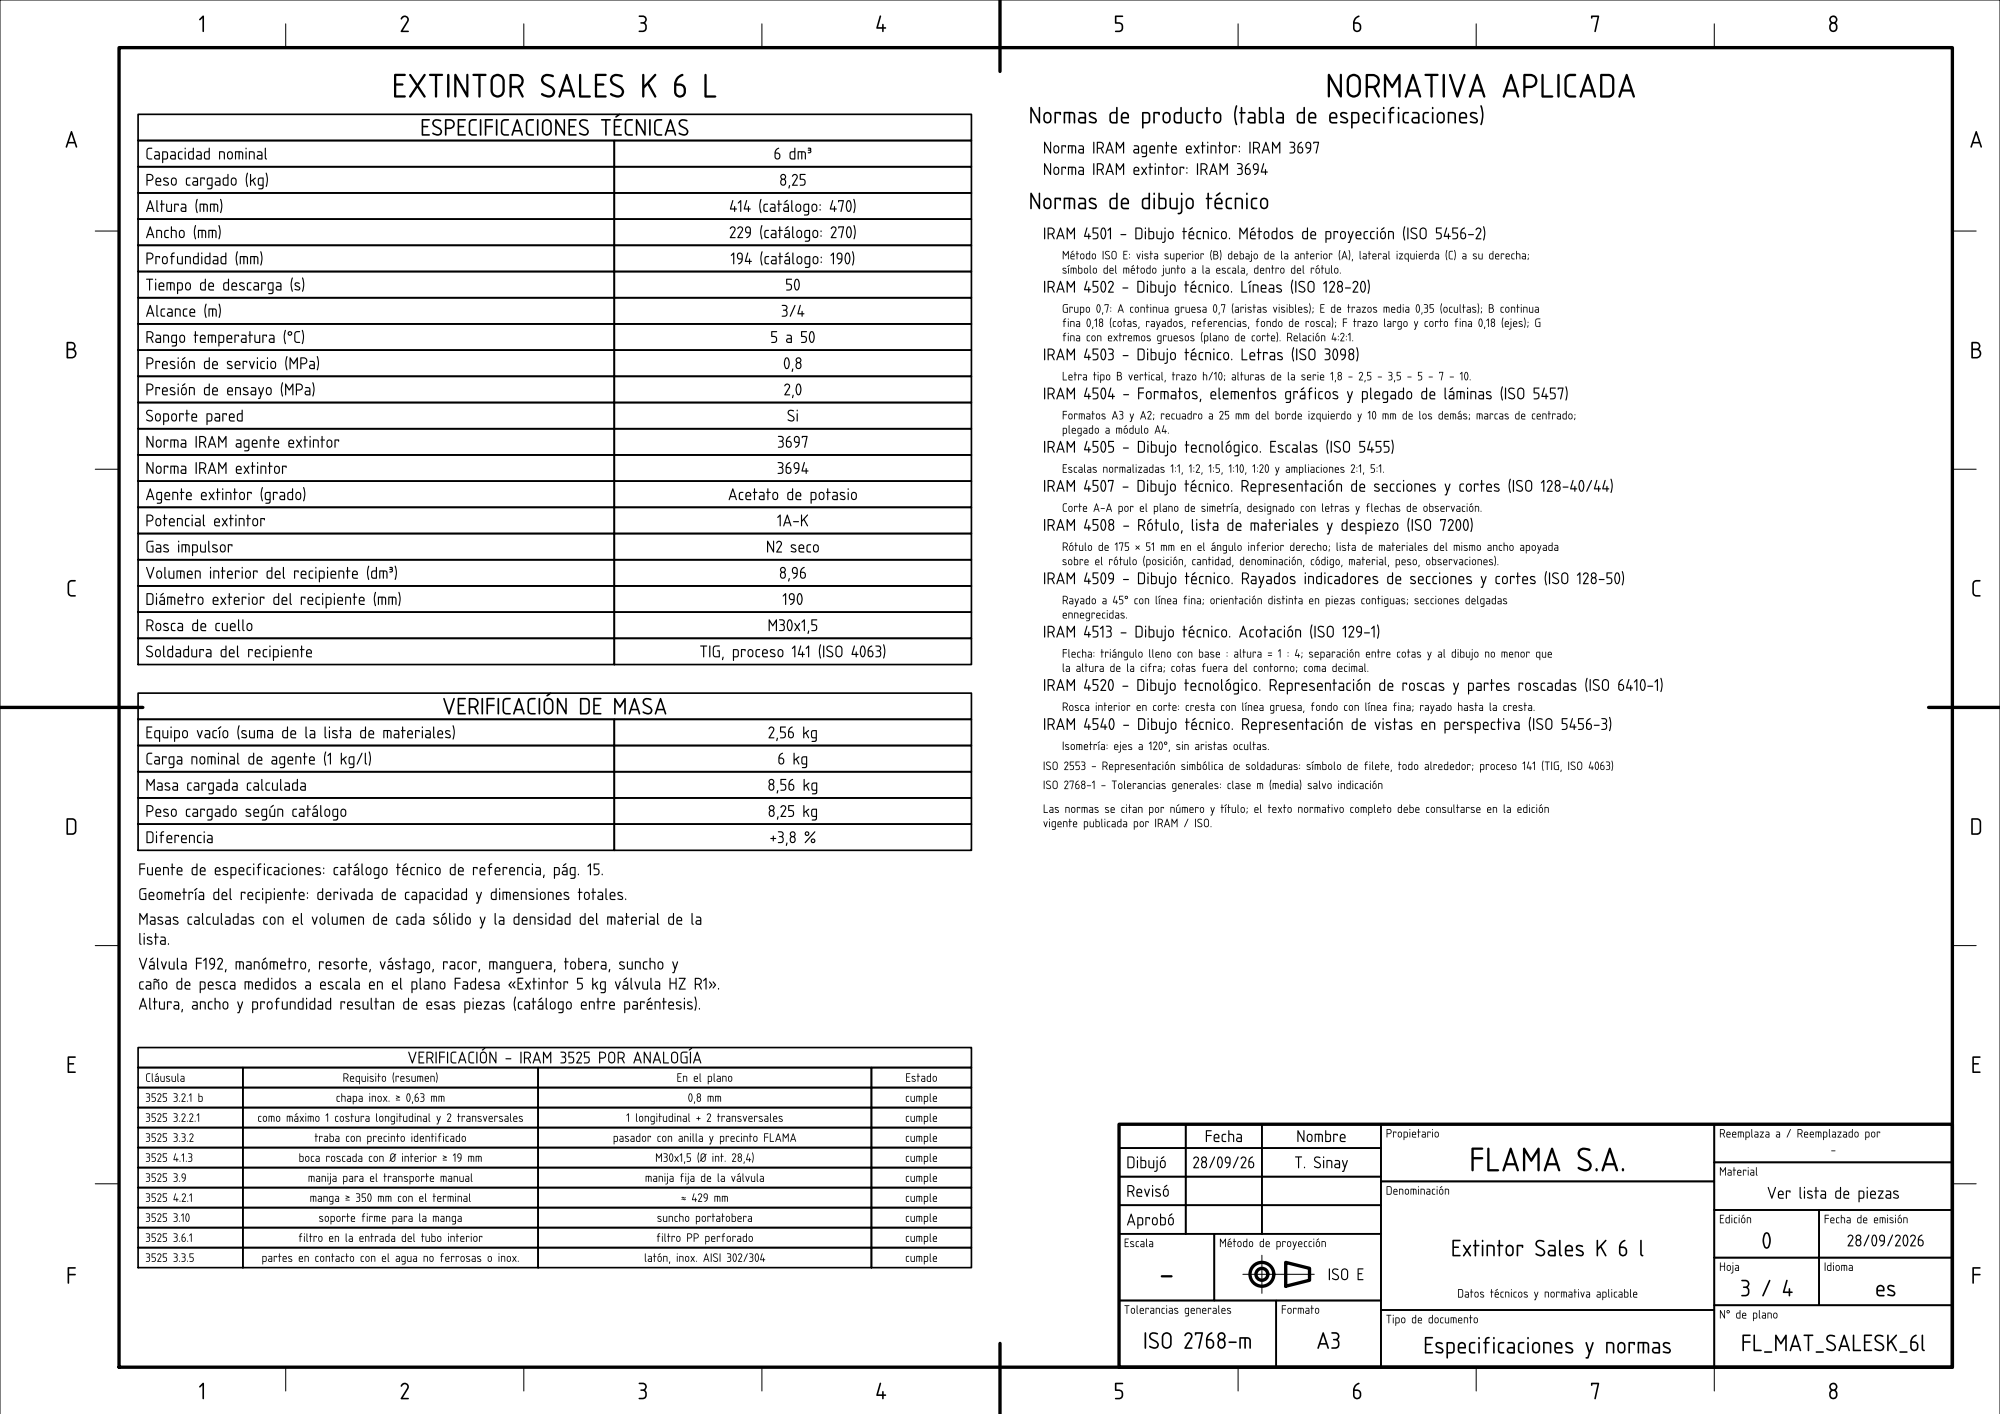
[picture p208: page 3]

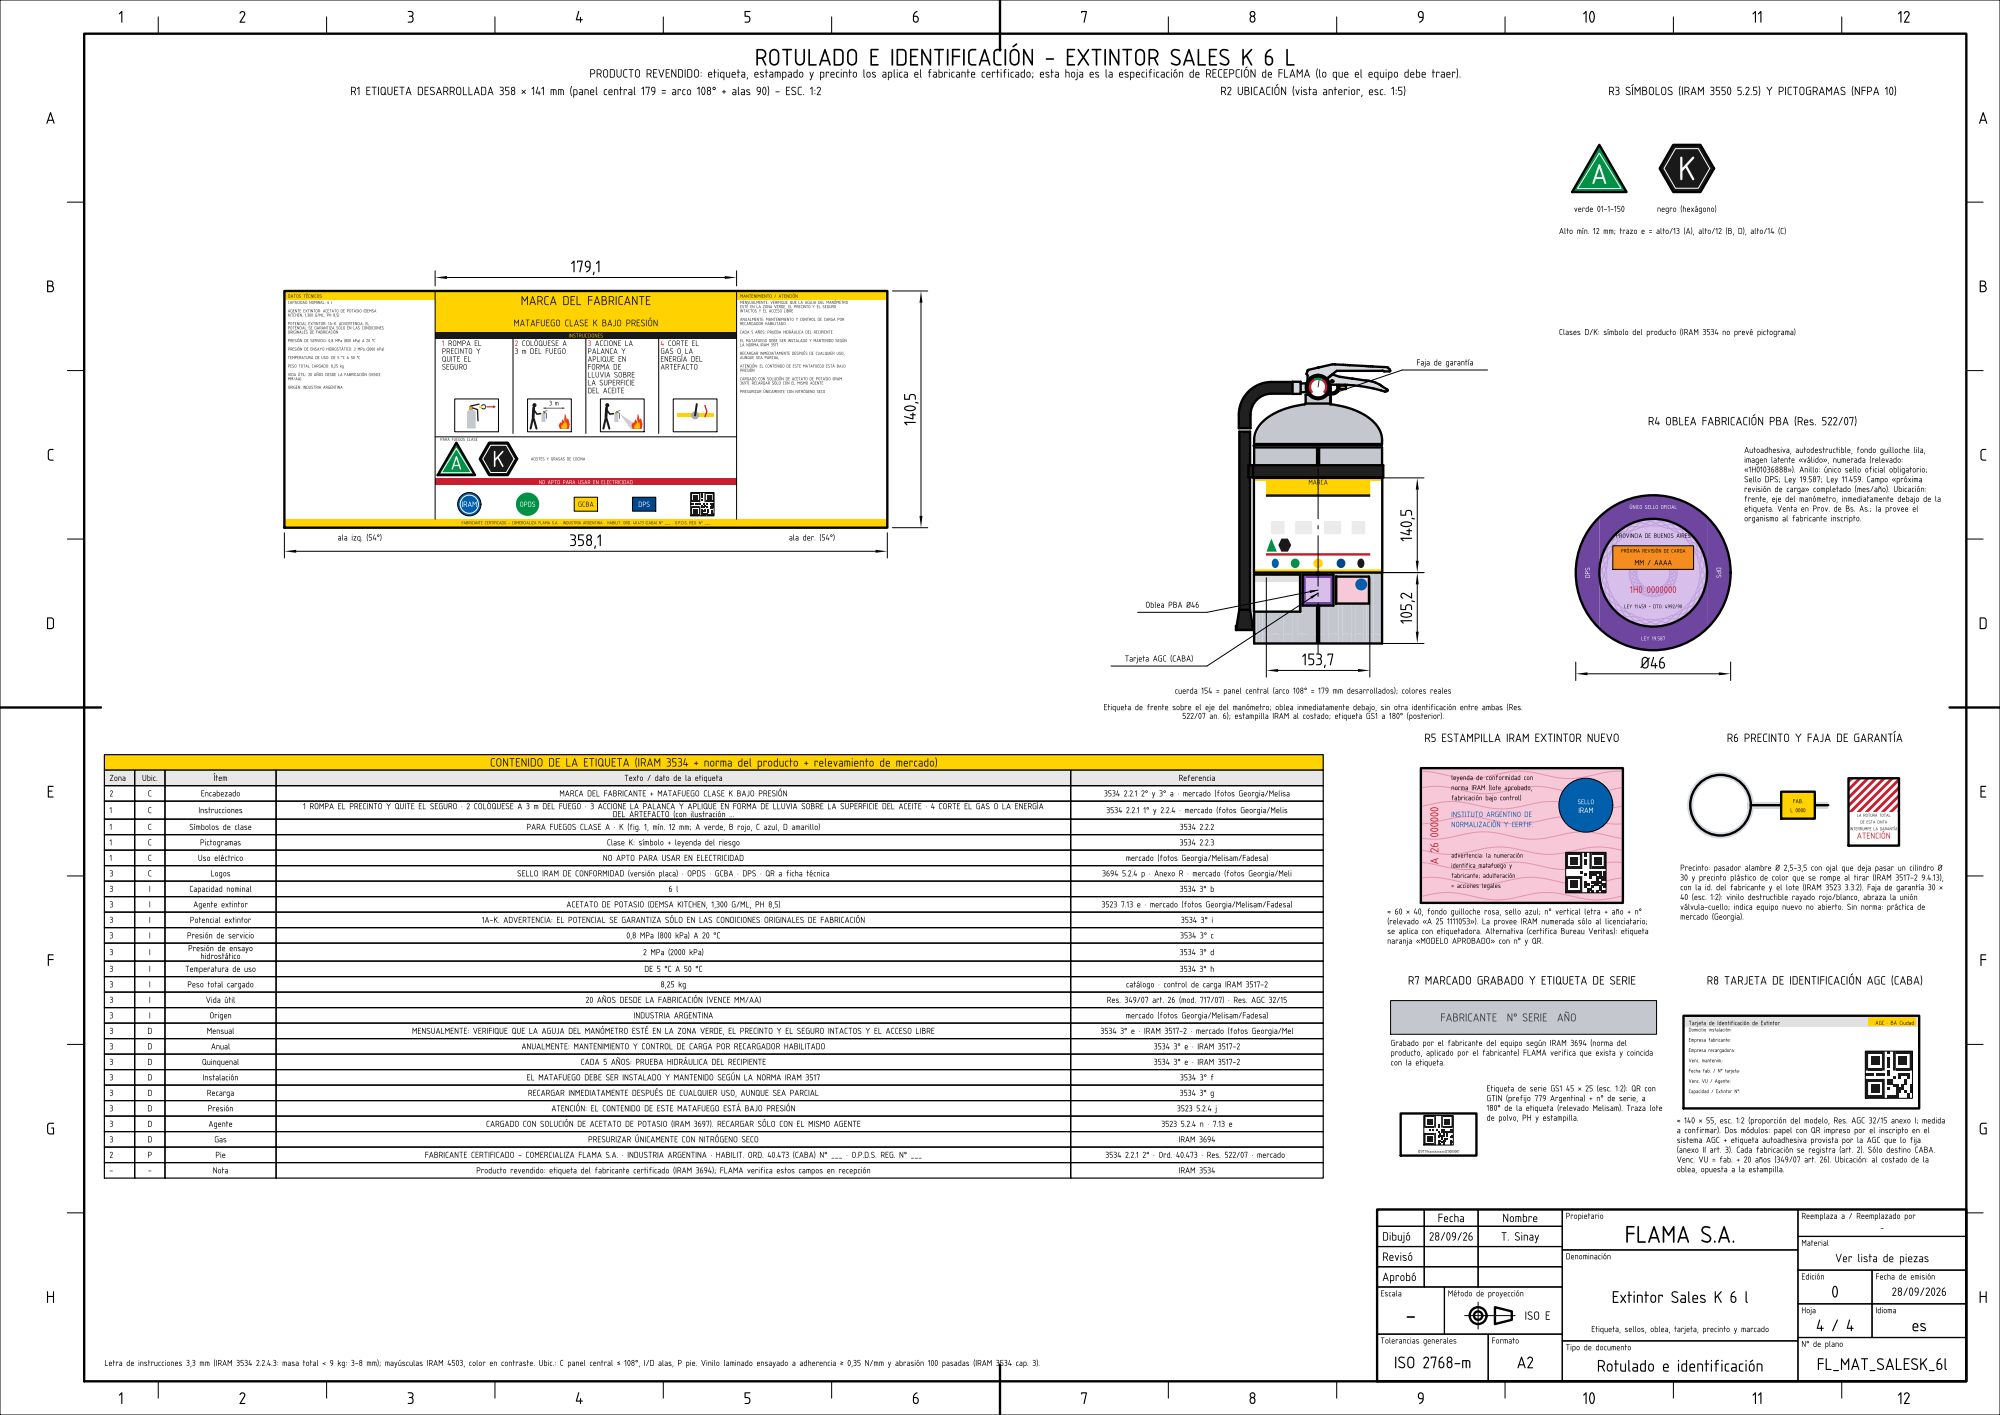
[picture p209: page 4]
