TadeoSinay/planos_flama-/salida/sustituto/FL_SUS_00.pdf

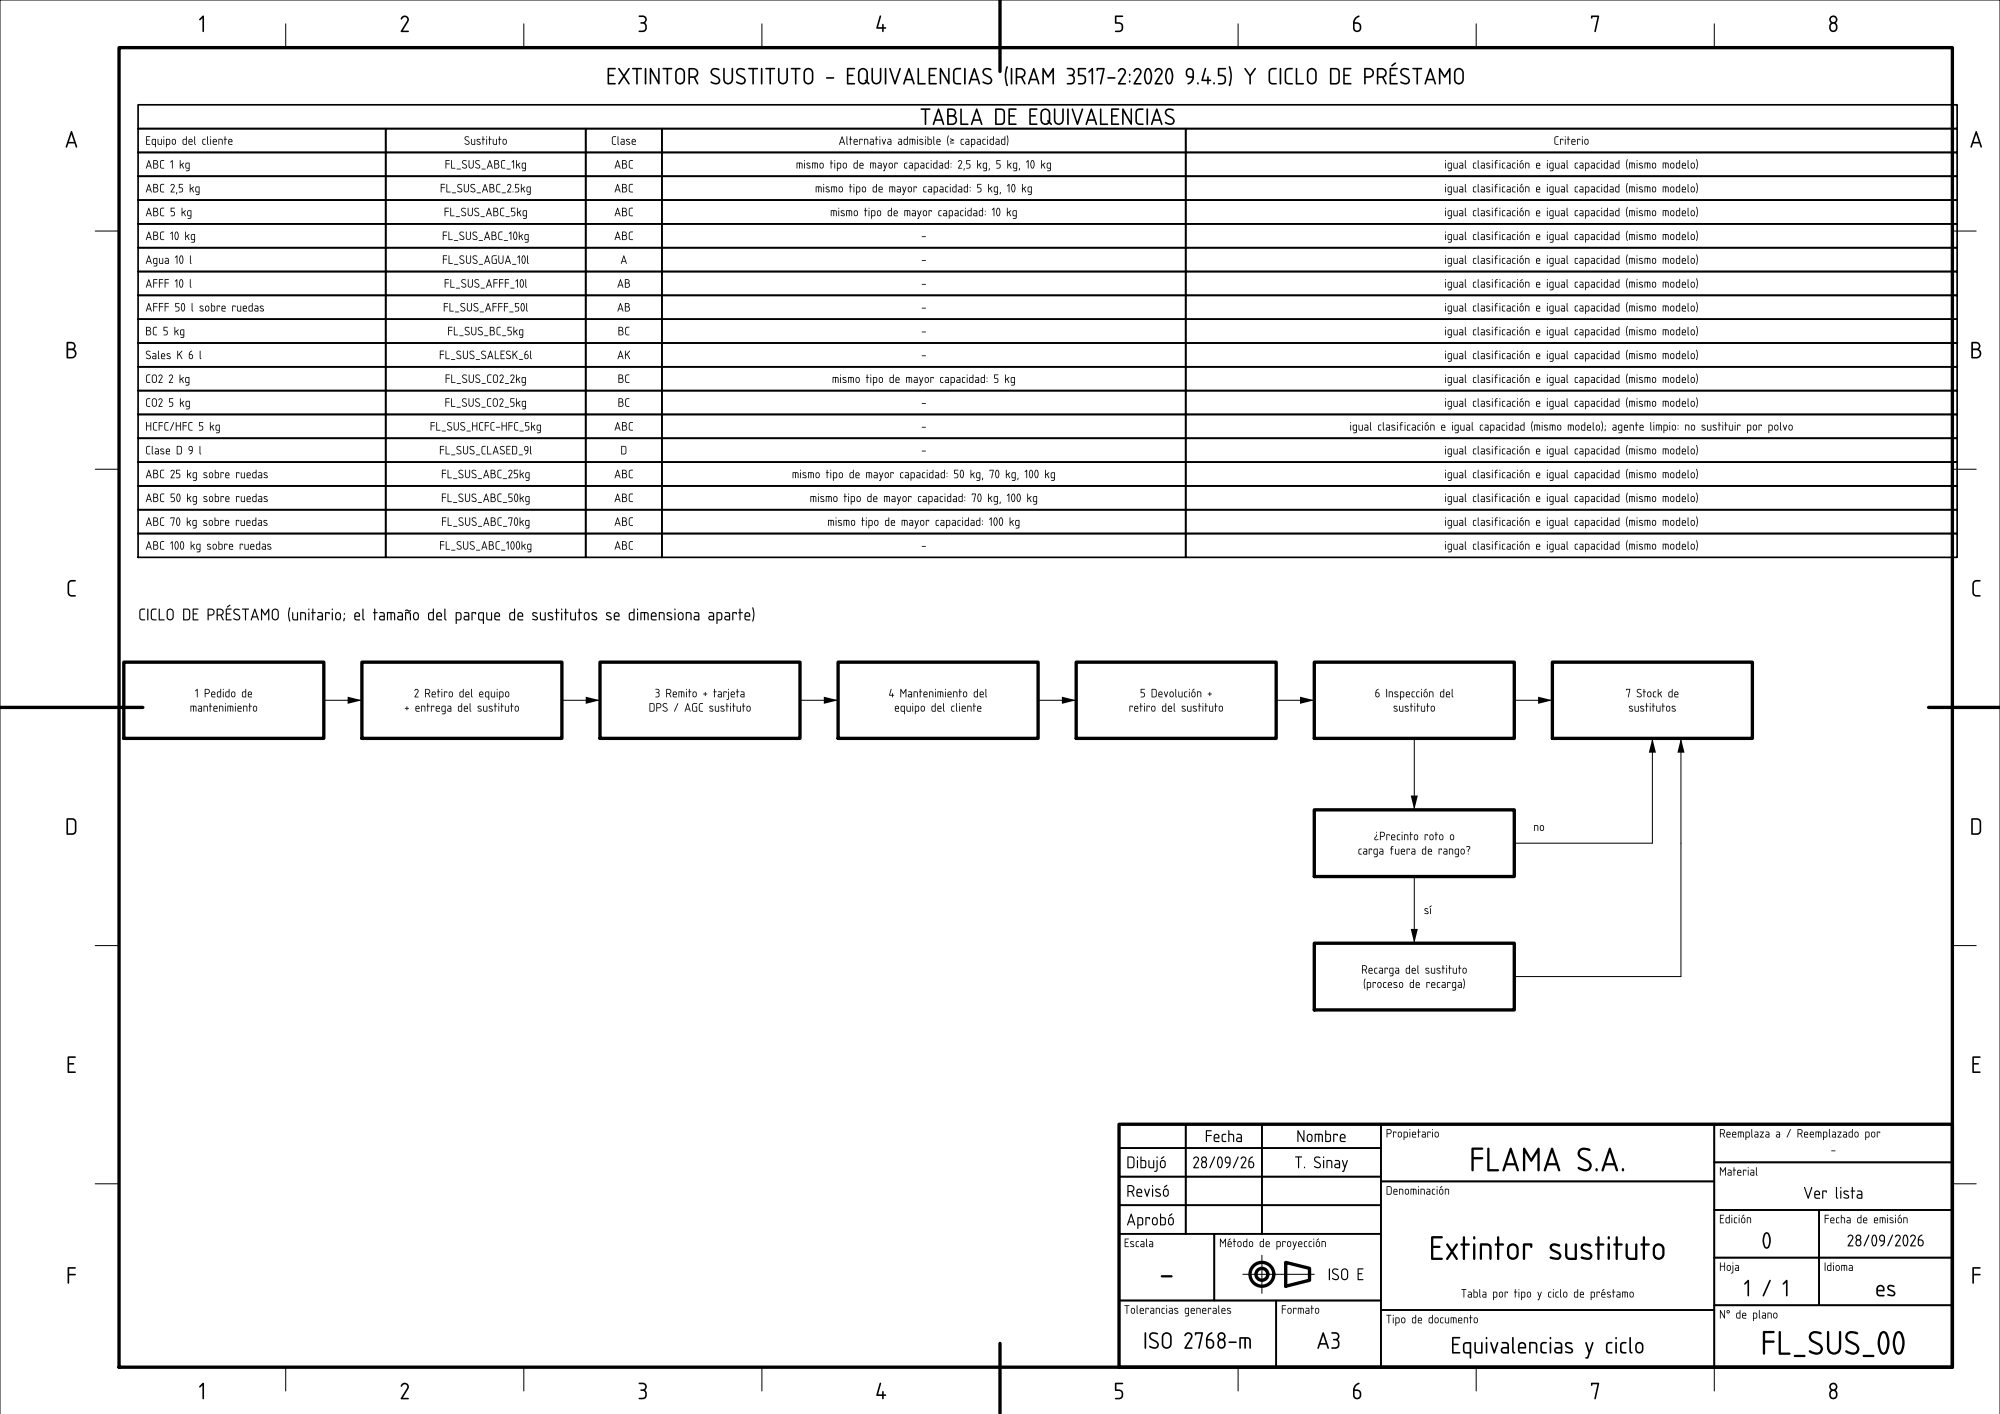
[picture p210: page 1]
