TadeoSinay/planos_flama-/salida/sustituto/FL_SUS_ABC_100kg.pdf

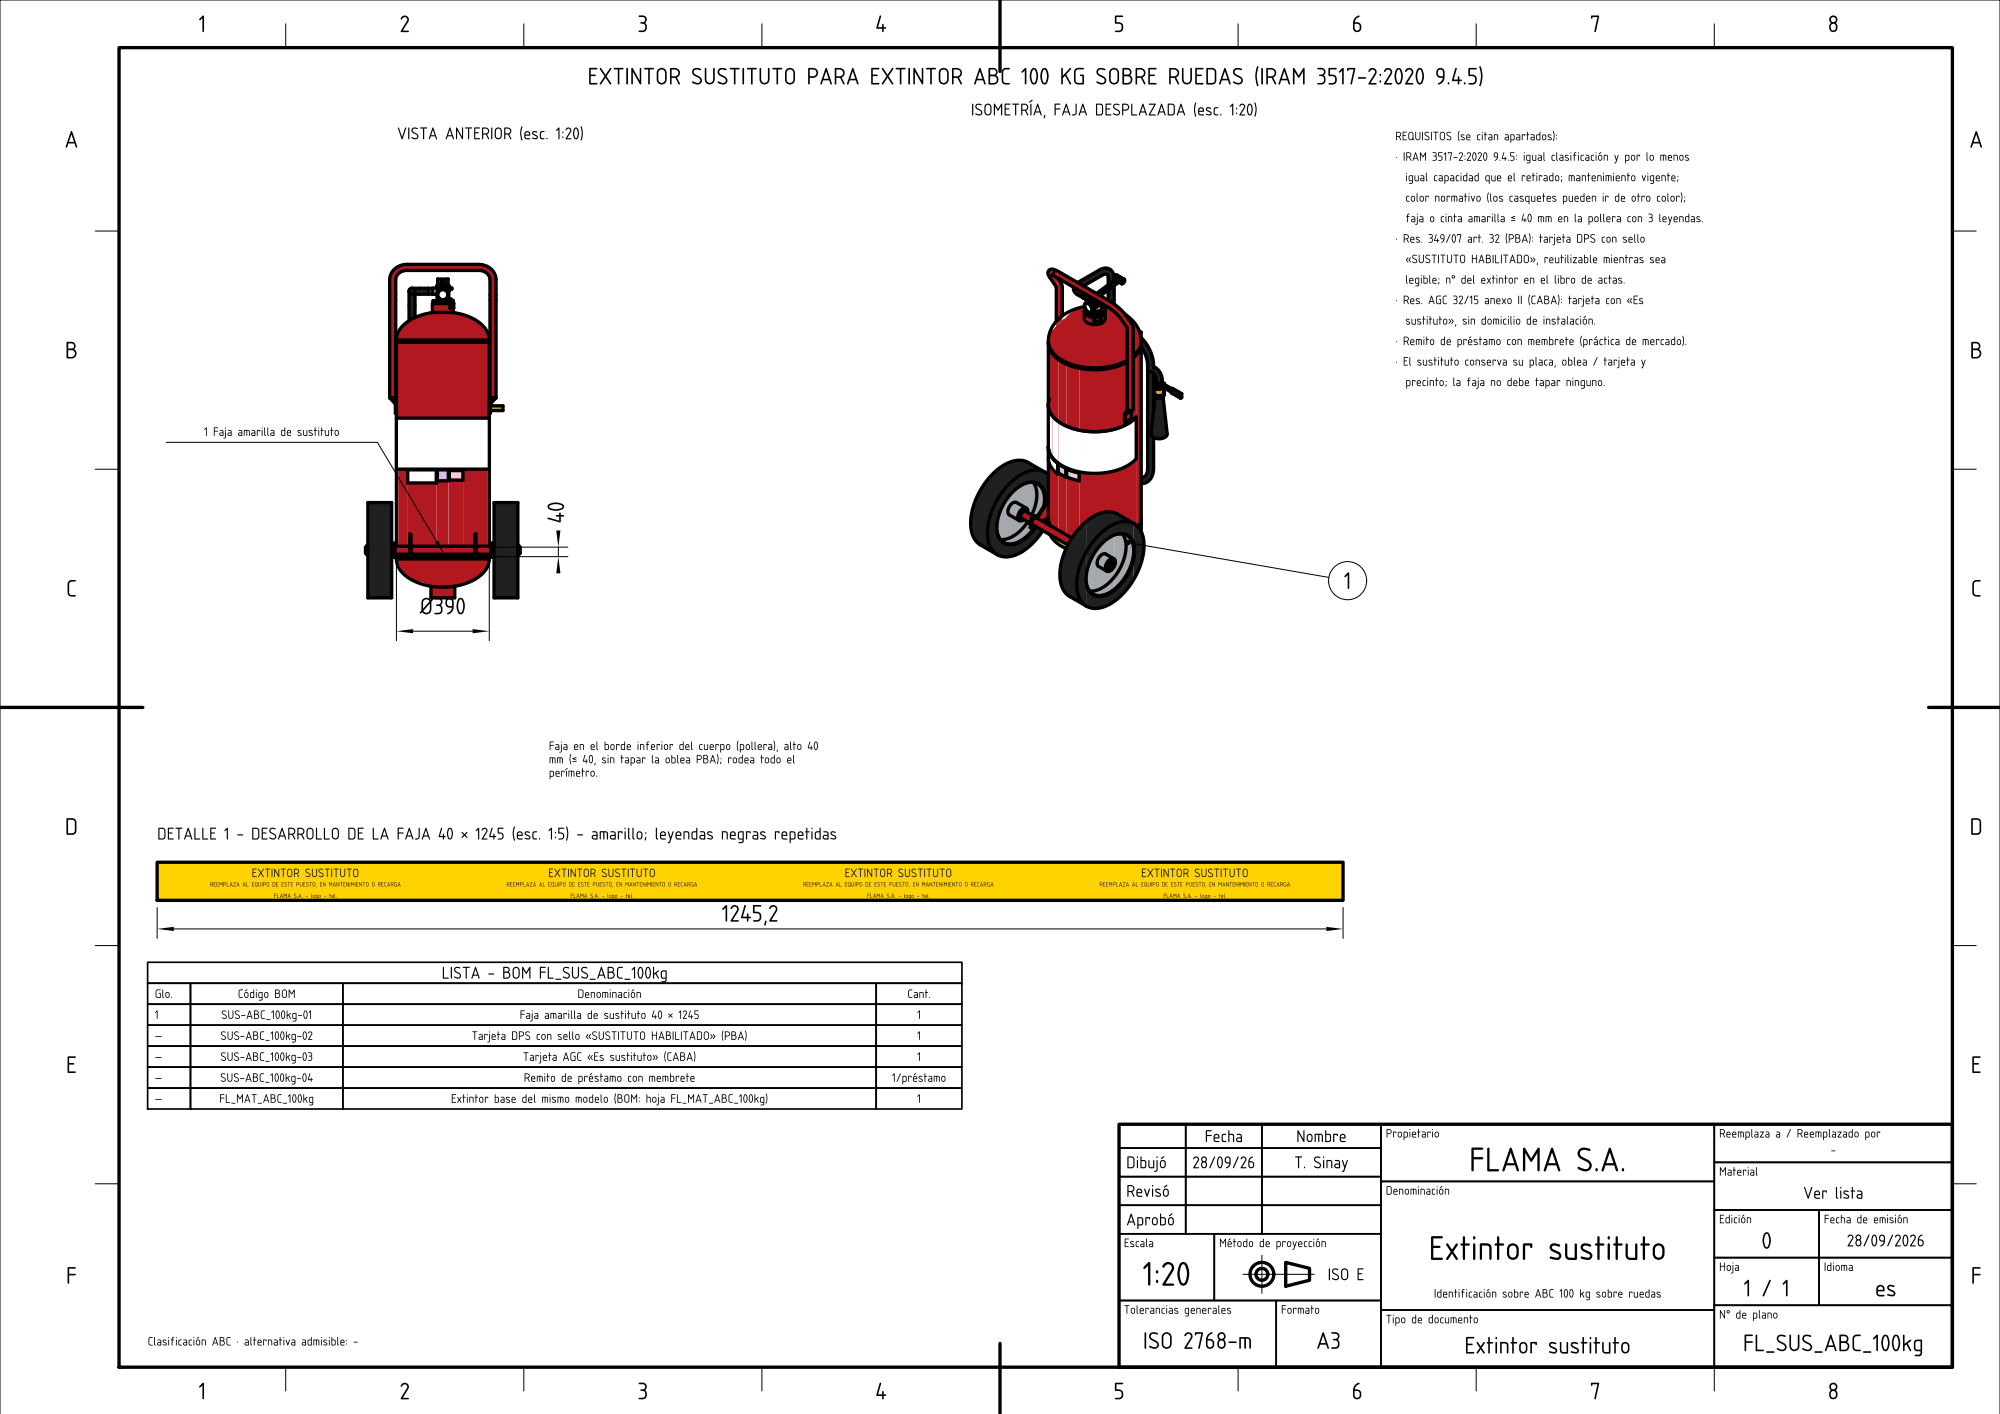
[picture p211: page 1]
