TadeoSinay/planos_flama-/salida/sustituto/FL_SUS_ABC_10kg.pdf

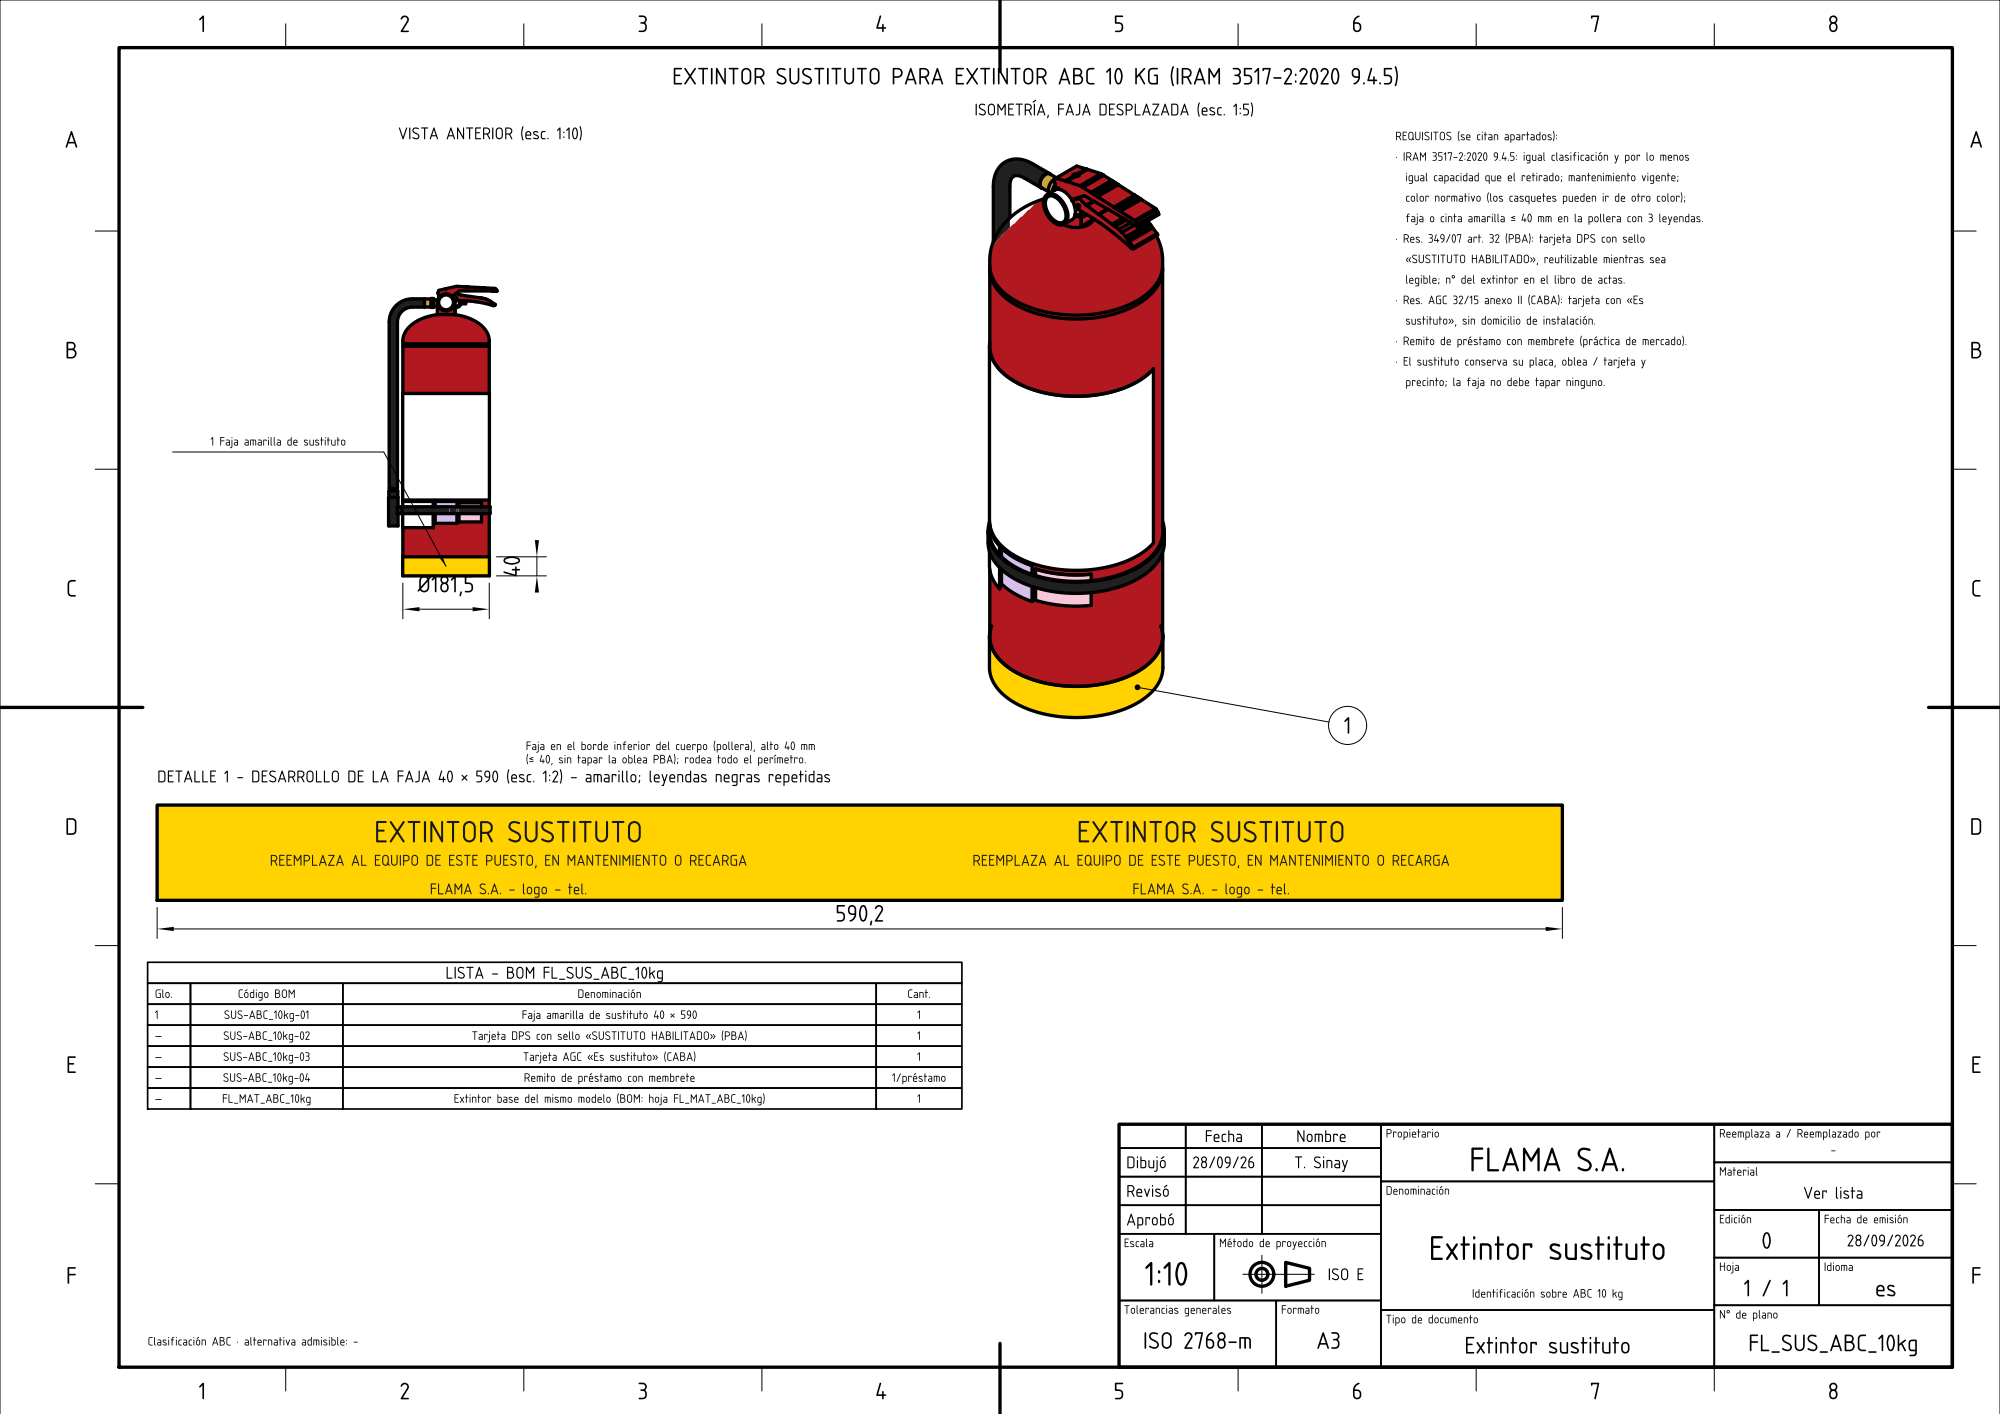
[picture p212: page 1]
