TadeoSinay/planos_flama-/salida/sustituto/FL_SUS_ABC_1kg.pdf

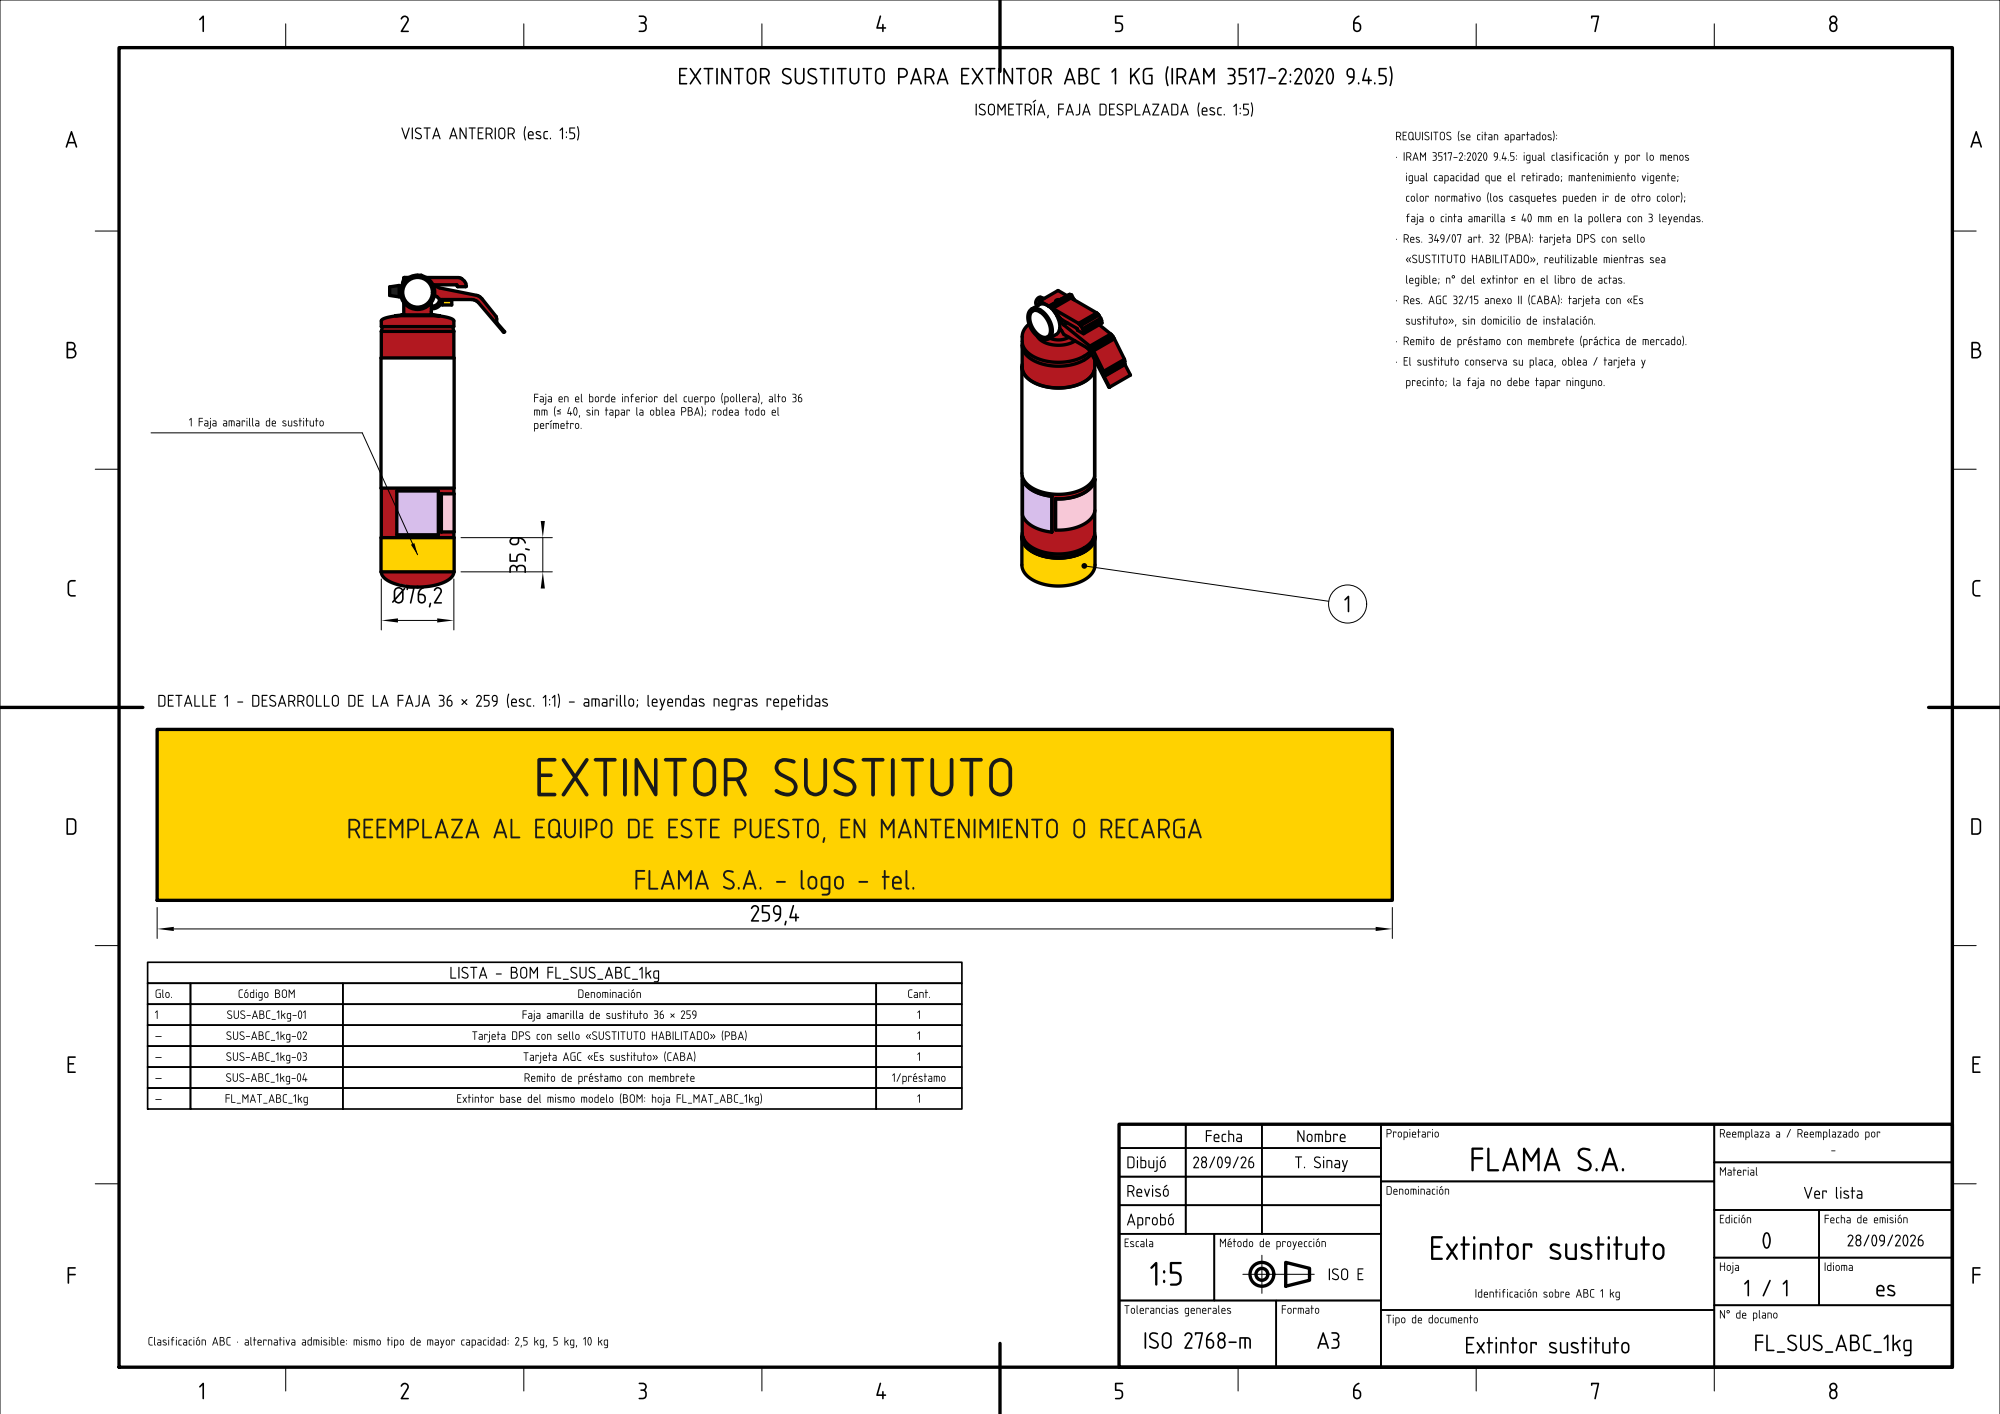
[picture p213: page 1]
