TadeoSinay/planos_flama-/salida/sustituto/FL_SUS_ABC_2.5kg.pdf

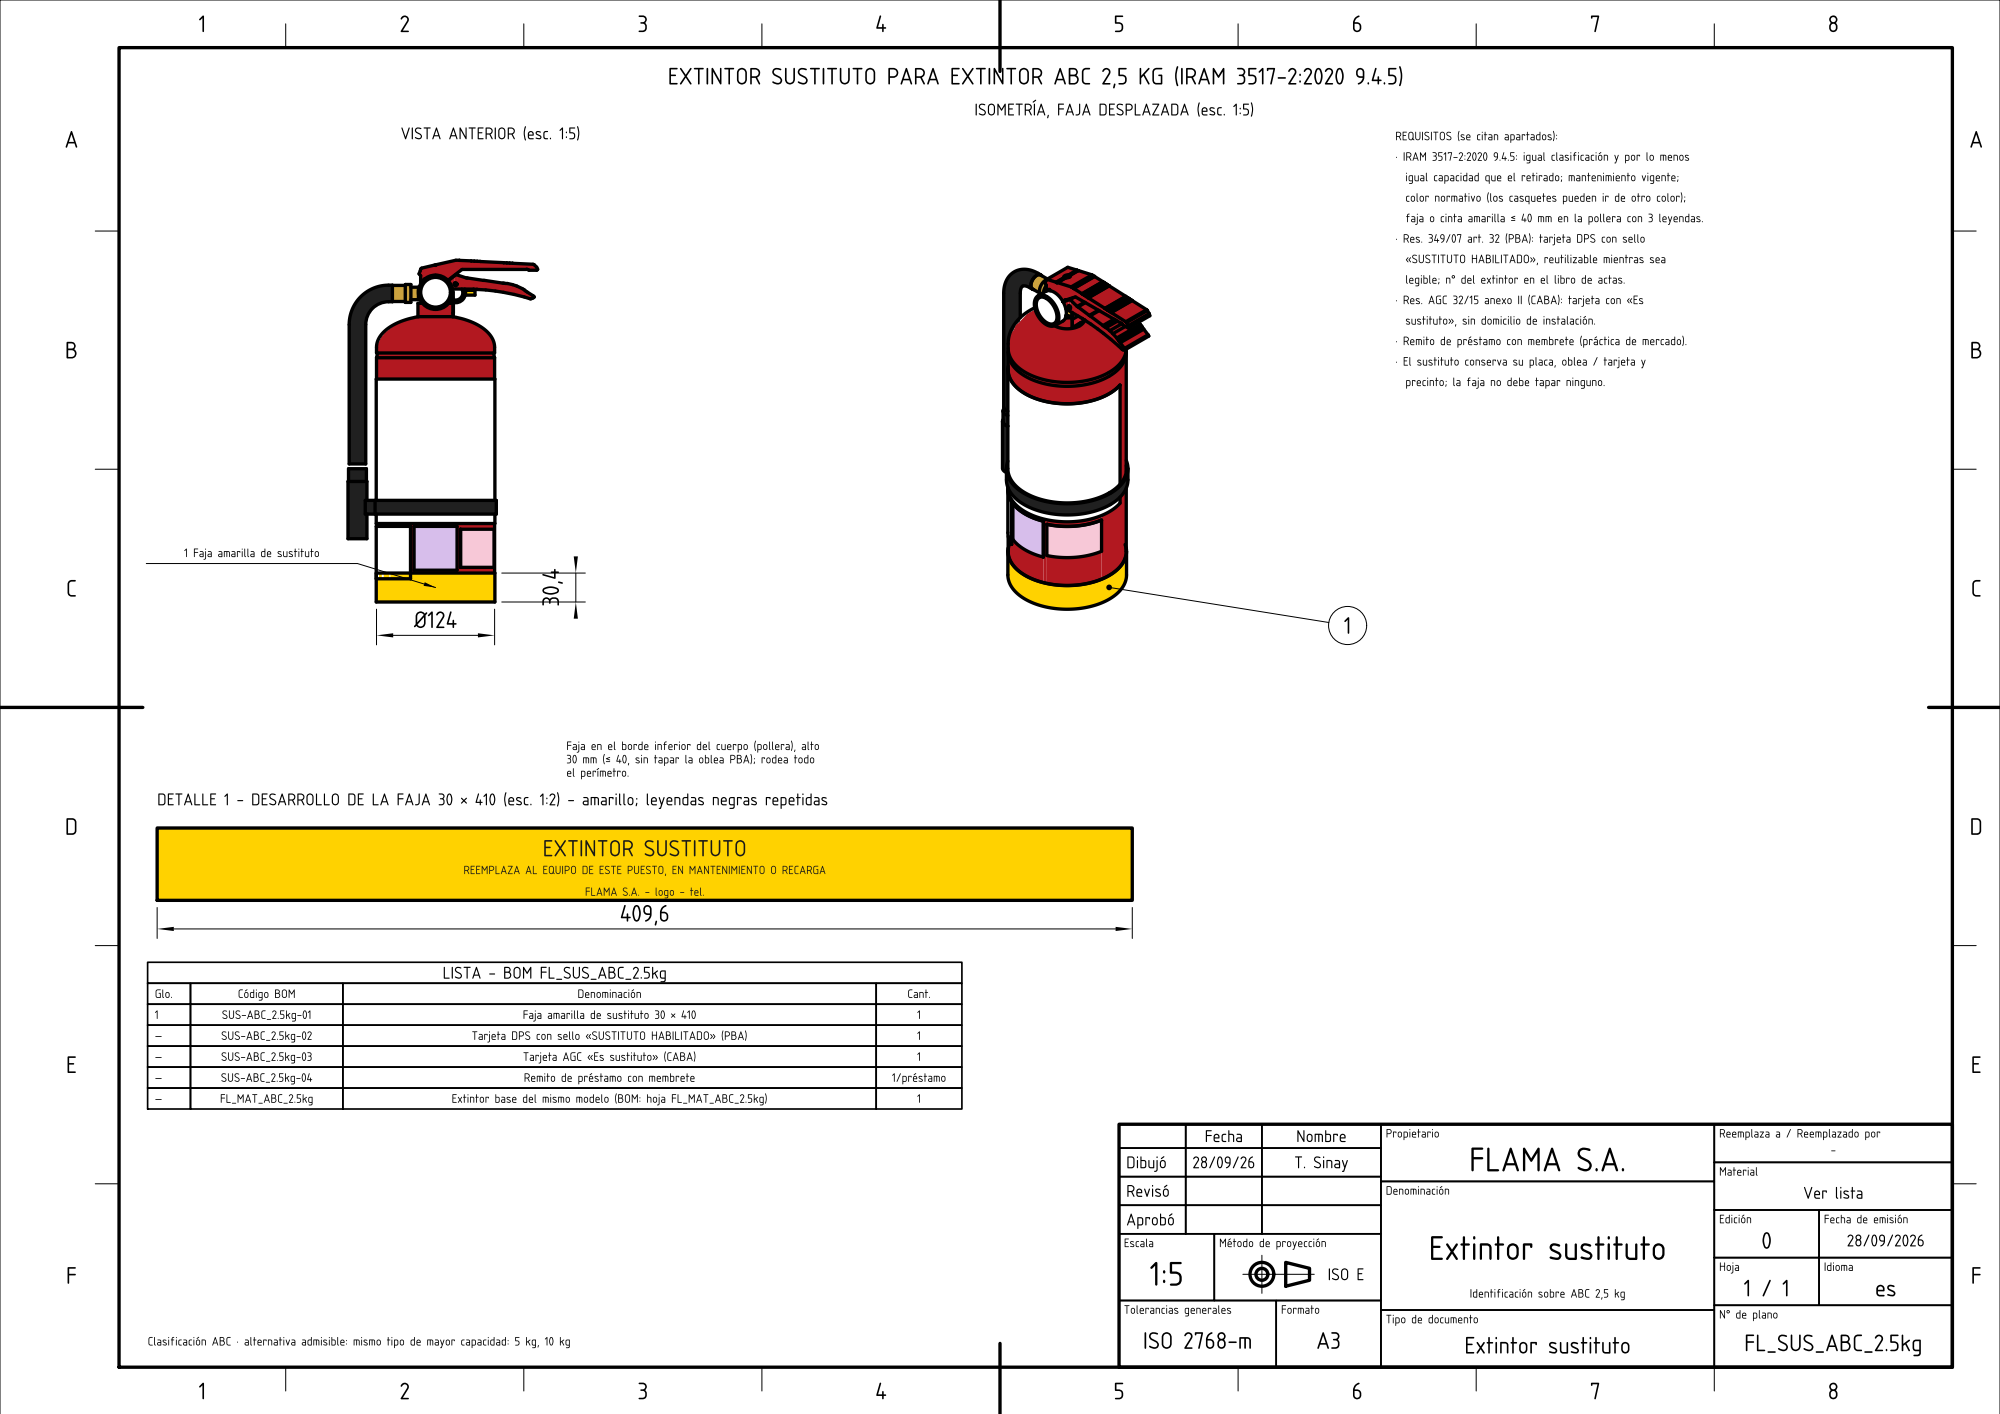
[picture p214: page 1]
