TadeoSinay/planos_flama-/salida/sustituto/FL_SUS_ABC_25kg.pdf

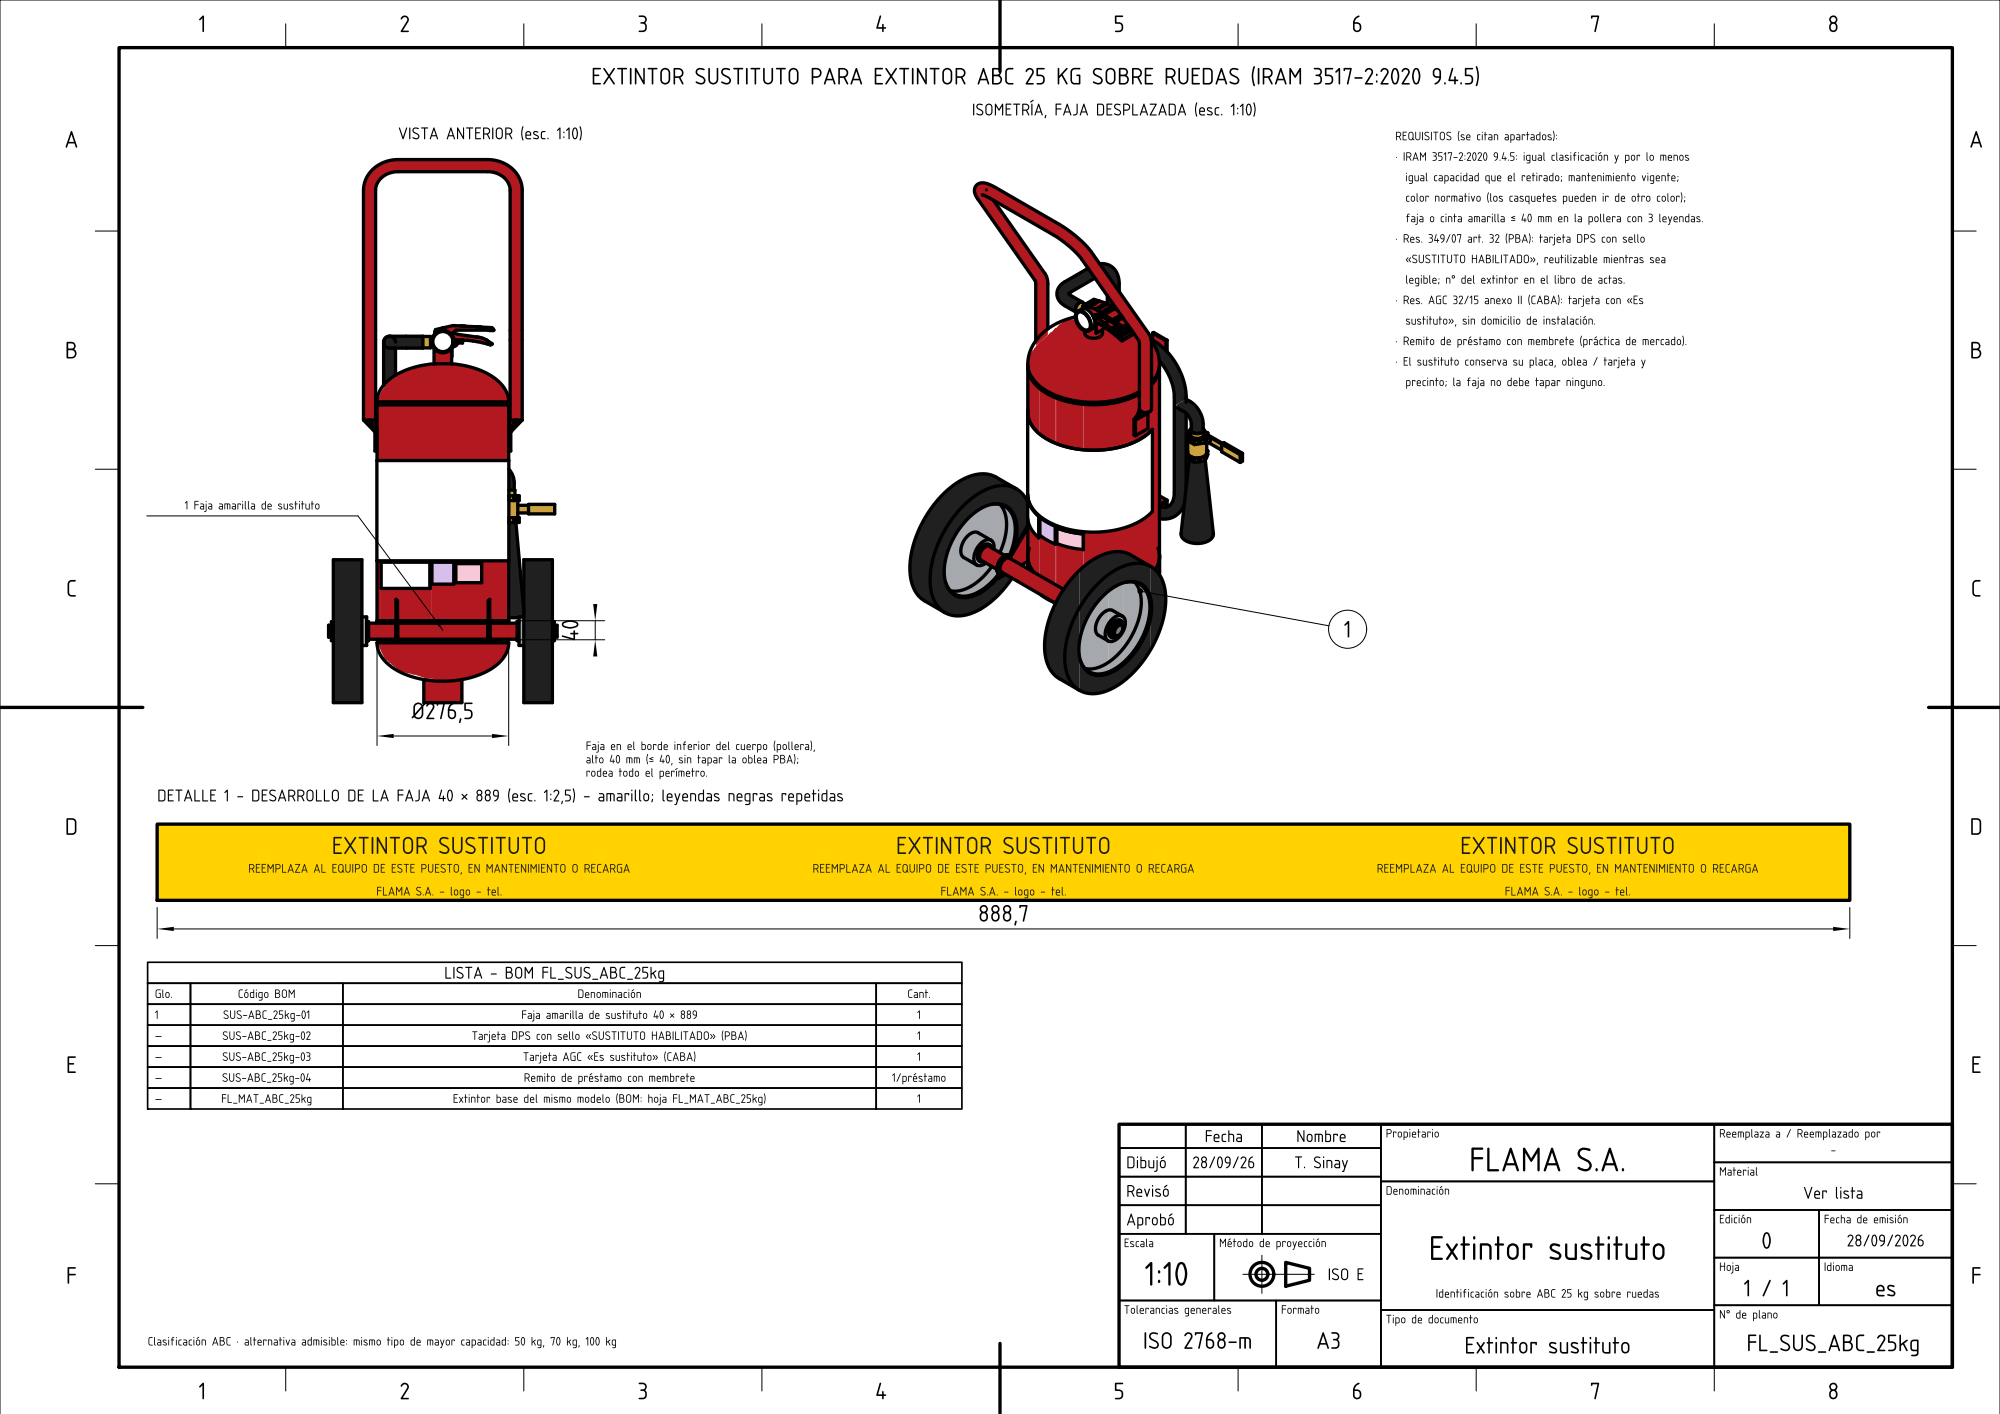
[picture p215: page 1]
