TadeoSinay/planos_flama-/salida/sustituto/FL_SUS_ABC_50kg.pdf

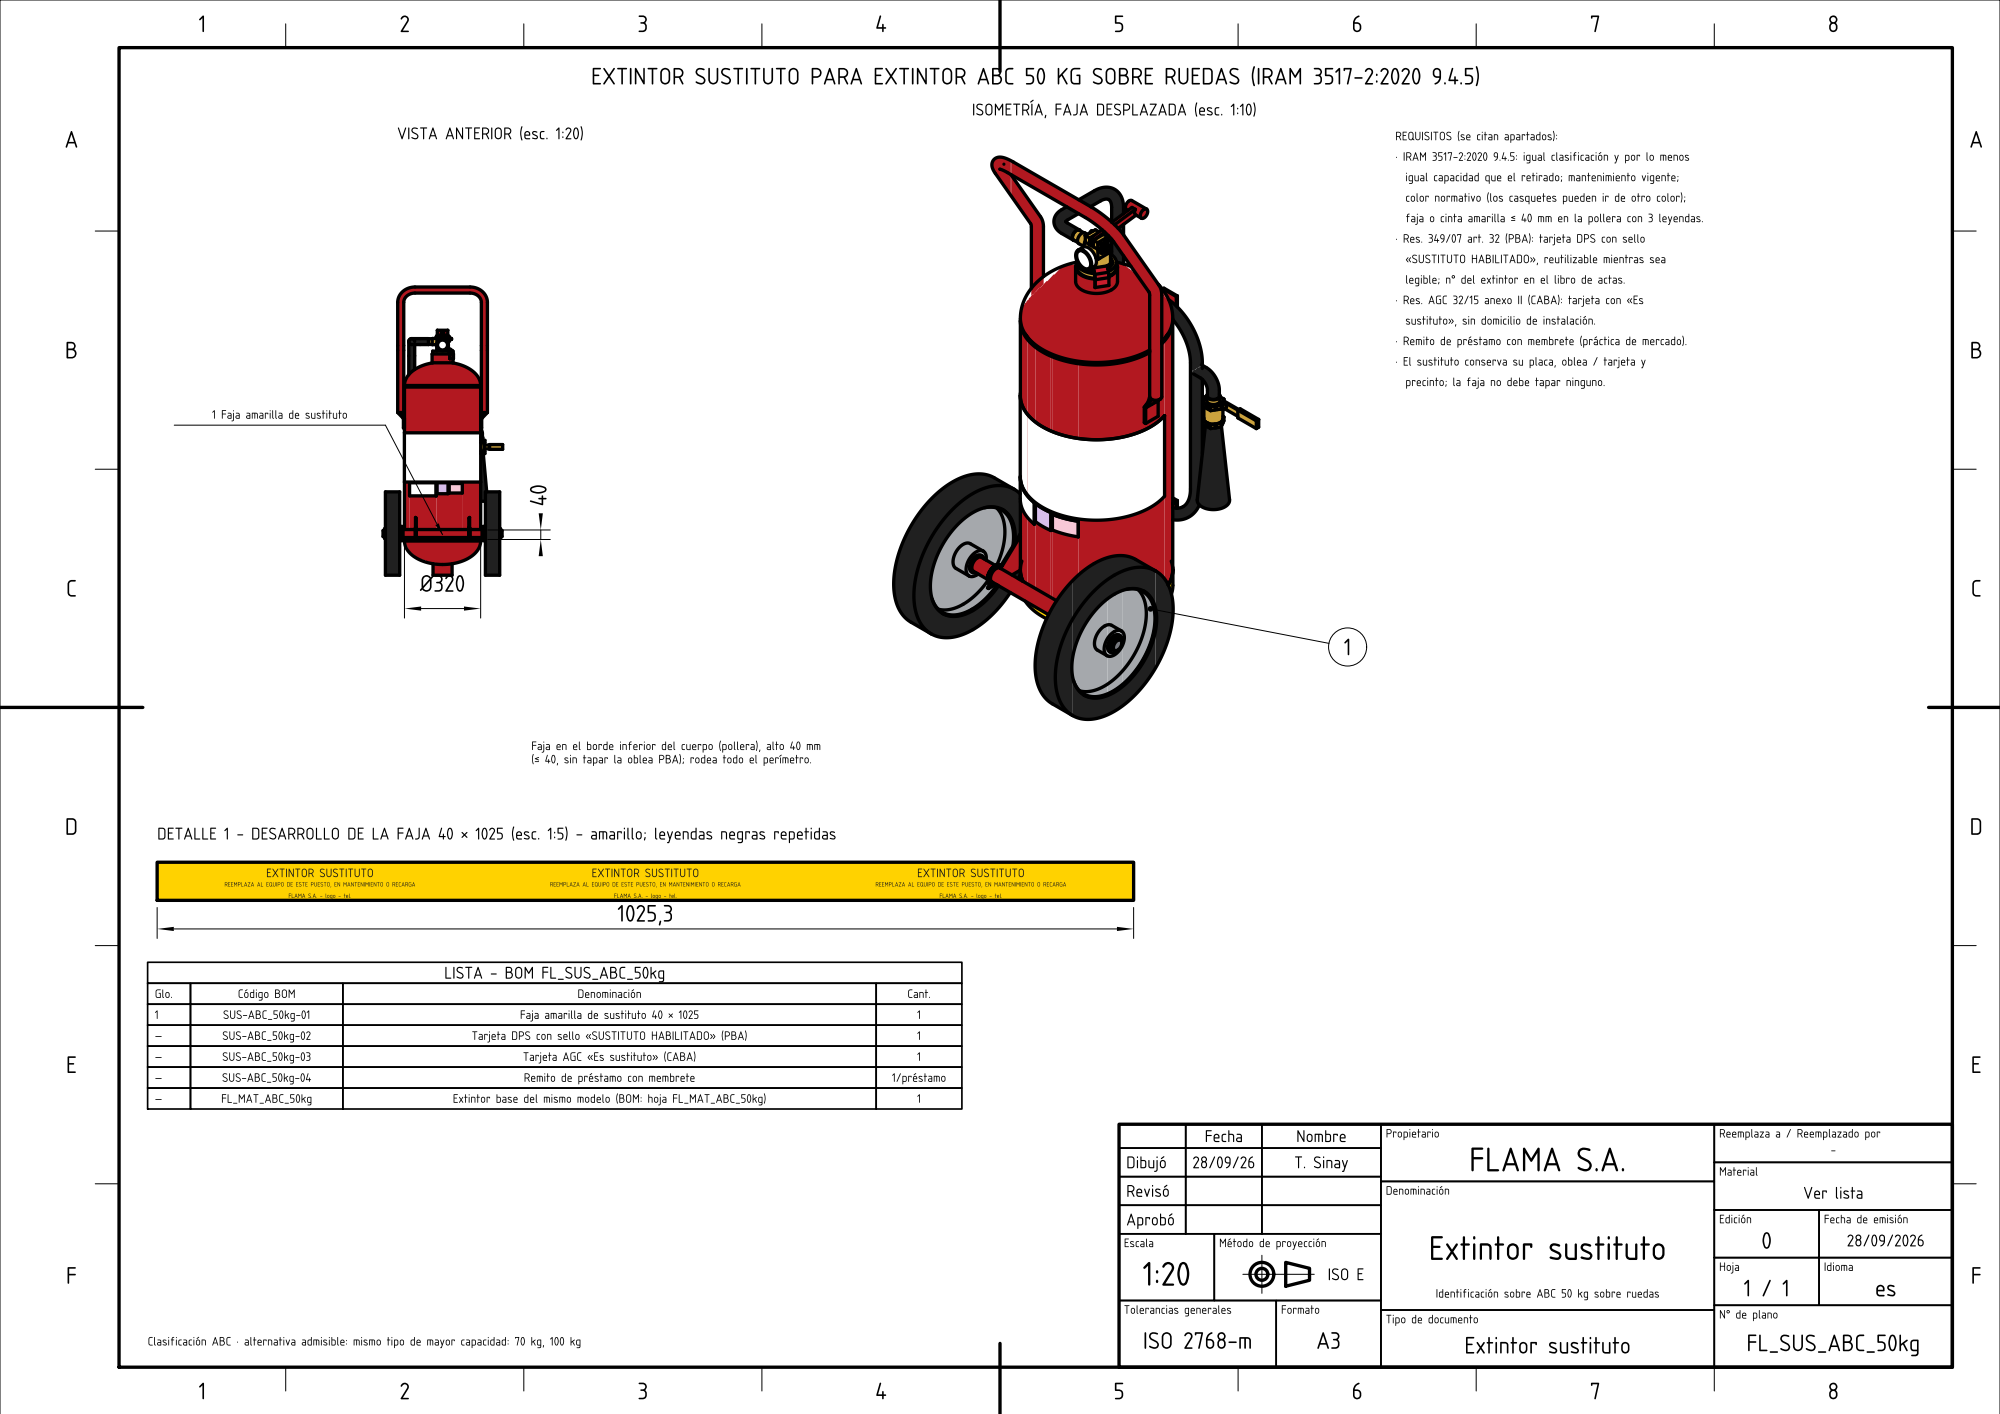
[picture p216: page 1]
