TadeoSinay/planos_flama-/salida/sustituto/FL_SUS_ABC_5kg.pdf

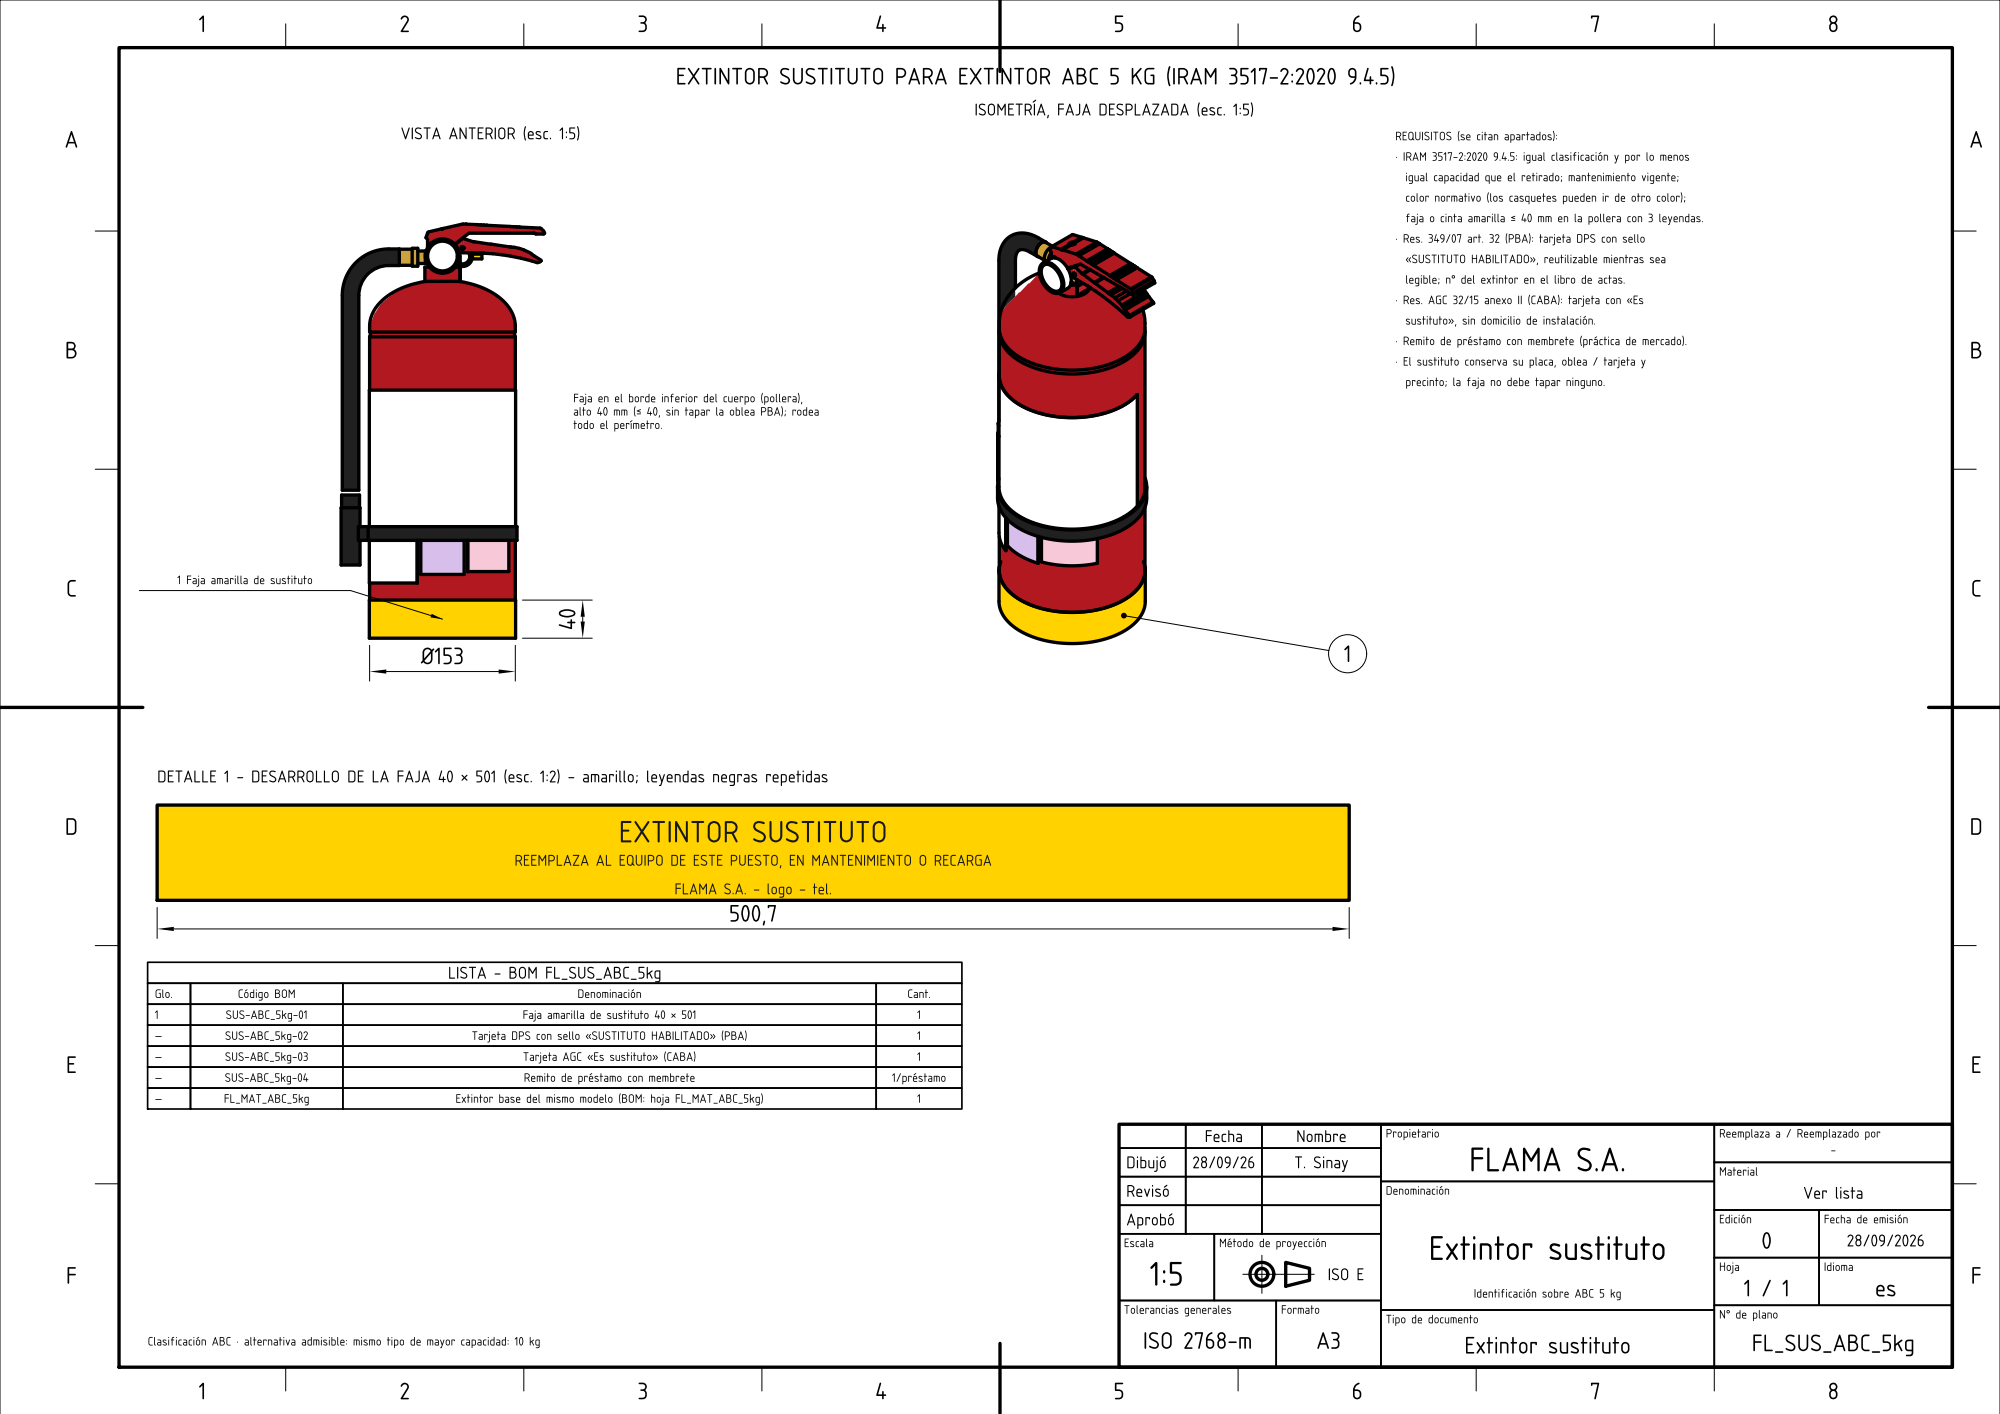
[picture p217: page 1]
