TadeoSinay/planos_flama-/salida/sustituto/FL_SUS_ABC_70kg.pdf

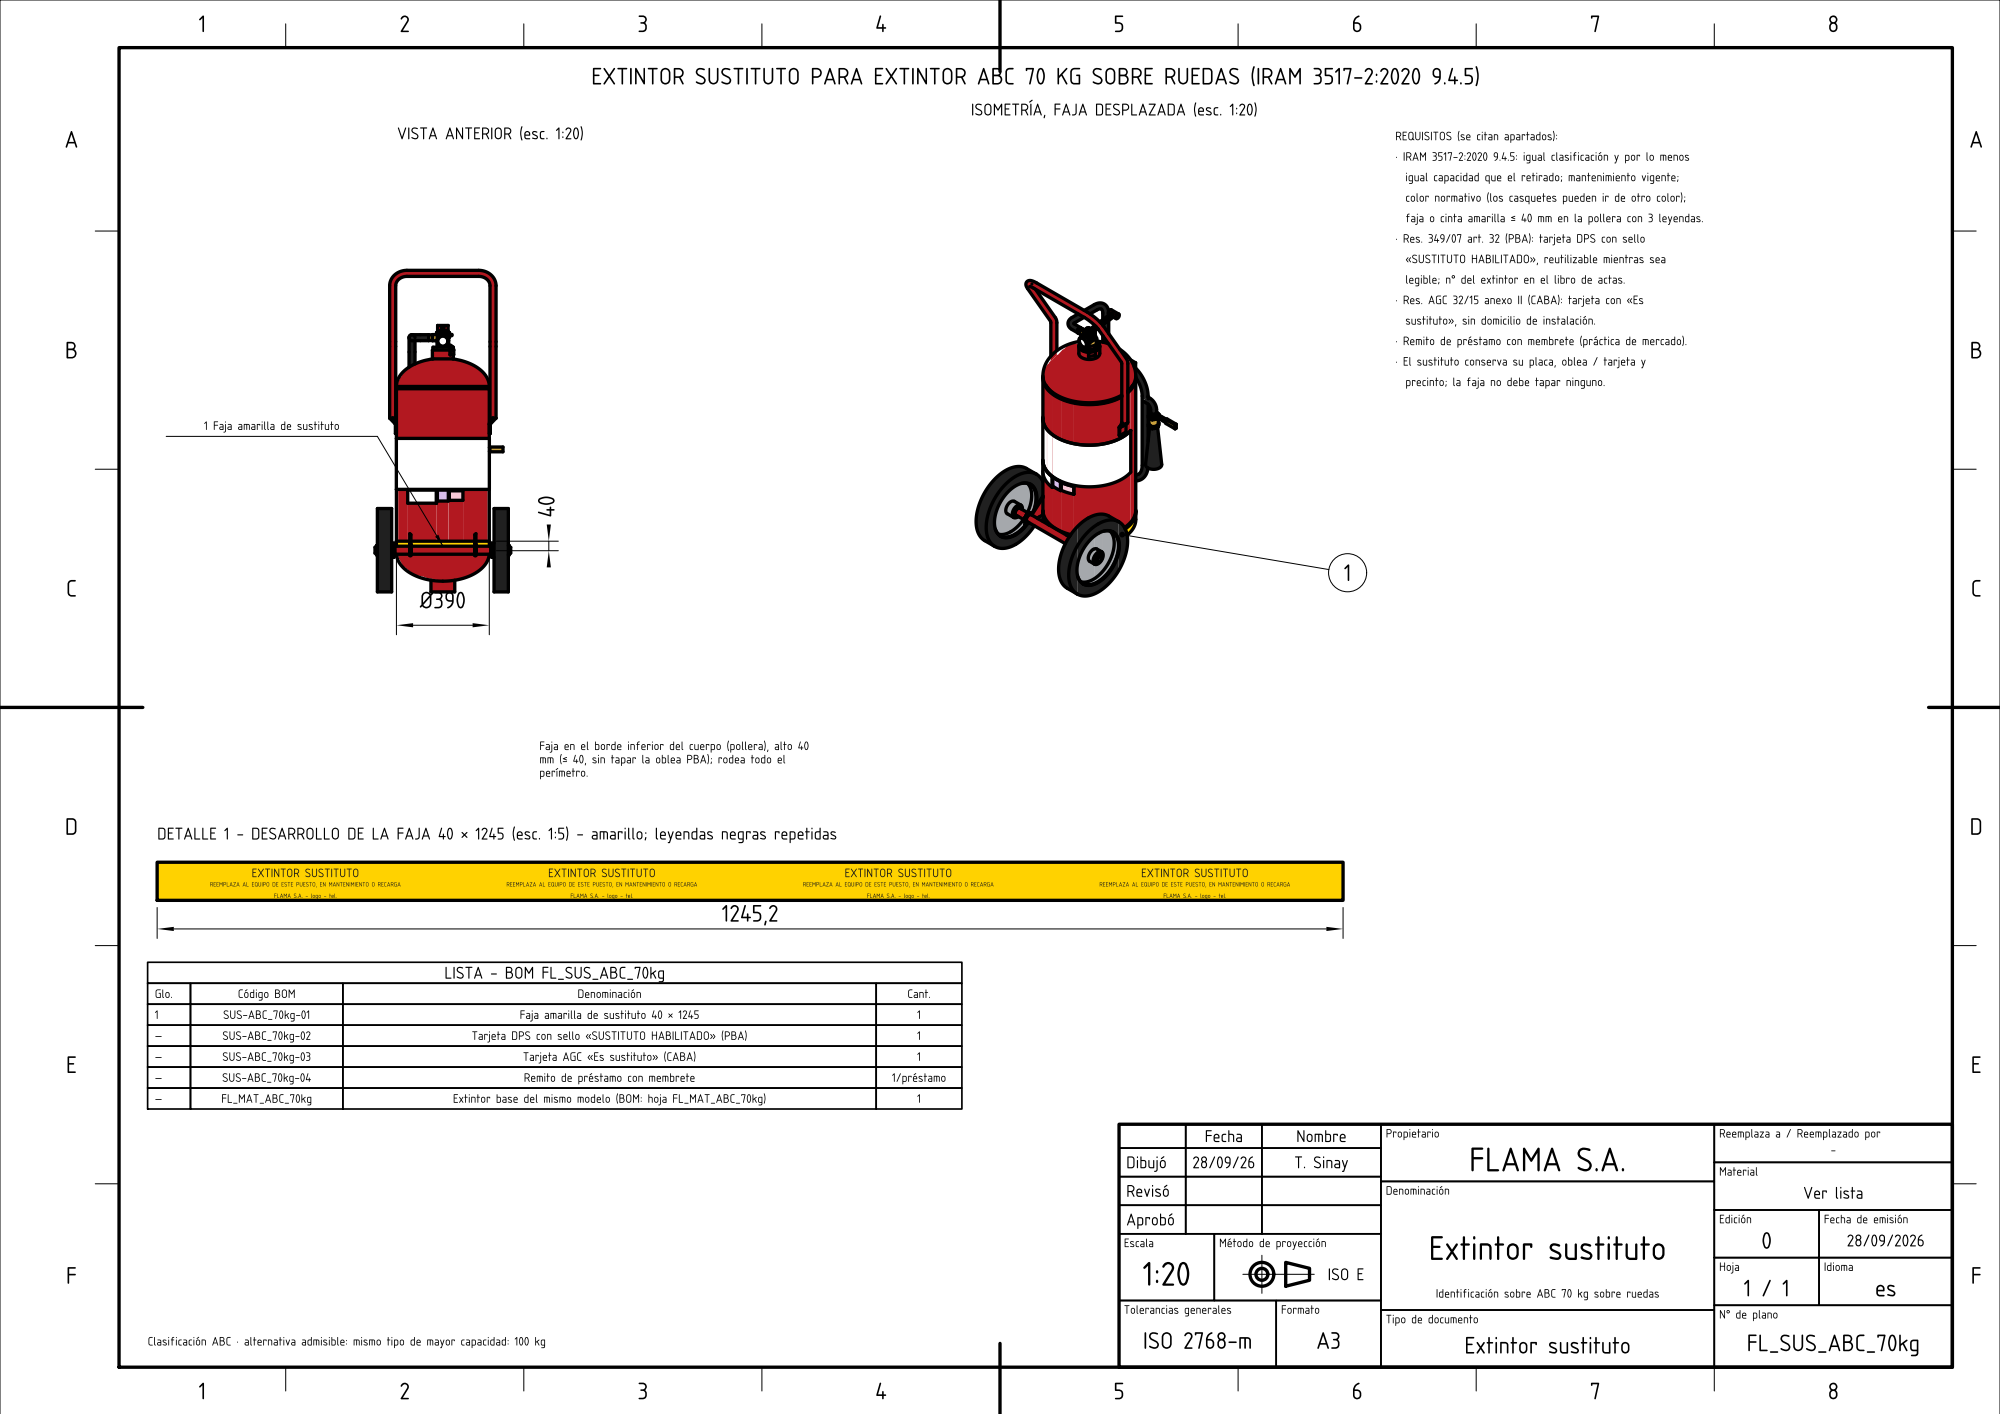
[picture p218: page 1]
