TadeoSinay/planos_flama-/salida/sustituto/FL_SUS_AFFF_10l.pdf

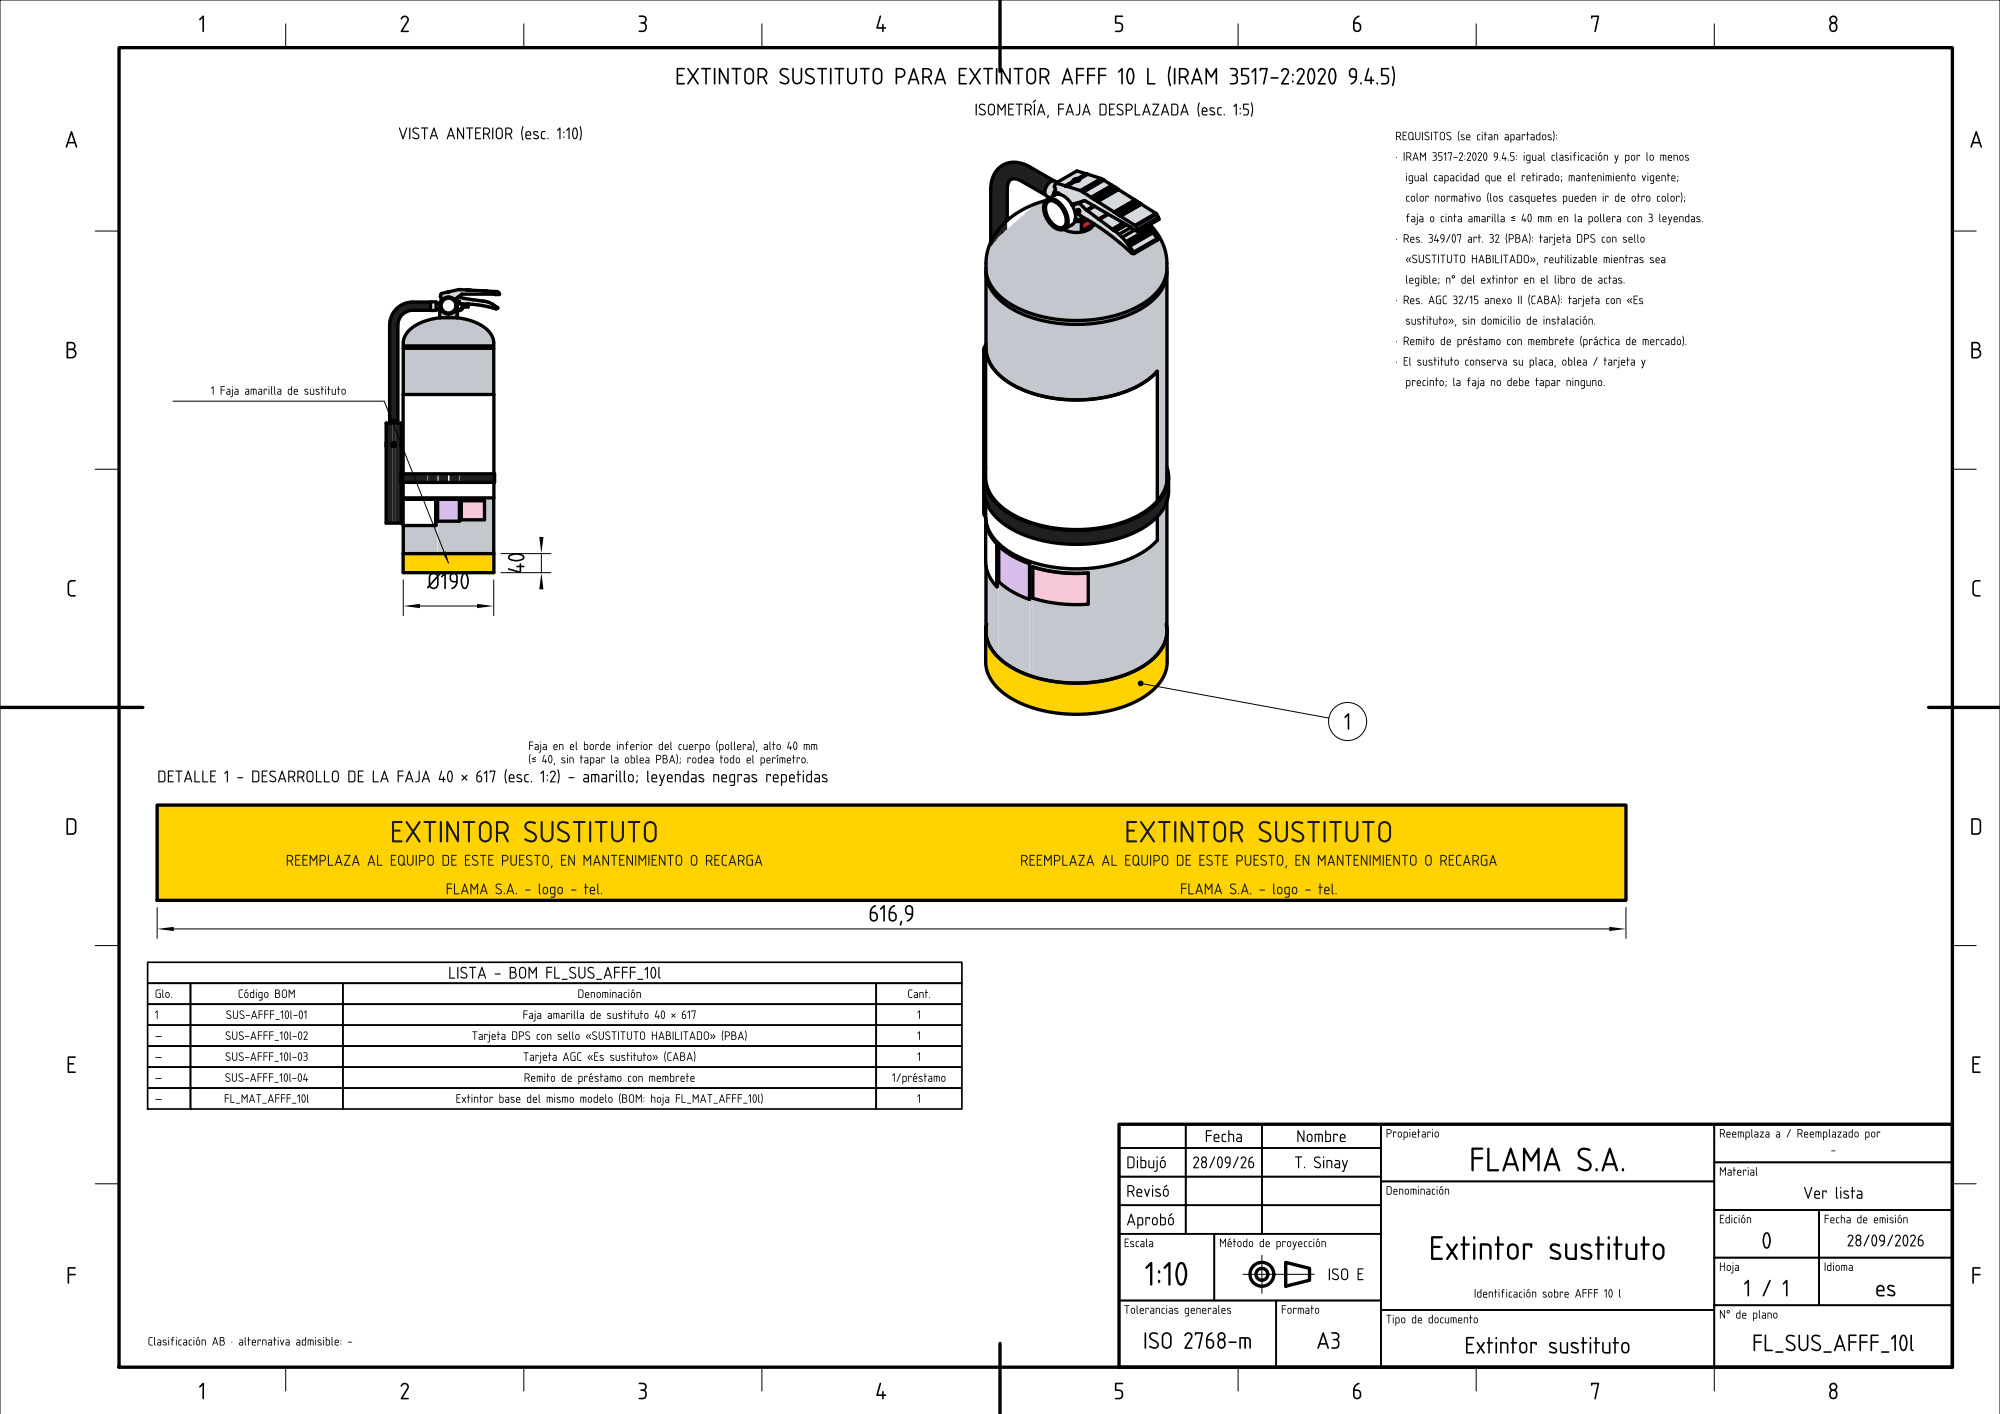
[picture p219: page 1]
