TadeoSinay/planos_flama-/salida/sustituto/FL_SUS_AFFF_50l.pdf

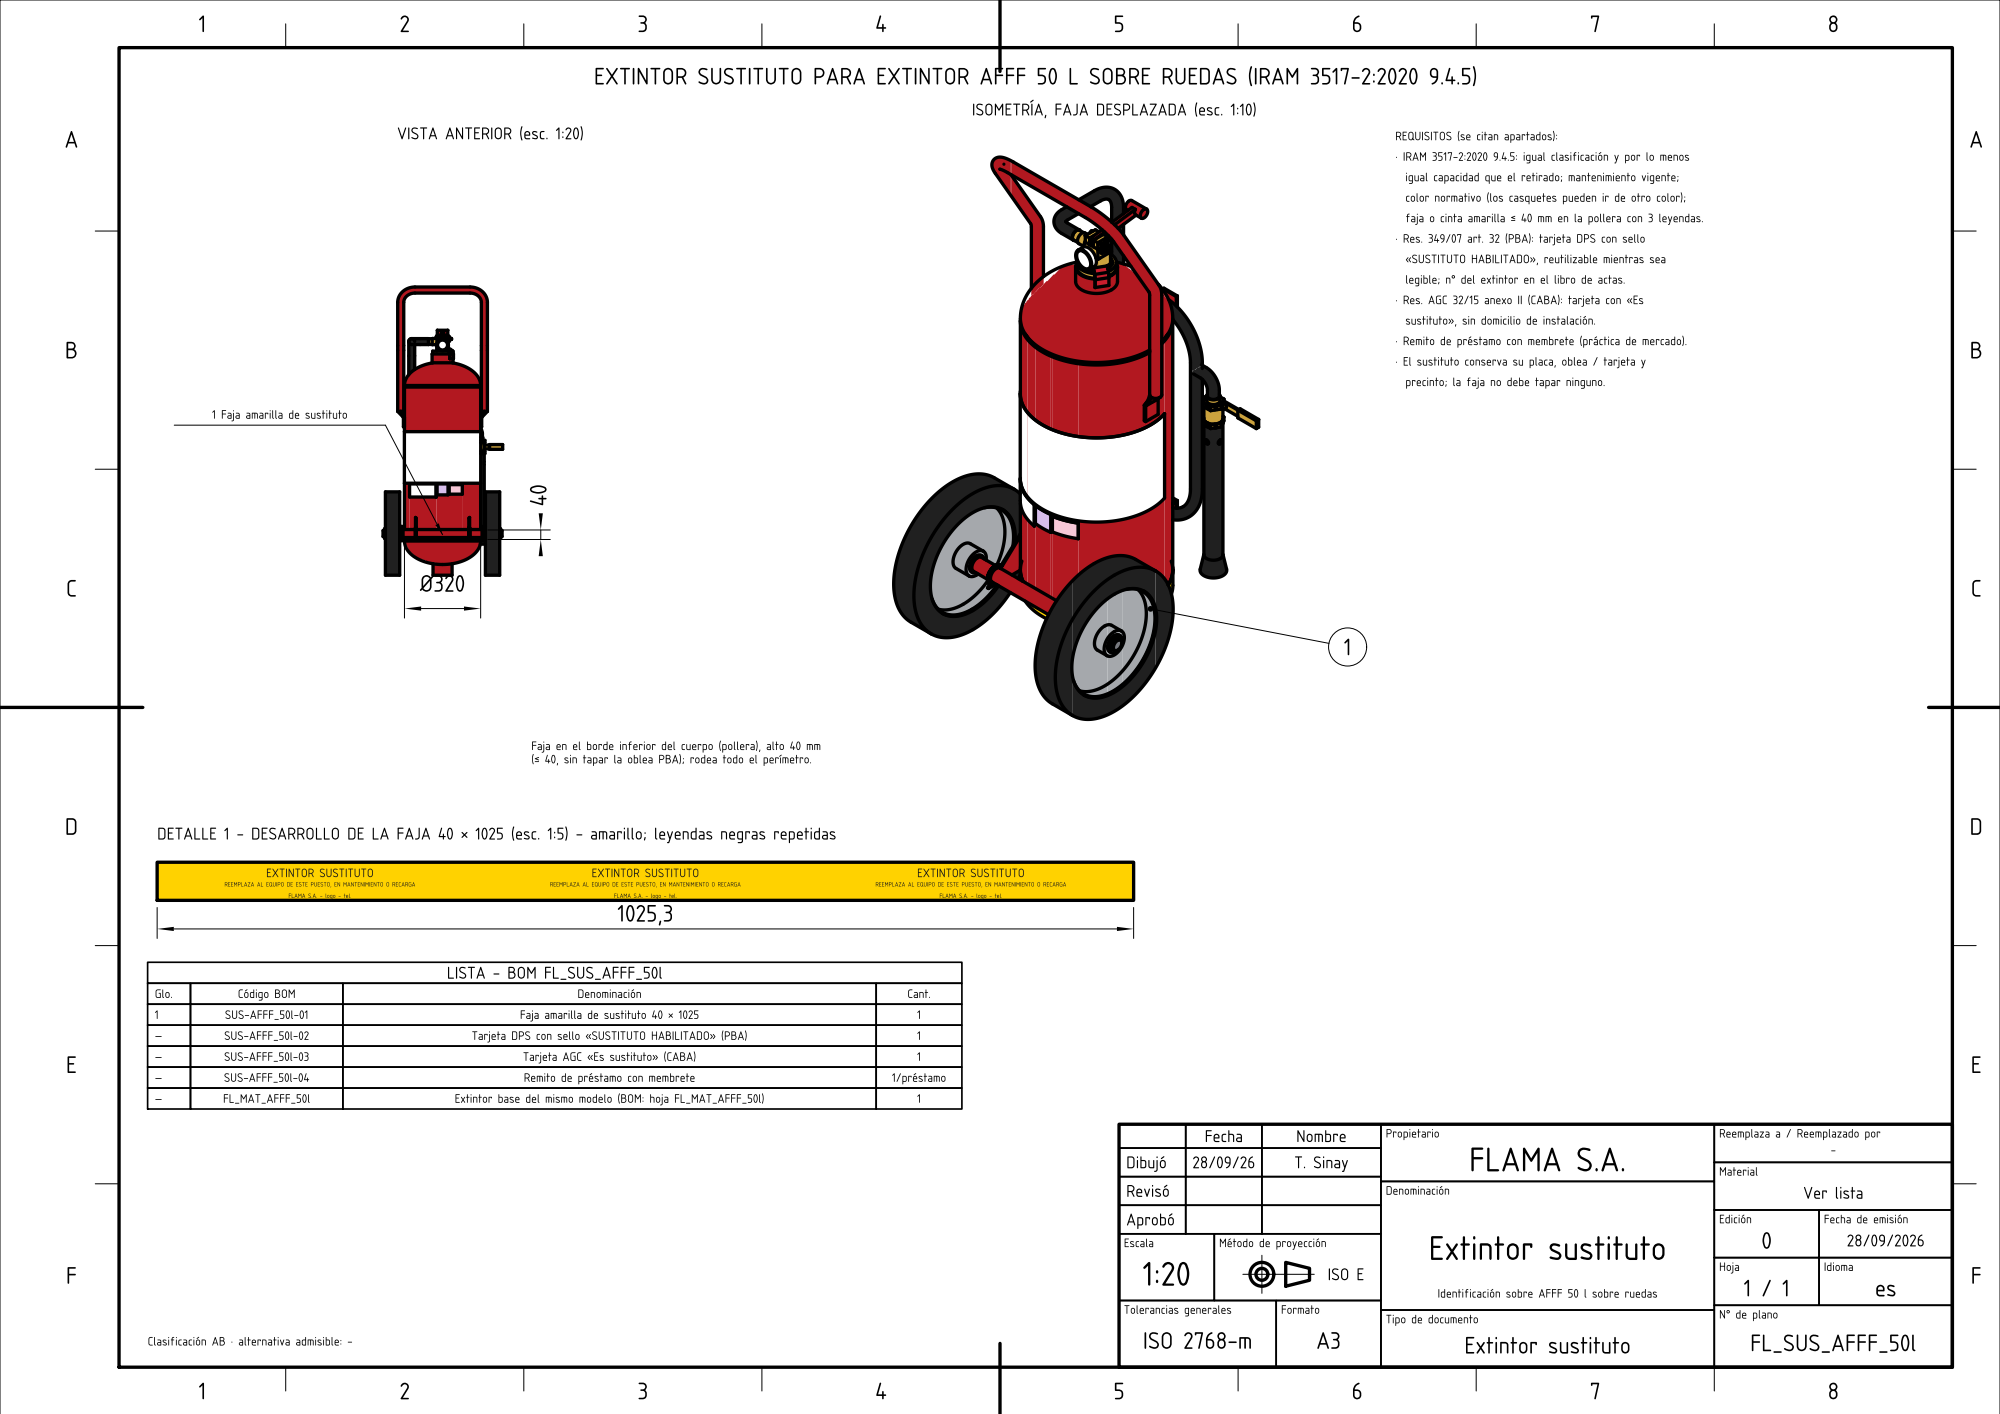
[picture p220: page 1]
