TadeoSinay/planos_flama-/salida/sustituto/FL_SUS_AGUA_10l.pdf

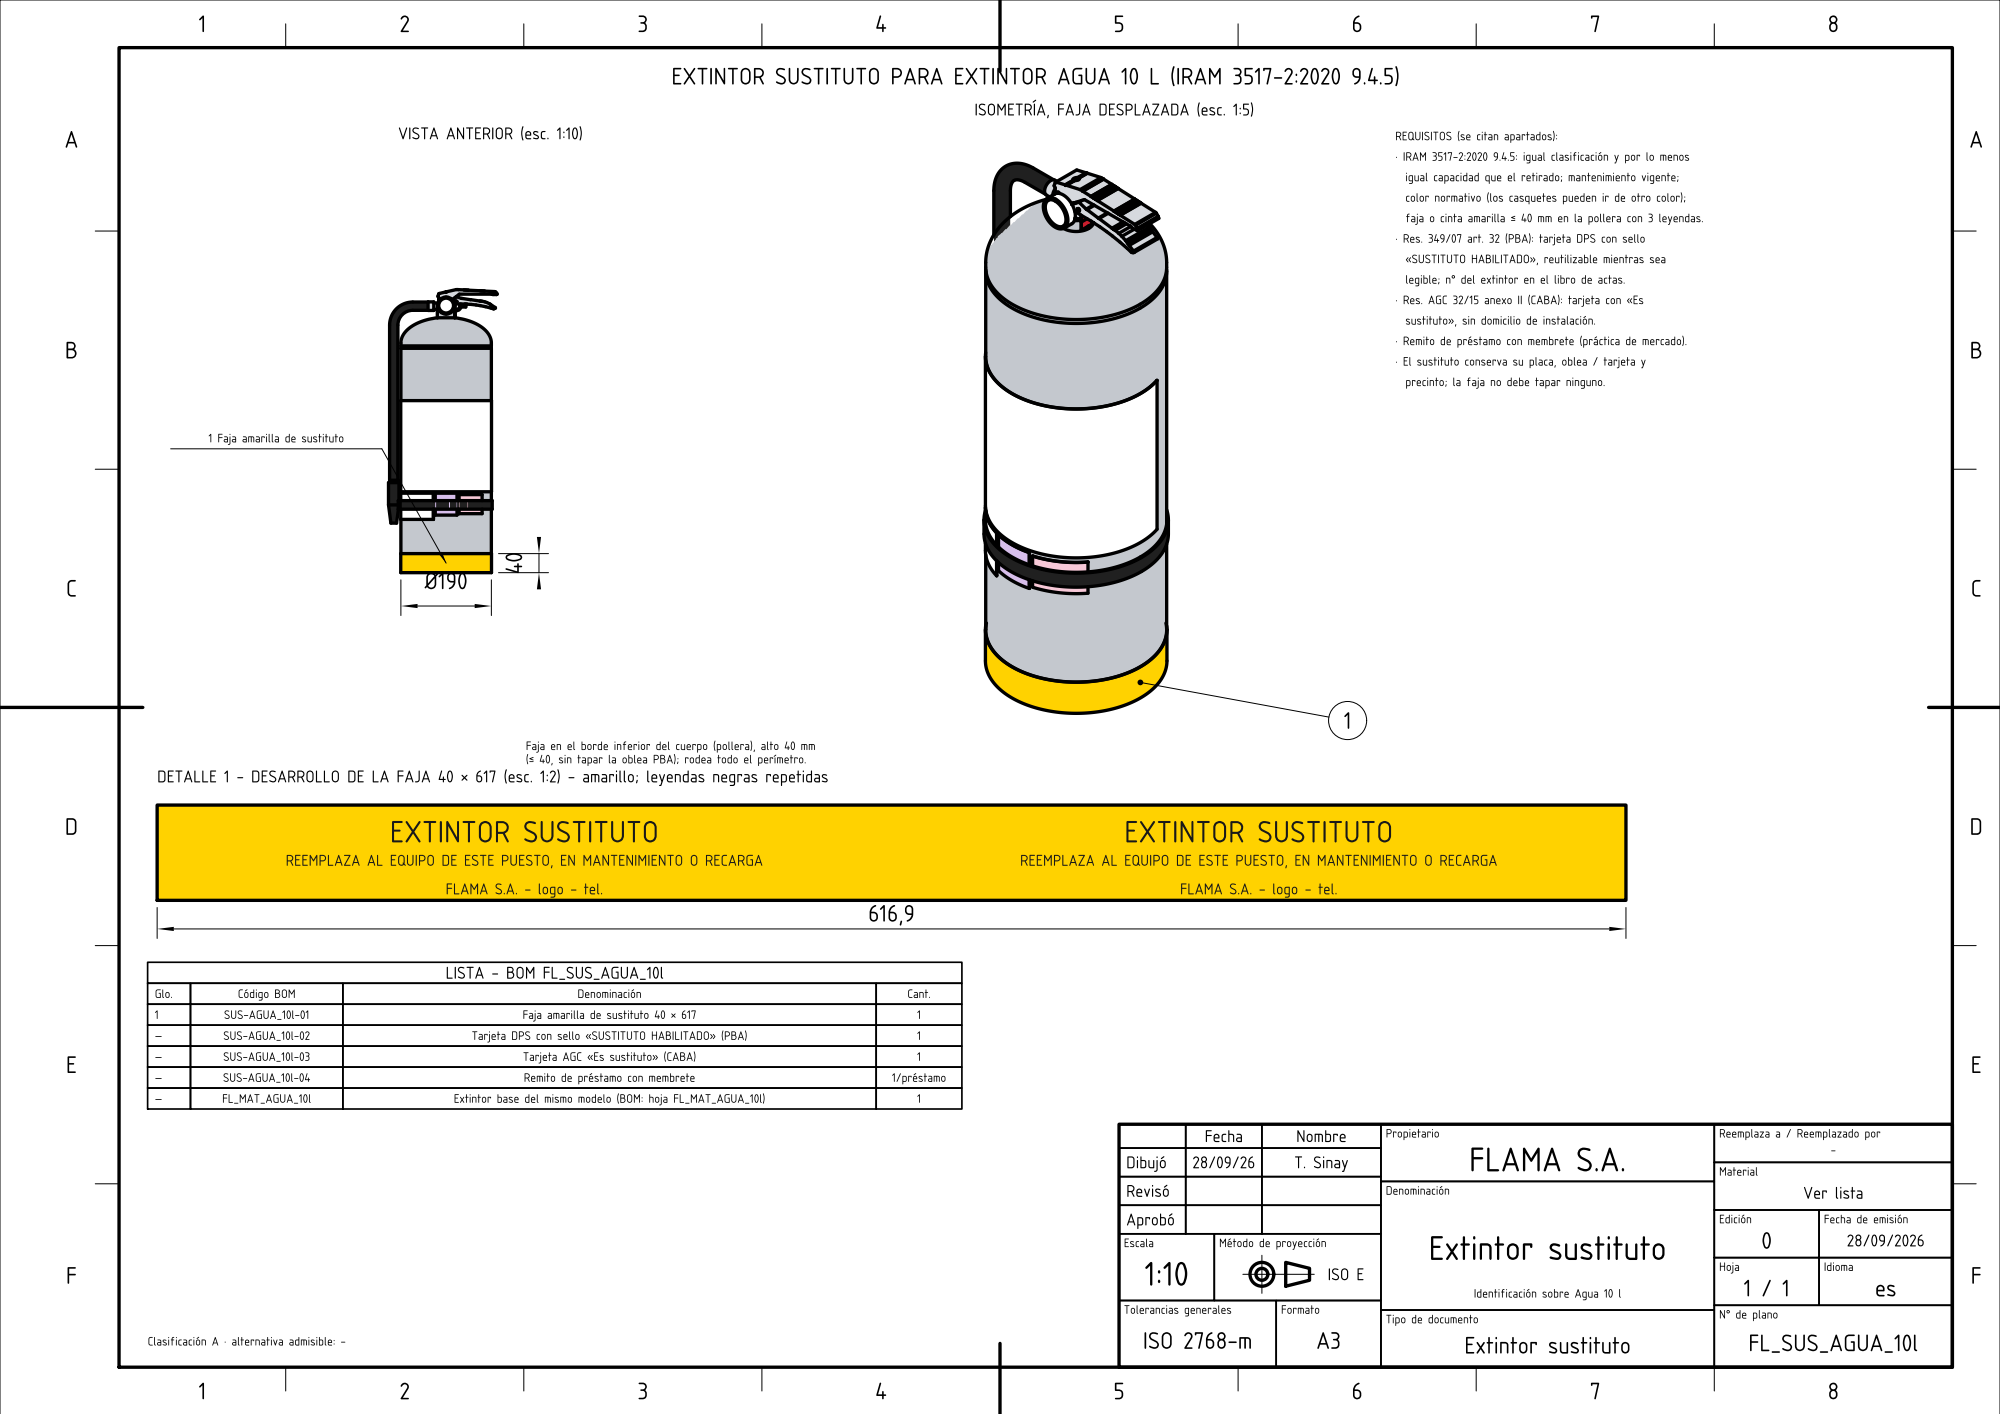
[picture p221: page 1]
