TadeoSinay/planos_flama-/salida/sustituto/FL_SUS_BC_5kg.pdf

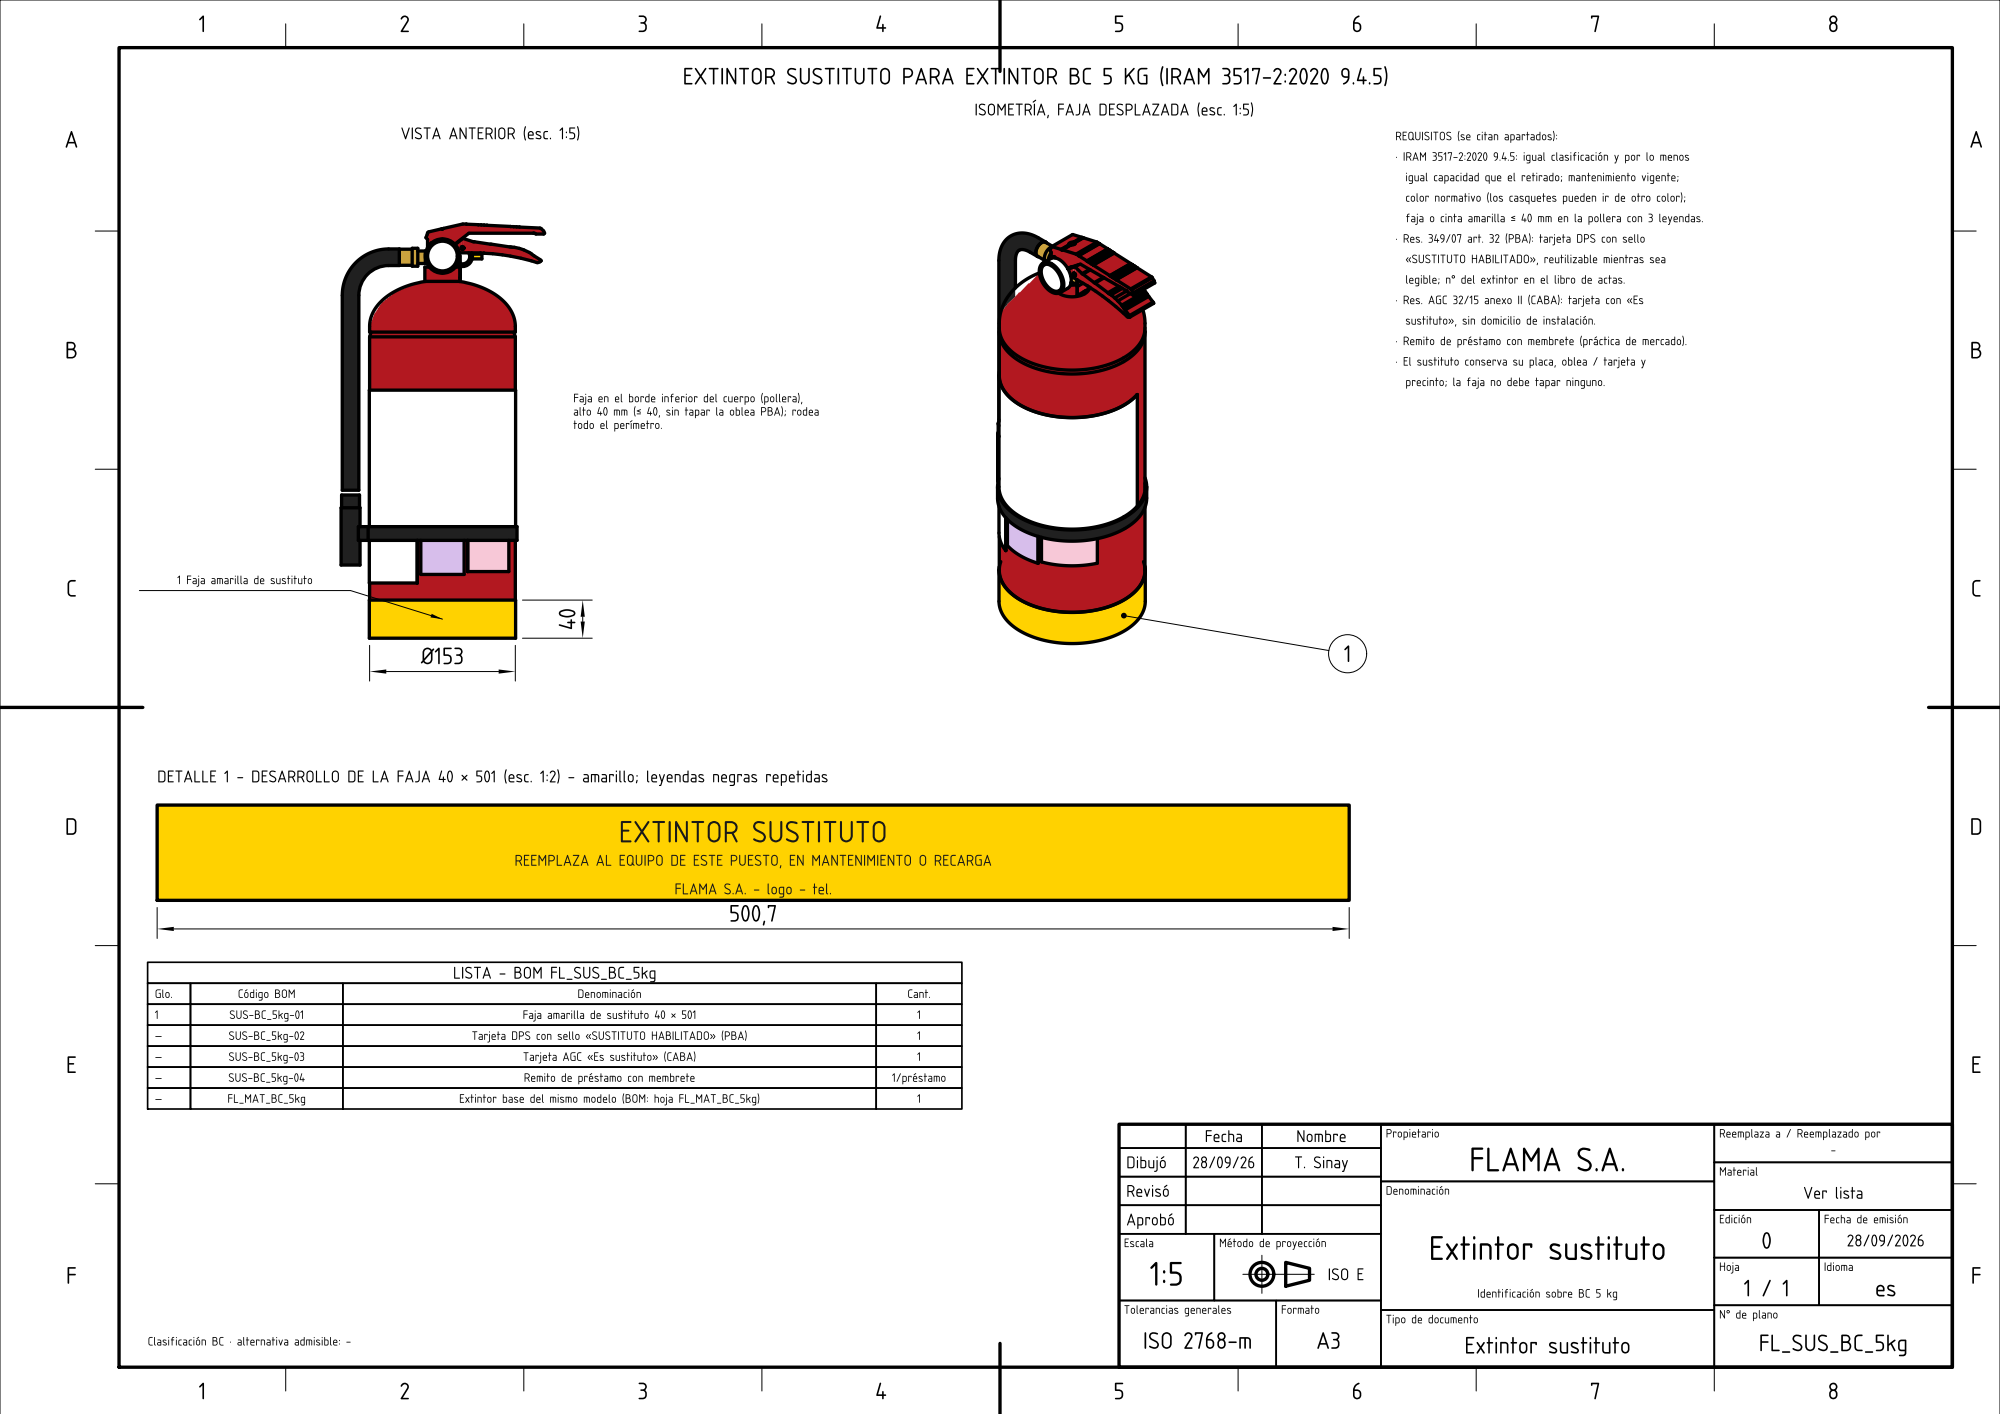
[picture p222: page 1]
