TadeoSinay/planos_flama-/salida/sustituto/FL_SUS_CLASED_9l.pdf

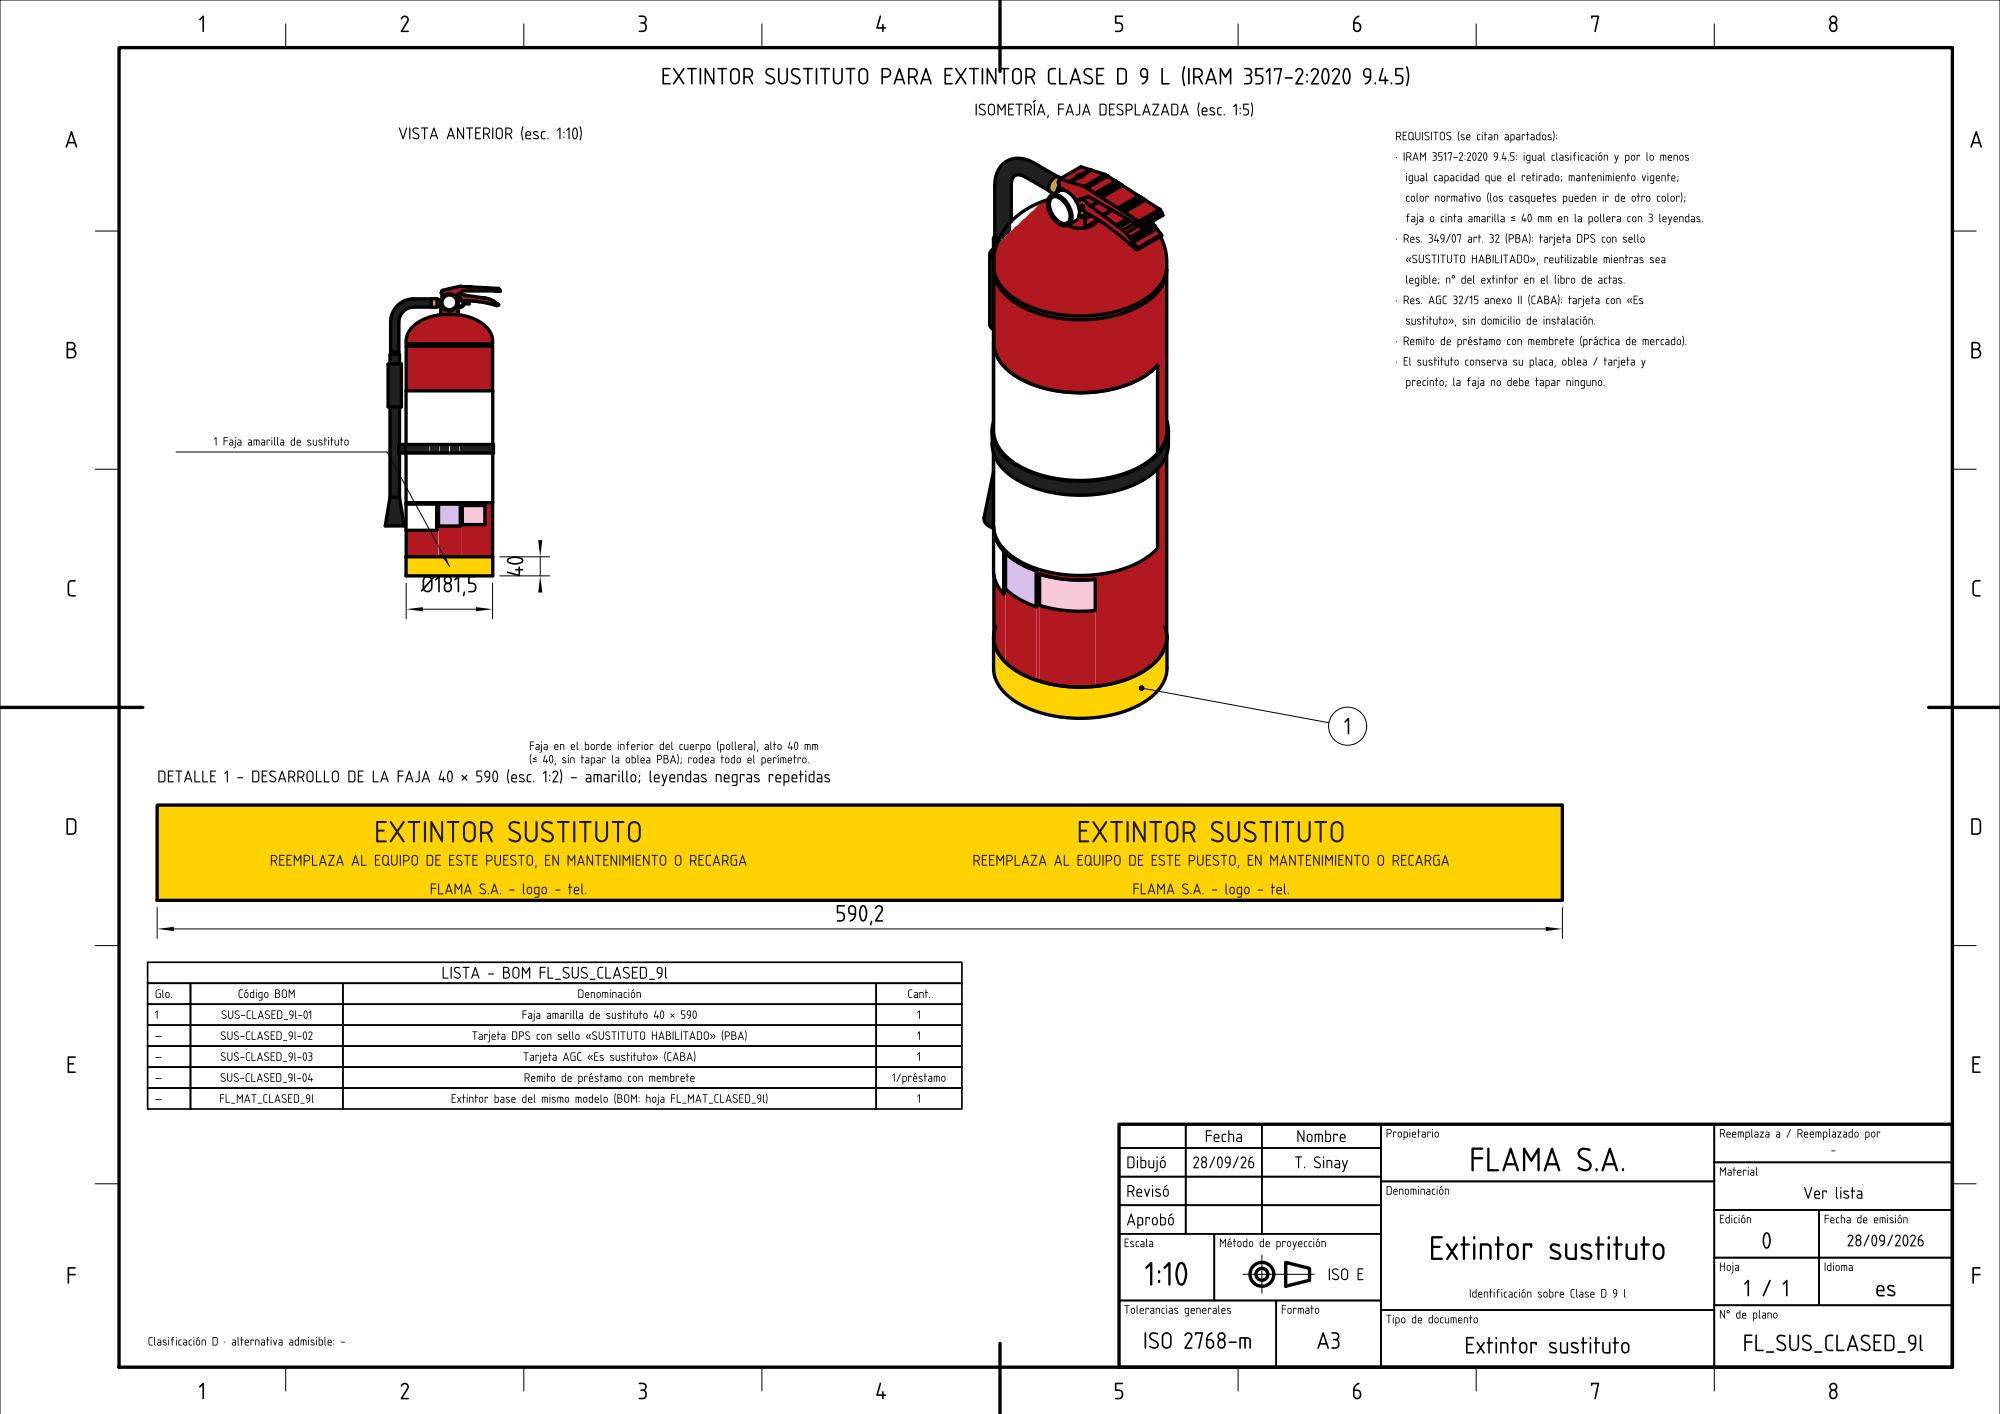
[picture p223: page 1]
