TadeoSinay/planos_flama-/salida/sustituto/FL_SUS_CO2_2kg.pdf

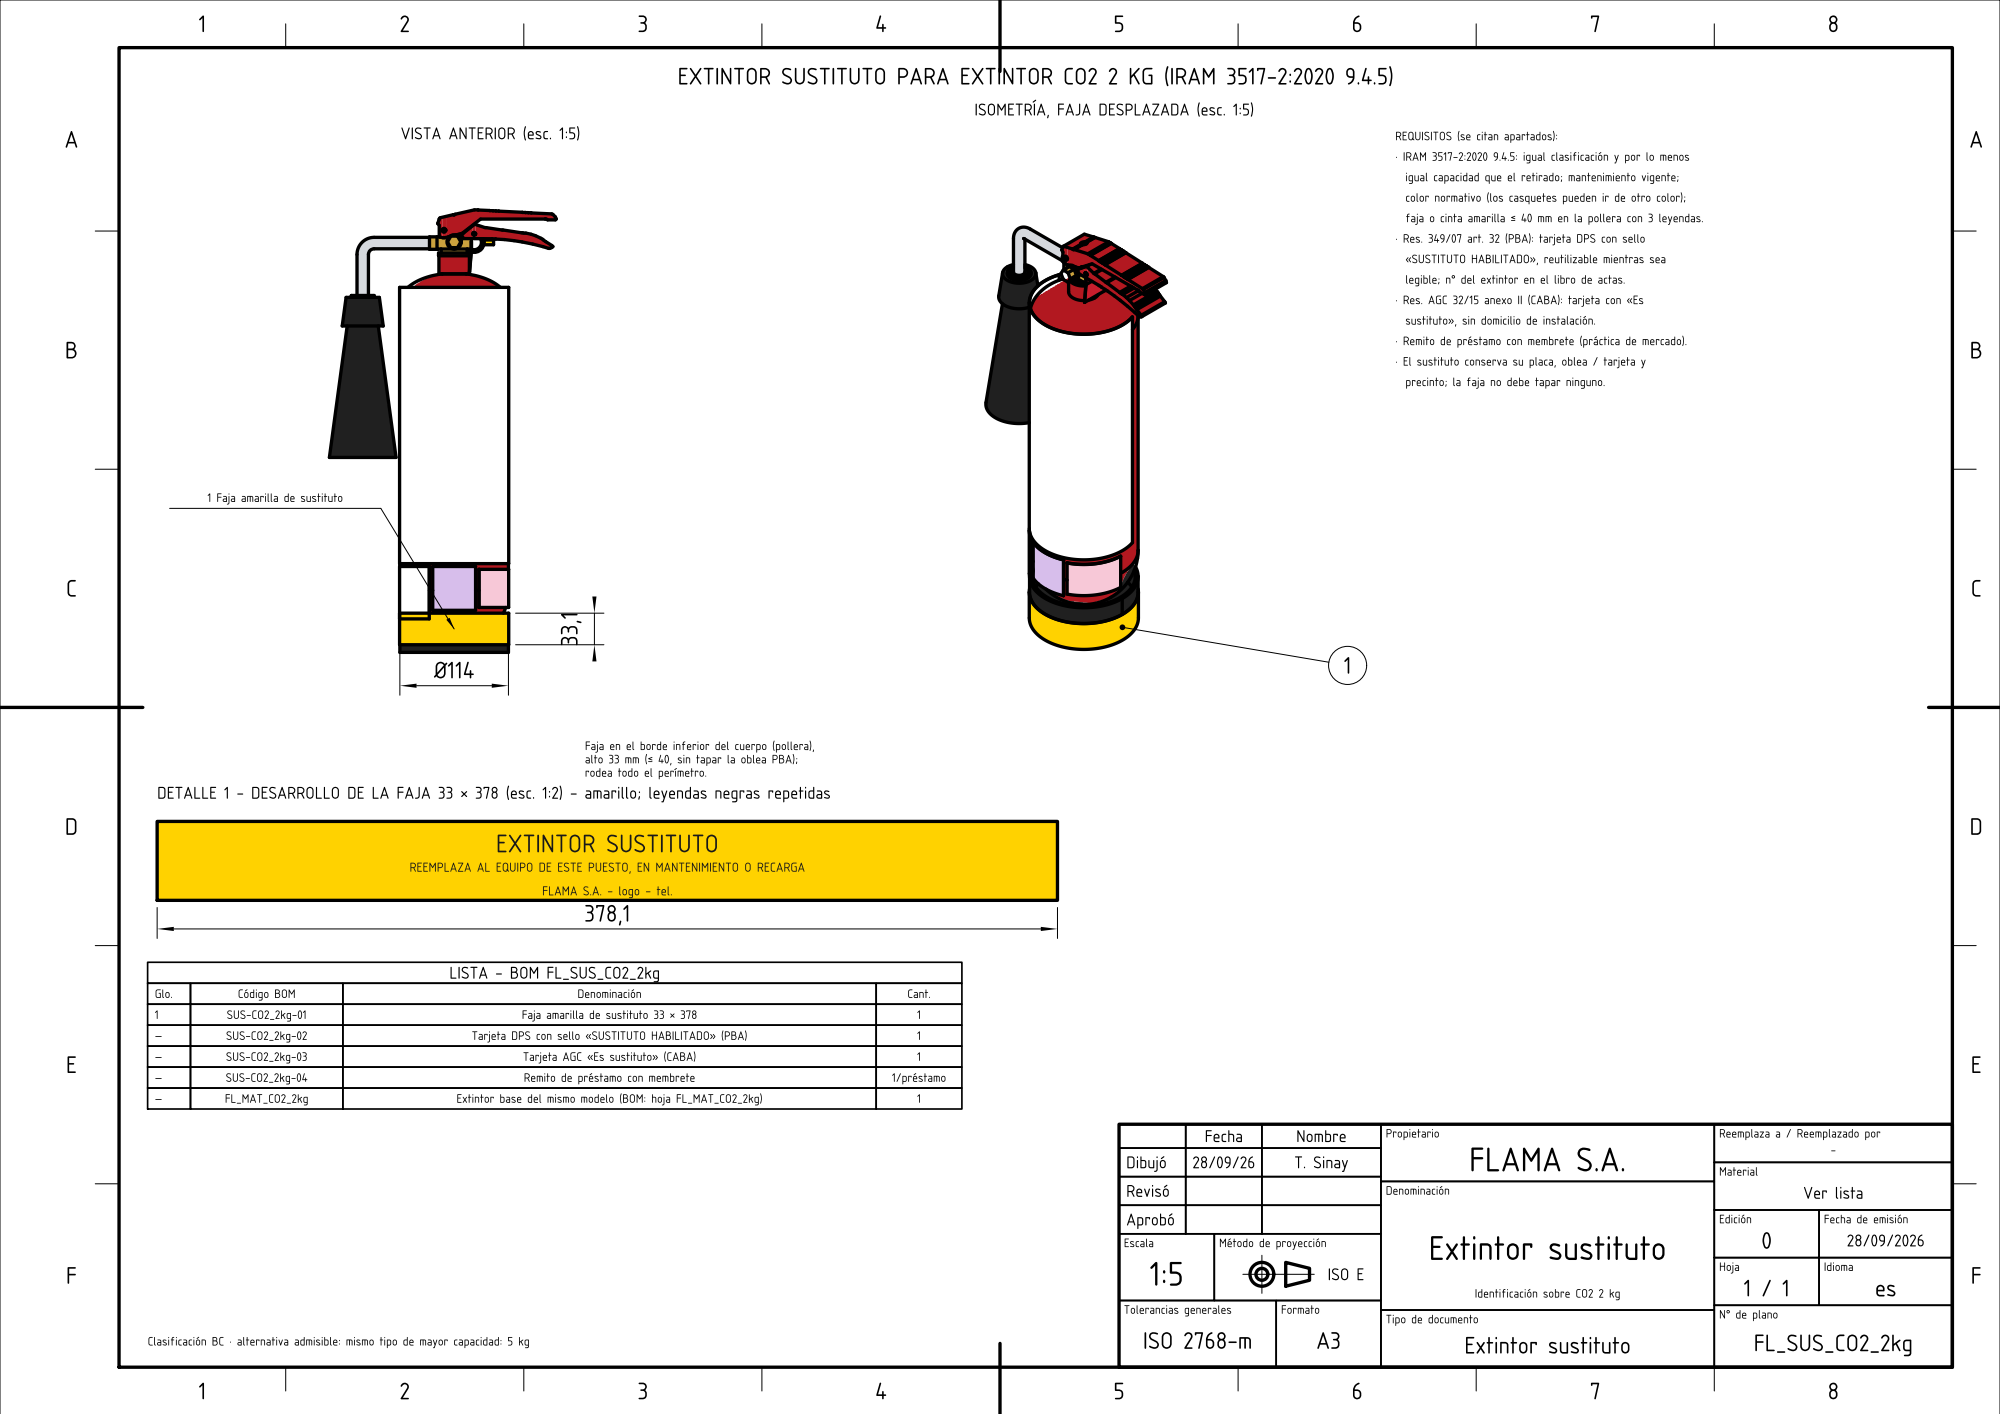
[picture p224: page 1]
