TadeoSinay/planos_flama-/salida/sustituto/FL_SUS_CO2_5kg.pdf

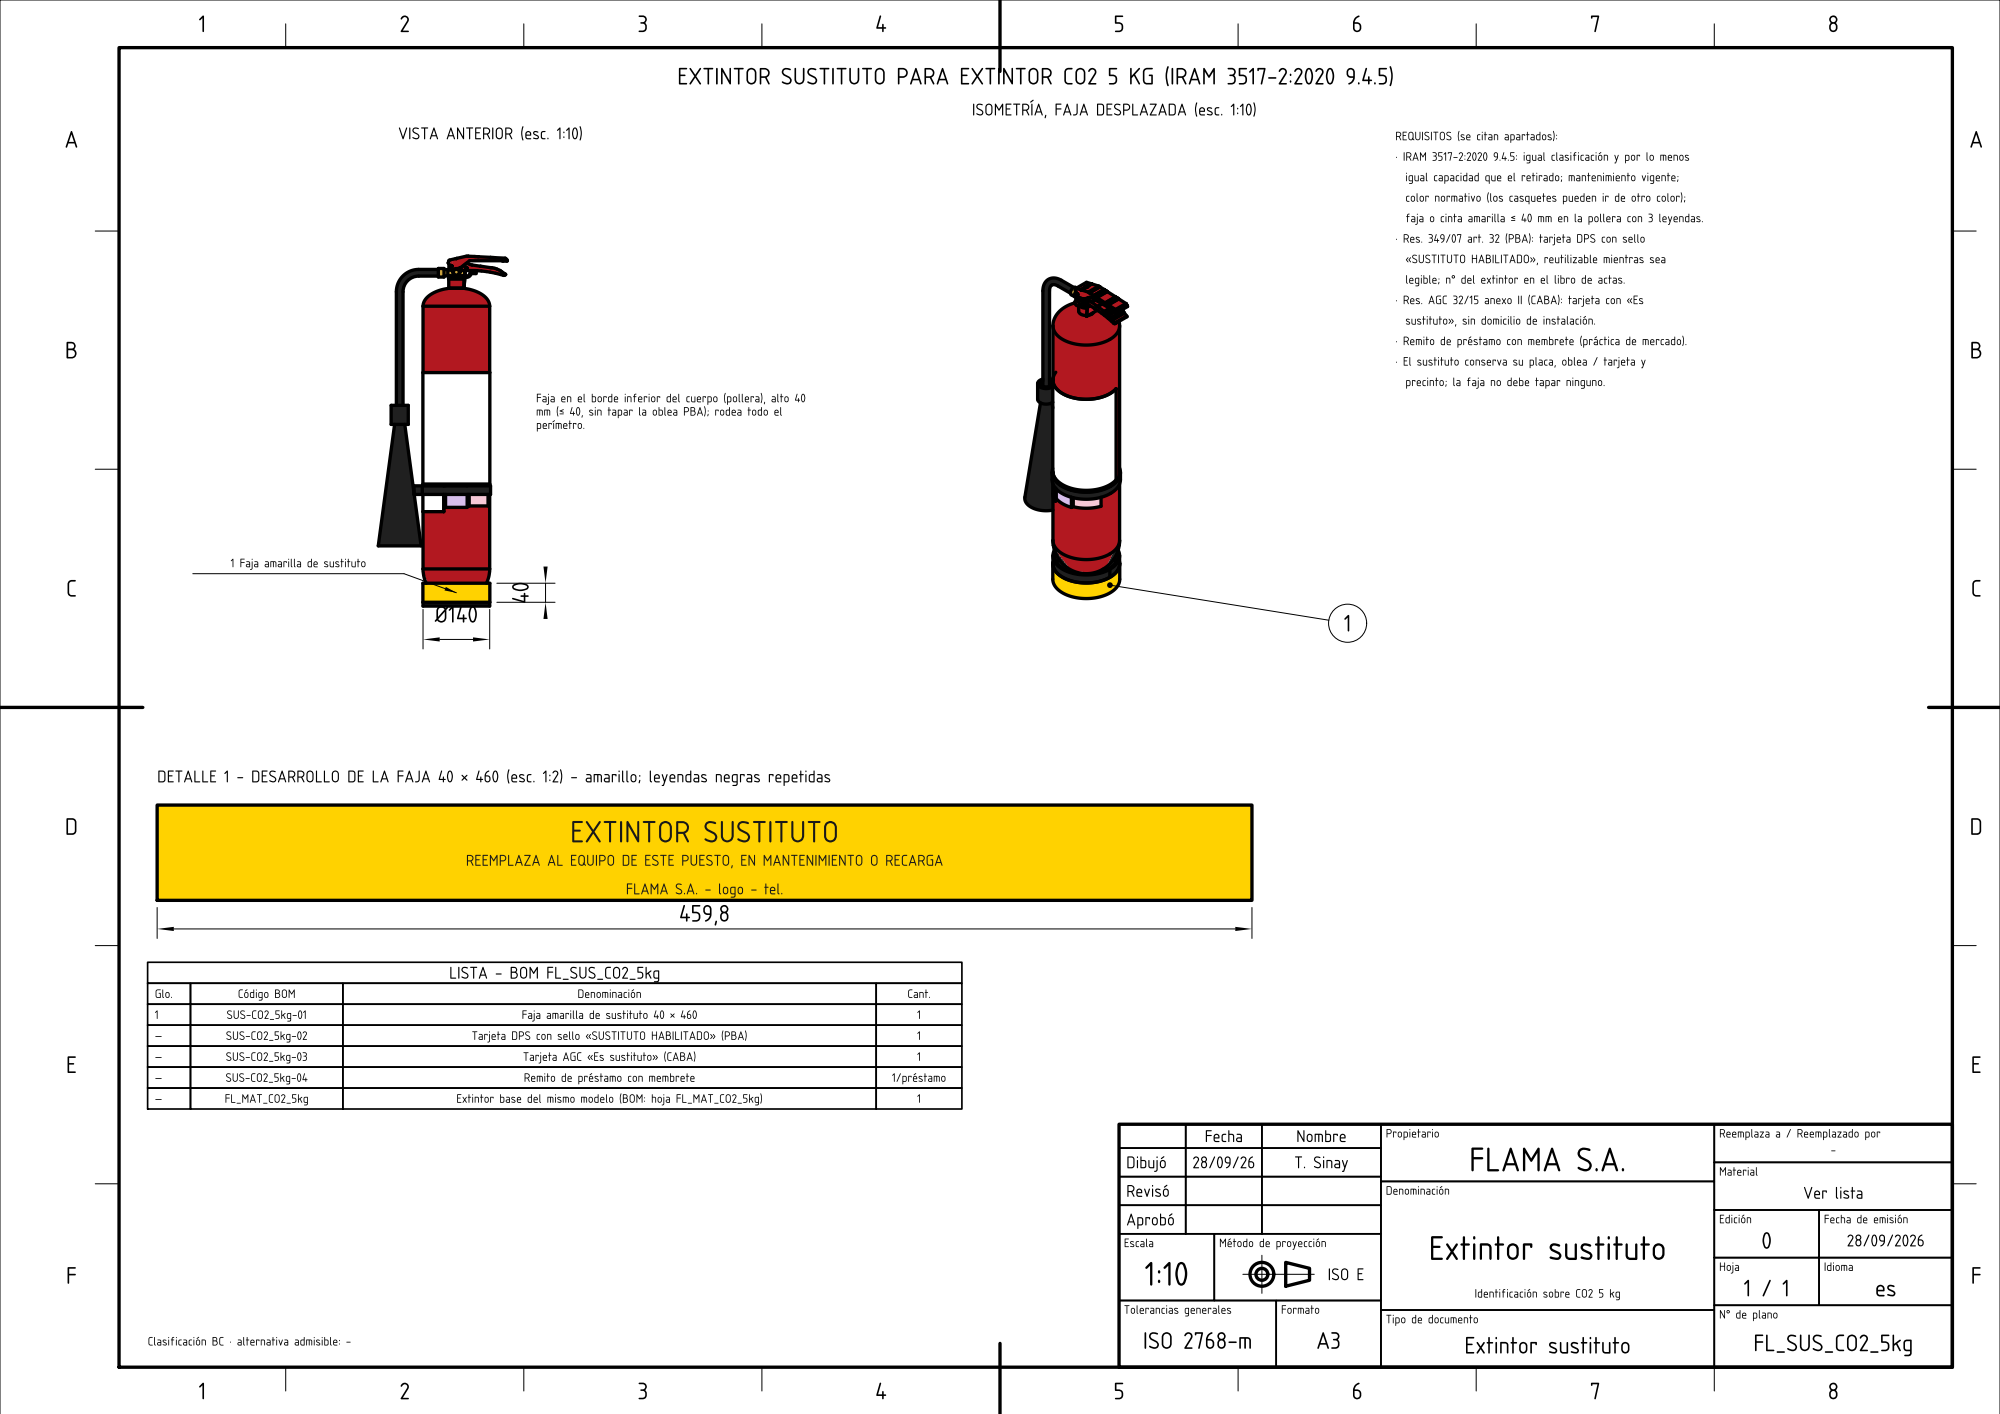
[picture p225: page 1]
