TadeoSinay/planos_flama-/salida/sustituto/FL_SUS_HCFC-HFC_5kg.pdf

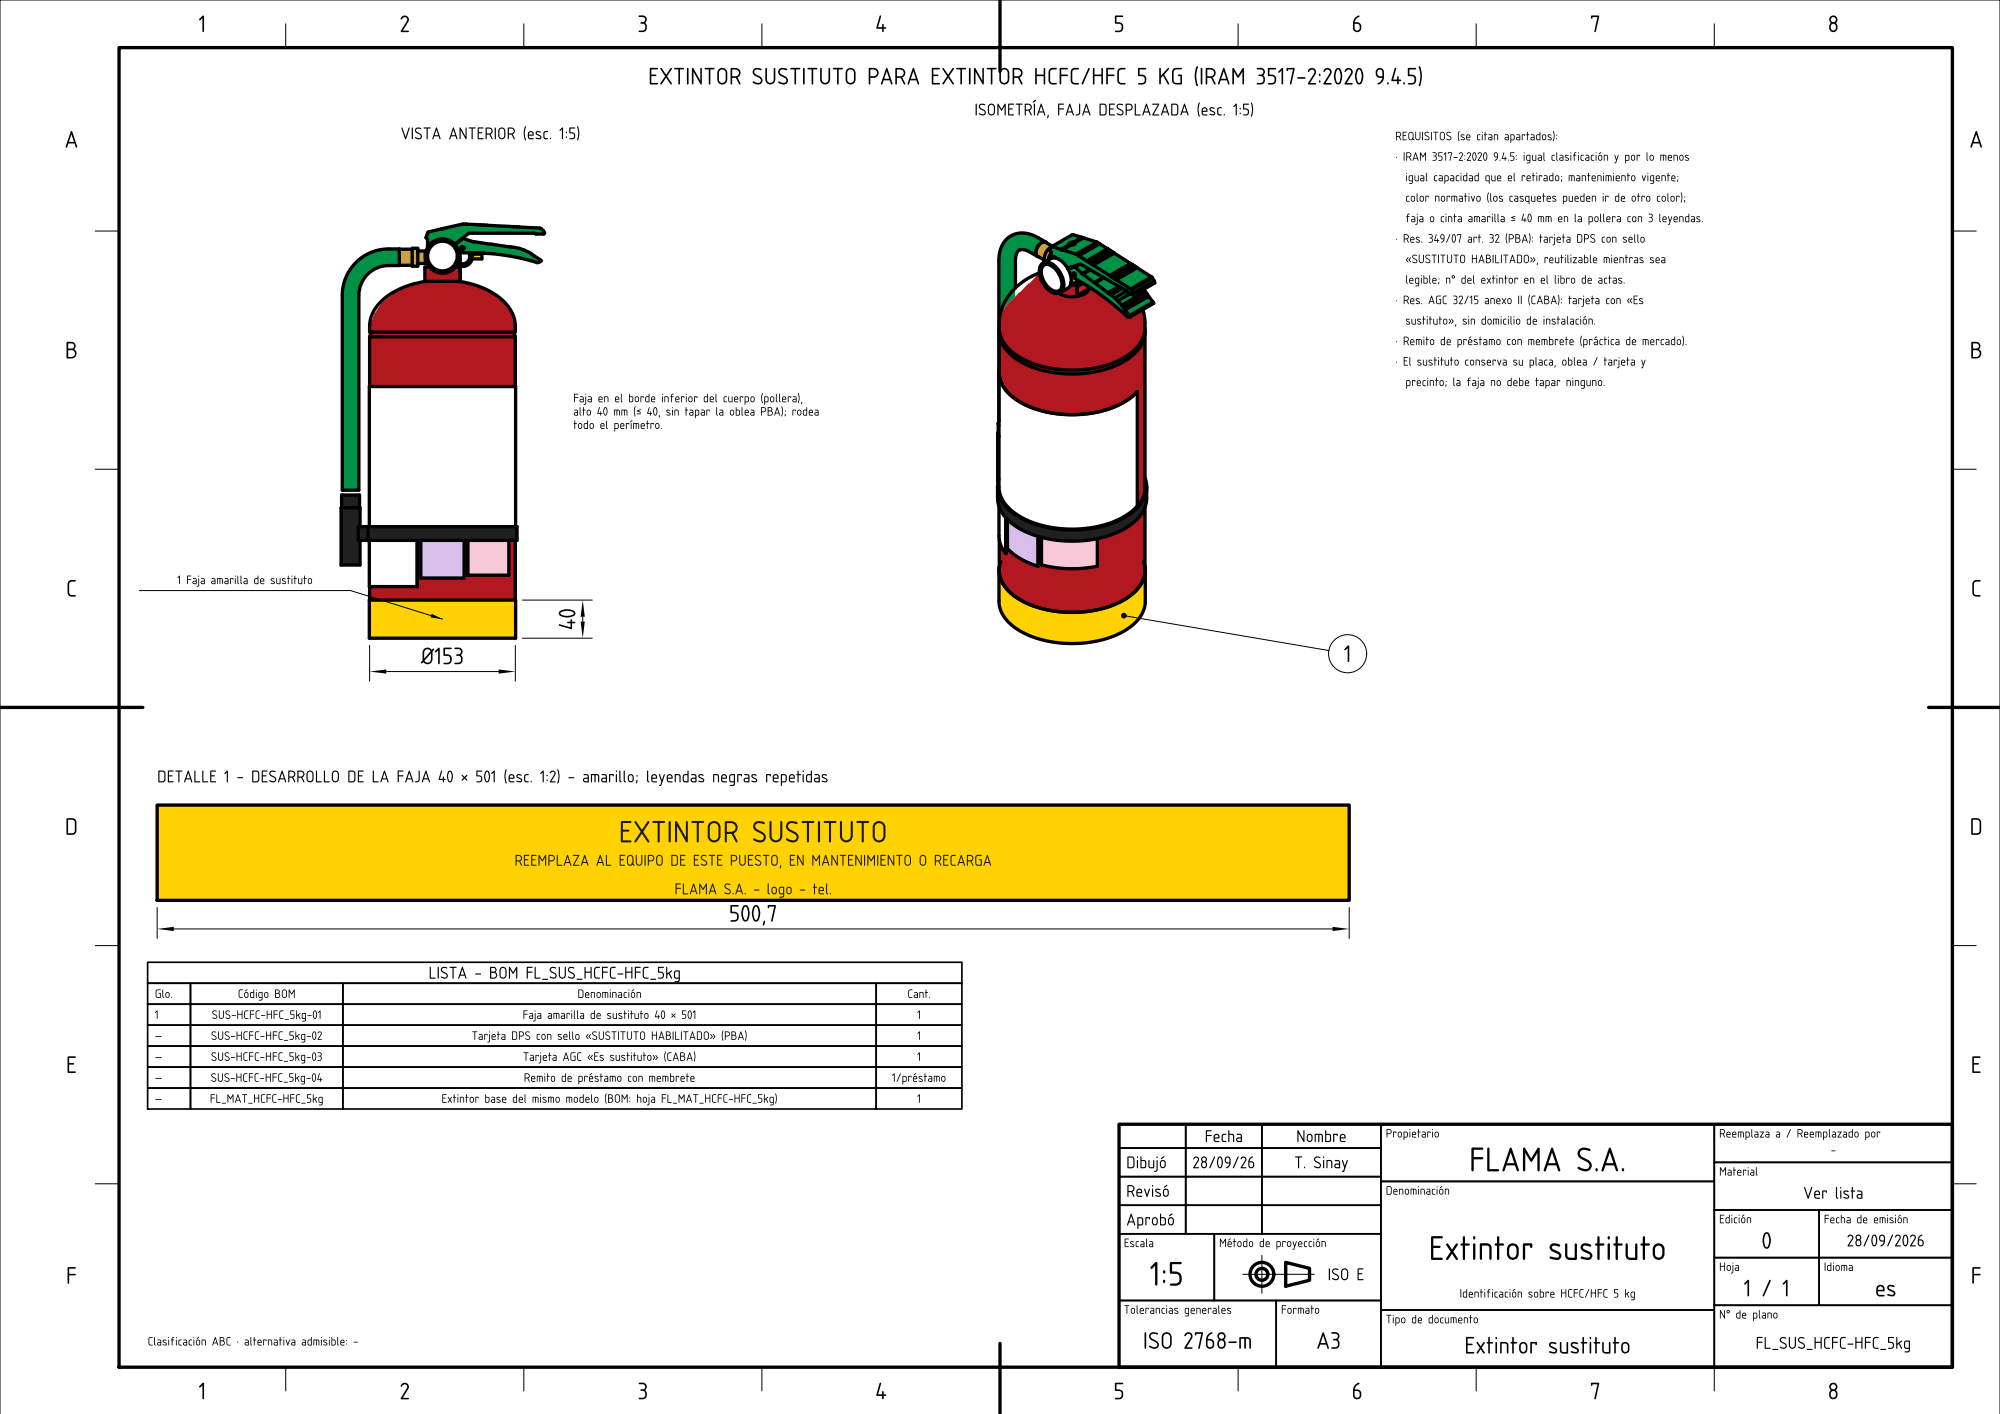
[picture p226: page 1]
