TadeoSinay/planos_flama-/salida/sustituto/FL_SUS_SALESK_6l.pdf

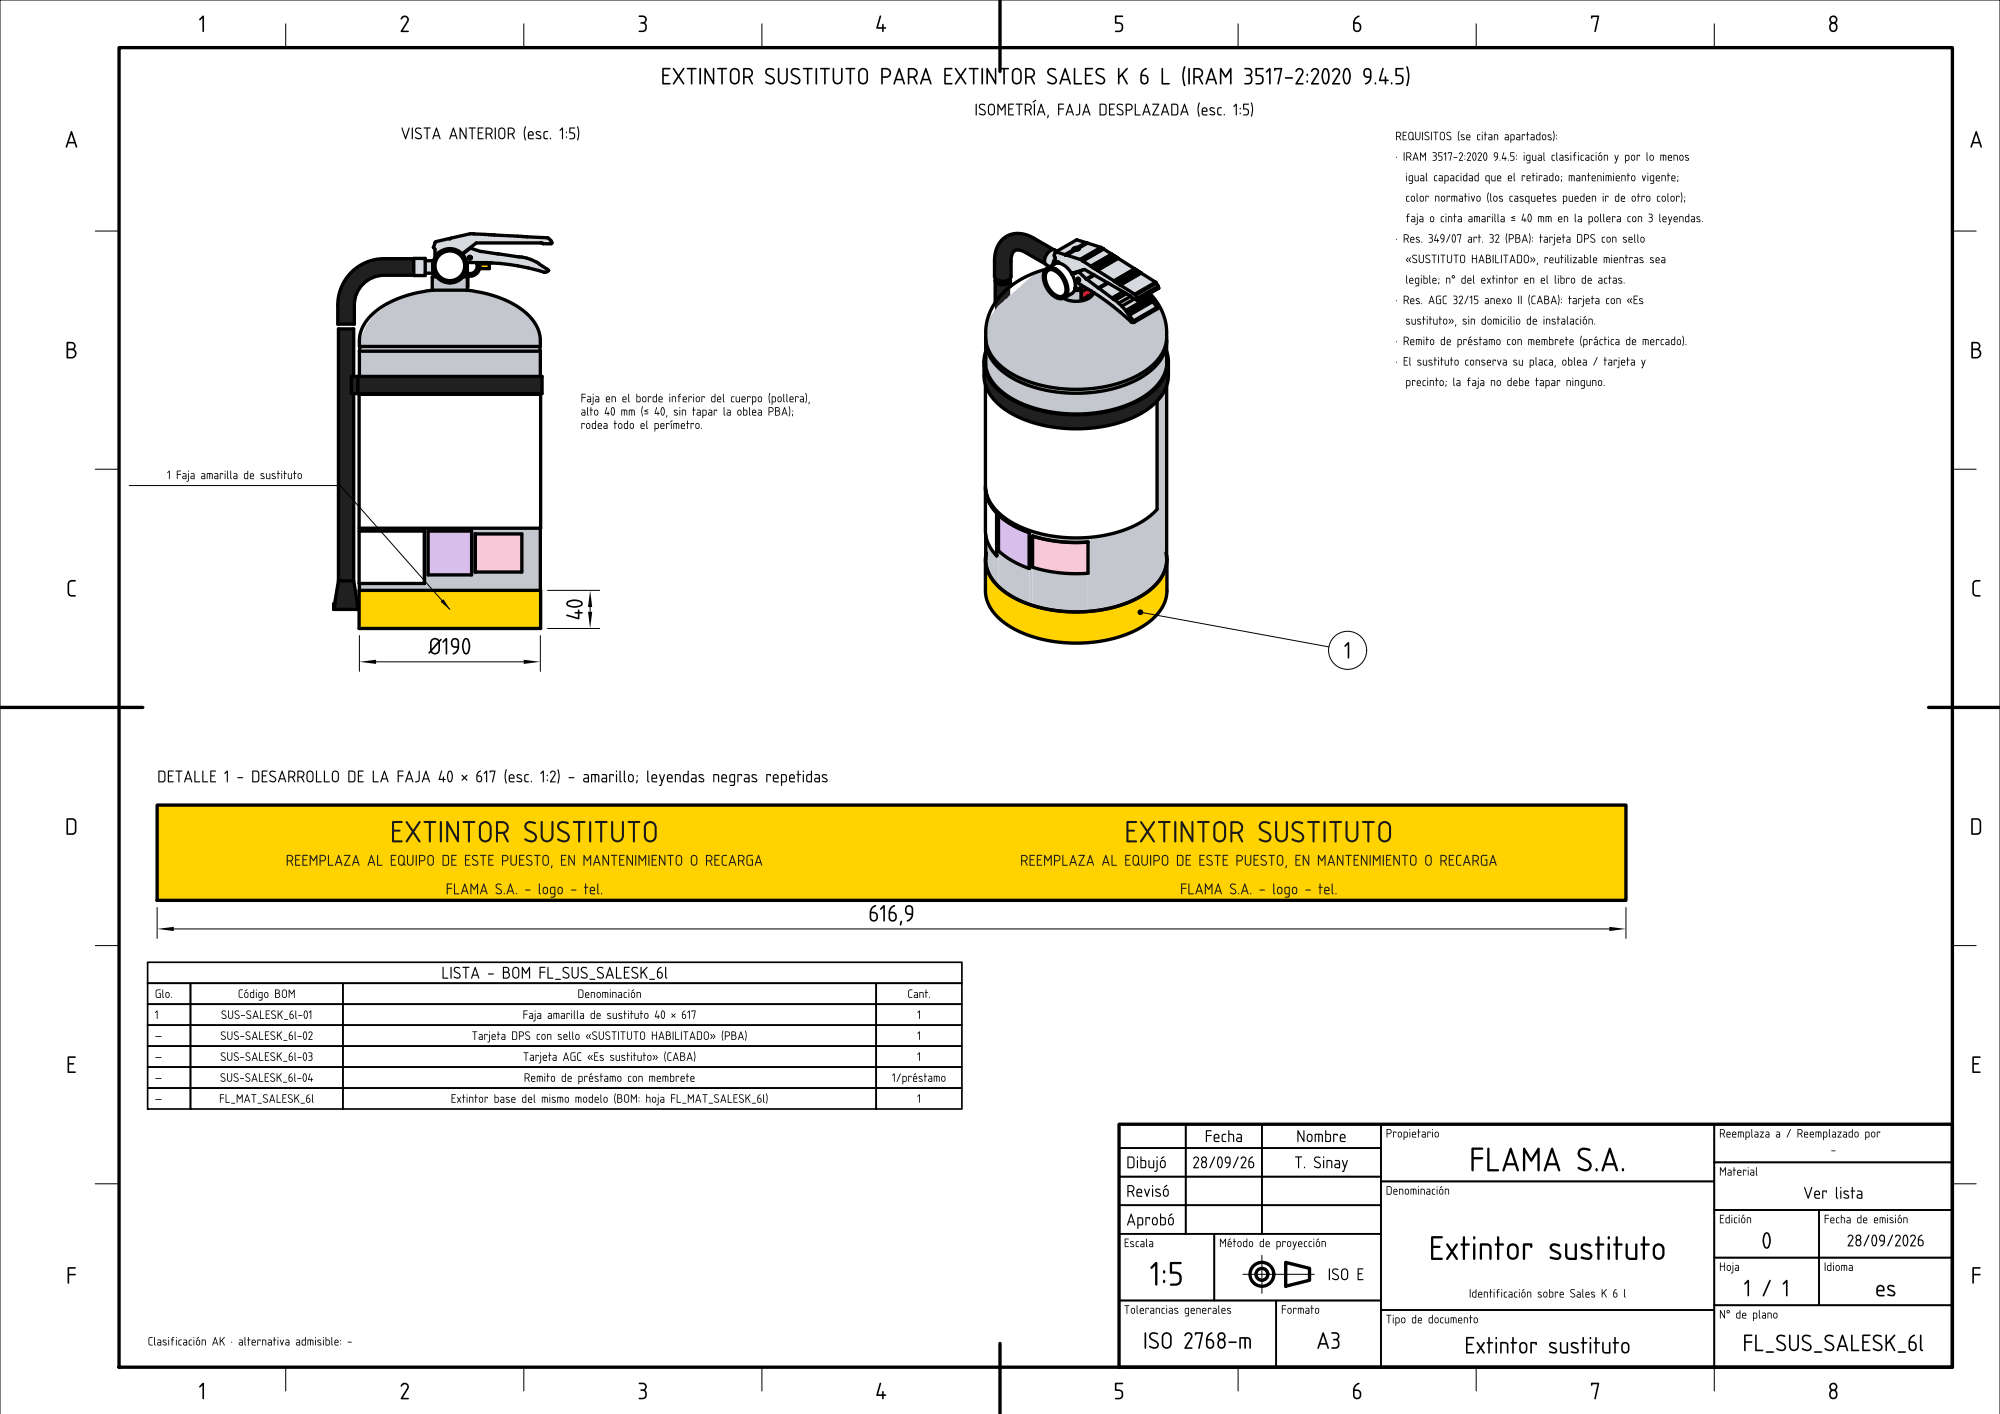
[picture p227: page 1]
