TadeoSinay/planos_flama-/salida/cilindros/FLAMA_cilindros.pdf

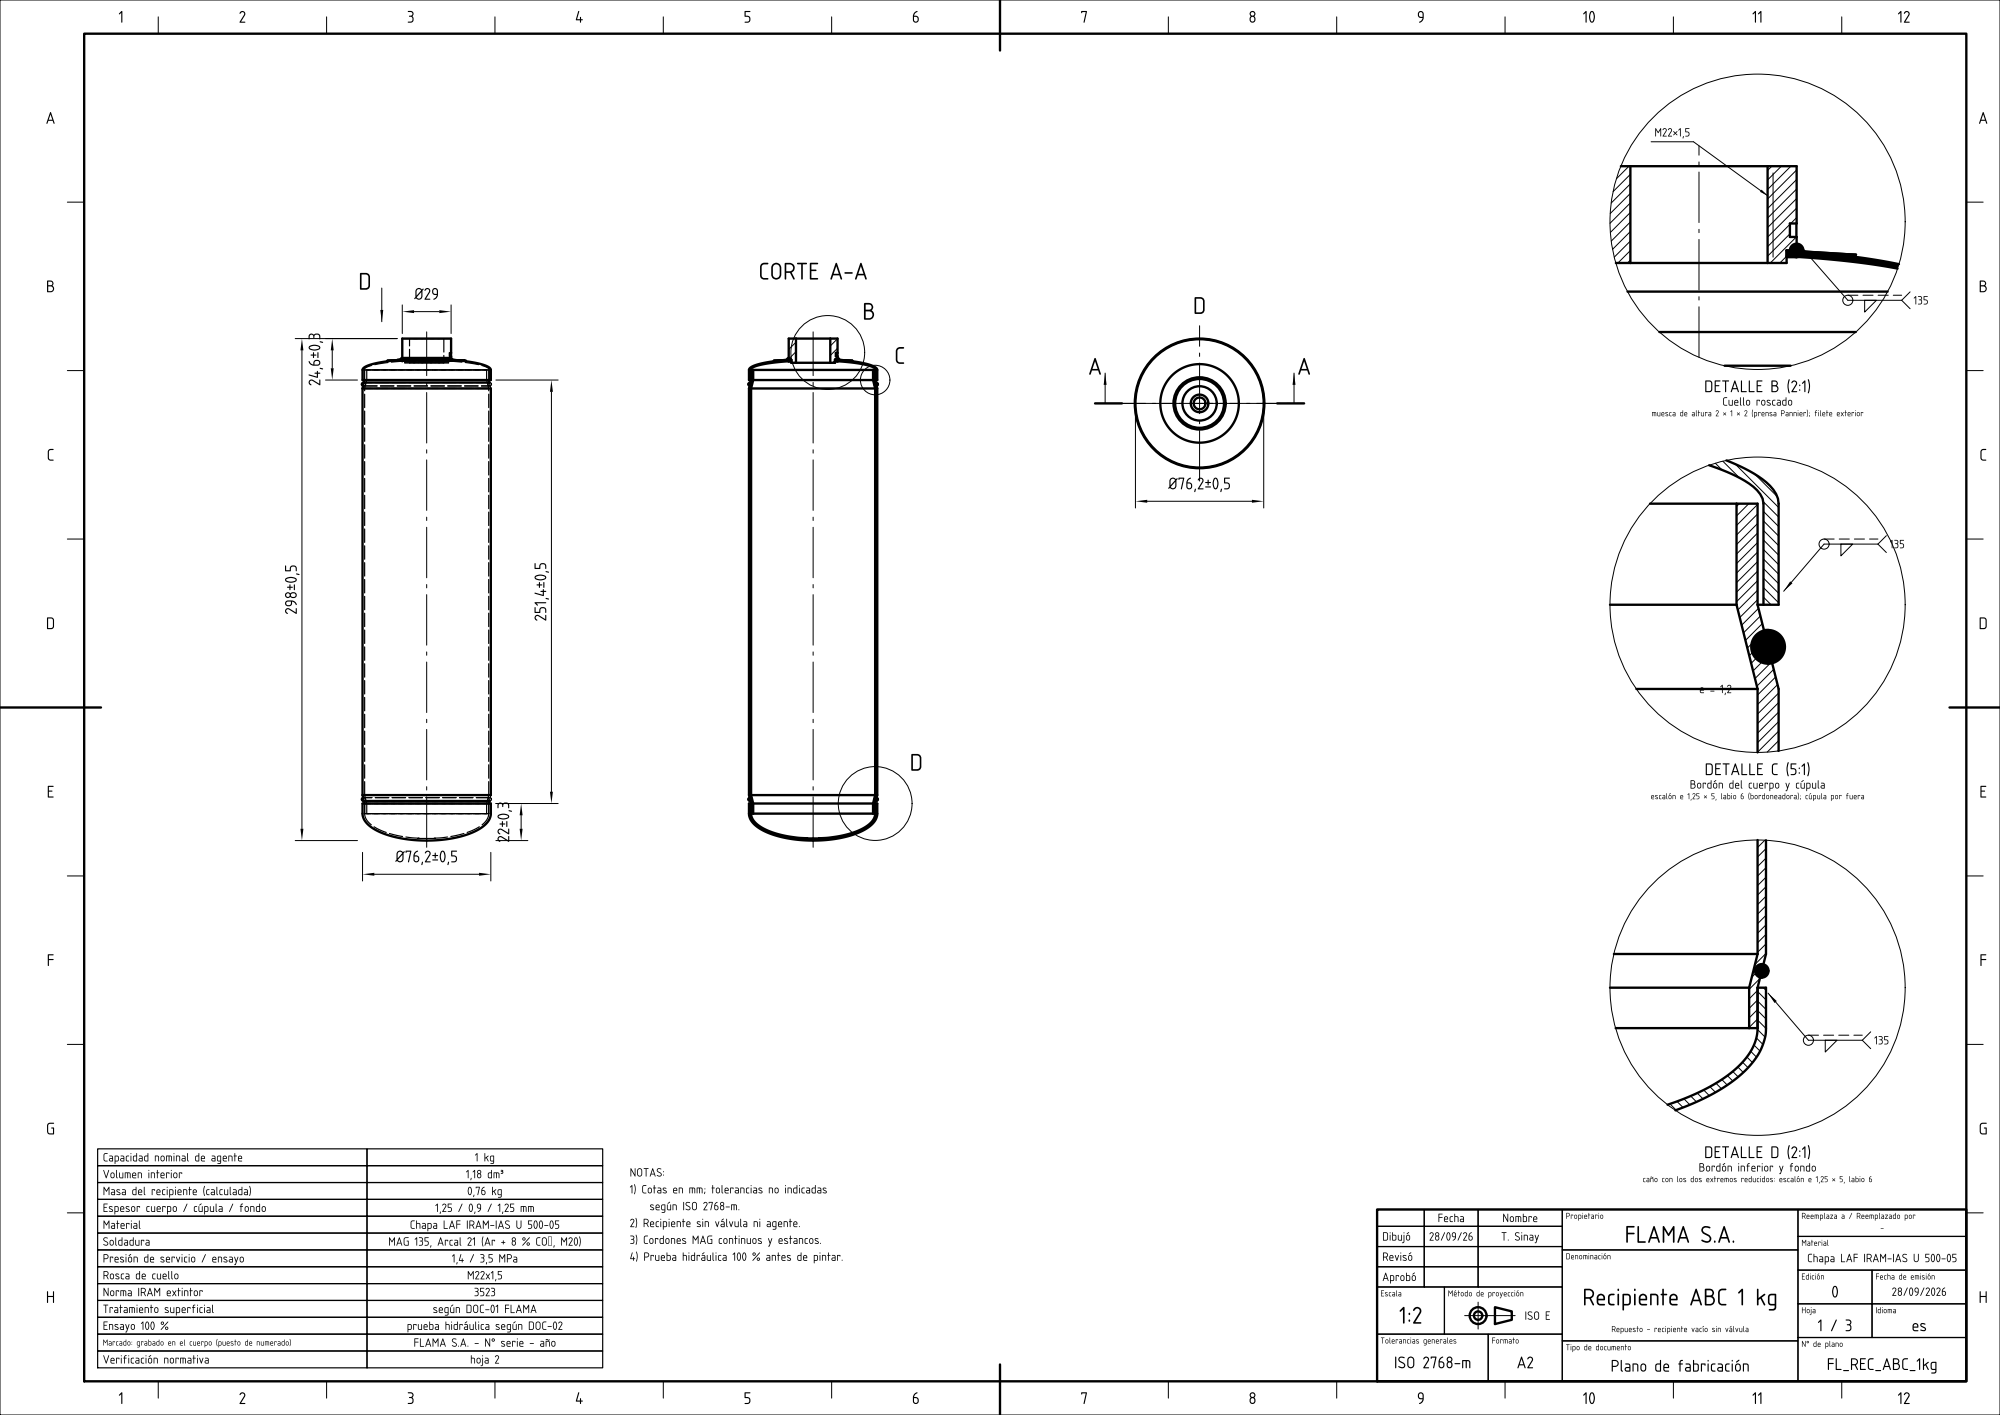
[picture p228: page 1]

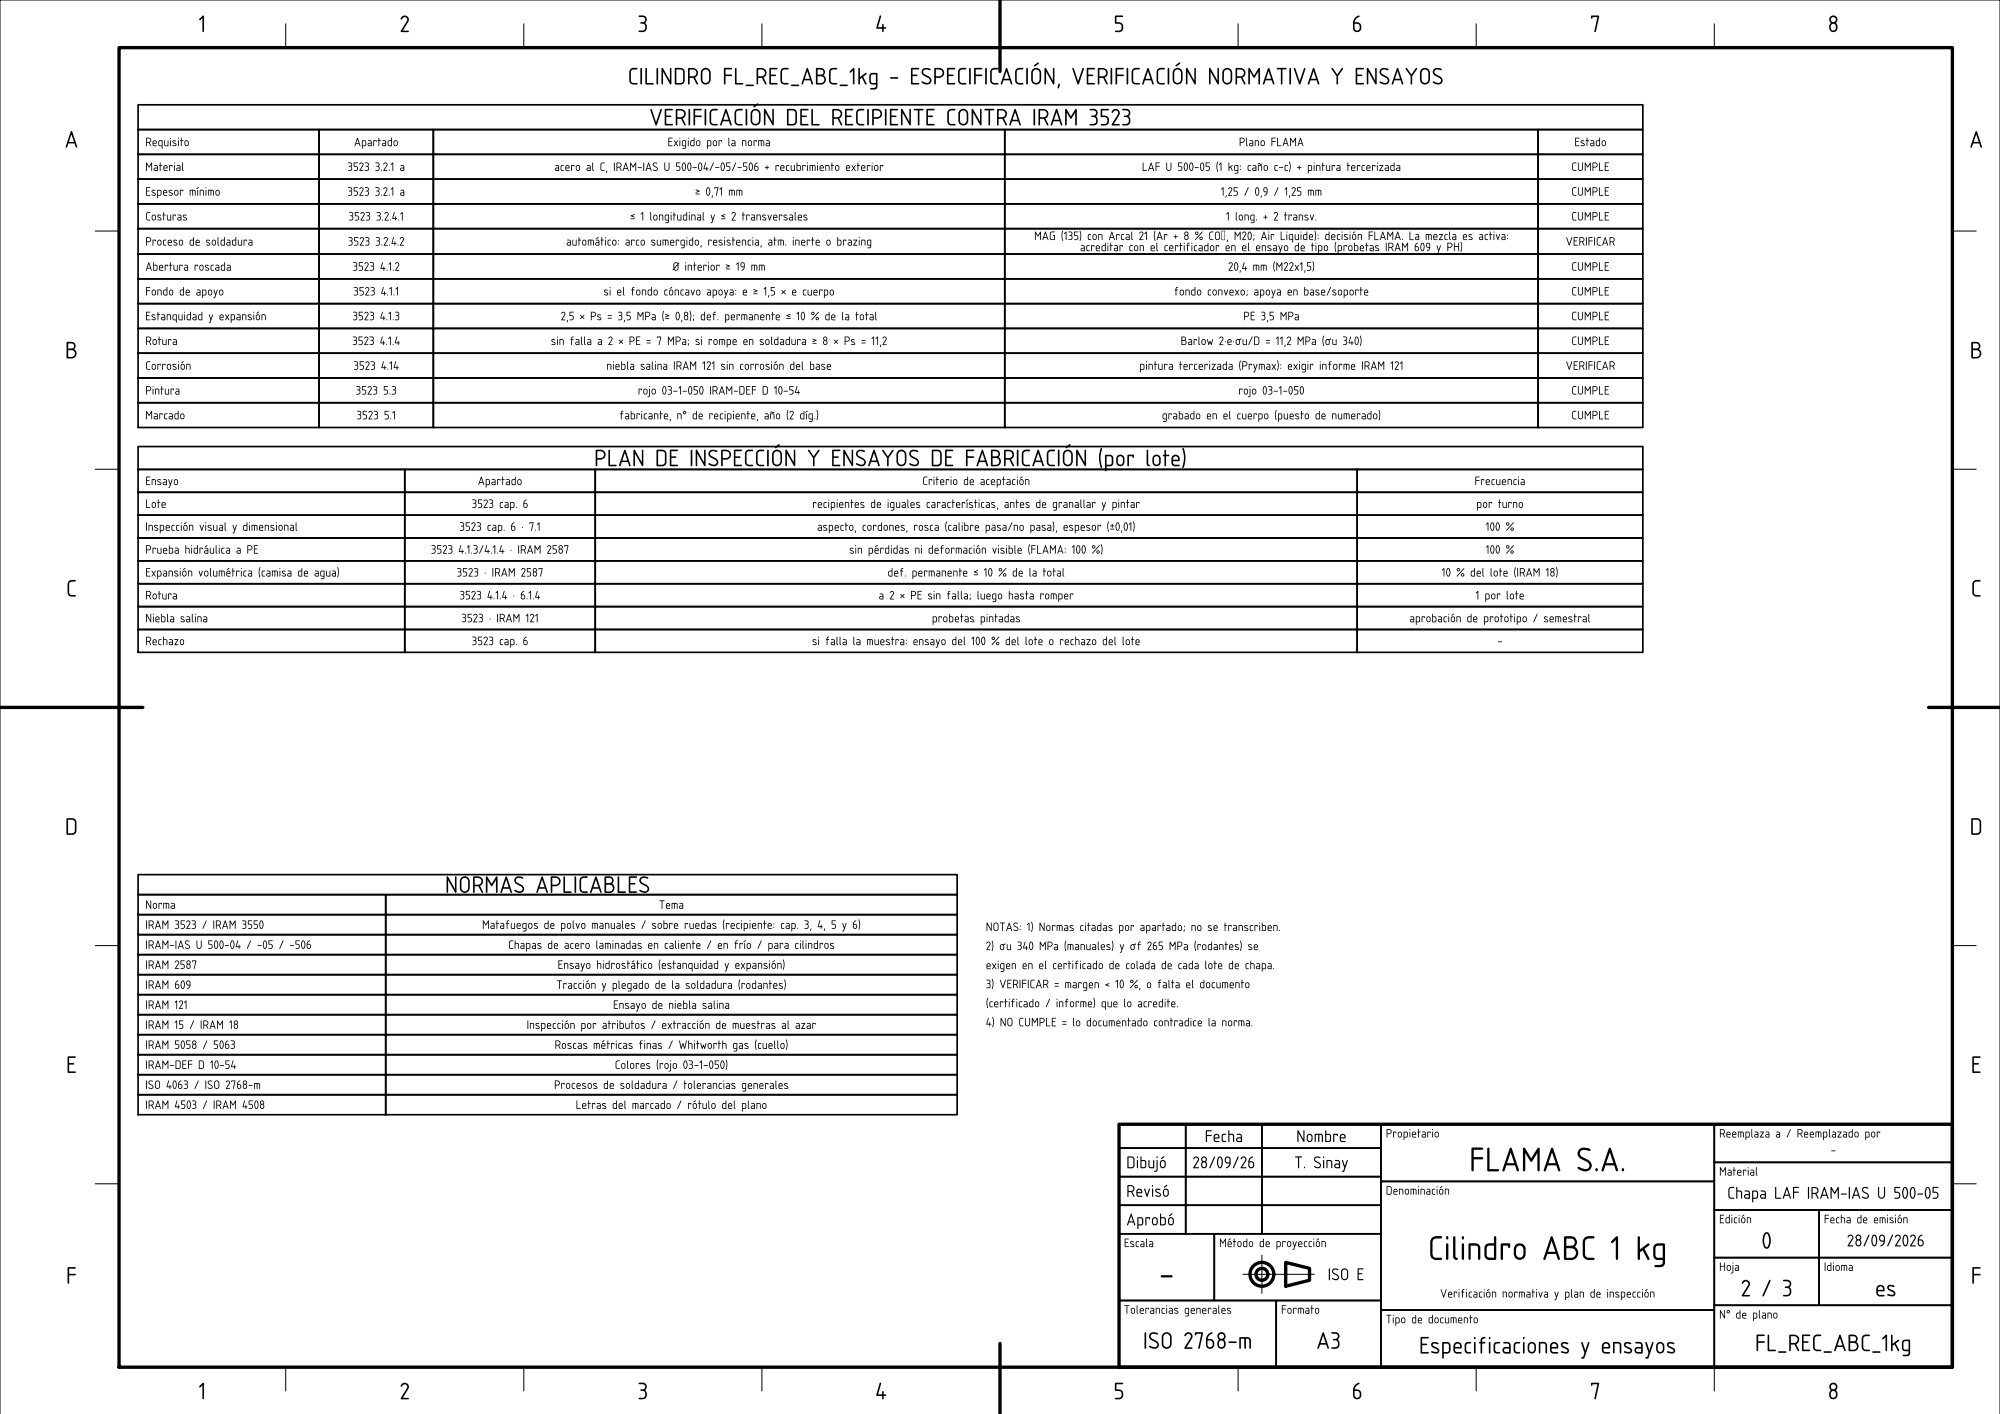
[picture p229: page 2]

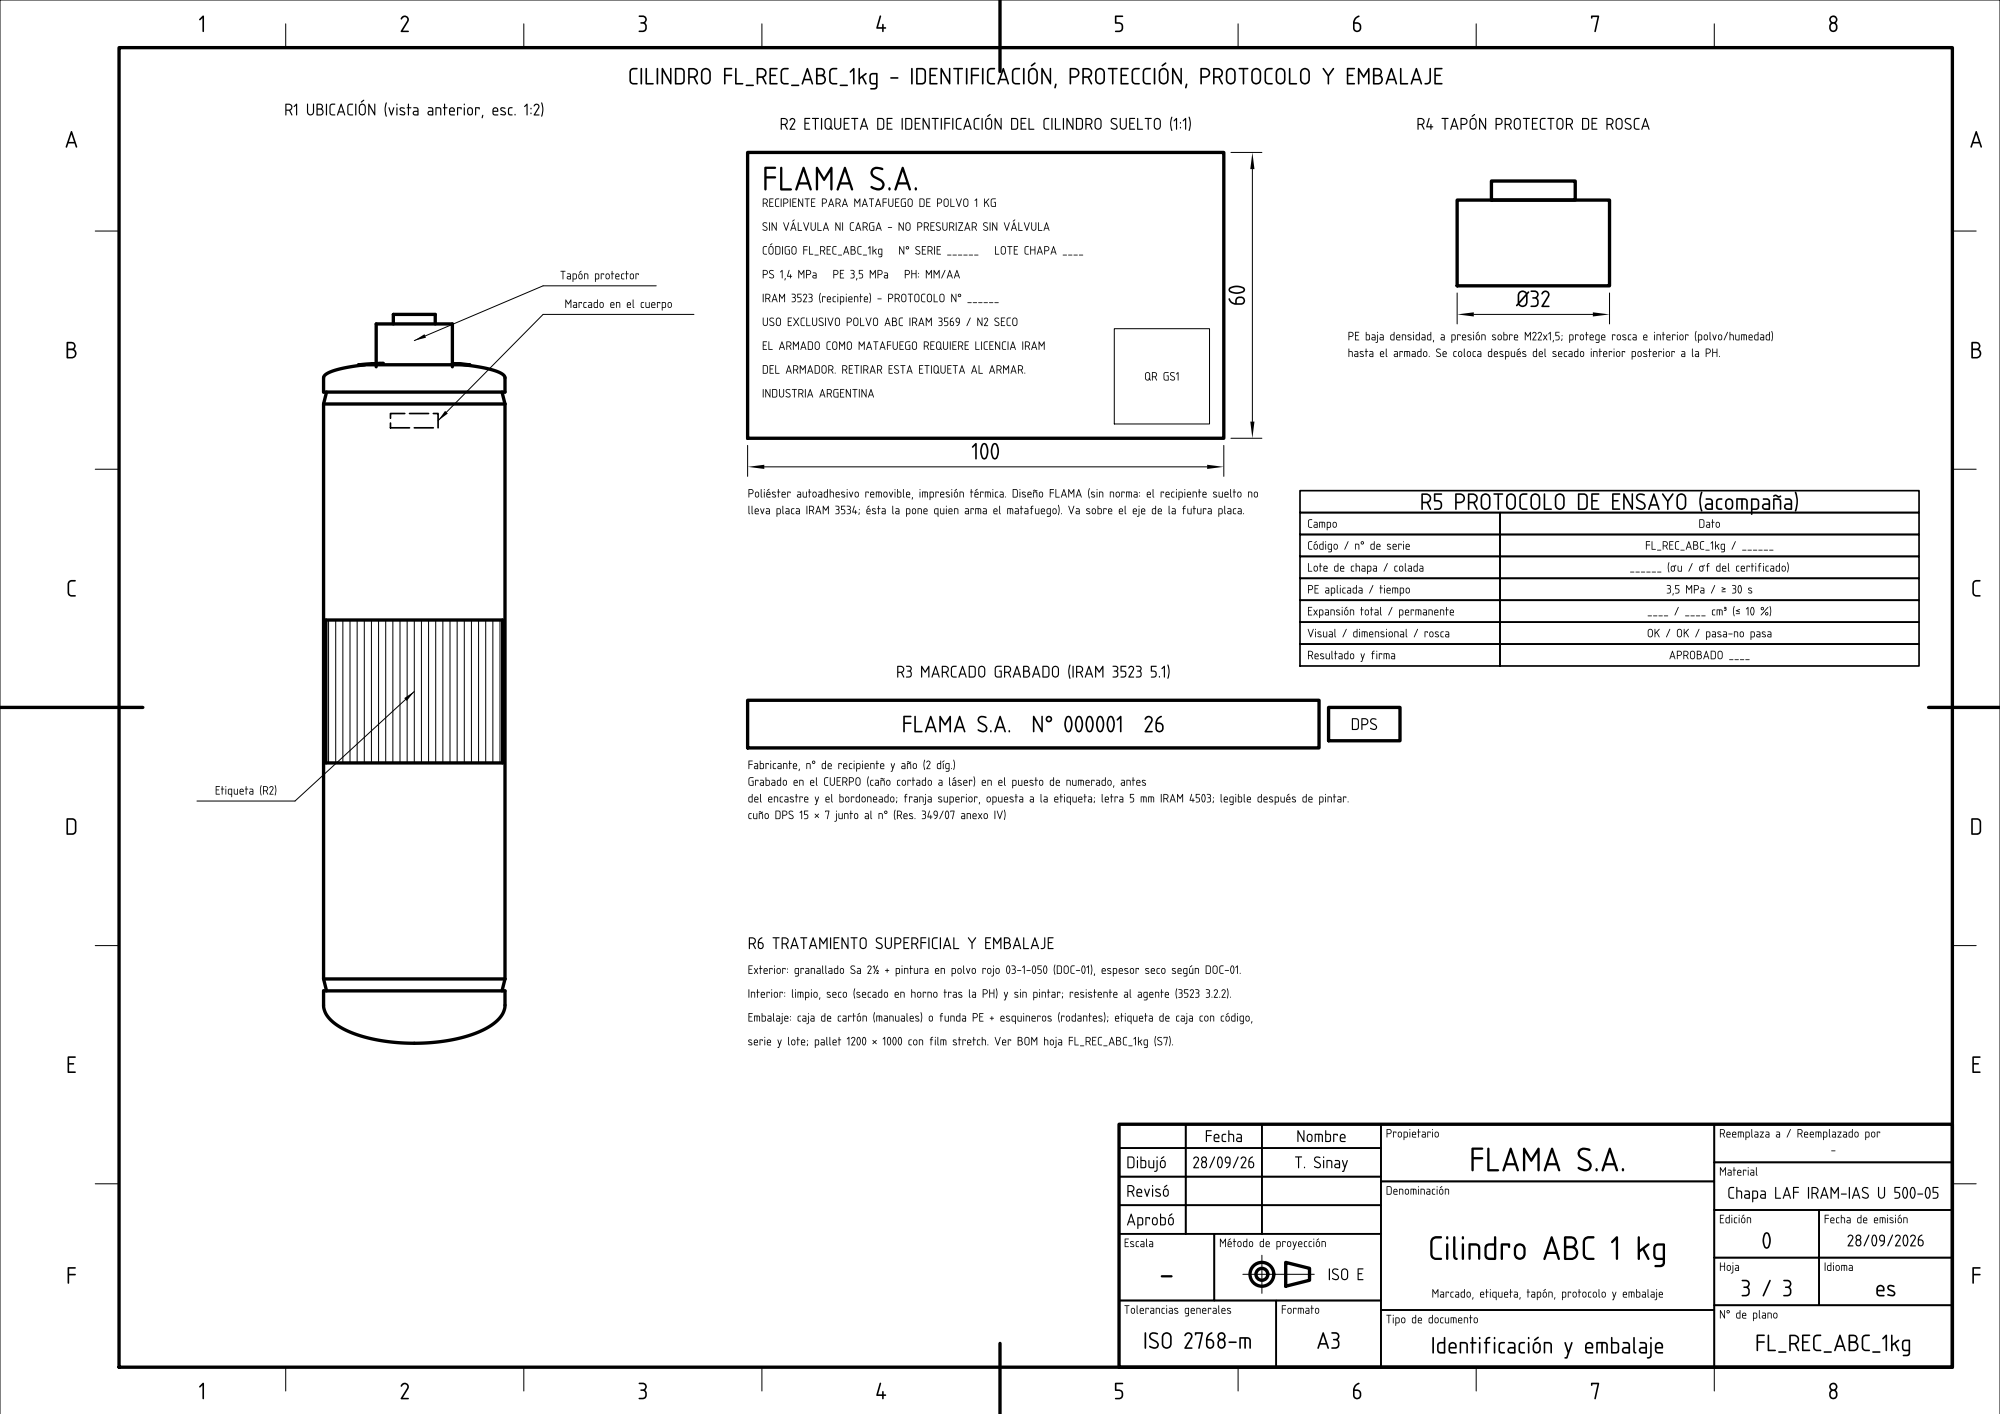
[picture p230: page 3]

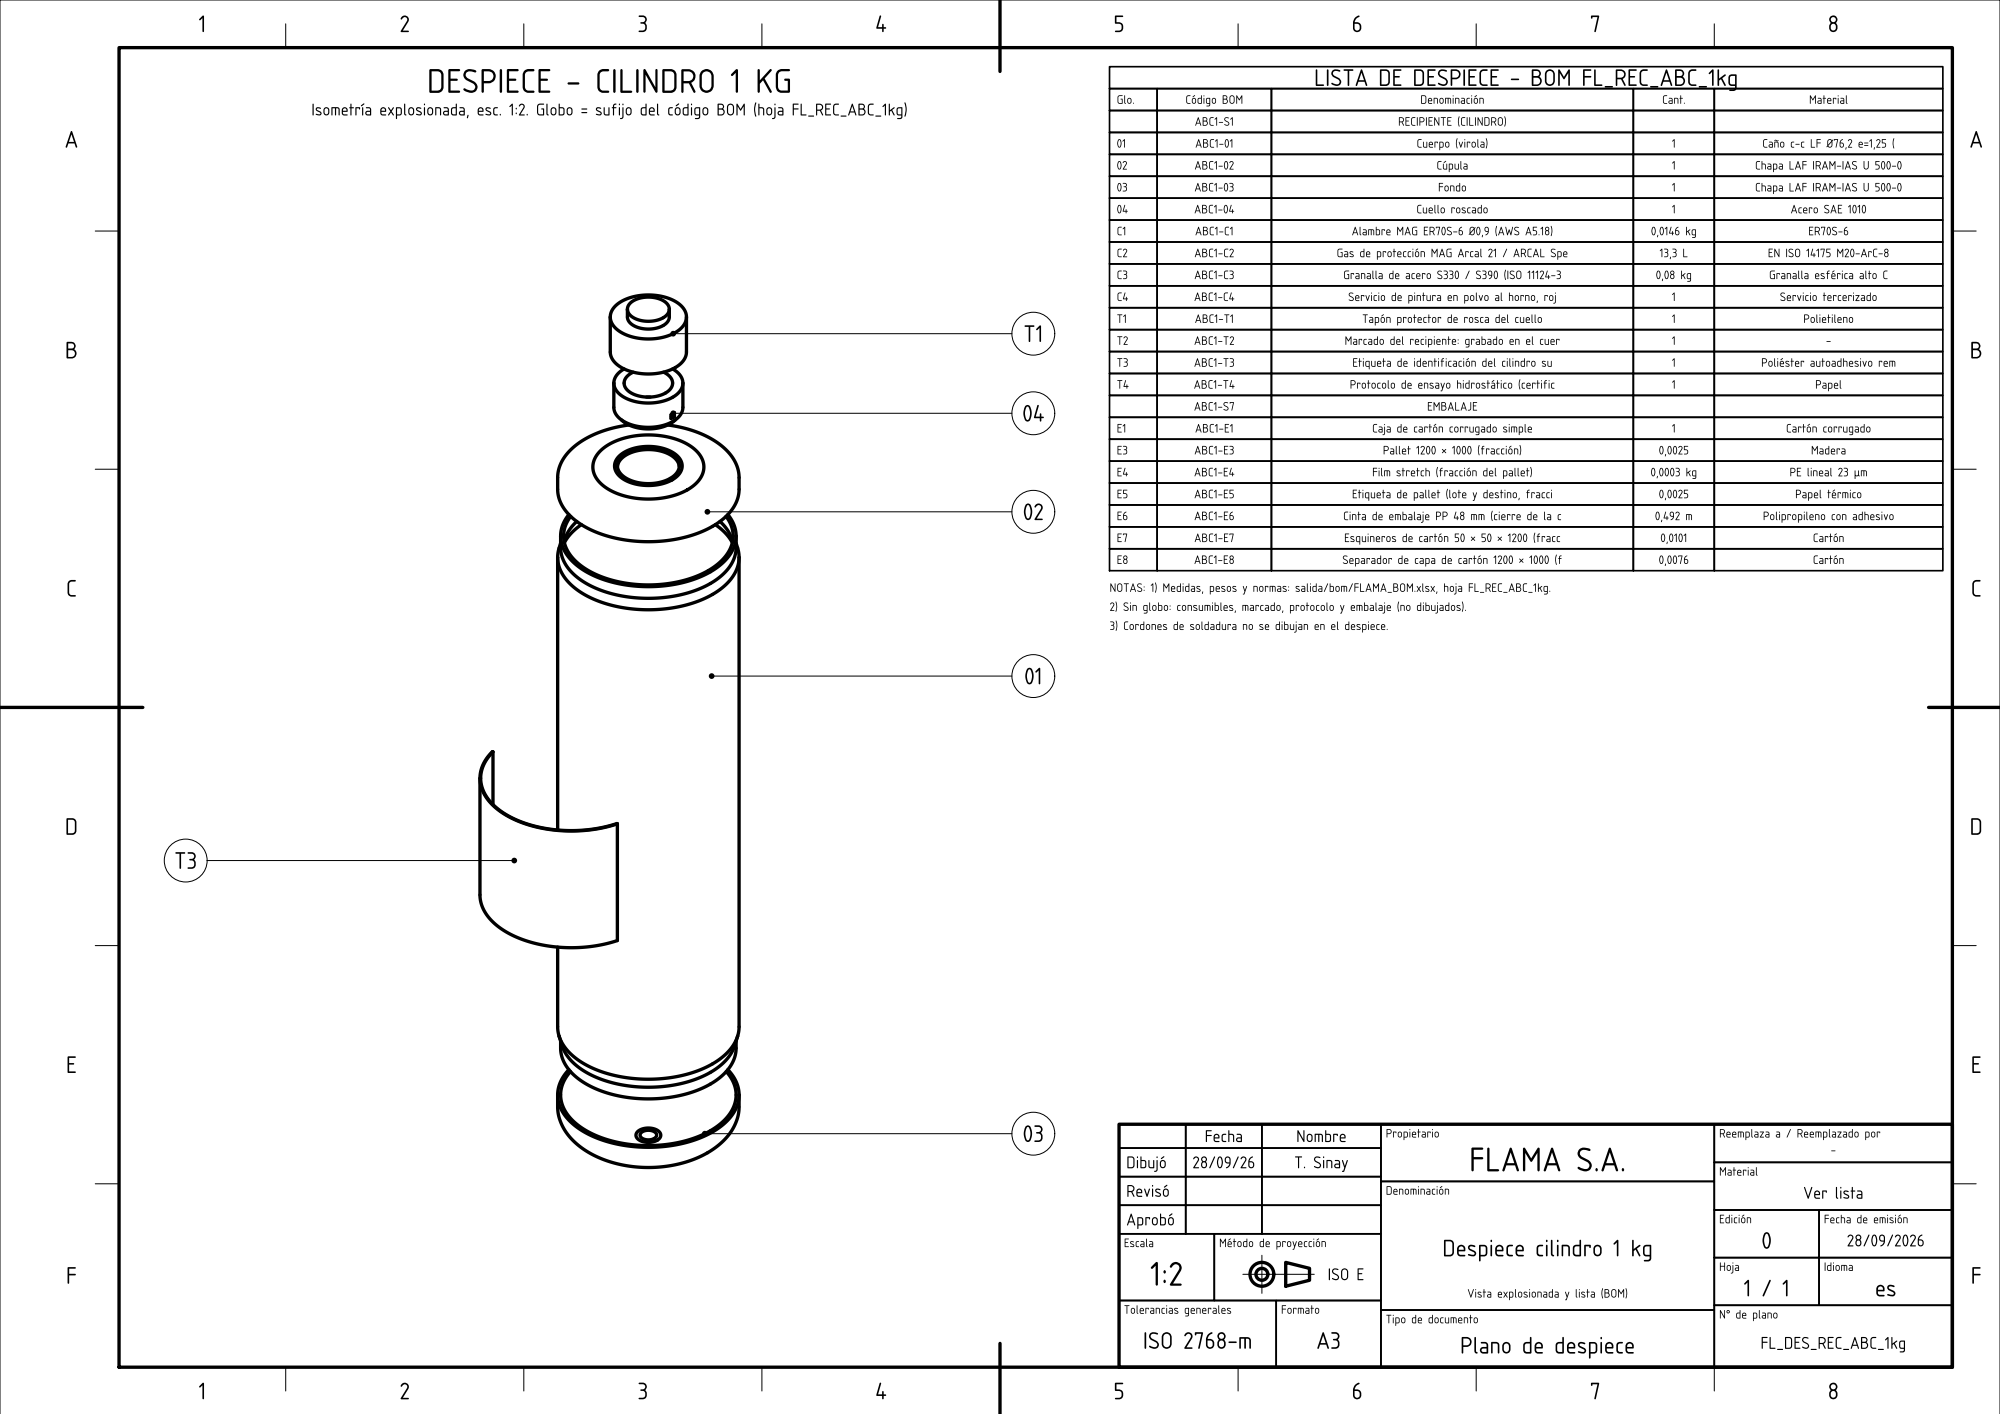
[picture p231: page 4]

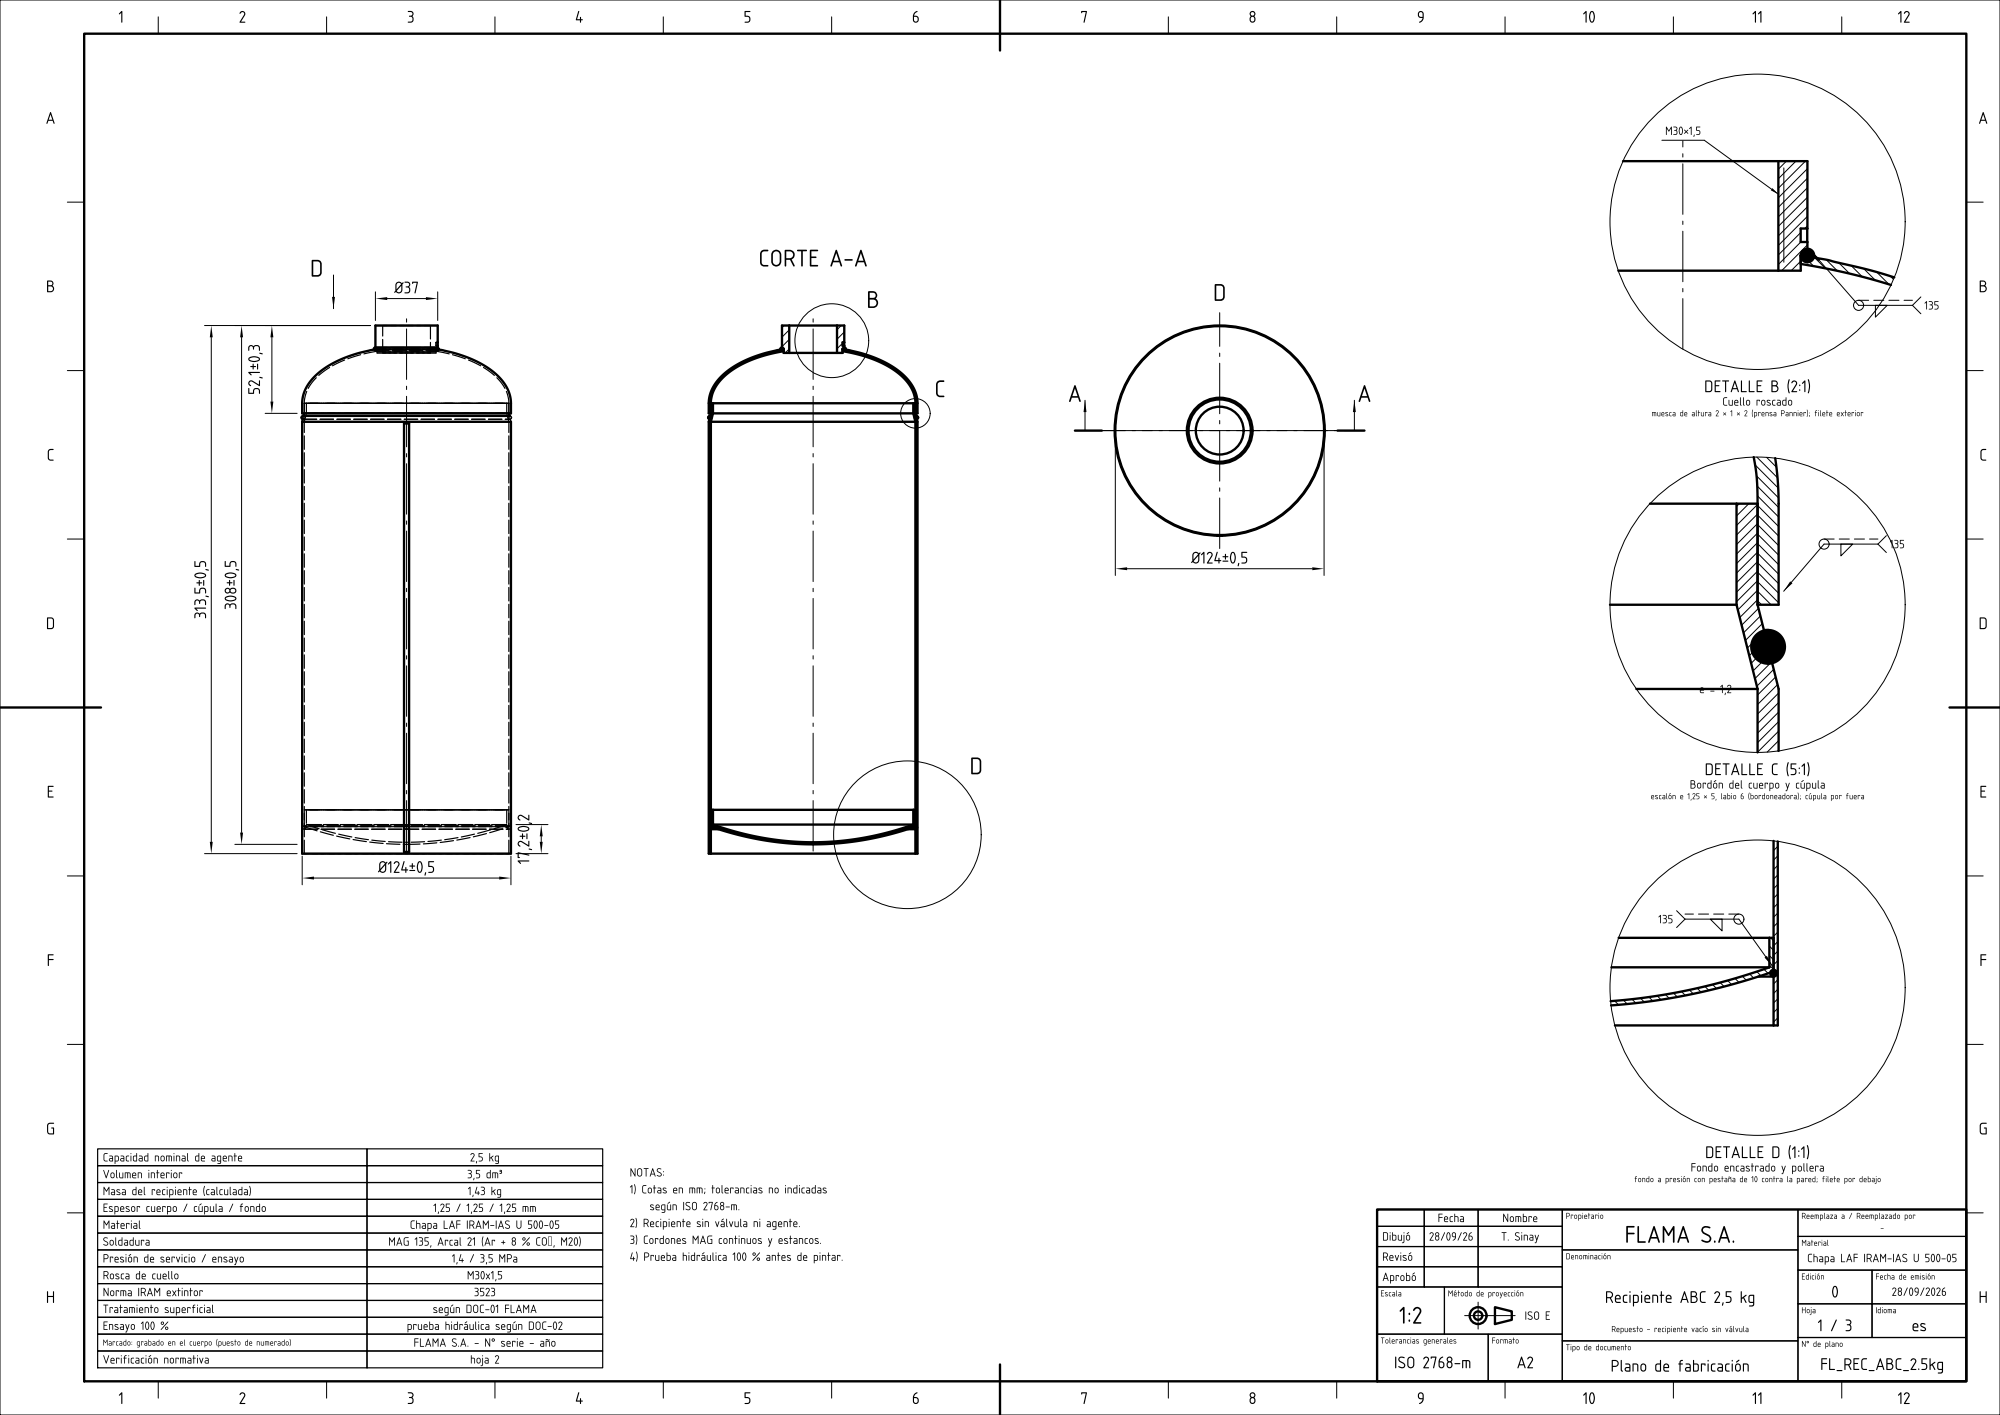
[picture p232: page 5]

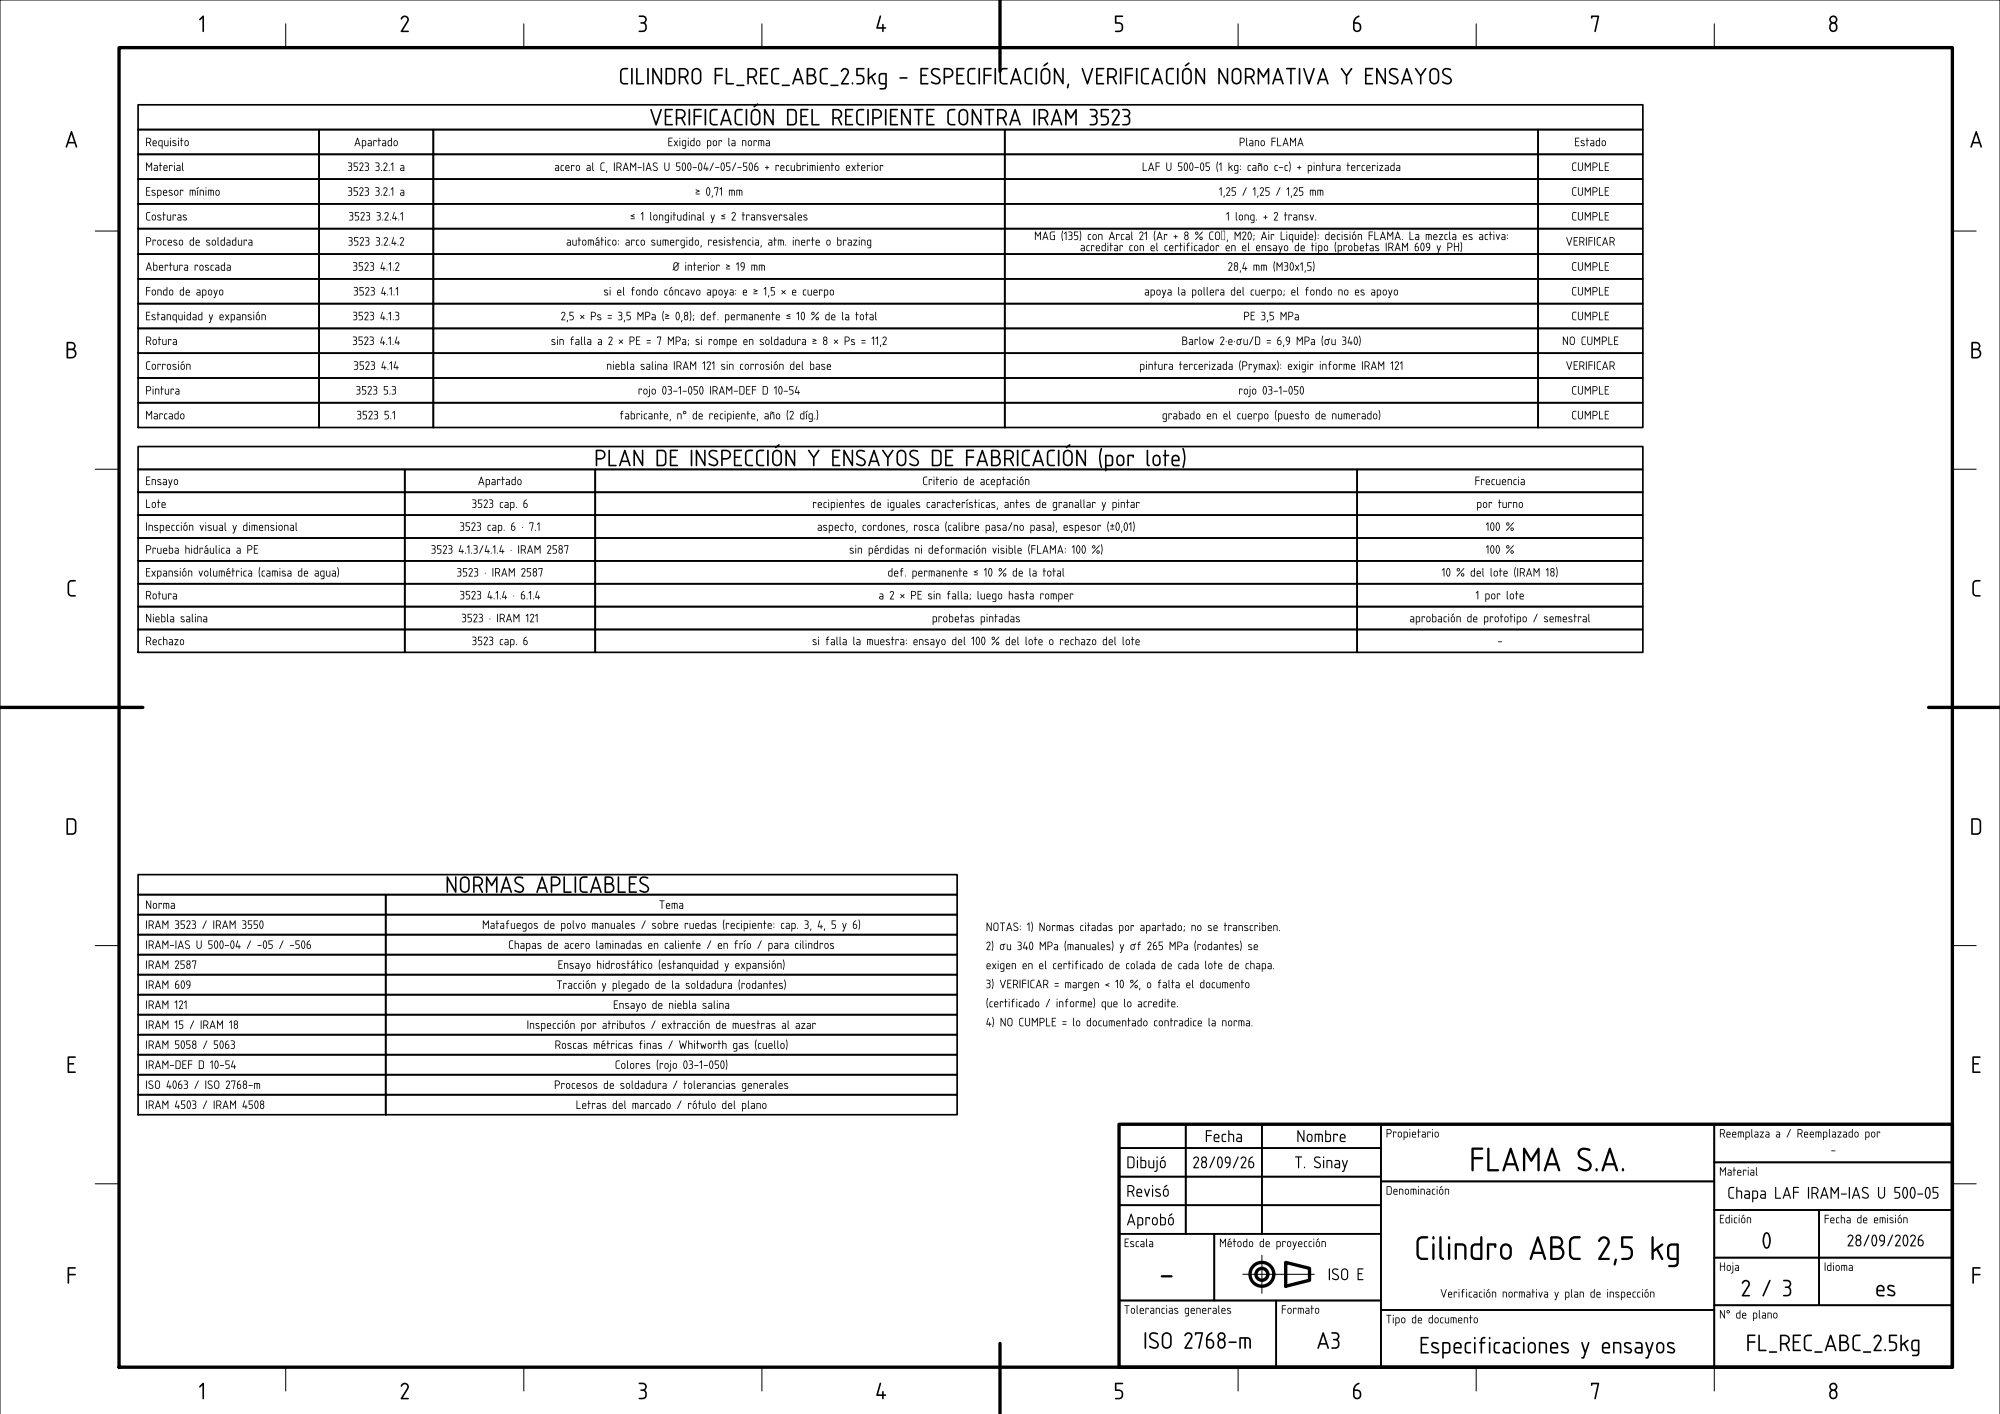
[picture p233: page 6]

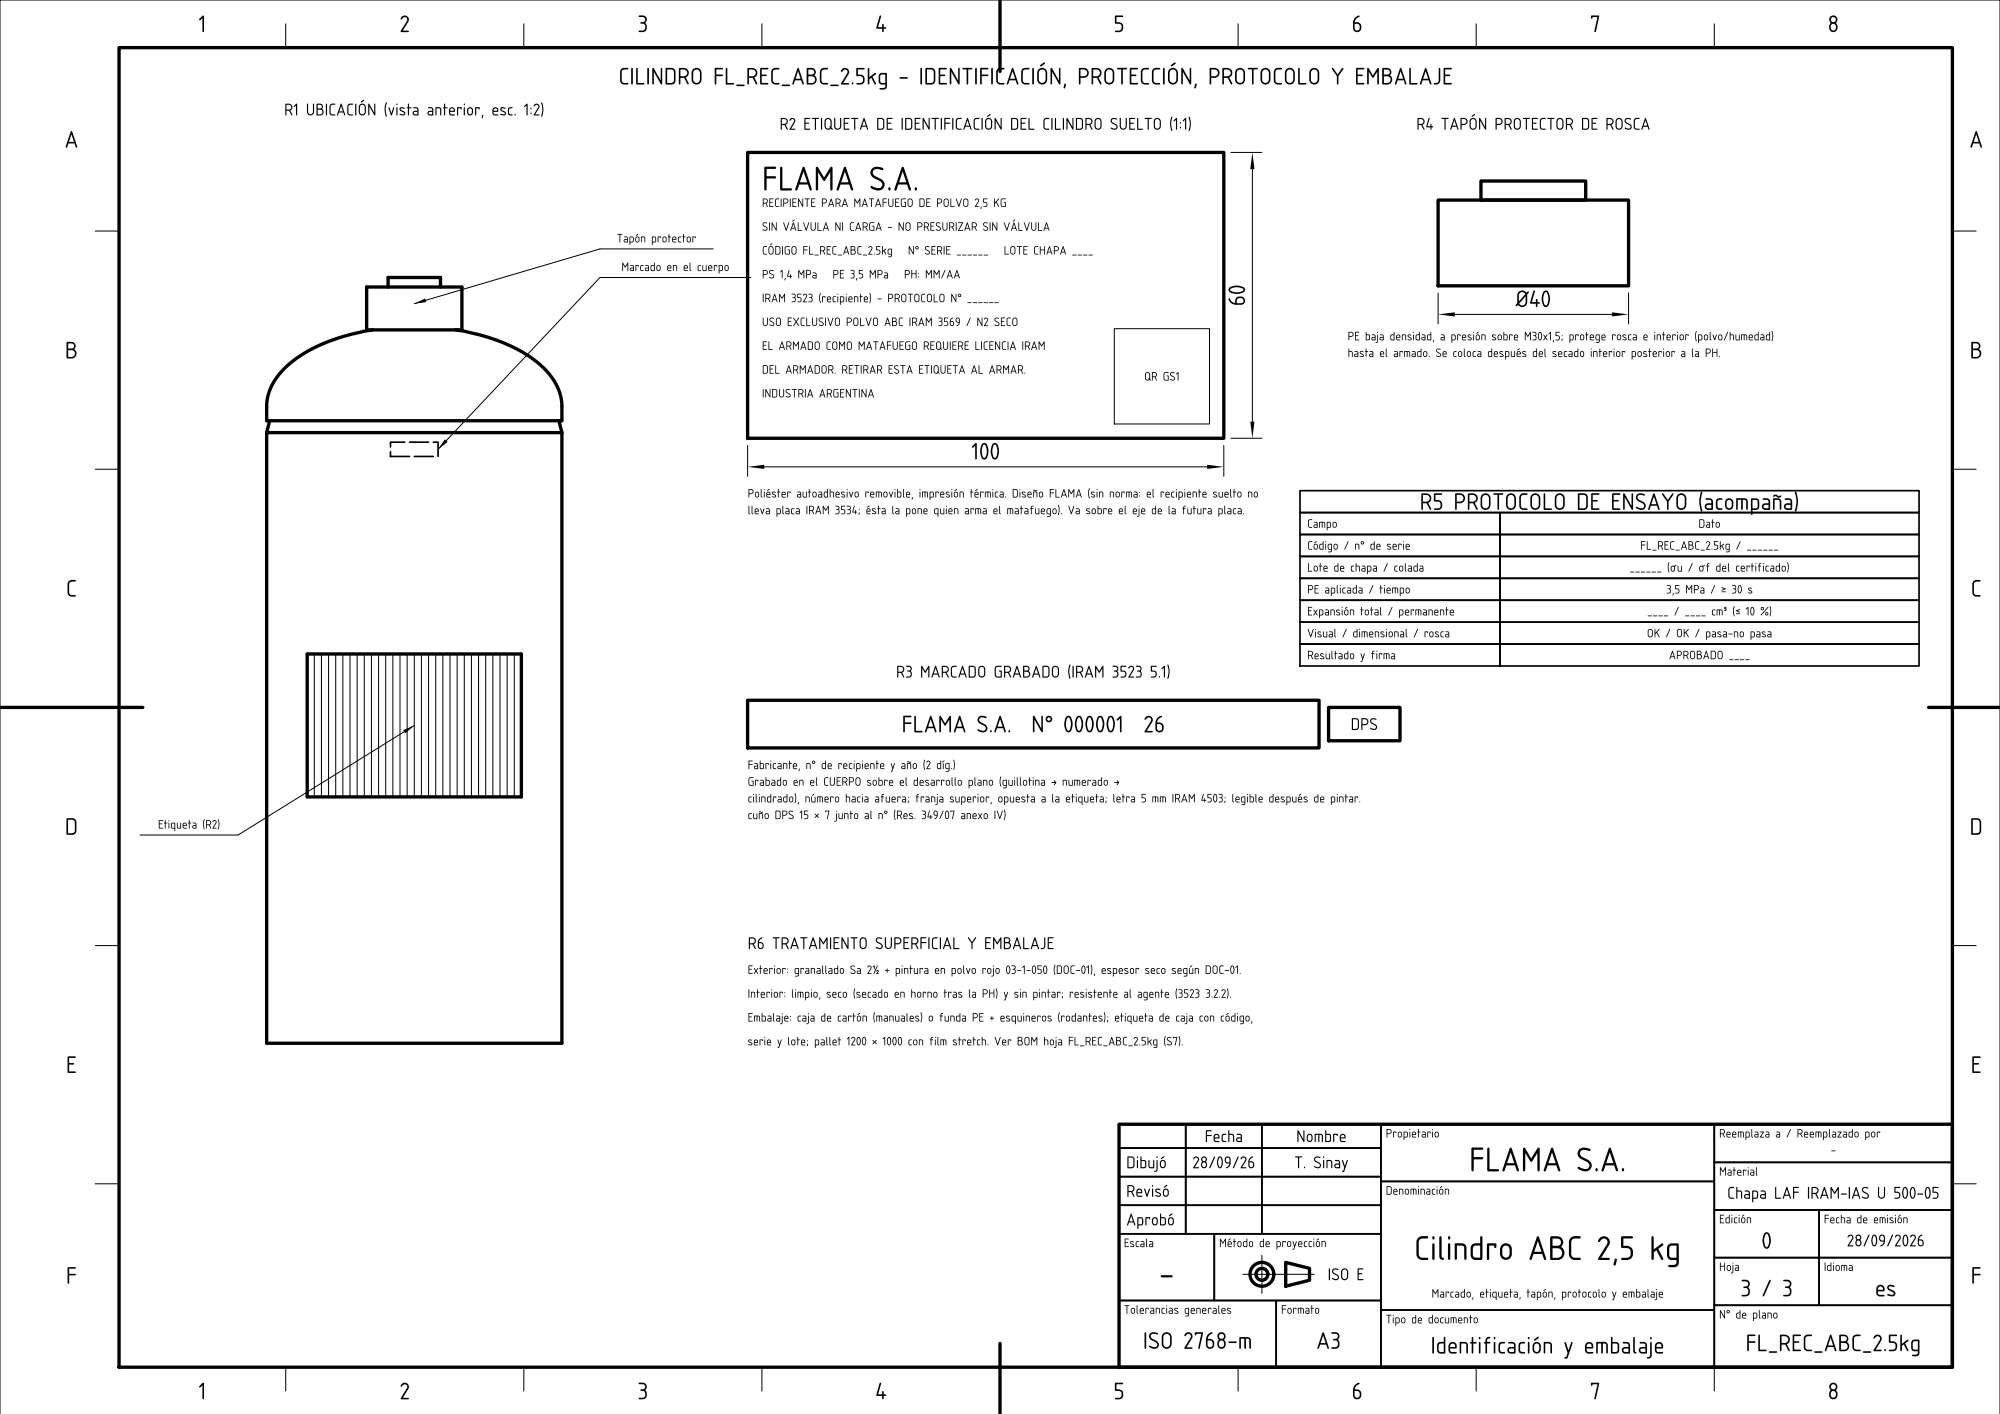
[picture p234: page 7]

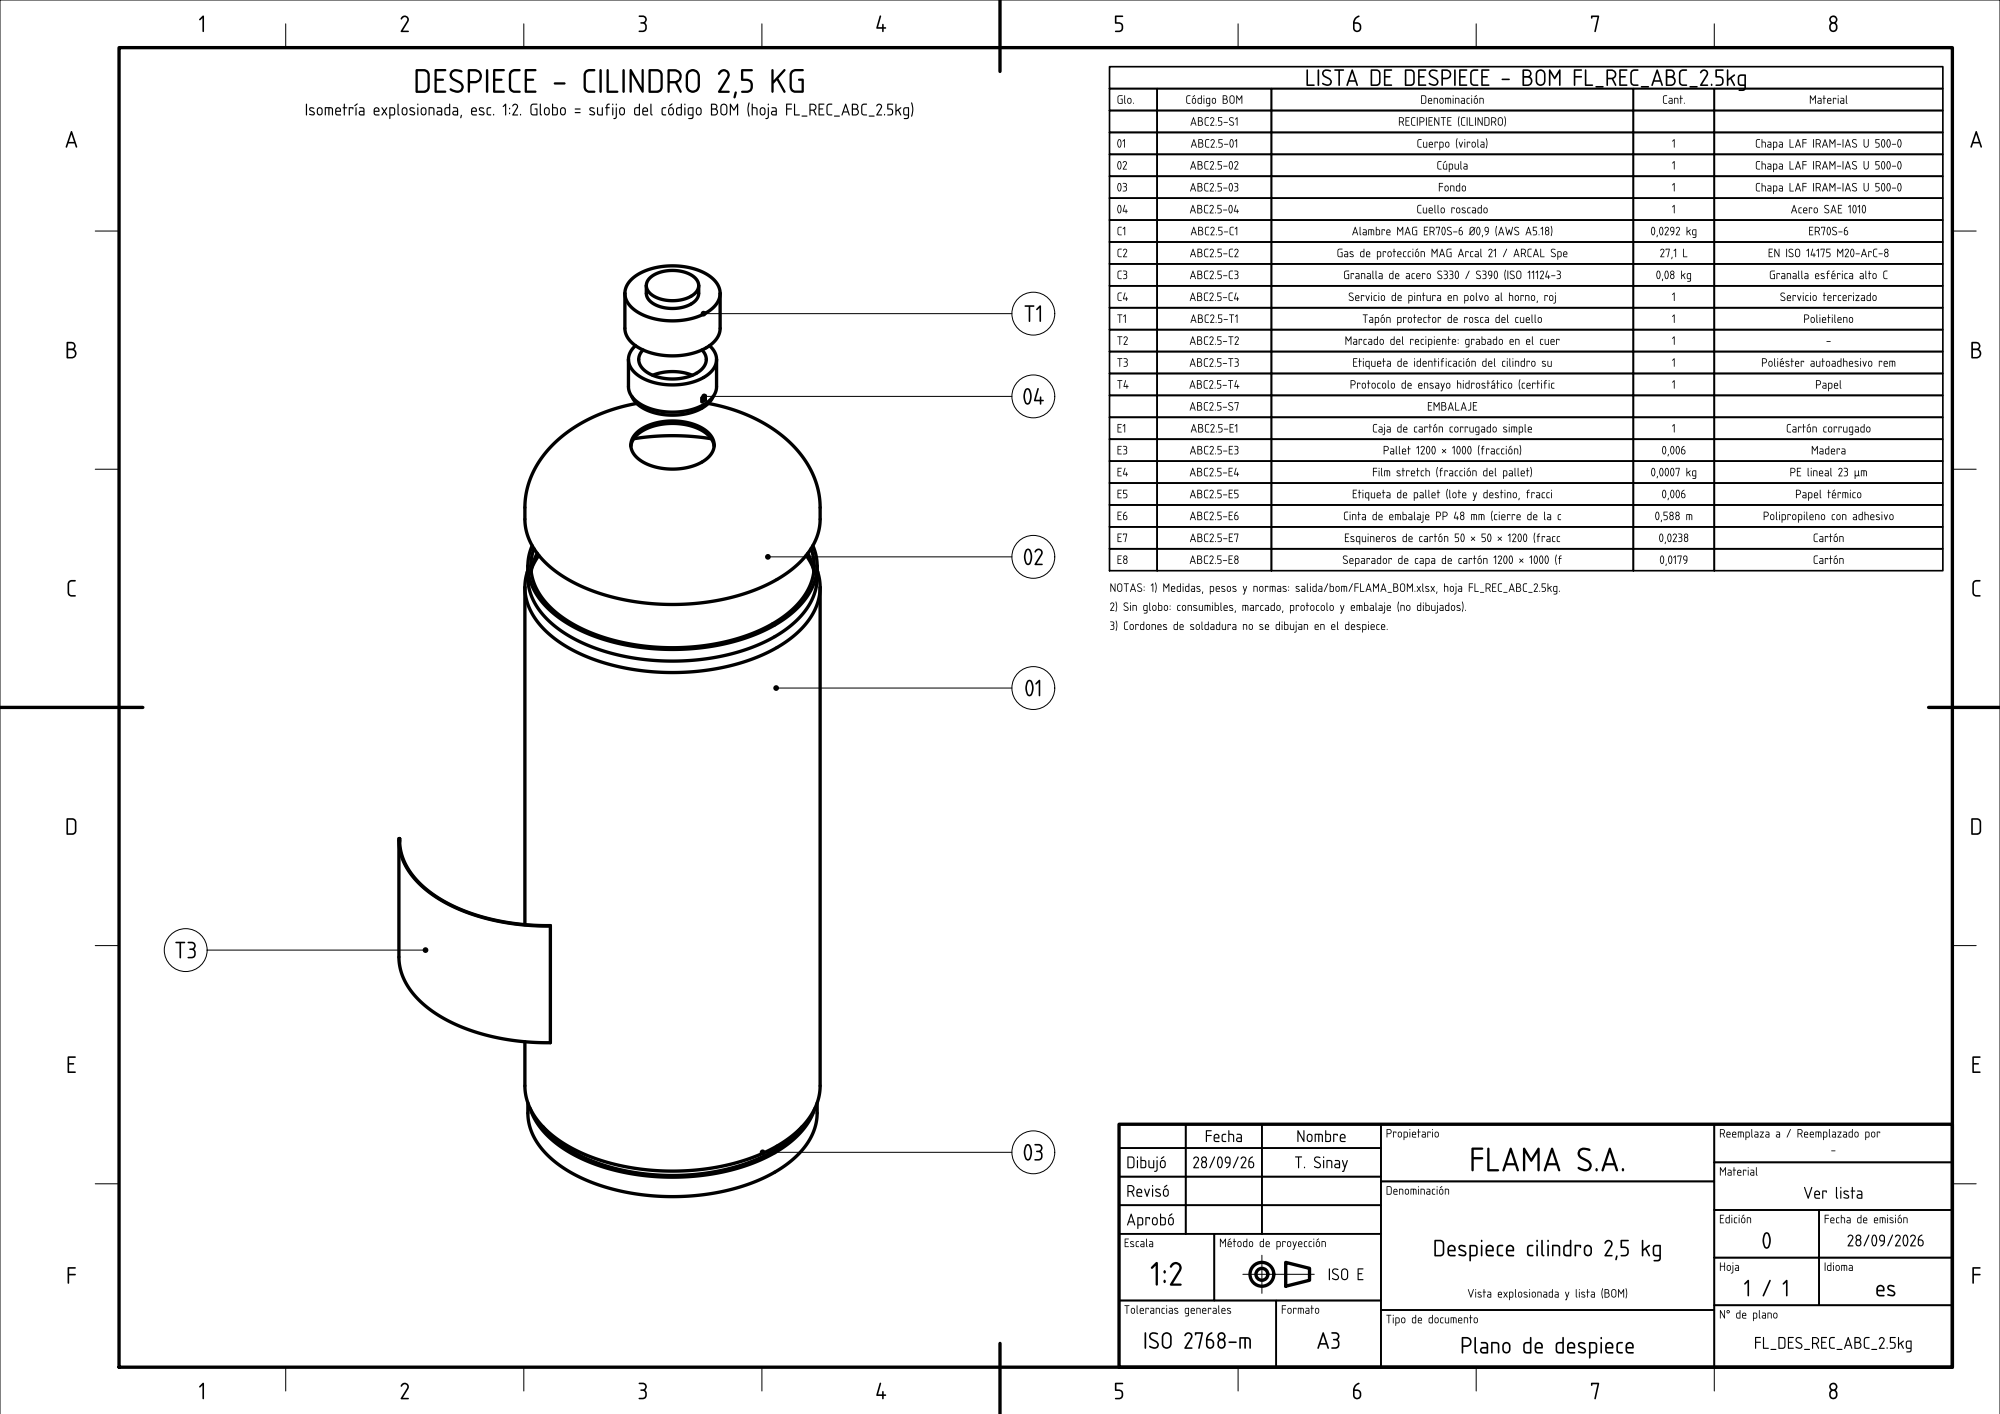
[picture p235: page 8]

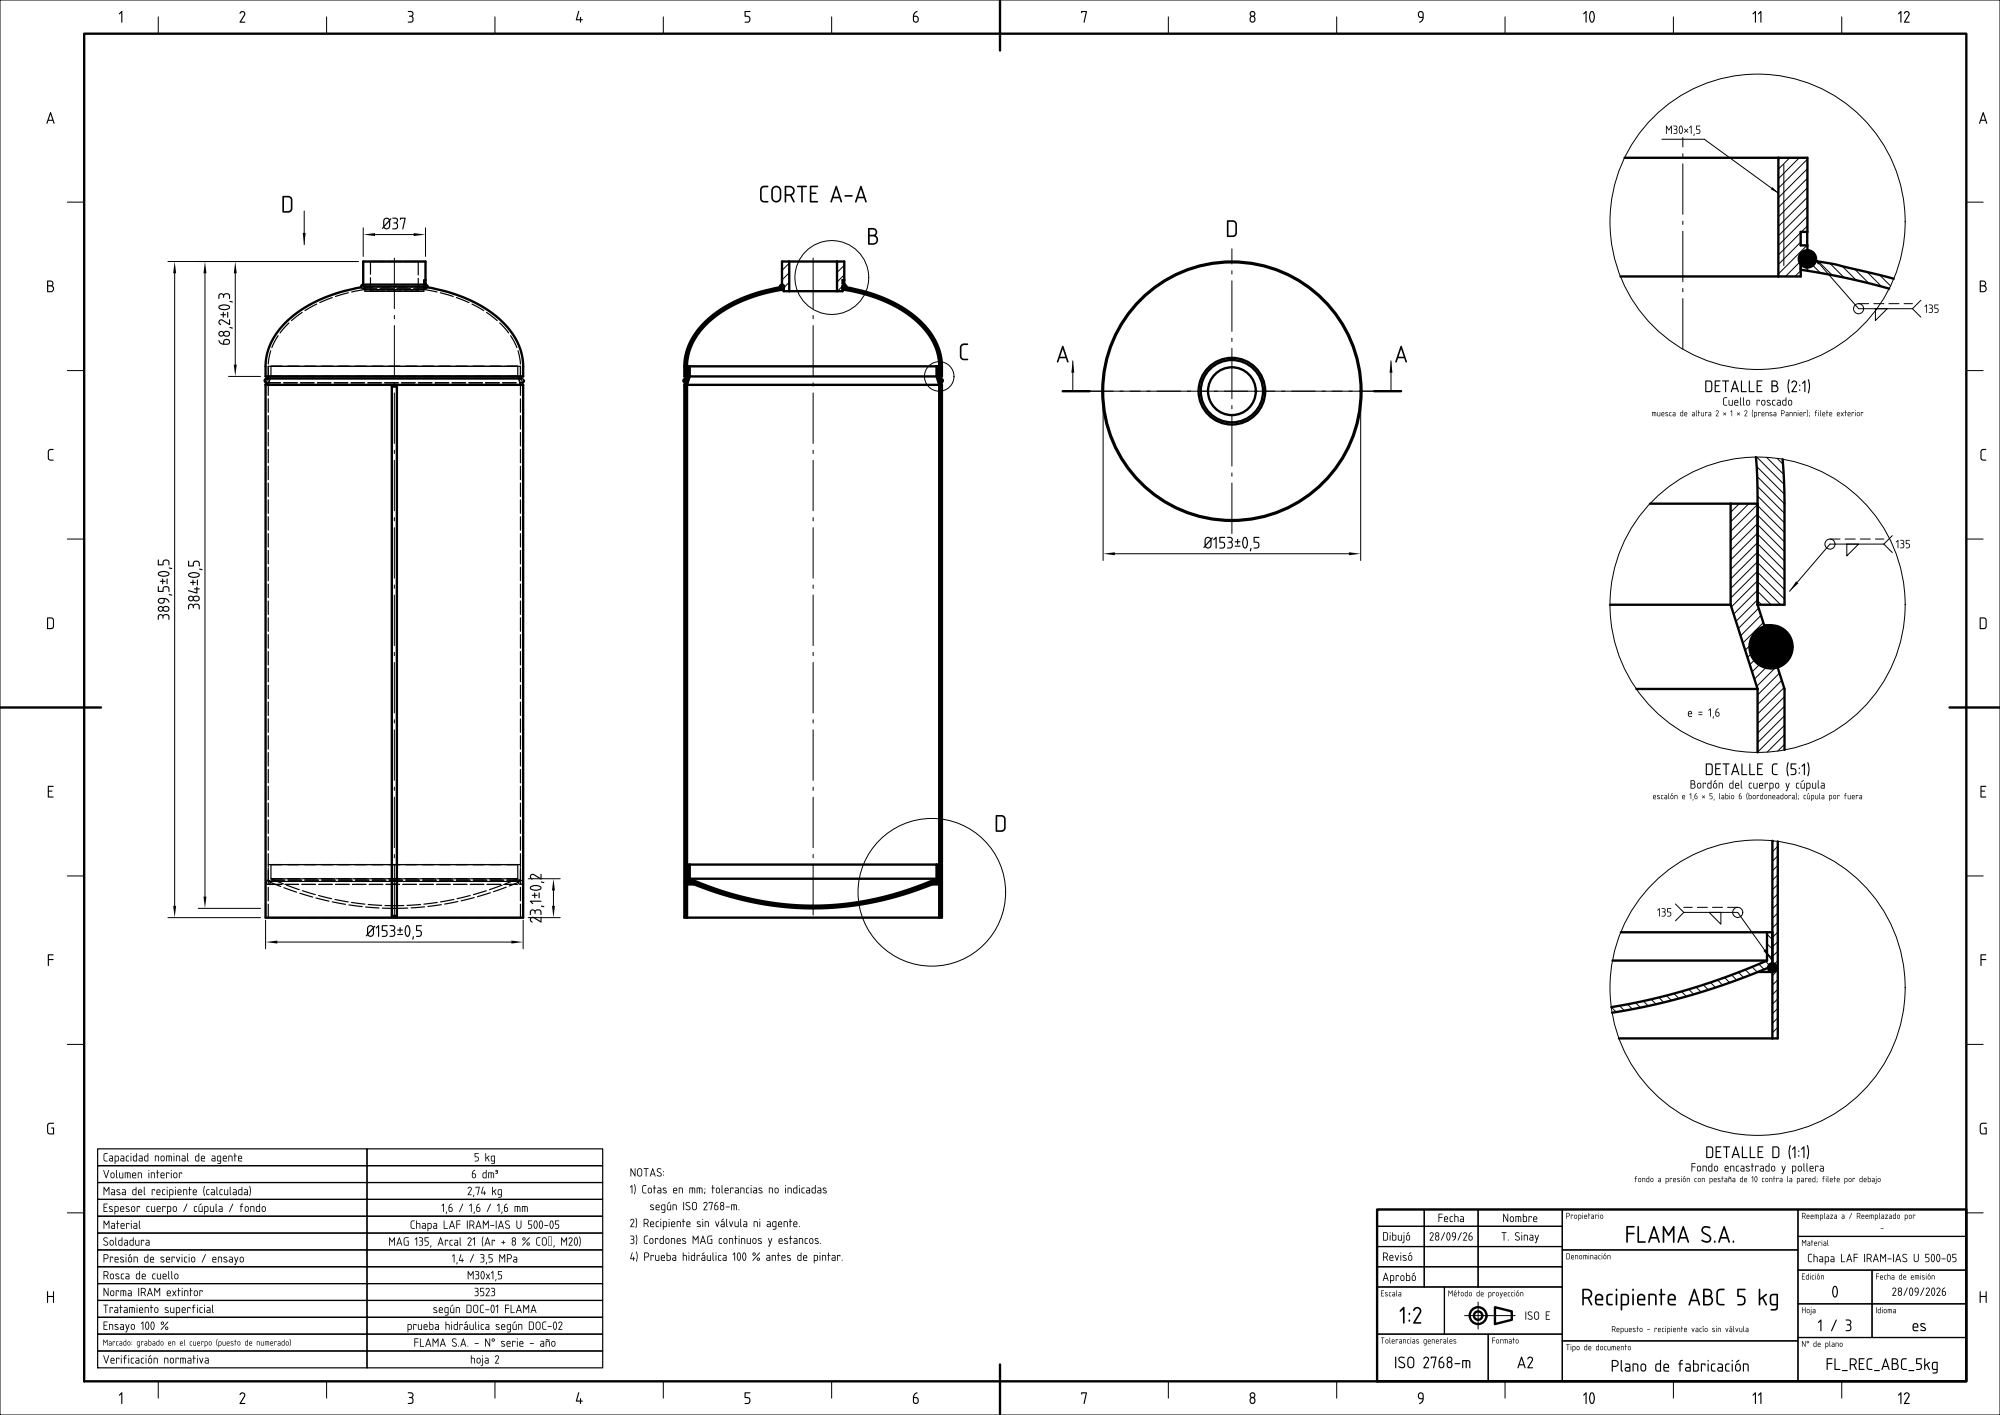
[picture p236: page 9]

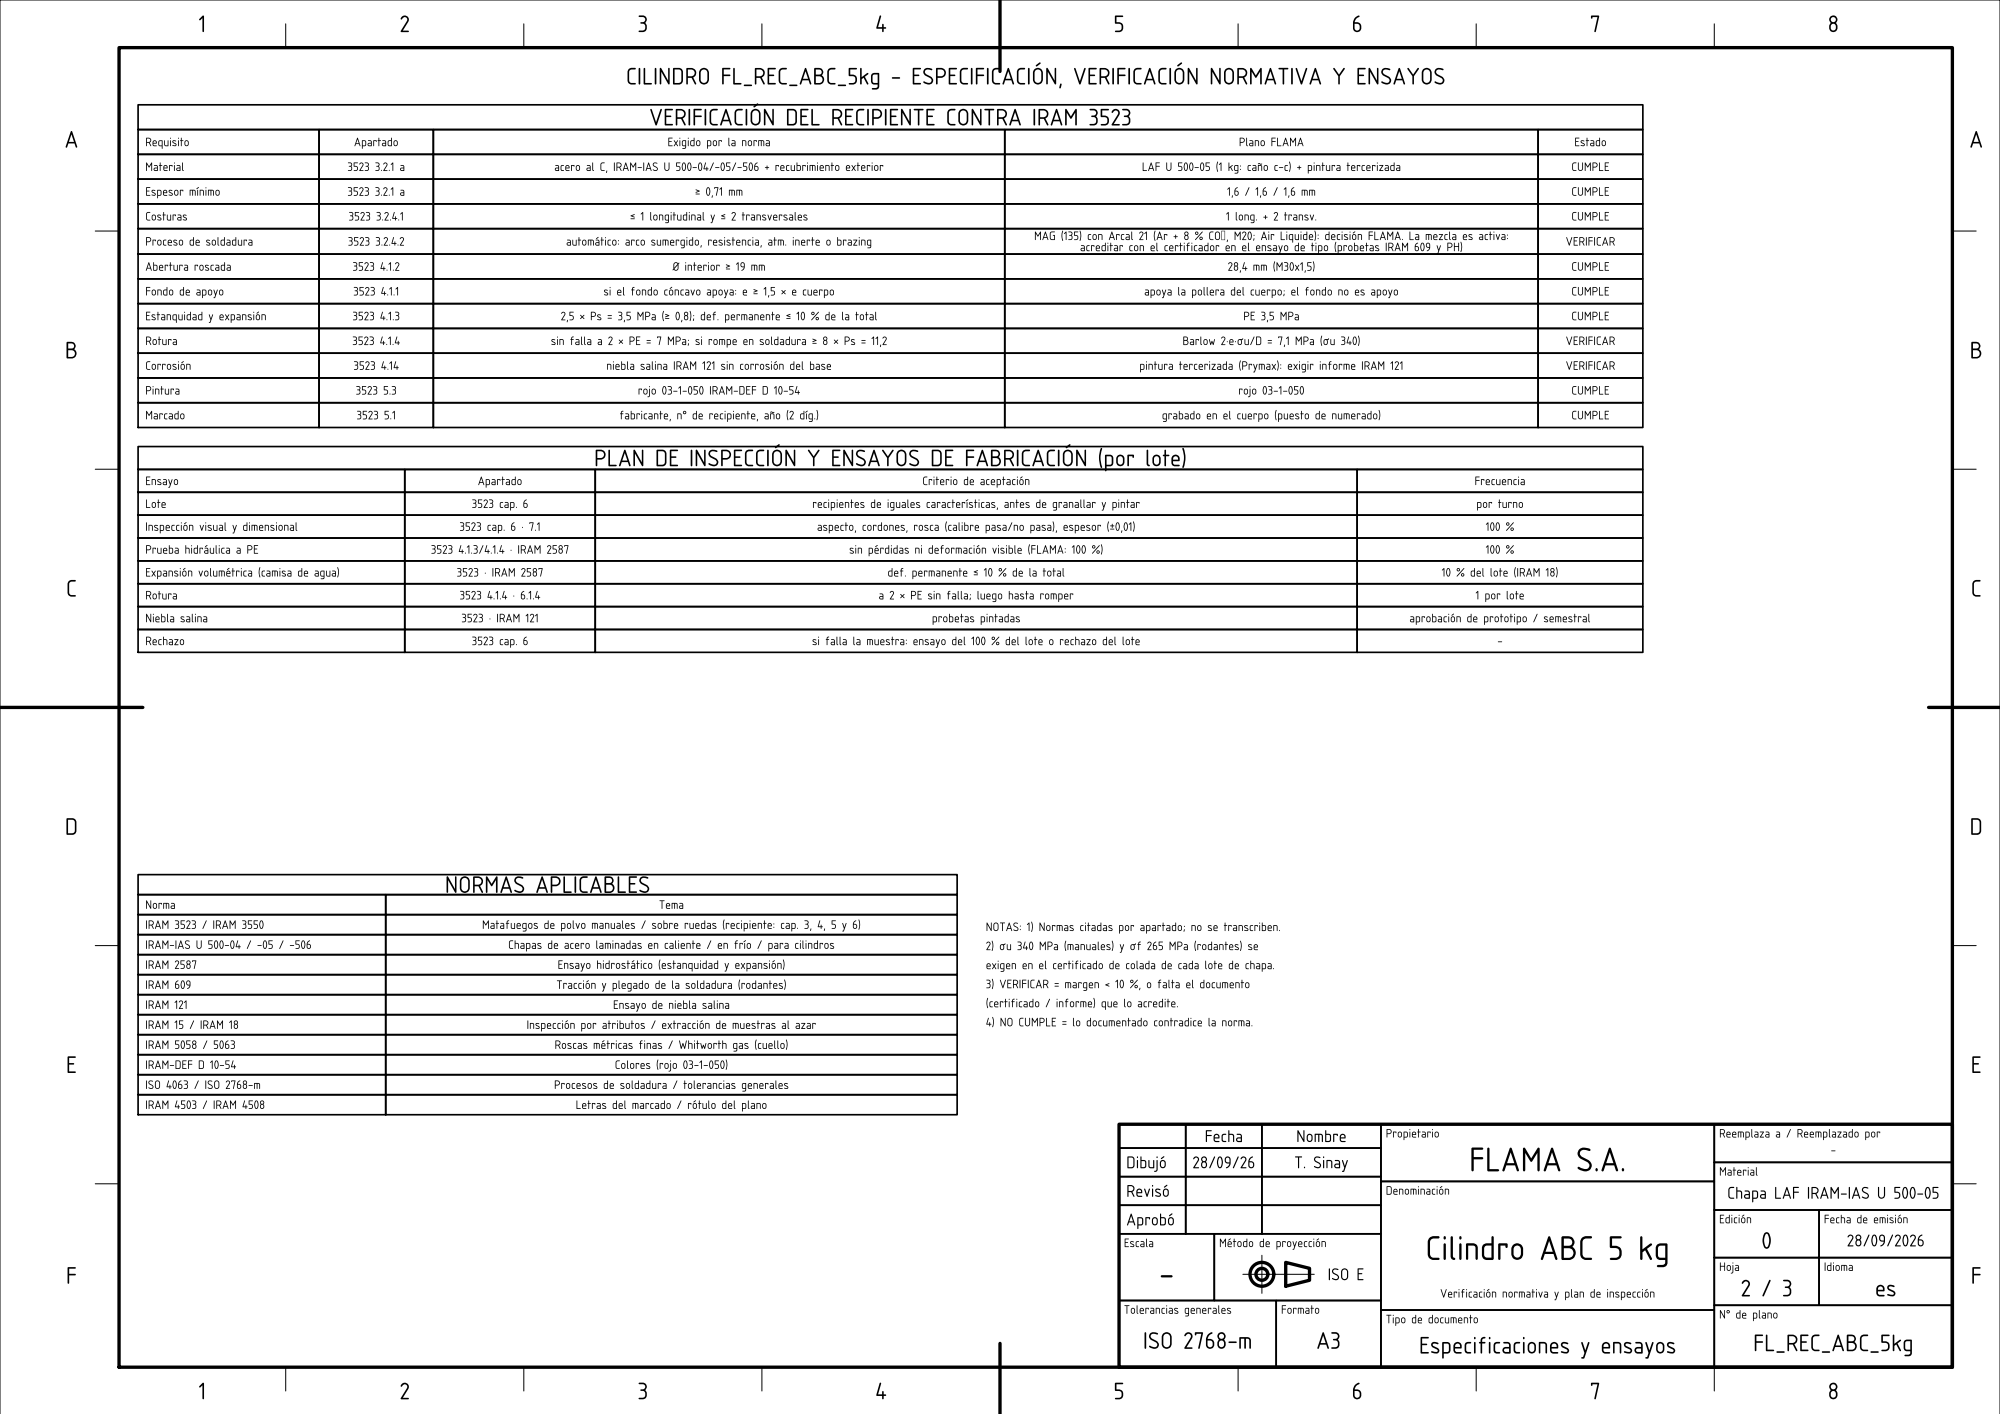
[picture p237: page 10]

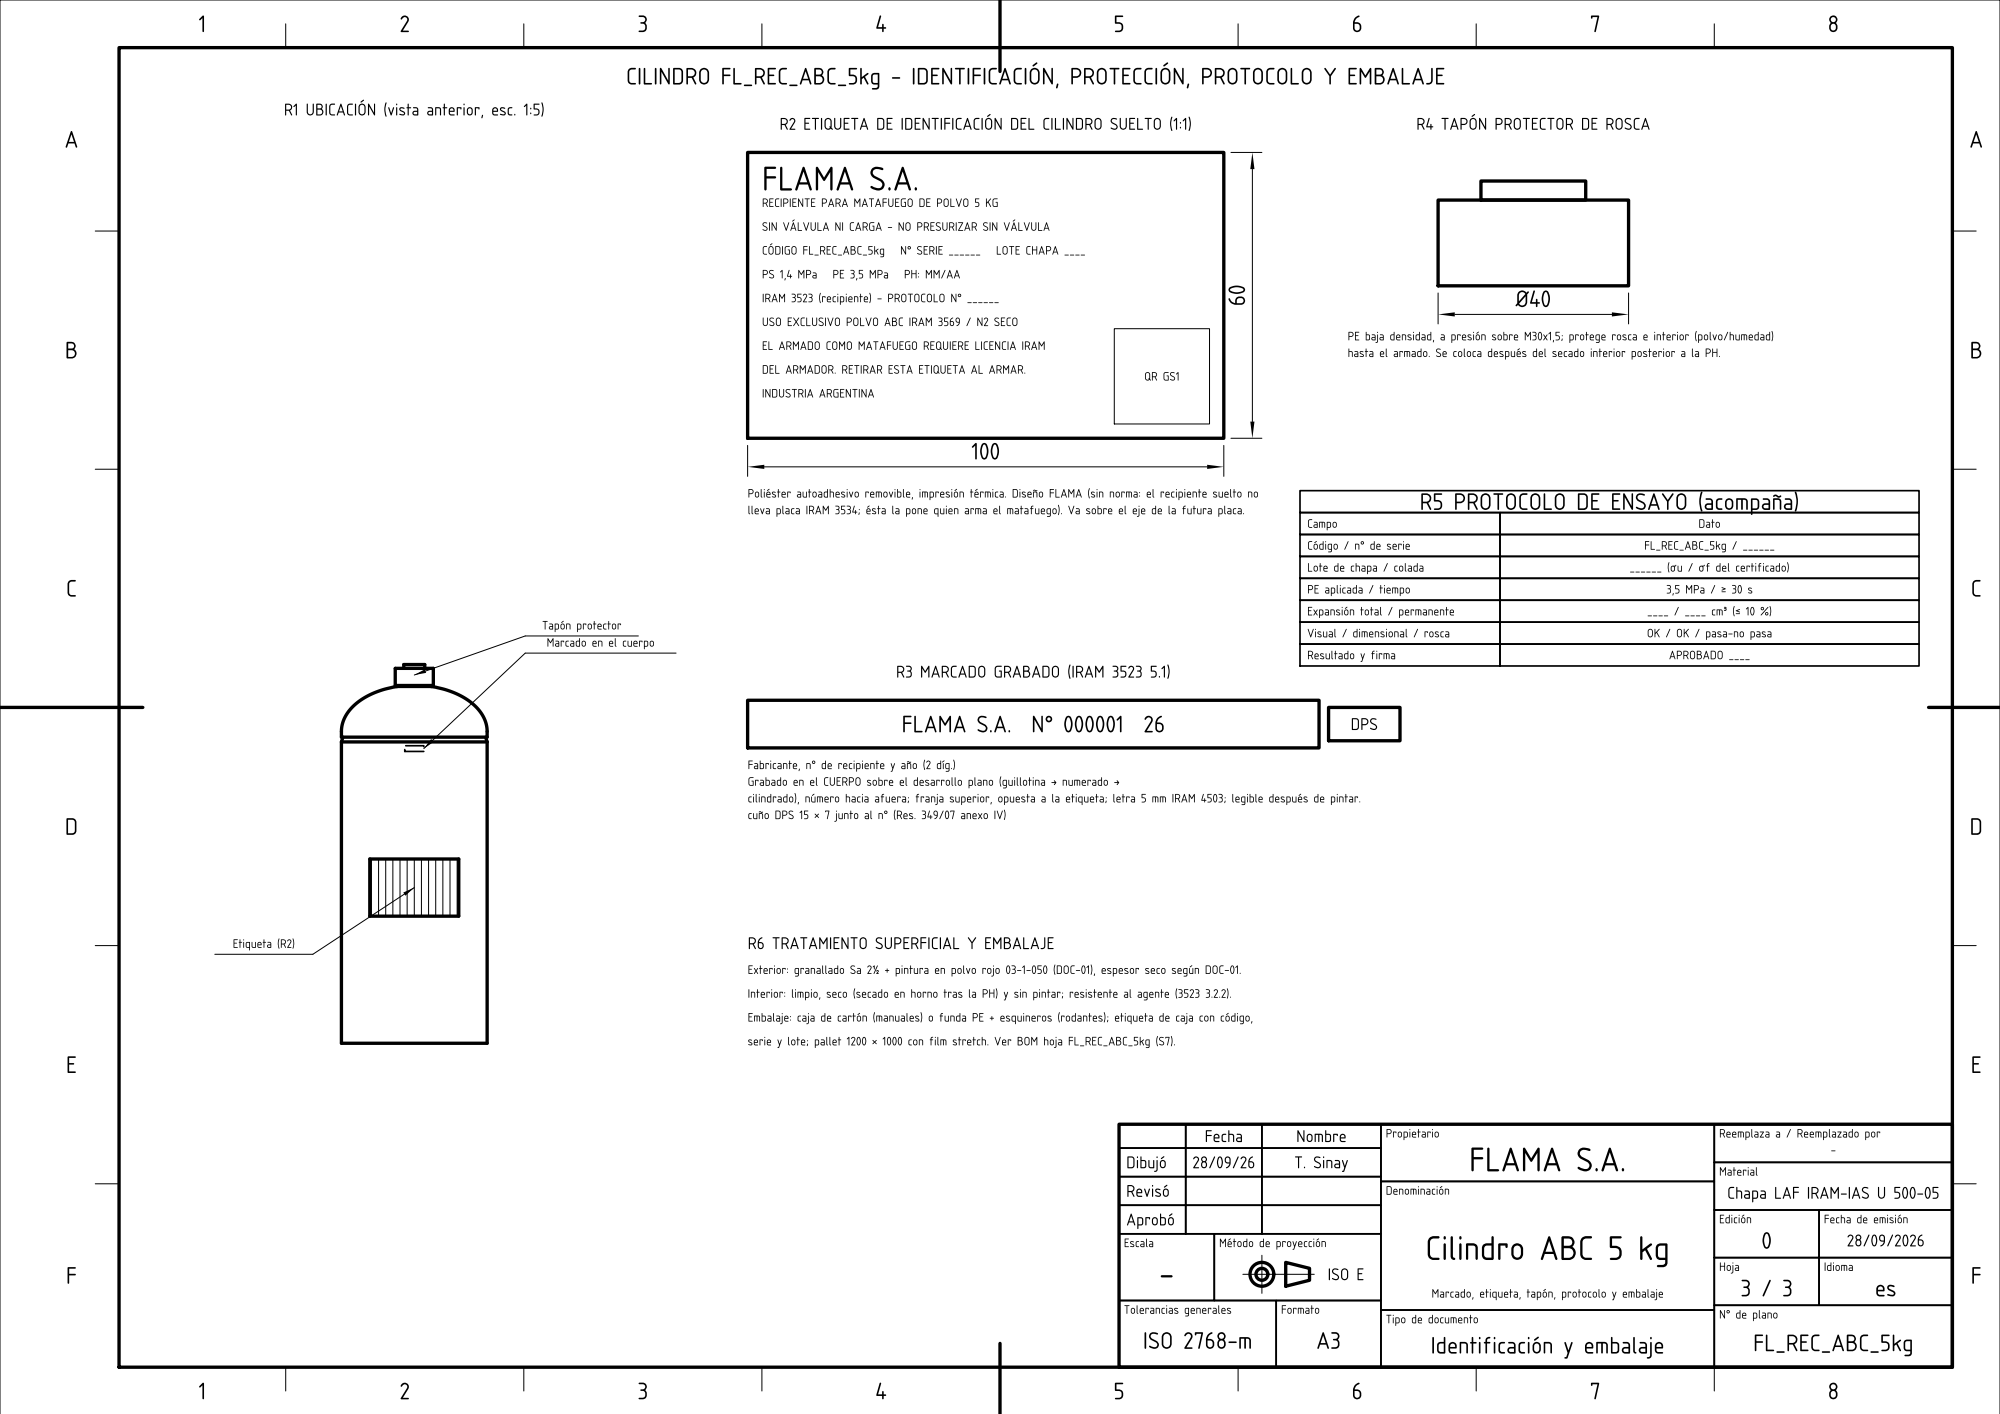
[picture p238: page 11]

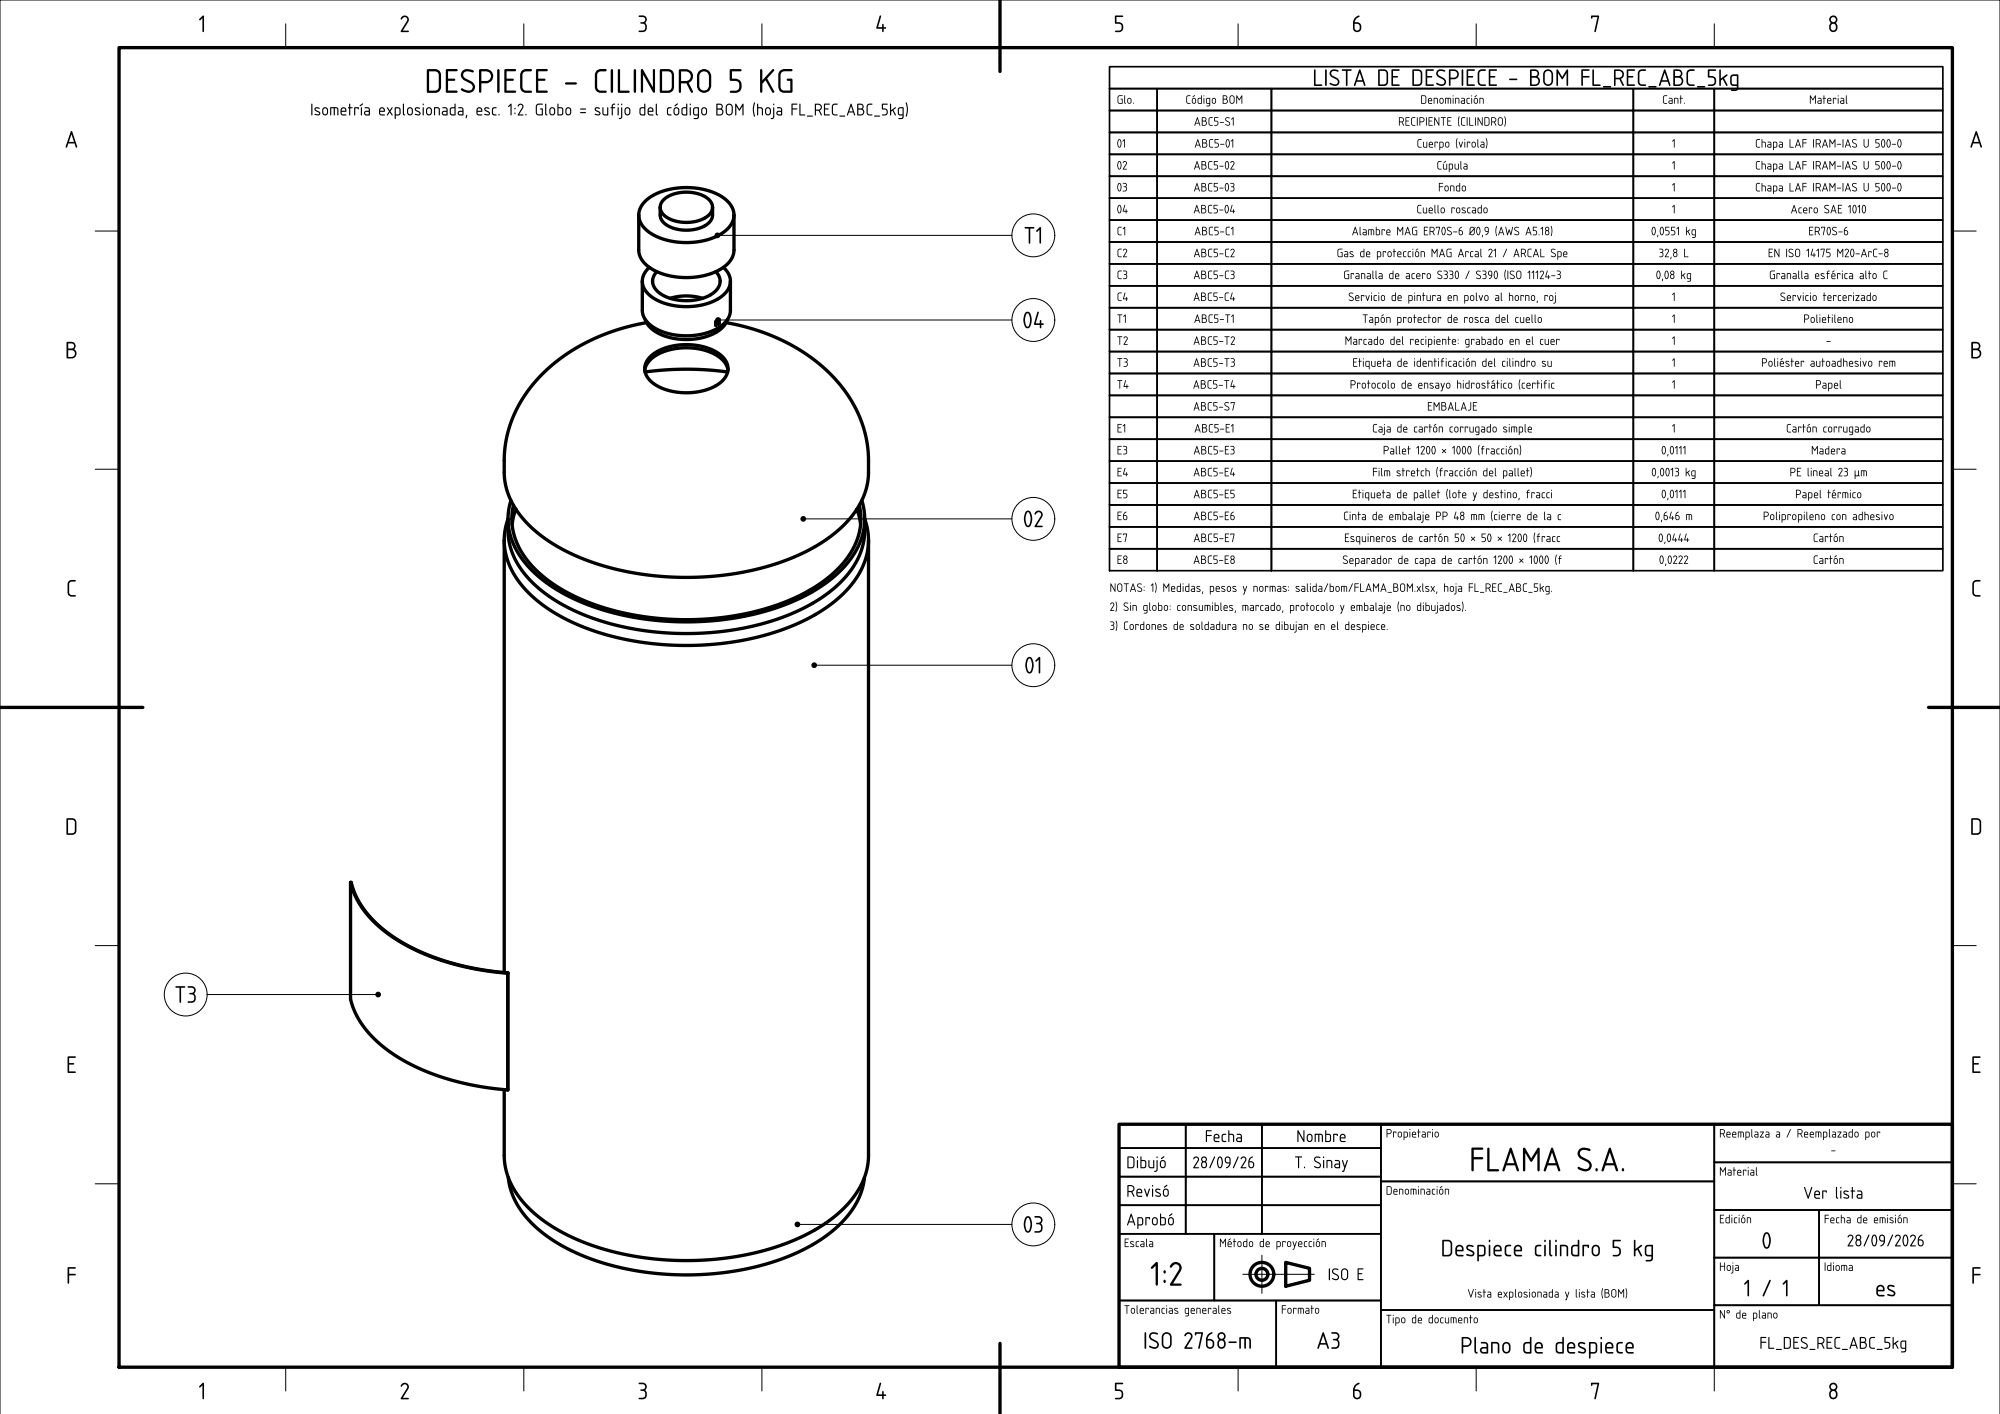
[picture p239: page 12]

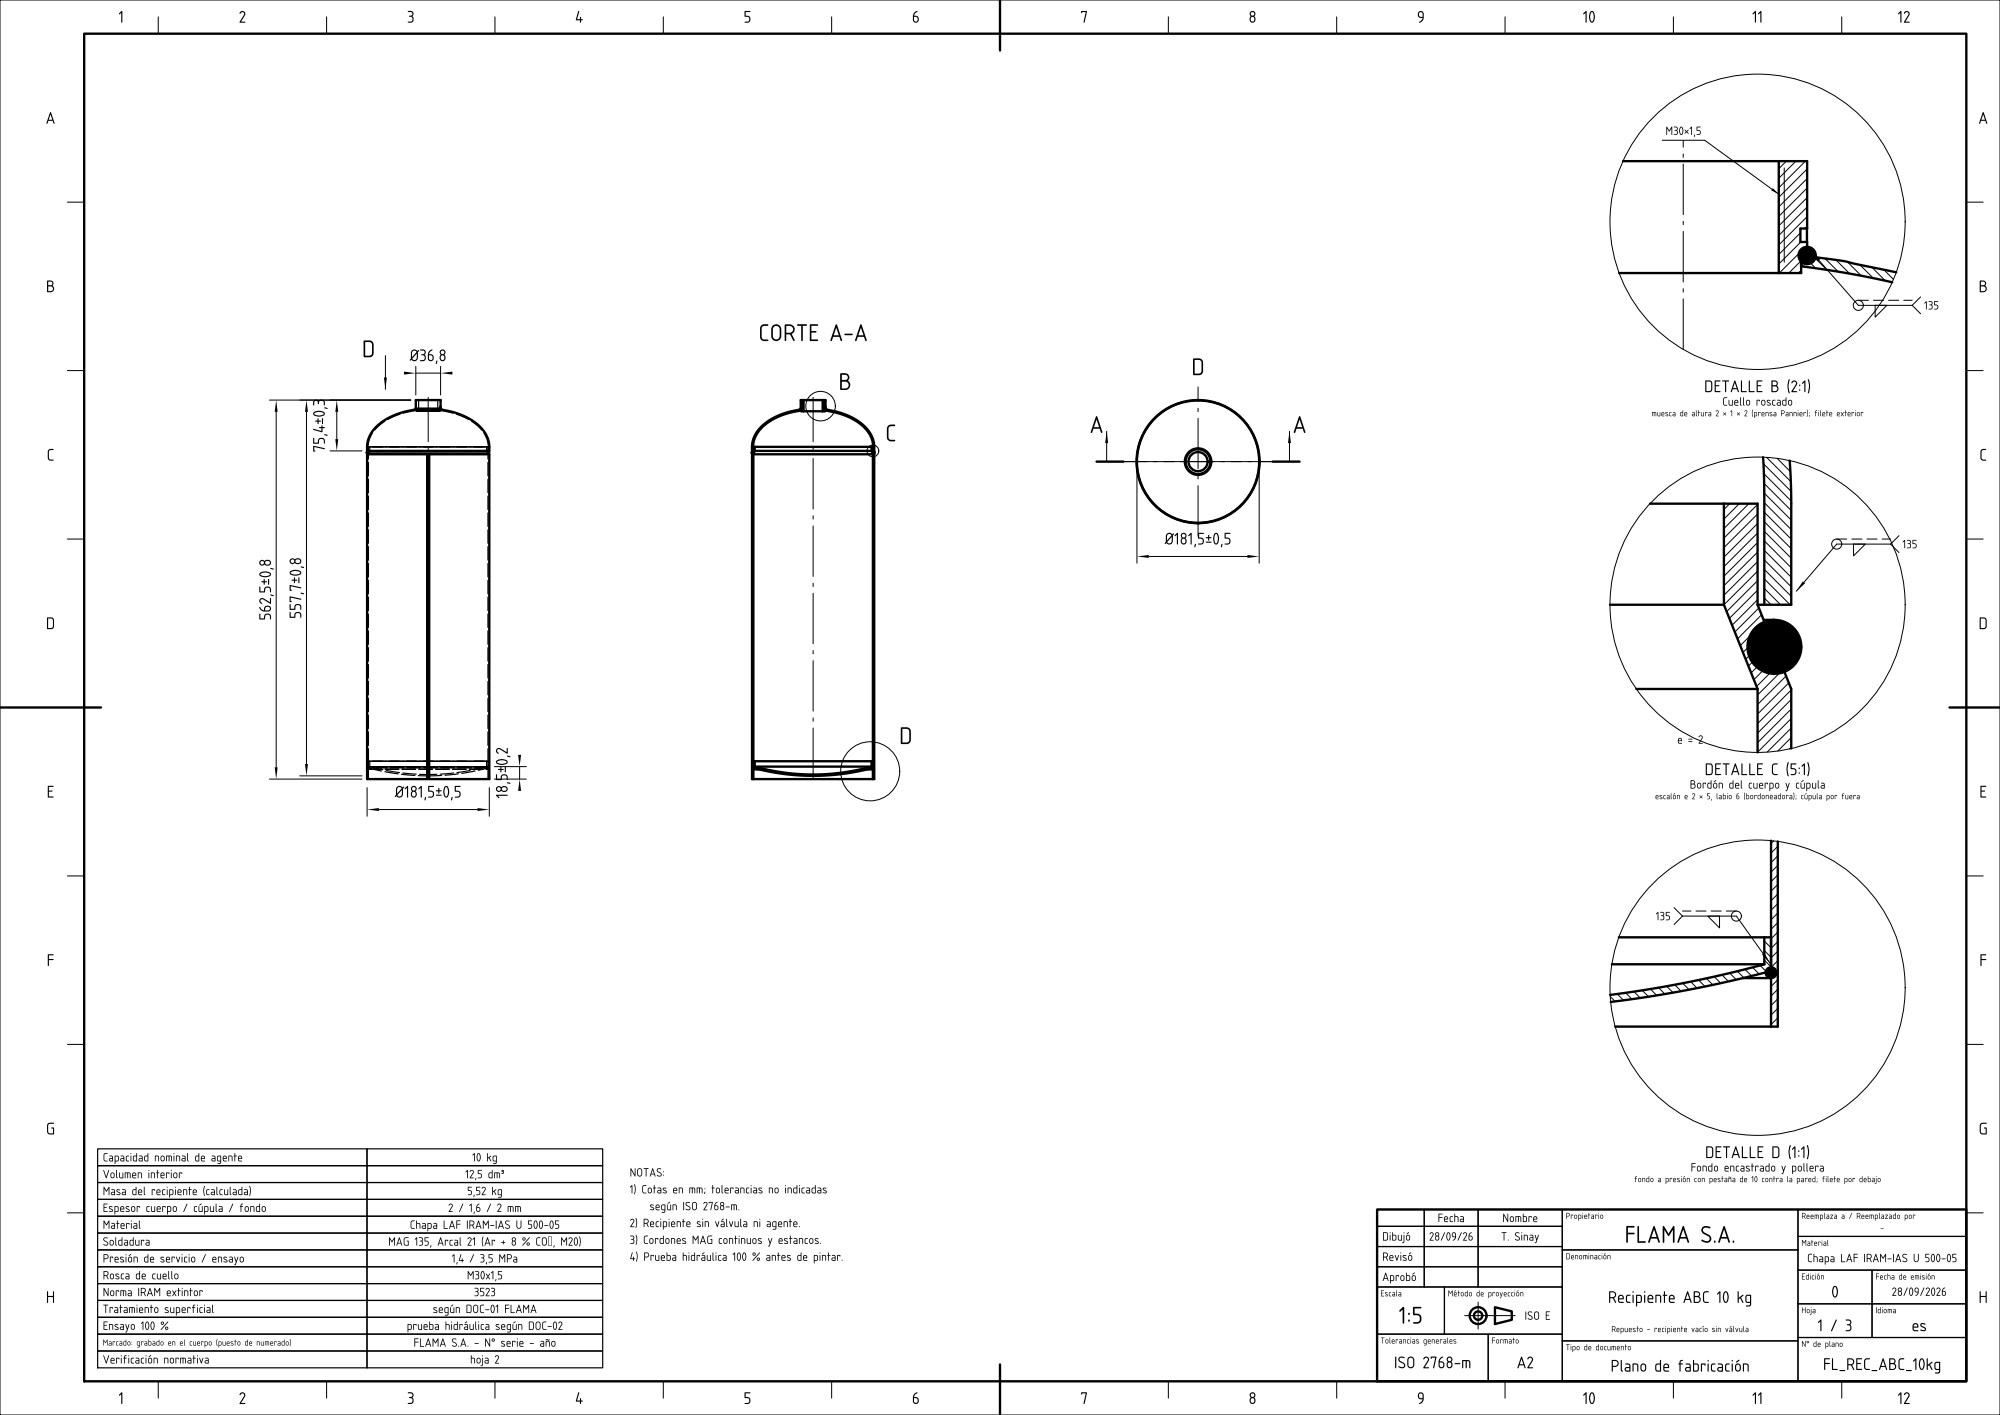
[picture p240: page 13]

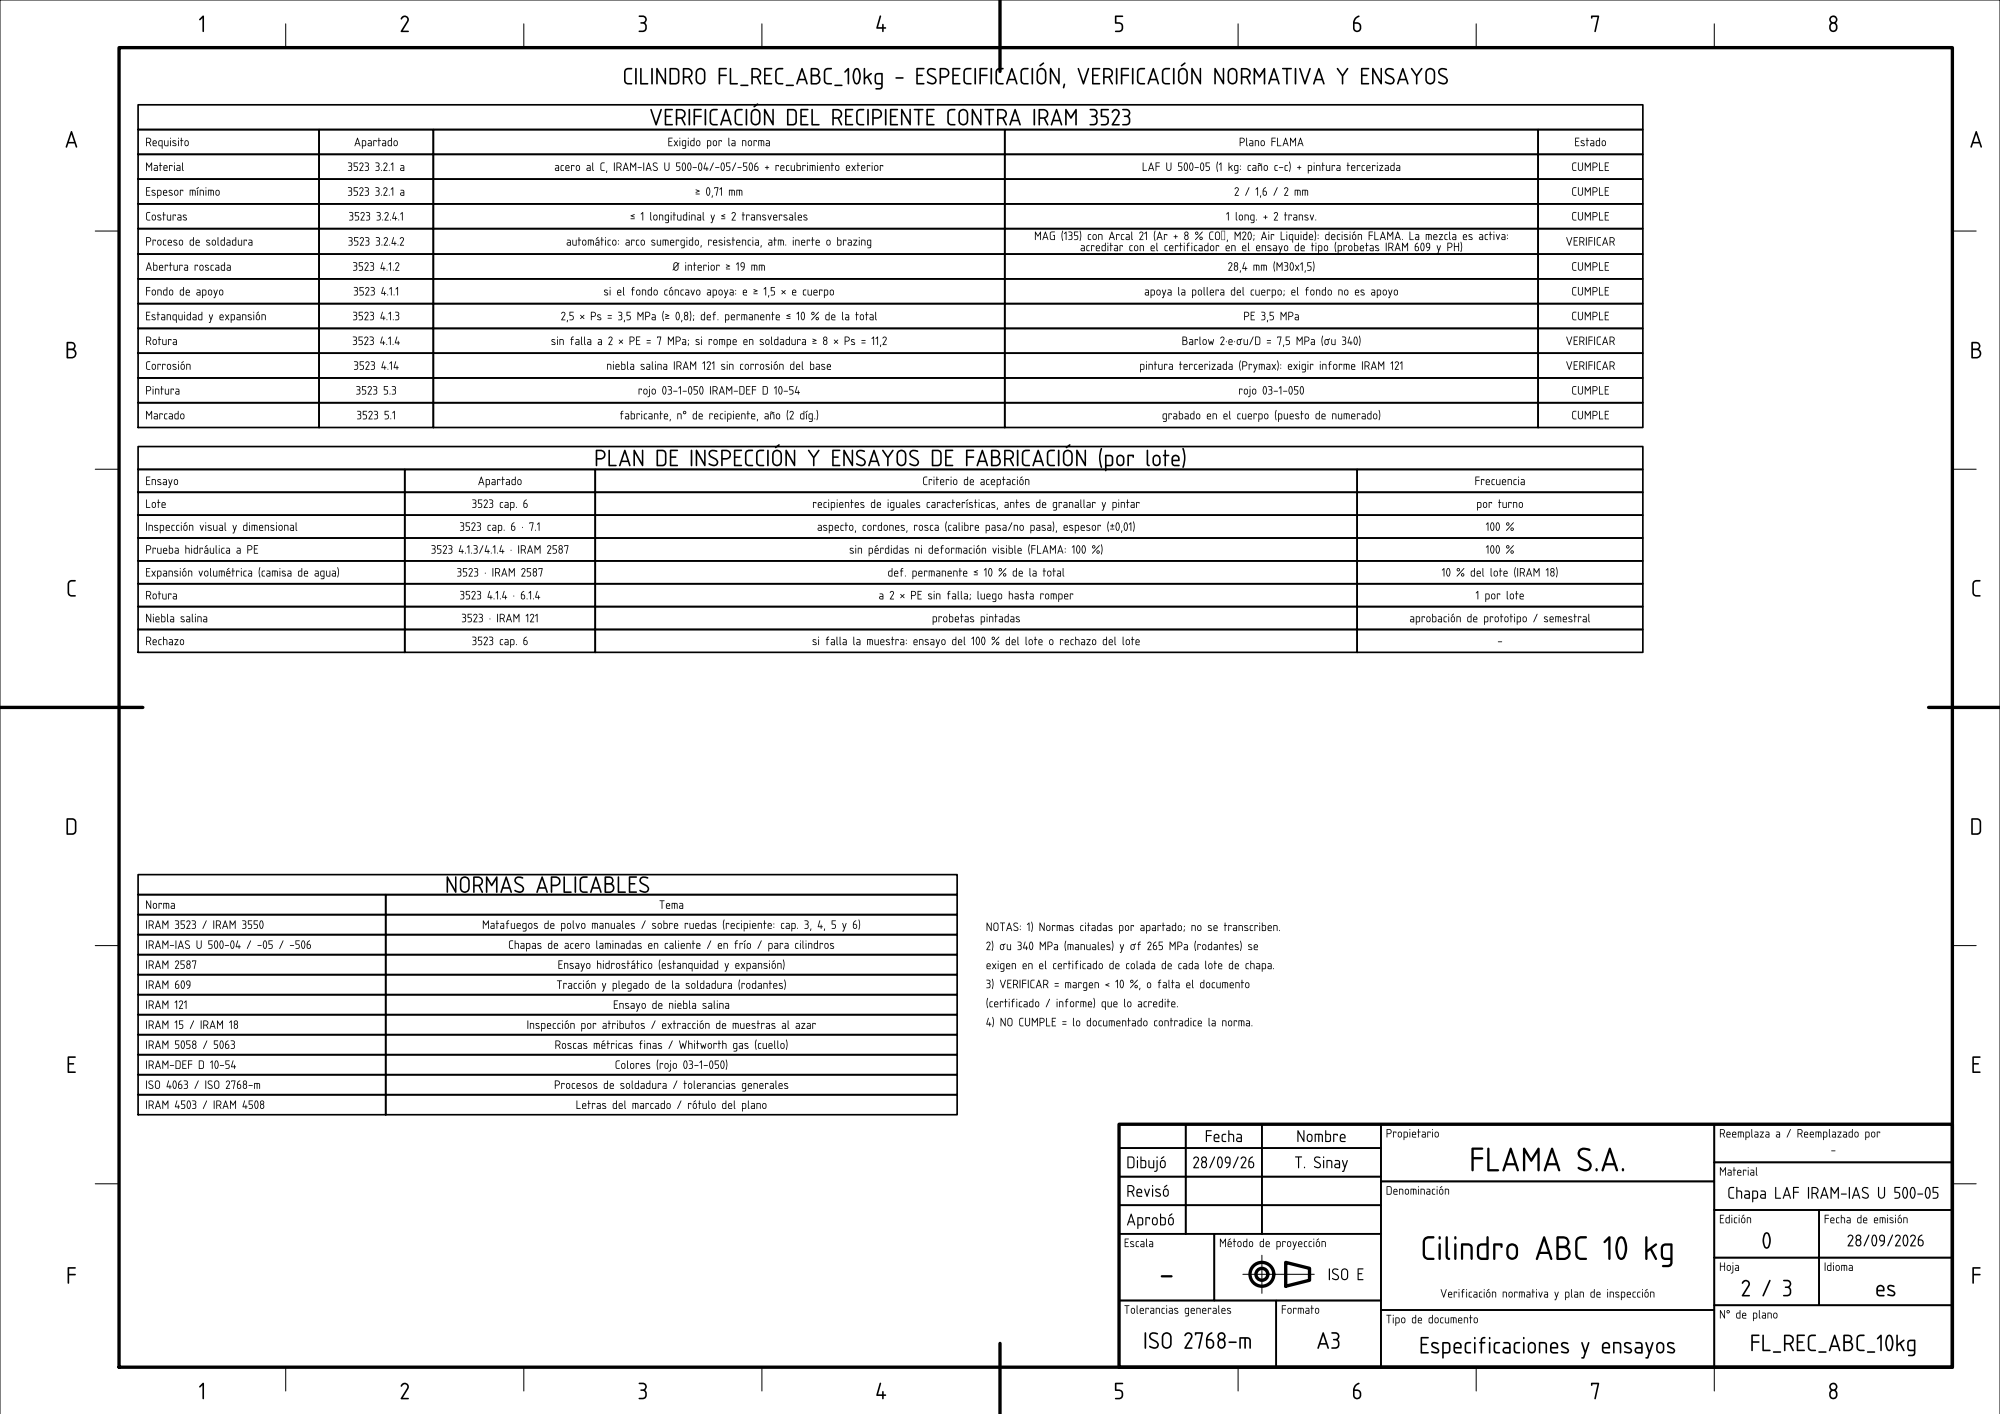
[picture p241: page 14]

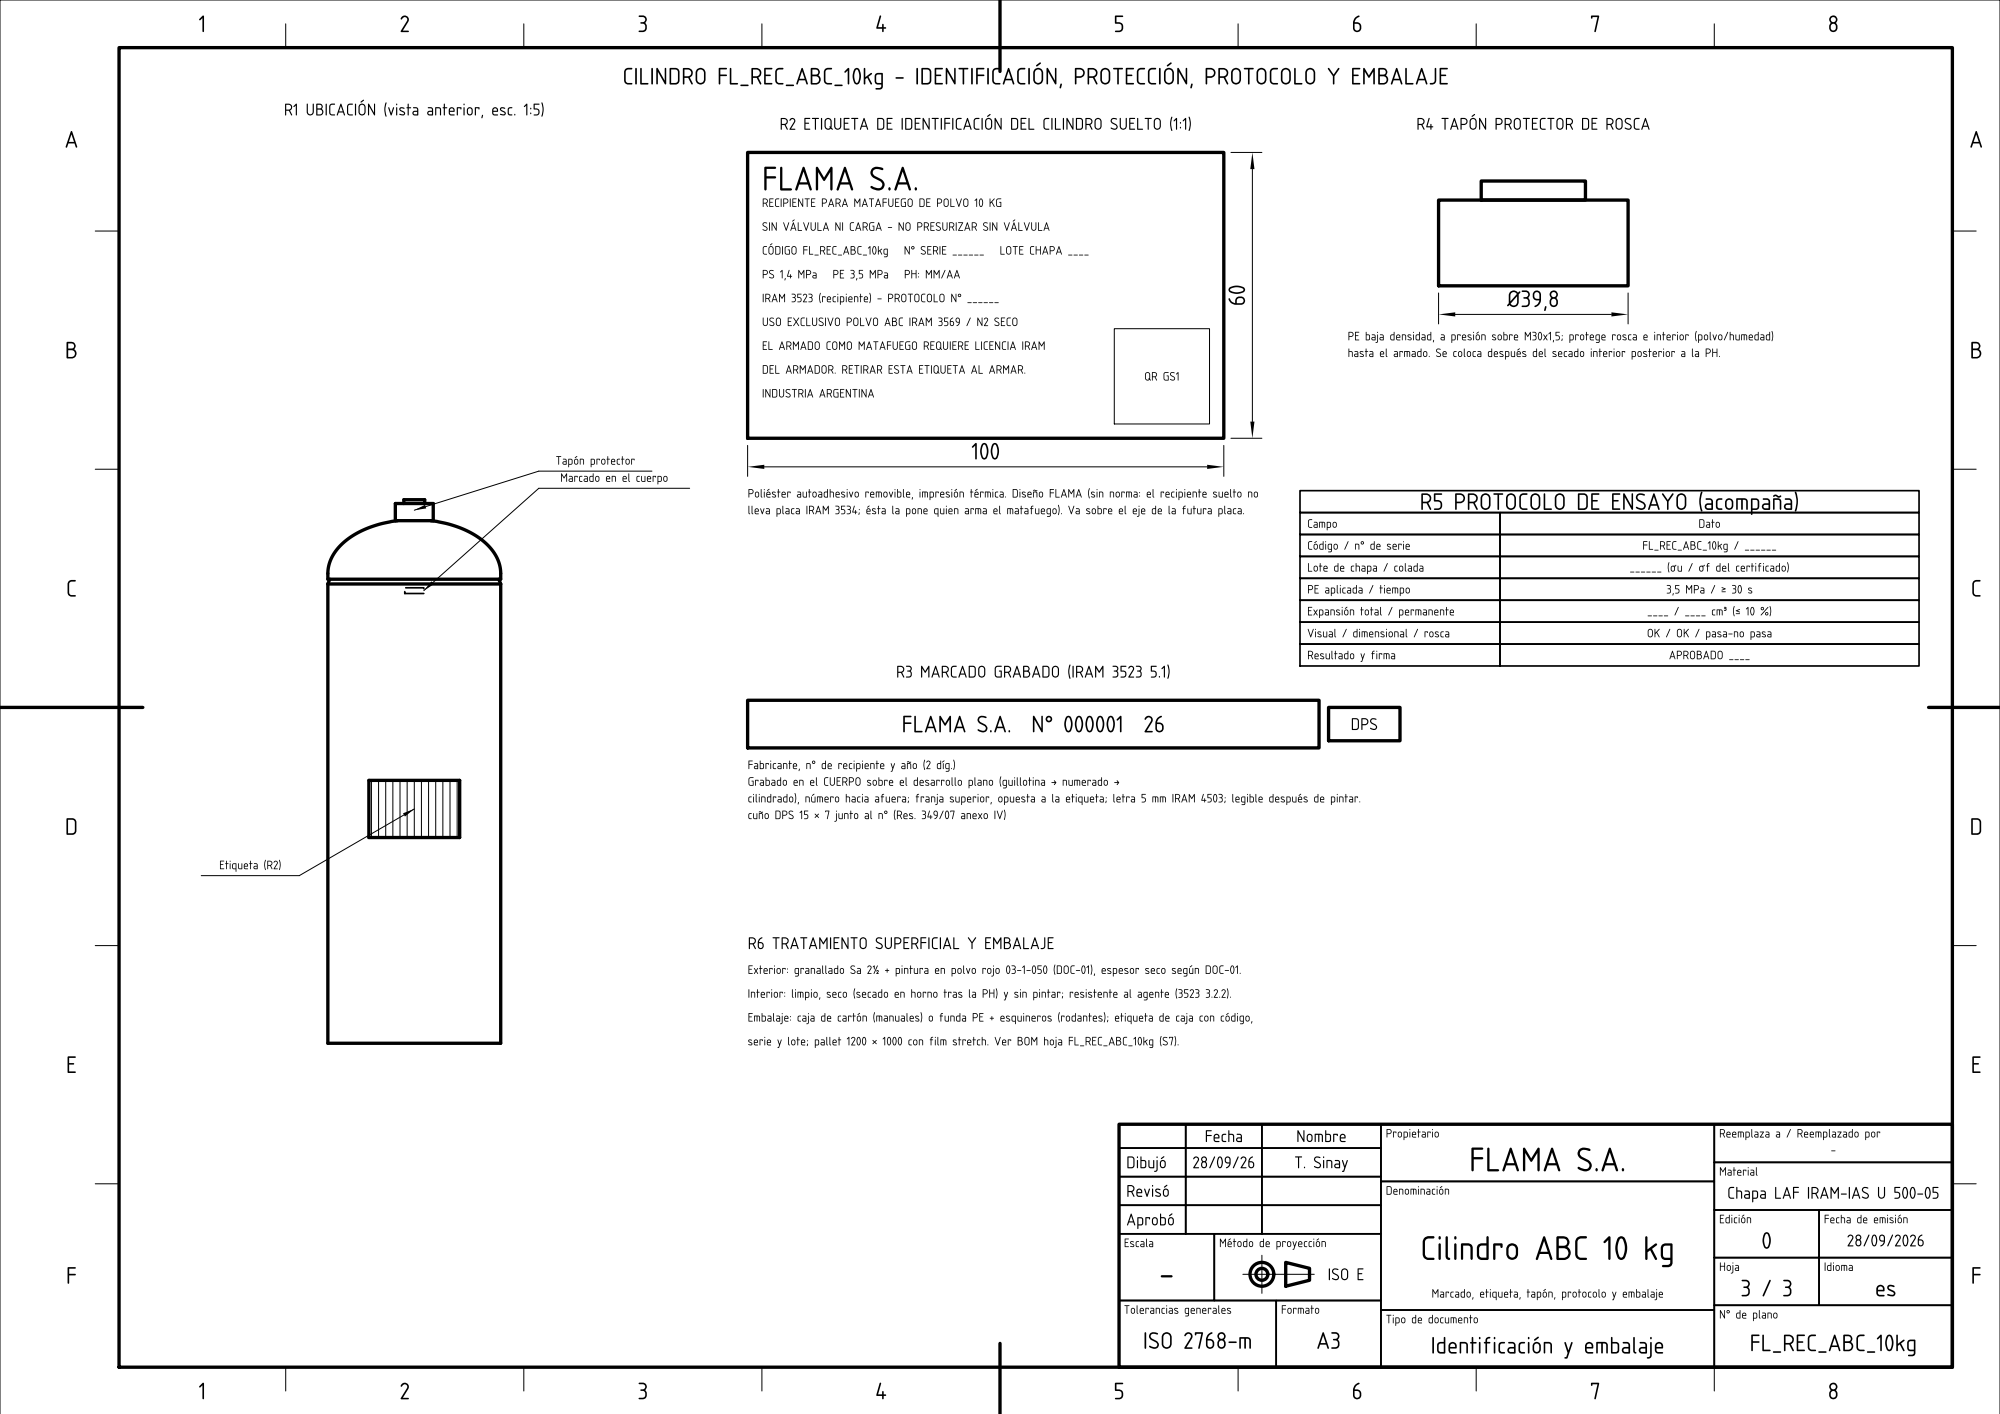
[picture p242: page 15]

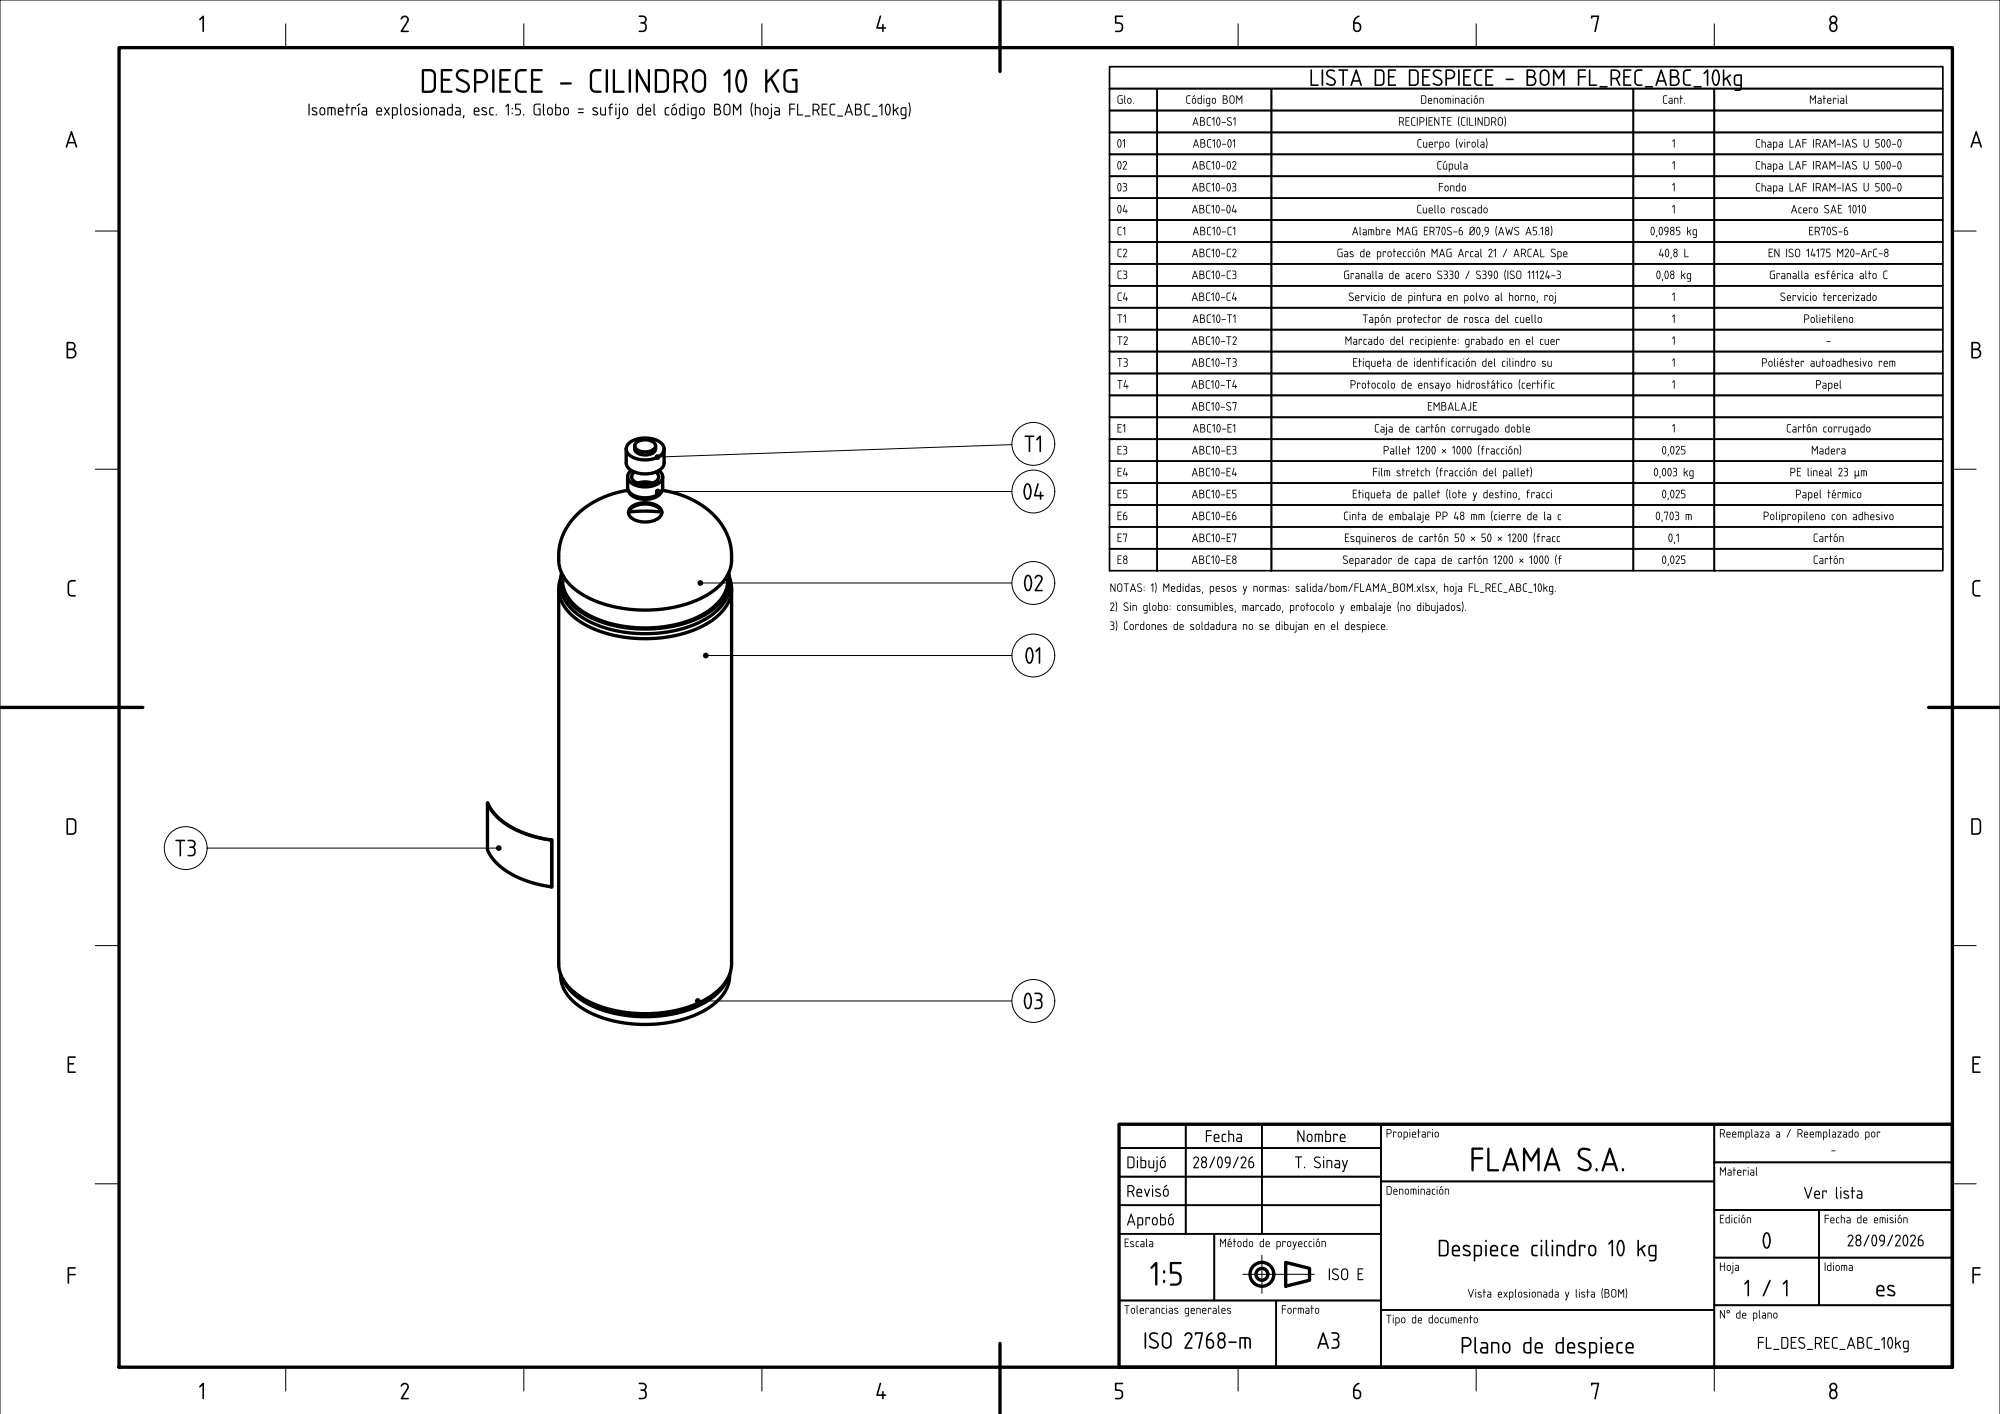
[picture p243: page 16]

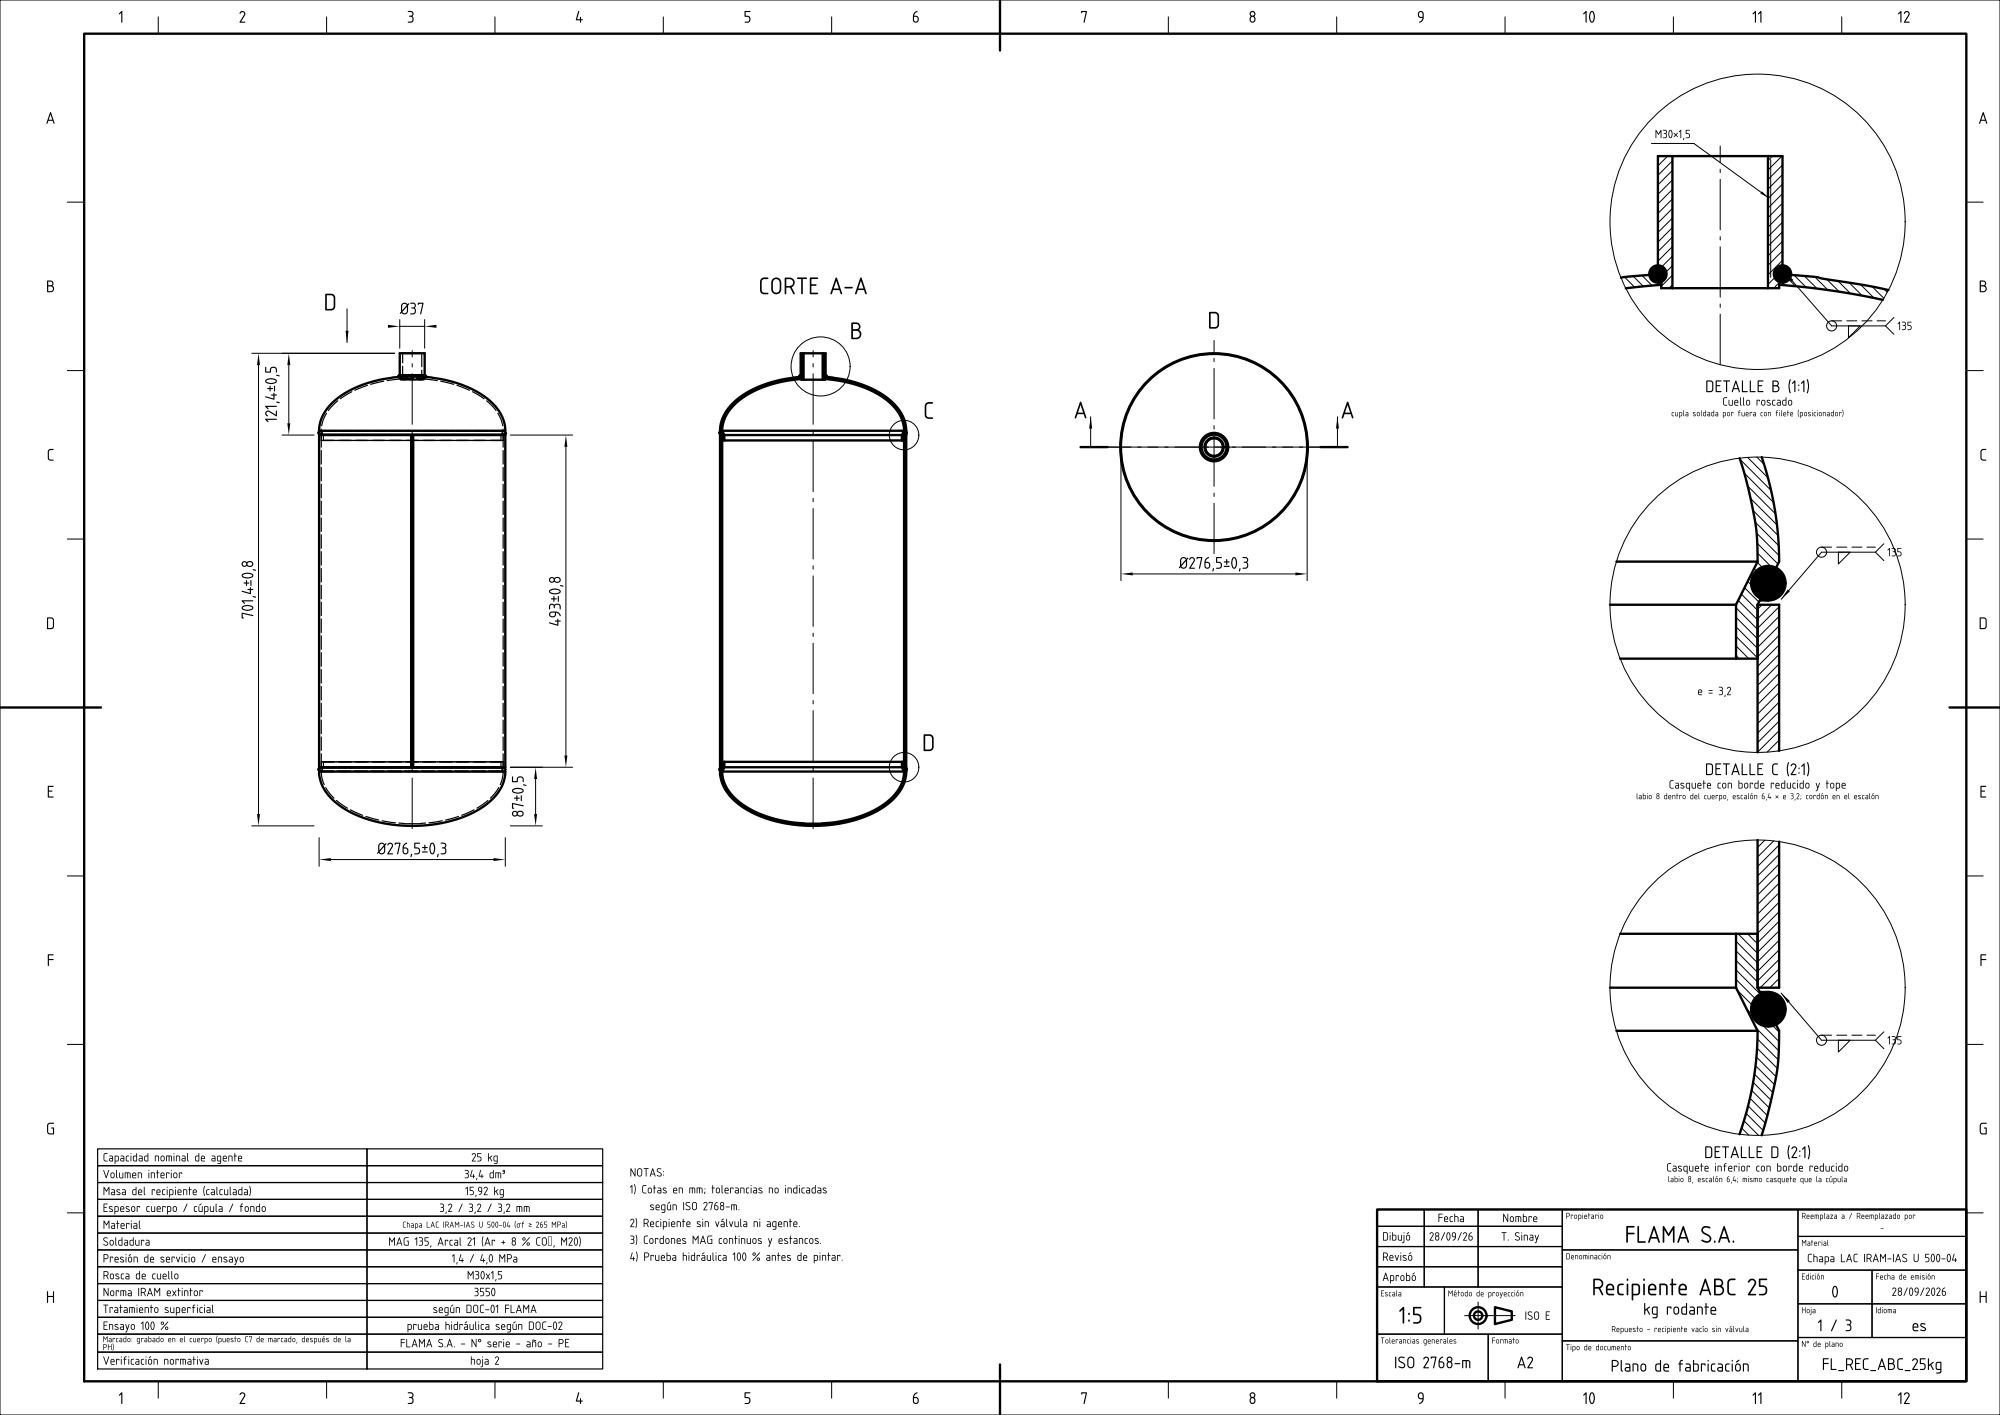
[picture p244: page 17]

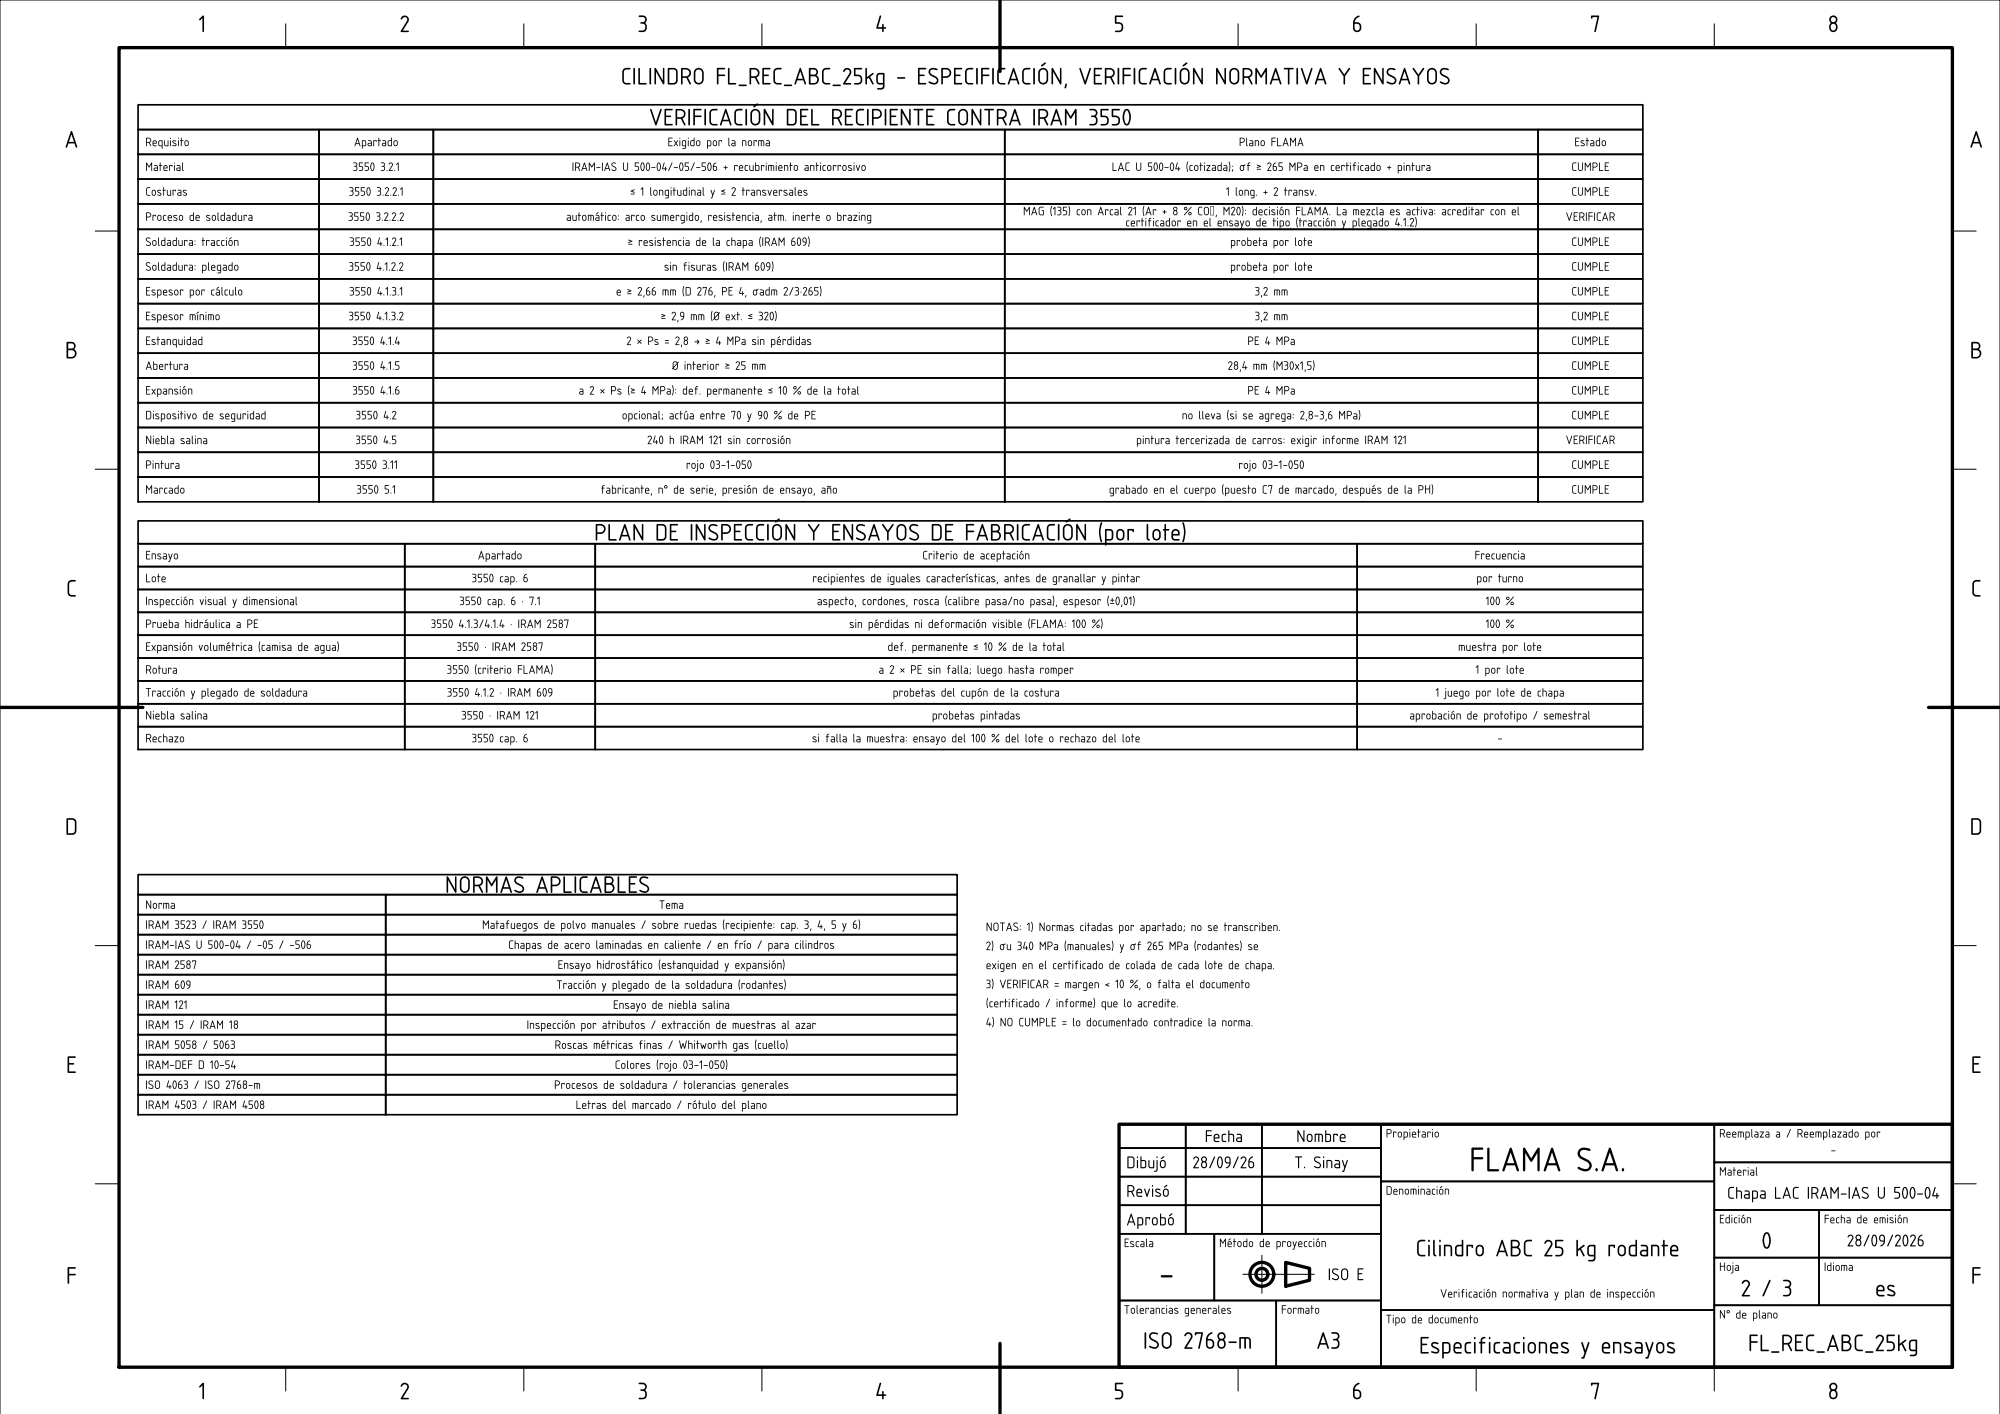
[picture p245: page 18]

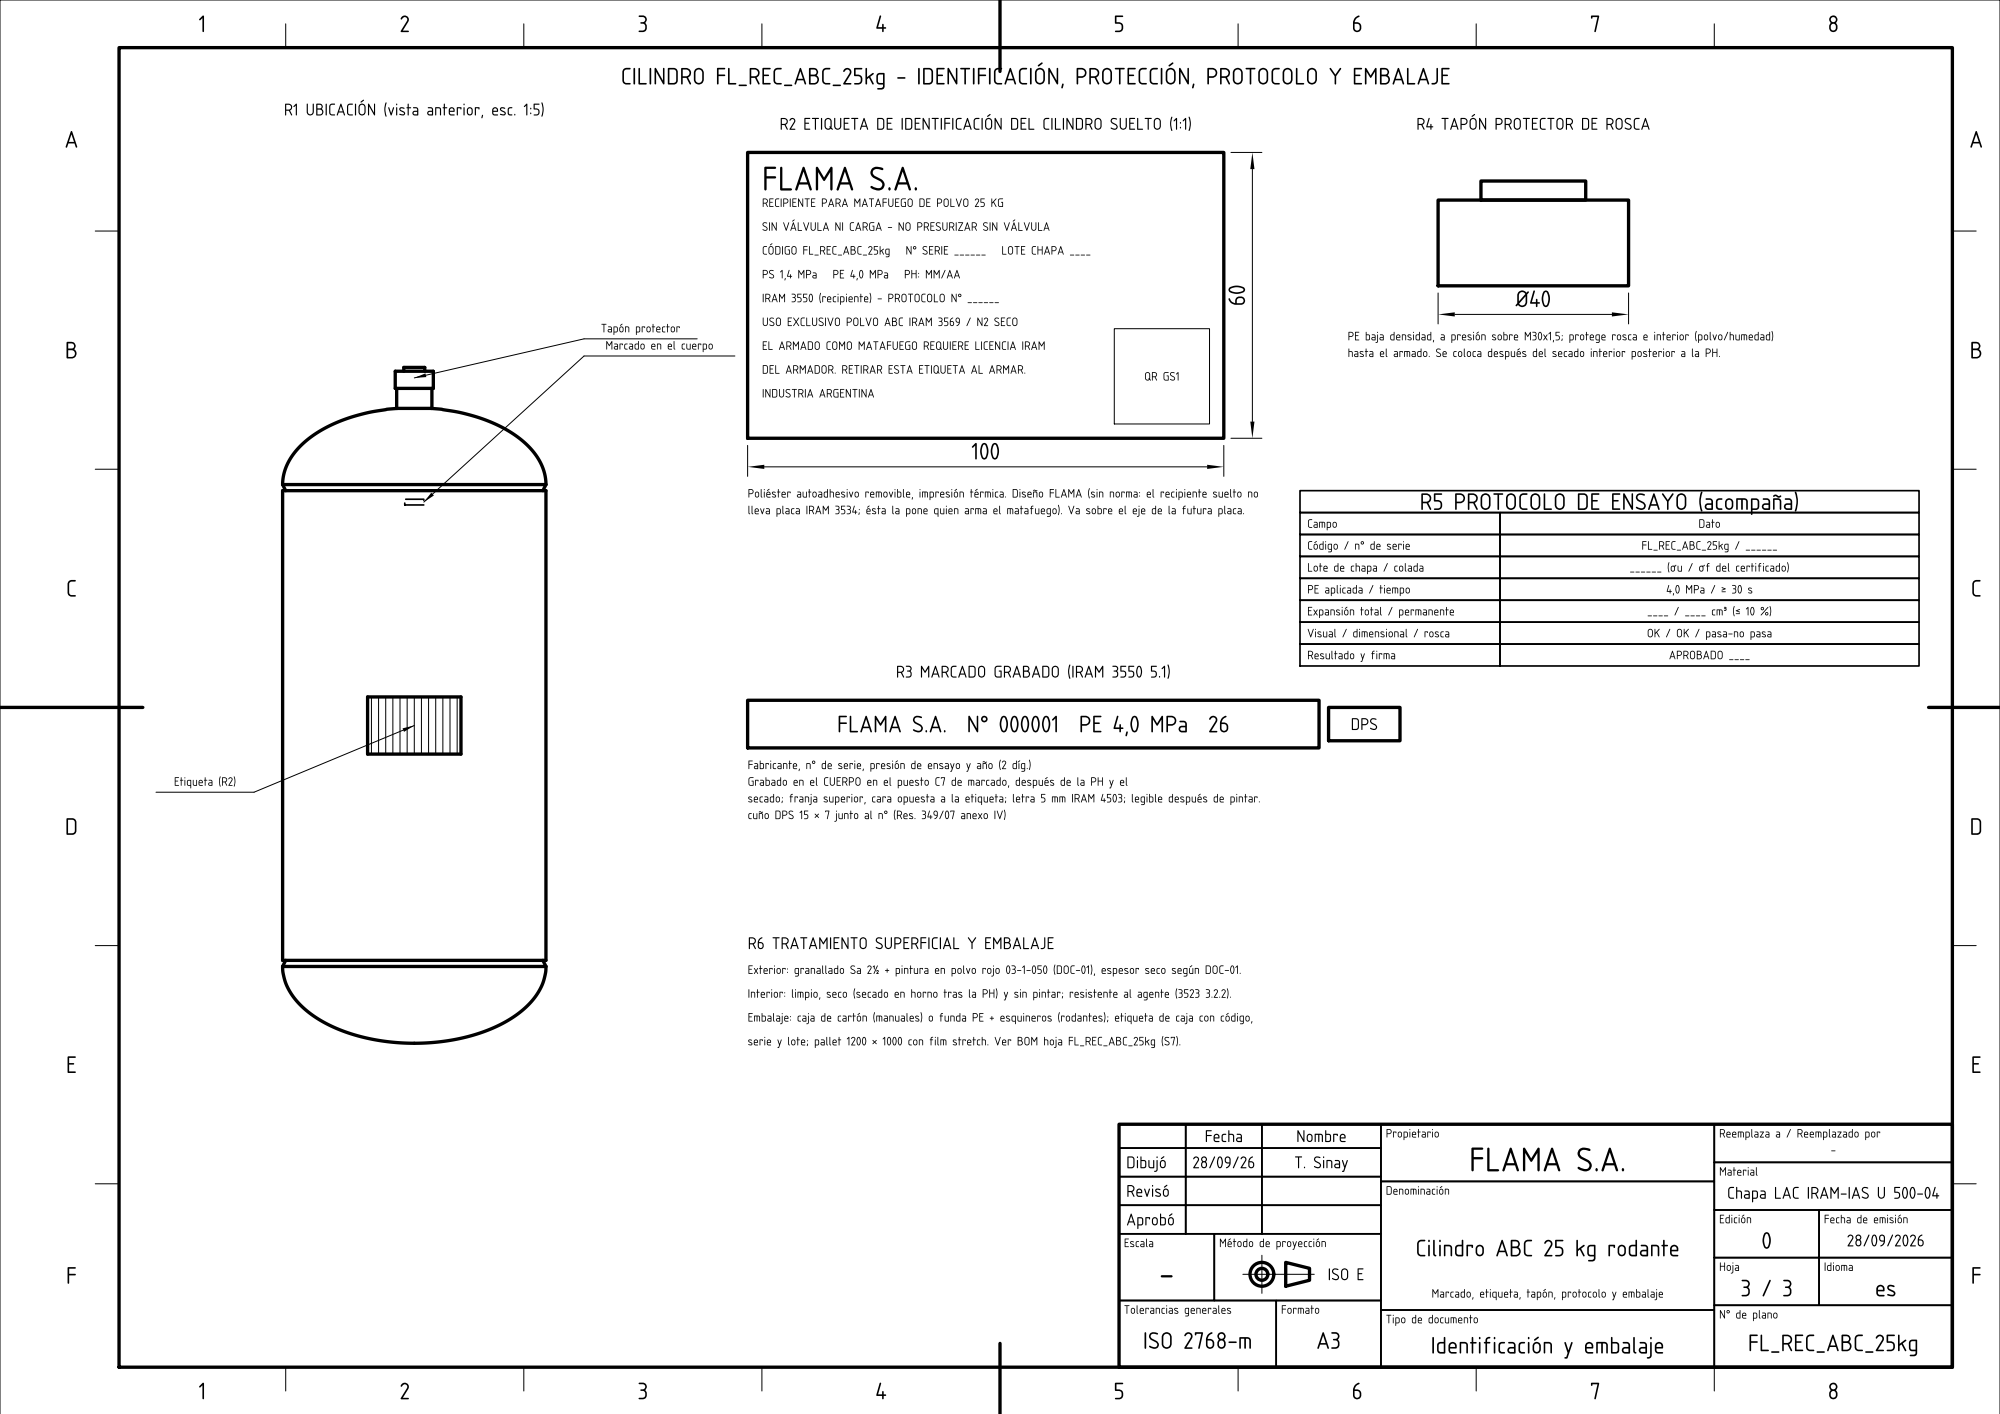
[picture p246: page 19]

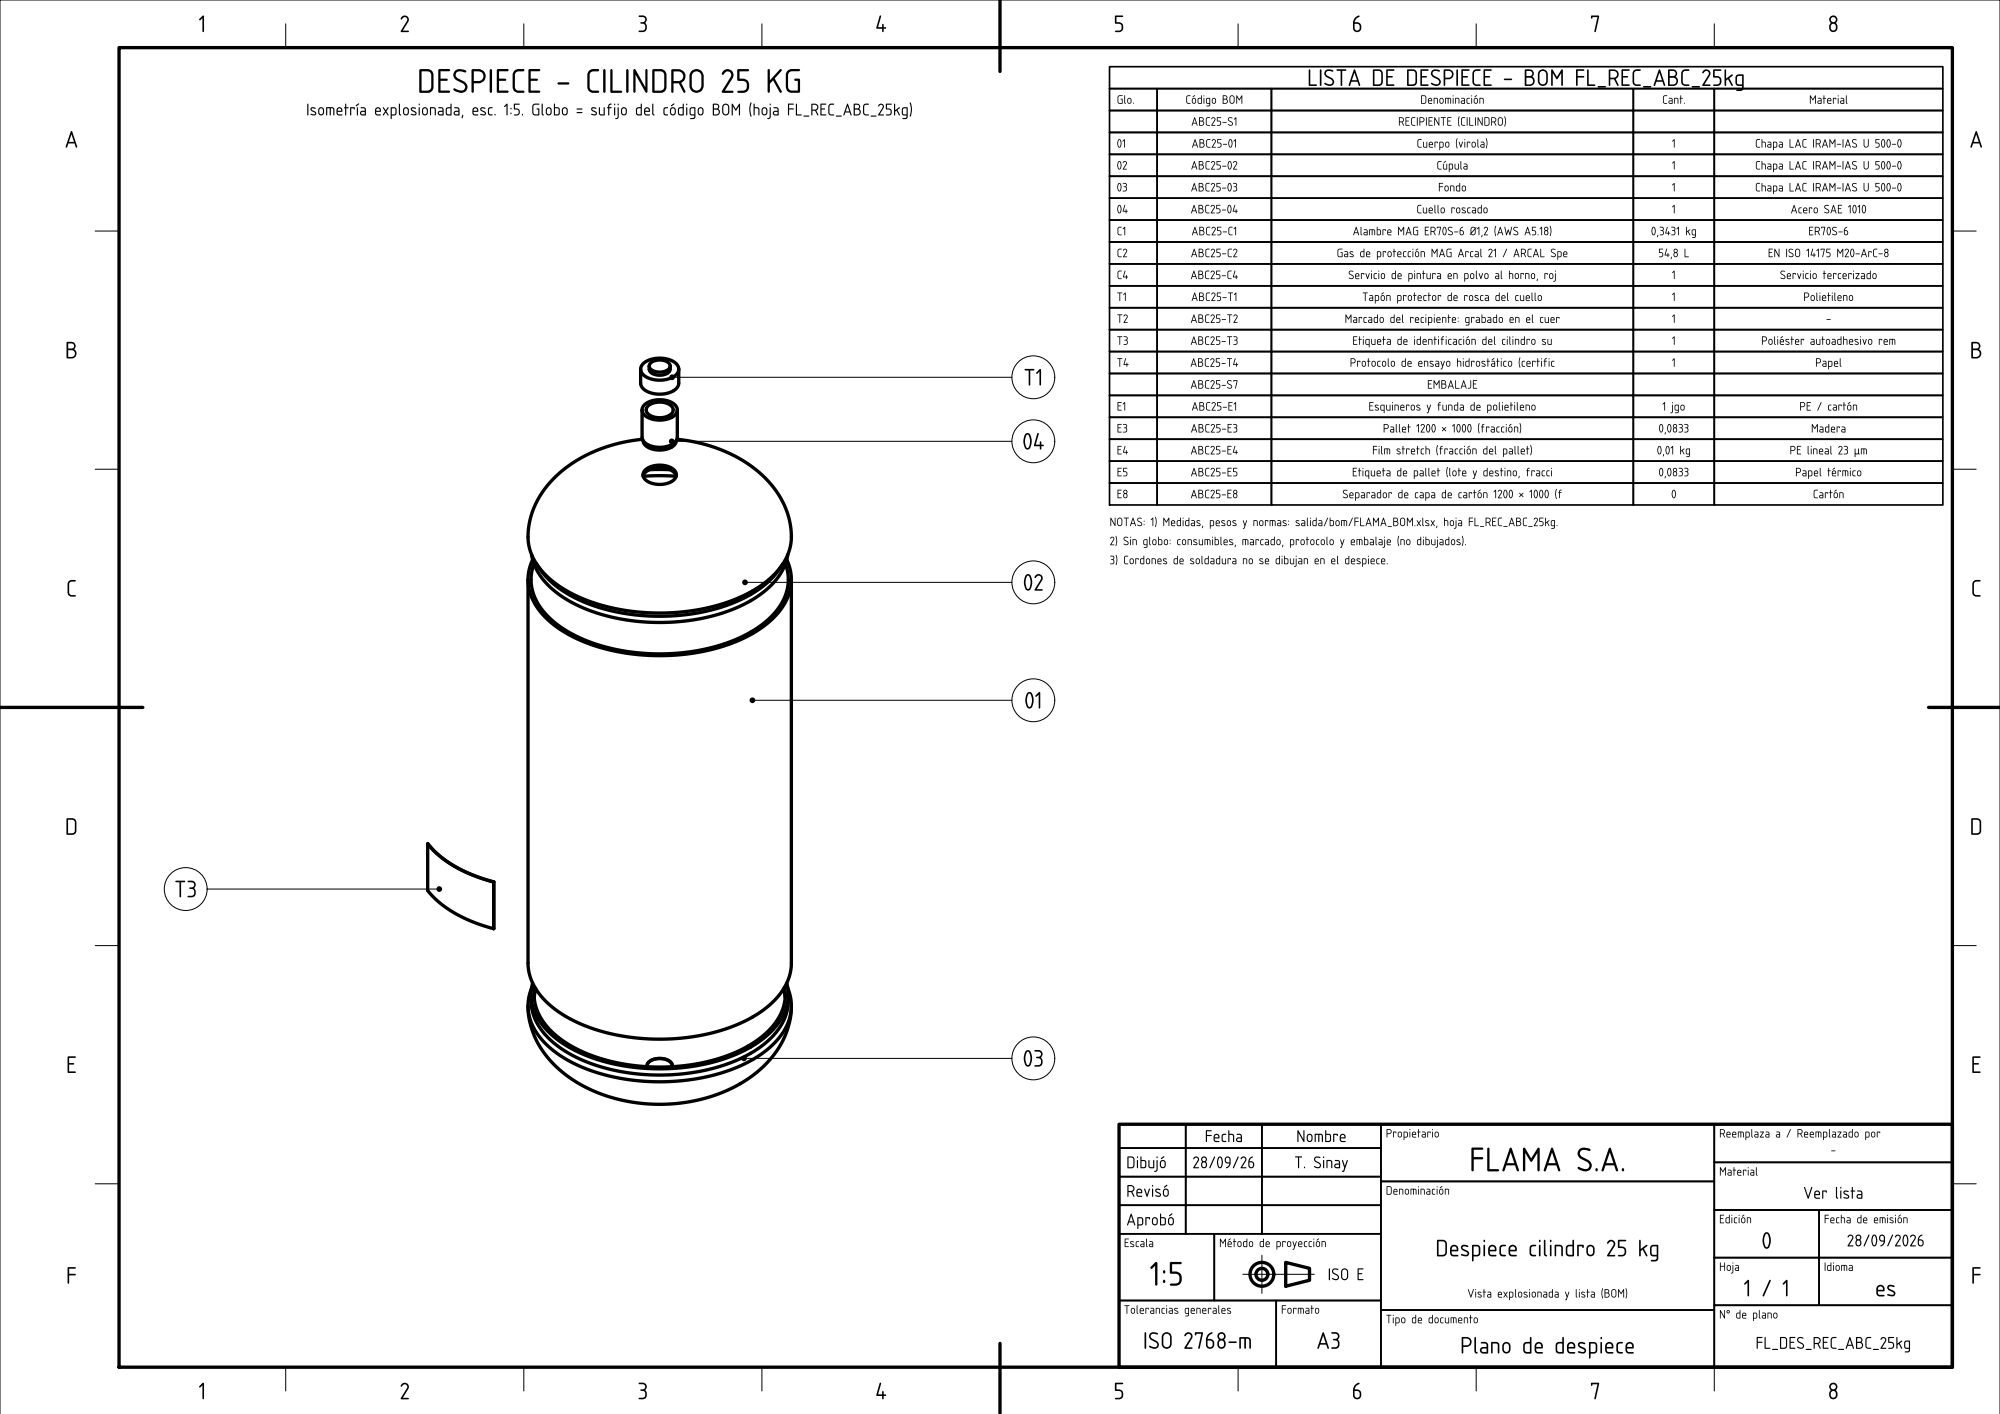
[picture p247: page 20]

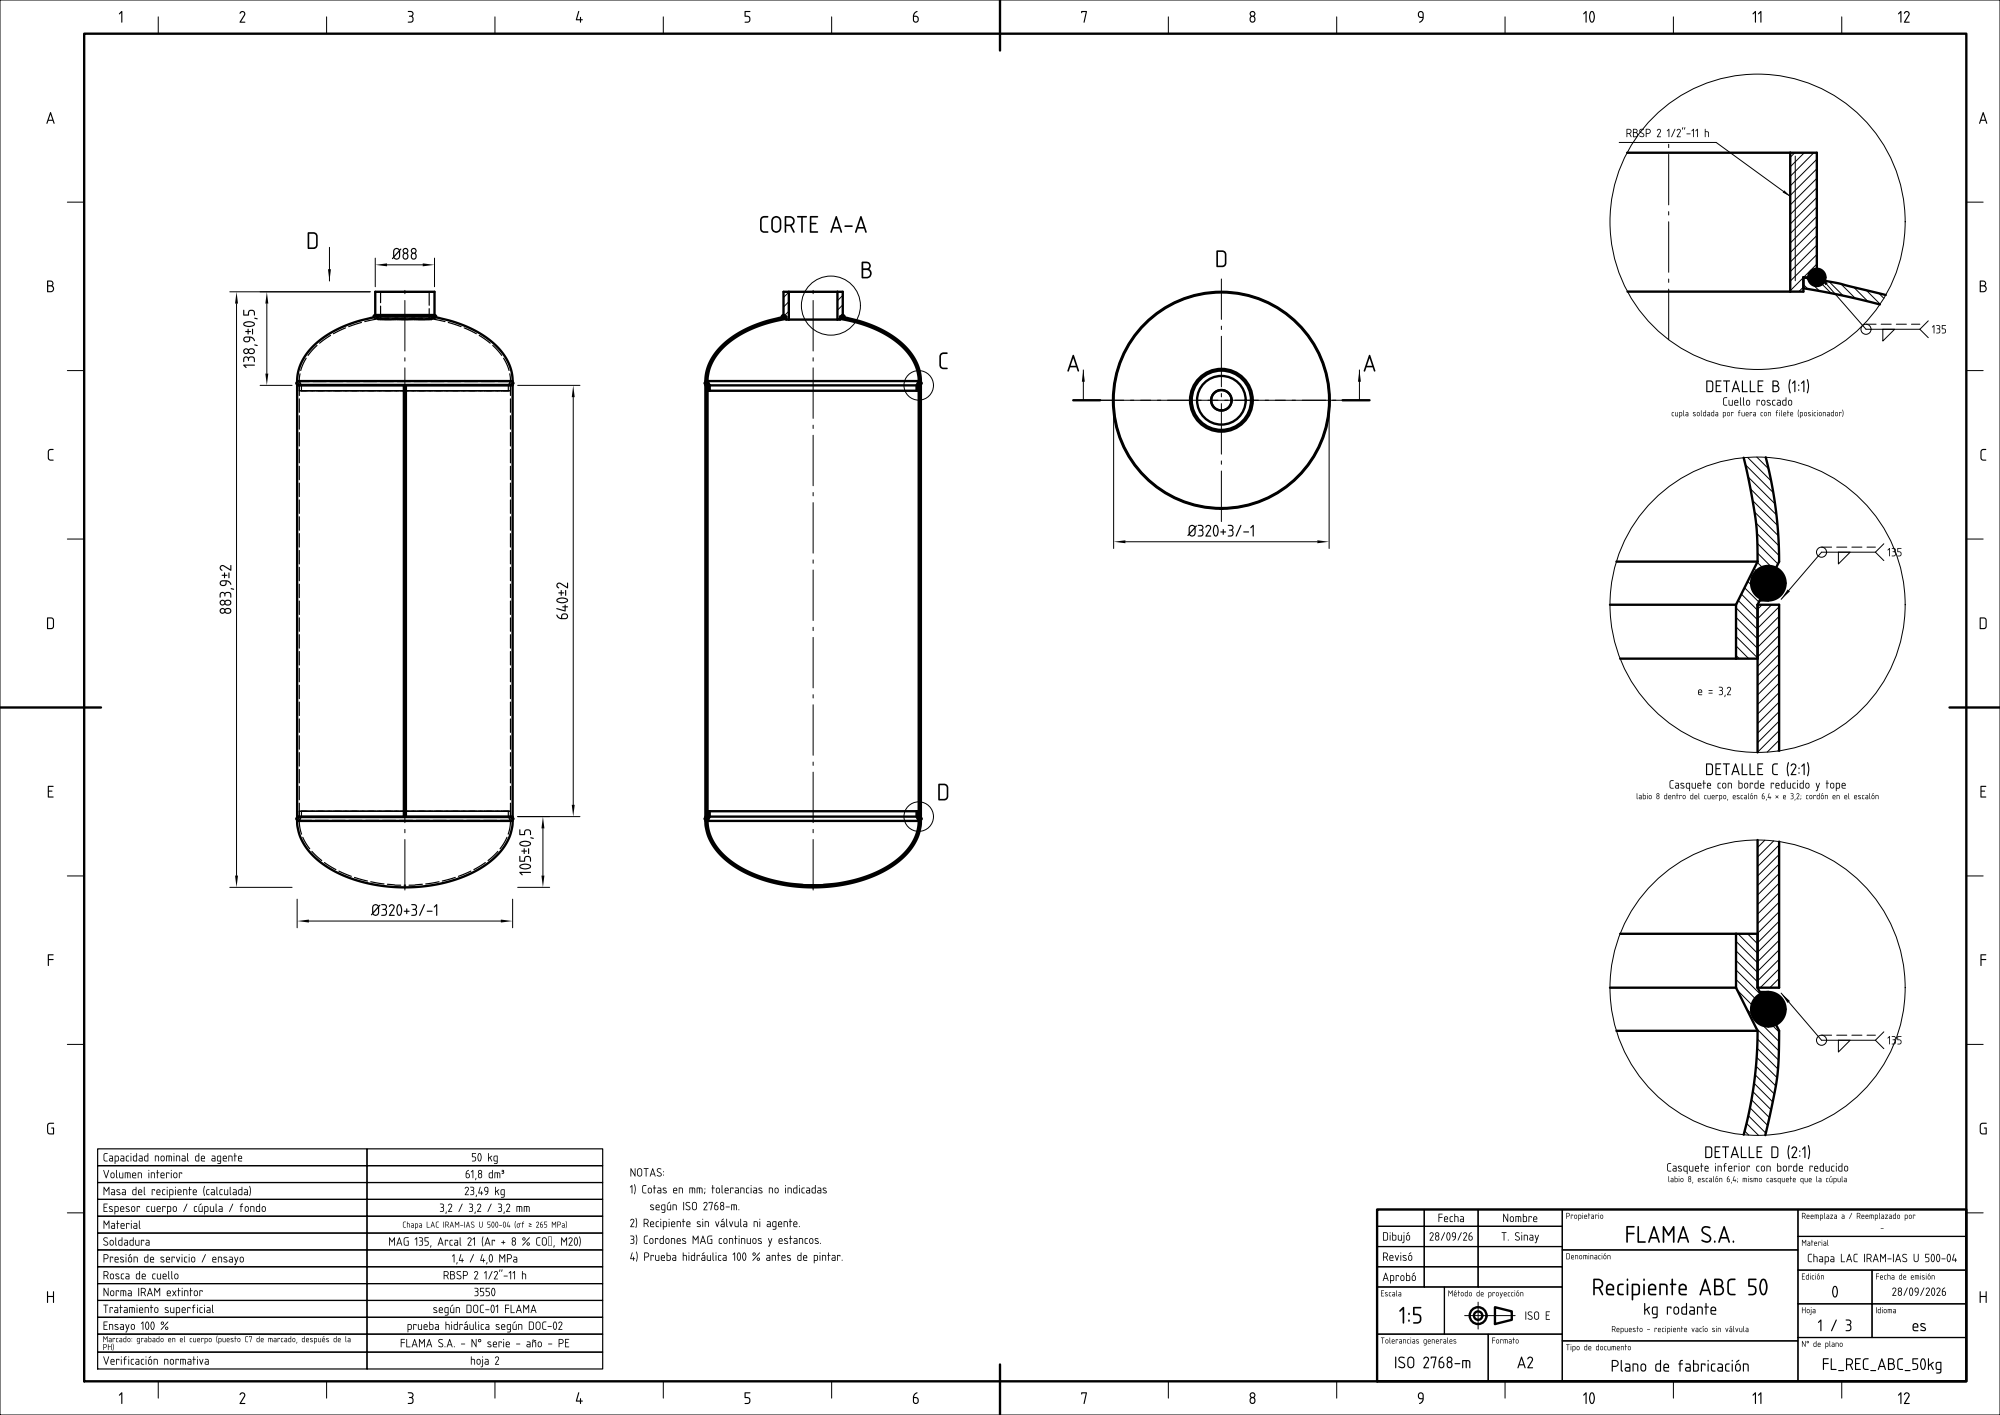
[picture p248: page 21]

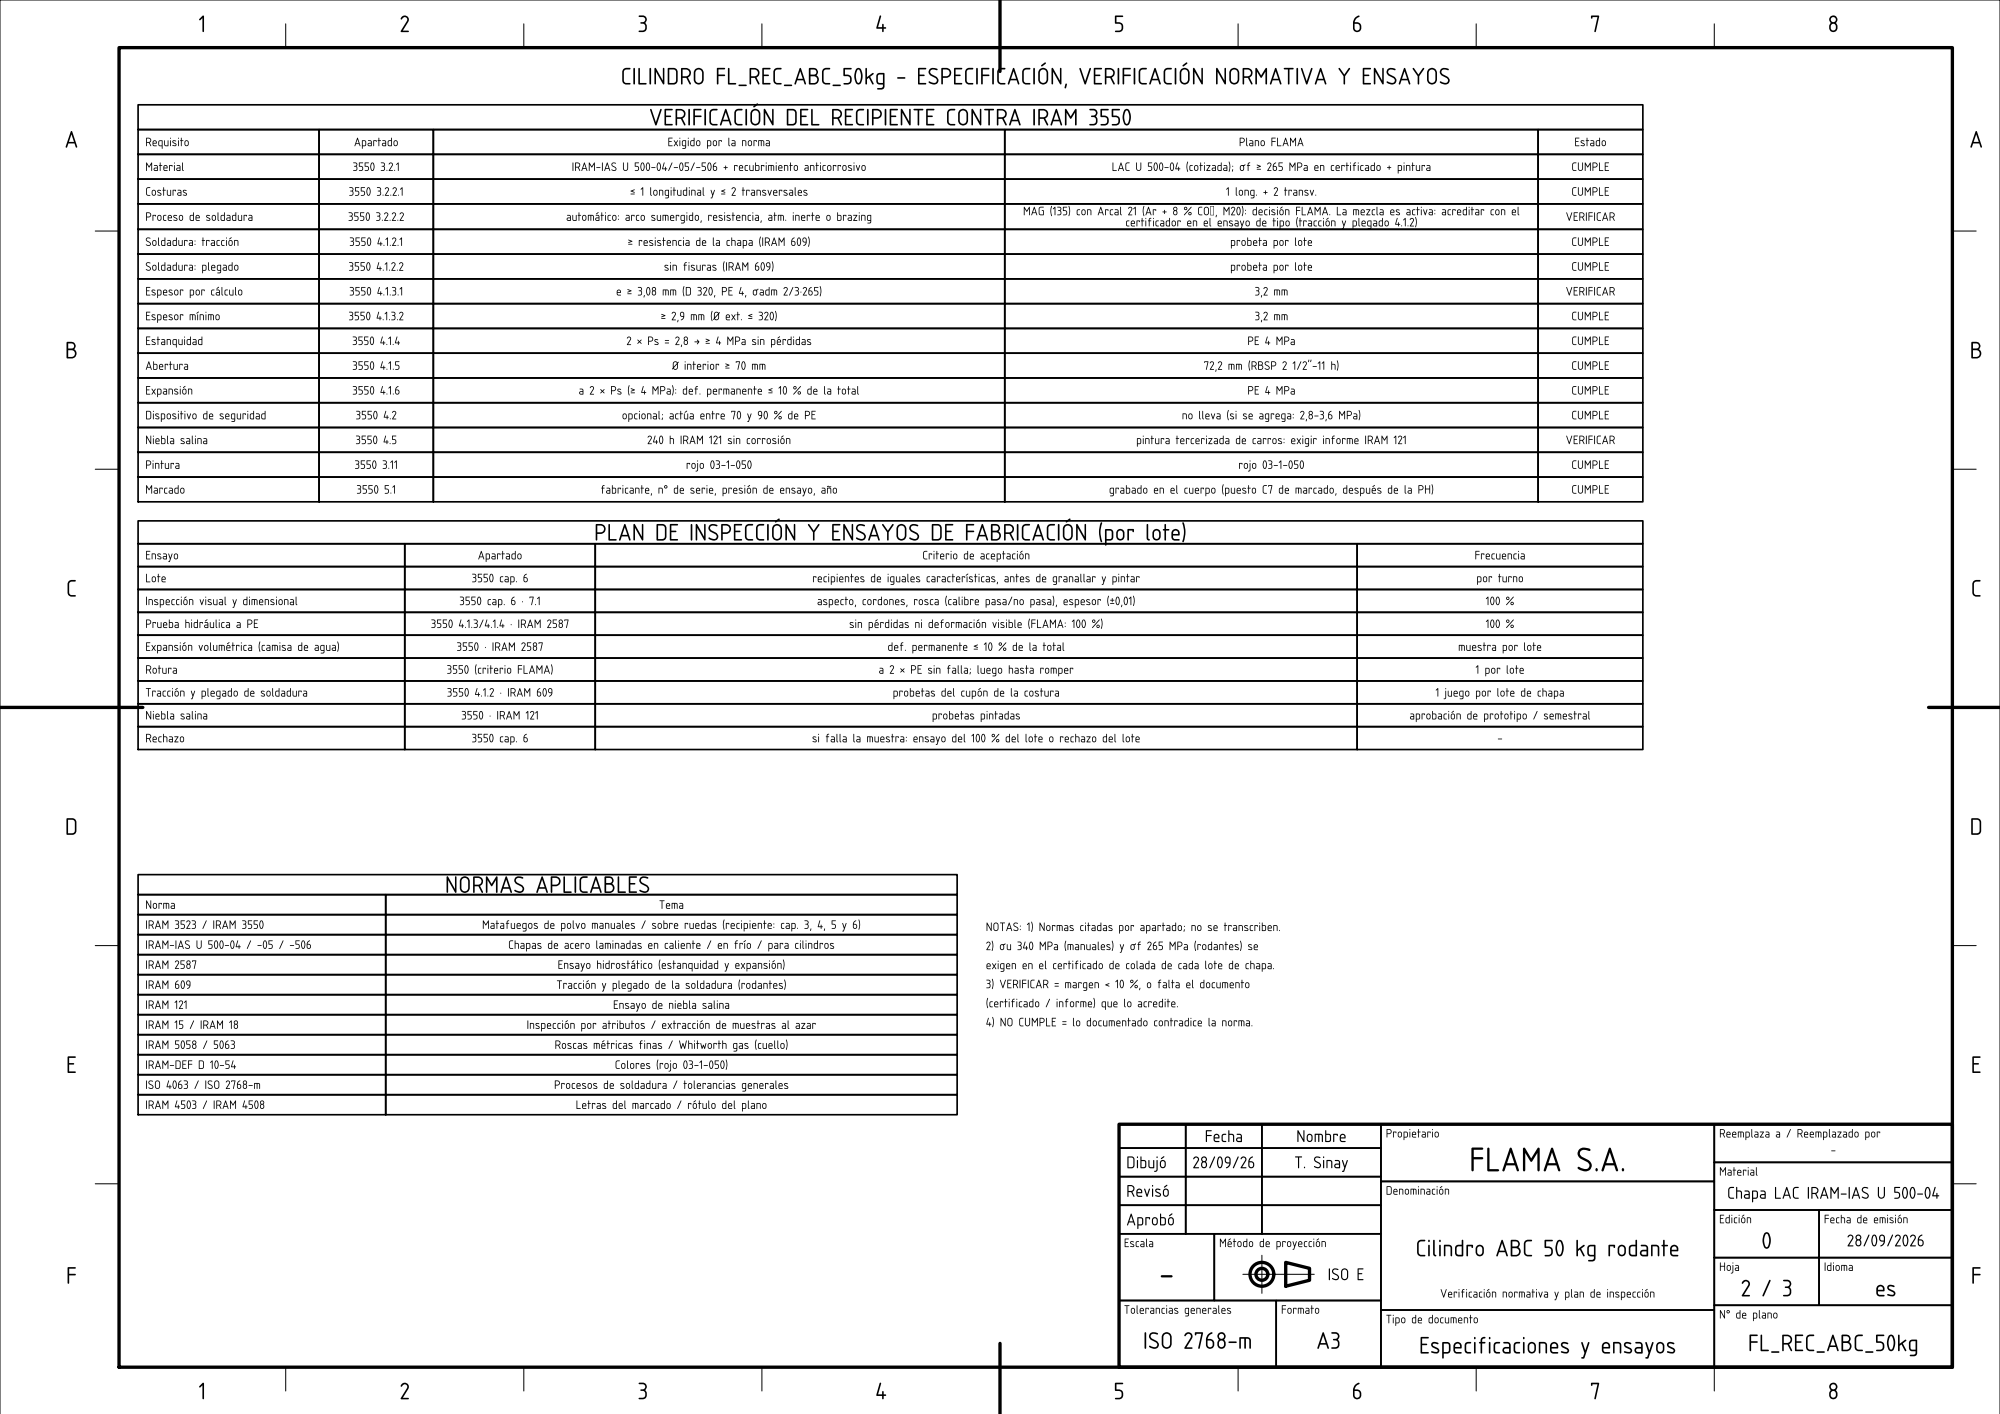
[picture p249: page 22]

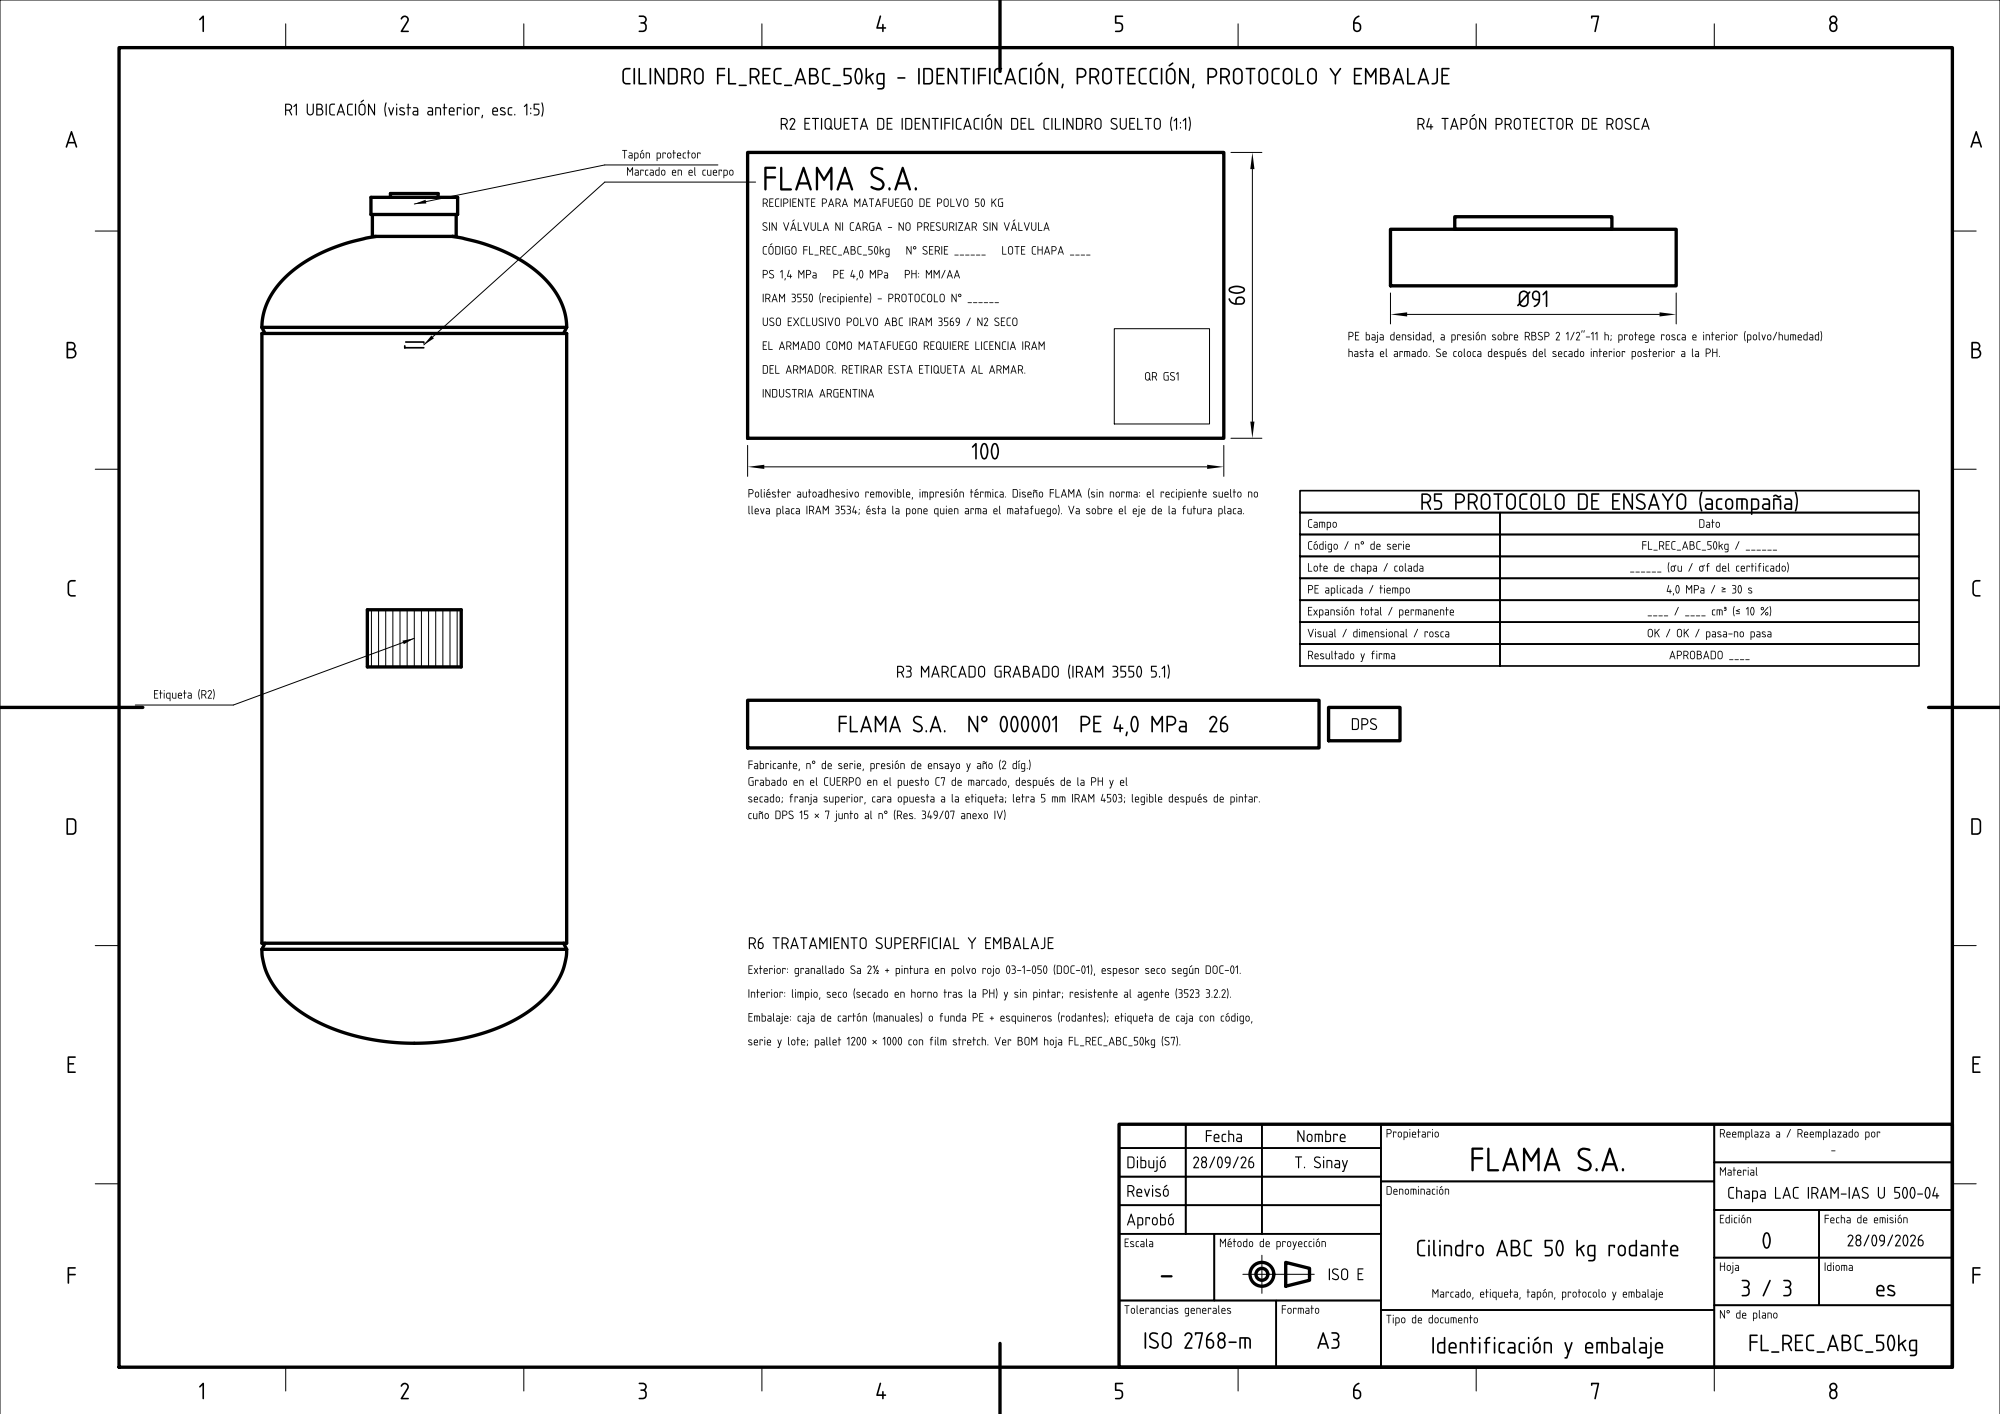
[picture p250: page 23]

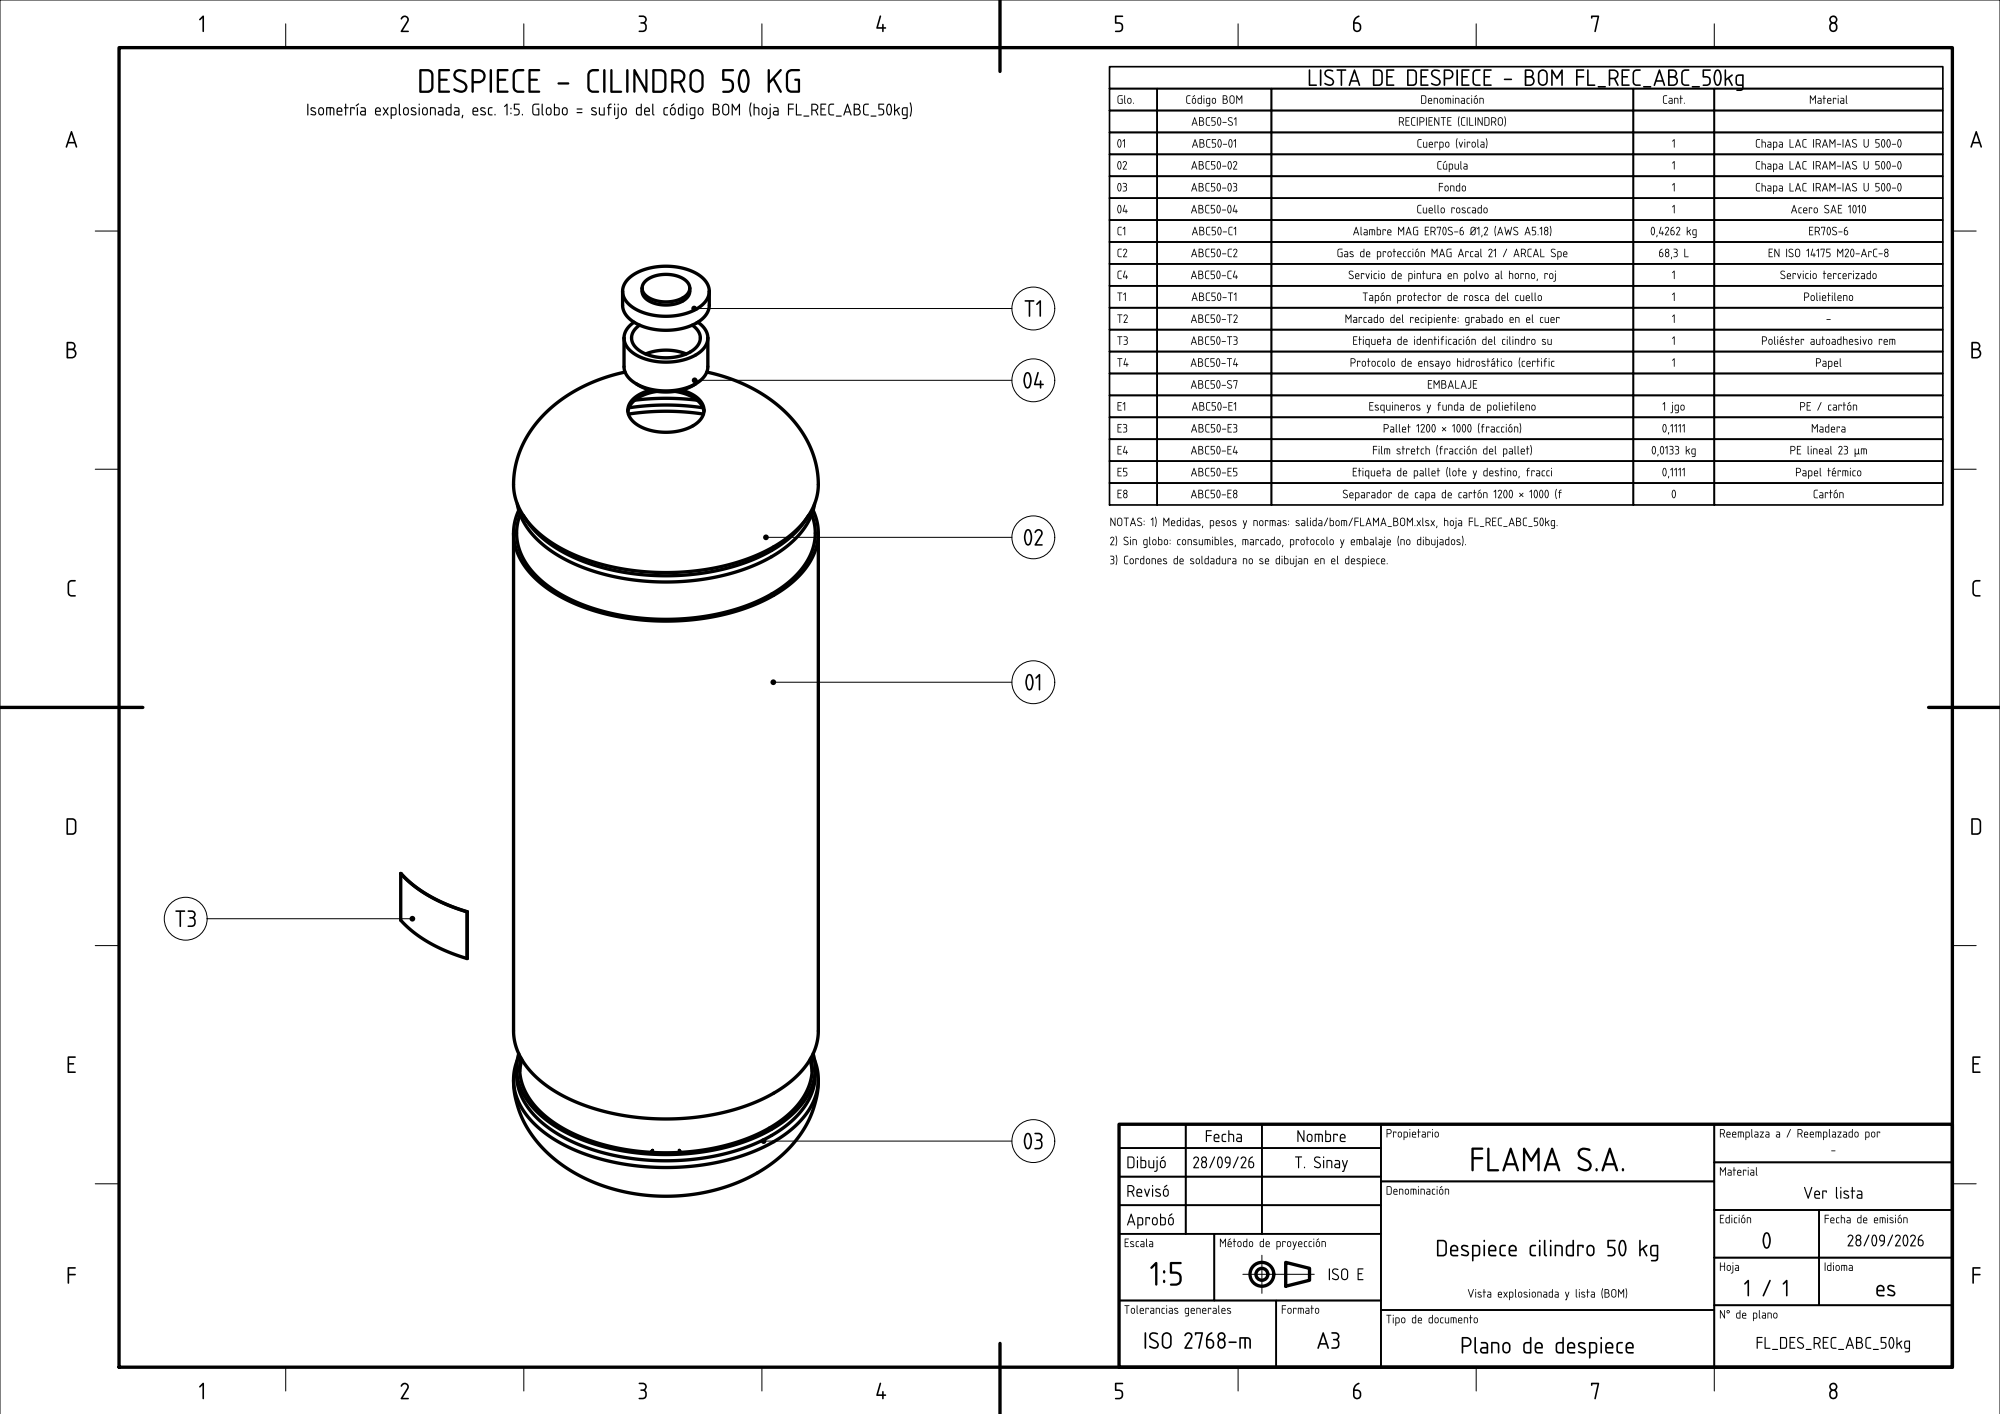
[picture p251: page 24]

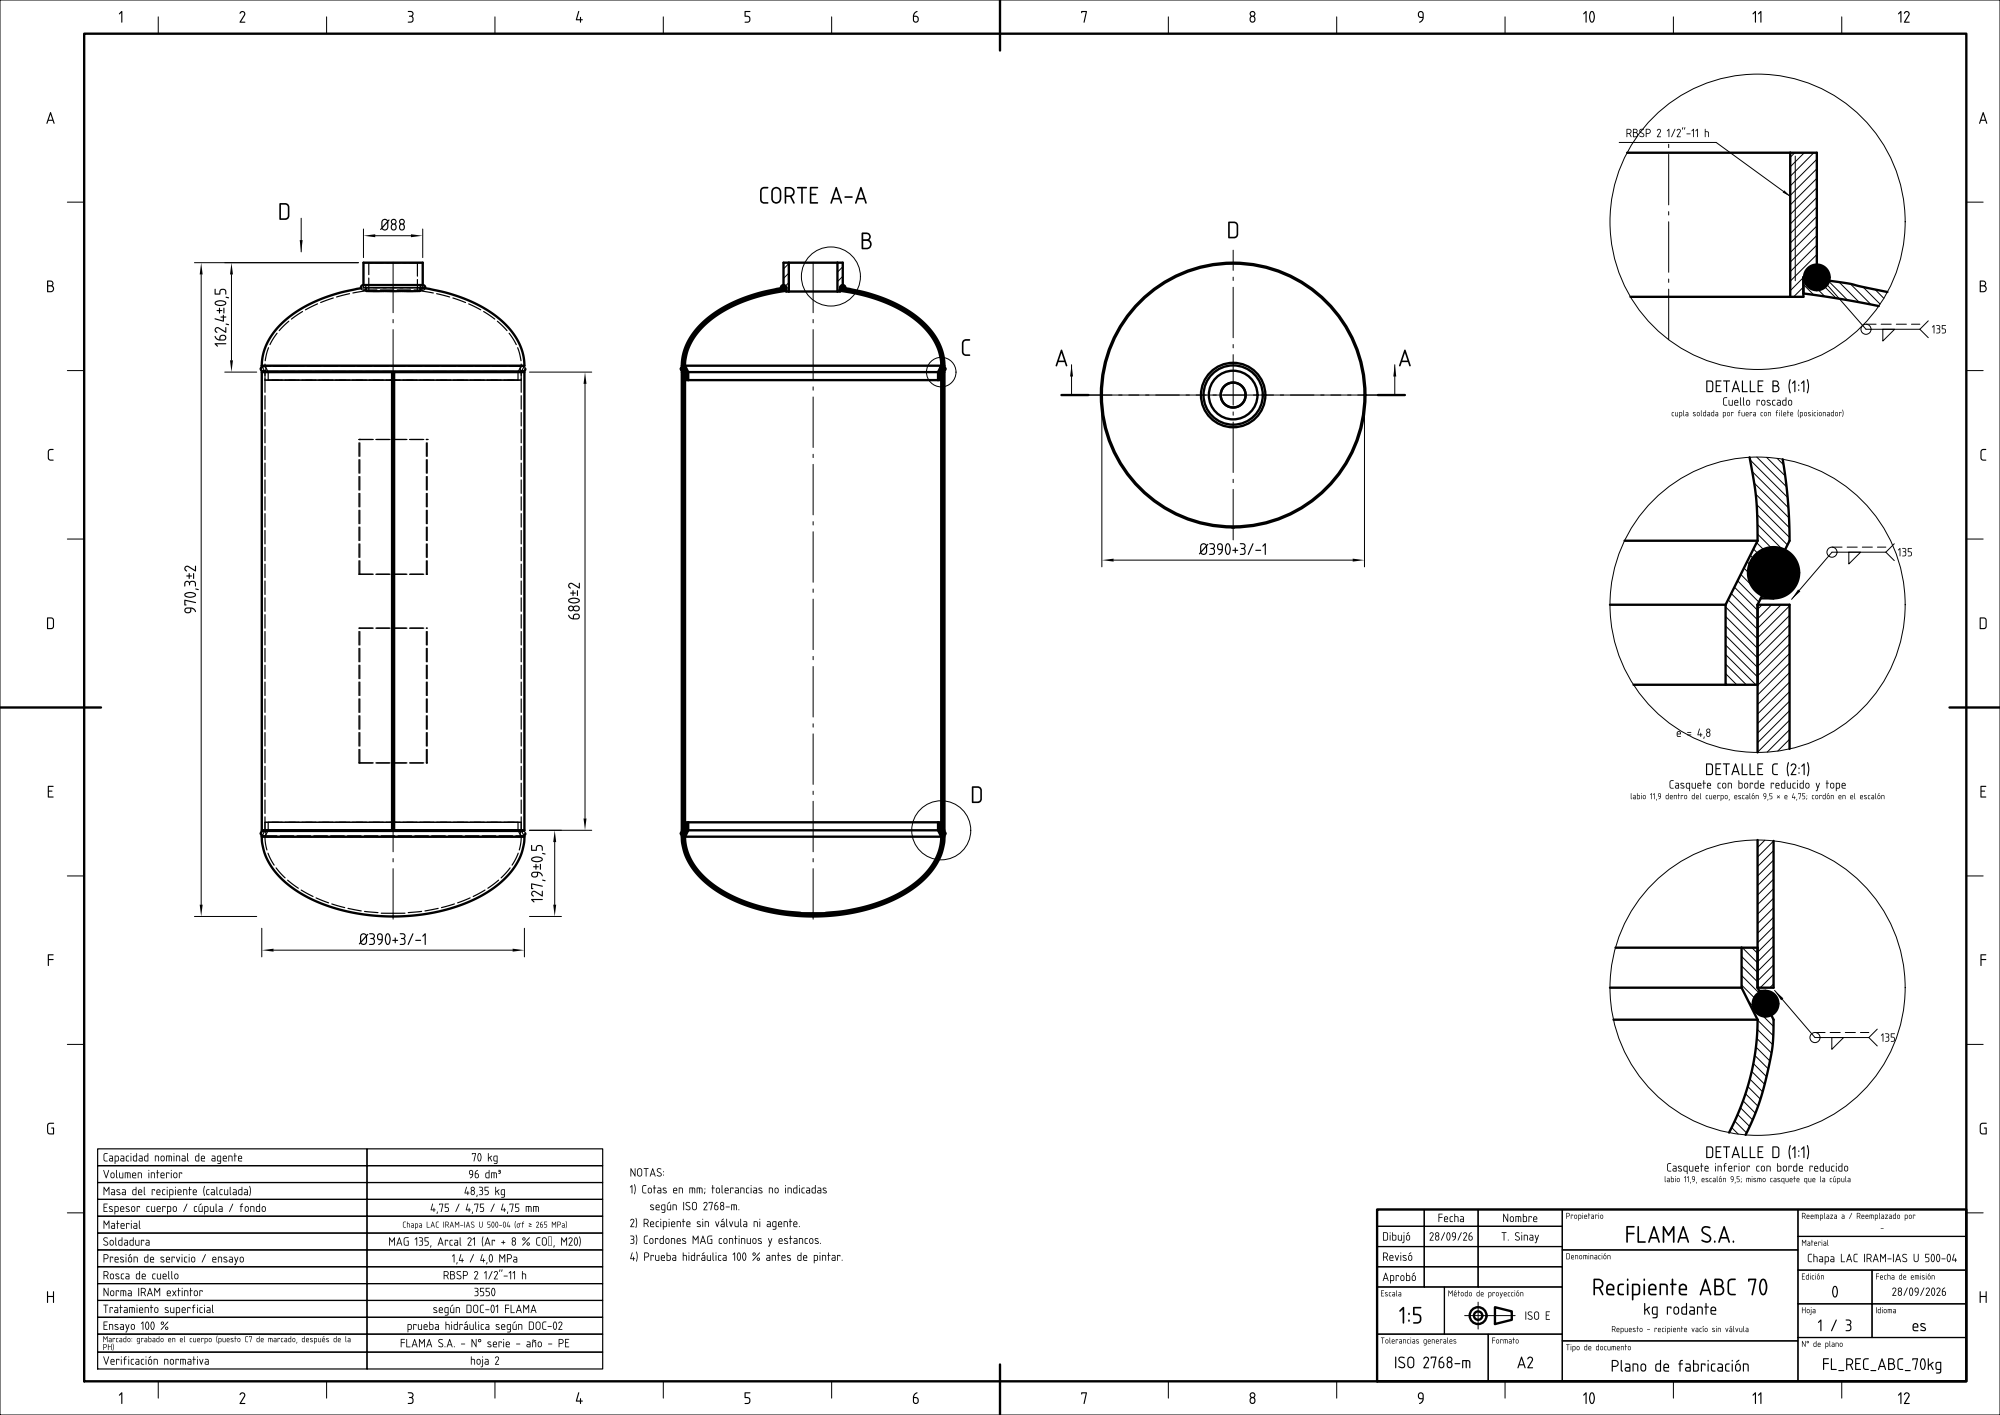
[picture p252: page 25]

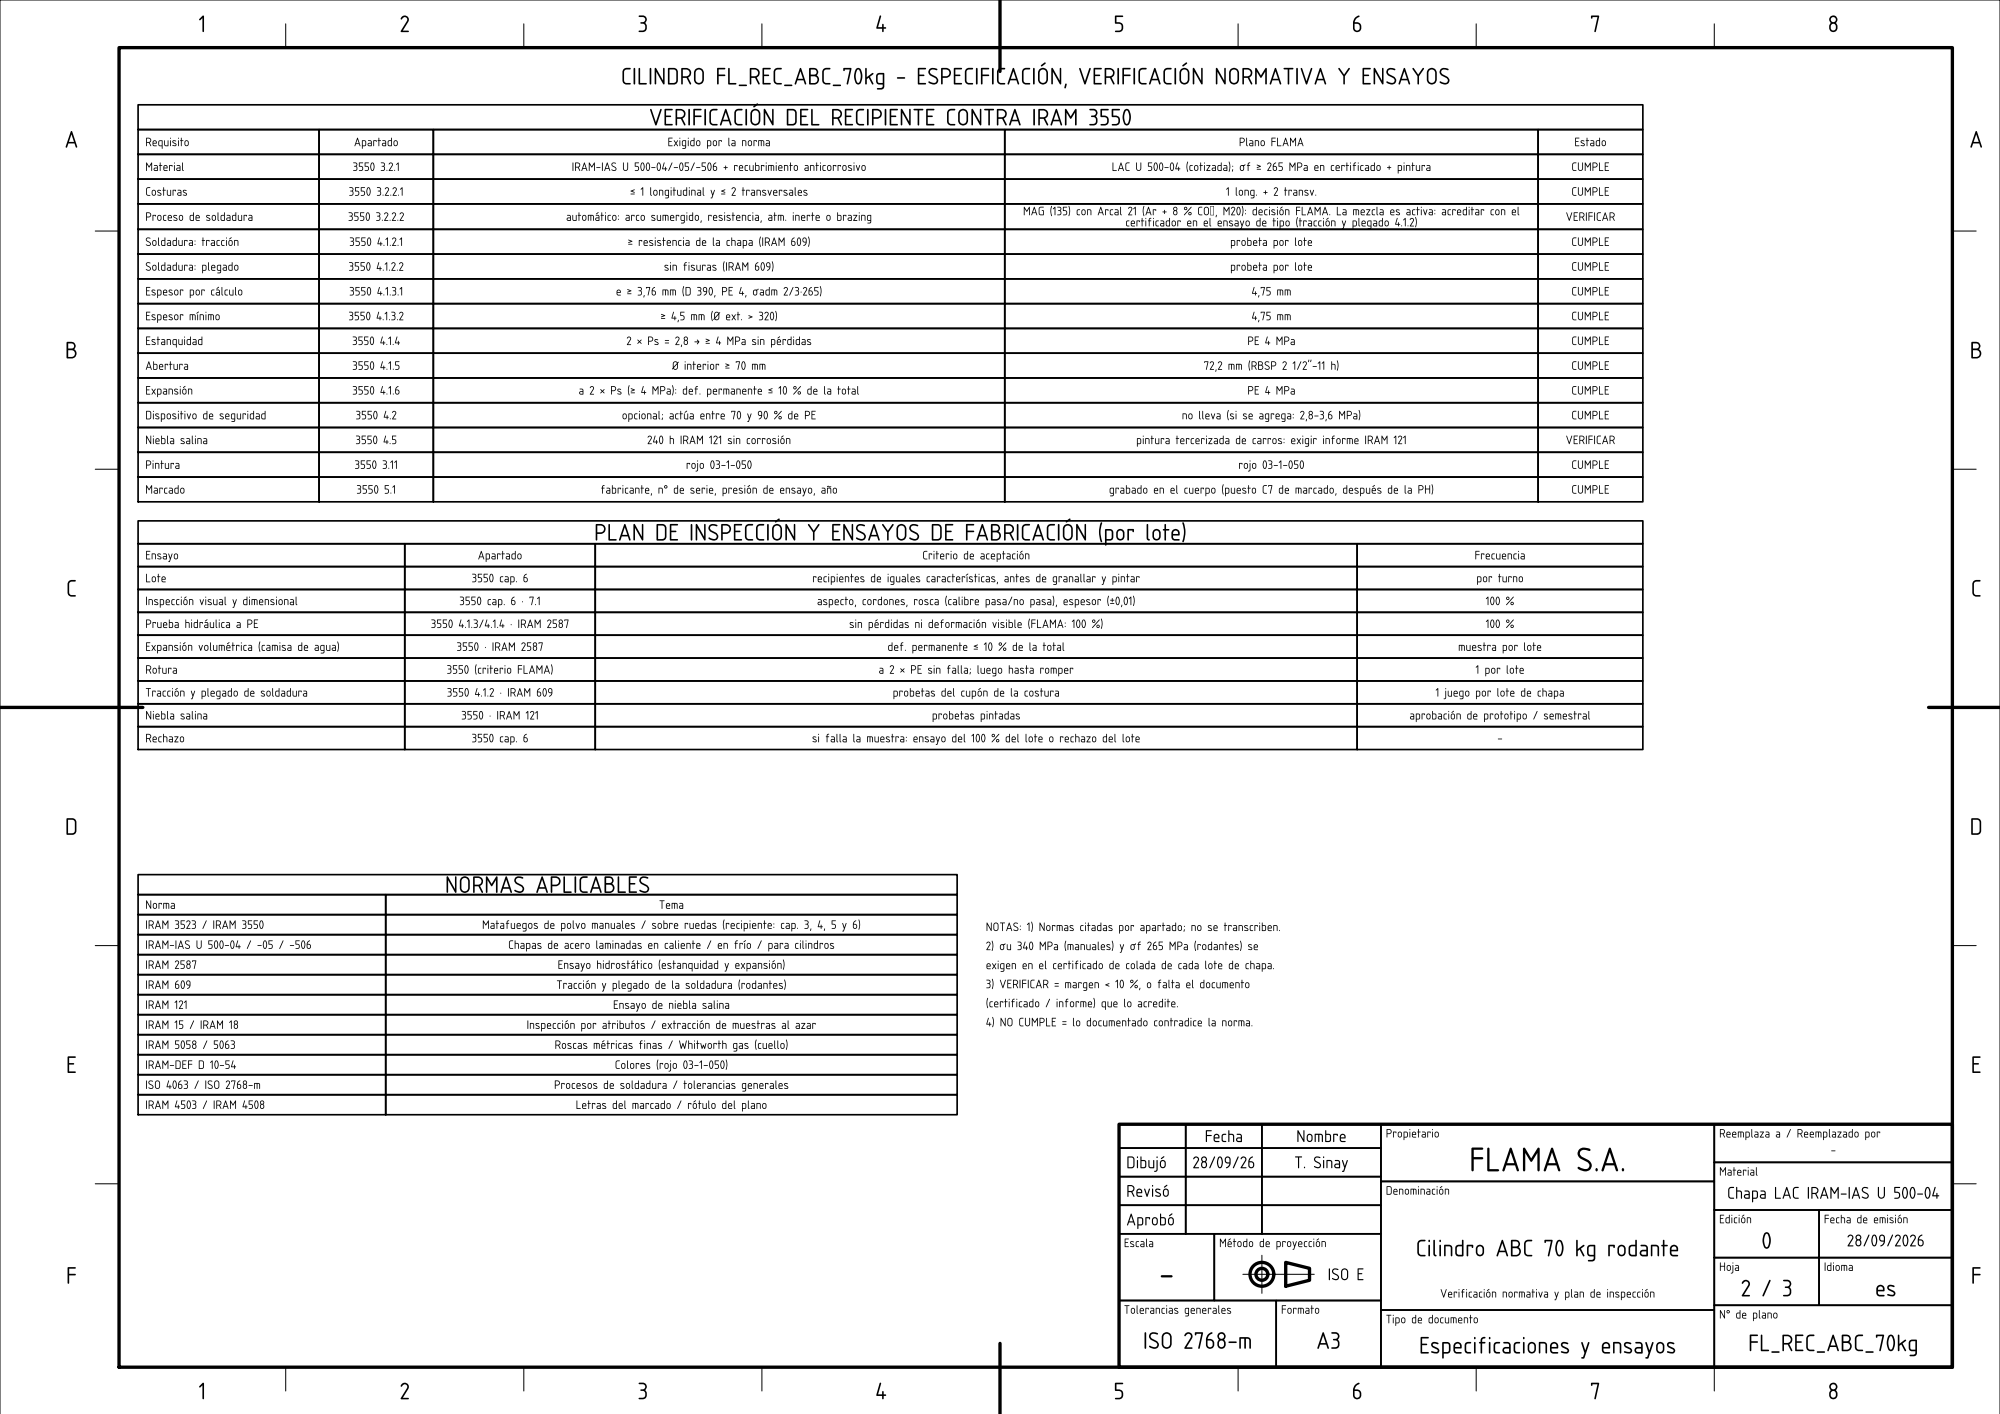
[picture p253: page 26]

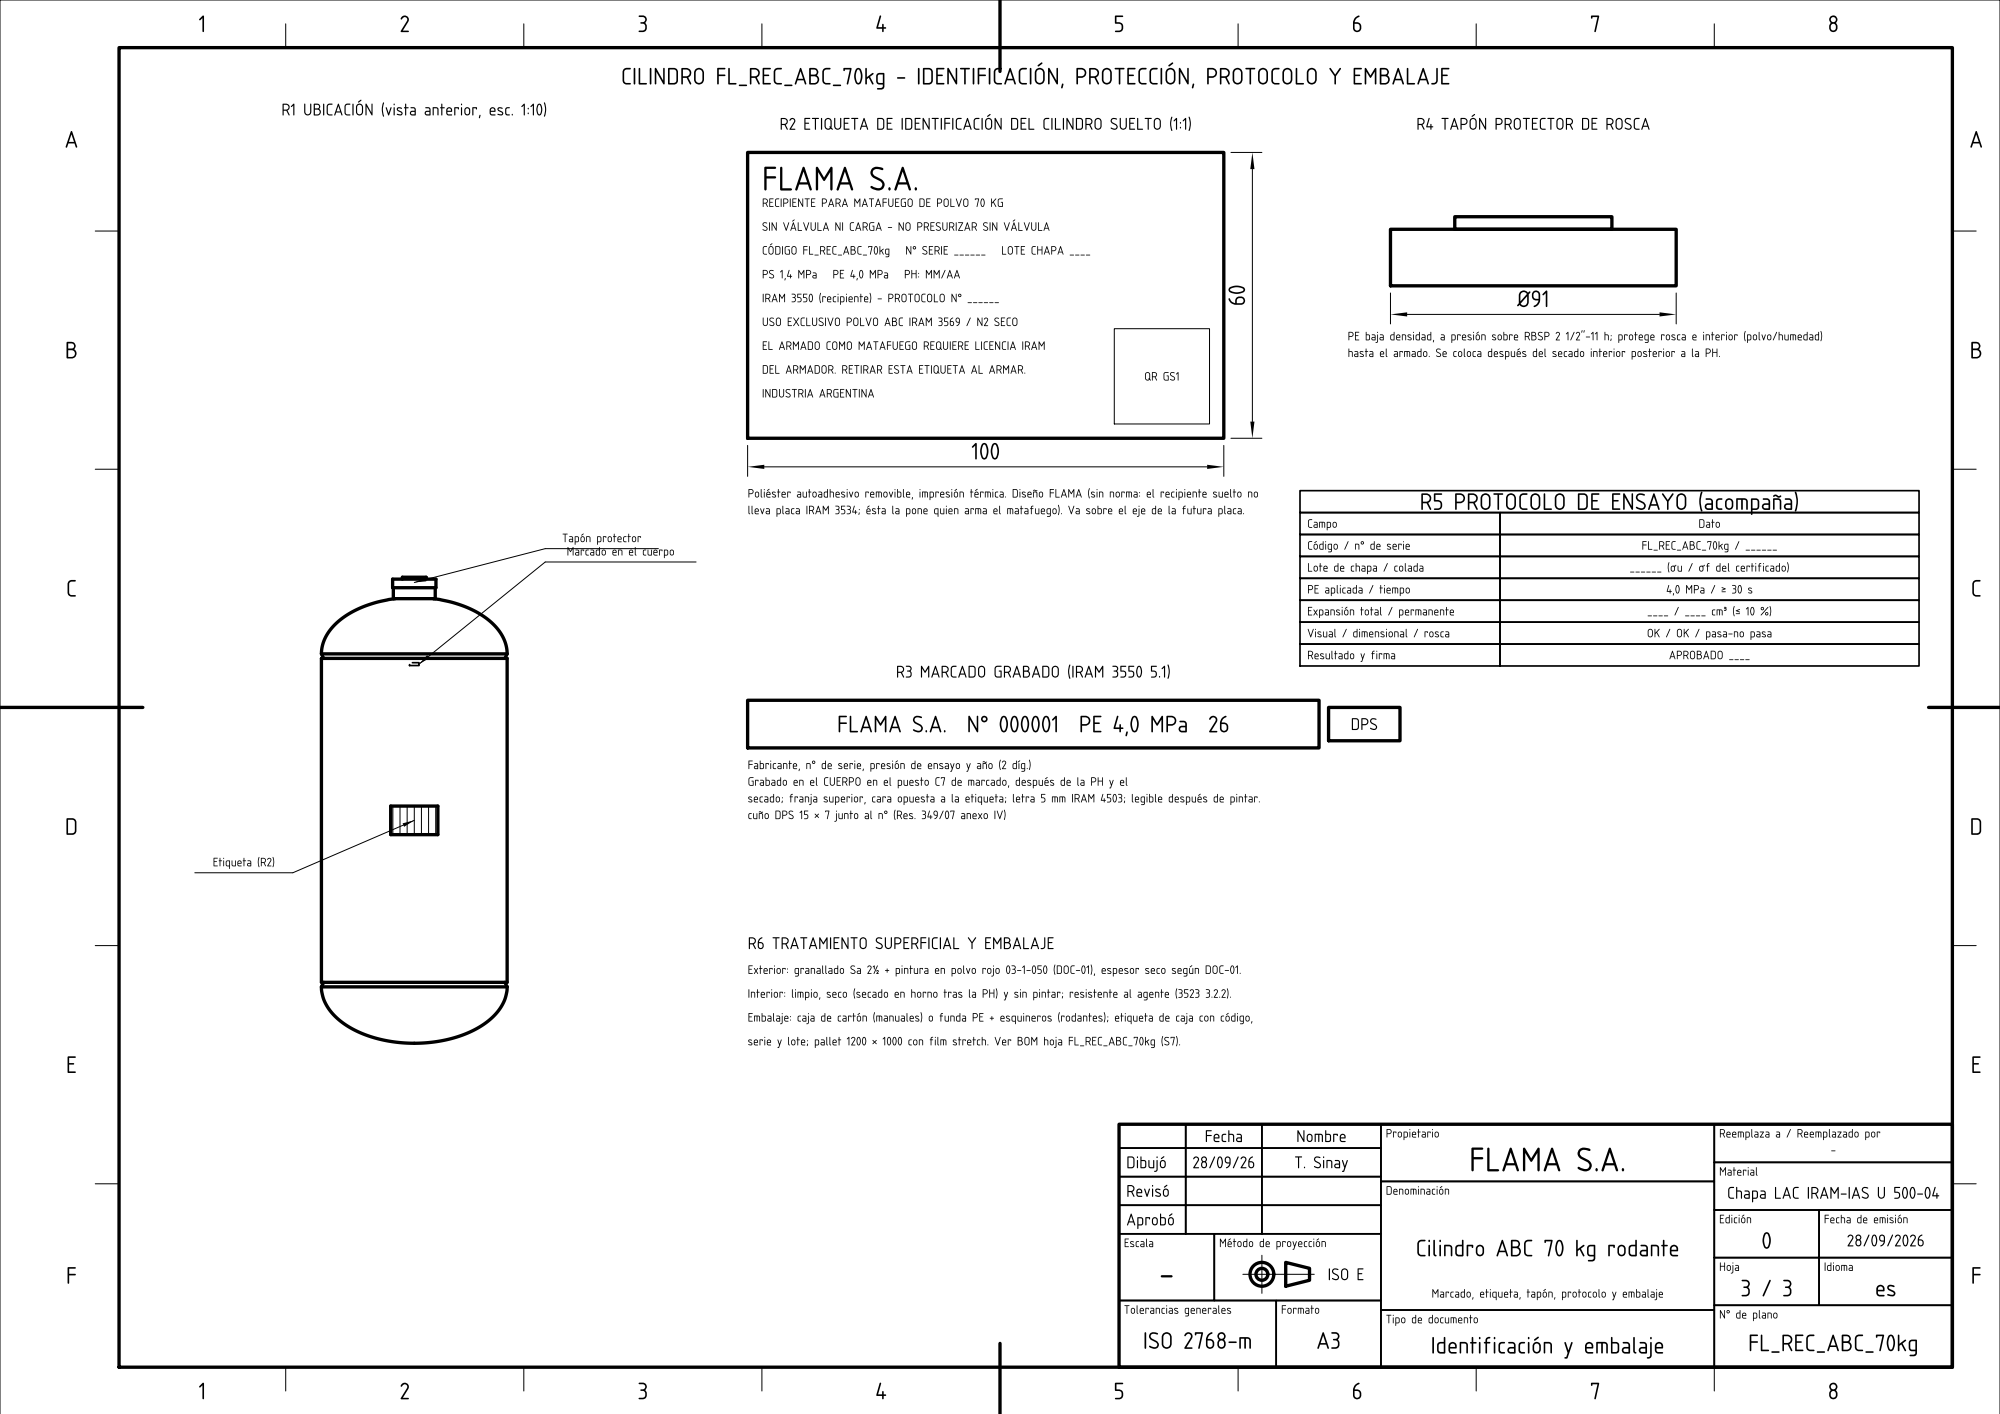
[picture p254: page 27]

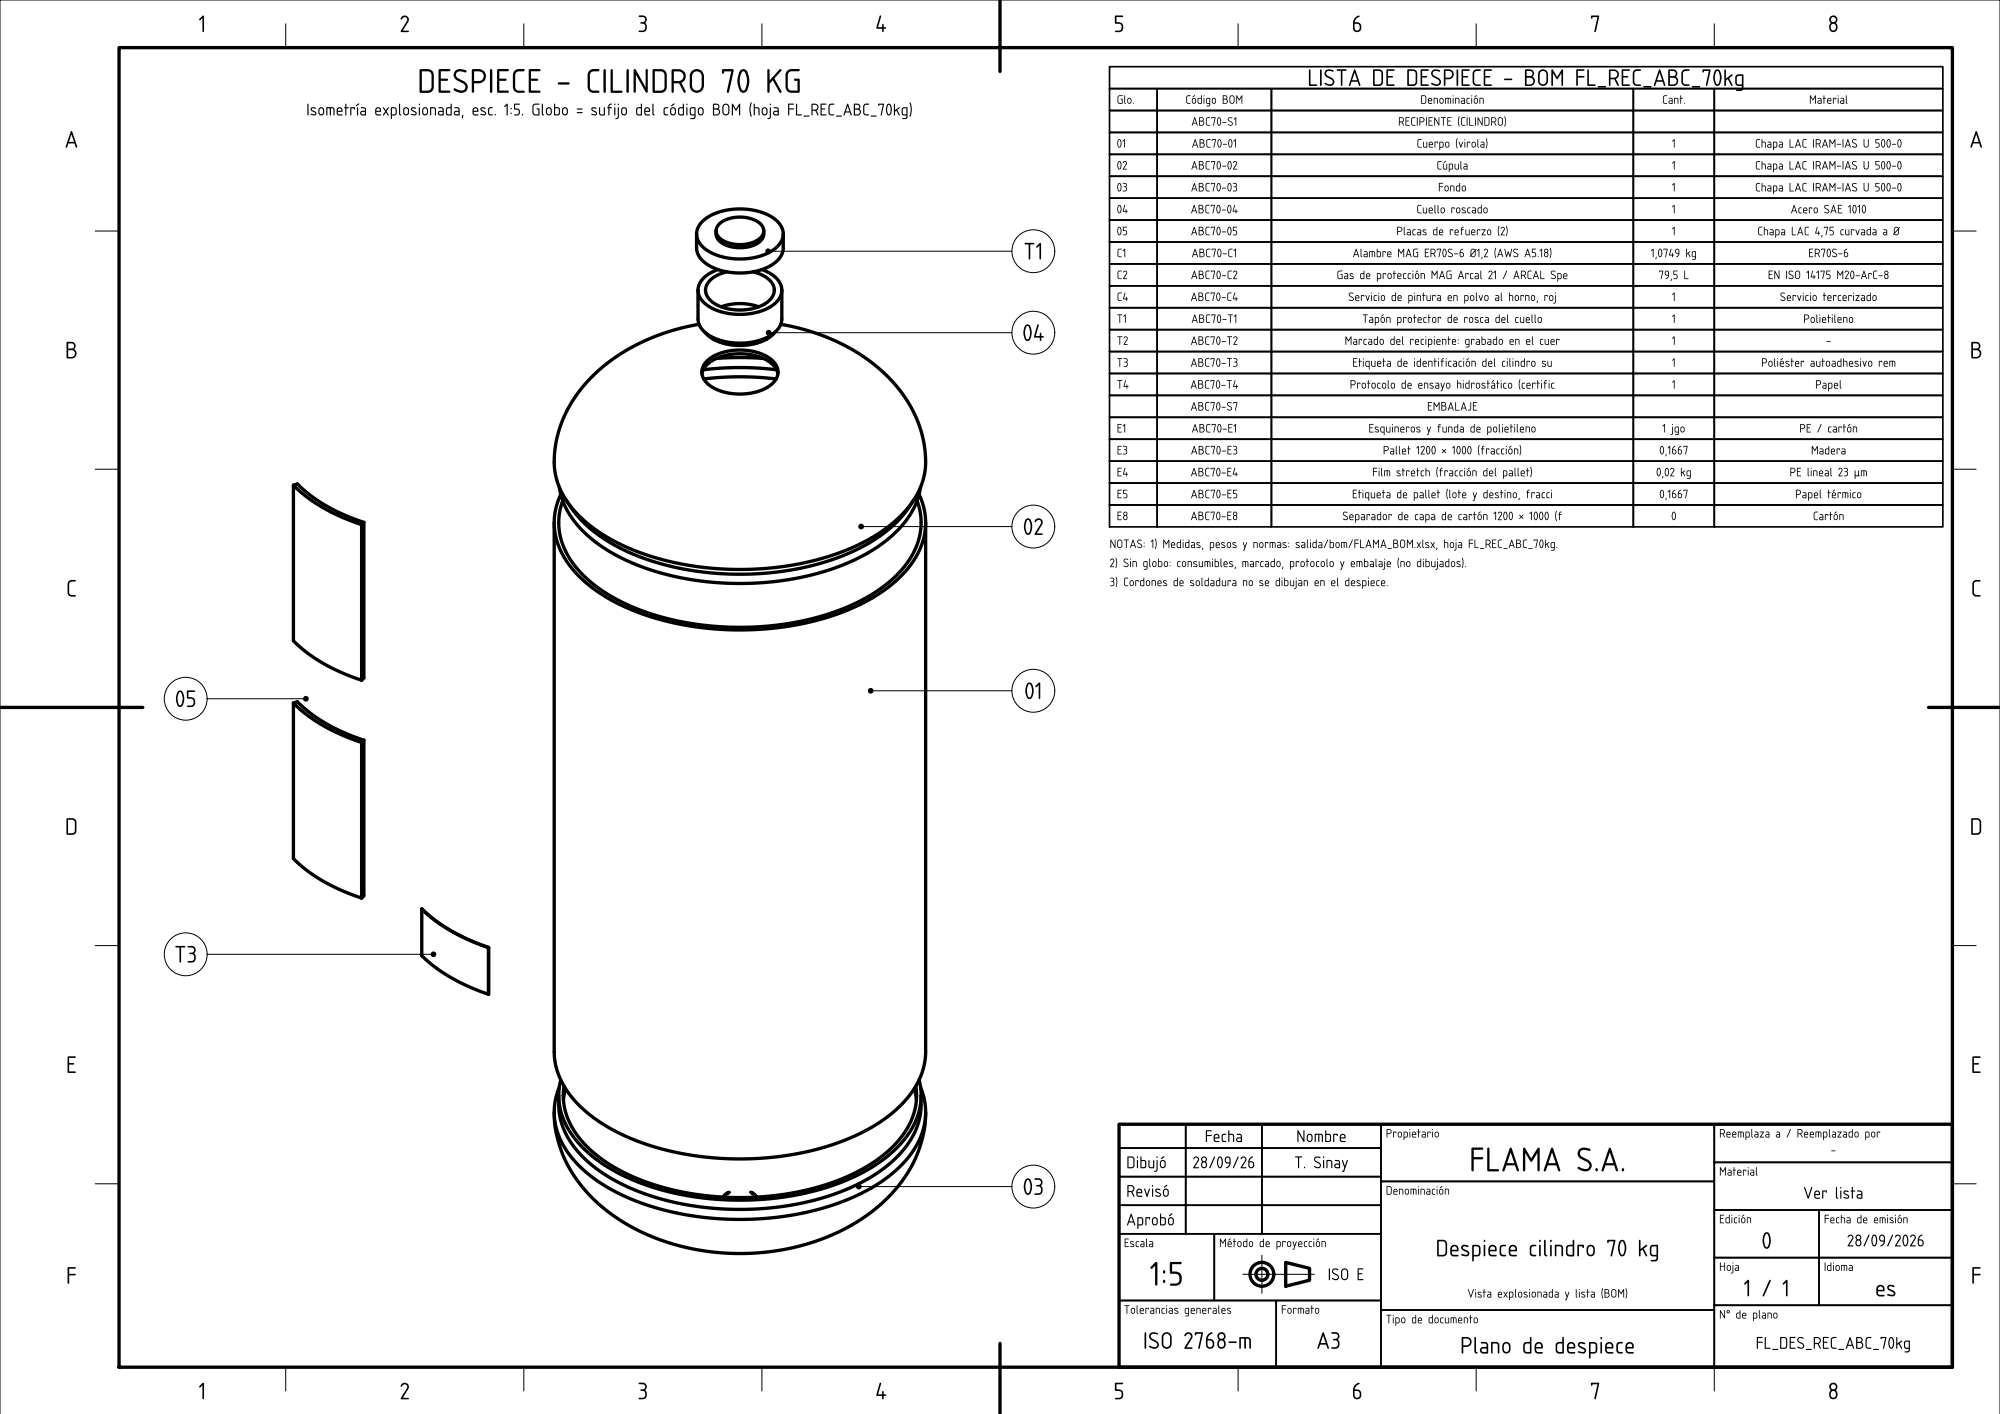
[picture p255: page 28]

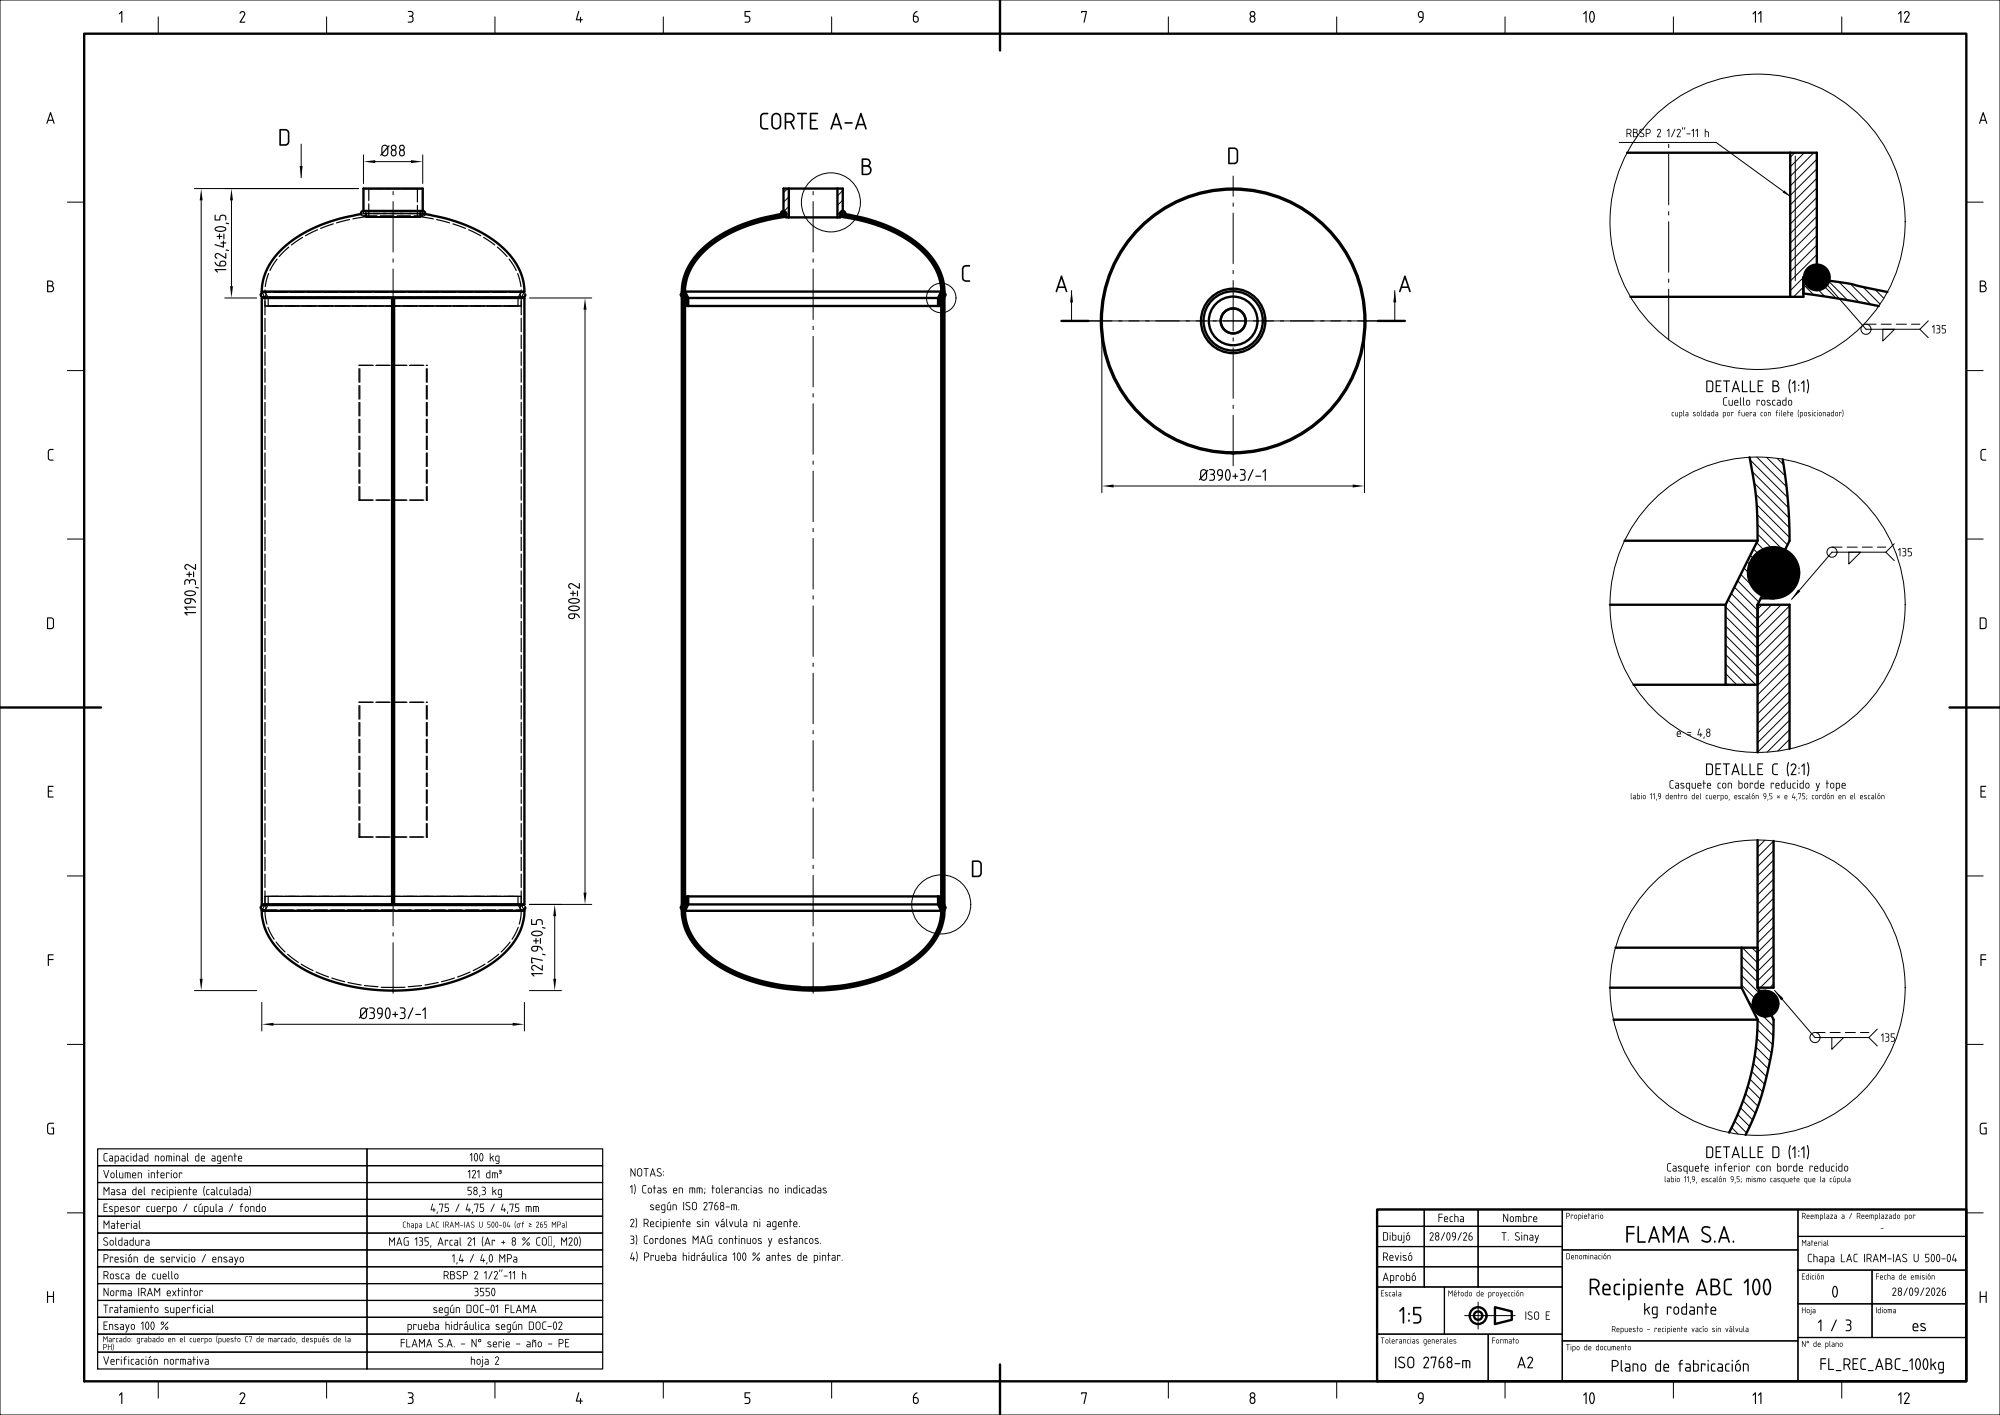
[picture p256: page 29]

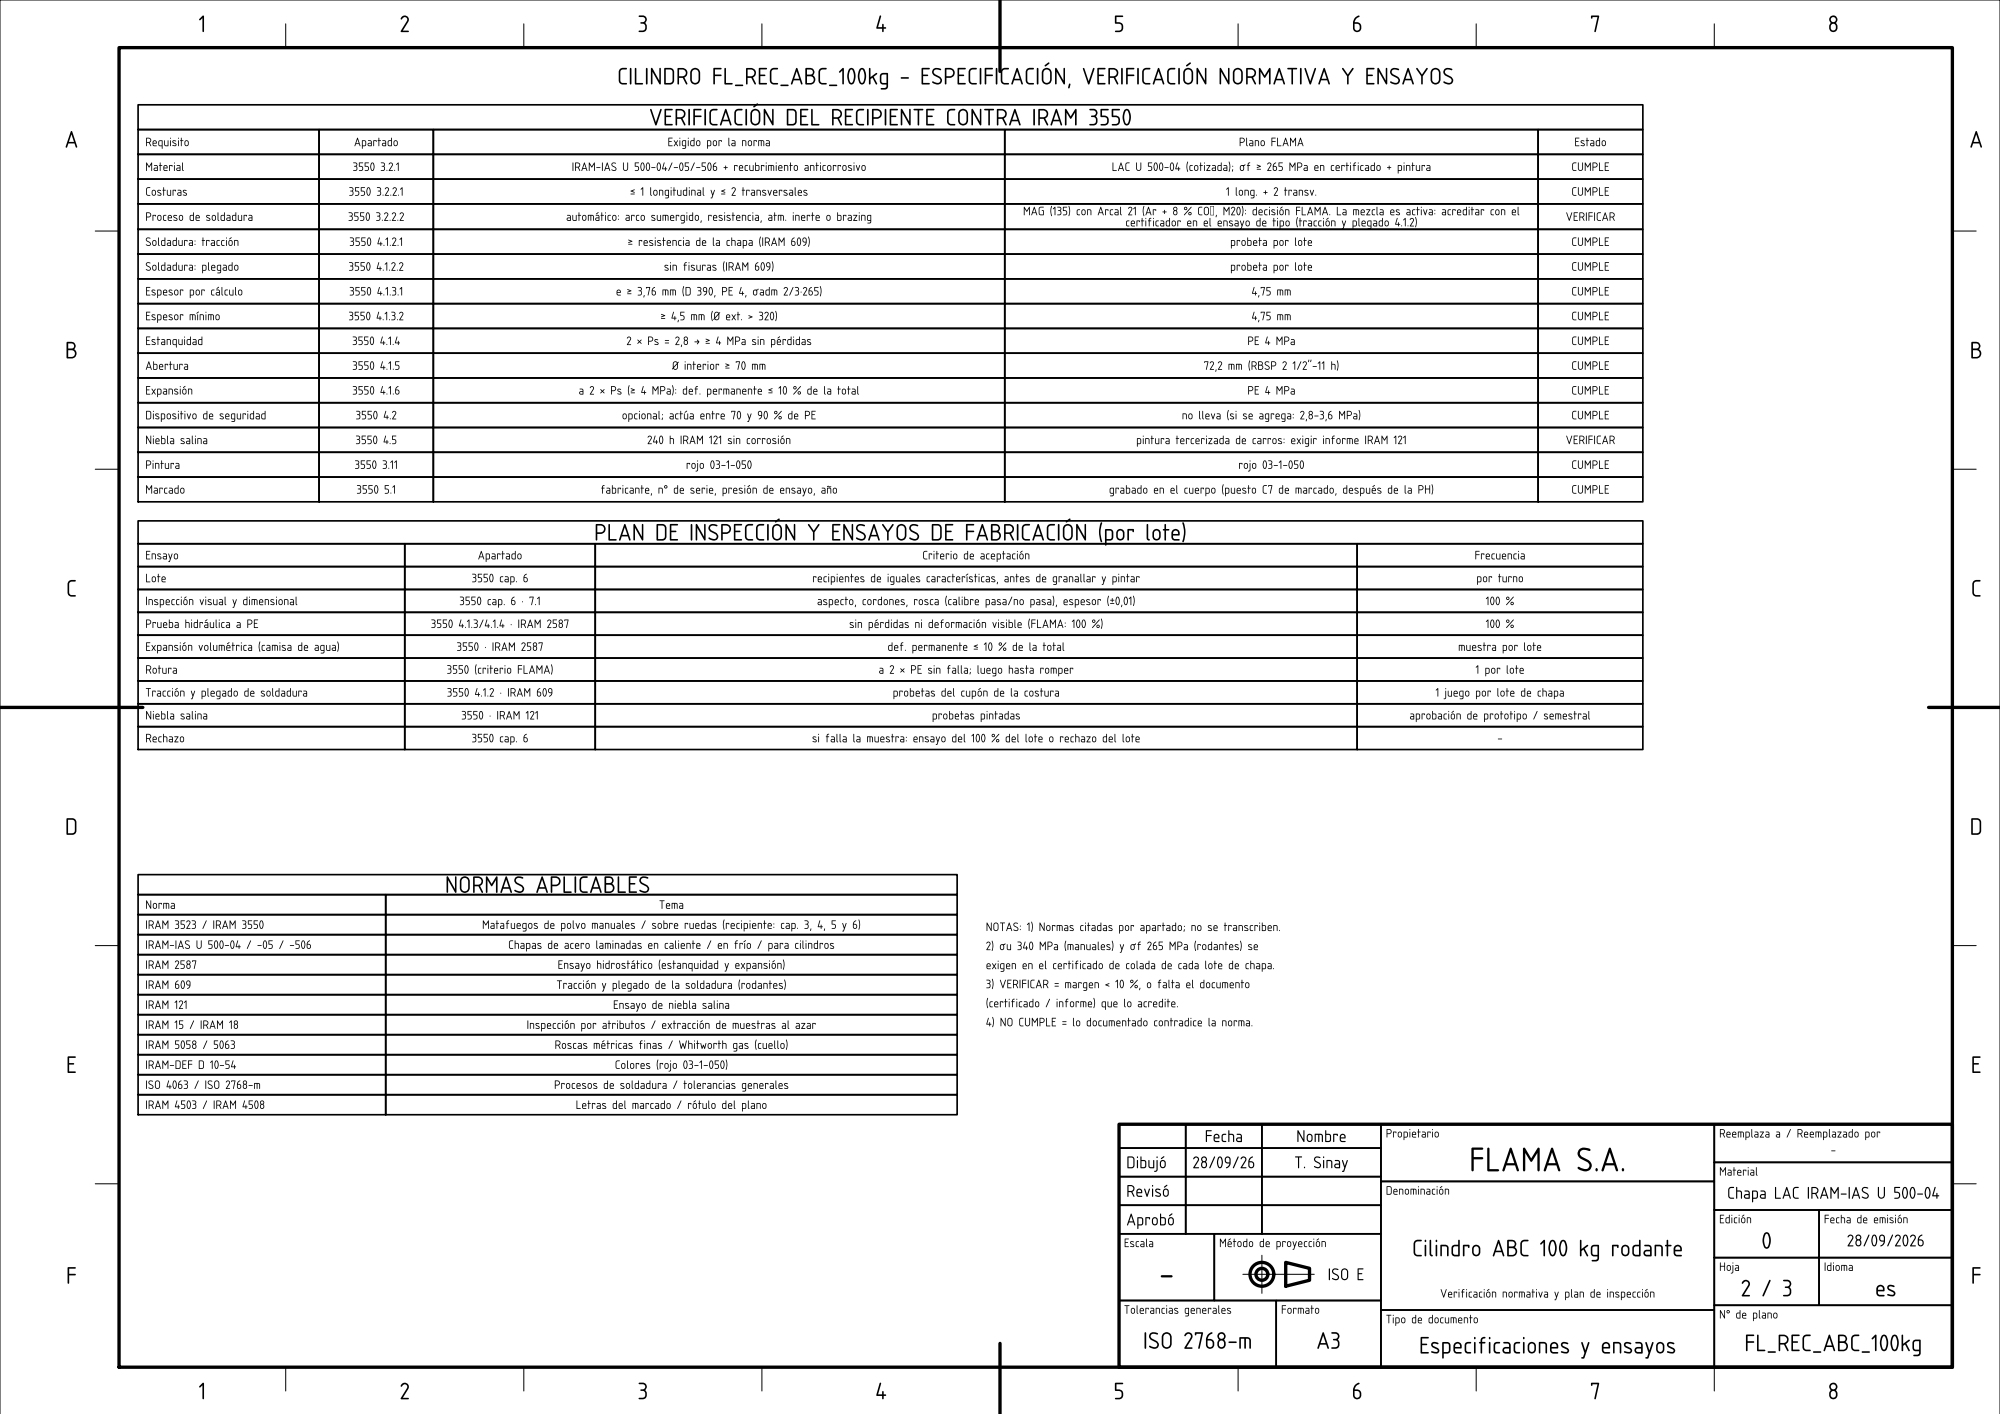
[picture p257: page 30]

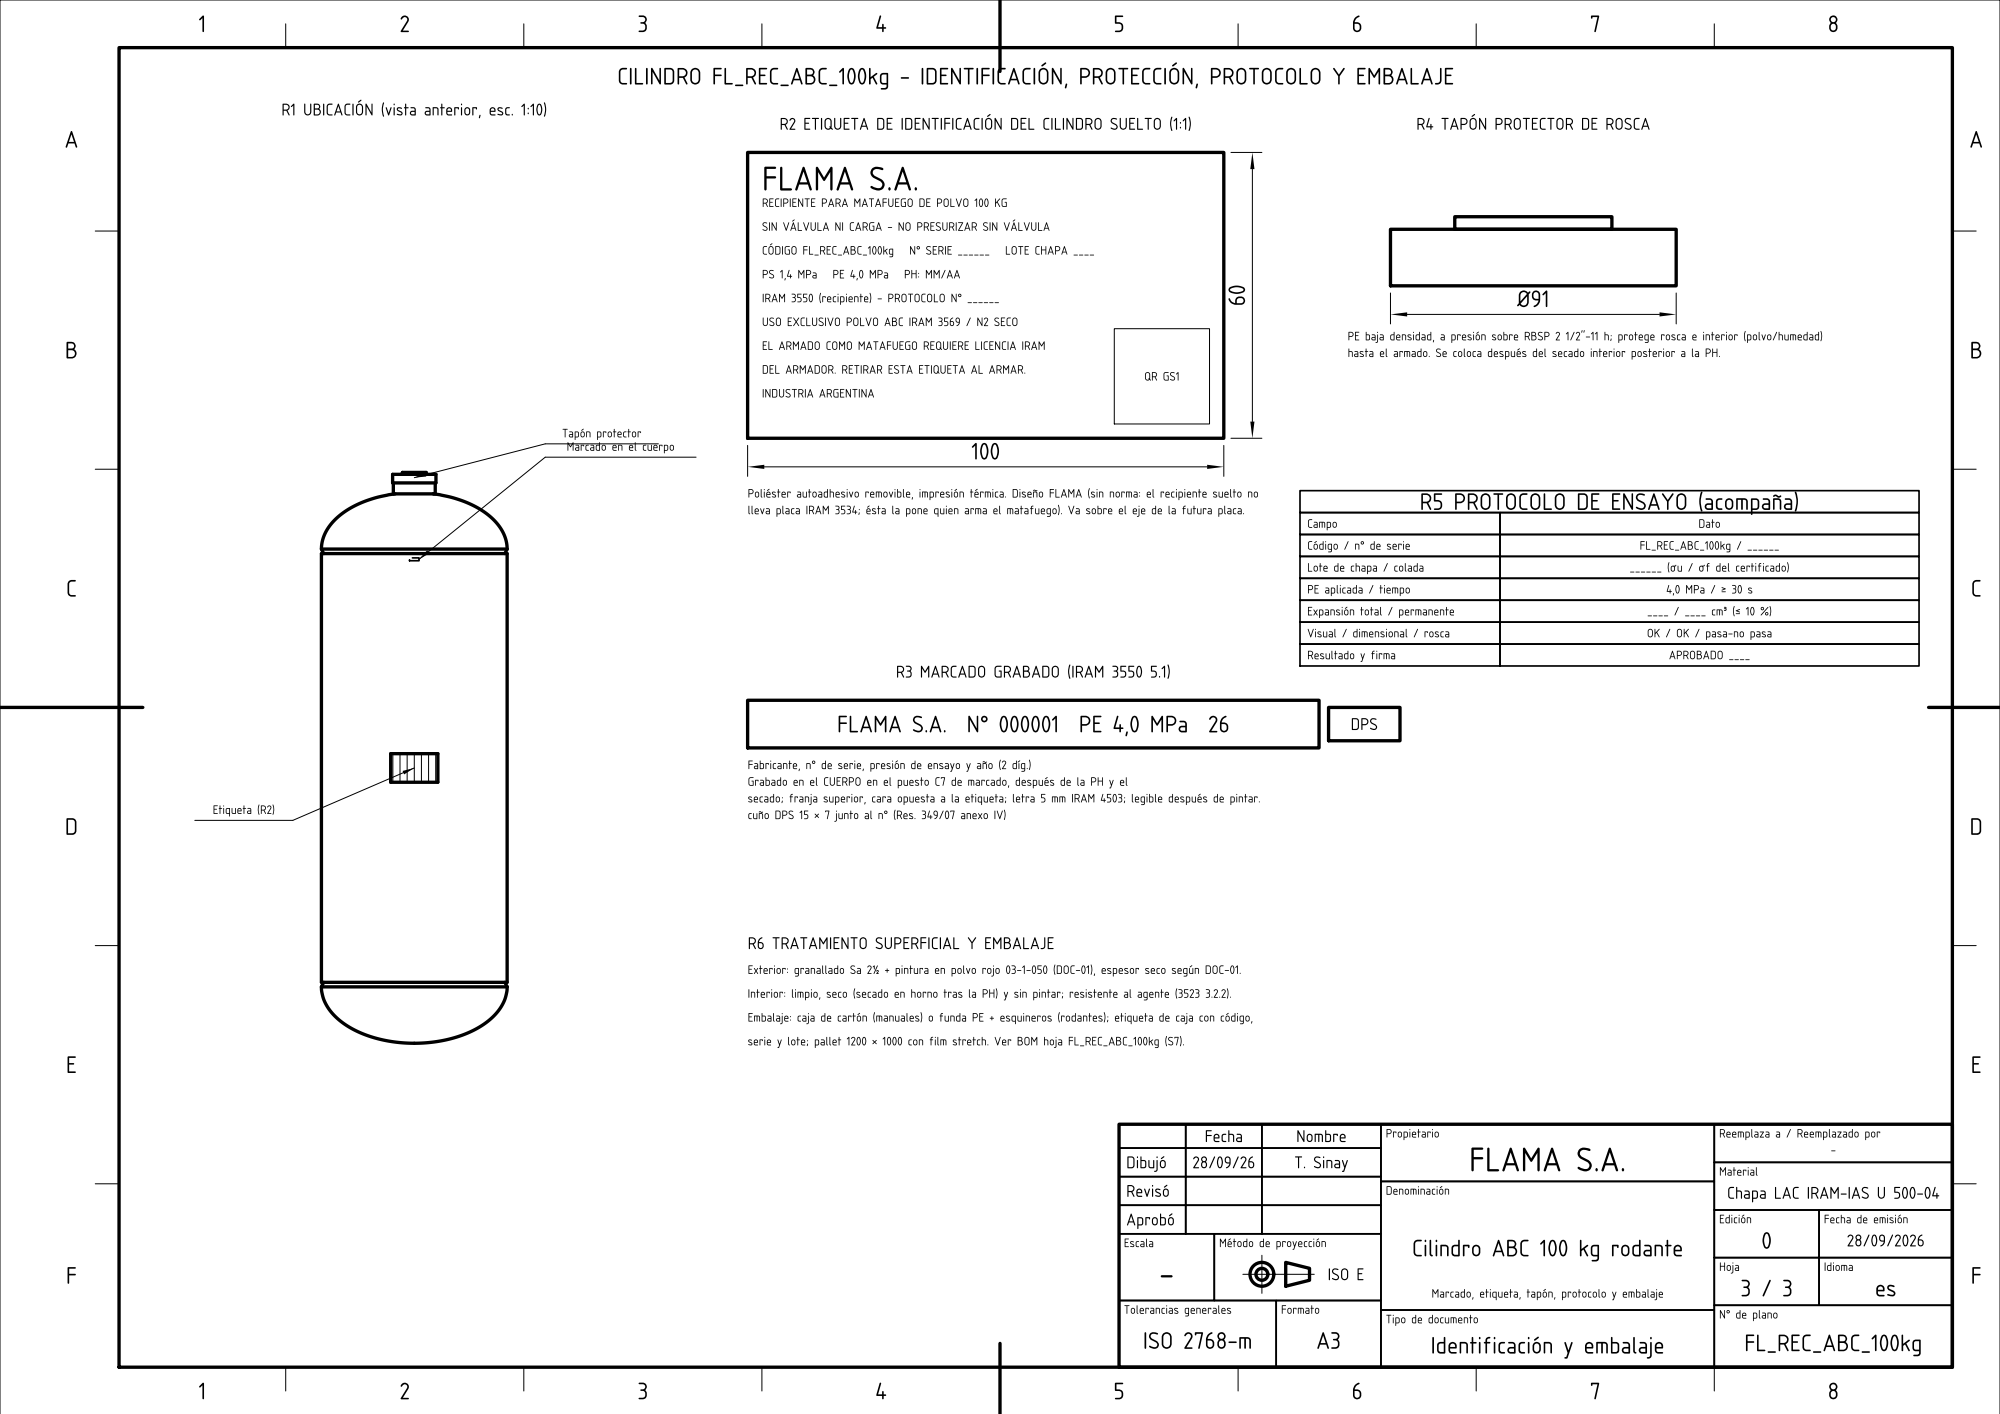
[picture p258: page 31]

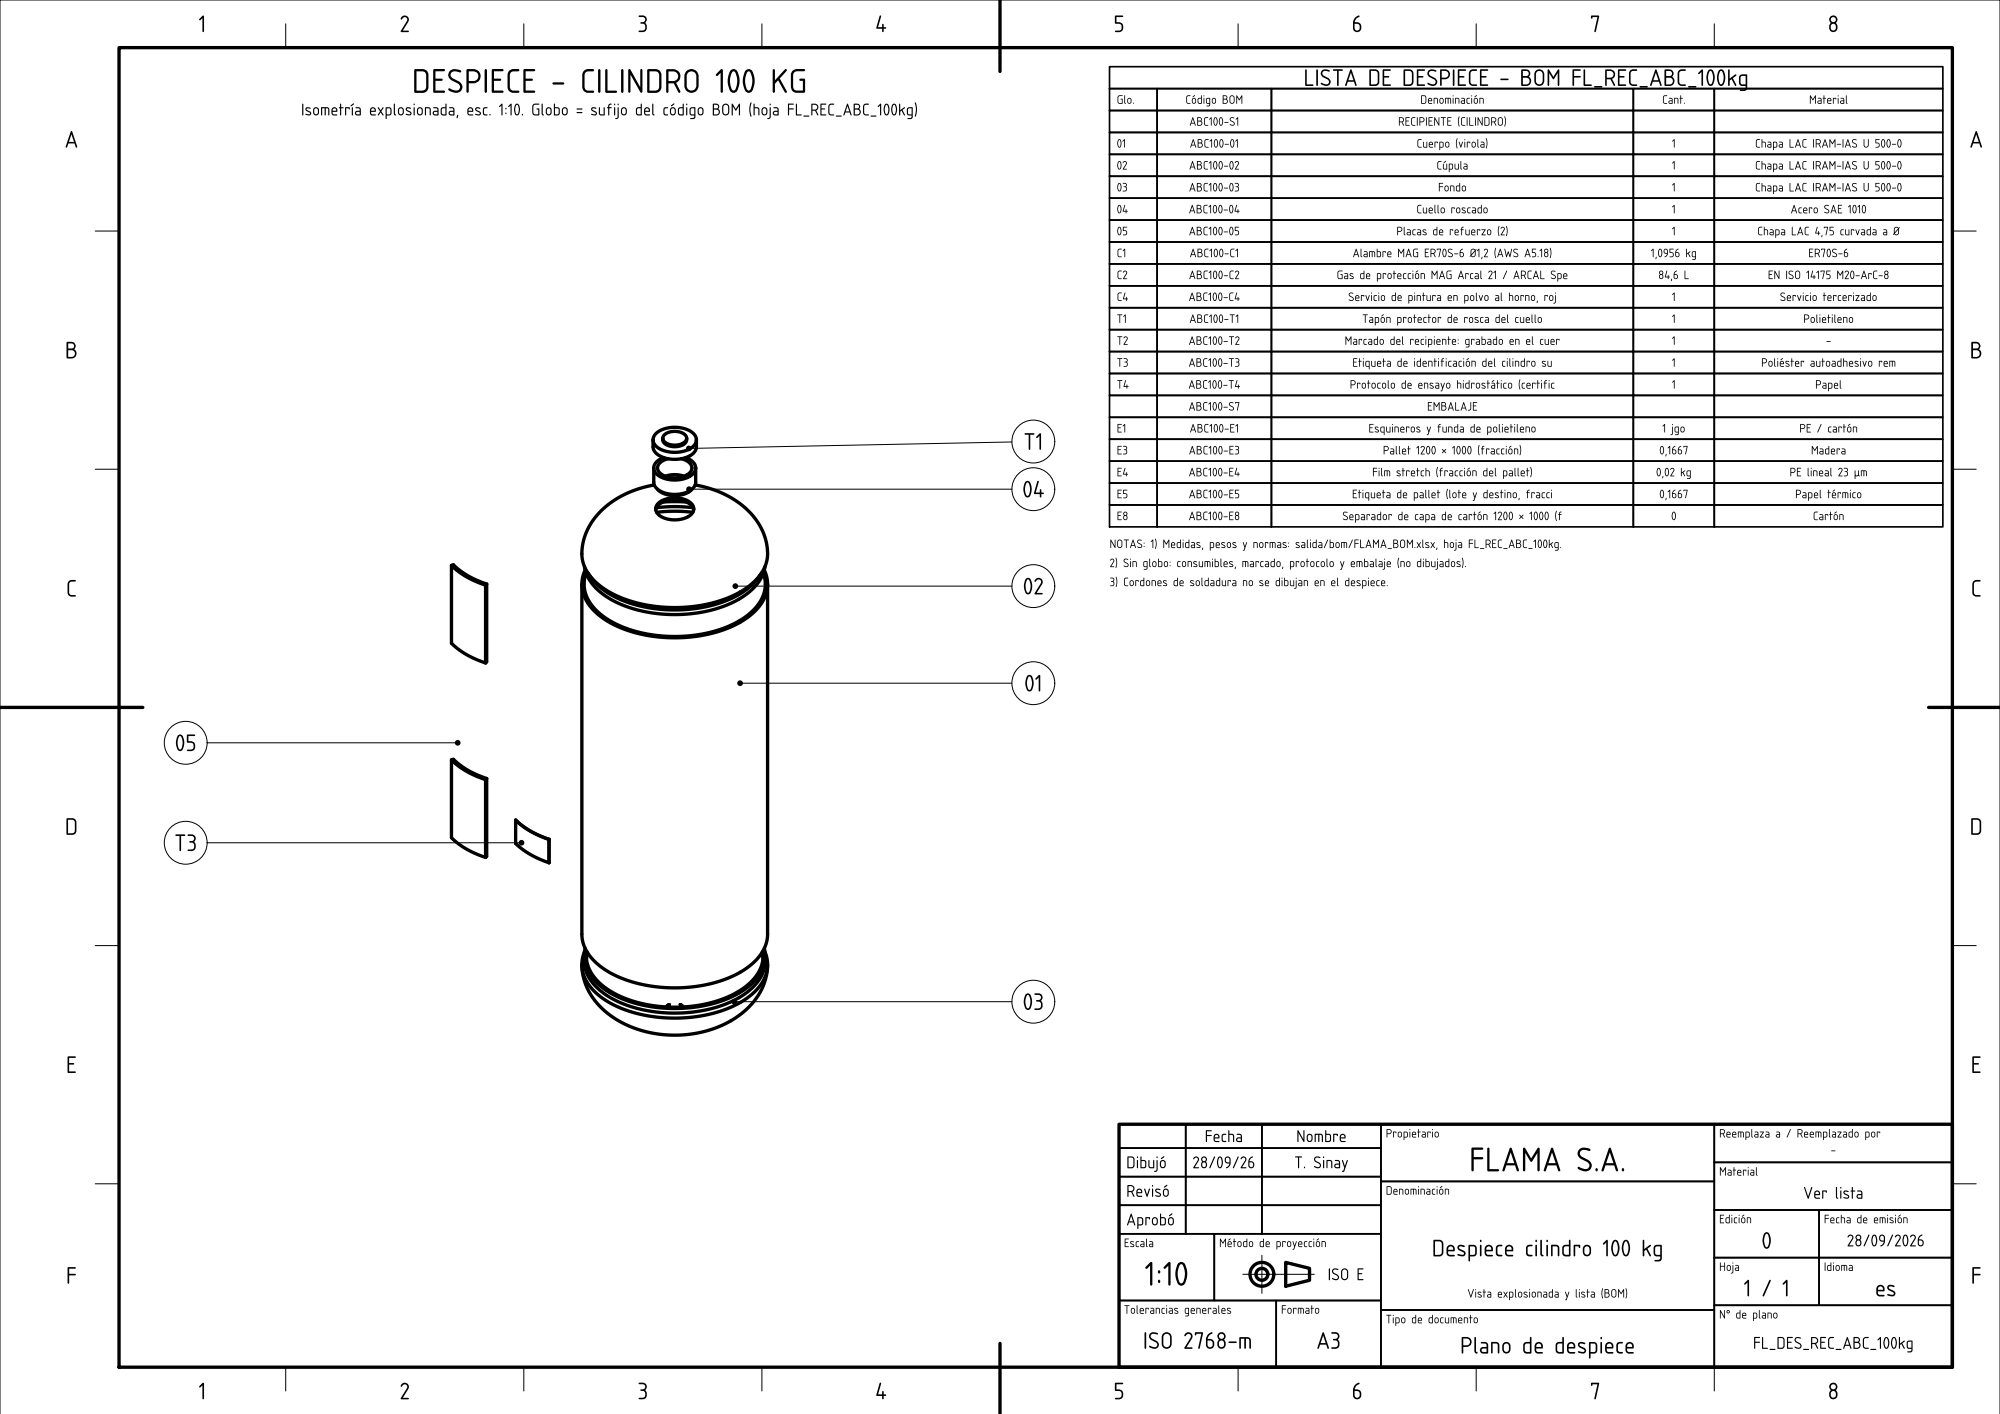
[picture p259: page 32]
