TadeoSinay/planos_flama-/salida/cilindros/despiece/FL_DES_REC_ABC_100kg.pdf

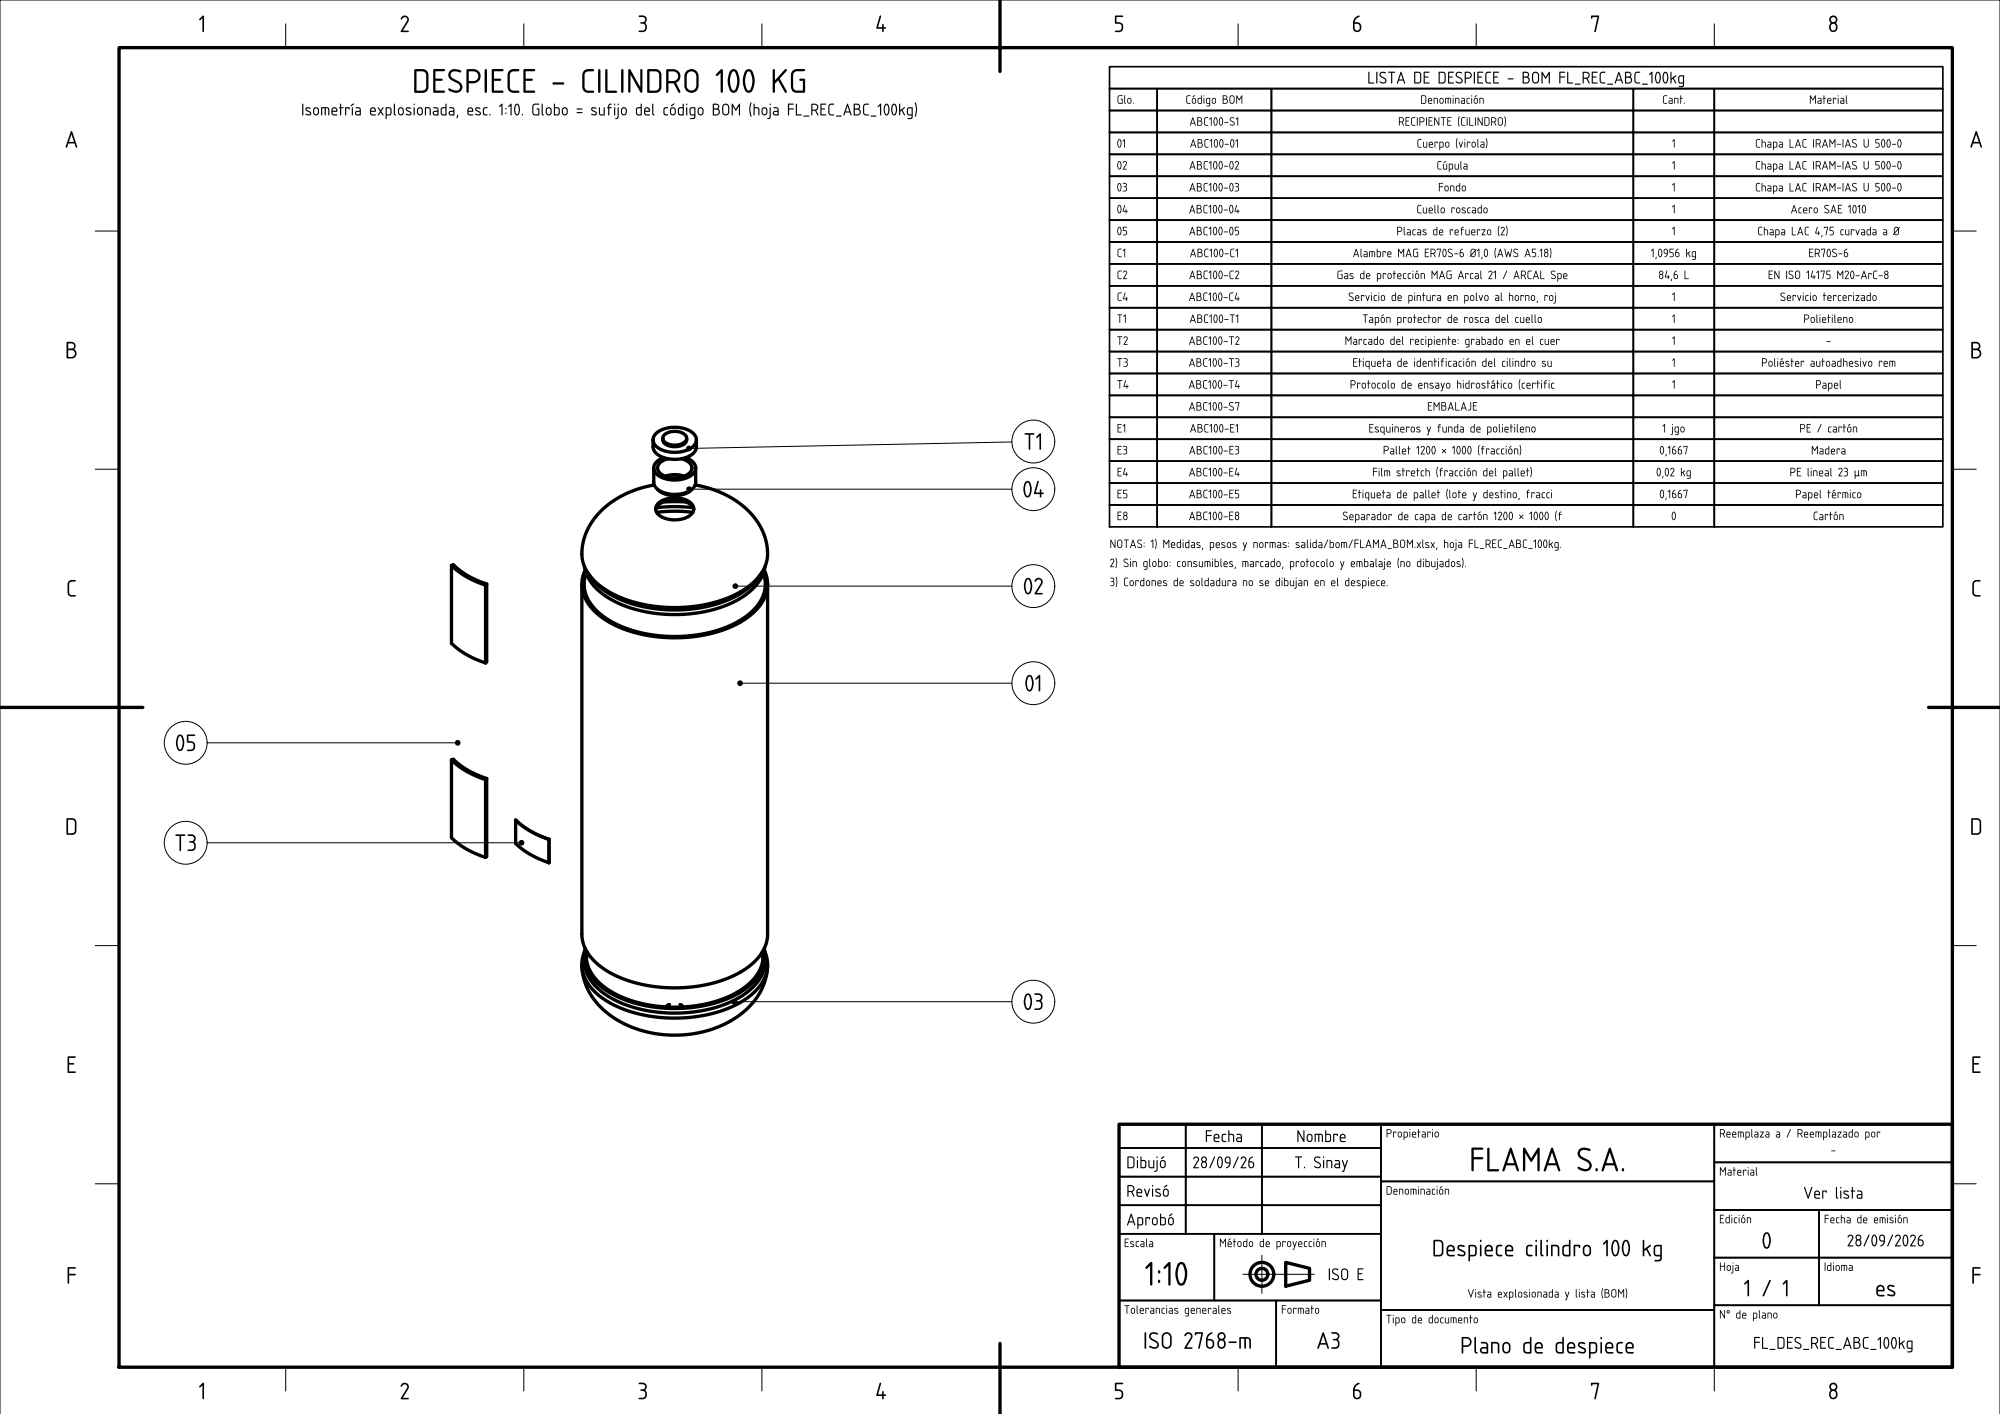
[picture p260: page 1]
