TadeoSinay/planos_flama-/salida/cilindros/despiece/FL_DES_REC_ABC_10kg.pdf

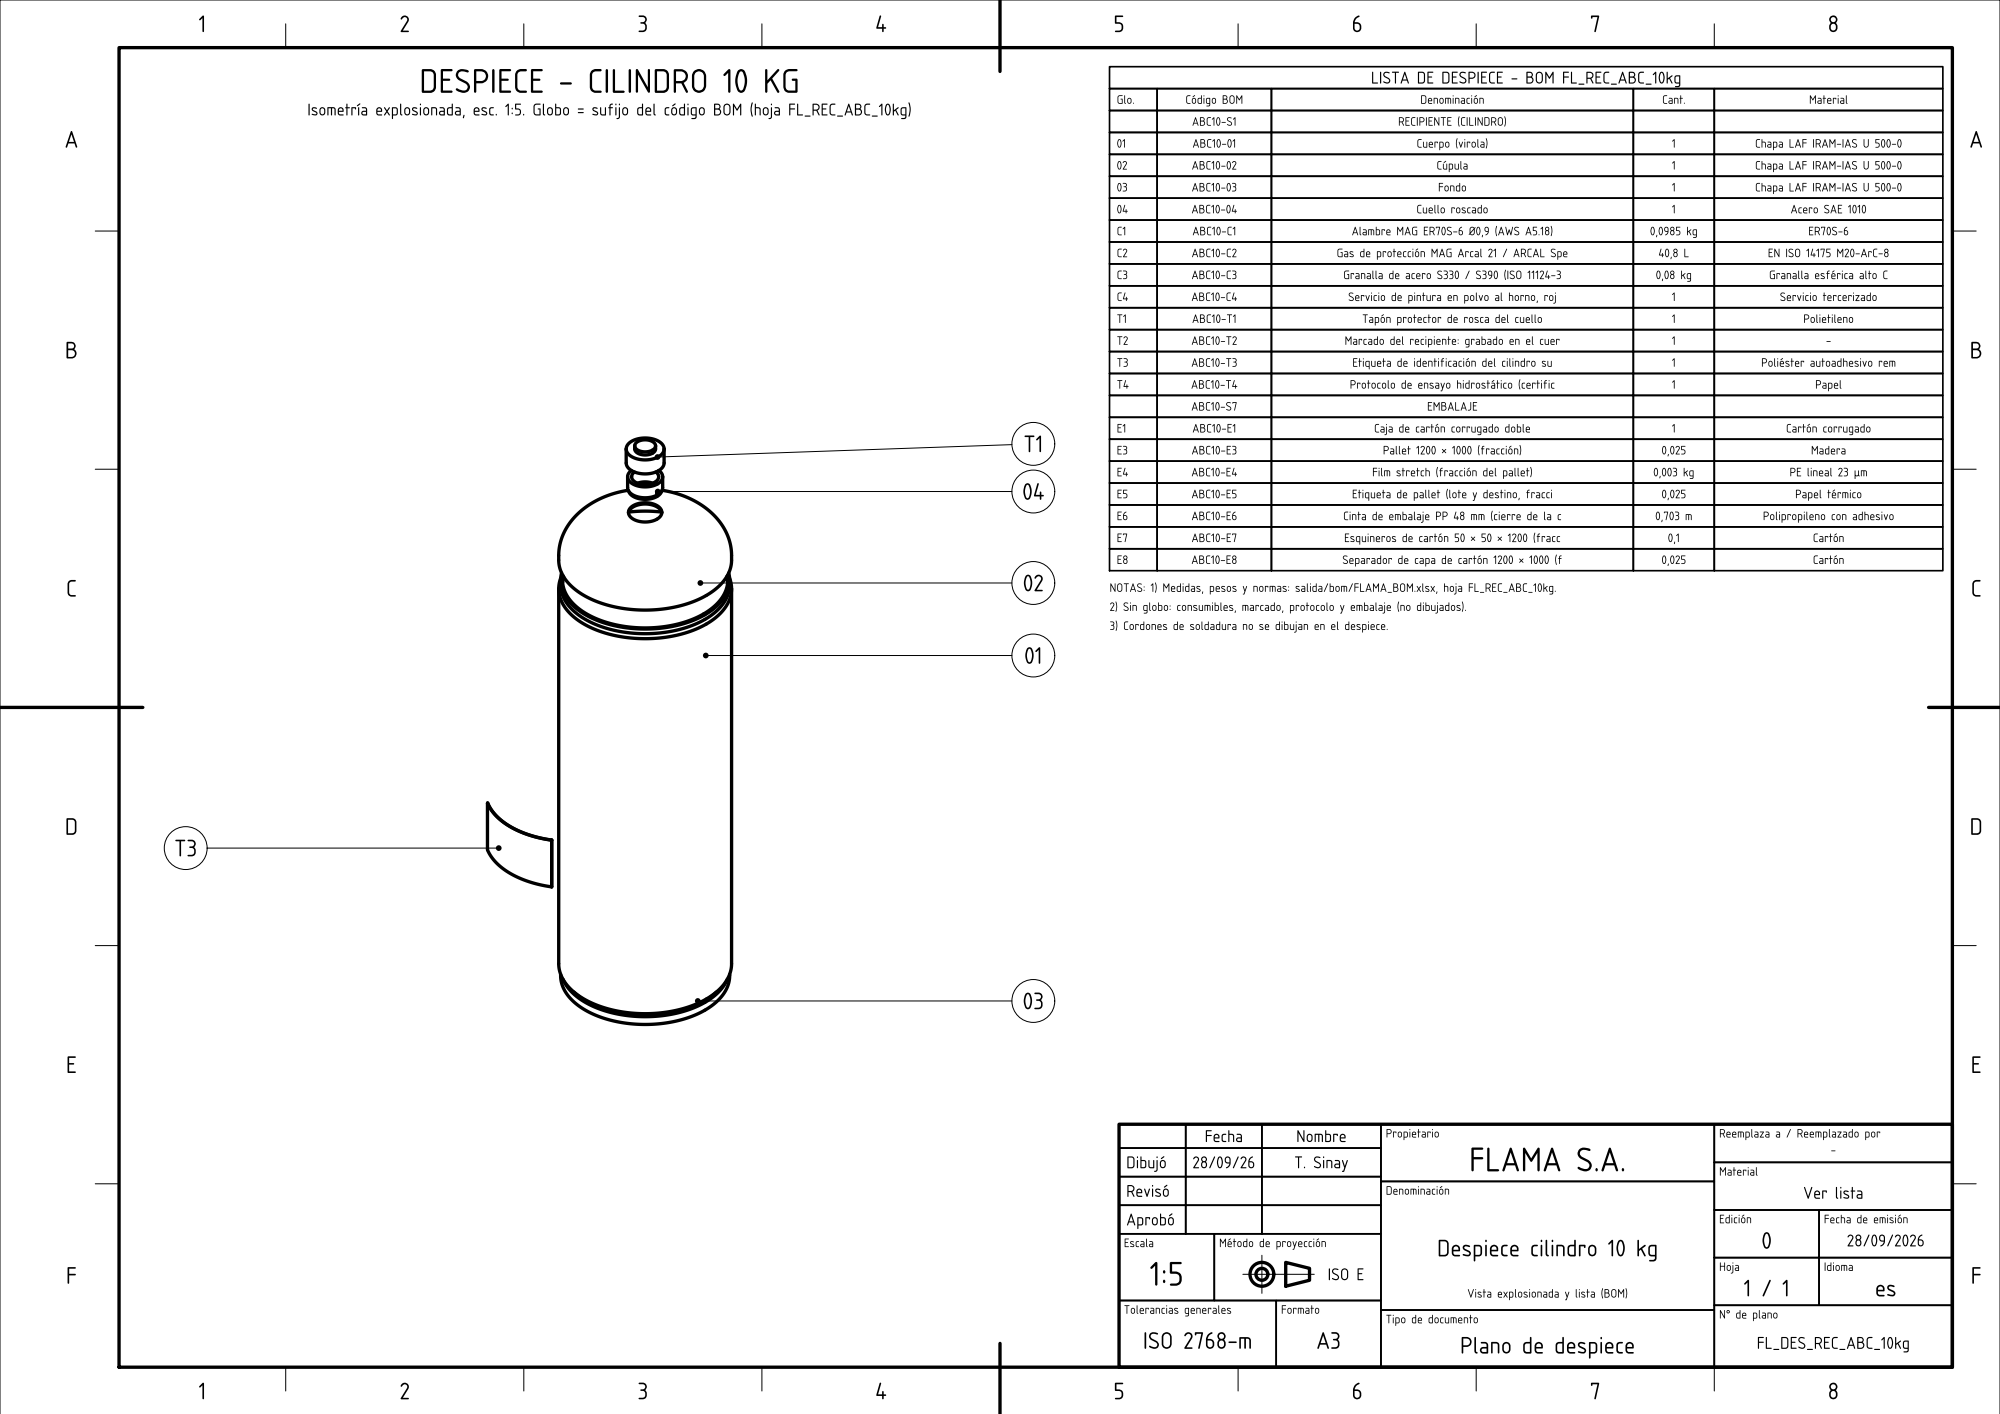
[picture p261: page 1]
