TadeoSinay/planos_flama-/salida/cilindros/despiece/FL_DES_REC_ABC_1kg.pdf

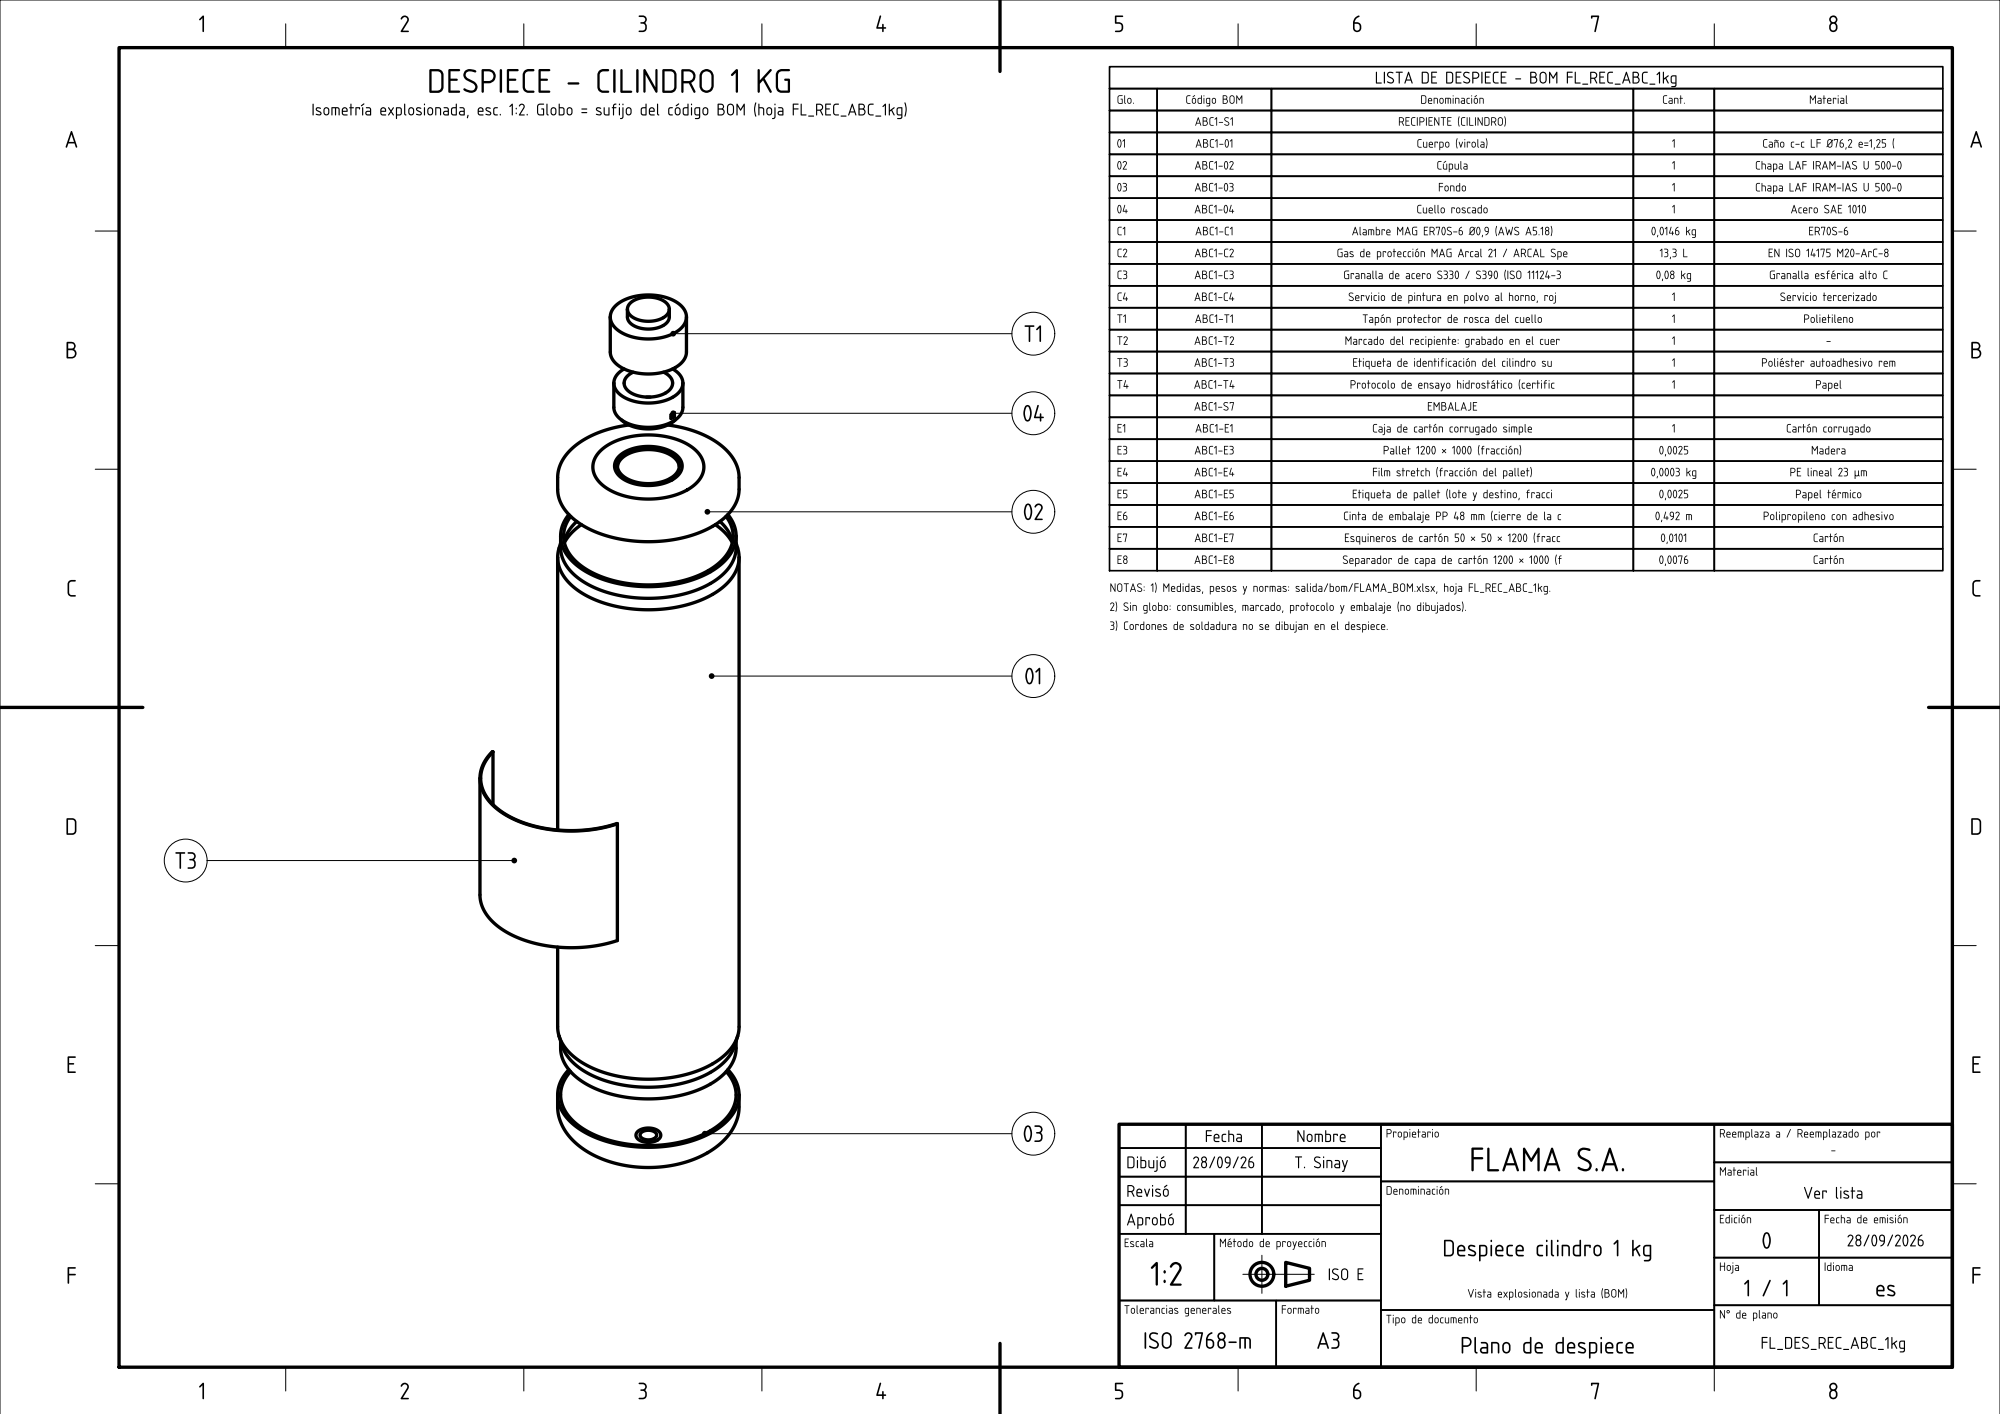
[picture p262: page 1]
