TadeoSinay/planos_flama-/salida/cilindros/despiece/FL_DES_REC_ABC_2.5kg.pdf

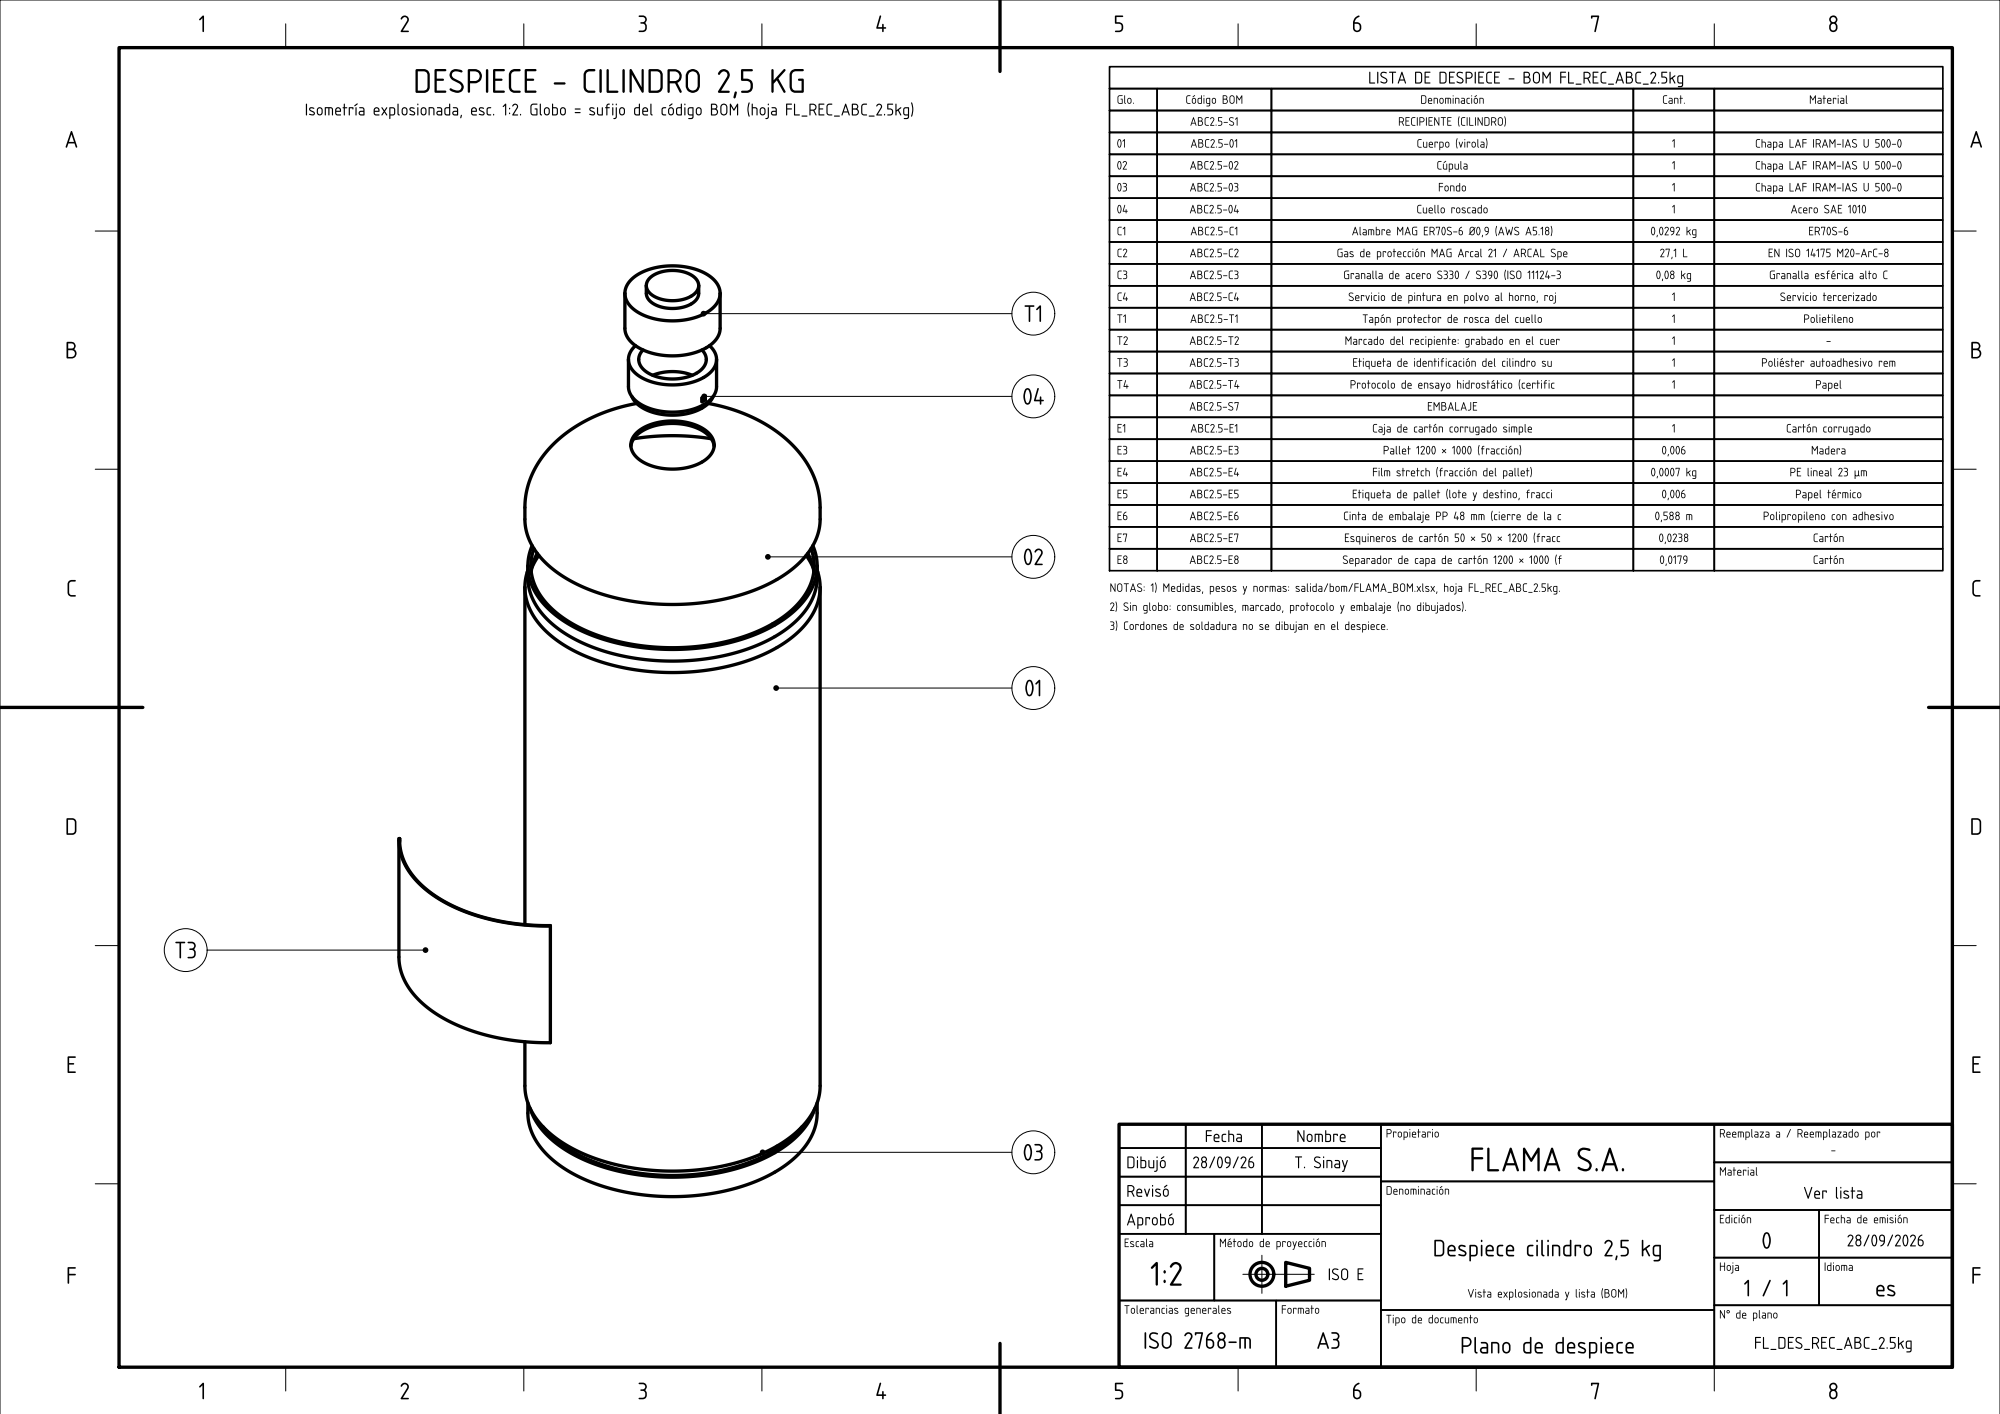
[picture p263: page 1]
